rompasaurus/regardedPal/hardware-design/scad Parts/Rev 2 extended with joystick/04-26-design-alterations/solar-panel-bonding-adhesives.md

# Bonding a Solar Panel to a PETG Base Plate — Adhesive Options

Goal: glue a small solar panel (typically PET / ETFE / glass front, EVA + polymer backsheet, or epoxy-potted "rigid" panel) to a 3D-printed **PETG** base plate, outdoors, for years.

PETG itself is one of the most weather-tolerant common filaments — it survives years of sun without going brittle, so the bond joint is the limiting factor, not the plate. The two failure modes you're designing against are: (1) UV breaking down the adhesive, and (2) thermal cycling shearing it as PETG (CTE ~60 µm/m·°C) and the panel expand/contract at different rates. That's why **flexible** adhesives outperform rigid epoxies for this job.

## Quick recommendation

- **Best overall (long life, tolerant of thermal cycling, weather-sealed):** Sikaflex‑252 or Sikaflex‑295 UV bead around the perimeter.
- **Best for a clean, no-mess, fast install:** 3M VHB tape (5952 / 4941 / 4611 outdoor grades).
- **Best if you want it permanent and don't care about removability:** Sikaflex 252 + a few dots of CA glue to tack it while the urethane cures.
- **Avoid for outdoor, long-term:** hot glue, generic super glue, PVA/wood glue, plain 2‑part 5‑min epoxy.

---

## Option matrix

| Adhesive | Type | Bond to PETG | UV / outdoor | Flexible? | Expected outdoor life | Notes |
|---|---|---|---|---|---|---|
| **Sikaflex‑252** | 1‑part polyurethane | Excellent (lightly sand PETG first) | Excellent | Yes | **15–20+ years** (field reports of 20 yr installs still holding) | Industry standard for bonding solar panels to RVs/vans. Cures with humidity over ~24 h. |
| **Sikaflex‑295 UV** | 1‑part polyurethane | Excellent | Excellent (designed for marine glazing in UV) | Yes | **15–20+ years** | Specifically formulated for plastics that see direct sun. Often paired with Sika primer 209 on plastics. |
| **DOWSIL 795** | Neutral‑cure silicone | Very good (abrade + clean with IPA) | Excellent | Yes | **20+ years** (architectural rated) | Used to structurally bond glass curtain walls — overkill in the best way. |
| **3M VHB 5952 / 4941 / 4611** | Acrylic foam tape | Very good on PETG (clean, 21 °C+ install) | UV‑stable, weather‑resistant | Slightly (foam absorbs shear) | **10+ years** outdoor; 3M cites multi‑decade architectural use | Cleanest install. Press hard; full bond strength at ~72 h. Use a wide enough strip — bond area is everything. |
| **3M 4945 (UV‑resistant VHB)** | Acrylic foam tape | Good | Specifically UV‑rated | Slight | **10+ years** | Variant marketed for UV‑exposed joints. |
| **3D Gloop! (PETG version)** | Solvent‑weld | Excellent — chemically welds PETG to PETG | Moderate (joint is PETG, so good; but only welds PETG‑to‑PETG, not PETG‑to‑glass/EVA) | No | Depends on substrate | Great for joining PETG parts; **not** the right tool for bonding a glass/EVA panel face to PETG. |
| **Weld‑On 16** | Solvent cement | Excellent on PETG (PETG‑to‑acrylic/PETG) | Moderate | No | 5–10 yr | Same caveat as Gloop — designed for plastic‑to‑plastic, not panel‑to‑plastic. |
| **J‑B Weld Plastic Bonder** | 2‑part urethane epoxy | Good (sand PETG) | OK | Slightly | **5–10 yr** outdoor | Stronger than 5‑min epoxy, more flexible than rigid epoxy. Decent budget option. |
| **Loctite PL Premium / polyurethane construction adhesive** | 1‑part polyurethane | Good | Good | Yes | **10–15 yr** | Cheap, available everywhere, similar chemistry to Sikaflex but less refined. |
| **Gorilla Clear Silicone / GE II** | Neutral‑cure silicone | OK (abrade first) | Good | Yes | **5–10 yr** | The hardware‑store version of DOWSIL 795. Fine for hobby projects. |
| **Hot glue (EVA)** | Thermoplastic | Poor adhesion to PETG, softens in sun | Bad | Yes | **<1 season outdoors** | Don't. PETG + black plate + sun easily hits 60–80 °C. |
| **CA / super glue** | Cyanoacrylate | OK on PETG with primer | Bad — embrittles in UV/humidity | No | **<1 yr outdoors** | Fine as a *tack* while a real adhesive cures, not as the structural bond. |
| **5‑minute epoxy (generic)** | Rigid epoxy | OK on sanded PETG | Yellows and embrittles in UV | No | **1–3 yr outdoors** | Rigid joint cracks under thermal cycling. |

CTE = coefficient of thermal expansion.

---

## UHU products (Germany / EU availability)

UHU is the obvious shelf-pick in DE/AT/CH. Here's how their lineup maps onto this job:

| UHU product | Chemistry | Fit for solar‑on‑PETG outdoors | Expected outdoor life | Verdict |
|---|---|---|---|---|
| **UHU Max Repair Extreme** | MS polymer (modified silane, same family as Soudal Fix All / Bostik Evo‑Stik Serious Stuff) | **Yes — best UHU choice.** Flexible, waterproof, UV‑resistant, rated −40 to +120 °C, bonds plastic/glass/metal | **~10–15 yr** outdoors realistically (UHU markets it as long-life UV/weather rated) | **Pick this** if you want a UHU product. Functionally equivalent to a softer Sikaflex. Bead the perimeter, weight overnight, full strength in 24 h. |
| **UHU Plus Endfest 300** | 2‑part epoxy, 90 min open time | Strong but **rigid** → fails the thermal-cycling test on a sunlit panel | 2–5 yr outdoors before stress cracking | OK for indoor structural; not ideal for an outdoor solar bond. |
| **UHU Plus Schnellfest** (5‑min) | 2‑part rapid epoxy | Same problem as Endfest, plus weaker | 1–3 yr outdoors | Avoid for this use. |
| **UHU Plast Special / UHU Plast** | Solvent cement (THF/MEK based) | Designed for polystyrene, ABS, PVC, acrylic — **does not chemically weld PETG**, and only works plastic‑to‑plastic anyway | n/a for this job | Wrong tool. |
| **UHU Alleskleber Kraft / All Purpose Power Transparent** | Solvent‑based contact-style | Not weatherproof at the level you need | <2 yr outdoors | Indoor only. |
| **UHU Sekundenkleber (super glue)** | Cyanoacrylate | Embrittles in UV/humidity | <1 yr outdoors | Use only as a tack while MS polymer cures. |
| **UHU Kraftkleber Kontakt** | Polychloroprene contact adhesive | Softens in heat, not UV‑rated | 1–3 yr outdoors | Skip. |
| **Pattex Kleben statt Bohren Montagekleber Extreme** *(not UHU but same shelf in any Bauhaus / OBI)* | MS polymer | Equivalent to UHU Max Repair Extreme | ~10–15 yr | Solid alternative if Max Repair Extreme is sold out. |

**Bottom line for the German shelf:** grab **UHU Max Repair Extreme**. It's the UHU product that matches the chemistry the solar industry actually uses (MS polymer / polyurethane hybrids). If you can find Sikaflex‑252 or Pattex Montagekleber Extreme at a Bauhaus / OBI / Hornbach, those are a half-step better for very long service life, but Max Repair Extreme is more than good enough for a hobby solar plate and is everywhere — Müller, dm, Rossmann, hardware stores.

Same prep rules apply: scuff the PETG with 240 grit, wipe with isopropanol, clamp/weight for 24 h.

---

## Surface prep (matters more than the adhesive choice)

PETG is a low-ish surface energy plastic and 3D prints are often glossy, which kills adhesion. For any of the options above:

1. **Scuff** the PETG bond face with 220–400 grit sandpaper until uniformly matte. This is the single biggest win.
2. **Degrease** with 90 %+ isopropyl alcohol on a lint-free cloth. Let it flash off.
3. (Polyurethane / silicone) Optionally apply the manufacturer's primer — Sika Primer‑209 N for Sikaflex on plastics, DOWSIL 1200 OS Primer for DOWSIL 795. Adds years of service life.
4. **Clamp or weight** the panel during cure. For VHB, apply firm pressure (15+ psi) for ~10 seconds across the whole strip.
5. **Cure at room temp** before exposing to sun/rain — 24 h minimum for Sikaflex/silicone, 72 h for VHB to reach full strength.

## Application patterns

- **Perimeter bead + center dots** (Sikaflex/silicone): leaves a flexible joint that also weather-seals the panel edge. Best for outdoor.
- **Continuous VHB strip around the perimeter**: clean, mechanically strong, but doesn't seal as well unless you also run a thin silicone fillet around the outside edge afterward.
- **Avoid full‑face rigid bonding** (epoxy slathered everywhere). Differential thermal expansion will pop the bond or crack the panel substrate within a few summers.

## Solar‑specific note

Commercial solar modules are laminated with **EVA encapsulant** at ~150 °C, then bonded into frames with polyurethane or silicone. You're effectively recreating the frame‑bond step. Polyurethane (Sikaflex) and structural silicone (DOWSIL 795) are what the industry actually uses for this exact job at scale, which is why they top the list.

---

## Sources

- [3M VHB Tapes — outdoor durability overview](https://www.3m.com/3M/en_US/vhb-tapes-us/)
- [3M VHB Durability Technical Bulletin (PDF)](https://www.curbellplastics.com/wp-content/uploads/2022/11/3M-VHB-Tape-Durability.pdf)
- [3M 4945 UV‑resistant VHB datasheet](https://www.adezif.com/vhb-adhesive-3m-4945)
- [DOWSIL 795 product page](https://www.dow.com/en-us/pdp.dowsil-795-silicone-building-sealant.01595717z.html)
- [Sika Sikaflex‑715 / solar mounting context](https://www.solarpanelstore.com/products/sika-sikaflex-715-semi-self-leveling-roof-sealant)
- [Sikaflex for solar panels — long‑term field report (10 yr)](https://www.promasterforum.com/threads/ten-year-follow-up-on-direct-mount-of-pv-panel-to-pm-roof.105215/)
- [Best Sikaflex for solar panel mounting (2026 guide)](https://tyntrades.com/power-generation/best-sikaflex-for-mounting-solar-panel/)
- [DIY solar — silicone sealant discussion](https://diysolarforum.com/threads/silicone-sealant.36943/)
- [Hackaday — comparing adhesives for gluing PETG prints](https://hackaday.com/2025/01/30/comparing-adhesives-for-gluing-petg-prints/)
- [MakerBuildIt — best adhesives for PETG (3D Gloop, Weld‑On 16, J‑B Weld)](https://makerbuildit.com/blogs/news/the-best-adhesives-for-petg-3d-gloop-pvc-glue-weld-on-16-and-j-b-weld-for-plastics)
- [All3DP — best glue for PETG 3D prints](https://all3dp.com/2/best-petg-glue/)
- [PETG UV resistance overview](https://makershop.co/petg-uv-resistance/)
- [PVEducation — module materials & EVA encapsulation](https://www.pveducation.org/pvcdrom/modules-and-arrays/module-materials)
- [EVA encapsulant — adhesion study](https://vishakharenewables.com/blog/eva-encapsulant-a-detailed-study/)
- [UHU Max Repair Power — official product page](https://www.uhu.com/en-en/products/uhu-max-repair-power-blister-8-g-enplcsskhu)
- [UHU Max Repair Extreme — official product page](https://www.uhu.com/en/glueing-activities/diy-and-repair/repair/max-repair)
- [UHU Plus Endfest — 2‑part epoxy overview](https://buildglueinfo.com/features-of-two-component-epoxy-glue-of-the-uhu/)
- [UHU Plast Special — plastic-to-plastic solvent cement](https://sylcreate.com/product/uhu-plast-plastic-glue-30g/)
- [UHU adhesives product family](https://sylcreate.com/product-category/adhesives/uhu/)
