rompasaurus/regardedPal/PromptProgression.md

# Prompt Progression

A record of every prompt submitted during the development of Dilder.

Spelling and grammar are lightly cleaned for readability while preserving the original intent and voice.

## Fields tracked per entry

Every prompt entry below uses the following fields. Entries that don't yet list all fields should be treated as incomplete and backfilled when the context is recovered.

- **Date/Time** — absolute date (`YYYY-MM-DD`) of the prompt. Relative dates like "Thursday" get resolved when the entry is written.
- **Prompt** — the user's message, quoted. Spelling and grammar are lightly cleaned for readability while preserving the original intent and voice.
- **Input Tokens (est)** — approximate user-facing input token count.
- **Output Tokens (est)** — approximate assistant output token count across the full turn.
- **Commit** — the short SHA + subject line of the git commit that landed the changes from this prompt, in the form `` `abc1234` — commit subject ``. Uses `n/a — <reason>` if no files were changed (research / Q&A / explanation turns) or if the work was never committed.
- **Files Created/Modified** — bulleted list of files touched, with short notes on the change. If nothing changed, omit or write `none`. Multi-prompt sessions may share a single commit; each entry still lists the files the specific prompt touched.

---

## Prompt #1
- **Date/Time:** 2026-04-08
- **Prompt:** "Let's create a new git repo for this project and put it up on my rompasaurus GitHub account. Also create a prompt progression file to notate every prompt that I type out for this project in an MD file with date and time stamp and the token count for each, and the files created or modified, in a file called PromptProgression."
- **Input Tokens (est):** ~75
- **Output Tokens (est):** ~350
- **Commit:** `369880d` — Initial commit: add PromptProgression.md for tracking project prompts
- **Files Created/Modified:**
  - `PromptProgression.md` (created)
  - `.git/` (initialized)
  - GitHub repo `rompasaurus/dilder` (created)

---

## Prompt #2
- **Date/Time:** 2026-04-08
- **Prompt:** "Let's set up a README and plan for this project. The idea is to create a learning platform and blog along with a YouTube series that goes through the development process of creating a Tamagotchi clone using a Pi Zero, e-ink display, battery, and 3D-printed case. As part of this we are going to document the entire process, starting with the prompts and structure of the project and planning process. Flesh out a README that outlines this intent, marking each addition in phases so that it can be compiled into a proper step-by-step instruction."
- **Input Tokens (est):** ~110
- **Output Tokens (est):** ~2,500
- **Commit:** `cc9ea8f` — Add README with phased project roadmap and update prompt log
- **Files Created/Modified:**
  - `README.md` (created)
  - `PromptProgression.md` (modified)

---

## Prompt #3
- **Date/Time:** 2026-04-09
- **Prompt:** "Let's continue the planning process. Bear in mind each prompt I submit needs to be recorded in PromptProgression.md. I suppose Phase 0 planning is somewhat complete — there is a section to define the pet and personality but I believe that should be planned at a later date. I think the focus first will be piecing together the hardware for a prototype testable unit with a display and input, and perhaps we'll put a placeholder animal animation of sorts to get a scaffold in place code-wise and a process in place for deploying code and testing it. As for the hardware, what we are going to be working with is a Pi Zero and this e-ink display. Let's begin to research the materials list to include this and whatever else hardware-wise will be needed to get a test bench setup for developing on this hardware. Also, given this hardware, come up with prototype sketches that could potentially be a 3D-printed casing for these materials and allow for 4–5 buttons of input actions to be recorded on the hardware, and suggest and research the types of cheap off-the-shelf components that can be used to establish input actions."
- **Input Tokens (est):** ~220
- **Output Tokens (est):** ~4,500
- **Commit:** `733c582` — Add hardware research with materials list, component specs, and input options
- **Files Created/Modified:**
  - `PromptProgression.md` (modified)
  - `docs/hardware-research.md` (created)
  - `README.md` (modified)

---

## Prompt #4
- **Date/Time:** 2026-04-09
- **Prompt:** "I also need the output processing token estimate from the prompts as well in the prompt progression."
- **Input Tokens (est):** ~20
- **Output Tokens (est):** ~250
- **Commit:** `8b8b2e4` — Update README and prompt log for Phase 1 hardware planning
- **Files Created/Modified:**
  - `PromptProgression.md` (modified — added output token estimates to all entries)

---

## Prompt #5
- **Date/Time:** 2026-04-09
- **Prompt:** "Those concept ASCII images are neat, but I want something more like a long rectangular case with the buttons on the right of the display — somewhat like the second-to-last generation of iPod Nanos — with four buttons: up, down, left, right, and a center button. Try to mock this up and see if you can generate an actual example, full-resolution prototype concept of this, bearing in mind the hardware we are using."
- **Input Tokens (est):** ~90
- **Output Tokens (est):** ~3,800
- **Commit:** `e1b6891` — Add prototype enclosure concept renders (v1 and v2 SVGs)
- **Files Created/Modified:**
  - `docs/concepts/prototype-v1.svg` (created — full-resolution prototype concept render)
  - `docs/hardware-research.md` (modified — replaced ASCII concepts with SVG reference and updated form factor)
  - `PromptProgression.md` (modified)

---

## Prompt #6
- **Date/Time:** 2026-04-09
- **Prompt:** "That's a good start. Let's create another revision of the prototype and make a v2. This time let's make the dimensions make sense — the display is going to take up the largest area of the device with the buttons being a quarter or less of the device's face real estate. Let's also take into account the Waveshare's actual dimensions and account for these ratios."
- **Input Tokens (est):** ~75
- **Output Tokens (est):** ~6,500
- **Commit:** `e1b6891` — Add prototype enclosure concept renders (v1 and v2 SVGs)
- **Files Created/Modified:**
  - `docs/concepts/prototype-v2.svg` (created — dimension-accurate prototype concept at 4:1 scale)
  - `docs/hardware-research.md` (modified — updated enclosure section with v2 specs and real component dimensions)
  - `PromptProgression.md` (modified)

---

## Prompt #7
- **Date/Time:** 2026-04-09
- **Prompt:** "For the hardware research we will need a breadboard to wire everything together — add that in there. Then we can begin the hardware setup and configuration, assuming we bought all the materials listed and a Waveshare e-ink display 2.13 V3. Compose an in-depth, well-researched setup guide to begin displaying text on the display and compile and run embedded code on the Raspberry Pi. Make the guide as simple and exhaustive as possible. Include a table of contents and walk me through the documentation for the hardware and how to set up the development and debugging environment. Pull in and research every bit of documentation I will need to be successful in this project."
- **Input Tokens (est):** ~130
- **Output Tokens (est):** ~12,000
- **Commit:** `30bb8b7` — Add comprehensive hardware and dev environment setup guide
- **Files Created/Modified:**
  - `docs/setup-guide.md` (created — comprehensive hardware and dev environment setup guide with 13 sections)
  - `docs/hardware-research.md` (modified — updated display to V3, added breadboard detail)
  - `README.md` (modified — added setup guide link to docs table and Phase 1 checklist)
  - `PromptProgression.md` (modified)

---

## Prompt #8
- **Date/Time:** 2026-04-09
- **Prompt:** "I want to set up a documentation webpage/portfolio to provide an in-depth guide on how this project is progressing in real time, along with a page for documentation and research, contact information, and an introduction. Let's create a new folder to begin planning this. I would also like to use pwnagotchi.ai as something of an inspiration for how to set this up and organise the website. It doesn't need to be anything ridiculous — in fact, static pages may be the ideal format — along with a Discord group and Patreon page. Let's roll out this folder and christen it with a new MD file."
- **Input Tokens (est):** ~120
- **Output Tokens (est):** ~3,500
- **Commit:** `f44695c` — Add website planning folder with site structure and community plan
- **Files Created/Modified:**
  - `website/PLAN.md` (created — website plan with site structure, page descriptions, Discord/Patreon plans, SSG comparison, pwnagotchi analysis)
  - `PromptProgression.md` (modified)

---

## Prompt #9
- **Date/Time:** 2026-04-09
- **Prompt:** "Let's kick off the website implementation. Look through the plan and start fleshing this out. Make sure while implementing the site to notate every step taken in a website implementation process MD, which will have a nicely structured TOC and detailed step-by-step notes on the process of creating this static site — to act as instruction and documentation. I also need a detailed guide on how to add and update content and the structure of the site, and further steps to deploy on Digital Ocean for as cheap as possible, and the best way to secure a domain for a website. Come up with domain ideas as well. Add steps to create a Patreon and Discord account. Don't forget to update PromptProgression with any prompt I input — don't be afraid to clean spelling and grammar before putting it in there too."
- **Input Tokens (est):** ~180
- **Output Tokens (est):** ~35,000
- **Commit:** `0360ba9` — Build out full MkDocs website scaffold and dev tooling (Prompts 9–13)
- **Files Created/Modified:**
  - `website/mkdocs.yml` (created — full MkDocs Material config with blog plugin, nav, social links, extensions)
  - `website/docs/index.md` (created — landing page)
  - `website/docs/about/index.md` (created — about page)
  - `website/docs/about/contact.md` (created — contact page)
  - `website/docs/blog/index.md` (created — blog landing)
  - `website/docs/blog/posts/phase-0-planning.md` (created — Phase 0 blog post)
  - `website/docs/blog/posts/phase-1-hardware.md` (created — Phase 1 blog post)
  - `website/docs/docs/index.md` (created — docs overview)
  - `website/docs/docs/hardware/materials-list.md` (created — migrated from hardware-research.md)
  - `website/docs/docs/hardware/wiring-pinout.md` (created — GPIO assignments and breadboard layout)
  - `website/docs/docs/hardware/enclosure-design.md` (created — case dimensions and design constraints)
  - `website/docs/docs/setup/pi-zero-setup.md` (created — OS flash, SSH, SPI setup)
  - `website/docs/docs/setup/display-setup.md` (created — HAT attachment, Waveshare library, hello world)
  - `website/docs/docs/setup/dev-environment.md` (created — rsync workflow, VS Code Remote-SSH, systemd)
  - `website/docs/docs/software/project-structure.md` (created — planned firmware architecture)
  - `website/docs/community/index.md` (created — community overview)
  - `website/docs/community/discord.md` (created — Discord server structure)
  - `website/docs/community/support.md` (created — Patreon tiers)
  - `website/docs/prompts/index.md` (created — prompt log mirroring PromptProgression.md)
  - `website/docs/stylesheets/extra.css` (created — custom CSS overrides)
  - `website/IMPLEMENTATION.md` (created — 14-section build process doc covering MkDocs setup, GitHub Pages, Digital Ocean deployment, domain registration guide, domain ideas, Discord setup, Patreon setup)
  - `website/CONTENT-GUIDE.md` (created — 11-section content management guide covering blog posts, docs pages, nav, Markdown features, images, and publishing)
  - `PromptProgression.md` (modified)

---

## Prompt #10
- **Date/Time:** 2026-04-09
- **Prompt:** "Give me a Python setup CLI script I can run to deploy this locally, with nice logging and status output when it is running, and various helper options for this project."
- **Input Tokens (est):** ~40
- **Output Tokens (est):** ~4,500
- **Commit:** `0360ba9` — Build out full MkDocs website scaffold and dev tooling (Prompts 9–13)
- **Files Created/Modified:**
  - `website/dev.py` (created — CLI with subcommands: check, install, serve, build, deploy, clean, status; ANSI color output with spinner; argparse; no external dependencies)

---

## Prompt #11
- **Date/Time:** 2026-04-09
- **Prompt:** "Give me a nice selection menu interface instead of a list of commands."
- **Input Tokens (est):** ~15
- **Output Tokens (est):** ~3,800
- **Commit:** `0360ba9` — Build out full MkDocs website scaffold and dev tooling (Prompts 9–13)
- **Files Created/Modified:**
  - `website/dev.py` (modified — replaced no-args fallback with interactive arrow-key menu: ↑↓ navigation, live description footer, env status badges, returns to menu after each command)

---

## Prompt #12
- **Date/Time:** 2026-04-09
- **Prompt:** "There seems to be a build failure when I build via the CLI script."
- **Input Tokens (est):** ~180 (included full error output)
- **Output Tokens (est):** ~500
- **Commit:** `0360ba9` — Build out full MkDocs website scaffold and dev tooling (Prompts 9–13)
- **Files Created/Modified:**
  - `website/docs/blog/.authors.yml` (created — required by MkDocs blog plugin for named authors)
  - `website/docs/blog/index.md` (modified — removed dead RSS link that wasn't a source file)
  - `website/docs/docs/hardware/enclosure-design.md` (modified — changed SVG links from broken relative paths to GitHub URLs)

---

## Prompt #13
- **Date/Time:** 2026-04-09
- **Prompt:** "Let's update the prompts with the last ones I sent through — divide and describe them. Commit the changes, and also apply the git commit as another field in the prompt progression where the prompt's changes were applied. Don't be afraid to clean up the spelling and grammar a bit. Report this prompt as well."
- **Input Tokens (est):** ~65
- **Output Tokens (est):** ~2,500
- **Commit:** `78ea1a0` — Backfill commit hash in PromptProgression.md (Prompt 13)
- **Files Created/Modified:**
  - `PromptProgression.md` (modified — full grammar/spelling pass, added commit hash field to all entries, added Prompts #11–13)

---

## Prompt #14
- **Date/Time:** 2026-04-09
- **Prompt:** "Walk me through how I could deploy this on GitHub Pages and the pricing structure — hopefully free — and if a domain can be linked to a GitHub Pages account."
- **Input Tokens (est):** ~35
- **Output Tokens (est):** ~900
- **Commit:** `633b084` — Add GitHub Actions workflow for automatic Pages deployment
- **Files Created/Modified:**
  - `.github/workflows/deploy-site.yml` (created — workflow that triggers on pushes to `website/` on main, installs MkDocs Material, and runs `mkdocs gh-deploy`)

---

## Prompt #15
- **Date/Time:** 2026-04-09
- **Prompt:** "Can you embed the concept images instead of linking to the GitHub page on the website?"
- **Input Tokens (est):** ~30
- **Output Tokens (est):** ~300
- **Commit:** `e358a1f` — Embed prototype SVG renders directly in enclosure design page
- **Files Created/Modified:**
  - `website/docs/assets/images/prototype-v1.svg` (created — copied from docs/concepts/)
  - `website/docs/assets/images/prototype-v2.svg` (created — copied from docs/concepts/)
  - `website/docs/docs/hardware/enclosure-design.md` (modified — replaced GitHub links with inline `![img]()` embeds)

---

## Prompt #16
- **Date/Time:** 2026-04-09
- **Prompt:** "Should the site folder be in the gitignore or will that need to be included to render on the GitHub Pages?"
- **Input Tokens (est):** ~25
- **Output Tokens (est):** ~150
- **Commit:** n/a — explanation only, no files changed
- **Files Created/Modified:** none

---

## Prompt #17
- **Date/Time:** 2026-04-09
- **Prompt:** "Add the last prompts with code changes to the prompt history with a commit ref."
- **Input Tokens (est):** ~20
- **Output Tokens (est):** ~400
- **Commit:** `1c270fd` — Update PromptProgression with Prompts 14–17 and fix #13 commit ref
- **Files Created/Modified:**
  - `PromptProgression.md` (modified — fixed Prompt #13 commit hash, added Prompts #14–17)

---

## Prompt #18
- **Date/Time:** 2026-04-09
- **Prompt:** "I need a website deployment process guide for GitHub Pages. I have a registered domain on Squarespace and I would like to deploy this site on GitHub and link my domain to this page."
- **Input Tokens (est):** ~45
- **Output Tokens (est):** ~2,800
- **Commit:** `38baa75` — Add deployment guide and CNAME file for Squarespace domain setup
- **Files Created/Modified:**
  - `website/DEPLOY.md` (created — 13-section deployment guide: GitHub Pages setup, first deployment, CNAME file, Squarespace DNS configuration with step-by-step record setup, HTTPS, mkdocs.yml update, end-to-end verification checklist, troubleshooting)
  - `website/docs/CNAME` (created — placeholder CNAME file, update with real domain before deploying)

---

## Prompt #19
- **Date/Time:** 2026-04-09
- **Prompt:** "Add my Patreon page to the site."
- **Input Tokens (est):** ~15
- **Output Tokens (est):** ~100
- **Commit:** `3b36905` — Add real Patreon URL (MchenrysDevelopment) across site
- **Files Created/Modified:**
  - `website/mkdocs.yml` (modified — Patreon social link updated)
  - `website/docs/community/support.md` (modified — Patreon URL updated)
  - `website/docs/about/contact.md` (modified — Patreon URL updated)

---

## Prompt #20
- **Date/Time:** 2026-04-09
- **Prompt:** "There's a 404 error — it's not loading despite the domain pointing correctly and the GitHub hook deploying."
- **Input Tokens (est):** ~40
- **Output Tokens (est):** ~300
- **Commit:** `0af7962` — Clarify Pages source setting in workflow comment
- **Files Created/Modified:**
  - `.github/workflows/deploy-site.yml` (modified — added comment clarifying Pages must be set to "Deploy from a branch → gh-pages" not "GitHub Actions")

---

## Prompt #21
- **Date/Time:** 2026-04-09
- **Prompt:** "Make that branch for me so that it triggers the deploy."
- **Input Tokens (est):** ~20
- **Output Tokens (est):** ~150
- **Commit:** `1c7f210` — Trigger GitHub Pages deployment via website/ path change
- **Files Created/Modified:**
  - `website/requirements.txt` (modified — added comment to satisfy workflow paths filter and trigger first deployment)

---

## Prompt #22
- **Date/Time:** 2026-04-09
- **Prompt:** *(Shared GitHub Actions build log showing successful deploy to gh-pages branch with CNAME resolution to dilder.dev)*
- **Input Tokens (est):** ~200 (build log)
- **Output Tokens (est):** ~200
- **Commit:** `18c8876` — Lowercase CNAME domain
- **Files Created/Modified:**
  - `website/docs/CNAME` (modified — changed `Dilder.dev` to `dilder.dev` for consistency)

---

## Prompt #23
- **Date/Time:** 2026-04-09
- **Prompt:** "Now we need to pull in the documentation for the Pi Zero WH and the e-ink display. Reach out to the official documentation and put it in its own folder in the docs folder. We need to then extract the pinout and pertinent documentation and attach it to the Wiring & Pinout doc."
- **Input Tokens (est):** ~55
- **Output Tokens (est):** ~8,500
- **Commit:** `61525d6` — Add official hardware reference docs and expand wiring pinout
- **Files Created/Modified:**
  - `website/docs/docs/reference/pi-zero-wh.md` (created — full 40-pin GPIO table, electrical limits, SPI/I²C/UART/PWM protocol assignments, BCM vs physical numbering guide, official links)
  - `website/docs/docs/reference/waveshare-eink.md` (created — display specs, HAT pin mapping with signal behavior table, SPI protocol details, refresh rules, V3 vs V4 comparison, Python setup examples, safety notes, official links)
  - `website/docs/docs/hardware/wiring-pinout.md` (modified — expanded with full 40-pin header map, signal behavior table, wiring diagram, SPI config table, links to new reference docs, troubleshooting section)
  - `website/mkdocs.yml` (modified — Reference section added to nav)

---

## Prompt #24
- **Date/Time:** 2026-04-09
- **Prompt:** "Update the prompts file with this and the commit."
- **Input Tokens (est):** ~15
- **Output Tokens (est):** ~400
- **Commit:** `09519b5` — Update PromptProgression with Prompts 20–24
- **Files Created/Modified:**
  - `PromptProgression.md` (modified — added Prompts #20–24)

---

## Prompt #25
- **Date/Time:** 2026-04-10
- **Prompt:** "Let's update this plan and the hardware we are going to use. For now I have a set of Waveshare 2.13 V3 displays and Pico W boards on hand that I would like to use to start this project with instead of the Pi Zero. We'll put the Pi Zero in a later dev phase and start with what we have. Update the documentation to account for this hardware change and pull in the correct documentation for this hardware and setup in the project and on the site. Update everything and replace the Zero with the Pico, and then we need to create a setup document to wire up the Waveshare to the Pico W and begin debugging from VSCode on Linux."
- **Input Tokens (est):** ~130
- **Output Tokens (est):** ~45,000
- **Commit:** `604039f` — Migrate from Pi Zero to Pico W as Phase 1 development platform
- **Files Created/Modified:**
  - `README.md` (modified — Pico W as primary board, Pi Zero deferred to Phase 5, new phase roadmap)
  - `docs/hardware-research.md` (modified — Pico W specs, SPI1 pin mapping, updated materials list and GPIO budget)
  - `website/docs/docs/reference/pico-w.md` (created — full Pico W reference: RP2040 specs, pinout, electrical limits, MicroPython firmware, Pico W vs Pi Zero comparison)
  - `website/docs/docs/reference/waveshare-eink.md` (modified — added Pico W jumper wire mapping, MicroPython driver setup, kept Pi Zero mapping for future)
  - `website/docs/docs/reference/pi-zero-wh.md` (modified — added "future hardware" banner)
  - `website/docs/docs/hardware/materials-list.md` (modified — Pico W components, updated costs and specs)
  - `website/docs/docs/hardware/wiring-pinout.md` (modified — complete rewrite for Pico W GPIO, jumper wire diagrams, MicroPython button code, visual pin map)
  - `website/docs/docs/hardware/enclosure-design.md` (modified — Pico W dimensions, enclosure deferred note)
  - `website/docs/docs/setup/pi-zero-setup.md` (modified — rewritten as Pico W setup: MicroPython flash, BOOTSEL, serial REPL, Wi-Fi test)
  - `website/docs/docs/setup/display-setup.md` (modified — rewritten for Pico W jumper wire connection, Waveshare MicroPython driver, framebuf hello world)
  - `website/docs/docs/setup/dev-environment.md` (modified — rewritten for VSCode + MicroPico on Linux: serial permissions, project config, file upload, mpremote CLI, debugging)
  - `website/docs/docs/software/project-structure.md` (modified — updated for MicroPython: framebuf, machine.Pin, flash storage notes)
  - `website/docs/docs/index.md` (modified — updated section names and descriptions for Pico W)
  - `website/docs/index.md` (modified — landing page updated for Pico W)
  - `website/mkdocs.yml` (modified — site description, nav labels, added Pico W reference page)
  - `website/docs/blog/posts/phase-1-hardware.md` (modified — rewritten for Pico W test bench)
  - `website/docs/blog/posts/phase-0-planning.md` (modified — hardware decision section updated for Pico W first approach)

---

## Prompt #26
- **Date/Time:** 2026-04-10
- **Prompt:** "Update the prompts file and fix grammar a bit. Divide, describe, and commit."
- **Input Tokens (est):** ~20
- **Output Tokens (est):** ~1,500
- **Commit:** `604039f` — Migrate from Pi Zero to Pico W as Phase 1 development platform
- **Files Created/Modified:**
  - `PromptProgression.md` (modified — added Prompts #25–26)

---

## Prompt #27
- **Date/Time:** 2026-04-11
- **Prompt:** "Let's make a development setup folder with a Docker Compose file and a step-by-step guide with a table of contents on setting up the Pico W and Waveshare e-ink display — physically connecting the display to the Pico board via GPIO headers, then flashing and connecting the Pico to this computer and running a first Hello World program via VSCode using compiled C. I need all the instructions to set up the hardware, configure VSCode, connect, debug, and run this application. Make this guide as detailed and as simple as possible, step by step. Also update the PromptProgression every time I submit a prompt here — clean up the grammar and spelling though. Make this setup guide the Pico and display first-time setup, and update the dev website too."
- **Input Tokens (est):** ~150
- **Output Tokens (est):** ~45,000
- **Commit:** `8f0df95` — Add C SDK dev environment, setup CLI, and first-time hardware guide
- **Files Created/Modified:**
  - `dev-setup/pico-and-display-first-time-setup.md` (created — comprehensive 13-section first-time setup guide with TOC: hardware wiring, C SDK toolchain install, VSCode configuration, CMake cross-compilation, build/flash/debug workflow, troubleshooting)
  - `dev-setup/hello-world/CMakeLists.txt` (created — CMake build config for Pico W with Waveshare e-Paper library, USB serial output, Ninja generator)
  - `dev-setup/hello-world/main.c` (created — Hello World C program that initializes SPI, draws text on the e-ink display, and prints heartbeat to USB serial)
  - `dev-setup/Dockerfile` (created — Ubuntu 24.04 container with ARM cross-compiler toolchain and Pico SDK for reproducible builds)
  - `dev-setup/docker-compose.yml` (created — single-service compose file that mounts the project and runs CMake + Ninja build)
  - `website/docs/docs/setup/first-time-setup.md` (created — website version of the setup guide with MkDocs Material formatting, tabbed OS instructions, admonitions)
  - `website/mkdocs.yml` (modified — added "First-Time Setup (C SDK)" to the Setup nav section)
  - `PromptProgression.md` (modified — added Prompt #27)

---

## Prompt #28
- **Date/Time:** 2026-04-11
- **Prompt:** "Let's start planning the hardware enclosure design. Create a new folder labelled hardware-design and document the applicable dimensions of the e-ink display and Pico board, along with viable off-the-shelf button options that can be wired to the Pico easily. Research the web for the best button options and provide a cost breakdown. Then we need to start planning how to model out a 3D-printed prototype case based on the concept images — link the concept images, suggest the best CAD software and company to print the first prototype cases, and provide estimated costs. Put this in a new hardware planning document with a table of contents and step-by-step guide. Also update the PromptProgression with this entry, following the same pattern."
- **Input Tokens (est):** ~150
- **Output Tokens (est):** ~25,000
- **Commit:** `8f0df95` — Add C SDK dev environment, setup CLI, and first-time hardware guide
- **Files Created/Modified:**
  - `hardware-design/hardware-planning.md` (created — comprehensive enclosure planning document with TOC: component dimensions, button selection with cost breakdown, concept image links, enclosure constraints, CAD software comparison, step-by-step 3D modeling plan, printing service comparison with costs, prototype timeline)

---

## Prompt #29
- **Date/Time:** 2026-04-11
- **Prompt:** "I want another Hello World version of the code running in C as well. The intent with this project is to have it running on C code completely for speed and efficiency. Also, for the wiring section, I am using the soldered-on headers and pins to slot the Waveshare directly onto the Pico on its headers, so it just slides in. Update the guide accordingly — I will provide pictures later."
- **Input Tokens (est):** ~80
- **Output Tokens (est):** ~30,000
- **Commit:** `8f0df95` — Add C SDK dev environment, setup CLI, and first-time hardware guide
- **Files Created/Modified:**
  - `dev-setup/hello-world-serial/main.c` (created — bare-minimum serial-only Hello World in C: LED blink + heartbeat printf, no display wiring needed, verifies toolchain end-to-end)
  - `dev-setup/hello-world-serial/CMakeLists.txt` (created — minimal CMake config linking only pico_stdlib with USB serial output)
  - `dev-setup/pico-and-display-first-time-setup.md` (rewritten — restructured as two checkpoints: Checkpoint 1 serial-only, Checkpoint 2 display; added C vs MicroPython rationale; updated wiring section from jumper wires to direct header-on-header connection)
  - `website/docs/docs/setup/first-time-setup.md` (rewritten — website version updated to match: direct header connection, two-checkpoint flow, C-first rationale)
  - `PromptProgression.md` (modified — added Prompt #29)

---

## Prompt #30
- **Date/Time:** 2026-04-11
- **Prompt:** "Let's take this Pico W & Display First-Time Setup and implement a Python command-line step-by-step interface that sets everything up and explains the process in detail as well. Put the Python script in the root of this project."
- **Input Tokens (est):** ~40
- **Output Tokens (est):** ~35,000
- **Commit:** `8f0df95` — Add C SDK dev environment, setup CLI, and first-time hardware guide
- **Files Created/Modified:**
  - `setup.py` (created — interactive 14-step CLI walkthrough: prerequisite checks, ARM toolchain install with distro detection, Pico SDK clone, PICO_SDK_PATH configuration, serial port permissions, VSCode extension install, serial hello world build/flash/verify, display connection guidance, Waveshare library download, display hello world build/flash/verify; includes --status, --step N, and --list flags; matches dev.py visual style with ANSI colors, spinners, boxed explanations, and manual-step callouts)
  - `PromptProgression.md` (modified — added Prompt #30)

---

## Prompt #31
- **Date/Time:** 2026-04-11
- **Prompt:** "Failed at step 5 — `usermod: group 'dialout' does not exist`. Does the Pico need to be connected at step 5?"
- **Input Tokens (est):** ~30
- **Output Tokens (est):** ~5,000
- **Commit:** `8f0df95` — Add C SDK dev environment, setup CLI, and first-time hardware guide
- **Files Created/Modified:**
  - `setup.py` (modified — added `detect_serial_group()` and `user_in_serial_group()` helpers that check for `uucp` first then `dialout`; Arch/CachyOS uses `uucp`, Debian/Ubuntu uses `dialout`; all hardcoded `dialout` references replaced with dynamic detection)
  - `dev-setup/pico-and-display-first-time-setup.md` (modified — serial permissions section updated with distro-specific group names)
  - `website/docs/docs/setup/first-time-setup.md` (modified — same distro-specific serial group fix with tabbed instructions)
  - `PromptProgression.md` (modified — added Prompt #31)

---

## Prompt #32
- **Date/Time:** 2026-04-11
- **Prompt:** *(Pasted build failure output from setup.py Step 7 — `PICO_DEFAULT_LED_PIN` undeclared error)*
- **Input Tokens (est):** ~80
- **Output Tokens (est):** ~8,000
- **Commit:** `8f0df95` — Add C SDK dev environment, setup CLI, and first-time hardware guide
- **Files Created/Modified:**
  - `dev-setup/hello-world-serial/main.c` (modified — replaced `PICO_DEFAULT_LED_PIN` and `gpio_put` with `cyw43_arch_gpio_put(CYW43_WL_GPIO_LED_PIN)` since the Pico W's onboard LED is wired to the CYW43 Wi-Fi chip, not a regular GPIO pin; added `pico/cyw43_arch.h` include and `cyw43_arch_init()` call)
  - `dev-setup/hello-world-serial/CMakeLists.txt` (modified — added `pico_cyw43_arch_none` to link libraries for CYW43 LED control)
  - `setup.py` (modified — fixed build error output to show both stdout and stderr since Ninja reports compile errors on stdout)
  - `PromptProgression.md` (modified — added Prompt #32)

---

## Prompt #33
- **Date/Time:** 2026-04-11
- **Prompt:** "Could not find the RPI-RP2 mount despite it showing up in Dolphin file explorer."
- **Input Tokens (est):** ~40
- **Output Tokens (est):** ~5,000
- **Commit:** `8f0df95` — Add C SDK dev environment, setup CLI, and first-time hardware guide
- **Files Created/Modified:**
  - `setup.py` (modified — added `find_rpi_rp2_mount()` helper that checks static paths, falls back to `findmnt`/`lsblk` for the actual mount point, retries after 1-second delay for automount; both flash steps now loop with retry instead of failing on first miss)
  - `PromptProgression.md` (modified — added Prompt #33)

---

## Prompt #34
- **Date/Time:** 2026-04-11
- **Prompt:** *(Pasted Step 12 build failure — `Debug.h: No such file or directory` and missing `<stdlib.h>` warnings)*
- **Input Tokens (est):** ~100
- **Output Tokens (est):** ~5,000
- **Commit:** `8f0df95` — Add C SDK dev environment, setup CLI, and first-time hardware guide
- **Files Created/Modified:**
  - `dev-setup/hello-world/main.c` (modified — added missing `#include <stdlib.h>` for `malloc`/`free`)
  - `dev-setup/hello-world/lib/Config/Debug.h` (added — copied from Waveshare repo, was missing from the initial file list)
  - `setup.py` (modified — added `Debug.h` to the Waveshare library copy list in Step 11)
  - `dev-setup/pico-and-display-first-time-setup.md` (modified — added `Debug.h` to the manual copy commands)
  - `website/docs/docs/setup/first-time-setup.md` (modified — same `Debug.h` fix)
  - `PromptProgression.md` (modified — added Prompt #34)

---

## Prompt #35
- **Date/Time:** 2026-04-11
- **Prompt:** "That worked. Let's update the documentation and provide a step-by-step walkthrough of this script and setup process in the setup document. Also update the prompts doc with all the prompts we used here and the last session, then divide, describe, commit, and push this code."
- **Input Tokens (est):** ~50
- **Output Tokens (est):** ~12,000
- **Commit:** `8f0df95` — Add C SDK dev environment, setup CLI, and first-time hardware guide
- **Files Created/Modified:**
  - `dev-setup/pico-and-display-first-time-setup.md` (modified — added "Automated Setup Script" section at the top with full walkthrough: command reference, 14-step table with automated/manual flags, example `--status` output, resume instructions)
  - `website/docs/docs/setup/first-time-setup.md` (modified — added matching setup script walkthrough with MkDocs admonitions and step table)
  - `.gitignore` (modified — added build artifacts, Waveshare lib files, pico_sdk_import.cmake, `__pycache__/`, `.vscode/`)
  - `PromptProgression.md` (modified — added Prompts #27–35, updated all pending commit hashes)
  - All new and modified files committed and pushed to origin/main

---

## Prompt #36
- **Date/Time:** 2026-04-11
- **Prompt:** "Now that the dev environment is set up, let's make a Python GUI to interface with the Pico — view logs, debug, and create a simple utility to draw images and type text on an emulated e-ink display that can then be either saved locally or sent to the e-ink display live. When saved, add it to an assets folder in the root of this project directory. Also, if there are any other useful utilities that can be added to enhance the development and usage of the Pico W, add them to this Python UI. Let's make this in Tkinter and put it in the root of this project in a directory called DevTool. Also I need an in-depth walkthrough of this implementation in the folder as well — an MD with a TOC and step-by-step instructions."
- **Input Tokens (est):** ~150
- **Output Tokens (est):** ~55,000
- **Commit:** `cf5cd3a` — Add DevTool — Tkinter GUI for Pico W development
- **Files Created/Modified:**
  - `DevTool/devtool.py` (created — 950-line Tkinter GUI with five tabs: display emulator with pencil/eraser/line/rect/text tools and save/load/send; serial monitor with connect/disconnect/send/log; firmware flash utility with BOOTSEL detection and build buttons; asset manager with preview and delete; GPIO pin reference viewer; dark theme; threaded serial I/O)
  - `DevTool/requirements.txt` (created — pyserial, Pillow)
  - `DevTool/README.md` (created — 11-section walkthrough with TOC: requirements, installation, all five tabs documented with usage instructions, file formats, architecture overview, class structure, threading model, troubleshooting table)
  - `assets/` (created — empty directory for saved display images)
  - `PromptProgression.md` (modified — added Prompt #36)

---

## Prompt #37
- **Date/Time:** 2026-04-11
- **Prompt:** "Add a utility tab to walk through connecting the Pico via USB, and also add a Wi-Fi option as well in the GUI as a tab. Be descriptive and as simple as possible. And add a documentation tab to reference how to use the application."
- **Input Tokens (est):** ~50
- **Output Tokens (est):** ~25,000
- **Commit:** `cdae51f` — Add Connect and Docs tabs to DevTool
- **Files Created/Modified:**
  - `DevTool/devtool.py` (modified — added two new tabs: ConnectionUtility with USB serial walkthrough (4 steps with live Check buttons for device detection, serial port, permissions, plus link to Serial Monitor) and Wi-Fi walkthrough (C code examples, CMake config, network scanner, TCP connection tester with IP/port input); DocumentationTab with searchable TOC sidebar, styled headings/code blocks, Find/Clear search with highlight, covers all 7 tabs plus keyboard shortcuts, file formats, and troubleshooting)
  - `DevTool/README.md` (modified — updated TOC, launch table, and architecture table for 7 tabs; added Section 9 Connection Utility with USB and Wi-Fi step tables; added Section 10 Documentation tab description; renumbered remaining sections)
  - `PromptProgression.md` (modified — added Prompt #37)

---

## Prompt #38
- **Date/Time:** 2026-04-11
- **Prompt:** "Allow me to run the sudo for serial permissions in the DevTool."
- **Input Tokens (est):** ~15
- **Output Tokens (est):** ~5,000
- **Commit:** `b8985c7` — Add sudo serial permissions button to DevTool Connect tab
- **Files Created/Modified:**
  - `DevTool/devtool.py` (modified — added "Fix: Add me to serial group" button in the Connect tab USB walkthrough; `_fix_serial_perms()` method auto-detects the correct group, tries `pkexec` for a graphical sudo prompt first, falls back to opening a terminal emulator with the command, shows confirmation dialog before running, reports success with logout reminder)
  - `PromptProgression.md` (modified — added Prompt #38)

---

## Prompt #39
- **Date/Time:** 2026-04-11
- **Prompt:** "The DevTool was suspended but didn't close. Help me close this and prevent this in the future."
- **Input Tokens (est):** ~20
- **Output Tokens (est):** ~2,000
- **Commit:** `586dff9` — Ignore Ctrl+Z (SIGTSTP) in DevTool to prevent zombie suspends
- **Files Created/Modified:**
  - `DevTool/devtool.py` (modified — added `signal.signal(signal.SIGTSTP, signal.SIG_IGN)` at startup to ignore Ctrl+Z; killed the suspended process with `kill -9`)

---

## Prompt #40
- **Date/Time:** 2026-04-11
- **Prompt:** "Update the prompts and add the latest assets as well. Clean up spelling and grammar."
- **Input Tokens (est):** ~20
- **Output Tokens (est):** ~3,000
- **Commit:** `5025ec6` — Add test assets and update PromptProgression through Prompt #40
- **Files Created/Modified:**
  - `assets/garbage.pbm` (added — test image saved from DevTool display emulator)
  - `assets/garbage.bin` (added — raw display buffer of the test image)
  - `assets/garbage.png` (added — PNG export of the test image)
  - `PromptProgression.md` (modified — added Prompts #39–40, backfilled commit hashes for #37–38, grammar and spelling pass)

---

## Prompt #41
- **Date/Time:** 2026-04-11
- **Prompt:** "We need to update the website with all the new documentation and Python tools created. Follow the structure of the site and update this."
- **Input Tokens (est):** ~30
- **Output Tokens (est):** ~60,000
- **Commit:** `b408ab1` — Update website with Tools docs, blog post, prompt log, and DevTool Programs tab
- **Files Created/Modified:**
  - `website/docs/docs/tools/devtool.md` (created — DevTool documentation page with installation, tabs overview, file formats, and architecture)
  - `website/docs/docs/tools/setup-cli.md` (created — setup.py documentation page with step tables, features, and status dashboard)
  - `website/docs/docs/tools/website-dev.md` (created — website dev.py documentation page with commands and workflow)
  - `website/docs/blog/posts/phase-1-devtools.md` (created — blog post covering setup CLI, DevTool GUI, and C-first development decisions)
  - `website/mkdocs.yml` (modified — added Tools section to nav with DevTool, Setup CLI, Website Dev CLI)
  - `website/docs/docs/index.md` (modified — added Tools subsection with links to all three tool pages)
  - `website/docs/docs/software/project-structure.md` (modified — complete rewrite: updated repo layout to include DevTool, dev-setup, hardware-design, assets, website planning docs; rewrote planned modules from MicroPython to C SDK; updated comparison table)
  - `website/docs/index.md` (modified — updated current phase to reflect dev tooling progress, added Dev Tools quick link card, added tools link to "How This Project Works" section)
  - `website/docs/prompts/index.md` (modified — added Prompts #10–40, covering website deployment, GitHub Pages, hardware migration, C SDK setup, DevTool development)
  - `PromptProgression.md` (modified — added Prompt #41)

---

## Prompt #42
- **Date/Time:** 2026-04-11
- **Prompt:** "Divide, describe, and commit. Update the prompts, fix grammar. Check all the latest Claude sessions for prompts."
- **Input Tokens (est):** ~25
- **Output Tokens (est):** ~2,000
- **Commit:** `b408ab1` — Update website with Tools docs, blog post, prompt log, and DevTool Programs tab
- **Files Created/Modified:**
  - `PromptProgression.md` (modified — added Prompt #42)

---

## Prompt #43
- **Date/Time:** 2026-04-11
- **Prompt:** "Also the software on the site needs the READMEs for the GUI app and a guide on the CLI setup."
- **Input Tokens (est):** ~25
- **Output Tokens (est):** ~40,000
- **Commit:** `8401317` — Expand DevTool and Setup CLI pages with full README content
- **Files Created/Modified:**
  - `website/docs/docs/tools/devtool.md` (rewritten — expanded from summary to full documentation matching DevTool/README.md: all 7 tabs with detailed usage instructions, drawing tools, serial monitor, flash firmware, asset manager, GPIO reference, connection utility with USB/Wi-Fi walkthroughs, documentation tab, file format specifications with byte layouts, class architecture, threading model, troubleshooting table)
  - `website/docs/docs/tools/setup-cli.md` (rewritten — expanded from summary to comprehensive guide matching dev-setup/pico-and-display-first-time-setup.md: 14-step walkthrough table, hardware requirements, software installed, Pico W and Waveshare specs, C vs MicroPython rationale, display connection with side-view diagram and pin mapping, troubleshooting tables for build/flash/serial/display issues, quick reference card)
  - `PromptProgression.md` (modified — added Prompt #43)

---

## Prompt #44
- **Date/Time:** 2026-04-11
- **Prompt:** "OK, you made a dev tool where I can create assets via the display emulator. First of all, the pencil and line don't draw on the window at all — text and rectangle do. Also I want the ability to preview the asset on the Pico display if it's connected — add a button to deploy to Pico. Then we want to create another tab in the dev tool to deploy from a list of programs. For the first program I want you to create a sassy octopus that smiles and alternates between that expression and an open-mouth expression with a text chat bubble where it blurts out from a random list of unhinged hilarious conspiracies and jokes and meme statements, alternating between facial expressions. The octopus should be on the left side of the display and the chat bubble to the right of its mouth."
- **Input Tokens (est):** ~200
- **Output Tokens (est):** ~80,000
- **Commit:** `63e696b`
- **Files Created/Modified:**
  - `DevTool/devtool.py` (modified — fixed `_draw_brush` range bug that broke pencil/line tools; added Programs tab with preview/deploy; added Sassy Octopus program with pixel art, 3 mouth expressions, 30 quotes, tiny bitmap font, chat bubble rendering; made Send to Pico non-blocking with write timeout)

---

## Prompt #45
- **Date/Time:** 2026-04-11
- **Prompt:** "The octopus needs more legs and it should have less black and more curvaceous. The display emulator tab should have a preview deploy on the Pico as well."
- **Input Tokens (est):** ~40
- **Output Tokens (est):** ~30,000
- **Commit:** `151b575` — Make DevTool serial send non-blocking and backfill Prompt #40 commit hash
- **Files Created/Modified:**
  - `DevTool/devtool.py` (modified — redesigned octopus to outline style with 6 curvy tentacles, then reverted to original chunky style per user preference; added 6 tentacle legs; fixed deploy hang with write_timeout)

---

## Prompt #46
- **Date/Time:** 2026-04-11
- **Prompt:** "God the octopus looks awful, use the other octopus you made — it looked way better."
- **Input Tokens (est):** ~20
- **Output Tokens (est):** ~15,000
- **Commit:** `b408ab1` — Update website with Tools docs, blog post, prompt log, and DevTool Programs tab
- **Files Created/Modified:**
  - `DevTool/devtool.py` (modified — reverted to original chunky filled-style octopus with 6 tentacle legs, improved open-mouth with proper white interior and black border)

---

## Prompt #47
- **Date/Time:** 2026-04-11
- **Prompt:** "I don't want to see the logs — write the steps in the write-failed message. Also the logs at the bottom need to be resizable."
- **Input Tokens (est):** ~30
- **Output Tokens (est):** ~10,000
- **Commit:** `63e696b` — Add Programs tab, Sassy Octopus, IMG-receiver and standalone firmware, fix drawing tools
- **Files Created/Modified:**
  - `DevTool/devtool.py` (modified — moved deploy failure steps to status label; replaced fixed log bar with resizable PanedWindow + scrollbar + Clear button; improved port detection with Raspberry Pi VID 0x2E8A; fixed hardcoded /dev/ttyACM0 references)

---

## Prompt #48
- **Date/Time:** 2026-04-11
- **Prompt:** "Also no device found error — I changed USB ports, does that break this? If so check for the correct port in all the utils."
- **Input Tokens (est):** ~30
- **Output Tokens (est):** ~5,000
- **Commit:** `63e696b` — Add Programs tab, Sassy Octopus, IMG-receiver and standalone firmware, fix drawing tools
- **Files Created/Modified:**
  - `DevTool/devtool.py` (modified — `find_pico_serial()` now checks Raspberry Pi USB VID 0x2E8A first, then falls back to ttyACM/usbmodem name matching; connection utility uses dynamic detection instead of hardcoded paths)

---

## Prompt #49
- **Date/Time:** 2026-04-11
- **Prompt:** "It says to flash the firmware via the flash tab — where is the image, what am I flashing? Can't you do it in the Programs tab when I have the Pico in BOOTSEL mode?"
- **Input Tokens (est):** ~40
- **Output Tokens (est):** ~40,000
- **Commit:** `63e696b` — Add Programs tab, Sassy Octopus, IMG-receiver and standalone firmware, fix drawing tools
- **Files Created/Modified:**
  - `dev-setup/img-receiver/main.c` (created — Pico W firmware that receives IMG: protocol over USB serial and displays on e-ink, with landscape-to-portrait transpose and partial refresh)
  - `dev-setup/img-receiver/CMakeLists.txt` (created)
  - `dev-setup/img-receiver/lib/` (created — copied shared Waveshare/GUI libraries)
  - `dev-setup/docker-compose.yml` (modified — added build-img-receiver service)
  - `DevTool/devtool.py` (modified — added Build & Flash button to Programs tab with Docker build + BOOTSEL flash; added 3 mouth expressions: smirk, smile, open; added MOUTH_CYCLE animation; updated all error messages to reference Programs tab)

---

## Prompt #50
- **Date/Time:** 2026-04-11
- **Prompt:** "Also give the octopus more mouth expressions — I want a default smile which is a half-circle that's white and slightly off-angle from the normal mouth."
- **Input Tokens (est):** ~30
- **Output Tokens (est):** ~5,000
- **Commit:** `63e696b` — Add Programs tab, Sassy Octopus, IMG-receiver and standalone firmware, fix drawing tools
- **Files Created/Modified:**
  - `DevTool/devtool.py` (modified — added smirk expression as default: tilted half-circle with white interior; animation now cycles smirk → open → smile → open)

---

## Prompt #51
- **Date/Time:** 2026-04-12
- **Prompt:** "In the build give some more descriptive logs of what Docker is doing. Also can the logs and windows be resized on this GUI?"
- **Input Tokens (est):** ~25
- **Output Tokens (est):** ~15,000
- **Commit:** `63e696b` — Add Programs tab, Sassy Octopus, IMG-receiver and standalone firmware, fix drawing tools
- **Files Created/Modified:**
  - `DevTool/devtool.py` (modified — Docker image build step now streams output line-by-line with `[docker]` prefixed log entries; shows download/install/clone progress in real time; increased timeout to 600s; fixed sidebar panels to allow proper horizontal resizing)

---

## Prompt #52
- **Date/Time:** 2026-04-12
- **Prompt:** "I want the ability to deploy the sassy octopus fully to the Pico so I can run it without having the USB connected and it will just boot into this program standalone."
- **Input Tokens (est):** ~40
- **Output Tokens (est):** ~30,000
- **Commit:** `63e696b` — Add Programs tab, Sassy Octopus, IMG-receiver and standalone firmware, fix drawing tools
- **Files Created/Modified:**
  - `dev-setup/sassy-octopus/main.c` (created — standalone firmware that cycles pre-rendered frames on the e-ink display with partial refresh, no USB needed)
  - `dev-setup/sassy-octopus/CMakeLists.txt` (created)
  - `dev-setup/sassy-octopus/lib/` (created — copied shared Waveshare/GUI libraries)
  - `dev-setup/docker-compose.yml` (modified — added build-sassy-octopus service)
  - `DevTool/devtool.py` (modified — added Deploy Standalone button that pre-renders all 120 animation frames in Python, writes frames.h C header, Docker-builds the firmware, and flashes to Pico via BOOTSEL)

---

## Prompt #53
- **Date/Time:** 2026-04-12
- **Prompt:** "Divide, describe, and commit. Update the prompts, fix spelling, and add documentation on the new features of the tool. Update existing docs and the website and prompts file, and commit and push."
- **Input Tokens (est):** ~40
- **Output Tokens (est):** ~50,000
- **Commit:** `63e696b` — Add Programs tab, Sassy Octopus, IMG-receiver and standalone firmware, fix drawing tools
- **Files Created/Modified:**
  - `PromptProgression.md` (modified — added Prompts #44–53)
  - `README.md` (modified — updated Phase 1 checklist, added DevTool and firmware projects)
  - `DevTool/README.md` (modified — updated for 8 tabs, added Programs tab docs, updated architecture)
  - `website/docs/docs/tools/devtool.md` (modified — added Programs tab and standalone deploy documentation)
  - `website/docs/prompts/index.md` (modified — added Prompts #41–53)
  - `dev-setup/img-receiver/main.c`, `dev-setup/sassy-octopus/main.c` (spelling fixes)

---

## Prompt #54
- **Date/Time:** 2026-04-12
- **Prompt:** "Could the XIAO nRF52840, BT5.0 do the same thing as the Pi Pico in this project?"
- **Input Tokens (est):** ~25
- **Output Tokens (est):** ~4,000
- **Commit:** n/a — analysis only, no files changed
- **Files Created/Modified:** none

---

## Prompt #55
- **Date/Time:** 2026-04-12
- **Prompt:** "Give me a comparison chart for Raspberry Pi Pico, RP2040, Cortex-M0+, microUSB..." *(pasted full shopping cart with 9 boards: Pi Pico, Pi Pico H, Pi Pico 2 W, Pi Pico 2 WH, XIAO SAMD21, XIAO nRF52840+, XIAO MG24 Sense, XIAO ESP32S3+, XIAO RP2350)*
- **Input Tokens (est):** ~400
- **Output Tokens (est):** ~5,000
- **Commit:** n/a — analysis only, no files changed
- **Files Created/Modified:** none

---

## Prompt #56
- **Date/Time:** 2026-04-12
- **Prompt:** *(Pasted wrong shopping cart with microscopes, USB mouse, stool, and other non-display items — corrected in next prompt)*
- **Input Tokens (est):** ~350
- **Output Tokens (est):** ~1,500
- **Commit:** n/a — clarification, no files changed
- **Files Created/Modified:** none

---

## Prompt #57
- **Date/Time:** 2026-04-12
- **Prompt:** *(Pasted correct shopping cart with 18 items: boards, e-paper displays, LCD/TFT displays, and Pi Zeros — asked for display comparison with board compatibility, power consumption, refresh rates, and pros/cons)*
- **Input Tokens (est):** ~600
- **Output Tokens (est):** ~8,000
- **Commit:** n/a — analysis only, no files changed
- **Files Created/Modified:** none

---

## Prompt #58
- **Date/Time:** 2026-04-12
- **Prompt:** "Go in depth with the difference in the e-ink displays — what would be the improvements or detriments to each."
- **Input Tokens (est):** ~20
- **Output Tokens (est):** ~6,000
- **Commit:** n/a — analysis only, no files changed
- **Files Created/Modified:** none

---

## Prompt #59
- **Date/Time:** 2026-04-12
- **Prompt:** "OK, update the hardware research with all the details from this research and prompt session. Also update the prompts file and clean grammar and spelling. Commit and push."
- **Input Tokens (est):** ~30
- **Output Tokens (est):** ~8,000
- **Commit:** `ce2f22b` — Add board and display comparison research to hardware docs
- **Files Created/Modified:**
  - `docs/hardware-research.md` (modified — added Board Comparison table with 9 boards, Display Comparison section with 4 e-paper displays and 7 LCD/TFT alternatives, trade-off analysis, firmware impact assessments, and recommendations; updated firmware language from MicroPython to C/C++)
  - `PromptProgression.md` (modified — added Prompts #54–59, grammar and spelling cleanup)

---

## Prompt #60
- **Date/Time:** 2026-04-12
- **Prompt:** "OK, let's research LiPo batteries that I could wire up to these boards easily and run me through estimated cost and battery life on each board and wiring setup process as well."
- **Input Tokens (est):** ~40
- **Output Tokens (est):** ~10,000
- **Commit:** n/a — analysis only, no files changed
- **Files Created/Modified:** none

---

## Prompt #61
- **Date/Time:** 2026-04-12
- **Prompt:** "Could a rechargeable AAA battery work for this?"
- **Input Tokens (est):** ~15
- **Output Tokens (est):** ~3,000
- **Commit:** n/a — analysis only, no files changed
- **Files Created/Modified:** none

---

## Prompt #62
- **Date/Time:** 2026-04-12
- **Prompt:** "What about just 1 battery?"
- **Input Tokens (est):** ~10
- **Output Tokens (est):** ~2,000
- **Commit:** n/a — analysis only, no files changed
- **Files Created/Modified:** none

---

## Prompt #63
- **Date/Time:** 2026-04-12
- **Prompt:** "Update the hardware research — add a section for batteries and expected battery life. Include 2000mAh and 3000mAh options and viable options for that and expected price. Update prompts and website documentation with everything as well. Commit and push."
- **Input Tokens (est):** ~40
- **Output Tokens (est):** ~10,000
- **Commit:** `1e27cb4` — Add battery and power research to hardware docs and website
- **Files Created/Modified:**
  - `docs/hardware-research.md` (modified — added Battery & Power section with board power consumption, LiPo options up to 3000mAh, battery life estimates, charging solutions, wiring diagrams for Pico/XIAO/Pi Zero, AAA NiMH alternative, and recommendation)
  - `website/docs/docs/hardware/materials-list.md` (modified — updated battery section with specific recommendations, added no-boost-converter tip)
  - `website/docs/prompts/index.md` (modified — added Prompts #54–63)
  - `PromptProgression.md` (modified — added Prompts #60–63)

---

## Prompt #64
- **Date/Time:** 2026-04-12
- **Prompt:** "OK, the testing pulled screenshots for the website. I also need the devtool and the setup to have screenshot walkthroughs as well and detailed documentation. Also scan code changes and ensure the tests are up to date."
- **Input Tokens (est):** ~50
- **Output Tokens (est):** ~120,000
- **Commit:** *(included in multi-commit push)*
- **Files Created/Modified:**
  - `testing/devtool/test_dependency_gate.py` (created — tests for `_check_and_install_deps()` distro detection, `_check_docker_toolchain()` startup health check, and simplified output logging)
  - `testing/setup_cli/test_docker_step.py` (created — tests for Step 15 Docker install/daemon/compose detection and build file verification)
  - `testing/setup_cli/test_test_setup.py` (created — tests for `setup_testing()` function, `--test-setup` CLI flag, Docker/Testing status sections)
  - `testing/setup_cli/test_cli_screenshots.py` (created — ANSI-to-PNG rendering pipeline for CLI screenshots via Playwright)
  - `testing/setup_cli/test_prerequisites.py` (modified — added `TestTkinterPrereqCheck` and `TestPyserialPrereqCheck` classes with realistic mock run_cmd responses)
  - `testing/setup_cli/test_vscode_extensions.py` (modified — added `TestCodeOSSDetection` class covering pacman detection, codium path resolution, and proprietary VSCode fallback)
  - `testing/setup_cli/test_cli_navigation.py` (modified — updated step count from 14 to 15, added `TestTestSetupFlag` class and `--test-setup` help mention test)
  - `testing/utils/guide_generator.py` (modified — added setup_cli screenshot descriptions for help, list, status, and test-setup renders)
  - DevTool screenshots generated: 35 PNGs covering all 8 tabs (display emulator with all 6 tools, serial monitor states, flash firmware, asset manager, programs, GPIO pins, connection utility USB/WiFi modes, documentation with search)
  - Setup CLI screenshots generated: 4 PNGs for global flags (help, list, status, test-setup rendered as styled terminal HTML)
  - Test suite: 147 tests passing (90 devtool + 57 setup_cli), 0 failures
  - User guides generated: `testing/guides/devtool_guide.md` (35 screenshots), `testing/guides/setup_cli_guide.md` (4 screenshots), `testing/guides/website_guide.md` (23 screenshots)

---

## Prompt #65
- **Date/Time:** 2026-04-12
- **Prompt:** "Get a few more screenshots for the setup.py util. I want every step captured and put into documentation. Also we need to attach all the screenshots to the associated documentation and update the website to show it."
- **Input Tokens (est):** ~50
- **Output Tokens (est):** ~150,000
- **Commit:** *(included in multi-commit push)*
- **Files Created/Modified:**
  - `testing/setup_cli/test_cli_screenshots.py` (rewritten — added `TestStepScreenshots` class with parametrized tests for all 15 steps, `_capture_step_output()` helper that pipes Enter+quit to capture step headers/explanations, `TestCLIGlobalScreenshots` class for --help/--list/--status/--test-setup)
  - `testing/utils/guide_generator.py` (modified — added 15 step-by-step screenshot descriptions: `setup_cli_step_01` through `setup_cli_step_15`)
  - `website/docs/assets/images/setup-cli/` (created — 19 PNGs: 4 global flag renders + 15 individual step screenshots)
  - `website/docs/assets/images/devtool/` (created — 35 PNGs copied from testing screenshots)
  - `website/docs/docs/tools/setup-cli.md` (rewritten — added 19 embedded screenshots: help output, step list, full step-by-step walkthrough with a screenshot for each of all 15 steps, status dashboard, testing setup; updated step count to 15, added Checkpoint 3, added Code OSS detection and `--test-setup` documentation)
  - `website/docs/docs/tools/devtool.md` (rewritten — added 28 embedded screenshots: every tab overview, all 6 drawing tools individually, drawing demo, inverted canvas, save workflow, serial monitor 3 states, flash firmware with BOOTSEL detection, asset manager list and preview, programs list/preview/deploy, GPIO pin diagram, connection utility USB/WiFi modes, documentation with search; updated architecture for dependency gate, Docker health check, line count ~3400)
  - `website/docs/docs/setup/first-time-setup.md` (modified — added 7 embedded screenshots at toolchain install, Docker setup, checkpoint 1, display connection, and checkpoint 2 sections; updated step count from 14 to 15, added Step 15 Docker row, added status dashboard screenshot)
  - Test suite: 162 tests passing (90 devtool + 72 setup_cli), 0 failures
  - MkDocs site builds successfully with all 54 images resolving across 3 documentation pages

---

## Prompt #66
- **Date/Time:** 2026-04-12
- **Prompt:** "Looks good, let's update the prompts. Look through the entire list of relevant session history in Claude and ensure the entire prompts with error messages are put into the prompt history. Clean up grammar and spelling and account for any prompts that haven't been listed yet. Update while running the commits on all the staged code changes. Be descriptive and push it."
- **Input Tokens (est):** ~60
- **Output Tokens (est):** ~80,000
- **Commit:** *(see commits below)*
- **Files Created/Modified:**
  - `PromptProgression.md` (modified — added Prompts #64–66 covering testing framework creation, step screenshot capture, documentation updates with embedded images, and prompt history update)
  - `website/docs/prompts/index.md` (modified — added Prompts #64–66)

---

## Prompt #67
- **Date/Time:** 2026-04-12
- **Prompt:** "Let's continue the hardware design process. Let's make a 3D print prototyping pipeline MD analysis document and go through every viable off-the-shelf 3D printing option, technologies and price points, and use this to evaluate the most cost-effective and quickest way to CAD design and print a case and mounting system for this hardware. Give a pros and cons list between all the available 3D printing technologies and tech stacks and overhead behind it. Also deep-dive into third-party print options and the pros and cons and price options for this as well. Build a robust document for this with a TOC and pricing estimates. Give several viable options after research."
- **Input Tokens (est):** ~120
- **Output Tokens (est):** ~15,000
- **Commit:** `d61b2ff` — Add 3D printing prototyping pipeline analysis
- **Files Created/Modified:**
  - `hardware-design/3d-printing-pipeline.md` (created — comprehensive 15-section analysis covering FDM/SLA/SLS/MJF technologies, 9 third-party services deep-dived with pricing, material guide, CAD software comparison, cost estimates specific to Dilder enclosure, 5 ranked viable options, decision framework, and scaling path to injection molding)

---

## Prompt #68
- **Date/Time:** 2026-04-12
- **Prompt:** "OK, update the prompts with this and commit and push this doc and update the website as well."
- **Input Tokens (est):** ~25
- **Output Tokens (est):** ~8,000
- **Commit:** `d61b2ff` — Add 3D printing pipeline to website and update prompts
- **Files Created/Modified:**
  - `PromptProgression.md` (modified — added Prompts #67–68)
  - `website/docs/prompts/index.md` (modified — added Prompts #67–68)
  - `website/docs/docs/hardware/3d-printing-pipeline.md` (created — website copy of the pipeline analysis)
  - `website/docs/docs/hardware/enclosure-design.md` (modified — added 3D Printing Pipeline summary section with technology table, recommended approach, top services, and JLCPCB bundling tip)
  - `website/mkdocs.yml` (modified — added "3D Printing Pipeline" to Hardware nav section)

---

## Prompt #69
- **Date/Time:** 2026-04-12
- **Prompt:** "Alright we have a sassy octopus, let's make a sassy supportive octopus — same functionality but just the text should be more oriented to humorous but supportive statements, littered with unhinged but weirdly loving statements, sprinkle in some spicy language, and make a huge list of cycled text for this and add it to the programs to be deployable to the Pico."
- **Input Tokens (est):** ~80
- **Output Tokens (est):** ~12,000
- **Commit:** `da4d979`
- **Files Created/Modified:**
  - `DevTool/devtool.py` (modified — added `SUPPORTIVE_QUOTES` list with 80 quotes, added `supportive_octopus` program entry, parameterized `_draw_chat_bubble` and `_generate_octopus_frame` with tagline, refactored `_run_sassy_octopus` to generic `_run_octopus`, added `_OCTOPUS_CONFIGS` and `_FIRMWARE_DIRS` lookup dicts)
  - `dev-setup/supportive-octopus/main.c` (created — standalone Pico firmware for Supportive Octopus)
  - `dev-setup/supportive-octopus/CMakeLists.txt` (created — CMake build config)
  - `dev-setup/docker-compose.yml` (modified — added `build-supportive-octopus` service)
  - `.gitignore` (modified — added supportive-octopus build artifacts)

---

## Prompt #70
- **Date/Time:** 2026-04-12
- **Prompt:** "OK the sassy quotes are looking sparse compared to the supportive ones, let's expand on this — more unhinged, more weird, more conspiratorial, and more chaotic. Sprinkle in plenty of spicy language and swear words too. Get tin-foiled with some of them, get stupid with the others. Pull from modern memetic conspiracies. And if the quotes are especially weird, give the octopus a weird expression, and especially unhinged, make an unhinged expression."
- **Input Tokens (est):** ~100
- **Output Tokens (est):** ~15,000
- **Commit:** `da4d979`
- **Files Created/Modified:**
  - `DevTool/devtool.py` (modified — expanded `SASSY_QUOTES` from 30 to 124 entries with mood tags, added `MOUTH_WEIRD` and `MOUTH_UNHINGED` expressions with pixel art functions for wobbly sine-wave mouth and jagged scream-mouth, added `_octo_weird_eyes` with misaligned pupils and `_octo_unhinged_eyes` with tiny pinprick pupils, added `_parse_quote` and `_mood_cycle` helpers, updated all rendering and frame generation to use mood-based expression cycling)

---

## Prompt #71
- **Date/Time:** 2026-04-12
- **Prompt:** "OK the DevTool program tab is a bit wonky — when I select a display model it deselects the program. Also the display mode is hard to read once selected, the background lightness ruins the text."
- **Input Tokens (est):** ~40
- **Output Tokens (est):** ~3,000
- **Commit:** `da4d979`
- **Files Created/Modified:**
  - `DevTool/devtool.py` (modified — added `exportselection=False` to program Listbox to prevent deselection on focus loss, added `TCombobox` dark theme styling with proper `fieldbackground`/`foreground`/`selectbackground` for readonly state, added `option_add` for combobox popdown listbox dark theme)

---

## Prompt #72
- **Date/Time:** 2026-04-12
- **Prompt:** "Let's embed the sassy and supportive octopus on the website too, as a banner with all the quotes made. Have it cycle through them at the top."
- **Input Tokens (est):** ~30
- **Output Tokens (est):** ~10,000
- **Commit:** `b447aab`
- **Files Created/Modified:**
  - `website/docs/javascripts/octopus-banner.js` (created — canvas-rendered pixel art octopus with typewriter quote cycling across both sassy and supportive pools, responsive design)
  - `website/docs/stylesheets/extra.css` (modified — added octopus banner styles with dark background, blinking cursor, responsive breakpoints)
  - `website/docs/index.md` (modified — added banner div at top of homepage)
  - `website/mkdocs.yml` (modified — added `extra_javascript` for banner script)

---

## Prompt #73
- **Date/Time:** 2026-04-12
- **Prompt:** "Look at the SASSY_QUOTES and SUPPORTIVE_QUOTES blocks of strings. I want you to double the amount of quotes in each one and get weird with it — go off the rails, get unhinged, conspiratorial, and fun. Silly but match the theme for each block. Don't be afraid to swear or use spicy language."
- **Input Tokens (est):** ~80
- **Output Tokens (est):** ~18,000
- **Commit:** `23e7fd7`
- **Files Created/Modified:**
  - `DevTool/devtool.py` (modified — doubled `SASSY_QUOTES` from 124 to 252, doubled `SUPPORTIVE_QUOTES` from 80 to 160, each section expanded with theme-matched new entries)
  - `website/docs/javascripts/octopus-banner.js` (modified — updated JS quote arrays to match the expanded Python lists)

---

## Prompt #74
- **Date/Time:** 2026-04-12
- **Prompt:** "I want to ensure the programs on the Pi will also contain these quotes."
- **Input Tokens (est):** ~15
- **Output Tokens (est):** ~20,000
- **Commit:** `6b42bde`
- **Files Created/Modified:**
  - `dev-setup/sassy-octopus/main.c` (rewritten — runtime rendering engine replaces pre-baked frames; embeds body RLE, 5×7 bitmap font, all 5 mouth expressions, word-wrap text renderer, ADC-seeded PRNG; renders each frame on-the-fly)
  - `dev-setup/supportive-octopus/main.c` (rewritten — identical runtime renderer)
  - `dev-setup/sassy-octopus/CMakeLists.txt` (modified — removed GUI/Font deps, added hardware_adc and math lib)
  - `dev-setup/supportive-octopus/CMakeLists.txt` (modified — same changes)
  - `DevTool/devtool.py` (modified — replaced `_generate_frames_header` with `_generate_quotes_header` that outputs ~17KB string header instead of ~4MB bitmap data)
  - `.gitignore` (modified — `frames.h` → `quotes.h`)

---

## Prompt #75
- **Date/Time:** 2026-04-12
- **Prompt:** "OK let's look at the DevTool GUI documentation — the screenshots are nice but too damn big to really read. Can we run the test with the GUI again but with a smaller window and capture more readable screenshots?"
- **Input Tokens (est):** ~50
- **Output Tokens (est):** ~15,000
- **Commit:** `75fb79a` — Retake DevTool screenshots at compact 900x550 window size
- **Files Created/Modified:**
  - `DevTool/capture_screenshots.py` (created — automated screenshot capture script that launches the DevTool at 900x550, cycles through all 8 tabs, and saves PNGs via ImageMagick `import`)
  - `website/docs/assets/images/devtool/*.png` (35 files modified — all screenshots resized from 1908x2040 to 976x720, total image size reduced from ~2.5MB to ~1.3MB)

---

## Prompt #76
- **Date/Time:** 2026-04-12
- **Prompt:** "The website still shows the old small pics."
- **Input Tokens (est):** ~10
- **Output Tokens (est):** ~1,000
- **Commit:** n/a — confirmed GitHub Actions deployed successfully; issue was CDN cache (max-age 600s), resolved with hard refresh
- **Files Created/Modified:** none

---

## Prompt #77
- **Date/Time:** 2026-04-12
- **Prompt:** "The tool demo screenshots are all the same blank canvases — nothing shows on them in the screenshots."
- **Input Tokens (est):** ~20
- **Output Tokens (est):** ~20,000
- **Commit:** `7e06495` — Retake all DevTool screenshots with real drawn content
- **Files Created/Modified:**
  - `DevTool/capture_screenshots.py` (rewritten — draws real content for each tool: pencil sine wave, eraser with gap, crossing lines, nested rectangles, overlapping filled rects, multi-size text, house scene with roof/door/tree/sun, inverted version, simulated serial output with heartbeats, Sassy Octopus preview with quote)
  - `website/docs/assets/images/devtool/*.png` (16 detail screenshots replaced — each now shows actual tool output instead of blank canvas copies)

---

## Prompt #78
- **Date/Time:** 2026-04-12
- **Prompt:** "Perfect. Take all my prompts in this session not in the prompt progression and add them. Fix the grammar and spelling and commit."
- **Input Tokens (est):** ~25
- **Output Tokens (est):** ~8,000
- **Commit:** `608ab92` — Add Prompts #75–78 covering screenshot recapture and prompt log update
- **Files Created/Modified:**
  - `PromptProgression.md` (modified — added Prompts #75–78, grammar and spelling cleanup)

---

## Prompt #79
- **Date/Time:** 2026-04-12
- **Prompt:** "OK I have added pictures of the Pico and display setup. Compress into a smaller JPEG and delete the originals in the folders, then put them in the setup guide in the appropriate locations to give a picture of how the hardware looks and is set up."
- **Input Tokens (est):** ~50
- **Output Tokens (est):** ~10,000
- **Commit:** `a6f174c` — Add hardware photos to setup guide — compressed HEIC to JPG
- **Files Created/Modified:**
  - `website/docs/assets/images/hardware/*.jpg` (8 files created — converted from 4096x3072 HEIC to 800px-wide compressed JPG, ~985KB total down from ~21MB)
  - `docs/pictures/*.heic` (8 files deleted — originals removed after conversion)
  - `website/docs/docs/setup/first-time-setup.md` (modified — embedded photos at What You Need, Pico W at a Glance, Waveshare HAT, Seat the Display, Checkpoint 2 sections)

---

## Prompt #80
- **Date/Time:** 2026-04-12
- **Prompt:** "OK let's update the programs — the sassy and supportive octopuses. I want you to move the octopus and chat bubble down more, center vertically. Then let's add the day's date fully written out and the time without seconds, 12-hour format AM/PM, at the top middle."
- **Input Tokens (est):** ~60
- **Output Tokens (est):** ~15,000
- **Commit:** `2532778` — Add date/time header and vertically center octopus layout
- **Files Created/Modified:**
  - `DevTool/devtool.py` (modified — added date/time header rendering with `datetime.now().strftime`, centered at top; added Y_OFF=12 vertical offset to all octopus drawing; added y_offset parameter to `_draw_chat_bubble`)

---

## Prompt #81
- **Date/Time:** 2026-04-12
- **Prompt:** "The clock and height look good on the preview. I need it to also deploy via the C code as well to the Pico."
- **Input Tokens (est):** ~25
- **Output Tokens (est):** ~20,000
- **Commit:** `2864b14` — Add date/time header and vertical centering to standalone Pico firmware
- **Files Created/Modified:**
  - `dev-setup/sassy-octopus/main.c` (modified — added RTC initialization from compile-time `__DATE__`/`__TIME__`, `draw_clock_header()` with month name lookup and 12-hour format, Y_OFF=12 with `px_set_off`/`px_clr_off` helpers, offset applied to all body/eye/mouth/bubble drawing)
  - `dev-setup/sassy-octopus/CMakeLists.txt` (modified — added `hardware_rtc` to link libraries)
  - `dev-setup/supportive-octopus/main.c` (modified — same changes as sassy-octopus)
  - `dev-setup/supportive-octopus/CMakeLists.txt` (modified — added `hardware_rtc`)

---

## Prompt #82
- **Date/Time:** 2026-04-12
- **Prompt:** "Perfect. Update the prompts with this and commit."
- **Input Tokens (est):** ~10
- **Output Tokens (est):** ~5,000
- **Commit:** `17d0953` — Add Prompts #79–82 covering hardware photos, clock header, and Pico deploy
- **Files Created/Modified:**
  - `PromptProgression.md` (modified — added Prompts #79–82, backfilled commit hash for Prompt #78)

---

## Prompt #83
- **Date/Time:** 2026-04-12
- **Prompt:** "OK let's make an angry octopus program. We need to change its eyes to be two slanted half-circles angled in an angry way, then compile a list of nonsensical wacky kind-of-mean quotes but still cute. Then we also want to split out the sassy octopus and pull out the conspiratorial crazy statements into a conspiratorial octopus program. And if there are other emotional states we can map into a program, let's create those as well. Get fun and weird with the quotes and make sure they match the emotion state."
- **Input Tokens (est):** ~100
- **Output Tokens (est):** ~60,000
- **Commit:** `d0cc8fb` — Add Angry, Conspiratorial, Sad, and Chaotic octopus programs
- **Files Created/Modified:**
  - `DevTool/devtool.py` (modified — added MOUTH_ANGRY/SAD/CHAOTIC expressions with pixel art, angry slanted half-circle eyebrows, sad droopy brows, chaotic spiral eyes, angry frown mouth, sad frown, chaotic zigzag mouth, per-program default_mood, ANGRY_QUOTES 45 entries, CONSPIRATORIAL_QUOTES 47 entries split from sassy, SAD_QUOTES 35 entries, CHAOTIC_QUOTES 40 entries, 6 programs registered in PROGRAMS/_OCTOPUS_CONFIGS/_FIRMWARE_DIRS)
  - `dev-setup/angry-octopus/main.c`, `dev-setup/angry-octopus/CMakeLists.txt` (created)
  - `dev-setup/conspiratorial-octopus/main.c`, `dev-setup/conspiratorial-octopus/CMakeLists.txt` (created)
  - `dev-setup/sad-octopus/main.c`, `dev-setup/sad-octopus/CMakeLists.txt` (created)
  - `dev-setup/chaotic-octopus/main.c`, `dev-setup/chaotic-octopus/CMakeLists.txt` (created)
  - `dev-setup/docker-compose.yml` (modified — added 4 new build services)
  - `.gitignore` (modified — added new firmware build/lib/quote artifacts)

---

## Prompt #84
- **Date/Time:** 2026-04-12
- **Prompt:** "That's pretty great. Let's fix the angry one's eyes — they should look like slanted half-circles."
- **Input Tokens (est):** ~20
- **Output Tokens (est):** ~8,000
- **Commit:** `cba64b2` — Fix angry octopus eyebrows — thick slanted half-circle arcs
- **Files Created/Modified:**
  - `DevTool/devtool.py` (modified — rewrote `_octo_angry_eyes()` with proper thick curved arcs using sine-wave sweep across the eye socket width, 3px thick with extra fill, outer high / inner low for V-furrowed brow look)

---

## Prompt #85
- **Date/Time:** 2026-04-12
- **Prompt:** "The angry eyes look good on the preview but the C program eyes don't match — the pupils should be close to the nose and downward."
- **Input Tokens (est):** ~25
- **Output Tokens (est):** ~20,000
- **Commit:** `db5d6cd` — Add angry/sad/chaotic expressions to standalone Pico firmware
- **Files Created/Modified:**
  - `dev-setup/sassy-octopus/main.c` (modified — added MOOD_ANGRY/SAD/CHAOTIC constants, EXPR_ANGRY/SAD/CHAOTIC, `draw_pupils_angry()` with inward+down shifted pupils, `draw_brows_angry()` with matching half-circle arcs, `draw_pupils_sad()` with downward pupils, `draw_brows_sad()` with droopy arcs, `draw_pupils_chaotic()` with spiral ring eyes, `draw_mouth_angry/sad/chaotic()`, updated expression cycles and render_frame switch)
  - All 5 other octopus firmware main.c files updated with same changes

---

## Prompt #86
- **Date/Time:** 2026-04-12
- **Prompt:** "OK update the webpage implementation as well with the new quotes and emotion states."
- **Input Tokens (est):** ~15
- **Output Tokens (est):** ~15,000
- **Commit:** `038ba93` — Add all 6 octopus emotion states to website banner
- **Files Created/Modified:**
  - `website/docs/javascripts/octopus-banner.js` (modified — added ANGRY, CONSPIRATORIAL, SAD, CHAOTIC quote arrays with 25 entries each, updated `buildPool()` to include all 6 pools, updated `updateMode()` with labels and CSS classes for all 6 modes)
  - `website/docs/stylesheets/extra.css` (modified — added `.octo-mode-angry` red, `.octo-mode-conspiratorial` yellow, `.octo-mode-sad` blue, `.octo-mode-chaotic` orange accent colors)

---

## Prompt #87
- **Date/Time:** 2026-04-12
- **Prompt:** "Update the prompts with the latest ones not added and fix grammar and push."
- **Input Tokens (est):** ~15
- **Output Tokens (est):** ~8,000
- **Commit:** `59921bf` — Add Prompts #83–87 covering new octopus programs, expression fixes, and website banner
- **Files Created/Modified:**
  - `PromptProgression.md` (modified — added Prompts #83–87, backfilled commit hash for Prompt #82)

---

## Prompt #88
- **Date/Time:** 2026-04-12
- **Prompt:** "Let's add a hungry and tired and slap happy octopus as well. Implement this on the webpage, on the DevTool preview, and in the C program. Come up with a really good set of quotes for each state."
- **Input Tokens (est):** ~40
- **Output Tokens (est):** ~40,000
- **Commit:** `b8bdf54` — Add Hungry, Tired, and Slap Happy octopus programs
- **Files Created/Modified:**
  - `DevTool/devtool.py` (modified — added MOUTH_HUNGRY/TIRED/SLAPHAPPY expressions, hungry upward-staring eyes, tired half-closed eyelids, slap-happy one-squint-one-manic eyes, drooling mouth, yawn mouth, wobbly grin, HUNGRY_QUOTES 30, TIRED_QUOTES 30, SLAPHAPPY_QUOTES 30, 3 new programs registered)
  - `dev-setup/hungry-octopus/`, `dev-setup/tired-octopus/`, `dev-setup/slaphappy-octopus/` (created — main.c + CMakeLists.txt)
  - All 9 octopus firmware main.c files updated with new expressions
  - `dev-setup/docker-compose.yml` (modified — 3 new build services)
  - `.gitignore` (modified — new build/lib entries)
  - `website/docs/javascripts/octopus-banner.js` (modified — 3 new quote arrays, labels, sources)
  - `website/docs/stylesheets/extra.css` (modified — hungry pink, tired gray, slap-happy teal)

---

## Prompt #89
- **Date/Time:** 2026-04-12
- **Prompt:** "Let's add a lazy octopus and a fat octopus and chill octopus and creepy octopus."
- **Input Tokens (est):** ~20
- **Output Tokens (est):** ~80,000
- **Commit:** `d053296` — Add Lazy, Fat, Chill, Creepy, Excited, Nostalgic, and Homesick octopus programs
- **Files Created/Modified:**
  - `DevTool/devtool.py` (modified — added 7 new expression types: lazy nearly-shut eyes + flat mouth, fat wide pupils + cheek puffs, chill side-glancing + half-smile, creepy heart-shaped pupils + tongue, excited sparkle crosses + wide grin, nostalgic up-right looking + wistful smile, homesick teary eyes + wobbly line; 7 quote lists of 30 each; 7 programs registered)
  - 7 new firmware directories created (lazy/fat/chill/creepy/excited/nostalgic/homesick-octopus)
  - All 16 firmware main.c files updated
  - Docker, gitignore, website JS + CSS all updated

---

## Prompt #90
- **Date/Time:** 2026-04-12
- **Prompt:** "Excited as well and nostalgic."
- **Input Tokens (est):** ~5
- **Output Tokens (est):** ~500
- **Commit:** `ec59806` — Add Prompts #88-95, update website docs for 16 programs and body animations
- **Files Created/Modified:** (included in Prompt #89 commit — both were added in the same batch)

---

## Prompt #91
- **Date/Time:** 2026-04-12
- **Prompt:** "Homesick too."
- **Input Tokens (est):** ~5
- **Output Tokens (est):** ~500
- **Commit:** `ec59806` — Add Prompts #88-95, update website docs for 16 programs and body animations
- **Files Created/Modified:** (included in Prompt #89 commit)

---

## Prompt #92
- **Date/Time:** 2026-04-12
- **Prompt:** "The emotion state doc shouldn't have checkboxes. Also you didn't produce any images of the state or animation for me to view — you only explained it."
- **Input Tokens (est):** ~30
- **Output Tokens (est):** ~15,000
- **Commit:** `efcb22b` — Replace emotion states doc with rendered previews, remove checkboxes
- **Files Created/Modified:**
  - `assets/octopus-emotion-states.md` (rewritten — removed all checkboxes and tracker tables, replaced with clean visual gallery showing each octopus face)
  - `assets/emotion-previews/*.png` (17 files created — rendered at 2x scale from the DevTool engine, one per emotion state)

---

## Prompt #93
- **Date/Time:** 2026-04-12
- **Prompt:** "Let's make some body movement animations and head deformations to match with the emotional states in various ways as well."
- **Input Tokens (est):** ~25
- **Output Tokens (est):** ~50,000
- **Commit:** `b5a3b2f` — Add body movement animations and head deformations per emotional state
- **Files Created/Modified:**
  - `DevTool/devtool.py` (modified — added `_body_transform(mood, frame_count)` returning dx/dy/x_expand/row_wobble per mood, modified `_generate_octopus_frame` to accept `frame_count` and apply transforms to body spans and pixel offsets)
  - All 16 firmware main.c files updated with matching C `setup_body_transform()` function, `draw_body_transformed()`, per-row wobble globals, and `render_frame` now takes `frame_idx` parameter
  - `assets/emotion-previews/*-anim.png` (17 animation strip PNGs created — 4-frame strips showing body movement per mood)
  - `assets/octopus-emotion-states.md` (updated — added animation strips and body animation descriptions to every emotion state)

---

## Prompt #94
- **Date/Time:** 2026-04-12
- **Prompt:** "Also I want images of just the octopus in the MD document, focusing on the animations and clearly annotated and described in each picture. Make a robust set, then apply it."
- **Input Tokens (est):** ~30
- **Output Tokens (est):** ~5,000
- **Commit:** `ec59806` — Add Prompts #88-95, update website docs for 16 programs and body animations
- **Files Created/Modified:** (included in Prompt #93 commit — animation strips were generated in that batch)

---

## Prompt #95
- **Date/Time:** 2026-04-12
- **Prompt:** "OK let's look through the session prompts and add them to the prompt document, then update all the webpages with the new documents and documentation. Fix spelling and grammar too."
- **Input Tokens (est):** ~30
- **Output Tokens (est):** ~30,000
- **Commit:** *(see below)*
- **Files Created/Modified:**
  - `PromptProgression.md` (modified — added Prompts #88–95, backfilled commit hash for Prompt #87)
  - `website/docs/prompts/index.md` (modified — added Prompts #88–95)
  - `website/docs/docs/tools/devtool.md` (modified — updated Programs tab section for 16 programs, added body animation documentation)

---

## Prompt #96
- **Date/Time:** 2026-04-12
- **Prompt:** "OK let's export the octopus and its facial expressions and animations into the assets folder, label and map all the available combinations, and then plan for new implementation. For every emotional state of the octopus planned we need to start moving the body according to its state as well. Give me a nice exhaustive combination of assets that eventually can be put into the C program upon approval. Give me an MD document to outline each state and provide a check mark and notes option for each state for improvements later in Claude."
- **Input Tokens (est):** ~100
- **Output Tokens (est):** ~15,000
- **Commit:** `deb3291` — Add custom fat/lazy octopus bodies, C-faithful renderer, keyboard input plan, and Prompts #96-104
- **Files Created/Modified:**
  - `assets/octopus-emotion-states.md` (created — comprehensive tracker doc with all 13 emotional states, per-feature tables, body motion priority matrix, implementation approach for RLE body transforms, animation cycle reference, and source file reference)

---

## Prompt #97
- **Date/Time:** 2026-04-12
- **Prompt:** "What would it take to map the keyboard actions for the time being to the Pico so that I can play around with user actions on the octopus? Create an MD in the docs and dive into the options."
- **Input Tokens (est):** ~40
- **Output Tokens (est):** ~20,000
- **Commit:** `deb3291` — Add custom fat/lazy octopus bodies, C-faithful renderer, keyboard input plan, and Prompts #96-104
- **Files Created/Modified:**
  - `docs/keyboard-to-pico-input.md` (created — explores 3 options: Serial Command Mode over existing USB CDC, GPIO Button Array on free pins GP0-GP4, and Hybrid; includes full key mapping table for 30+ commands covering mood selection, expression override, animation control, body motion, quote control, and system commands; provides C code snippets for handle_command(), polling main loop, and state variables; GPIO pinout diagram; DevTool integration mockup; 10-step implementation plan)

---

## Prompt #98
- **Date/Time:** 2026-04-12
- **Prompt:** "The fat and lazy octopus legs are hard to differentiate between which leg is which. Perhaps for the fat one make the octopus fat up top with a bit thicker legs, and with the lazy one make it lounge on its side with a tentacle on its belly lying like a French woman."
- **Input Tokens (est):** ~50
- **Output Tokens (est):** ~40,000
- **Commit:** `deb3291` — Add custom fat/lazy octopus bodies, C-faithful renderer, keyboard input plan, and Prompts #96-104
- **Files Created/Modified:**
  - `dev-setup/fat-octopus/main.c` (modified — replaced `body_rle[]` with custom wider body: dome starts 2 rows higher, +5px per side at peak, no waist taper, tentacles widened +1px per side; updated `setup_body_transform` to remove `body_x_expand=3` since body is inherently fat)
  - `dev-setup/lazy-octopus/main.c` (modified — replaced `body_rle[]` with reclining pose: asymmetric body sloping rightward, belly tentacle overlay function, sprawling tentacles; updated `setup_body_transform`)
  - `DevTool/devtool.py` (modified — added `_octo_body_fat()`, `_octo_body_lazy()`, `_octo_belly_tentacle_lazy()`, updated `_body_transform()` and `_generate_octopus_frame()` to use mood-specific bodies)

---

## Prompt #99
- **Date/Time:** 2026-04-12
- **Prompt:** "Use the C implementation of the animations and produce accurately a set of images in the assets folder to compare against the Python."
- **Input Tokens (est):** ~25
- **Output Tokens (est):** ~50,000
- **Commit:** `deb3291` — Add custom fat/lazy octopus bodies, C-faithful renderer, keyboard input plan, and Prompts #96-104
- **Files Created/Modified:**
  - `assets/render_c_previews.py` (created — standalone Python script that is a 1:1 port of every C firmware drawing function: `fill_circle`, all `draw_pupils_*`, `draw_brows_*`, `draw_lids_*`, `draw_mouth_*`, body RLE decode, chat bubble, body transforms, and row wobble; renders all 16 moods to PNG at 4x scale plus a comparison grid)
  - `assets/c-render/*.png` (16 individual mood PNGs + `_grid_all_moods.png` generated)
  - `assets/py-render/*.png` (16 Python devtool renders regenerated for comparison)
  - `assets/c-vs-python-key-comparison.png` (created — side-by-side Normal/Fat/Lazy comparison)
  - `assets/c-vs-python-comparison.png` (created — side-by-side all 16 moods)

---

## Prompt #100
- **Date/Time:** 2026-04-12
- **Prompt:** "Lazy octopus looks weird. Just have him sit on his side with his legs draped to the right."
- **Input Tokens (est):** ~20
- **Output Tokens (est):** ~15,000
- **Commit:** `deb3291` — Add custom fat/lazy octopus bodies, C-faithful renderer, keyboard input plan, and Prompts #96-104
- **Files Created/Modified:**
  - `dev-setup/lazy-octopus/main.c` (modified — replaced reclining body_rle with simpler design: standard head dome + body, cheeks taper rightward, all 5 tentacles sweep diagonally to the right with organic sine wobble; removed `draw_belly_tentacle_lazy()` call from render_frame)
  - `DevTool/devtool.py` (modified — updated `_octo_body_lazy()` to match new tentacles-draped-right design, removed belly tentacle from frame builder)
  - `assets/render_c_previews.py` (modified — updated `BODY_RLE_LAZY` and removed belly tentacle from `MOOD_CONFIG`)
  - All preview PNGs regenerated

---

## Prompt #101
- **Date/Time:** 2026-04-12
- **Prompt:** "Compare the C renders with the Python images and make sure they line up. Also with the C render, split up each octopus into its own image file named like the emotion previews."
- **Input Tokens (est):** ~30
- **Output Tokens (est):** ~10,000
- **Commit:** `deb3291` — Add custom fat/lazy octopus bodies, C-faithful renderer, keyboard input plan, and Prompts #96-104
- **Files Created/Modified:**
  - `assets/render_c_previews.py` (modified — added full `setup_body_transform()` with body_dx/dy/x_expand/wobble matching C firmware, added `body_x_expand` to `draw_body()`, added `row_wobble()` to `px_set_off`/`px_clr_off`)
  - `assets/emotion-previews/*.png` (all 34 files regenerated — 17 statics + 17 anim strips from C-faithful renderer)
  - `assets/c-render/*.png` (regenerated with body transforms applied)
  - `assets/py-render/*.png` (regenerated for comparison)
  - Pixel comparison: 10/16 moods pixel-perfect match, remaining 6 within 256 pixels (sinf rounding)

---

## Prompt #102
- **Date/Time:** 2026-04-12
- **Prompt:** "C renders need to be generated now too."
- **Input Tokens (est):** ~10
- **Output Tokens (est):** ~500
- **Commit:** `deb3291` — Add custom fat/lazy octopus bodies, C-faithful renderer, keyboard input plan, and Prompts #96-104
- **Files Created/Modified:**
  - `assets/c-render/*.png` (regenerated — 16 individual PNGs + grid)

---
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
