rompasaurus/regardedPal/Gamplay Planning/14-encounters-geocaching-collectibles.md

# 14 — Dilder Encounters, Geocaching Challenges & Collectible System

> Proximity-triggered encounters between Dilders, riddle-based geocaching treasure hunts with physical electronic prizes, and a collectible ecosystem that doubles as a community growth engine.

---

## Overview

This document extends the existing peer discovery protocol (see `peer-discovery-research.md`) and treasure hunt system (see `user-engagement-plan.md` §13) into a three-layer gameplay and marketing system:
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
