rompasaurus/regardedPal/assets/images/hardware/hello-dilder-running.jpg

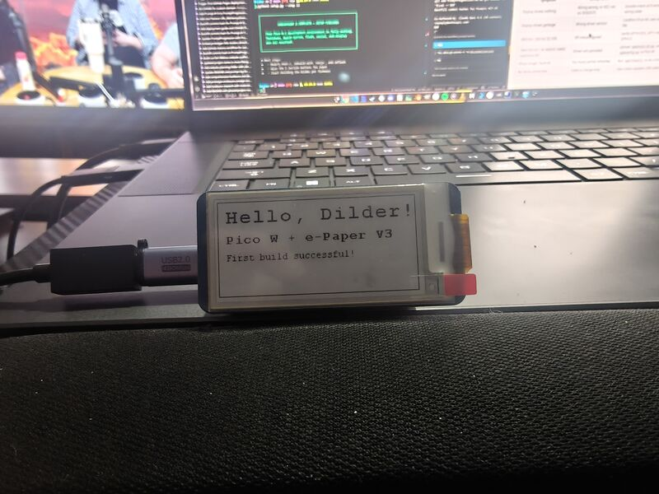
assets/images/hardware/hello-dilder-running.jpg
