rompasaurus/regardedPal/assets/images/hardware/pico-mounted-on-hat-side.jpg

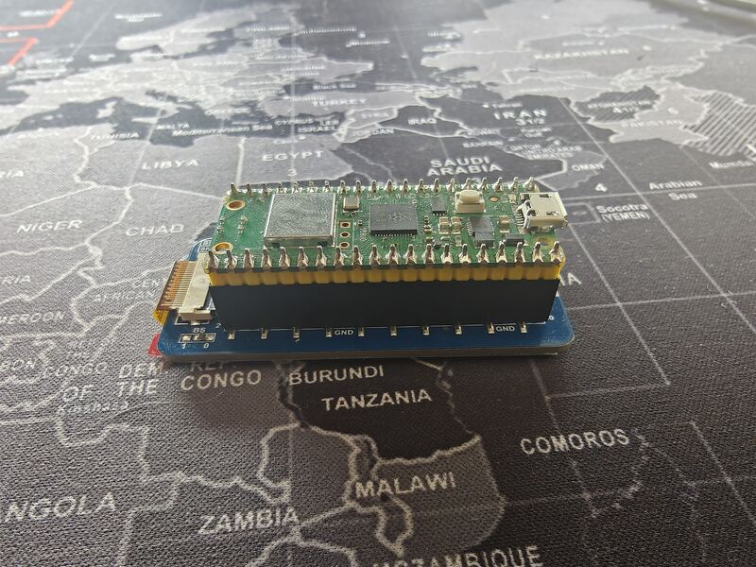
assets/images/hardware/pico-mounted-on-hat-side.jpg
