rompasaurus/regardedPal/assets/images/hardware/pico-mounted-on-hat-top.jpg

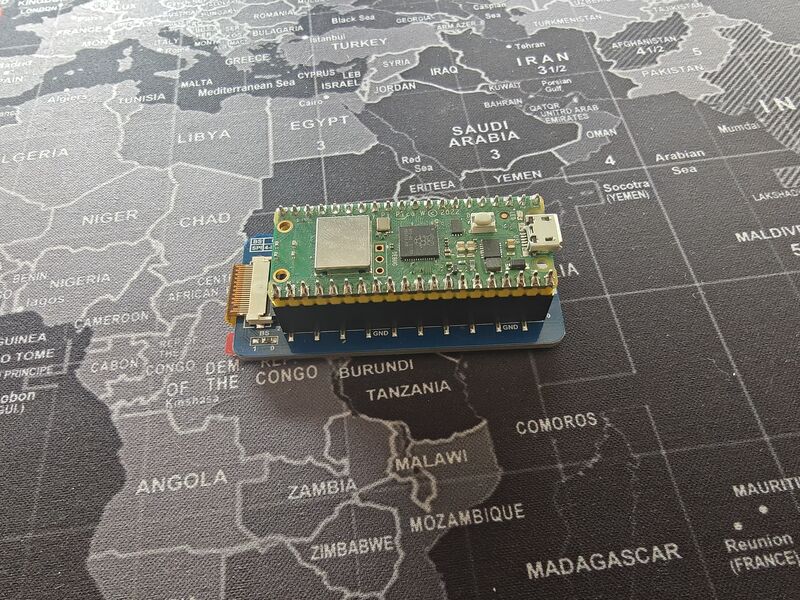
assets/images/hardware/pico-mounted-on-hat-top.jpg
