rompasaurus/regardedPal/assets/images/hardware/pico-w-and-display-separated.jpg

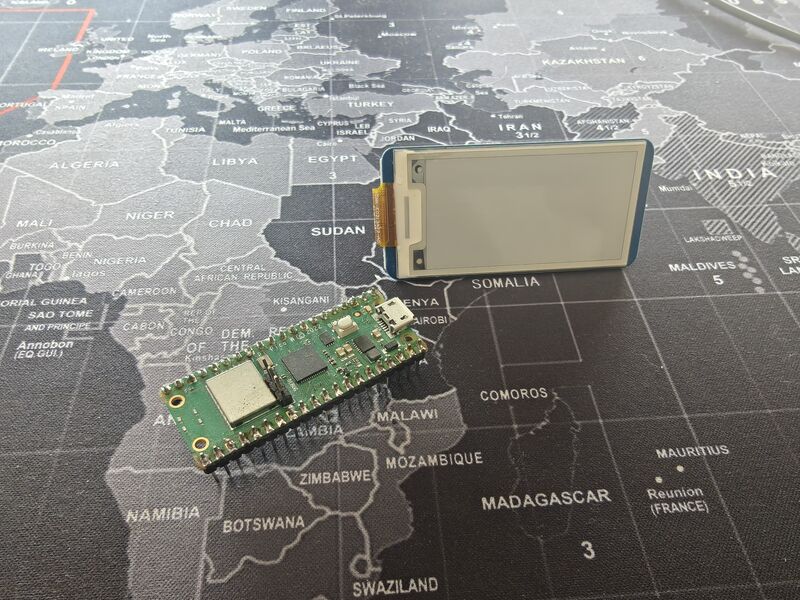
assets/images/hardware/pico-w-and-display-separated.jpg
