rompasaurus/regardedPal/assets/images/hardware/pico-w-board.jpg

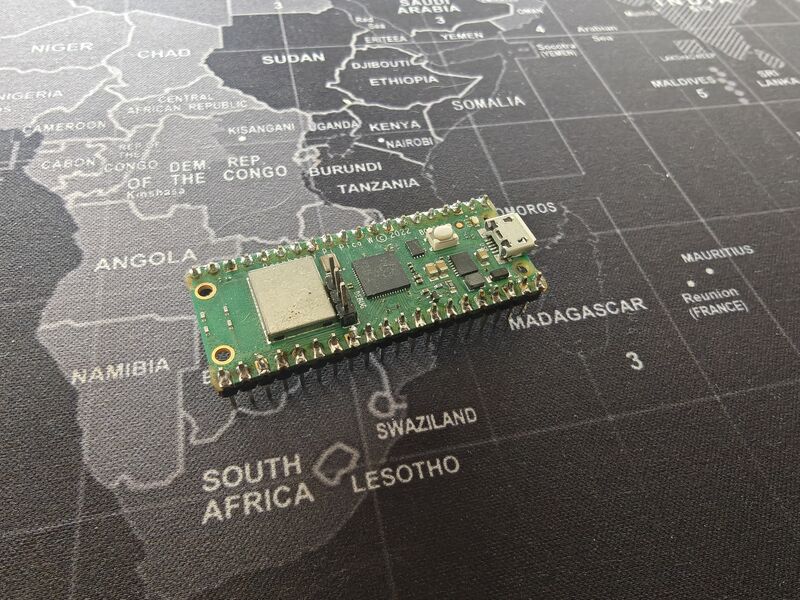
assets/images/hardware/pico-w-board.jpg
