rompasaurus/regardedPal/assets/images/hardware/waveshare-hat-back.jpg

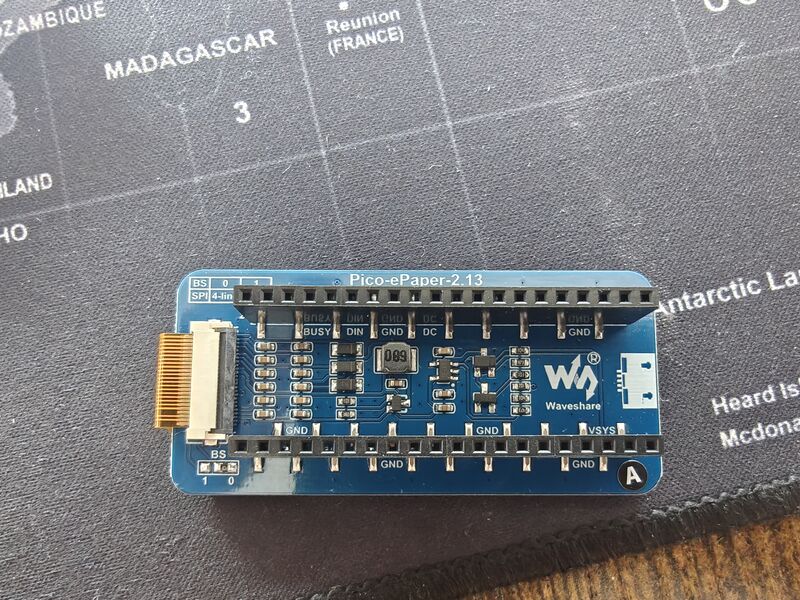
assets/images/hardware/waveshare-hat-back.jpg
