rompasaurus/regardedPal/hardware-design/examples/01-pocketmage-pda/Docs/Documents & Advanced/Assets/App Loader/Image200.bmp

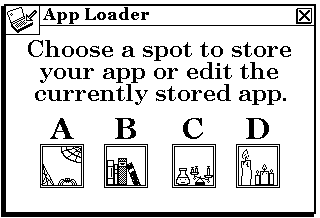
hardware-design/examples/01-pocketmage-pda/Docs/Documents & Advanced/Assets/App Loader/Image200.bmp
