rompasaurus/regardedPal/hardware-design/examples/01-pocketmage-pda/Docs/Documents & Advanced/Assets/Calendar/calendar00.bmp

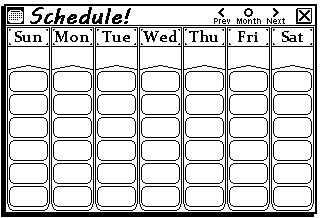
hardware-design/examples/01-pocketmage-pda/Docs/Documents & Advanced/Assets/Calendar/calendar00.bmp
