rompasaurus/regardedPal/hardware-design/examples/01-pocketmage-pda/Docs/Documents & Advanced/Assets/File Wizard/fileWiz1.bmp

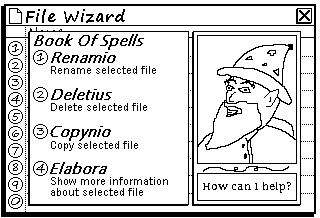
hardware-design/examples/01-pocketmage-pda/Docs/Documents & Advanced/Assets/File Wizard/fileWiz1.bmp
