rompasaurus/regardedPal/hardware-design/examples/01-pocketmage-pda/Docs/Documents & Advanced/Assets/File Wizard/fileWiz2.bmp

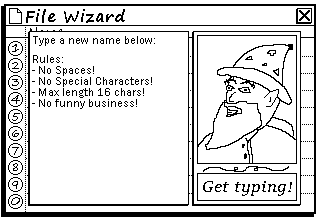
hardware-design/examples/01-pocketmage-pda/Docs/Documents & Advanced/Assets/File Wizard/fileWiz2.bmp
