rompasaurus/regardedPal/hardware-design/examples/01-pocketmage-pda/Docs/Documents & Advanced/Assets/Font Czar/font0.bmp

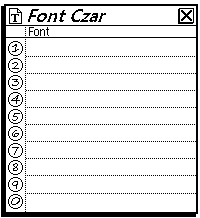
hardware-design/examples/01-pocketmage-pda/Docs/Documents & Advanced/Assets/Font Czar/font0.bmp
