rompasaurus/regardedPal/hardware-design/examples/01-pocketmage-pda/Docs/Documents & Advanced/Assets/Now and Later/nowAndLater3.bmp

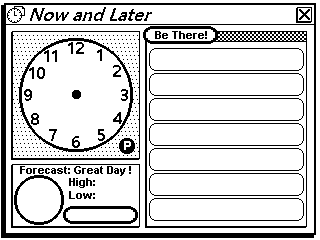
hardware-design/examples/01-pocketmage-pda/Docs/Documents & Advanced/Assets/Now and Later/nowAndLater3.bmp
