rompasaurus/regardedPal/hardware-design/examples/01-pocketmage-pda/Docs/Documents & Advanced/Assets/ScreenSaver/New folder/beautifulhair_b4by_dr1v3r.bmp

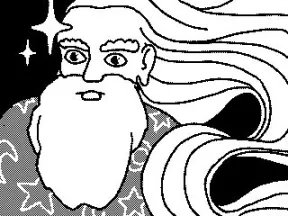
hardware-design/examples/01-pocketmage-pda/Docs/Documents & Advanced/Assets/ScreenSaver/New folder/beautifulhair_b4by_dr1v3r.bmp
