rompasaurus/regardedPal/hardware-design/examples/01-pocketmage-pda/Docs/Documents & Advanced/Assets/ScreenSaver/New folder/betterworld_JosieBB.bmp

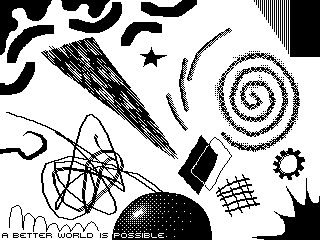
hardware-design/examples/01-pocketmage-pda/Docs/Documents & Advanced/Assets/ScreenSaver/New folder/betterworld_JosieBB.bmp
