rompasaurus/regardedPal/hardware-design/examples/01-pocketmage-pda/Docs/Documents & Advanced/Assets/ScreenSaver/New folder/chad_rein.bmp

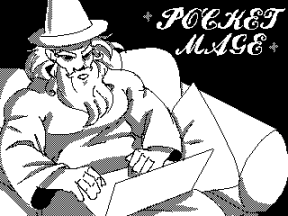
hardware-design/examples/01-pocketmage-pda/Docs/Documents & Advanced/Assets/ScreenSaver/New folder/chad_rein.bmp
