rompasaurus/regardedPal/hardware-design/examples/01-pocketmage-pda/Docs/Documents & Advanced/Assets/ScreenSaver/New folder/classic (1).bmp

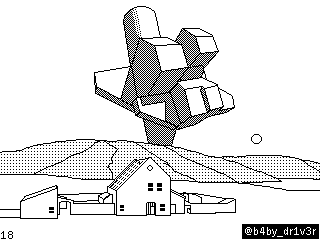
hardware-design/examples/01-pocketmage-pda/Docs/Documents & Advanced/Assets/ScreenSaver/New folder/classic (1).bmp
