rompasaurus/regardedPal/hardware-design/examples/01-pocketmage-pda/Docs/Documents & Advanced/Assets/ScreenSaver/New folder/classic (2).bmp

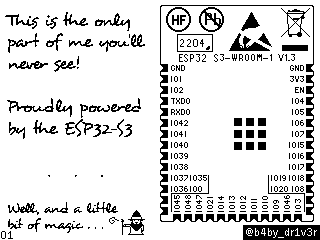
hardware-design/examples/01-pocketmage-pda/Docs/Documents & Advanced/Assets/ScreenSaver/New folder/classic (2).bmp
