rompasaurus/regardedPal/hardware-design/examples/01-pocketmage-pda/Docs/Documents & Advanced/Assets/screensavers/appzap_Omiopi.bmp

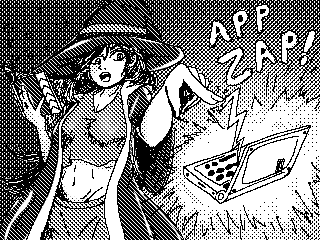
hardware-design/examples/01-pocketmage-pda/Docs/Documents & Advanced/Assets/screensavers/appzap_Omiopi.bmp
