rompasaurus/regardedPal/hardware-design/examples/01-pocketmage-pda/Docs/Documents & Advanced/Assets/screensavers/castle_Nora.bmp

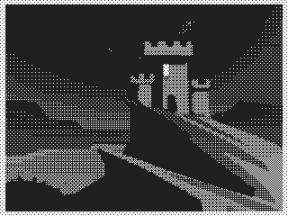
hardware-design/examples/01-pocketmage-pda/Docs/Documents & Advanced/Assets/screensavers/castle_Nora.bmp
