rompasaurus/regardedPal/hardware-design/examples/01-pocketmage-pda/Docs/Documents & Advanced/Assets/screensavers/powerbeam_forest927.bmp

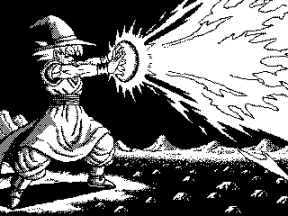
hardware-design/examples/01-pocketmage-pda/Docs/Documents & Advanced/Assets/screensavers/powerbeam_forest927.bmp
