rompasaurus/regardedPal/hardware-design/examples/01-pocketmage-pda/Docs/Documents & Advanced/Assets/screensavers/startrails_Fin.bmp

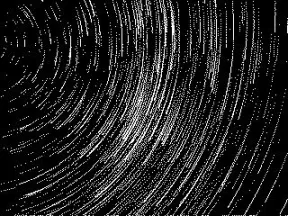
hardware-design/examples/01-pocketmage-pda/Docs/Documents & Advanced/Assets/screensavers/startrails_Fin.bmp
