rompasaurus/regardedPal/hardware-design/examples/01-pocketmage-pda/Docs/Documents & Advanced/Assets/Settings/settings0.bmp

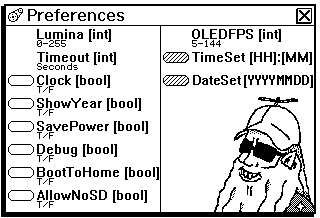
hardware-design/examples/01-pocketmage-pda/Docs/Documents & Advanced/Assets/Settings/settings0.bmp
