rompasaurus/regardedPal/hardware-design/examples/01-pocketmage-pda/Docs/Documents & Advanced/Assets/Tasks/1.bmp

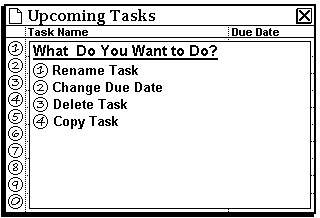
hardware-design/examples/01-pocketmage-pda/Docs/Documents & Advanced/Assets/Tasks/1.bmp
