rompasaurus/regardedPal/hardware-design/examples/01-pocketmage-pda/Docs/Documents & Advanced/Assets/usb/Image20.bmp

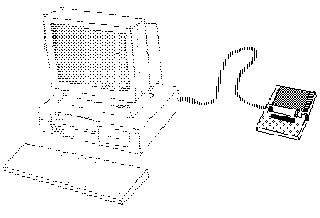
hardware-design/examples/01-pocketmage-pda/Docs/Documents & Advanced/Assets/usb/Image20.bmp
