rompasaurus/regardedPal/hardware-design/examples/09-bitwiseajeet-tp4056/PICTURES/75.png

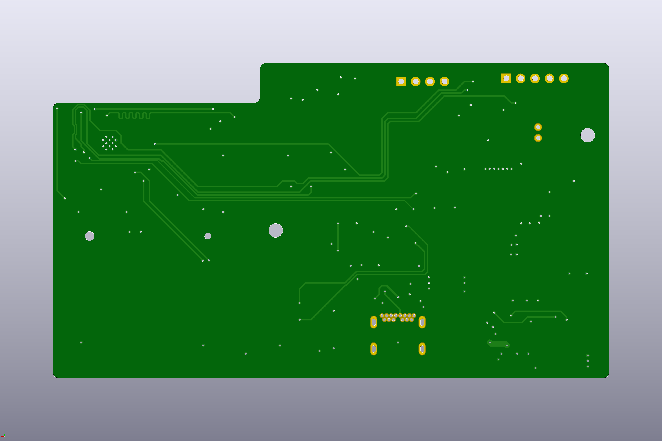
hardware-design/examples/09-bitwiseajeet-tp4056/PICTURES/75.png
