rompasaurus/regardedPal/hardware-design/examples/09-bitwiseajeet-tp4056/PICTURES/ESP32 PCB11.png

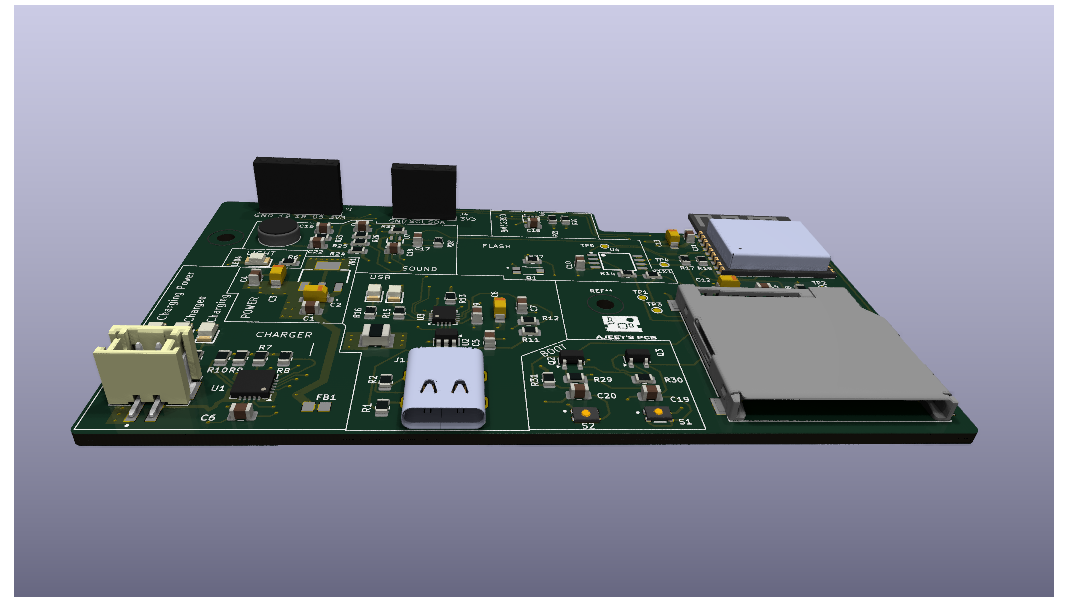
hardware-design/examples/09-bitwiseajeet-tp4056/PICTURES/ESP32 PCB11.png
