rompasaurus/regardedPal/hardware-design/examples/09-bitwiseajeet-tp4056/PICTURES/PCB HQQ.png

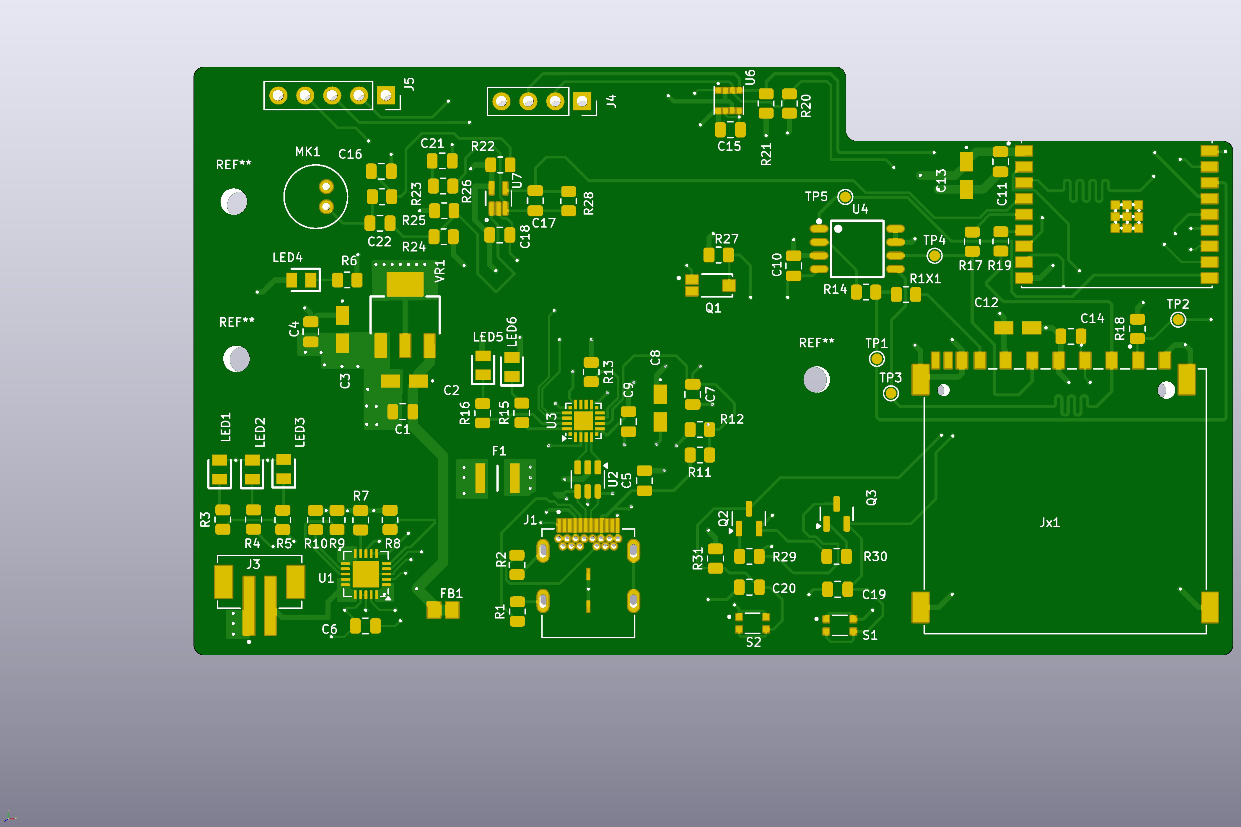
hardware-design/examples/09-bitwiseajeet-tp4056/PICTURES/PCB HQQ.png
