rompasaurus/regardedPal/hardware-design/examples/09-bitwiseajeet-tp4056/PICTURES/Screenshot 2025-06-28 162114.png

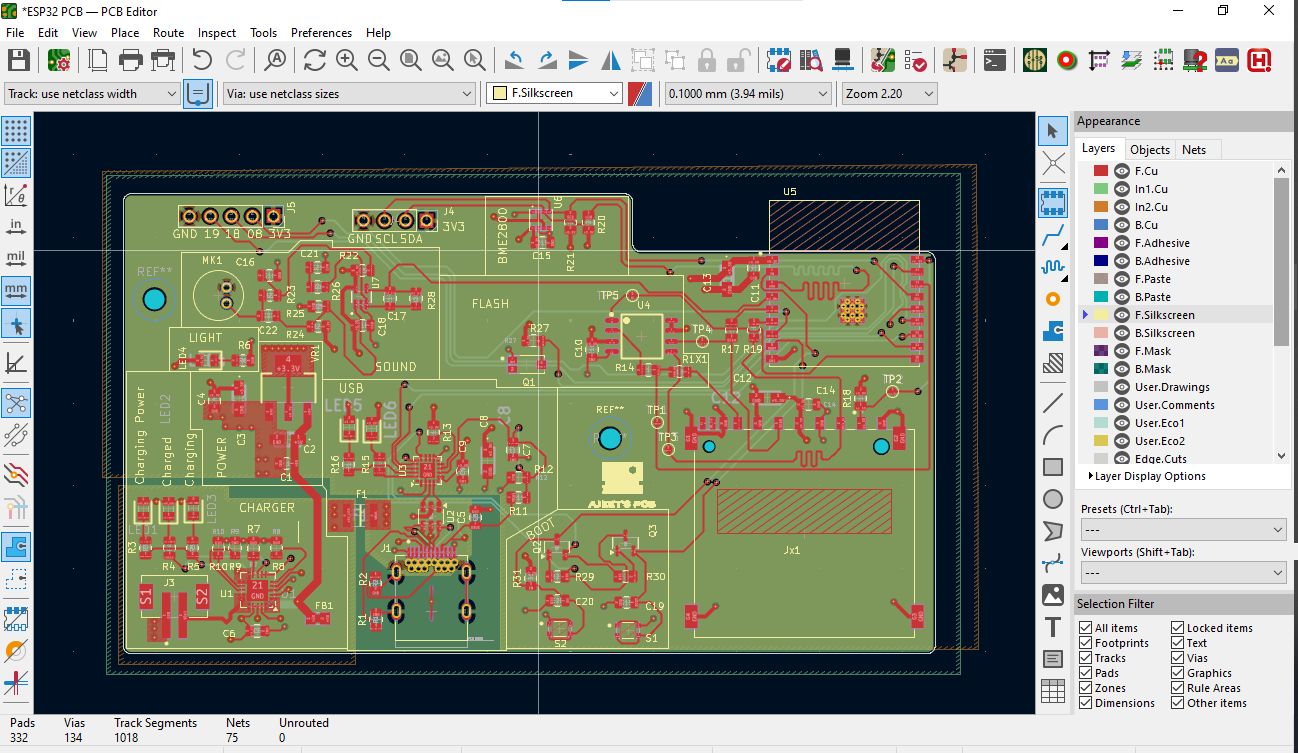
hardware-design/examples/09-bitwiseajeet-tp4056/PICTURES/Screenshot 2025-06-28 162114.png
