rompasaurus/regardedPal/hardware-design/renders/var-06a-angle-front-right.png

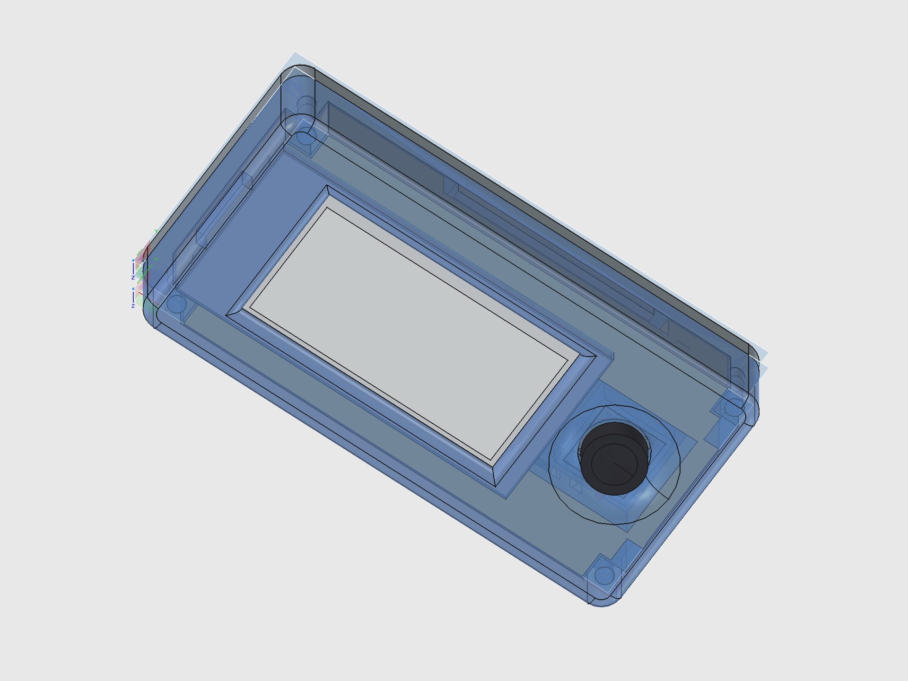
hardware-design/renders/var-06a-angle-front-right.png
