rompasaurus/regardedPal/hardware-design/renders/var-06b-angle-front-left.png

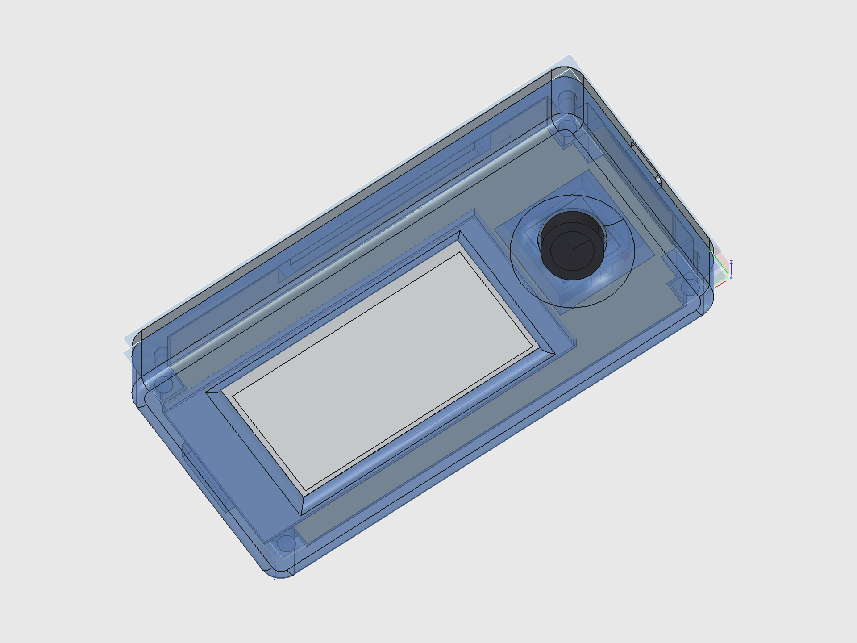
hardware-design/renders/var-06b-angle-front-left.png
