rompasaurus/regardedPal/hardware-design/renders/var-06d-angle-rear.png

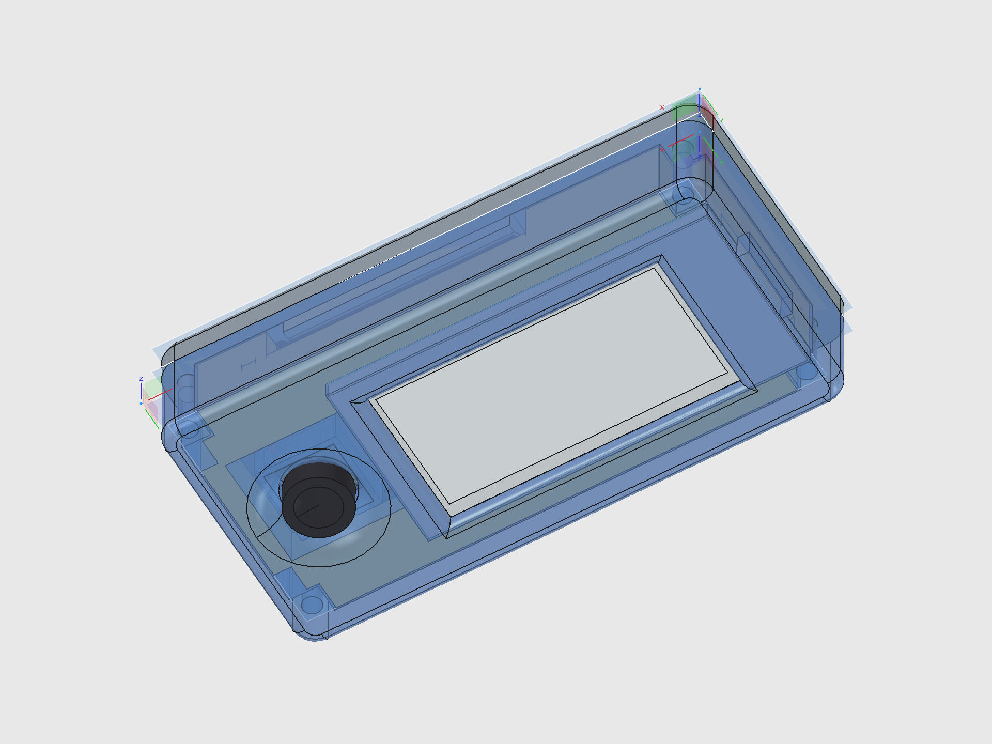
hardware-design/renders/var-06d-angle-rear.png
