rompasaurus/regardedPal/hardware-design/renders/var-16-exploded-iso.png

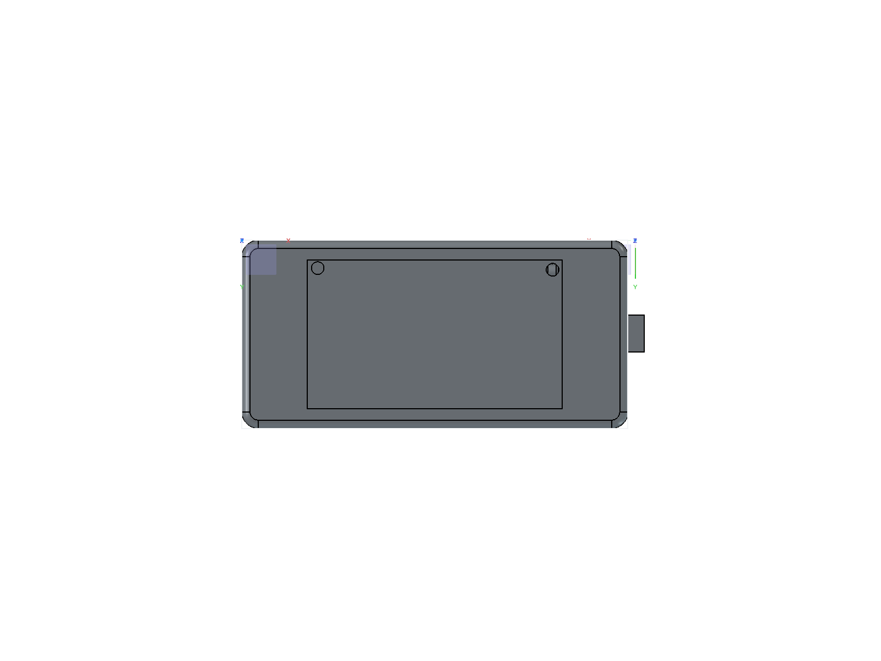
hardware-design/renders/var-16-exploded-iso.png
