rompasaurus/regardedPal/hardware-design/renders/var-17-exploded-front.png

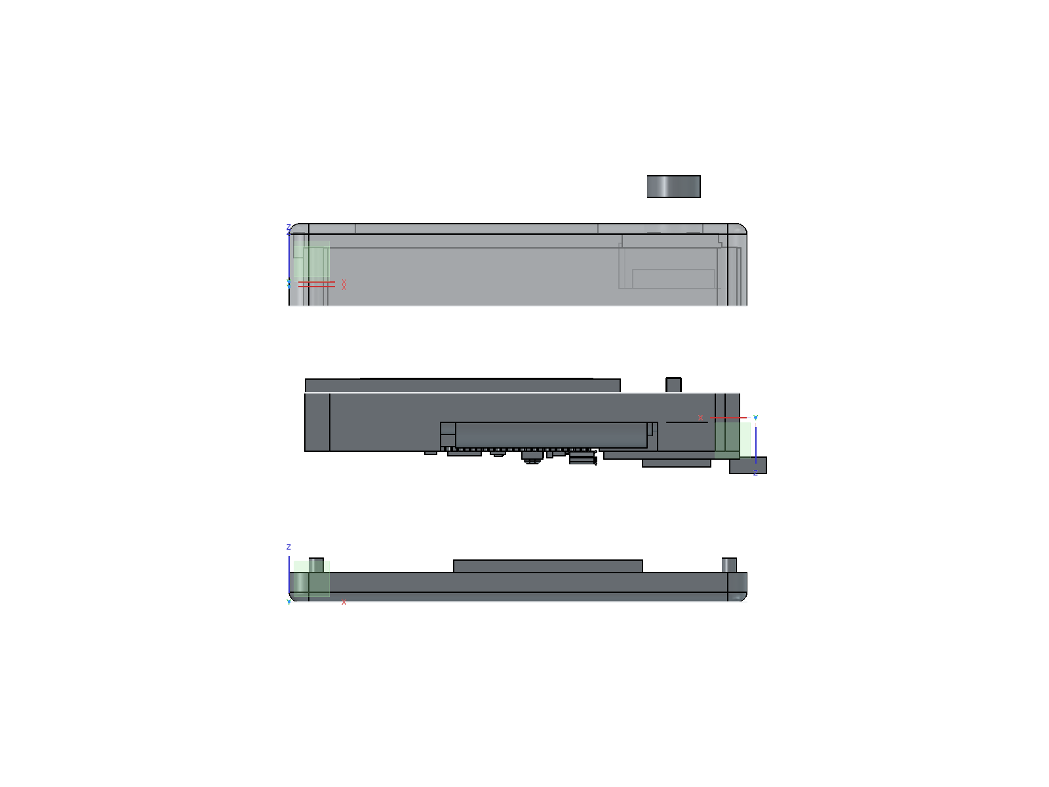
hardware-design/renders/var-17-exploded-front.png
