rompasaurus/regardedPal/hardware-design/renders/var-24-exploded-front.png

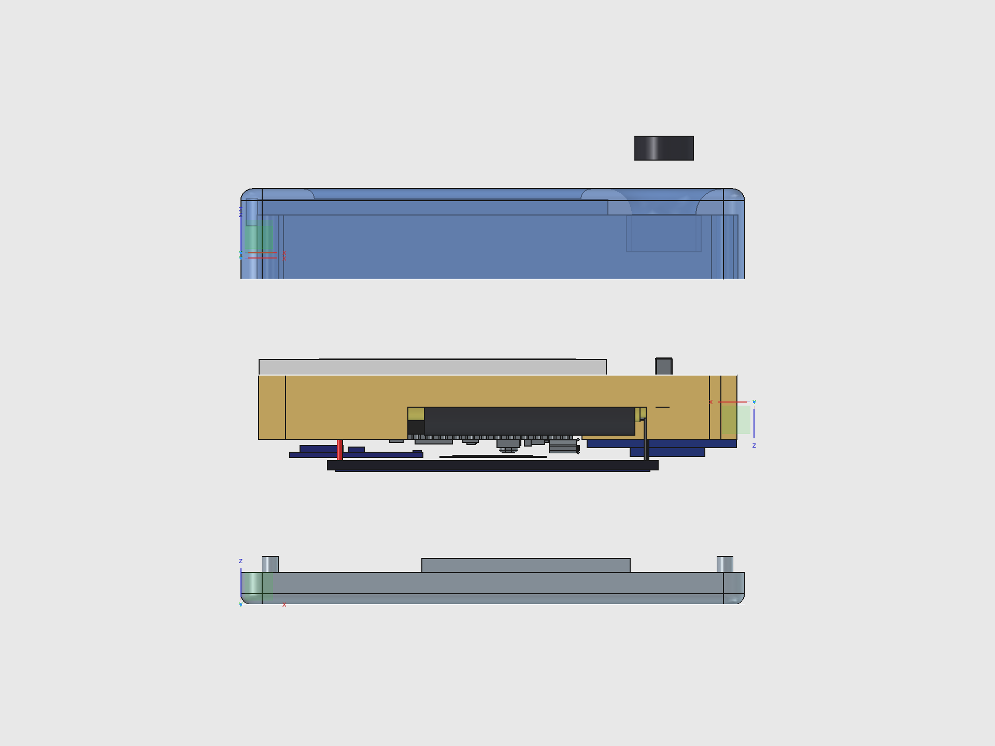
hardware-design/renders/var-24-exploded-front.png
