rompasaurus/regardedPal/website/docs/assets/images/tools/design-tracker/tracker-naming.png

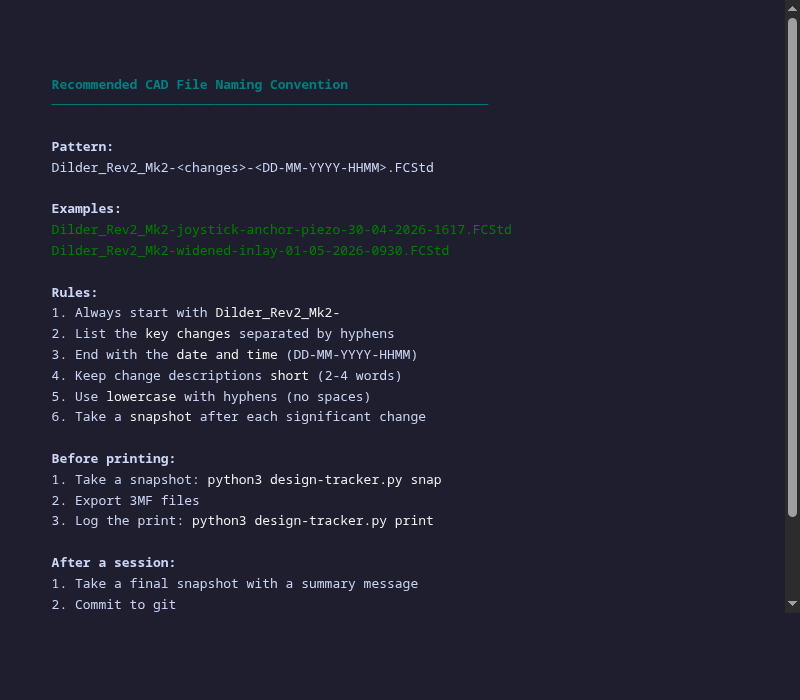
website/docs/assets/images/tools/design-tracker/tracker-naming.png
