rompasaurus/regardedPal/website/docs/assets/images/tools/designtool/designtool-tab-presets.png

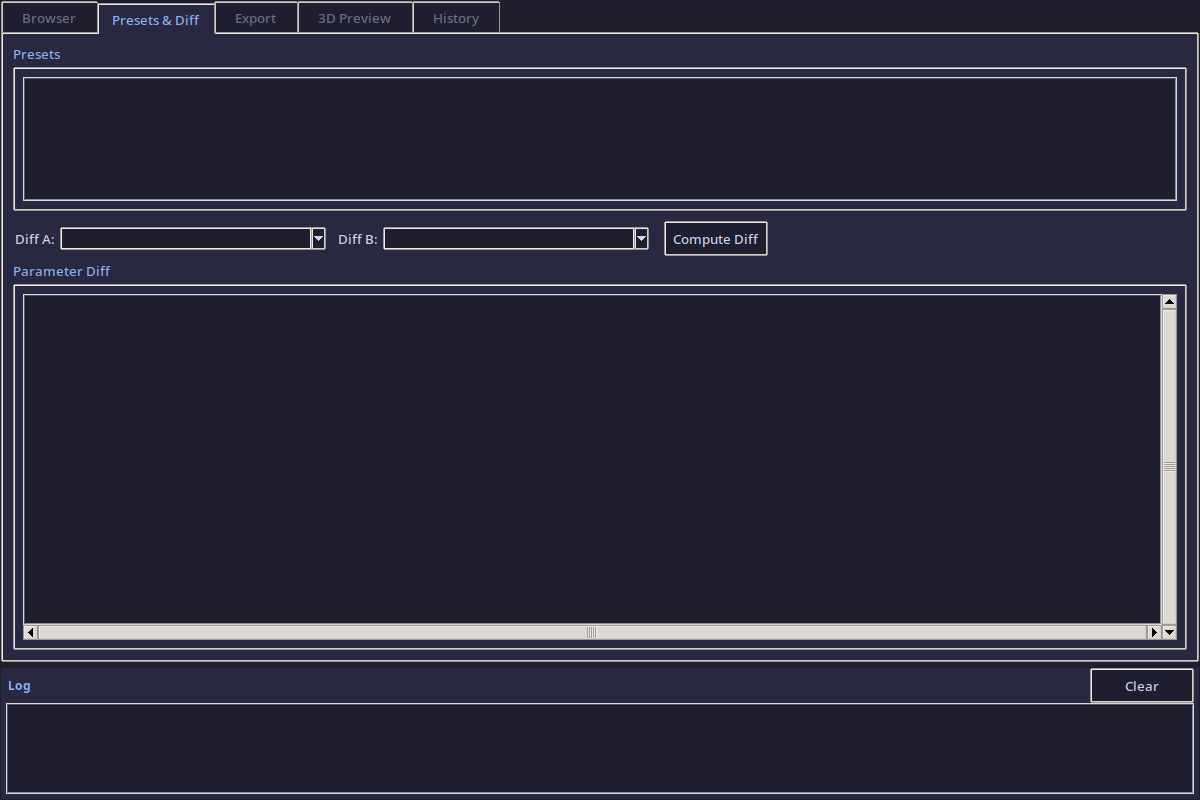
website/docs/assets/images/tools/designtool/designtool-tab-presets.png
