rompasaurus/regardedPal/website/docs/assets/images/tools/render-cli/design-doc-toc.png

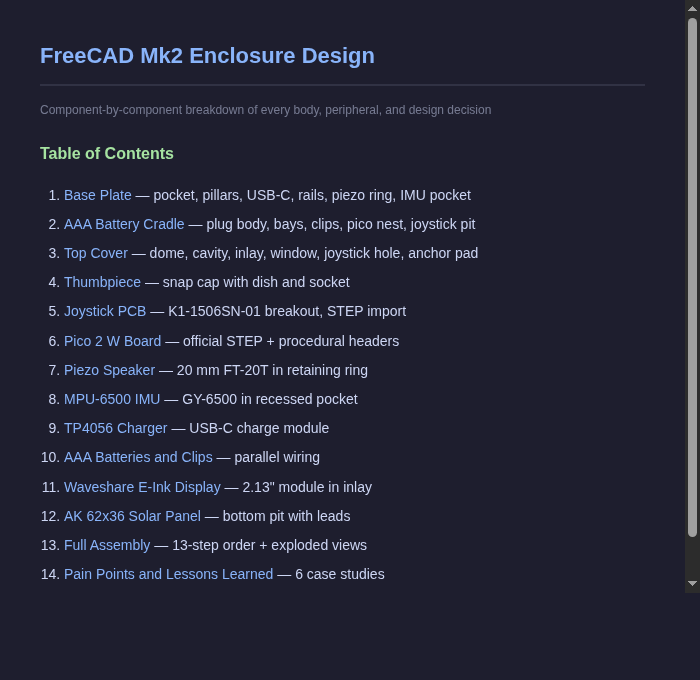
website/docs/assets/images/tools/render-cli/design-doc-toc.png
