rompasaurus/regardedPal/hardware-design/examples/10-klp5e-sensor-board/BOM.ods

DESIGNATOR | QTY | VALUE | MANUF. PART No | MANUFACTURER | PACKAGE | DESCRIPTION
C1, C2, C5, C8, C10, C13-C16, C18, C21, C23 | 12 | 0.1u | C0805C104K4RAC | KEMET | 0805 | Multilayer Ceramic Capacitors MLCC - SMD/SMT 16V 0.1uF X7R 0805 10%
C3, C4, C7, C12 | 4 | 10u | T491A106K010AT7280 | KEMET | 1206 | T491, Tantalum, MnO2 Tantalum, Commercial Grade, 10 uF, 10%, 10 VDC, 125C, -55C, 85C, SMD, MnO2, Molded, 6 % , 3.8 Ohms, 1000 nA, 58.6 mg, 3216, 1.6mm, Height Max = 1.8mm, 9000, 156 Weeks
C6, C11, C22 | 3 | 1u | C0805C105K4RACTU | KEMET | 0805 | Multilayer Ceramic Capacitors MLCC - SMD/SMT 16V 1uF X7R 0805 10%
C9 | 1 | 4.7u | T491A475K010AT7280 | KEMET | 1206 | T491, Tantalum, MnO2 Tantalum, Commercial Grade, 4.7 uF, 10%, 10 VDC, 125C, -55C, 85C, SMD, MnO2, Molded, 6 % , 4 Ohms, 500 nA, 58.6 mg, 3216, 1.6mm, Height Max = 1.8mm, 9000, 156 Weeks
C17, C24, C25 | 3 | 10n | C0603C103K4RACTU | KEMET | 0603 | Multilayer Ceramic Capacitors MLCC - SMD/SMT 16V 0.01uF X7R 0603 10%
C19 | 1 | 10uF | C1206C106K4RAC | KEMET | 1206 | Multilayer Ceramic Capacitors MLCC - SMD/SMT 16V 10uF X7R 1206 10%
C20 | 1 | 100pF | C0603C101K4RACTU | KEMET | 0603 | Multilayer Ceramic Capacitors MLCC - SMD/SMT 16V 100pF X7R 0603 10%
D1, D4, D6 | 3 | RED | LTST-C170KRKT | Lite-On | 0805 | Standard LEDs - SMD Red Clear 631nm
D2, D5 | 2 | GREEN | LTST-C170GKT | Lite-On | 0805 | LED,SMD,0805,Green,6mcd,130deg Lite-On LTST-C170GKT, CHIPLED 0805 Series Green LED, 569 nm 2012 (0805), Rectangle Lens SMD package
D3 | 1 | BLUE | LTST-C170TBKT | Lite-On | 0805 | LED,SMD,0805,Blue,28mcd,130deg
F1 | 1 | 0ZCH0110AF2E | 0ZCH0110AF2E | Belfuse | 1210 | 1210 SMT PPTC | 1.10 Ih | 16V
J1 | 1 | USB_C_Receptacle | SS-52400-002 | STEWART CONNECTOR | USB Type-C | USB 2.0-only Type-C Receptacle connector
J2 | 1 | JST_2mm_LiPo | PHR-2 | JST |  | 2 Pin 2mm JST Battery Connector
J3 | 1 | GSD090012SEU | GSD090012SEU | Amphenol |  | Memory Card Connectors SD CARD CONNECTOR 9 POS, SMT
J4, J5 | 2 | B4B-XH-AM | B4B-XH-AM | JST |  | Connector header vertical 4pos 2.5mm
J6 | 1 | Conn_01x05 |  |  |  | Header 1X5, 2.54mm
L1 | 1 |  | FBMJ2125HM330 | TAIYO YUDEN | 0805 | Ferrite Bead 0805 4A 33OHMS 25%
MK1 | 1 | CMC-5042PF-AC | CMC-5042PF-AC | CUI INC
Q1 | 1 | TEMT6000X01 | TEMT6000X01 | VISHAY | 4 mm x 2 mm x 1.05 mm | Ambient Light Sensors Ambient Light Sensor AEC-Q101 Qualified
Q2, Q3 | 2 | BC817 | BC817 |  | SOT-23 | 0.8A Ic, 45V Vce, NPN Transistor, SOT-23
R1, R2, R19, R23, R32-R34 | 7 | 10K |  |  | 805 | SMD resistor, 0805, 125mW, 1%
R3, R4 | 2 | 5k1 |  |  | 0805 | SMD resistor, 0805, 125mW, 1%
R5, R26, R28 | 3 | 2K |  |  | 0805 | SMD resistor, 0805, 125mW, 1%
R6 | 1 | 20K |  |  | 0805 | SMD resistor, 0805, 125mW, 1%
R7-R9 | 3 | 470 |  |  | 0805 | SMD resistor, 0805, 125mW, 1%
R10, R14, R18 | 3 | 330 |  |  | 0805 | SMD resistor, 0805, 125mW, 1%
R11, R30 | 2 | 1K |  |  | 0805 | SMD resistor, 0805, 125mW, 1%
R12 | 1 | 22K1 |  |  | 0805 | SMD resistor, 0805, 125mW, 1%
R13 | 1 | 47K5 |  |  | 0805 | SMD resistor, 0805, 125mW, 1%
R15-R17, R20-R22 | 6 | 50 |  |  | 0805 | SMD resistor, 0805, 125mW, 1%
R24, R25 | 2 | 4K7 |  |  | 0805 | SMD resistor, 0805, 125mW, 1%
R27, R29 | 2 | 1M |  |  | 0805 | SMD resistor, 0805, 125mW, 1%
R31 | 1 | 22K |  |  | 0805 | SMD resistor, 0805, 125mW, 1%
SW1, SW2 | 2 | TL3305AF260QG | TL3305AF260QG | E-Switch |  | Tactile Switches 50mA 12VDC SPST, NO 3.8mm Act 260gf
U1 | 1 | MCP73871 | MCP73871-4CCI/ML | Microchip | QFN-20 | Single cell, Li-Ion/Li-Po charge management controller
U2 | 1 | LM1117MPX-3.3_NOPB | LM1117MPX-3.3/NOPB | Texas Instruments | SOT-223-4 | Space saving 800-mA low-dropout linear regulator with internal current limit
U3 | 1 | ESP32-C3-WROOM-02-H4 | ESP32-C3-WROOM-02-H4 | Espressif |  | Multiprotocol Modules SMD module, ESP32-C3, 4MB SPI flash, PCB antenna
U4 | 1 | CP2102N-A02-GQFN20 | CP2102N-A02-GQFN20 | Silicon Laboratories | QFN20 | USB to UART Bridge
U5 | 1 | USBLC6-2SC6 | USBLC6-2SC6 | STMicroelectronics | SOT-23-6 | ESD Suppressors / TVS Diodes ESD Protection Low Cap
U6 | 1 | W25Q32JVSSIQ | W25Q32JVSSIQ | Winbond | SOIC-8 | NOR Flash spiFlash, 32M-bit, 4Kb Uniform Sector
U7 | 1 | BME280 | BME280 | Bosch | LGA-8 | Air Quality Sensor MEMS humidity, pressure and temperature sensor
U8 | 1 | MAX4466EXK+T | MAX4466EXK+T | Analog Devices Inc. | SC-70-5 | Microphone Preamplifier
VR1 | 1 | 35WR100KLFTR | 35WR100KLFTR | TT Electronics |  | Trimmer Resistor - SMD 3mm 100K Open Type
