rompasaurus/regardedPal/hardware-design/examples/07-whirlingbits-s3-platform/_Bom/ESP_S3-CP-24_Platform_BOM.xlsx

ESP-S3 Developer Platform R0.80 (12.3.2022)
Pos | Sourced | References | Value | Footprint | DigiKey | LCSC | Mouser | Quantity
1 |  | C2, C3, C5, C8, C15, C18, C21, C25 | 0.1uF, 50V | C_0805_2012Metric |  | C161260 |  | 8
2 |  | C7, C10, C14 | 1uF, 16V | C_0805_2012Metric |  | C16834 |  | 3
3 |  | C16, C17, C19 | 4.7uF, 25V | C_0805_2012Metric |  | C98192 |  | 3
4 |  | C4, C6 | 47uF, 22V | C_0805_2012Metric |  | C913559 |  | 2
5 |  | C22, C23 | 12pF, 50V | C_0805_2012Metric |  | C182488 |  | 2
6 |  | C24, C26 | 22uF, 10V | C_0805_2012Metric |  | C77074 |  | 2
7 |  | C1 | 0.1uF, 50V (DNP) | C_0805_2012Metric |  | C161260 |  | 1
8 |  | C9 | 22p | C_0805_2012Metric |  | C105623 |  | 1
9 |  | C11 | 1500p | C_0805_2012Metric |  | C114765 |  | 1
10 |  | C12 | 47p | C_0805_2012Metric |  | C113821 |  | 1
11 |  | C13 | 100uF, 6,3V | C_0805_2012Metric |  | C141660 |  | 1
12 |  | R49, R50, R51, R52, R53, R54, R55, R56, R57, R58, R59, R60, R61, R62, R63, R64, R65, R66, R67, R68, R69, R70, R71, R72, R73, R74, R75, R76, R77, R78, R79, R80, R81, R82, R83, R84, R85 | 22R | R_0402_1005Metric |  | C114765 |  | 37
13 |  | R2, R3, R6, R7, R8, R19, R37, R39, R40, R41, R42, R43, R91, R92, R99, R102, R103, R107, R108, R109, R110, R111, R112, R113 | 0R | R_0805_2012Metric |  | C100045 |  | 24
14 |  | R34, R35, R48, R106, R114, R115, R116, R117, R118, R119 | 10k | R_0805_2012Metric |  | C169253 |  | 10
15 |  | R14, R26, R27, R28, R29, R88, R101 | 5k1 | R_0805_2012Metric |  | C204548 |  | 7
16 |  | R11, R12, R13, R25, R30, R32 | 0R1 | R_1210_3225Metric |  | C473589 |  | 6
17 |  | R86, R87, R89, R100, R104, R105 | 5k1 (DNP) | R_0805_2012Metric |  | C204548 |  | 6
18 |  | R44, R45, R46, R47 | 22R | R_0805_2012Metric |  | C144531 |  | 4
19 |  | R4, R5, R16 | 1M (DNP) | R_0805_2012Metric |  | C230655 |  | 3
20 |  | R9, R10, R38 | 1k | R_0805_2012Metric |  | C95781, |  | 3
21 |  | R1 | 1k8 | R_0805_2012Metric |  | C137465 |  | 1
22 |  | R15 | 1M | R_0805_2012Metric |  | C230655 |  | 1
23 |  | R17 | 41,2k | R_0805_2012Metric |  | C204486 |  | 1
24 |  | R18 | 0R (DNP) | R_0805_2012Metric |  | C100045 |  | 1
25 |  | R20 | 11,5k | R_0805_2012Metric |  | C228269 |  | 1
26 |  | R21 | 49R9 | R_0805_2012Metric |  | C479104 |  | 1
27 |  | R22 | 845k | R_0805_2012Metric |  | C416871 |  | 1
28 |  | R23 | 270k | R_0805_2012Metric |  | C352236 |  | 1
29 |  | R24 | 1k5 | R_0805_2012Metric |  | C163951 |  | 1
30 |  | R31 | 2k2 | R_0805_2012Metric |  | C441982 |  | 1
31 |  | R33 | 47.5k | R_0805_2012Metric |  | C104355 |  | 1
32 |  | R36 | 10k (DNP) | R_0805_2012Metric |  |  |  | 1
33 |  | R90 | 5.6M | R_0805_2012Metric |  | C185285 |  | 1
34 |  | R93 | 22.1k | R_0805_2012Metric |  | C104113 |  | 1
35 |  | L1 | 10uH - SLF7032T-100M1R4-2PF | L_TDK_SLF7032 |  | C76852 |  | 1
36 |  | D5, D6, D7, D8, D9, D10, D14, D15, D16, D17, D18, D19 | PESD15VW1BCSFYL | D_SOD-523 |  |  | 771-PESD15VW1BCSFYL | 12
37 |  | D1, D3, D4, D13 | LTST-C191KRKT (Red) | LED_0603_1608Metric |  | C125099 |  | 4
38 |  | D2, D11, D12 | BAT760-7 | D_SOD-323 |  | C116158 |  | 3
39 |  | U1 | LTC3111EMSEPBF | MSOP-16 |  | C684080 | 584-LTC3111EMSETRPBF | 1
40 |  | U2 | CP2102N-A02-GQFN24 | QFN-24-1EP_4x4mm_P0.5mm_EP2.6x2.6mm |  | C80225 |  | 1
41 |  | U3 | ESP32-S3-WROOM-1 | ESP32-S3-WROOM-1 |  | C2913201 |  | 1
42 |  | Y1 | XTAL 32,678kHz (C20S-12.5PF20PPM) | SC20S125PF20PPM |  | C97603 |  | 1
43 |  | SW1, SW2 | SKRTLAE010 | SW_Push_1P1T-MP_NO_Horizontal_Alps_SKRTLAE010 |  | C110293 |  | 2
44 |  | Q1, Q2 | SS8050-G | SOT-23 |  | C164885 |  | 2
45 |  | J2, J3 | Conn_01x22 (DNP) | PinHeader_1x22_P2.54mm_Vertical |  | C725954 |  | 2
46 |  | J5, J6 | Conn_02x02_Top_Bottom (DNP) | PinHeader_2x02_P2.54mm_Vertical |  | C492419 |  | 2
47 |  | J7, J8 | USB_C_Receptacle (USB4110-GF-A) | GCT_USB4110-GF-A_REVB |  |  | 640-USB4110-GF-A | 2
48 |  | J1 | Conn_02x05_Odd_Even | PinHeader_2x05_P1.27mm_Vertical_SMD |  | C150517 |  | 1
49 |  | J4 | PJ-002AH-SMT-TR (Barrel Jack) | BarrelJack_CLIFF_FC681465S_SMT_Horizontal |  |  | 490-PJ-002AH-SMT-TR | 1
50 |  | J9 | DM3AT-SF-PEJM5 | HRS_DM3AT-SF-PEJM5 |  | C114218 |  | 1
