rompasaurus/regardedPal/hardware-design/PCB Designs/joystick-pcb-by-hand/JoystickBoardDilder/production/bom.csv

Comment | Designator | Footprint | LCSC
K1-1506SN-01 | SW1 | KEY-SMD_K1-1506SN-01 | C145910
