rompasaurus/regardedPal/hardware-design/examples/02-lilka-console/hardware/v2/bom_clean.ods

К-сть | Ідентифікатор | Значення | Ціна | +Батарея | +Звук | Посилання
1 | U4 | ESP32-S3-WROOM-1 | 249 |  |  | https://www.rcscomponents.kiev.ua/product/esp32-s3-wroom-1-n16r8_184448.html
1 | U2 | 280x240 1.69" TFT | 176 |  |  | https://arduino.ua/prod6568-tft-displei-1-7-spi-240x280-rgb
1 | J5 | uSD | 24 |  |  | https://diyshop.com.ua/en/modul-interfejsa-mini-sd-karty-kardrider
1 | U3 | TLV1117LV33DCYR | 7 |  |  | https://www.kosmodrom.ua/stabilizator-naprugi/tlv1117lv33dcyr-2.html
2 | C2, C3 | 10uF | 10 |  |  | https://prom.ua/ua/p436700921-kondensator-50v-keramika.html
1 | C1 | 1uF | 3 |  |  | https://m-teh.com.ua/kondensator-ct4-1uf-50v-x7r-10/
1 | R1 | 10K | 2 |  |  | https://justas-electronics.com.ua/rss0125w-10k/
8 | SW1-SW8 | Button Kit (12mm) | 27 |  |  | https://arduino.ua/prod2506-komplekt-knopok-12mm-s-kolpachkom-5-cvetov
3 | SW9, SW10, SW12 | Select/Start/Reset Tact Button | 10 |  |  | https://arduino.ua/prod6165-taktova-knopka-smd-4pin-6h6x9-5mm-shtok-6-0mm
1 | J1 | USB Type-C to DIP | 12 |  |  | https://arduino.ua/prod2783-plata-perehodnik-usb-type-c-na-dip-2-54
1 | R2 | 100K | 2 |  |  | https://justas-electronics.com.ua/rss0125w-100k/
1 | BZ1 | Buzzer | 5 |  |  | https://www.mini-tech.com.ua/ua/passivnyj-zummer
1 | SW11 | Power | 10 |  |  | https://arduino.ua/prod5124-perekluchatel-polzynkovii-ms-22d18g2-dip
1 | J3, | Ext, | 9 |  |  | https://arduino.ua/prod1077-konnektor-dvyhryadnii-2h40-pin-papa
1 | U2J1 | TFT_Socket | 7 |  |  | https://arduino.ua/prod315-konnektor-40-pin-mama
1 | J2 | Bat |  | 116 |  | https://m-teh.com.ua/li-pol-akumuliator-603048p-1000-ma-hod-3.7v-z-plato%D1%96u-zakhystu/?gad_source=1
1 | J8 | TP4056 |  | 16 |  | https://arduino.ua/prod1486-zaryadnii-modyl-tp4056-micro-usb-s-fynkciei-zashhiti-akkymylyatora
1 | Q1 | IRLML6401 |  | 4 |  | https://www.rcscomponents.kiev.ua/product/irlml6401trpbf_34344.html
1 | D1 | 1N4001 |  | 1 |  | https://voron.ua/uk/catalog/029199--diod_1n4001_v_lente_mic_master_instrument_corporation_do41_do41
1 | R3 | 100K |  | 2 |  | https://justas-electronics.com.ua/rss025w-200r/
1 | R4 | 33K |  | 2 |  | https://justas-electronics.com.ua/rss0125w-33kOm/
1 | J7 | MAX98357 |  |  | 92 | https://arduino.ua/prod4112-modyl-aydioysilitelya-mono-3vt-klassa-d-na-max98357
1 | J6 | Audio Jack 3.5 (mono) |  |  | 8 | https://imrad.com.ua/ua/pj3013d-144736
Разом |  |  | 553 | 141 | 100
