rompasaurus/regardedPal/hardware-design/freecad-mk2/Dilder_Rev2_Mk2Full parts so far with joystick model with battery assembly even closer-AAACradle.3mf

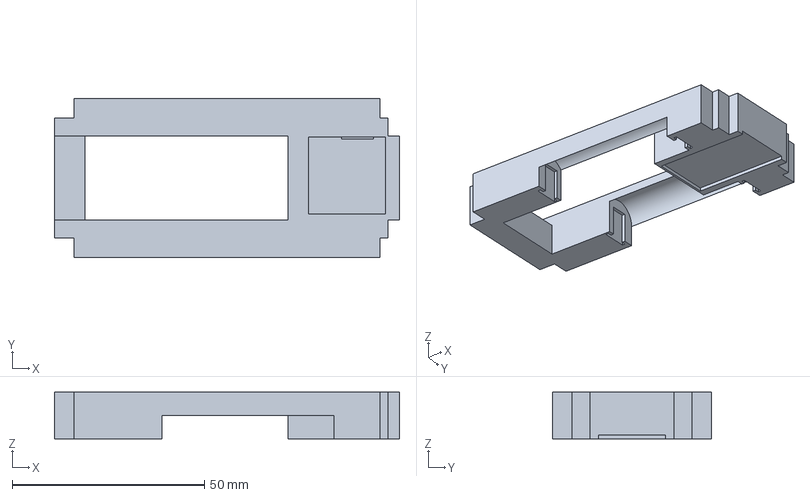
[picture p262: CAD file, 2026-04-30]
hardware-design/freecad-mk2/Dilder_Rev2_Mk2Full parts so far with joystick model with battery assembly even closer-AAACradle.3mf
89.7 x 41.4 x 12.1 mm
