rompasaurus/regardedPal/hardware-design/freecad-mk2/Dilder_Rev2_Mk2Full parts so far with joystick needs work.FCStd

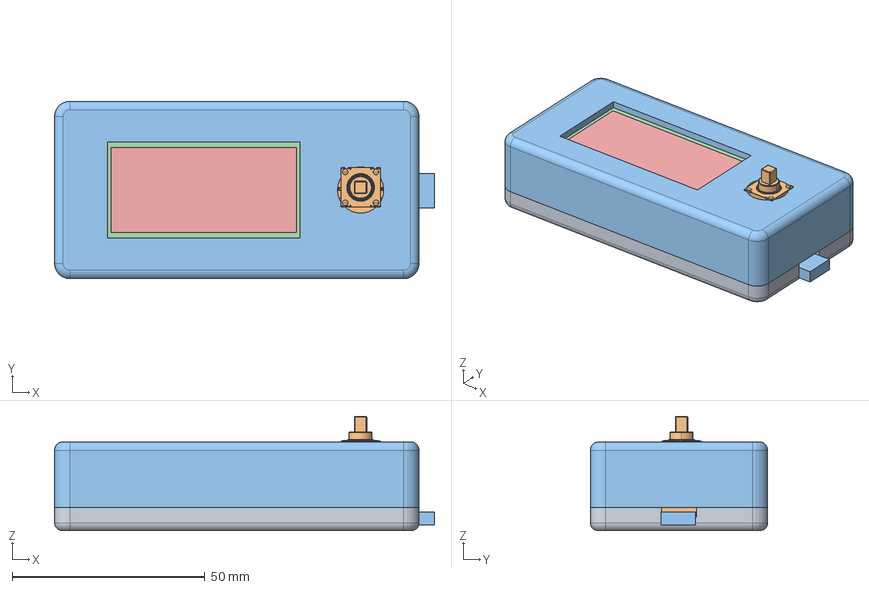
[picture p263: CAD file, 2026-04-29]
hardware-design/freecad-mk2/Dilder_Rev2_Mk2Full parts so far with joystick needs work.FCStd
98.5 x 46.0 x 29.6 mm
BasePlate
AAACradle
TopCover
Pico2W_Board
Pico2W_Headers
AAA_Battery_1
AAA_Battery_1_PosTerm
AAA_Battery_2
AAA_Battery_2_PosTerm
TP4056_Module
TP4056_USBC
EInkDisplay_Module
EInkDisplay_Panel
BatteryClips_Positive
BatteryClips_Negative
BatteryWiring_Positive
BatteryWiring_Negative
JoystickPCB
