rompasaurus/regardedPal/hardware-design/freecad-mk2/Dilder_Rev2_Mk2ProperwithPicoandHeaderAssemblies.FCStd

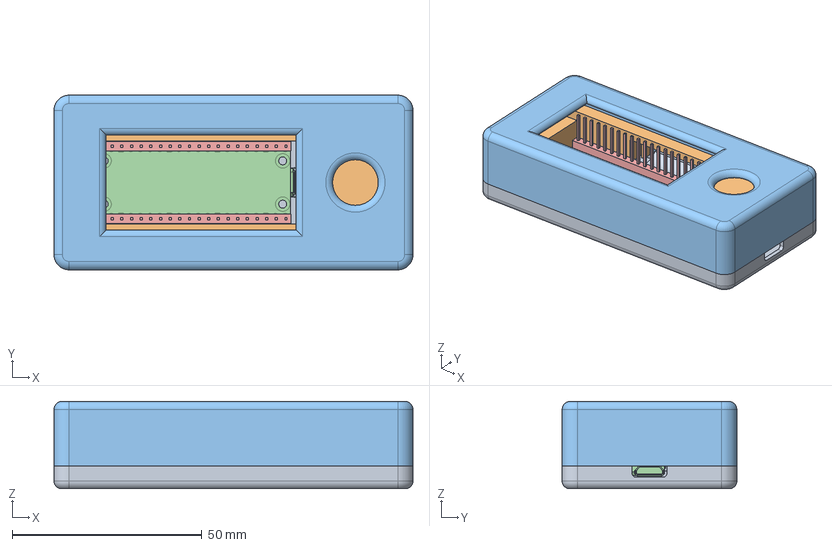
[picture p265: CAD file, 2026-04-29]
hardware-design/freecad-mk2/Dilder_Rev2_Mk2ProperwithPicoandHeaderAssemblies.FCStd
94.5 x 46.0 x 23.0 mm
BasePlate
AAACradle
TopCover
Pico2W_Board
Pico2W_Headers
