rompasaurus/regardedPal/hardware-design/freecad-mk2/Dilder_Rev2_Mk2ProperwithPicoandHeaderAssemblies-TopCover.3mf

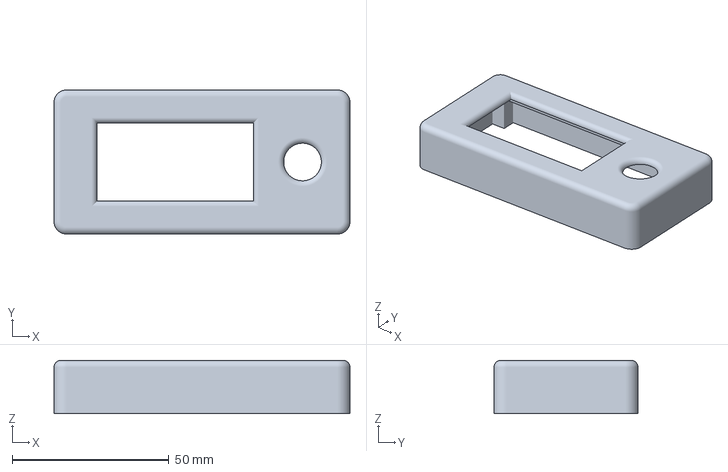
[picture p266: CAD file, 2026-04-29]
hardware-design/freecad-mk2/Dilder_Rev2_Mk2ProperwithPicoandHeaderAssemblies-TopCover.3mf
94.5 x 46.0 x 17.0 mm
