rompasaurus/regardedPal/hardware-design/examples/01-pocketmage-pda/Docs/Documents & Advanced/PCB/V3.3/einkPDA_keyboard/JLC_Parts/YTS-C017-2B.step

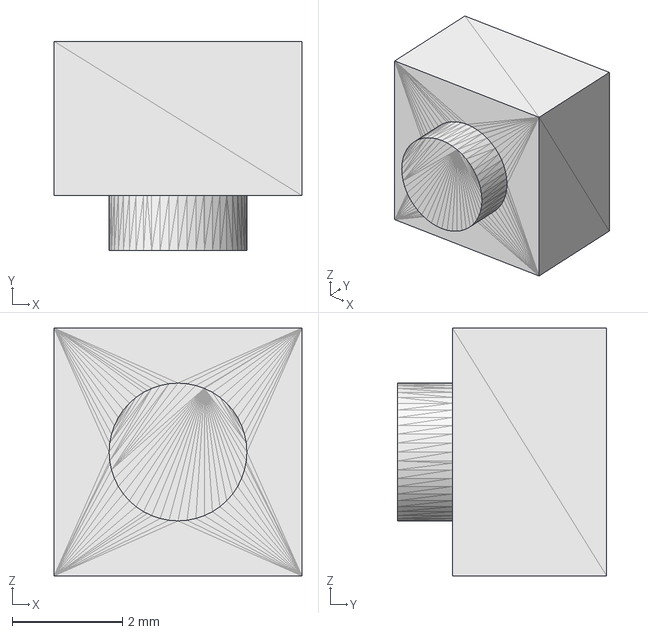
[picture p267: CAD file, 2026-04-15]
hardware-design/examples/01-pocketmage-pda/Docs/Documents & Advanced/PCB/V3.3/einkPDA_keyboard/JLC_Parts/YTS-C017-2B.step
4.50 x 3.80 x 4.50 mm
