rompasaurus/regardedPal/hardware-design/examples/02-lilka-console/hardware/v2/3dmodels/Display 1.69 ST7789V2.stp

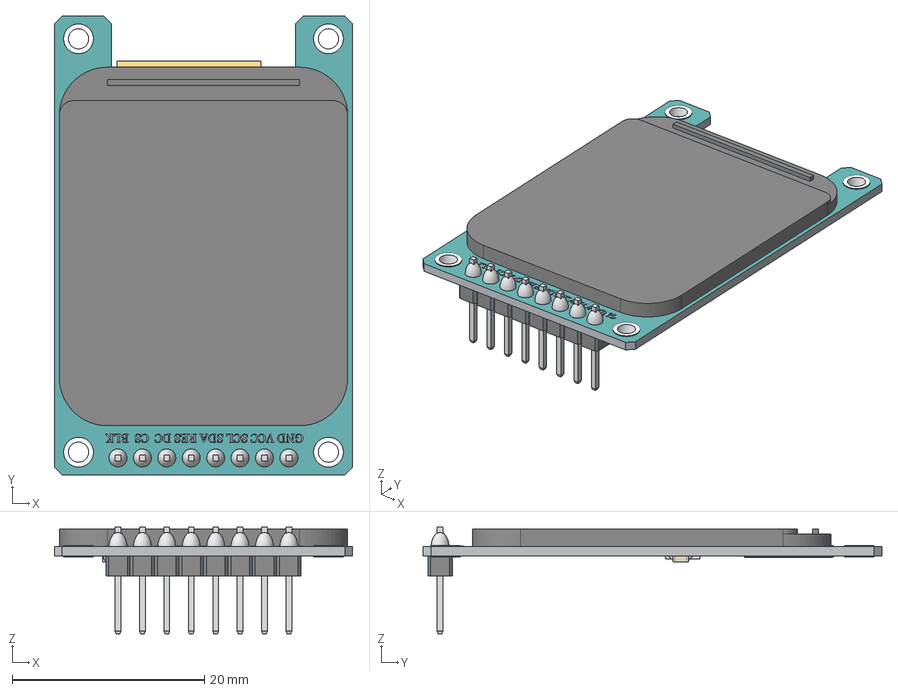
[picture p268: CAD file, 2026-04-15]
hardware-design/examples/02-lilka-console/hardware/v2/3dmodels/Display 1.69 ST7789V2.stp
31.0 x 47.7 x 11.1 mm
PCB
Display
Pin x 8
R-0603 x 3
C-0603 x 2
U-0603
