rompasaurus/regardedPal/hardware-design/examples/05-olimex-devkit-lipo/HARDWARE/ESP32-DevKit-LiPo-Rev.D/3d/BAT54.step

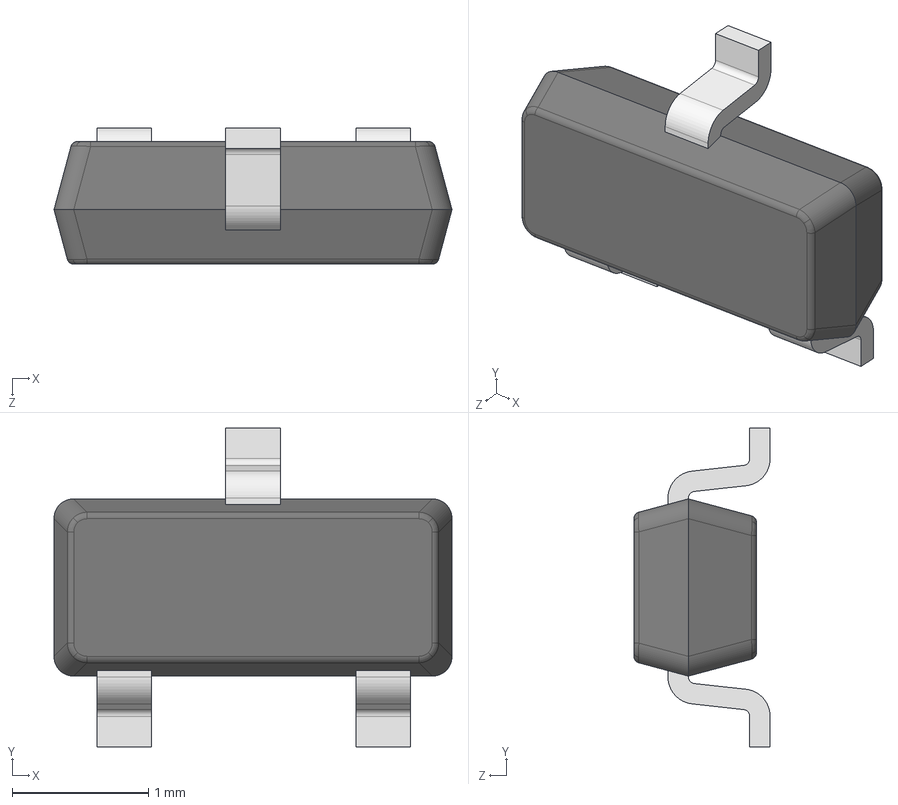
[picture p270: CAD file, 2026-04-15]
hardware-design/examples/05-olimex-devkit-lipo/HARDWARE/ESP32-DevKit-LiPo-Rev.D/3d/BAT54.step
2.92 x 2.34 x 1.00 mm
