rompasaurus/regardedPal/hardware-design/examples/06-unexpected-maker-s3/3d models/FeatherS3Neo/FeatherS3Neo.step

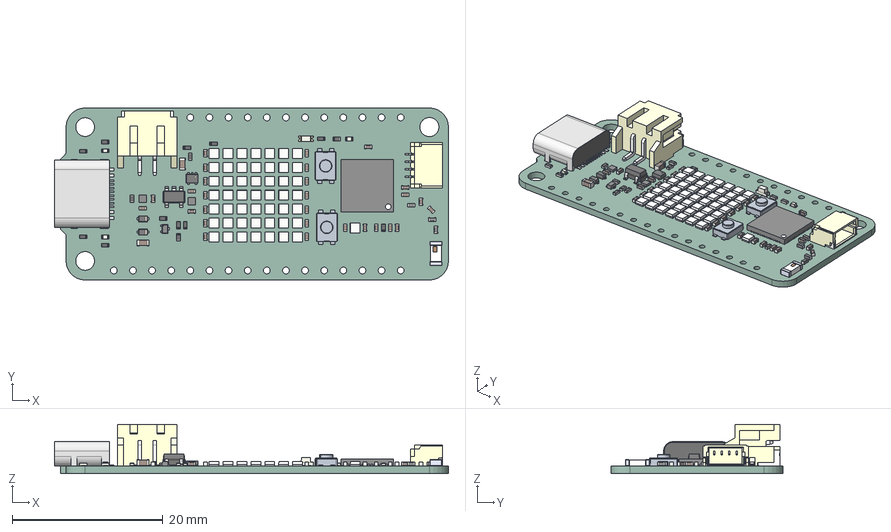
[picture p271: CAD file, 2026-04-15]
hardware-design/examples/06-unexpected-maker-s3/3d models/FeatherS3Neo/FeatherS3Neo.step
52.3 x 22.9 x 6.55 mm
2450AT18B100E
D_SOD_523 x 2
LED_0402_1005Metric x 3
R_0402_1005Metric x 15
C_0402_1005Metric x 28
SOT_23_5
ESD7C5.0DT5G
APA102 2020 LED v2 x 50
BTN_KMR2_4.6X2.8_HAND v1 x 2
HRO USB-C col 3 v9
LED_0805_2012Metric_Castellated
ESP32-S2
L_0402_1005Metric x 3
C_0603_1608Metric x 2
SM04B-SRSS-TB(LF)(SN)
NCP160AMX280TBG x 2
S2B-PH-SM4-TB(LF)(SN)
SOT_553
FeatherS3 Neo_PCB
