rompasaurus/regardedPal/hardware-design/examples/06-unexpected-maker-s3/3d models/NanoS3/NanoS3 Castellated.step

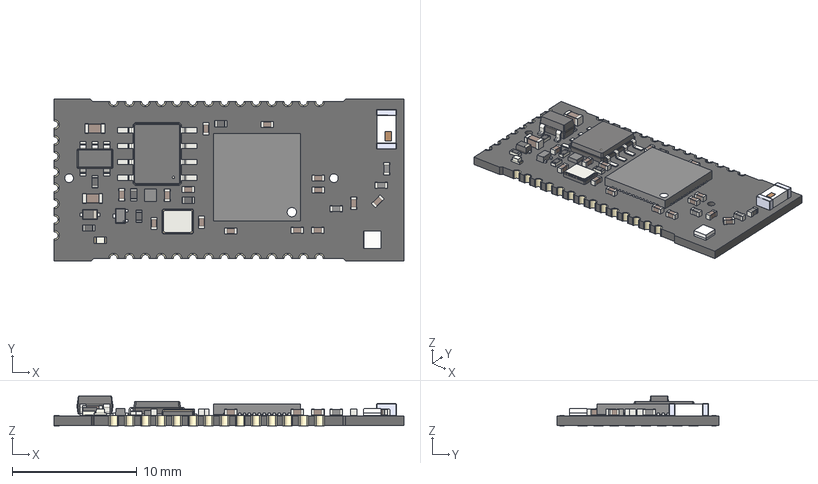
[picture p272: CAD file, 2026-04-15]
hardware-design/examples/06-unexpected-maker-s3/3d models/NanoS3/NanoS3 Castellated.step
28.1 x 13.0 x 2.40 mm
NanoS3_2450AT18B PCB
