rompasaurus/regardedPal/hardware-design/examples/06-unexpected-maker-s3/3d models/NanoS3_Carrier/NanoS3_Carrier_Empty.STEP

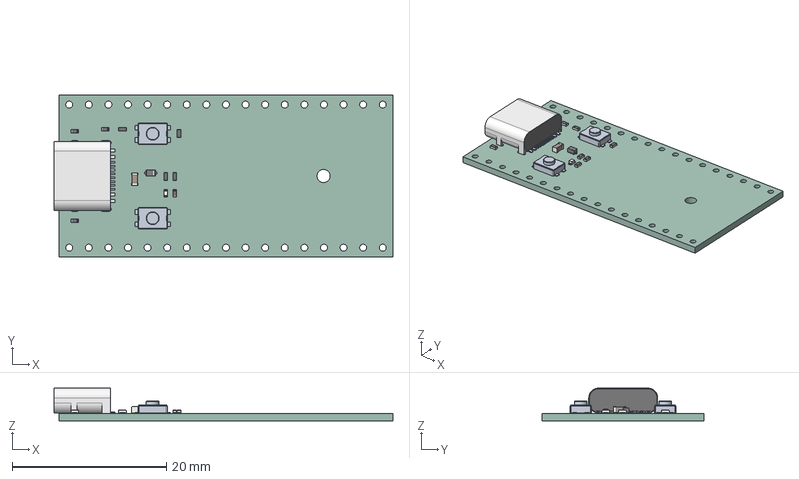
[picture p273: CAD file, 2026-04-15]
hardware-design/examples/06-unexpected-maker-s3/3d models/NanoS3_Carrier/NanoS3_Carrier_Empty.STEP
43.9 x 21.0 x 4.24 mm
_autosave-NanoS3_Carrier PCB
