rompasaurus/regardedPal/hardware-design/examples/06-unexpected-maker-s3/3d models/OMGS3/OMGS3.step

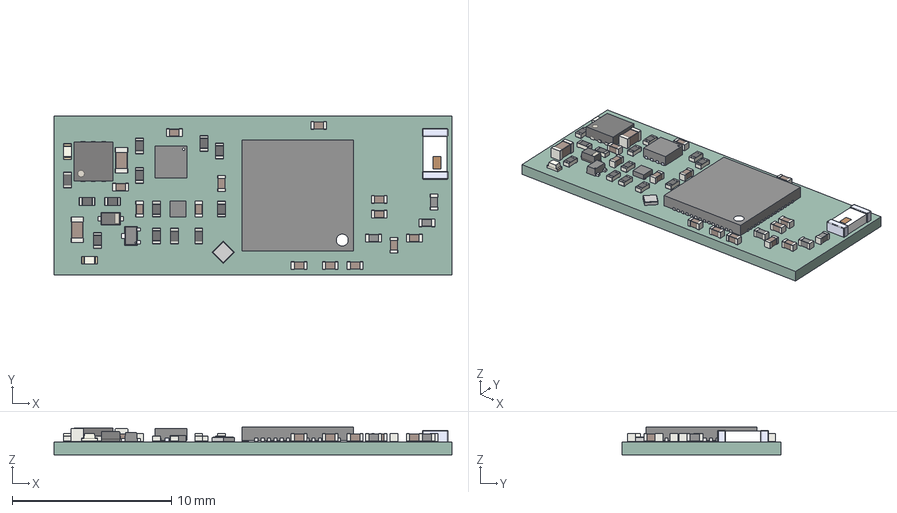
[picture p274: CAD file, 2026-04-15]
hardware-design/examples/06-unexpected-maker-s3/3d models/OMGS3/OMGS3.step
25.0 x 10.0 x 1.75 mm
C_0402_1005Metric x 13
L_0402_1005Metric x 3
R_0402_1005Metric x 13
(Unsaved)
TDFN_6_1EP_25x25mm_P065mm_EP13x2mm
2450AT18B100E
LED_0402_1005Metric x 2
MAX17048G+T10
ESD7C5.0DT5G
NCP160AMX280TBG
D_SOD_523
C_0603_1608Metric x 2
ESP32-S2
_autosave-OMGS3_P1_1.27_PCB
