rompasaurus/regardedPal/hardware-design/examples/06-unexpected-maker-s3/series_d/3d models/EdgeS3D.step

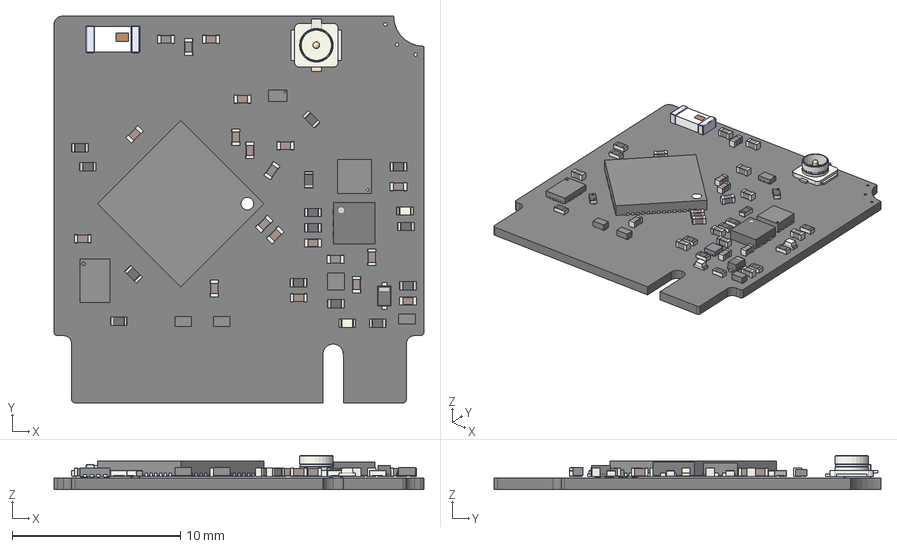
[picture p275: CAD file, 2026-04-15]
hardware-design/examples/06-unexpected-maker-s3/series_d/3d models/EdgeS3D.step
22.0 x 23.0 x 2.05 mm
C_0402_1005Metric x 17
U.FL_Hirose_U.FL-R-SMT-1_Vertical
BGS12WN6E6327XTSA1
L_0402_1005Metric x 3
R_0402_1005Metric x 14
TVS_DFN1006 x 3
LED_0402_1005Metric x 2
NCP170AMX170TCG
FXL6408UMX
D_SOD-523
2450AT18B100E--3DModel-STEP-269445
TDFN-6-1EP_2.5x2.5mm_P0.65mm_EP1.3x2mm
MAX17048G-T10
ESP32_S2--3DModel-STEP-1
EdgeS3_Dual_R1_PCB
