rompasaurus/regardedPal/hardware-design/examples/07-whirlingbits-s3-platform/_libraries/CP2102N-A01-GQFN28/CP2102N-A01-GQFN28.step

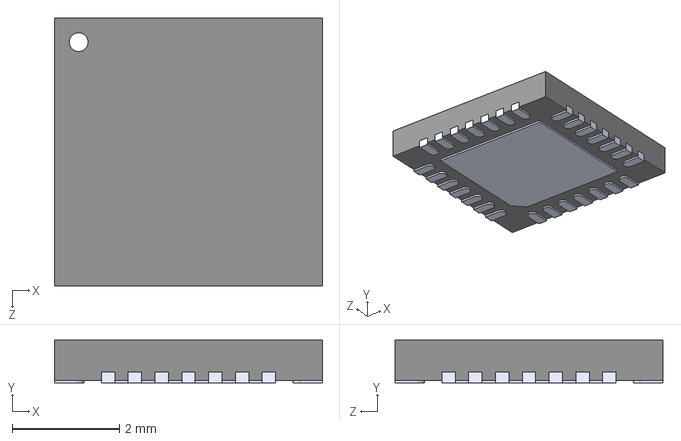
[picture p276: CAD file, 2026-04-15]
hardware-design/examples/07-whirlingbits-s3-platform/_libraries/CP2102N-A01-GQFN28/CP2102N-A01-GQFN28.step
5.00 x 0.8 x 5.00 mm
