rompasaurus/regardedPal/hardware-design/examples/07-whirlingbits-s3-platform/_libraries/CP2102N-A02-GQFN20R/CP2102N-A02-GQFN20R.step

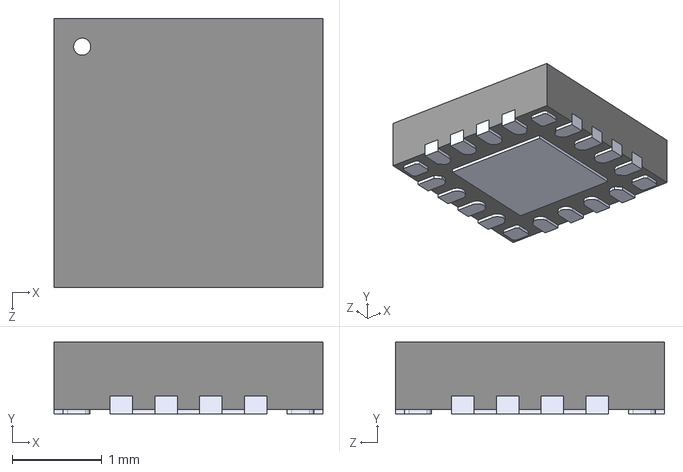
[picture p277: CAD file, 2026-04-15]
hardware-design/examples/07-whirlingbits-s3-platform/_libraries/CP2102N-A02-GQFN20R/CP2102N-A02-GQFN20R.step
3.00 x 0.8 x 3.00 mm
