rompasaurus/regardedPal/hardware-design/examples/07-whirlingbits-s3-platform/_libraries/DM3AT-SF-PEJM5/DM3AT-SF-PEJM5.step

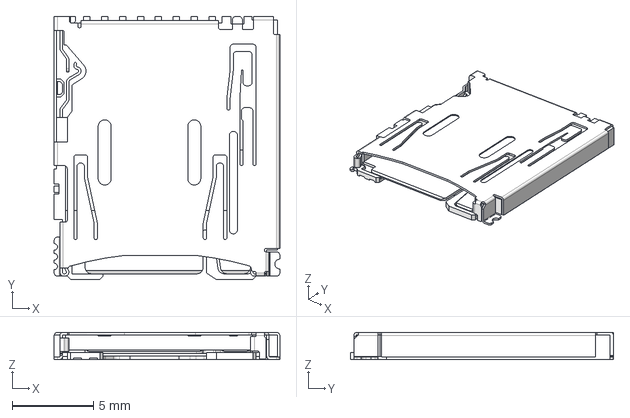
[picture p278: CAD file, 2026-04-15]
hardware-design/examples/07-whirlingbits-s3-platform/_libraries/DM3AT-SF-PEJM5/DM3AT-SF-PEJM5.step
13.8 x 16.2 x 1.68 mm
