rompasaurus/regardedPal/hardware-design/examples/07-whirlingbits-s3-platform/_libraries/ESP32-S3-WROOM/ESP32-S3-WROOM-1-N8R2.step

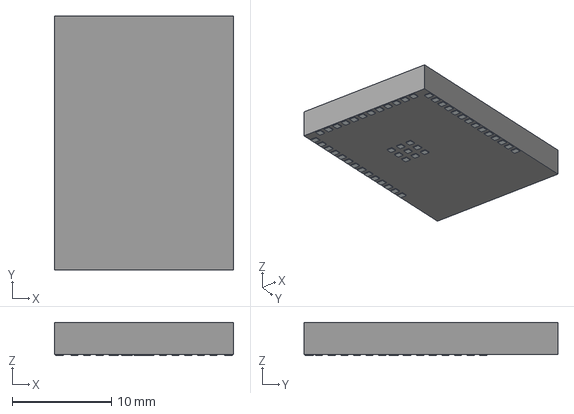
[picture p279: CAD file, 2026-04-15]
hardware-design/examples/07-whirlingbits-s3-platform/_libraries/ESP32-S3-WROOM/ESP32-S3-WROOM-1-N8R2.step
18.0 x 25.5 x 3.35 mm
Pins
