rompasaurus/regardedPal/hardware-design/examples/07-whirlingbits-s3-platform/_libraries/LM3671MF-3.3/LM3671MF-3.3.step

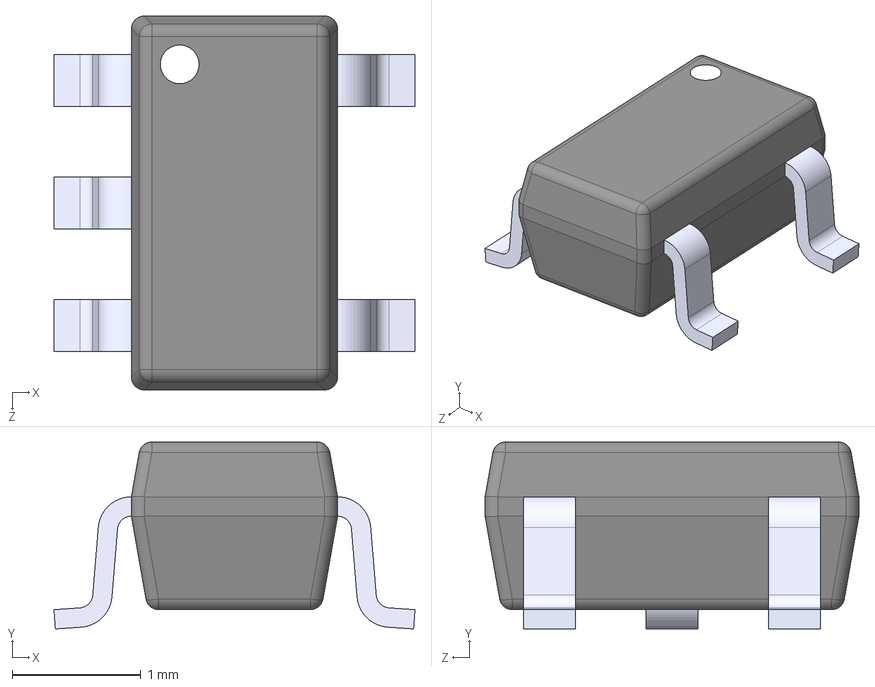
[picture p280: CAD file, 2026-04-15]
hardware-design/examples/07-whirlingbits-s3-platform/_libraries/LM3671MF-3.3/LM3671MF-3.3.step
2.80 x 1.45 x 2.90 mm
