rompasaurus/regardedPal/hardware-design/examples/07-whirlingbits-s3-platform/_libraries/LTC3111EMSEPBF/LTC3111EMSEPBF.step

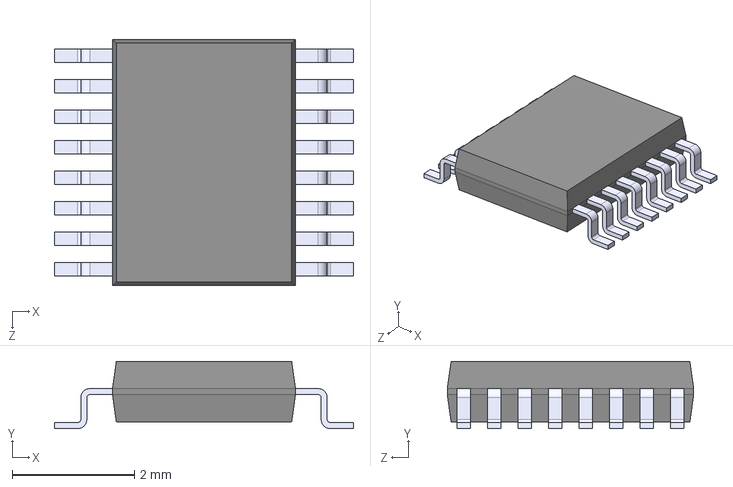
[picture p281: CAD file, 2026-04-15]
hardware-design/examples/07-whirlingbits-s3-platform/_libraries/LTC3111EMSEPBF/LTC3111EMSEPBF.step
4.90 x 1.10 x 4.04 mm
