rompasaurus/regardedPal/hardware-design/examples/07-whirlingbits-s3-platform/_libraries/LTST-C191KGKT/LTST-C191KGKT--3DModel-STEP-56544.STEP

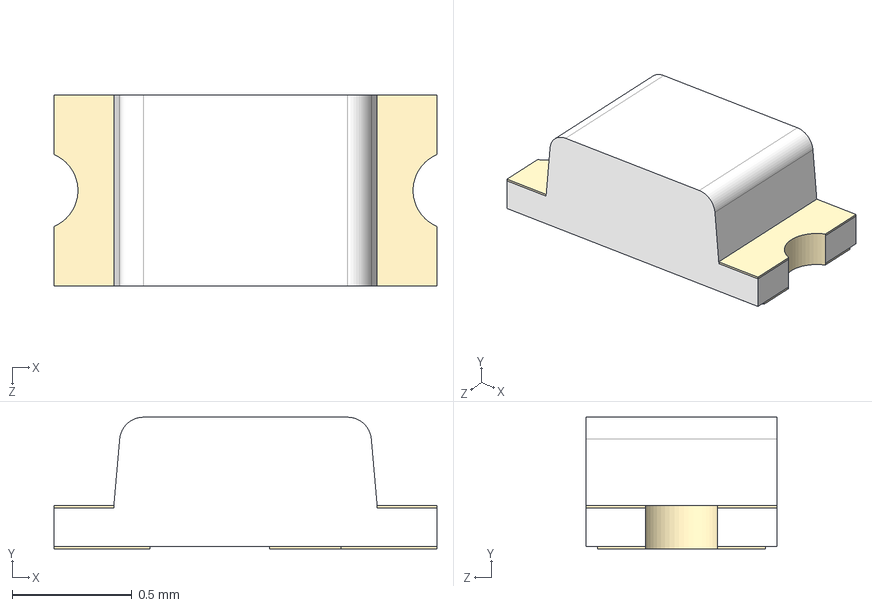
[picture p282: CAD file, 2026-04-15]
hardware-design/examples/07-whirlingbits-s3-platform/_libraries/LTST-C191KGKT/LTST-C191KGKT--3DModel-STEP-56544.STEP
1.60 x 0.55 x 0.8 mm
