rompasaurus/regardedPal/hardware-design/examples/07-whirlingbits-s3-platform/_libraries/MIC2026A-1YM-TR/MIC2026A-1YM-TR.step

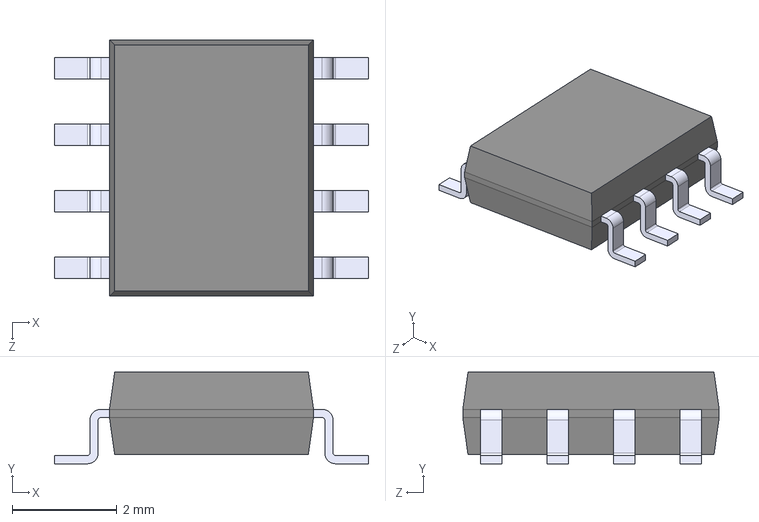
[picture p283: CAD file, 2026-04-15]
hardware-design/examples/07-whirlingbits-s3-platform/_libraries/MIC2026A-1YM-TR/MIC2026A-1YM-TR.step
6.00 x 1.75 x 4.90 mm
