rompasaurus/regardedPal/hardware-design/examples/07-whirlingbits-s3-platform/_libraries/PJ-036AH-SMT-TR/CUI_DEVICES_PJ-036AH-SMT-TR.step

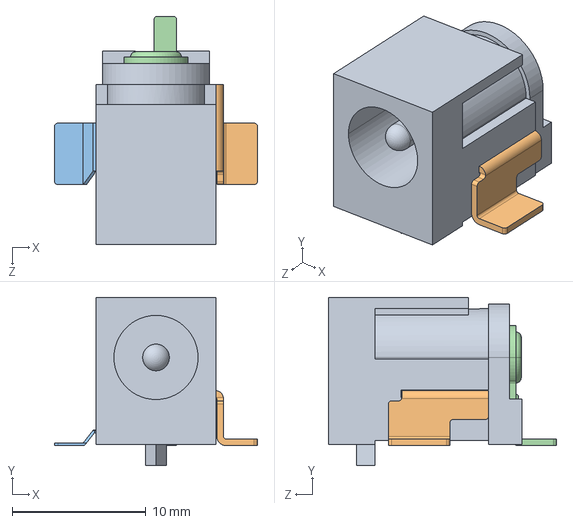
[picture p284: CAD file, 2026-04-15]
hardware-design/examples/07-whirlingbits-s3-platform/_libraries/PJ-036AH-SMT-TR/CUI_DEVICES_PJ-036AH-SMT-TR.step
15.2 x 12.6 x 17.1 mm
