rompasaurus/regardedPal/hardware-design/examples/07-whirlingbits-s3-platform/_libraries/SKRTLAE010/SKRTLA.STEP

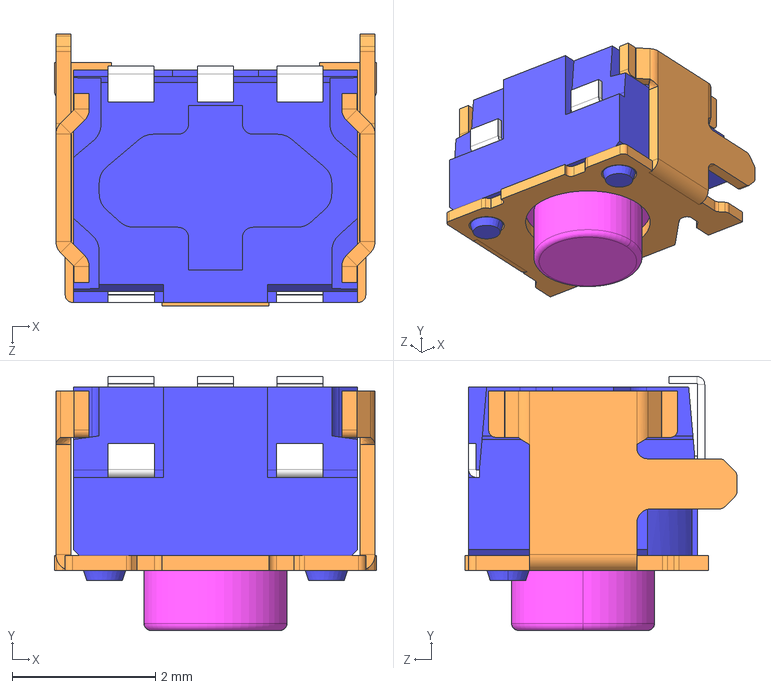
[picture p285: CAD file, 2026-04-15]
hardware-design/examples/07-whirlingbits-s3-platform/_libraries/SKRTLAE010/SKRTLA.STEP
4.50 x 3.55 x 3.80 mm
