rompasaurus/regardedPal/hardware-design/examples/07-whirlingbits-s3-platform/_libraries/USB4110-GF-A_REVB/USB4110-GF-A_REVB.step

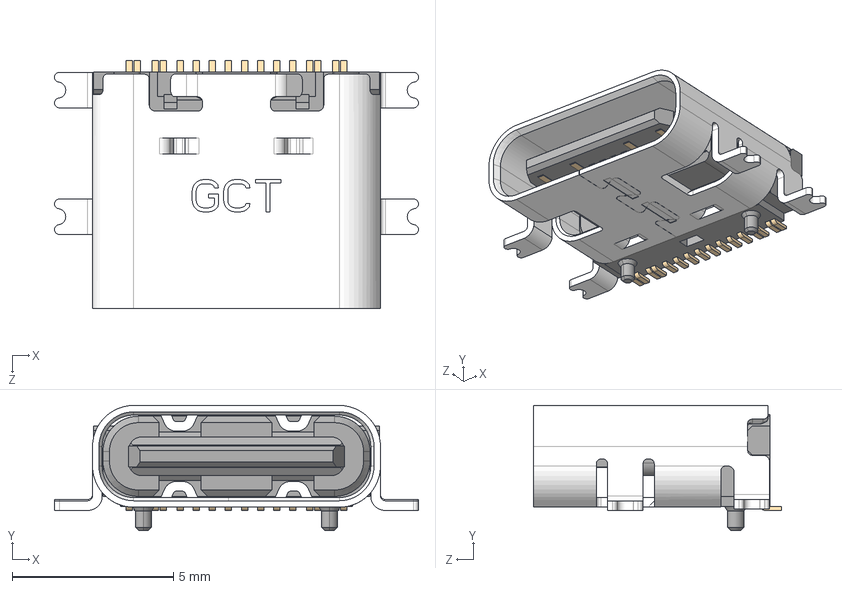
[picture p286: CAD file, 2026-04-15]
hardware-design/examples/07-whirlingbits-s3-platform/_libraries/USB4110-GF-A_REVB/USB4110-GF-A_REVB.step
11.3 x 3.89 x 7.70 mm
