rompasaurus/regardedPal/hardware-design/examples/08-esp-rust-board/kicad_libs/3d/SHTC3.step

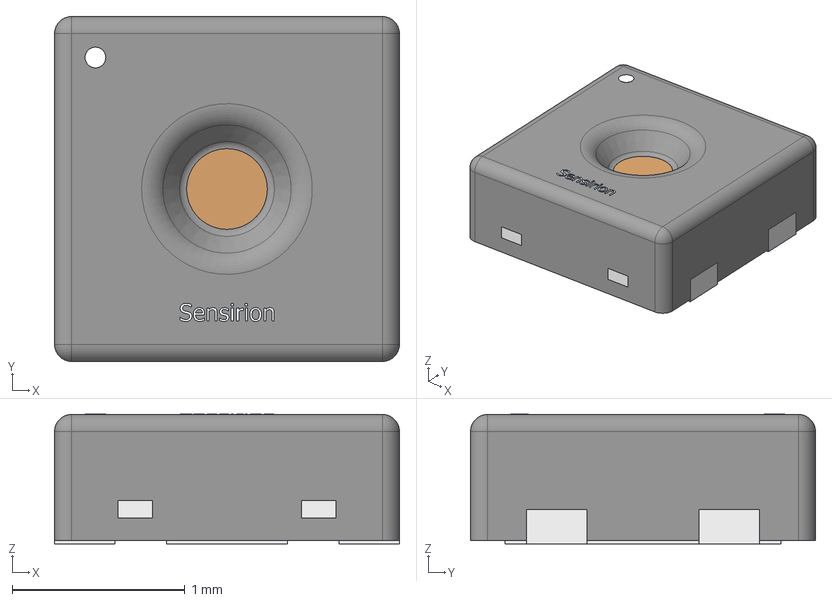
[picture p287: CAD file, 2026-04-15]
hardware-design/examples/08-esp-rust-board/kicad_libs/3d/SHTC3.step
2.00 x 2.00 x 0.751 mm
