rompasaurus/regardedPal/hardware-design/freecad-mk2/Dilder_Rev2_Mk2_NoSolar-Thumbpiece.3mf

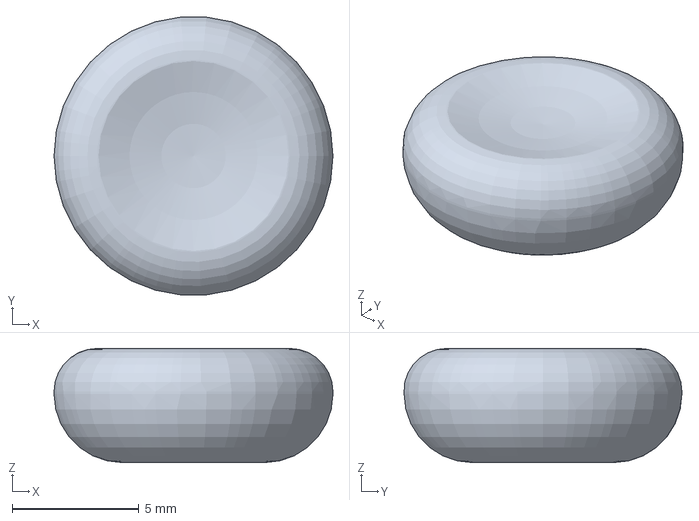
[picture p288: CAD file, 2026-05-06]
hardware-design/freecad-mk2/Dilder_Rev2_Mk2_NoSolar-Thumbpiece.3mf
11.0 x 11.0 x 4.50 mm
