rompasaurus/regardedPal/hardware-design/PCB Designs/joystick-pcb-by-hand/JoystickBoardDilder/JoystickBoardDilder.step

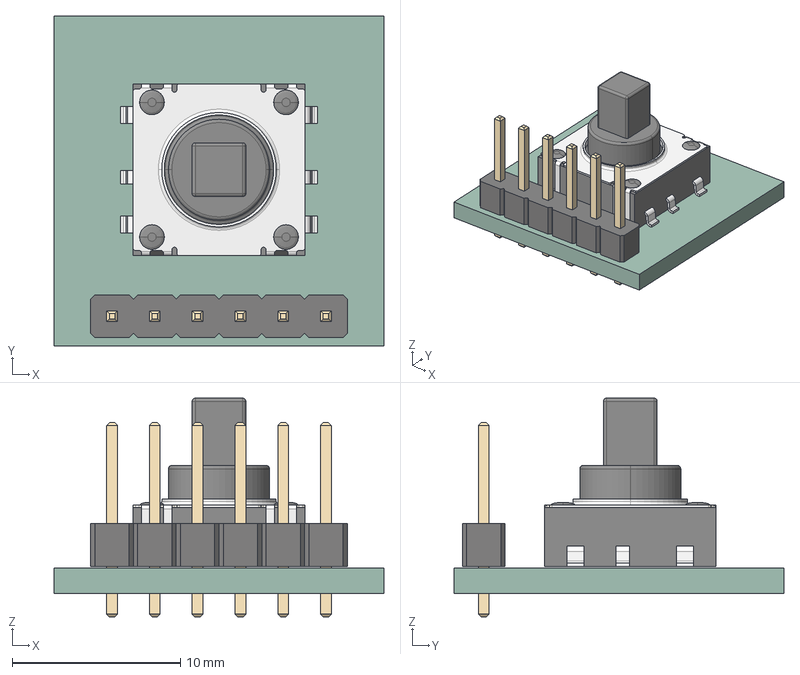
[picture p289: CAD file, 2026-04-29]
hardware-design/PCB Designs/joystick-pcb-by-hand/JoystickBoardDilder/JoystickBoardDilder.step
19.6 x 19.6 x 13.0 mm
KEY-SMD_6P-L10.2-W10.2-H10.0-LS11.7-P6.5
PinHeader_1x06_P2.54mm_Vertical
JoystickBoardDilder_PCB
