rompasaurus/regardedPal/hardware-design/reference-boards/esp32s3-basic-devboard/3d-models/TYPE-C-31-M-12.step

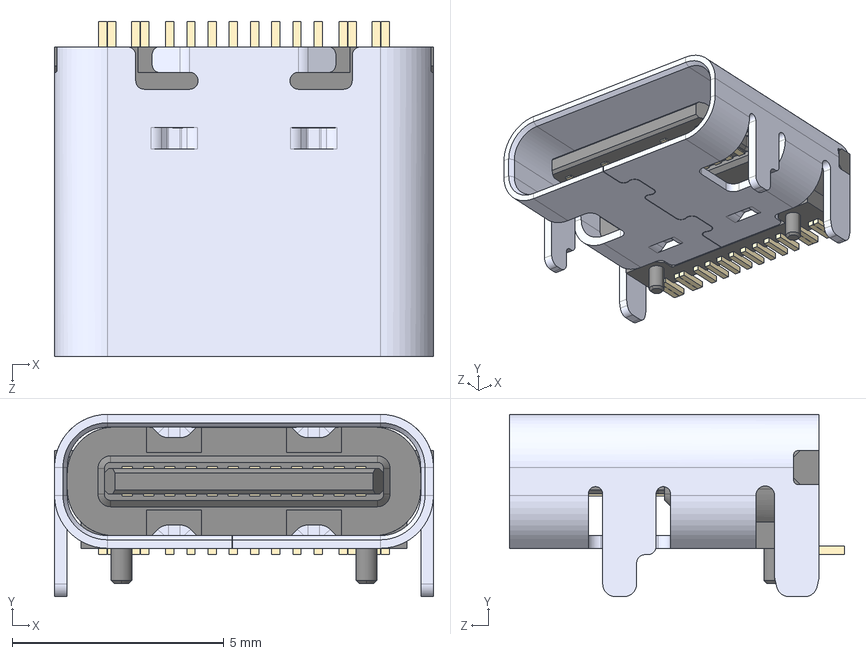
[picture p290: CAD file, 2026-04-15]
hardware-design/reference-boards/esp32s3-basic-devboard/3d-models/TYPE-C-31-M-12.step
8.94 x 4.30 x 7.90 mm
