rompasaurus/regardedPal/hardware-design/reference-boards/raspberry-pi-pico-2/RaspberryPi-Pico-2.step

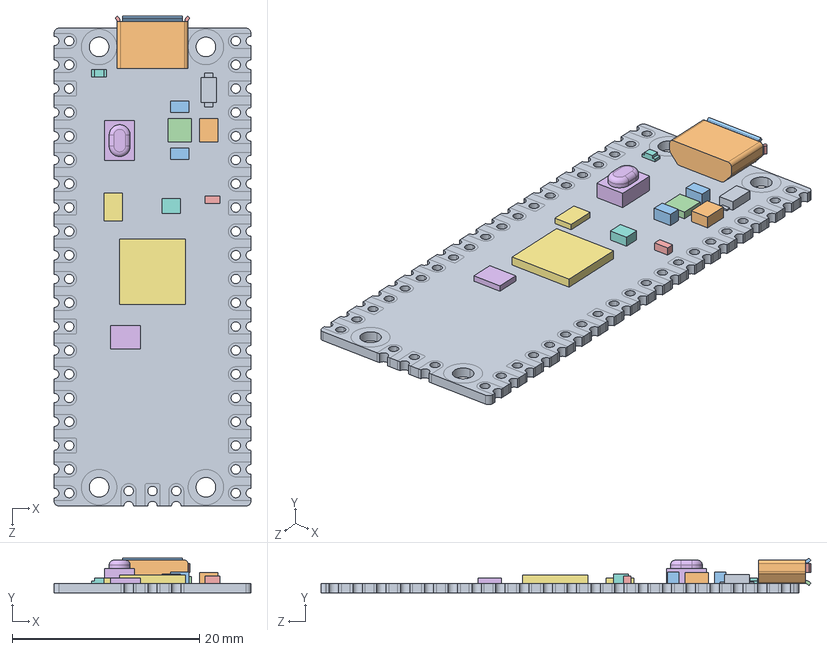
[picture p291: CAD file, 2026-04-29]
hardware-design/reference-boards/raspberry-pi-pico-2/RaspberryPi-Pico-2.step
21.0 x 3.73 x 52.3 mm
PICO_REF_BOARD
PICO_REF_USB
PICO_REF_SWITCH
PICO_REF_MICROCONTROLLER
PICO_REF_LED
PICO_REF_COMP_1
PICO_REF_COMP_2
PICO_REF_COMP_3 x 2
PICO_REF_COMP_4
PICO_REF_COMP_5
PICO_REF_COMP_6
PICO_REF_COMP_7
PICO_REF_INDUCTOR
