rompasaurus/regardedPal/hardware-design/reference-boards/rp2040-pico-usbc/KiCad Projects/Pico 2 C/STEP files/W25Q16JVUXIQ.step

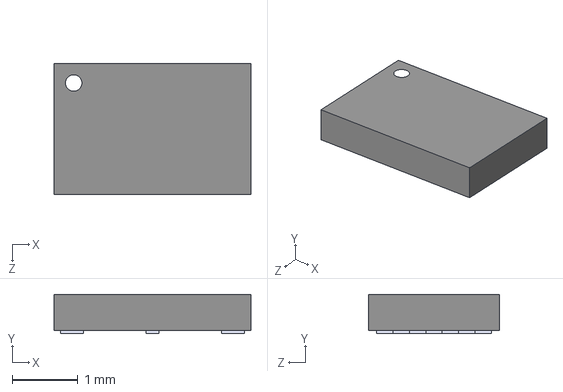
[picture p292: CAD file, 2026-04-15]
hardware-design/reference-boards/rp2040-pico-usbc/KiCad Projects/Pico 2 C/STEP files/W25Q16JVUXIQ.step
3.00 x 0.6 x 2.00 mm
