rompasaurus/regardedPal/hardware-design/reference-boards/rp2040-pico-usbc/KiCad Projects/Pico C/STEP files/RT6150B-33GQW.step

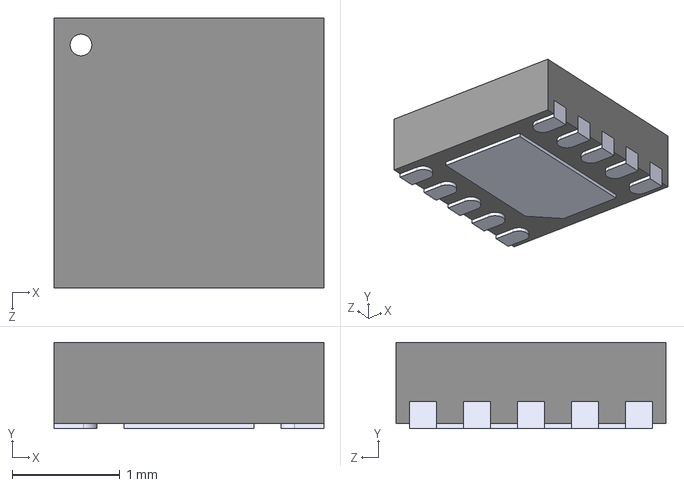
[picture p293: CAD file, 2026-04-15]
hardware-design/reference-boards/rp2040-pico-usbc/KiCad Projects/Pico C/STEP files/RT6150B-33GQW.step
2.50 x 0.8 x 2.50 mm
