rompasaurus/regardedPal/hardware-design/reference-boards/rp2040-pico-usbc/KiCad Projects/Pico WH - No License/STEP files/DMG1012T-7.step

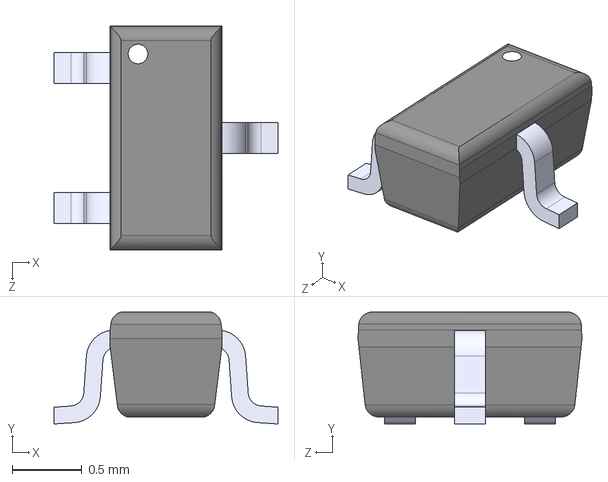
[picture p294: CAD file, 2026-04-15]
hardware-design/reference-boards/rp2040-pico-usbc/KiCad Projects/Pico WH - No License/STEP files/DMG1012T-7.step
1.60 x 0.8 x 1.60 mm
