rompasaurus/regardedPal/hardware-design/scad Parts/Rev 2 extended with joystick/04-24-designs-alterations/aaa-cradle-insert-v1__design_default_values.3mf

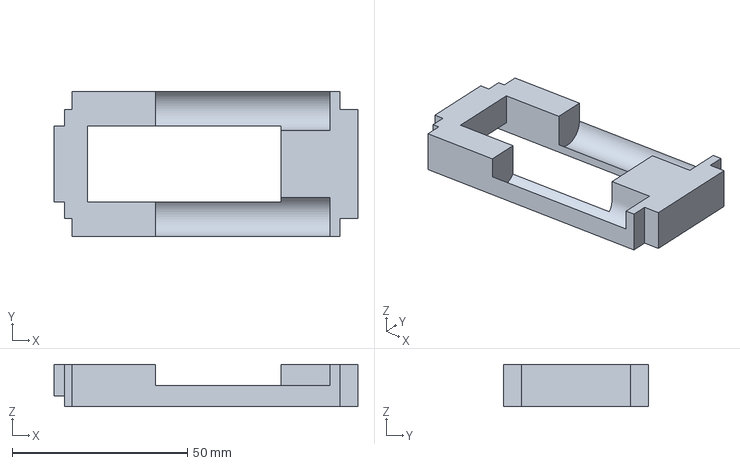
[picture p295: CAD file, 2026-04-26]
hardware-design/scad Parts/Rev 2 extended with joystick/04-24-designs-alterations/aaa-cradle-insert-v1__design_default_values.3mf
86.7 x 41.4 x 12.1 mm
