rompasaurus/regardedPal/hardware-design/scad Parts/Rev 2 extended with joystick/04-26-design-alterations/aaa-cradle-with-batt-clips__battery_clips_forst_print_04-27_Shortened_holesby_5mm_and_opened_batt_clip_window_at_top.3mf

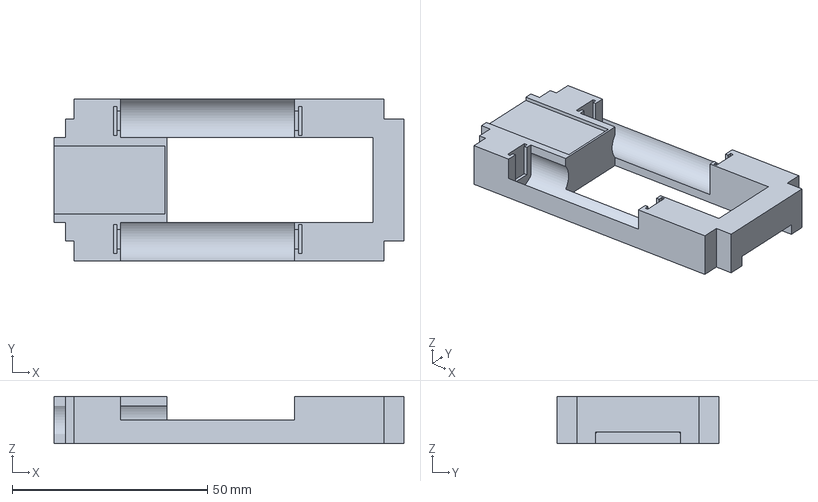
[picture p297: CAD file, 2026-04-27]
hardware-design/scad Parts/Rev 2 extended with joystick/04-26-design-alterations/aaa-cradle-with-batt-clips__battery_clips_forst_print_04-27_Shortened_holesby_5mm_and_opened_batt_clip_window_at_top.3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
89.7 x 41.4 x 12.1 mm
