rompasaurus/regardedPal/hardware-design/scad Parts/Rev 2 extended with joystick/base-v1.3mf

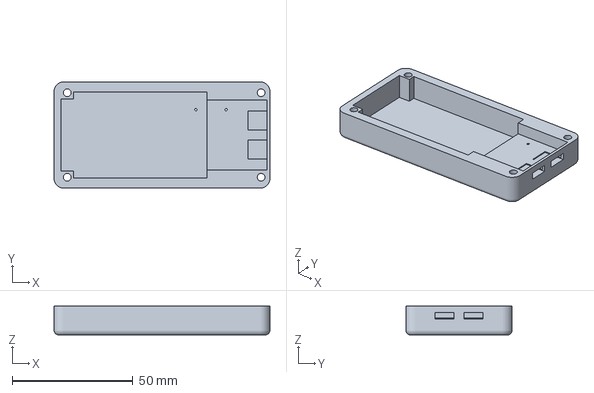
[picture p298: CAD file, 2026-04-23]
hardware-design/scad Parts/Rev 2 extended with joystick/base-v1.3mf
89.5 x 44.0 x 12.0 mm
