rompasaurus/regardedPal/hardware-design/scad Parts/Rev 2 extended with joystick/freecad-export/top-cover-windowed-v1.step

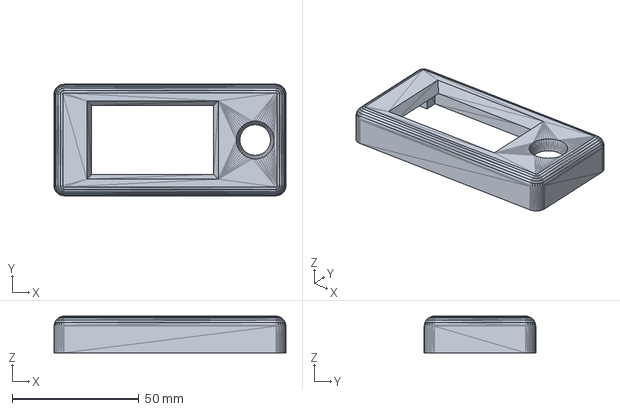
[picture p299: CAD file, 2026-04-25]
hardware-design/scad Parts/Rev 2 extended with joystick/freecad-export/top-cover-windowed-v1.step
91.5 x 44.0 x 14.5 mm
