rompasaurus/regardedPal/tools/design-tracker/.design-tracker/snapshots/snap-0002/Dilder_Rev2_Mk2 .4mm extension fixed lip and curved the thumbstick.FCStd

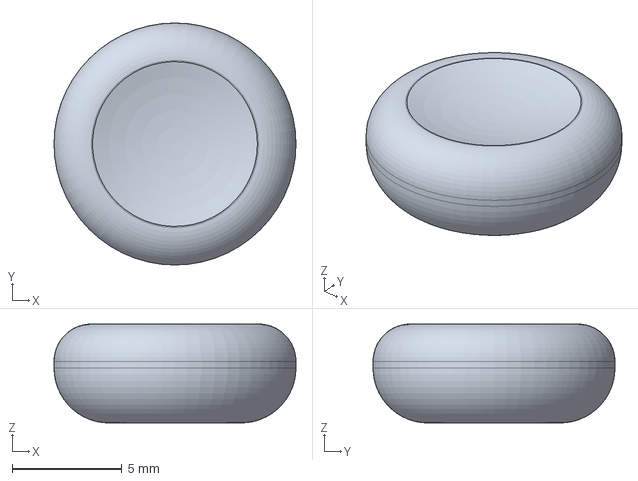
[picture p301: CAD file, 2026-05-01]
tools/design-tracker/.design-tracker/snapshots/snap-0002/Dilder_Rev2_Mk2 .4mm extension fixed lip and curved the thumbstick.FCStd
11.0 x 11.0 x 4.50 mm
