rompasaurus/regardedPal/hardware-design/examples/02-lilka-console/hardware/v2/3dmodels/12mm Push Button with Black Cap.STEP

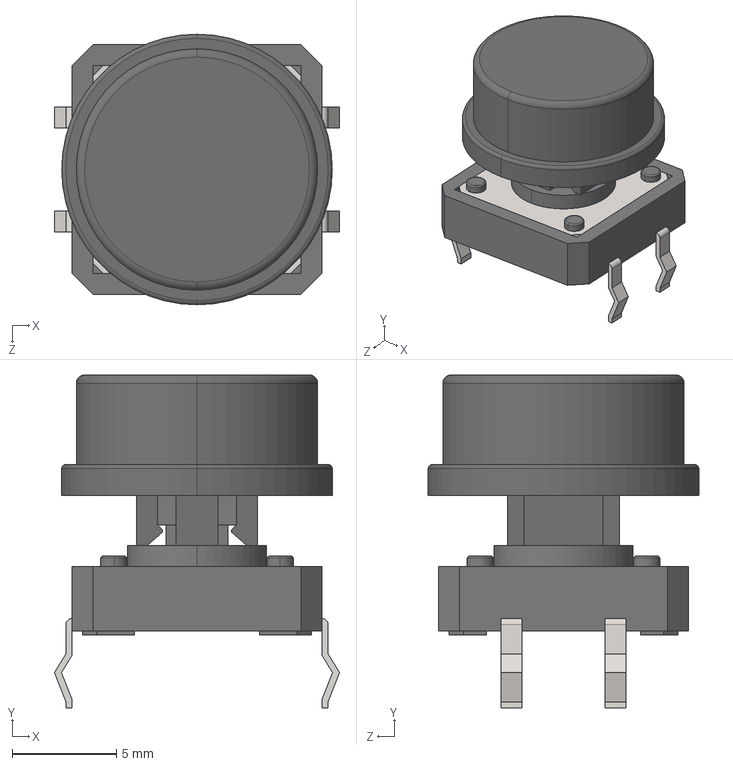
[picture p302: CAD file, 2026-04-15]
hardware-design/examples/02-lilka-console/hardware/v2/3dmodels/12mm Push Button with Black Cap.STEP
13.7 x 16.0 x 13.0 mm
12mm Push Button
12mm Push Button Cap
