rompasaurus/regardedPal/hardware-design/examples/04-olimex-s3-devkit-lipo/HARDWARE/ESP32-S3-DevKit-LiPo_Rev_B/3d/SOT-23-5.step

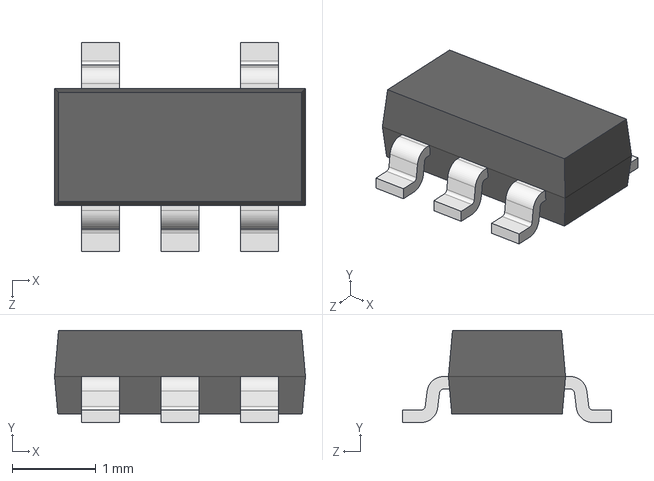
[picture p303: CAD file, 2026-04-15]
hardware-design/examples/04-olimex-s3-devkit-lipo/HARDWARE/ESP32-S3-DevKit-LiPo_Rev_B/3d/SOT-23-5.step
3.00 x 1.10 x 2.50 mm
