rompasaurus/regardedPal/hardware-design/examples/05-olimex-devkit-lipo/HARDWARE/ESP32-DevKit-LiPo-Rev.D/3d/usb_micro_4p.stp

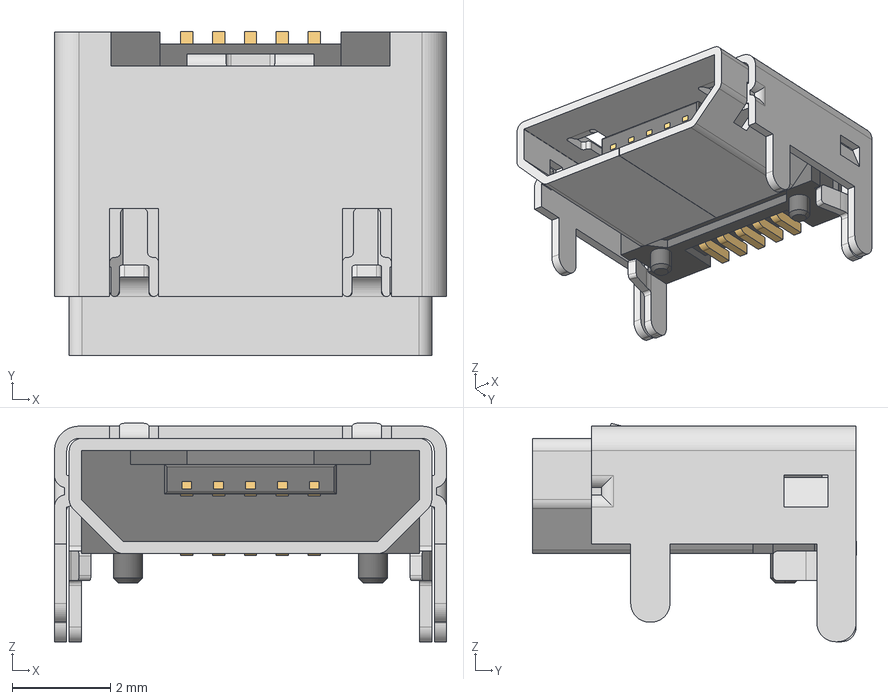
[picture p304: CAD file, 2026-04-15]
hardware-design/examples/05-olimex-devkit-lipo/HARDWARE/ESP32-DevKit-LiPo-Rev.D/3d/usb_micro_4p.stp
8.00 x 6.60 x 4.46 mm
