rompasaurus/regardedPal/hardware-design/examples/06-unexpected-maker-s3/3d models/OMGS3/OMGUSB.step

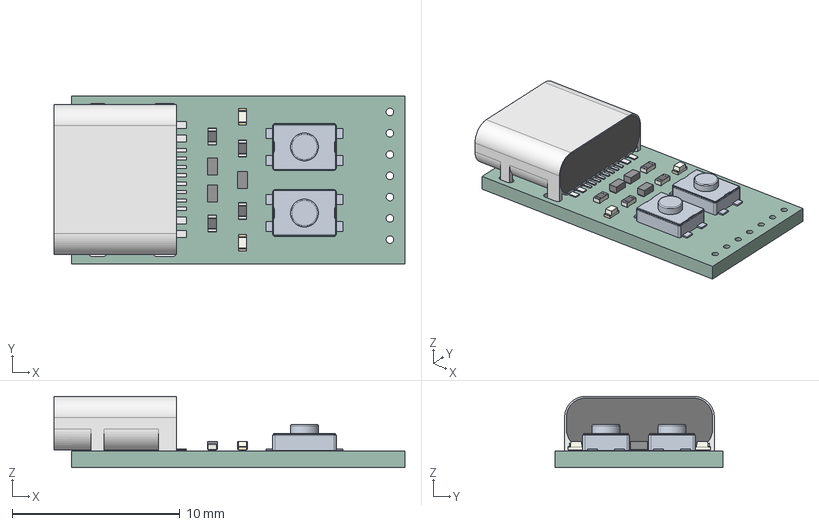
[picture p305: CAD file, 2026-04-15]
hardware-design/examples/06-unexpected-maker-s3/3d models/OMGS3/OMGUSB.step
21.0 x 10.0 x 4.26 mm
R_0402_1005Metric x 4
BTN_KMR2_4.6X2.8_HAND v1 x 2
HRO USB-C col 3 v9
TESD5V0L1UC RJG x 3
LED_0402_1005Metric x 2
OMGUSB_P3_PCB
