rompasaurus/regardedPal/hardware-design/examples/06-unexpected-maker-s3/series_d/3d models/TinyS3D.step

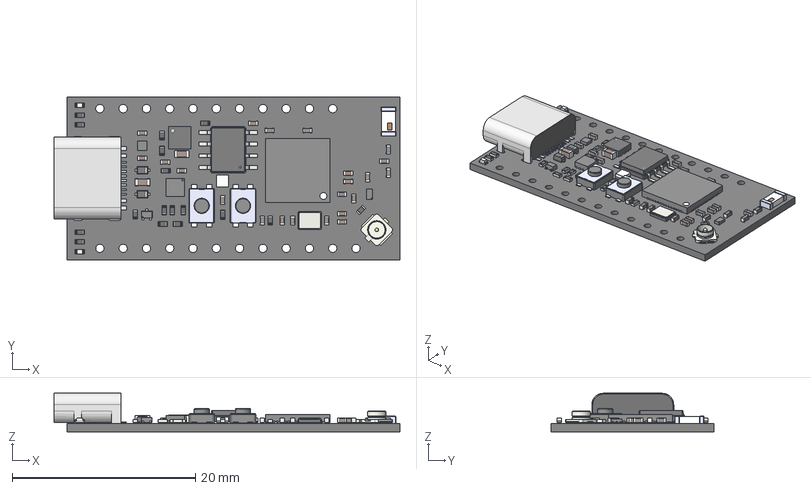
[picture p306: CAD file, 2026-04-15]
hardware-design/examples/06-unexpected-maker-s3/series_d/3d models/TinyS3D.step
37.7 x 17.8 x 4.21 mm
R_0402_1005Metric x 17
C_0402_1005Metric x 19
TDFN-6-1EP_2.5x2.5mm_P0.65mm_EP1.3x2mm
L_0402_1005Metric x 3
KMR221GLFS--3DModel-STEP-56544 v3 x 2
U.FL_Hirose_U.FL-R-SMT-1_Vertical
BGS12WN6E6327XTSA1
LED_0402_1005Metric x 2
MAX17048G-T10
SOT-723
NCP170AMX170TCG
D_SOD-523 x 2
SSOP-8_3.9x5.05mm_P1.27mm
2450AT18B100E--3DModel-STEP-269445
Crystal_SMD_3225-4Pin_3.2x2.5mm_HandSoldering
C_0603_1608Metric x 2
ESP32_S2--3DModel-STEP-1
HIRO-USB-C Fixed Position
TinyS3D_P1_PCB
