rompasaurus/regardedPal/hardware-design/examples/08-esp-rust-board/kicad_libs/3d/ICM-42670-P.step

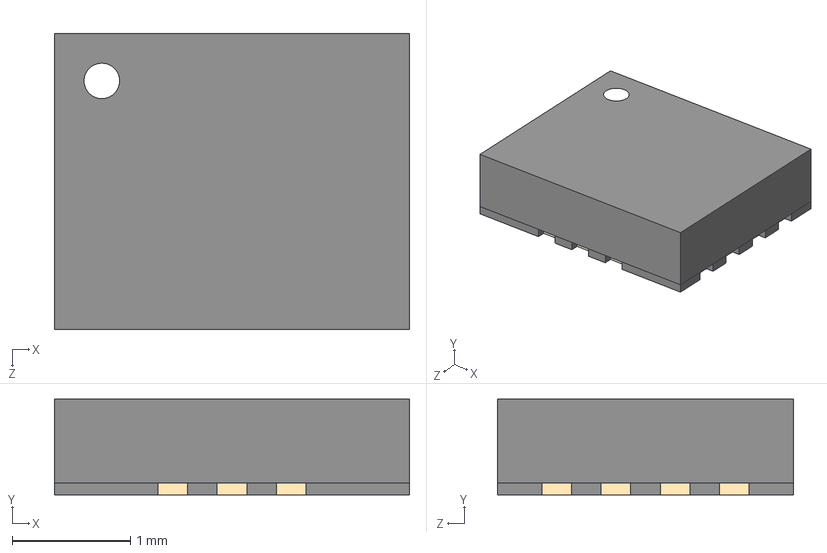
[picture p307: CAD file, 2026-04-15]
hardware-design/examples/08-esp-rust-board/kicad_libs/3d/ICM-42670-P.step
3.00 x 0.81 x 2.50 mm
