rompasaurus/regardedPal/hardware-design/freecad-mk2/loerclearer batter top and bottom.3mf

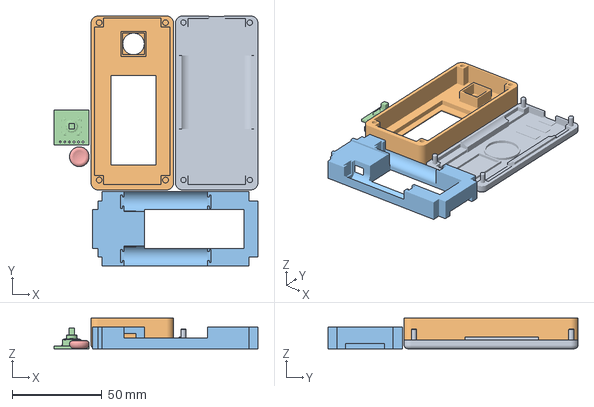
[picture p308: CAD file, 2026-05-04]
hardware-design/freecad-mk2/loerclearer batter top and bottom.3mf
113.6 x 139.3 x 17.0 mm
