rompasaurus/regardedPal/hardware-design/reference-boards/esp32s3-basic-devboard/3d-models/SW-SMD_L3.9-W2.9-H2.0-LS4.8.step

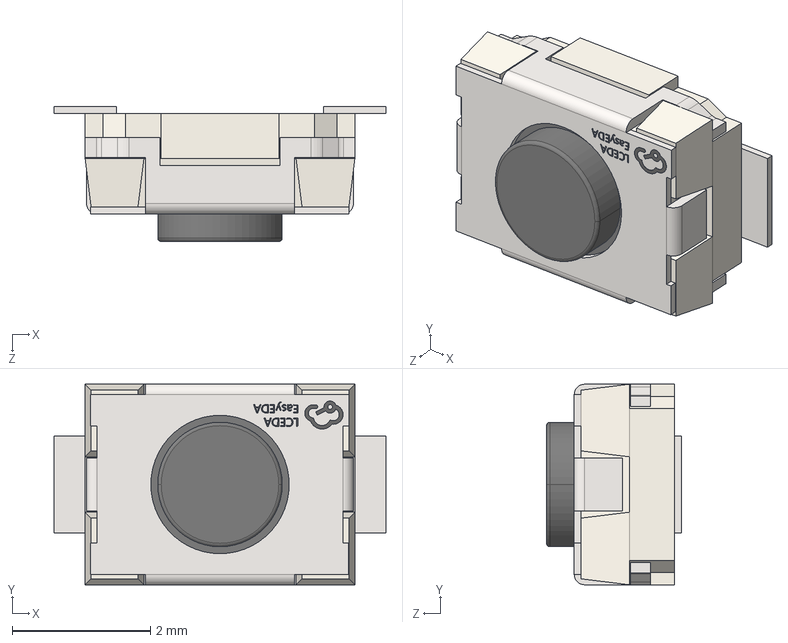
[picture p309: CAD file, 2026-04-15]
hardware-design/reference-boards/esp32s3-basic-devboard/3d-models/SW-SMD_L3.9-W2.9-H2.0-LS4.8.step
4.80 x 2.90 x 1.95 mm
