rompasaurus/regardedPal/hardware-design/reference-boards/rp2040-pico-usbc/KiCad Projects/Pico C/STEP files/SM03B-SRSS-TB_LF__SN_.step

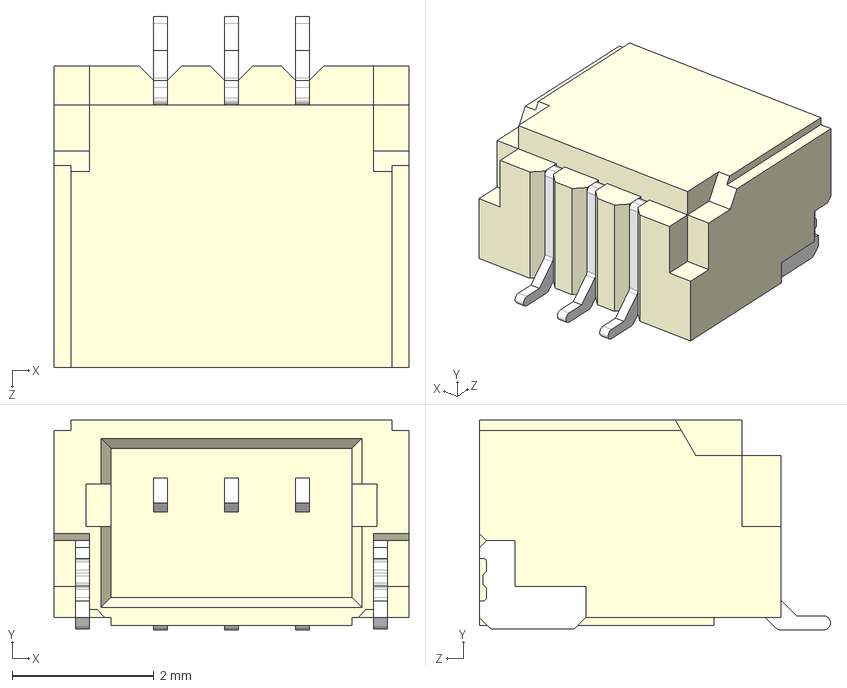
[picture p310: CAD file, 2026-04-15]
hardware-design/reference-boards/rp2040-pico-usbc/KiCad Projects/Pico C/STEP files/SM03B-SRSS-TB_LF__SN_.step
5.00 x 2.96 x 4.95 mm
