rompasaurus/regardedPal/hardware-design/reference-boards/rp2040-pico-usbc/KiCad Projects/Pico WH - No License/STEP files/8Q-37.400MEEE-T.step

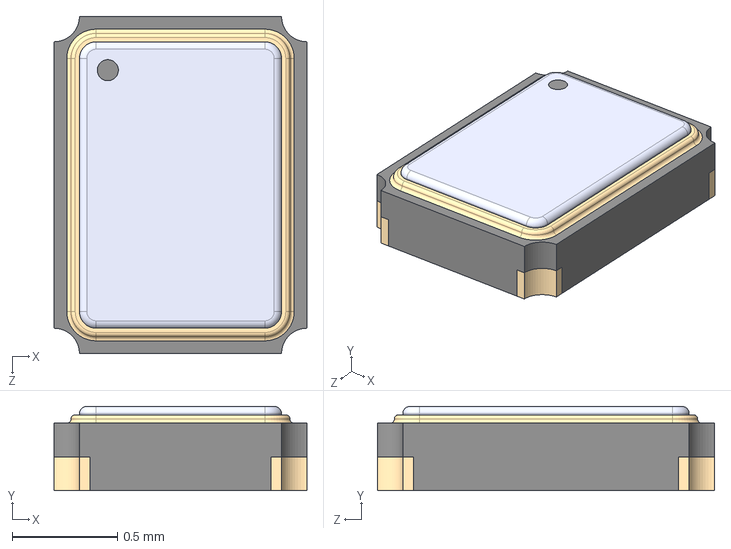
[picture p311: CAD file, 2026-04-15]
hardware-design/reference-boards/rp2040-pico-usbc/KiCad Projects/Pico WH - No License/STEP files/8Q-37.400MEEE-T.step
1.20 x 0.4 x 1.60 mm
