rompasaurus/regardedPal/hardware-design/scad Parts/Rev 2 extended with joystick/04-25-design-alterations/top-cover-windowed-screen-inlay-v3-2piece__working_face_flace_lowered_radius_curvature_1mm_face_plate_thickness.3mf

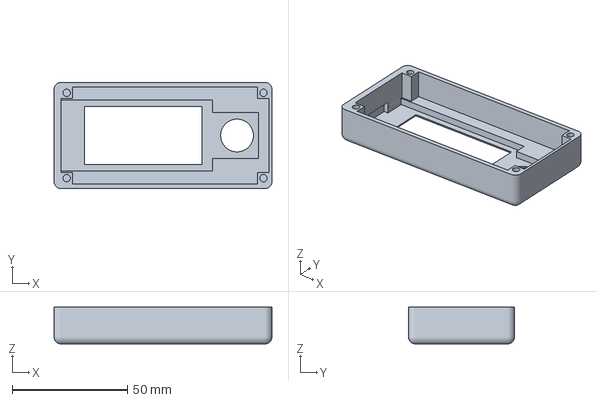
[picture p312: CAD file, 2026-04-26]
hardware-design/scad Parts/Rev 2 extended with joystick/04-25-design-alterations/top-cover-windowed-screen-inlay-v3-2piece__working_face_flace_lowered_radius_curvature_1mm_face_plate_thickness.3mf
94.5 x 46.0 x 16.0 mm
