rompasaurus/regardedPal/hardware-design/scad Parts/Rev 2 extended with joystick/freecad-export/top-cover-windowed-screen-inlay-v1-2mm.step

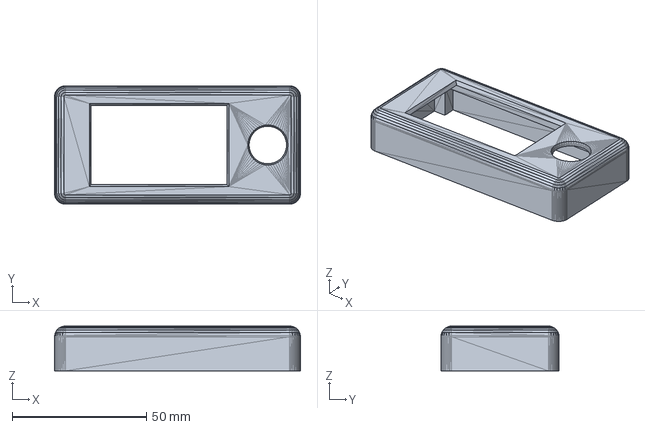
[picture p313: CAD file, 2026-04-25]
hardware-design/scad Parts/Rev 2 extended with joystick/freecad-export/top-cover-windowed-screen-inlay-v1-2mm.step
91.5 x 44.0 x 16.7 mm
