rompasaurus/regardedPal/hardware-design/examples/04-olimex-s3-devkit-lipo/HARDWARE/ESP32-S3-DevKit-LiPo_Rev_B/3d/MSOP10-1.step

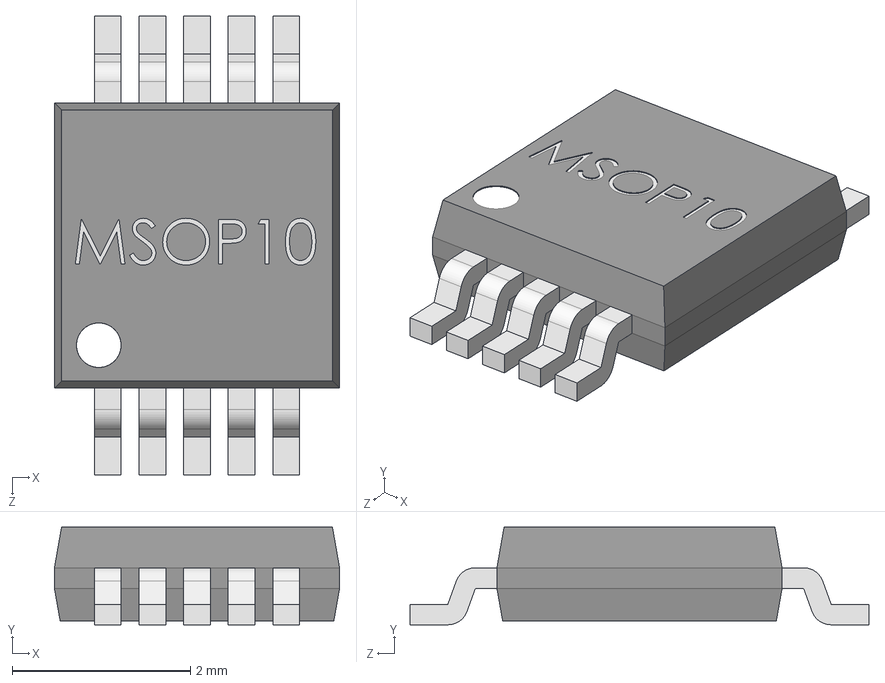
[picture p314: CAD file, 2026-04-15]
hardware-design/examples/04-olimex-s3-devkit-lipo/HARDWARE/ESP32-S3-DevKit-LiPo_Rev_B/3d/MSOP10-1.step
3.20 x 1.10 x 5.15 mm
