rompasaurus/regardedPal/hardware-design/examples/06-unexpected-maker-s3/3d models/OMGS3/OMGS3_Carrier.step

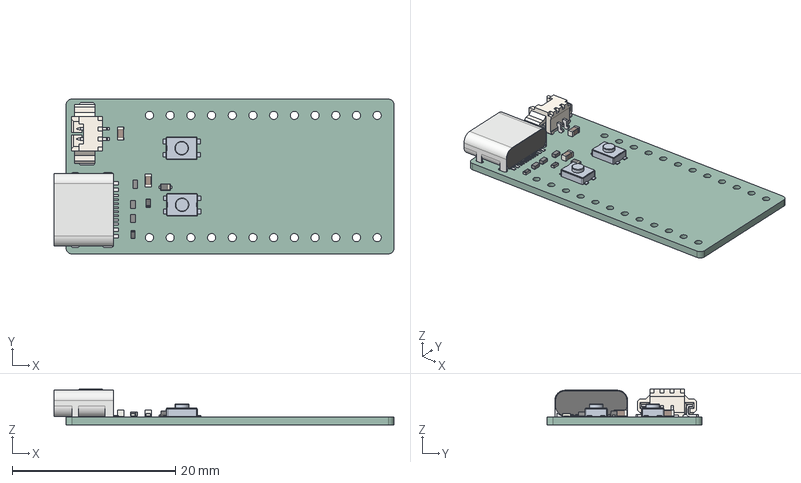
[picture p315: CAD file, 2026-04-15]
hardware-design/examples/06-unexpected-maker-s3/3d models/OMGS3/OMGS3_Carrier.step
41.7 x 19.0 x 4.40 mm
C_0603_1608Metric x 2
PICOBLADE v1
BTN_KMR2_4.6X2.8_HAND v1 x 2
R_0402_1005Metric x 2
TESD5V0L1UC RJG x 3
HRO USB-C col 3 v9
D_SOD_523
OMGS3_Carrier_R1_PCB
