rompasaurus/regardedPal/hardware-design/examples/08-esp-rust-board/kicad_libs/3d/PTS810SJK250SMTRLFS.step

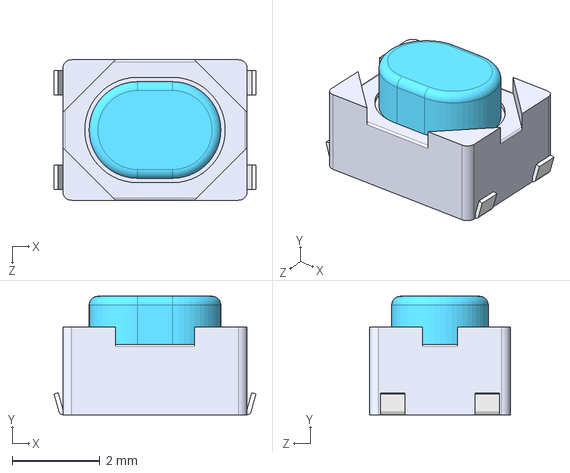
[picture p316: CAD file, 2026-04-15]
hardware-design/examples/08-esp-rust-board/kicad_libs/3d/PTS810SJK250SMTRLFS.step
4.60 x 2.70 x 3.20 mm
