rompasaurus/regardedPal/hardware-design/freecad-mk2/Dilder_Rev2_Mk2_NoSolar Thicker Base longer peg shorter pillars(ext_z).FCStd

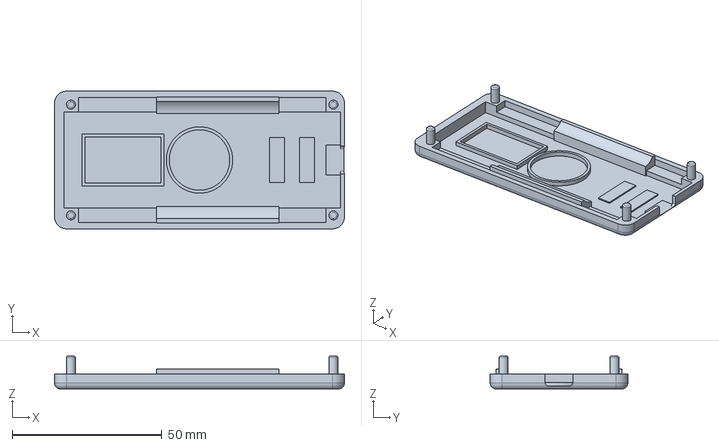
[picture p317: CAD file, 2026-05-04]
hardware-design/freecad-mk2/Dilder_Rev2_Mk2_NoSolar Thicker Base longer peg shorter pillars(ext_z).FCStd
96.9 x 46.0 x 11.0 mm
