rompasaurus/regardedPal/hardware-design/reference-boards/rp2040-pico-usbc/KiCad Projects/Pico 2 C/STEP files/SW_SPST_PTS810.step

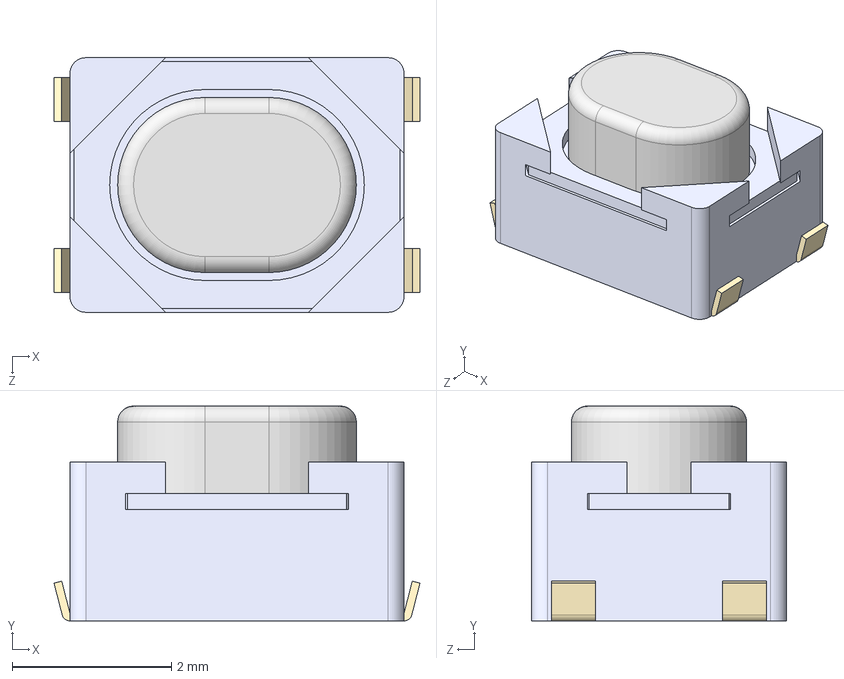
[picture p318: CAD file, 2026-04-15]
hardware-design/reference-boards/rp2040-pico-usbc/KiCad Projects/Pico 2 C/STEP files/SW_SPST_PTS810.step
4.60 x 2.70 x 3.20 mm
