rompasaurus/regardedPal/hardware-design/reference-boards/rp2040-pico-usbc/KiCad Projects/Pico WH - No License/STEP files/LFB212G45CG7D227.stp

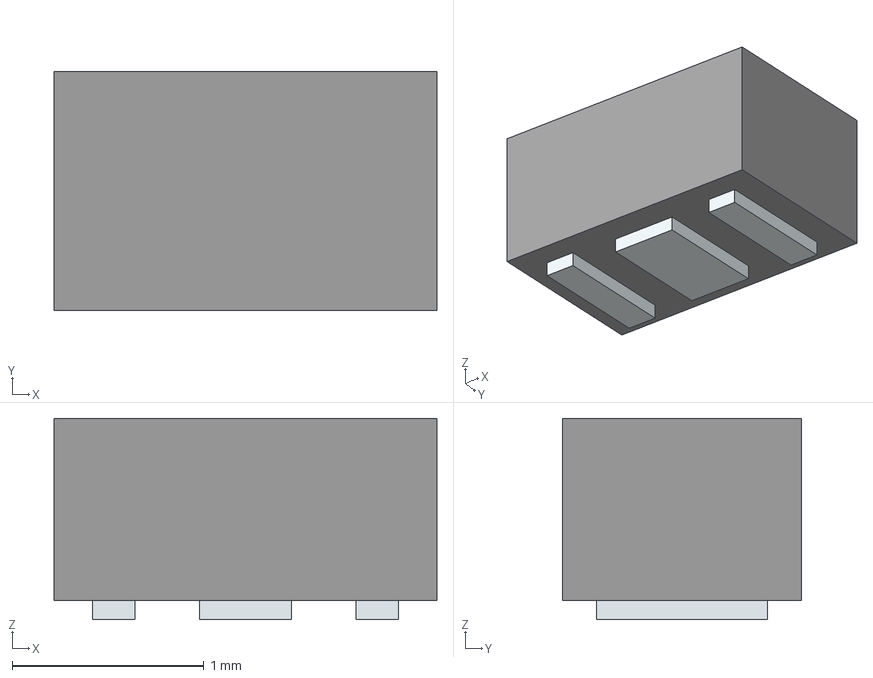
[picture p319: CAD file, 2026-04-15]
hardware-design/reference-boards/rp2040-pico-usbc/KiCad Projects/Pico WH - No License/STEP files/LFB212G45CG7D227.stp
2.00 x 1.25 x 1.05 mm
Pins
