rompasaurus/regardedPal/hardware-design/examples/02-lilka-console/hardware/v2/3dmodels/USB-C board JRC-B023.step

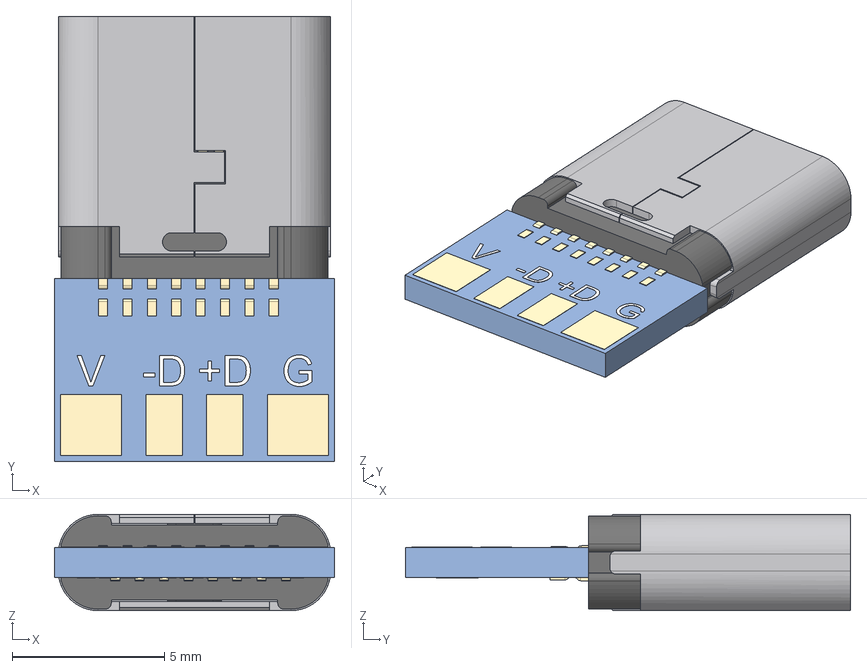
[picture p320: CAD file, 2026-04-15]
hardware-design/examples/02-lilka-console/hardware/v2/3dmodels/USB-C board JRC-B023.step
9.20 x 14.6 x 3.16 mm
USB_C_SHELL
USB_C_Body
USB_C_PIN x 16
PCB board
text
Contacts
