rompasaurus/regardedPal/hardware-design/examples/04-olimex-s3-devkit-lipo/HARDWARE/ESP32-S3-DevKit-LiPo_Rev_B/3d/L-CD32_shielded.step

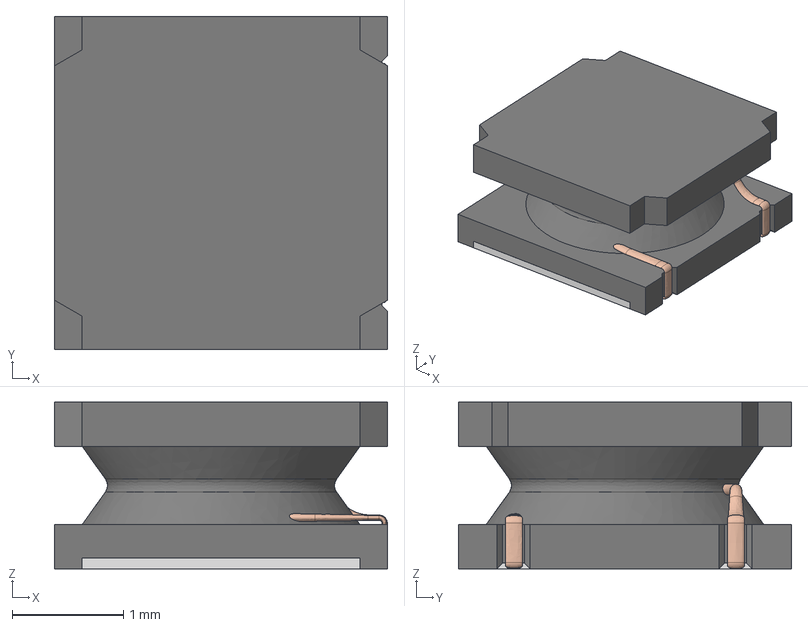
[picture p321: CAD file, 2026-04-15]
hardware-design/examples/04-olimex-s3-devkit-lipo/HARDWARE/ESP32-S3-DevKit-LiPo_Rev_B/3d/L-CD32_shielded.step
3.00 x 3.00 x 1.50 mm
