rompasaurus/regardedPal/hardware-design/examples/05-olimex-devkit-lipo/HARDWARE/ESP32-DevKit-LiPo-Rev.D/3d/ESP32-WROOM-32D-56544.STEP

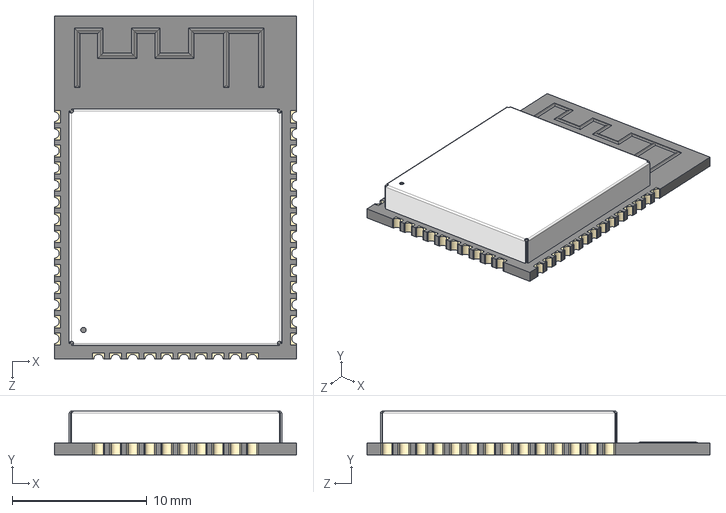
[picture p322: CAD file, 2026-04-15]
hardware-design/examples/05-olimex-devkit-lipo/HARDWARE/ESP32-DevKit-LiPo-Rev.D/3d/ESP32-WROOM-32D-56544.STEP
18.0 x 3.25 x 25.5 mm
