rompasaurus/regardedPal/hardware-design/examples/08-esp-rust-board/kicad_libs/3d/USB4105-GF-A.step

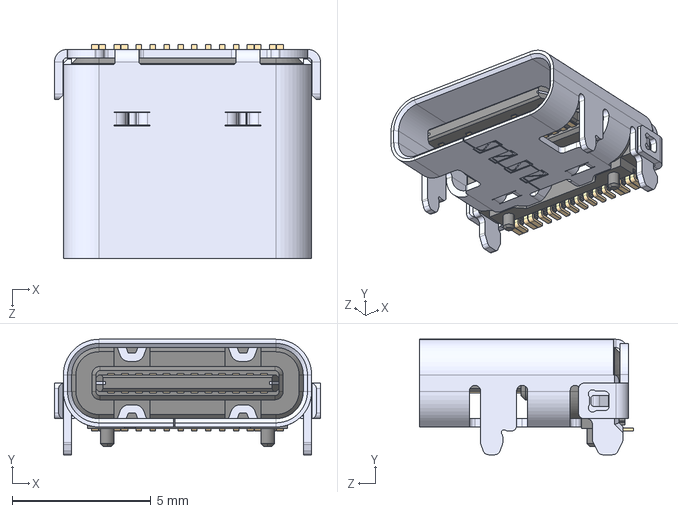
[picture p323: CAD file, 2026-04-15]
hardware-design/examples/08-esp-rust-board/kicad_libs/3d/USB4105-GF-A.step
9.58 x 4.16 x 7.71 mm
