rompasaurus/regardedPal/hardware-design/scad Parts/Rev 2 extended with joystick/04-25-design-alterations/base-plate-v1-2mm-thinner__pillar_instert_thinner_4mm.3mf

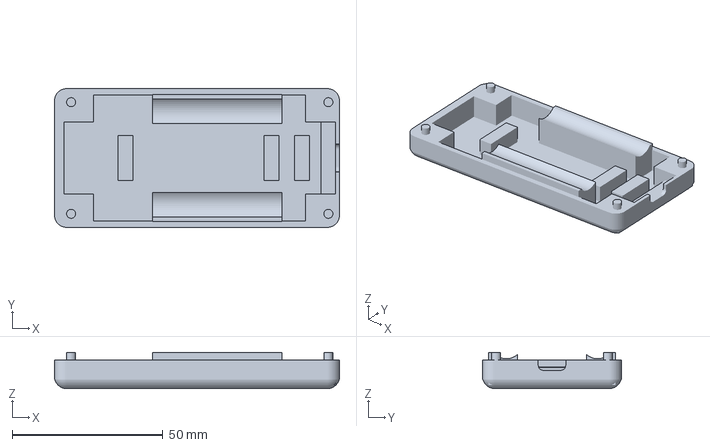
[picture p324: CAD file, 2026-04-26]
hardware-design/scad Parts/Rev 2 extended with joystick/04-25-design-alterations/base-plate-v1-2mm-thinner__pillar_instert_thinner_4mm.3mf
94.5 x 46.0 x 12.0 mm
