rompasaurus/regardedPal/hardware-design/examples/04-olimex-s3-devkit-lipo/HARDWARE/ESP32-S3-DevKit-LiPo_Rev_B/3d/YTS-A016-X(SKRPABE010).stp

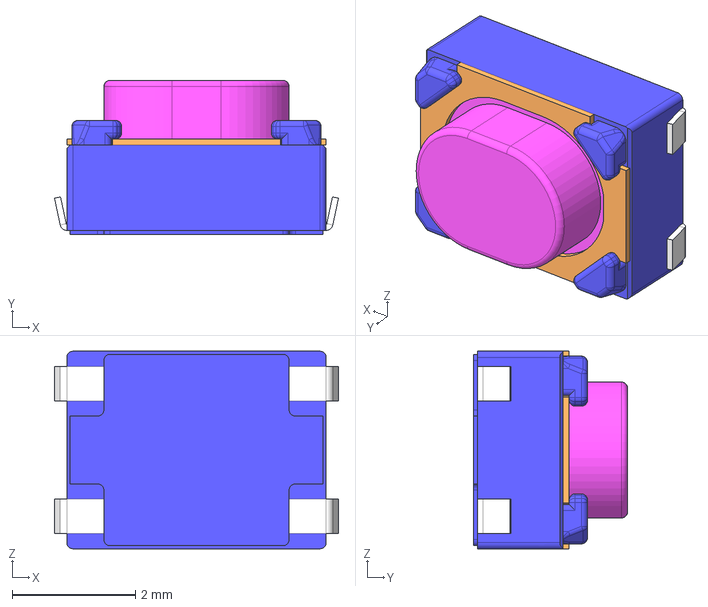
[picture p325: CAD file, 2026-04-15]
hardware-design/examples/04-olimex-s3-devkit-lipo/HARDWARE/ESP32-S3-DevKit-LiPo_Rev_B/3d/YTS-A016-X(SKRPABE010).stp
4.60 x 2.50 x 3.20 mm
