rompasaurus/regardedPal/hardware-design/examples/08-esp-rust-board/kicad_libs/3d/WS2812B-MINI.step

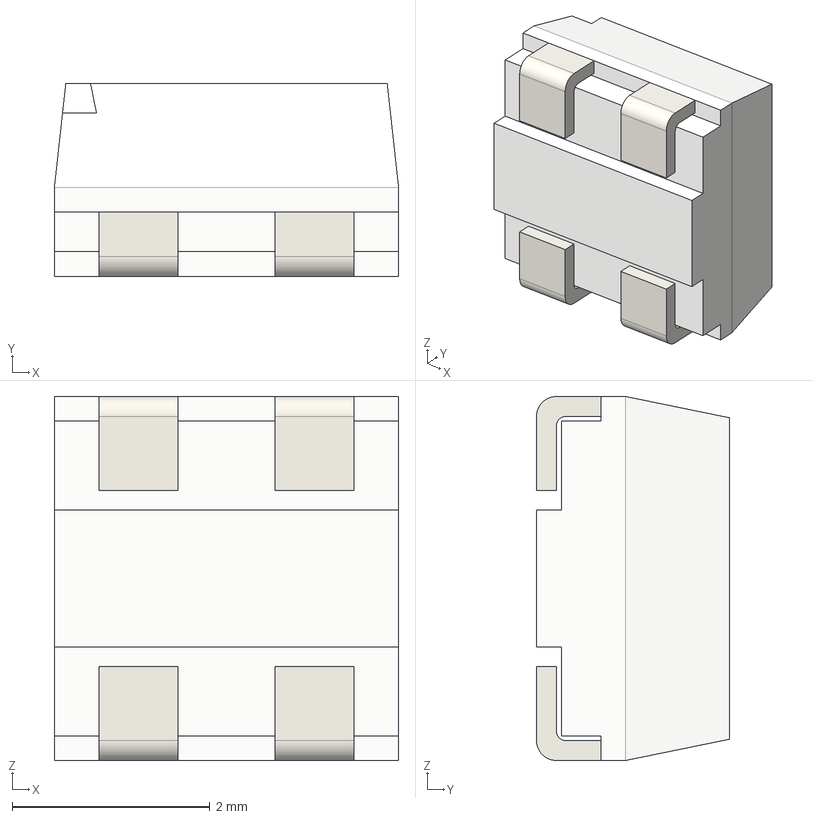
[picture p326: CAD file, 2026-04-15]
hardware-design/examples/08-esp-rust-board/kicad_libs/3d/WS2812B-MINI.step
3.48 x 1.95 x 3.68 mm
