rompasaurus/regardedPal/hardware-design/freecad-mk2/Dilder_Rev2_Mk2_NoSolar-AAACradle.3mf

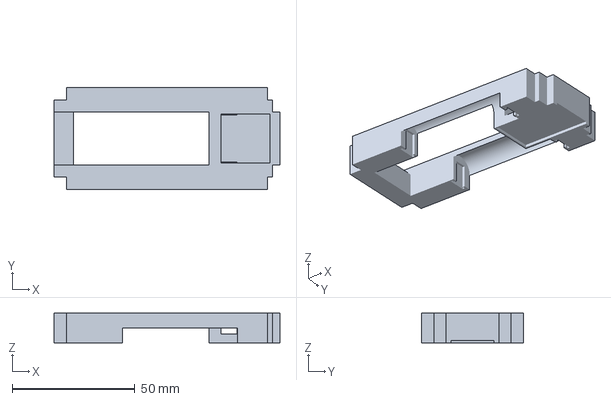
[picture p327: CAD file, 2026-05-02]
hardware-design/freecad-mk2/Dilder_Rev2_Mk2_NoSolar-AAACradle.3mf
92.1 x 41.4 x 12.1 mm
