rompasaurus/regardedPal/hardware-design/reference-boards/rp2040-pico-usbc/KiCad Projects/Pico WH - No License/STEP files/BGA-63.step

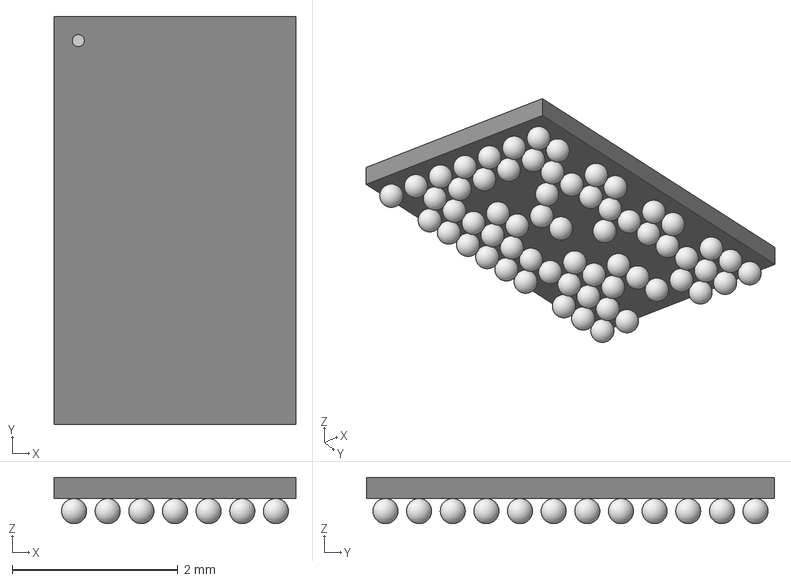
[picture p328: CAD file, 2026-04-15]
hardware-design/reference-boards/rp2040-pico-usbc/KiCad Projects/Pico WH - No License/STEP files/BGA-63.step
2.92 x 4.93 x 0.561 mm
