rompasaurus/regardedPal/hardware-design/examples/02-lilka-console/hardware/v2/3dmodels/ALPHA-RD901F-40.step

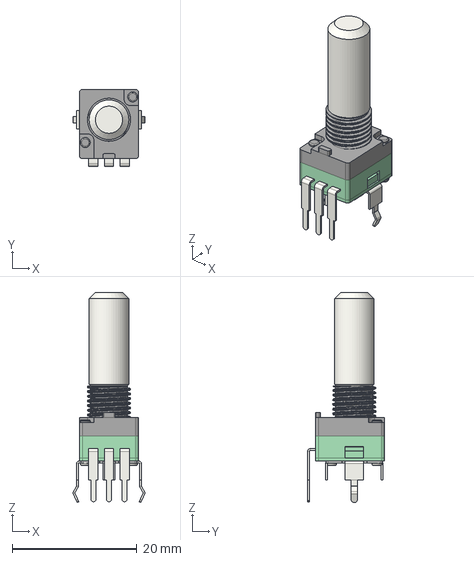
[picture p329: CAD file, 2026-04-15]
hardware-design/examples/02-lilka-console/hardware/v2/3dmodels/ALPHA-RD901F-40.step
11.5 x 12.4 x 33.6 mm
