rompasaurus/regardedPal/hardware-design/examples/04-olimex-s3-devkit-lipo/HARDWARE/ESP32-S3-DevKit-LiPo_Rev_B/3d/HN1x22-PinHeader_1x22_P2.54mm_Vertical.step

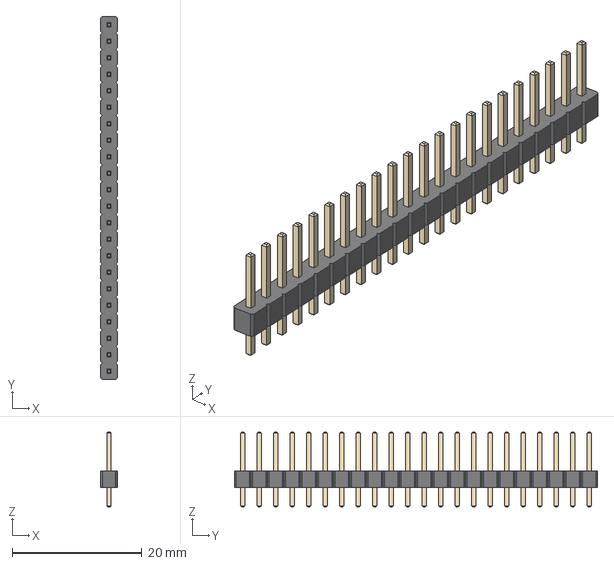
[picture p330: CAD file, 2026-04-15]
hardware-design/examples/04-olimex-s3-devkit-lipo/HARDWARE/ESP32-S3-DevKit-LiPo_Rev_B/3d/HN1x22-PinHeader_1x22_P2.54mm_Vertical.step
2.54 x 55.9 x 11.5 mm
