rompasaurus/regardedPal/hardware-design/examples/05-olimex-devkit-lipo/HARDWARE/ESP32-DevKit-LiPo-Rev.D/3d/SOD123.step

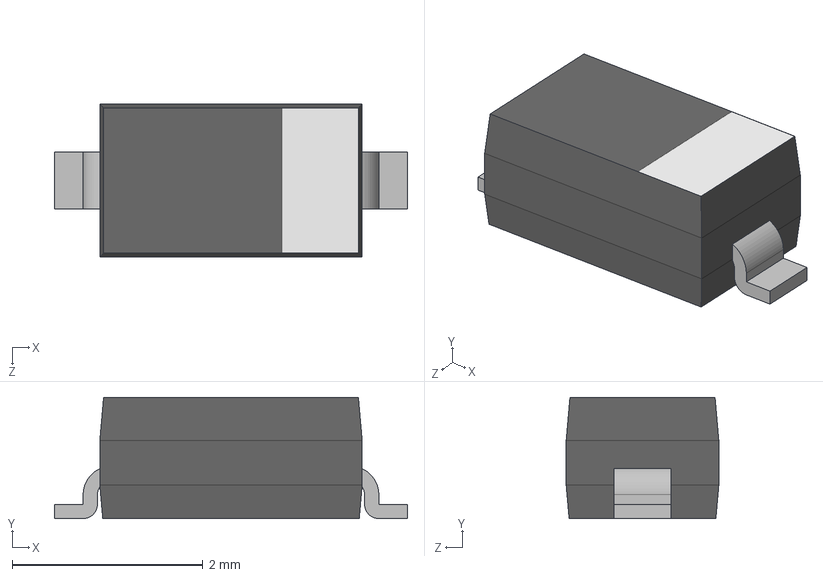
[picture p331: CAD file, 2026-04-15]
hardware-design/examples/05-olimex-devkit-lipo/HARDWARE/ESP32-DevKit-LiPo-Rev.D/3d/SOD123.step
3.70 x 1.27 x 1.60 mm
