rompasaurus/regardedPal/hardware-design/reference-boards/rp2040-pico-usbc/KiCad Projects/Pico WH - No License/STEP files/BM03B-SRSS-TB-LF--SN---3DModel-STEP-56544.STEP

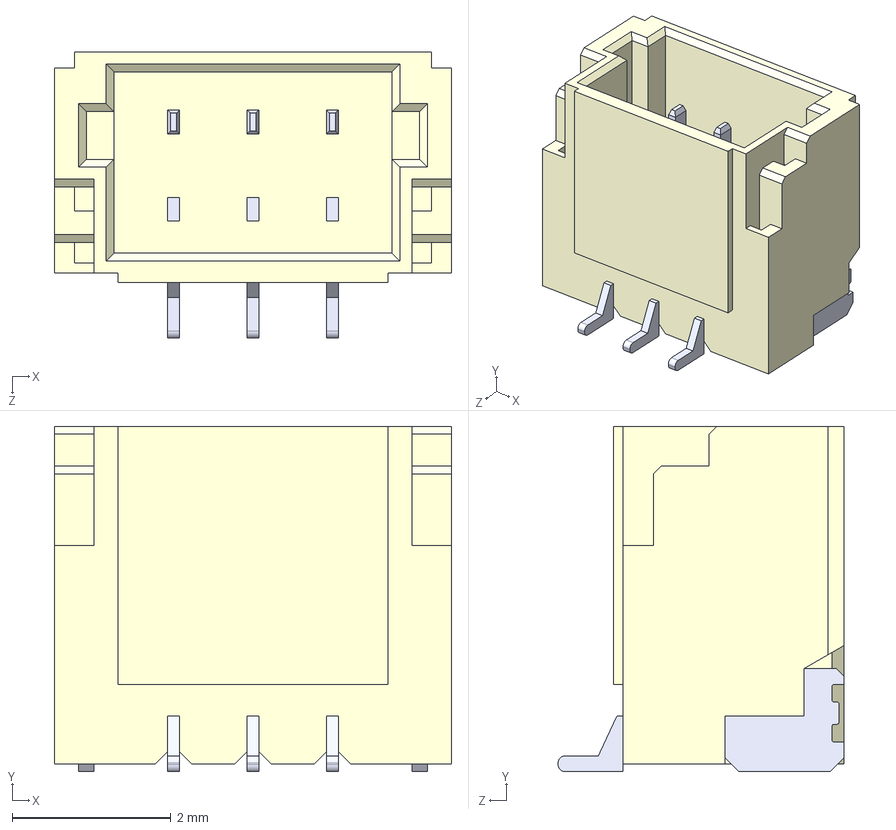
[picture p332: CAD file, 2026-04-15]
hardware-design/reference-boards/rp2040-pico-usbc/KiCad Projects/Pico WH - No License/STEP files/BM03B-SRSS-TB-LF--SN---3DModel-STEP-56544.STEP
5.00 x 4.35 x 3.60 mm
