rompasaurus/regardedPal/hardware-design/examples/04-olimex-s3-devkit-lipo/HARDWARE/ESP32-S3-DevKit-LiPo_Rev_B/3d/BM10B-SRSS-TB(JST_GH_BM10B-GHS-TBT_1x10-1MP_P1.25mm_Vertical).step

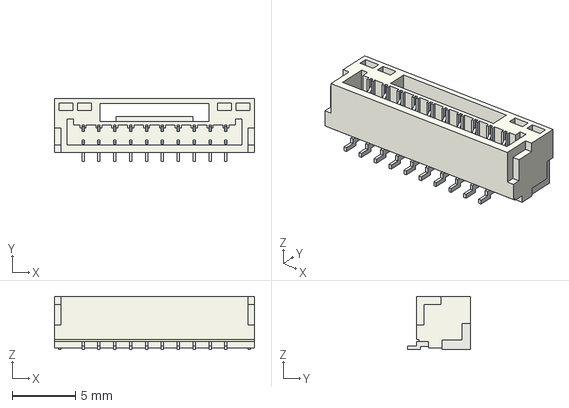
[picture p333: CAD file, 2026-04-15]
hardware-design/examples/04-olimex-s3-devkit-lipo/HARDWARE/ESP32-S3-DevKit-LiPo_Rev_B/3d/BM10B-SRSS-TB(JST_GH_BM10B-GHS-TBT_1x10-1MP_P1.25mm_Vertical).step
15.8 x 4.95 x 4.20 mm
