rompasaurus/regardedPal/hardware-design/examples/05-olimex-devkit-lipo/HARDWARE/ESP32-DevKit-LiPo-Rev.D/3d/HN1x19-PinHeader_1x19_P2.54mm_Vertical.step

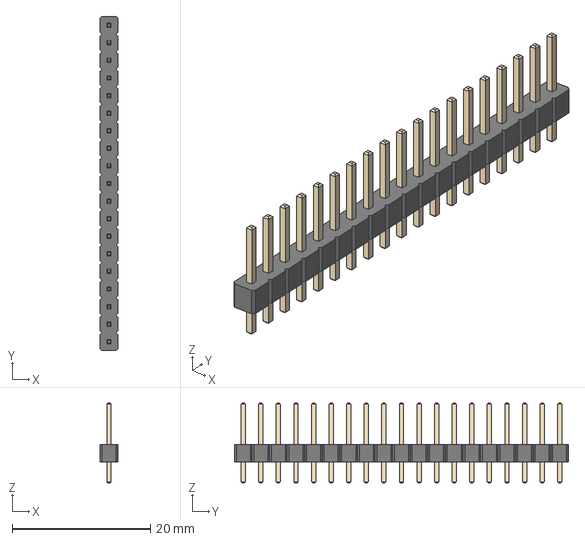
[picture p334: CAD file, 2026-04-15]
hardware-design/examples/05-olimex-devkit-lipo/HARDWARE/ESP32-DevKit-LiPo-Rev.D/3d/HN1x19-PinHeader_1x19_P2.54mm_Vertical.step
2.54 x 48.3 x 11.5 mm
