rompasaurus/regardedPal/hardware-design/freecad-mk2/Dilder_Rev2_Mk2_NoSolar-BasePlate.3mf

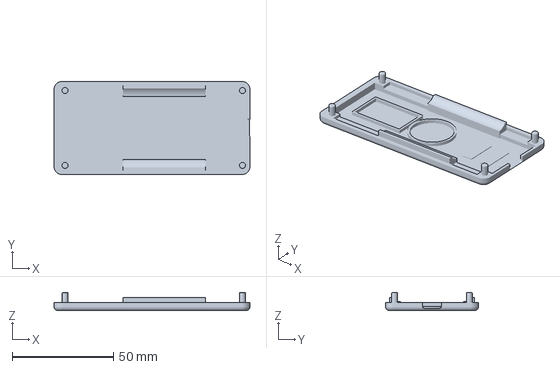
[picture p335: CAD file, 2026-05-02]
hardware-design/freecad-mk2/Dilder_Rev2_Mk2_NoSolar-BasePlate.3mf
96.9 x 46.0 x 9.00 mm
