rompasaurus/regardedPal/hardware-design/freecad-mk2/Dilder_Rev2_Mk2_NoSolar-TopCover.3mf

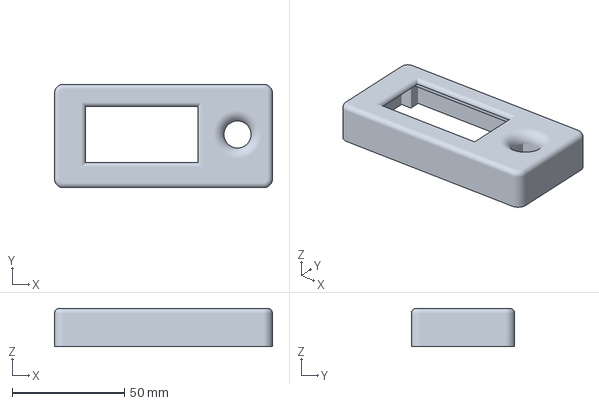
[picture p338: CAD file, 2026-05-02]
hardware-design/freecad-mk2/Dilder_Rev2_Mk2_NoSolar-TopCover.3mf
96.9 x 46.0 x 17.0 mm
