rompasaurus/regardedPal/hardware-design/scad Parts/Rev 2 extended with joystick/04-25-design-alterations/base-plate-v1__shortened_batt_rail_1_mm_height.3mf

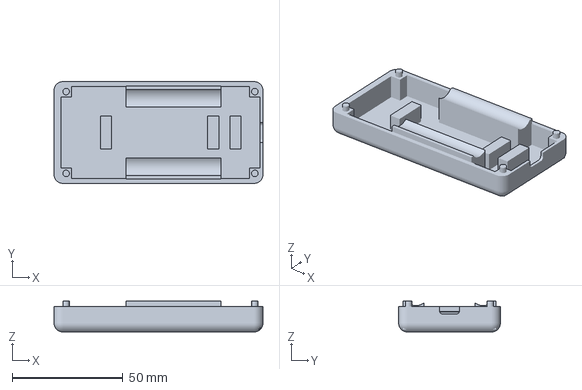
[picture p339: CAD file, 2026-04-25]
hardware-design/scad Parts/Rev 2 extended with joystick/04-25-design-alterations/base-plate-v1__shortened_batt_rail_1_mm_height.3mf
94.5 x 46.0 x 14.0 mm
