rompasaurus/regardedPal/hardware-design/freecad-mk2/Dilder_Rev2_Mk2 2mm longer line base plate rails for wiring 01-05-2026-Thumbpiece.3mf

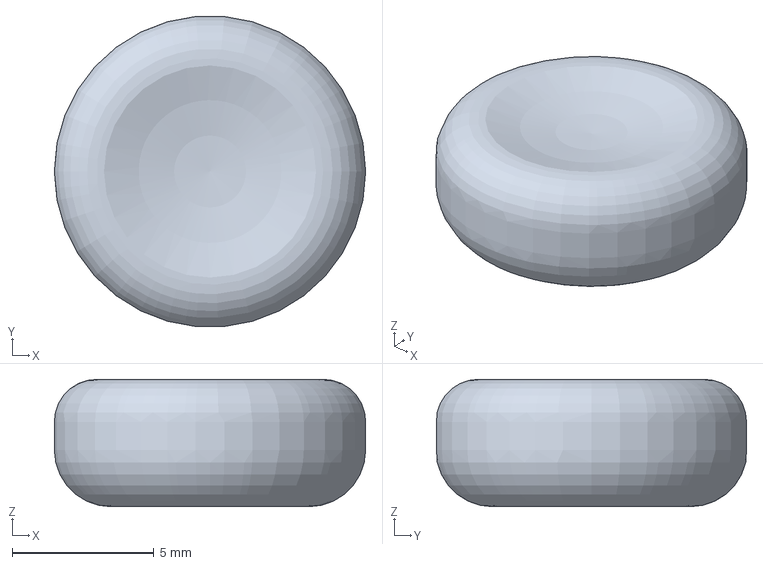
[picture p341: CAD file, 2026-05-01]
hardware-design/freecad-mk2/Dilder_Rev2_Mk2 2mm longer line base plate rails for wiring 01-05-2026-Thumbpiece.3mf
11.0 x 11.0 x 4.50 mm
