rompasaurus/regardedPal/hardware-design/freecad-mk2/Dilder_Rev2_Mk2 2mm longer line base plate rails for wiring 01-05-2026.FCStd

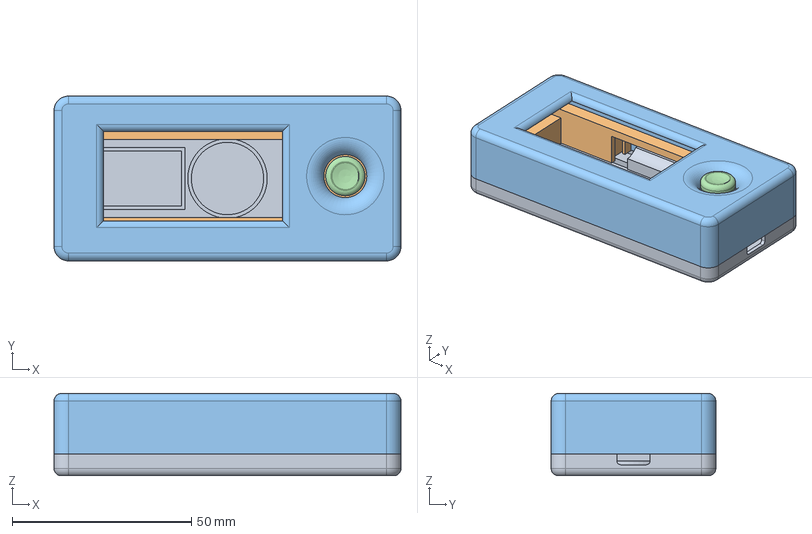
[picture p342: CAD file, 2026-05-01]
hardware-design/freecad-mk2/Dilder_Rev2_Mk2 2mm longer line base plate rails for wiring 01-05-2026.FCStd
96.9 x 46.0 x 23.0 mm
BasePlate
AAACradle
TopCover
Thumbpiece
