rompasaurus/regardedPal/hardware-design/freecad-mk2/Dilder_Rev2_Mk2 2mm longer line base plate rails for wiring 01-05-2026-BasePlate.3mf

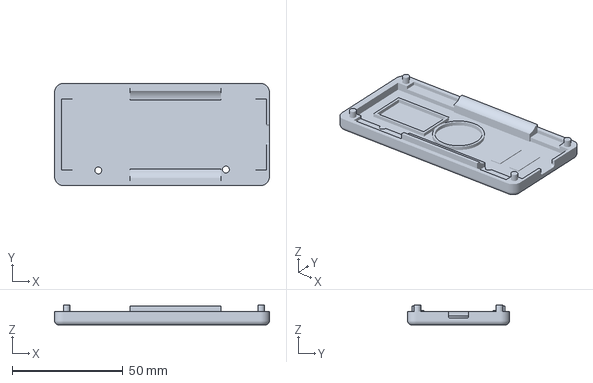
[picture p343: CAD file, 2026-05-01]
hardware-design/freecad-mk2/Dilder_Rev2_Mk2 2mm longer line base plate rails for wiring 01-05-2026-BasePlate.3mf
96.9 x 46.0 x 9.00 mm
