rompasaurus/regardedPal/hardware-design/freecad-mk2/Dilder_Rev2_Mk2.FCStd

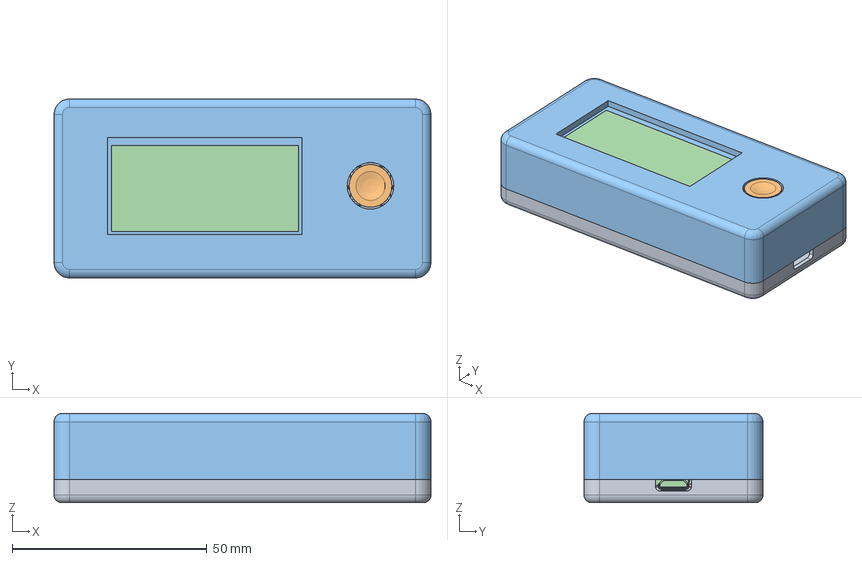
[picture p344: CAD file, 2026-05-01]
hardware-design/freecad-mk2/Dilder_Rev2_Mk2.FCStd
96.9 x 46.0 x 23.0 mm
BasePlate
AAACradle
TopCover
Pico2W_Board
Pico2W_Headers
AAA_Battery_1
AAA_Battery_1_PosTerm
AAA_Battery_2
AAA_Battery_2_PosTerm
TP4056_Module
EInkDisplay_Module
EInkDisplay_Panel
BatteryClips_Positive
BatteryClips_Negative
BatteryWiring_Positive
BatteryWiring_Negative
JoystickPCB
Thumbpiece
Piezo_Brass
Piezo_Ceramic
IMU_Module
Solar_Frame
Solar_Cells
Solar_Wire_Plus
Solar_Wire_Minus
