rompasaurus/regardedPal/hardware-design/freecad-mk2/Dilder_Rev2_Mk2 .4mm extension fixed lip and curved the thumbstickbambuprint.3mf

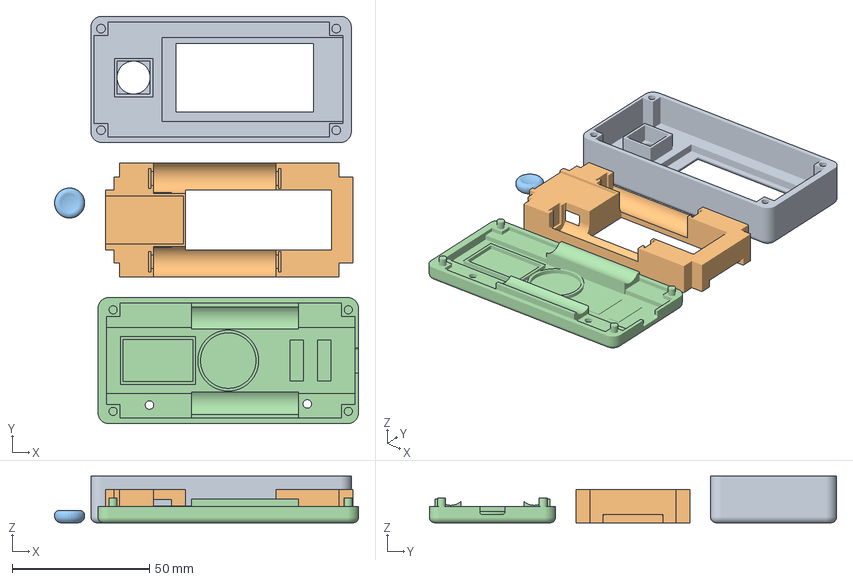
[picture p345: CAD file, 2026-05-01]
hardware-design/freecad-mk2/Dilder_Rev2_Mk2 .4mm extension fixed lip and curved the thumbstickbambuprint.3mf
110.8 x 148.5 x 17.0 mm
