rompasaurus/regardedPal/hardware-design/freecad-mk2/Dilder_Rev2_Mk2 .4mm extension fixed lip and curved the thumbstick-Thumbpiece.3mf

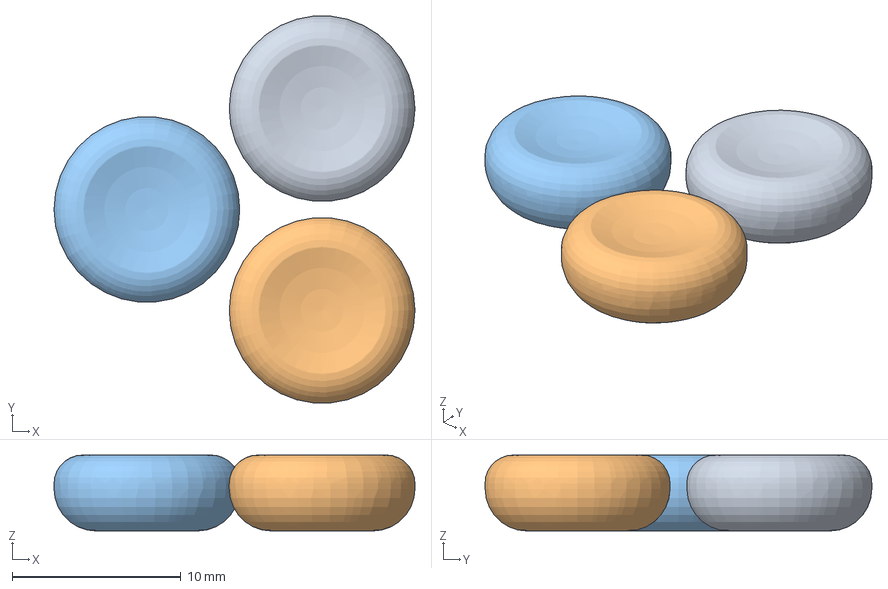
[picture p346: CAD file, 2026-05-01]
hardware-design/freecad-mk2/Dilder_Rev2_Mk2 .4mm extension fixed lip and curved the thumbstick-Thumbpiece.3mf
21.4 x 22.9 x 4.50 mm
