rompasaurus/regardedPal/hardware-design/freecad-mk2/Dilder_Rev2_Mk2 .4mm extension fixed lip and curved the thumbstick.FCStd

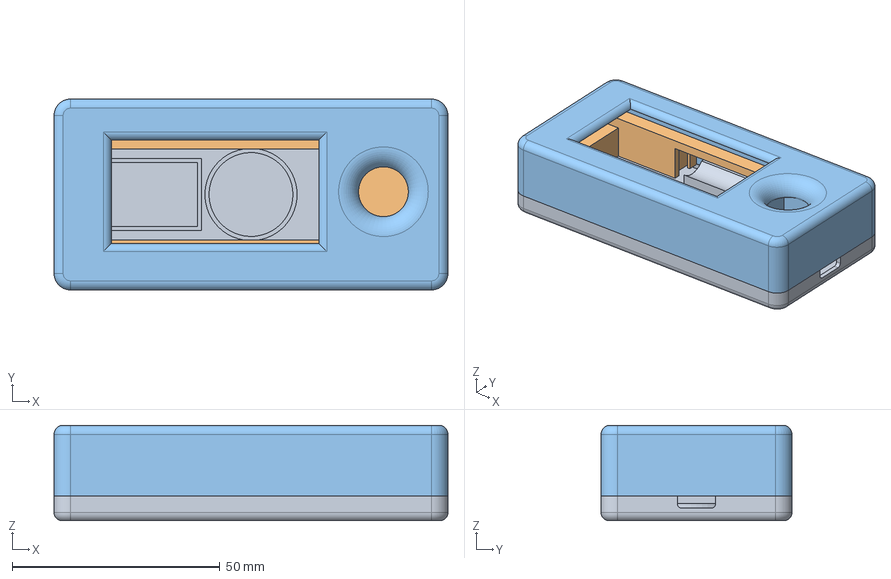
[picture p347: CAD file, 2026-05-01]
hardware-design/freecad-mk2/Dilder_Rev2_Mk2 .4mm extension fixed lip and curved the thumbstick.FCStd
94.9 x 46.0 x 23.0 mm
BasePlate
AAACradle
TopCover
