rompasaurus/regardedPal/hardware-design/examples/06-unexpected-maker-s3/3d models/README.md

# 3D models - Unexpected Maker - ESP32-S3 Boards 
3D STEP models and reference images of my ESP32-S3 boards  

You can find out more about my ESP32-S3 boards at https://esp32s3.com 

Artwork and content in this folder is (c)2022,2023 Unexpected Maker, all rights reserved.

### NanoS3
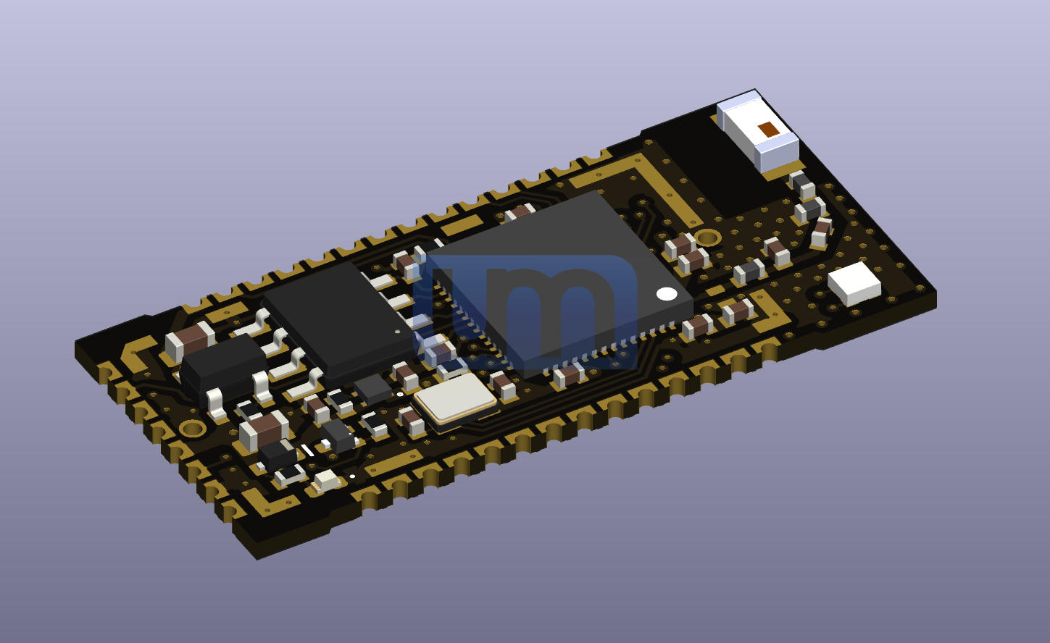
[picture p349: hardware-design/examples/06-unexpected-maker-s3/3d models/NanoS3/NanoS3.jpg]
NanoS3


### TinyS3 & TinyS3 uFL
<div>
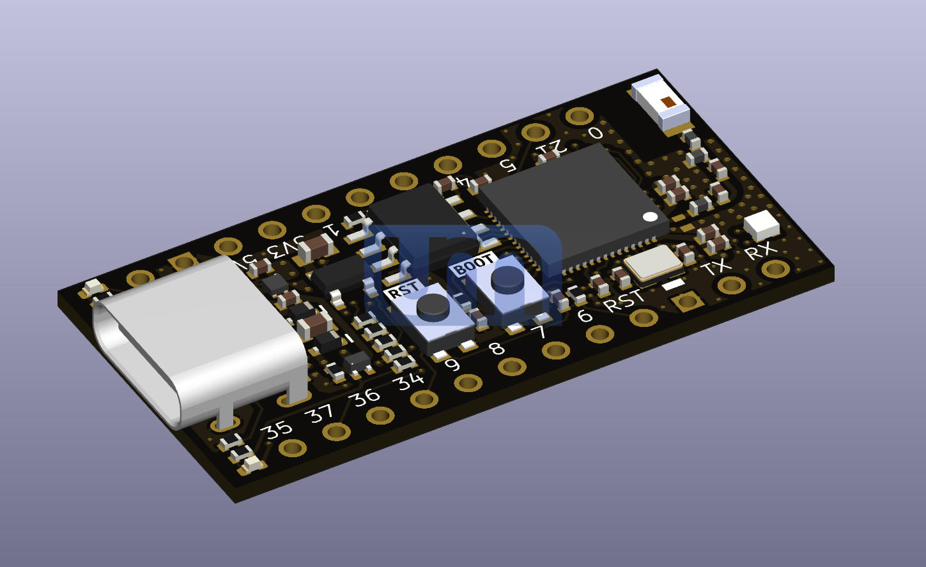
[picture p350: hardware-design/examples/06-unexpected-maker-s3/3d models/TinyS3/TinyS3.jpg]
TinyS3
    
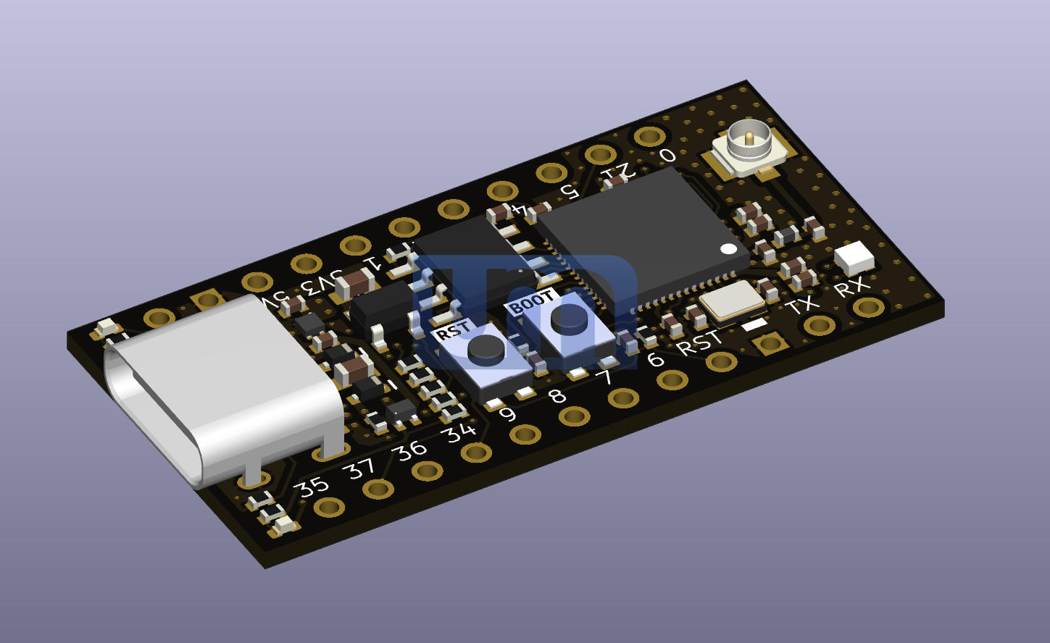
[picture p351: hardware-design/examples/06-unexpected-maker-s3/3d models/TinyS3/TinyS3_uFL.jpg]
TinyS3 uFL
    
</div>

### ProS3 & ProS3 uFL
<div>
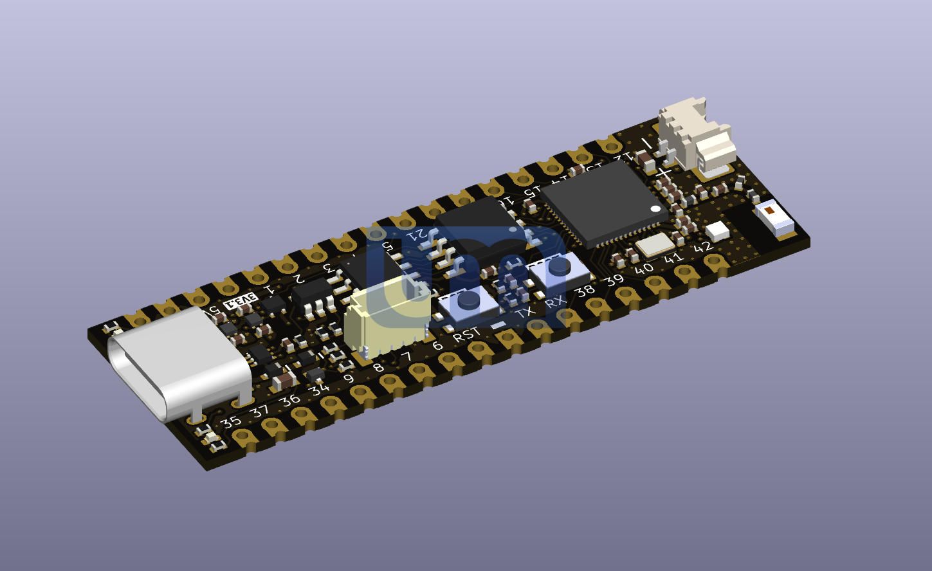
[picture p352: hardware-design/examples/06-unexpected-maker-s3/3d models/ProS3/ProS3.jpg]
ProS3
    
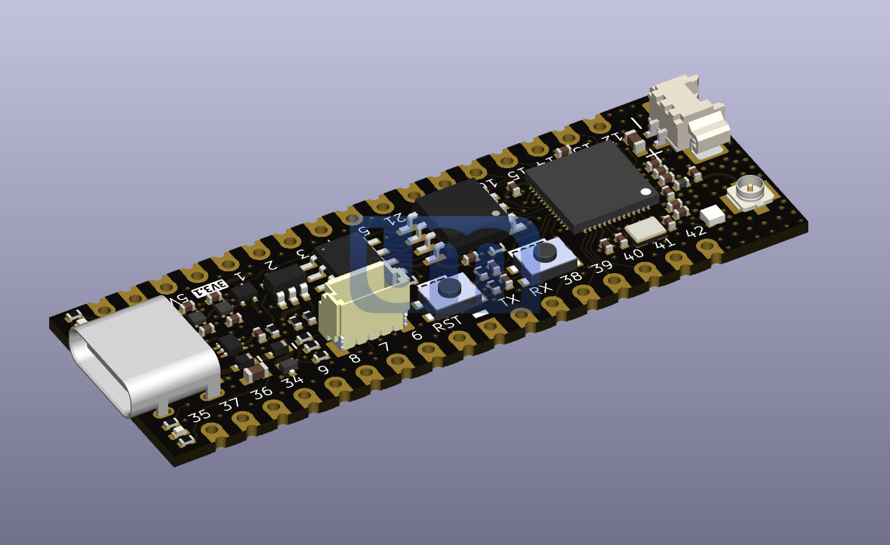
[picture p353: hardware-design/examples/06-unexpected-maker-s3/3d models/ProS3/ProS3_uFL.jpg]
ProS3 uFL
    
</div>

### FeatherS3 & FeatherS3 uFL
<div>
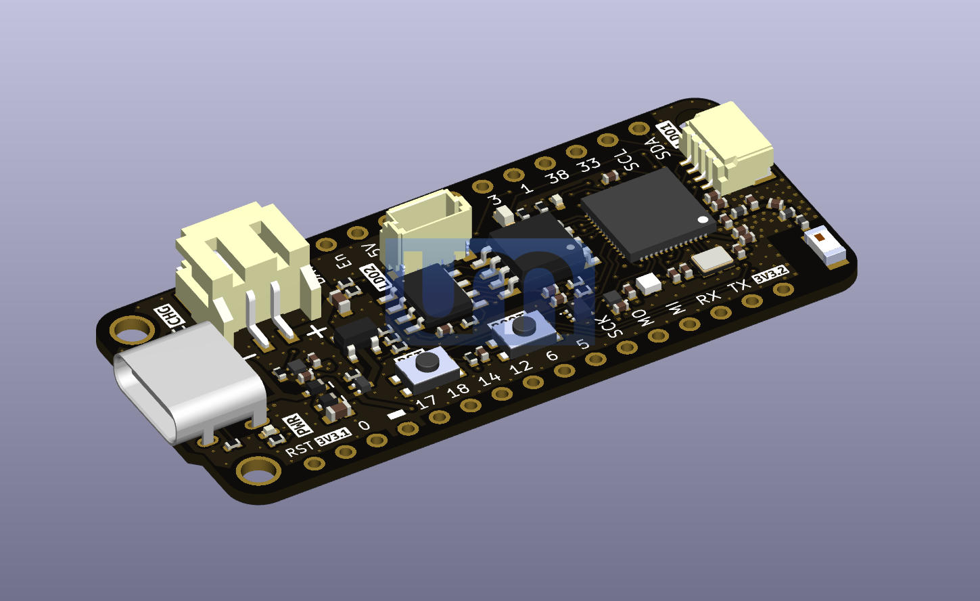
[picture p354: hardware-design/examples/06-unexpected-maker-s3/3d models/FeatherS3/FeatherS3.jpg]
FeatherS3
    
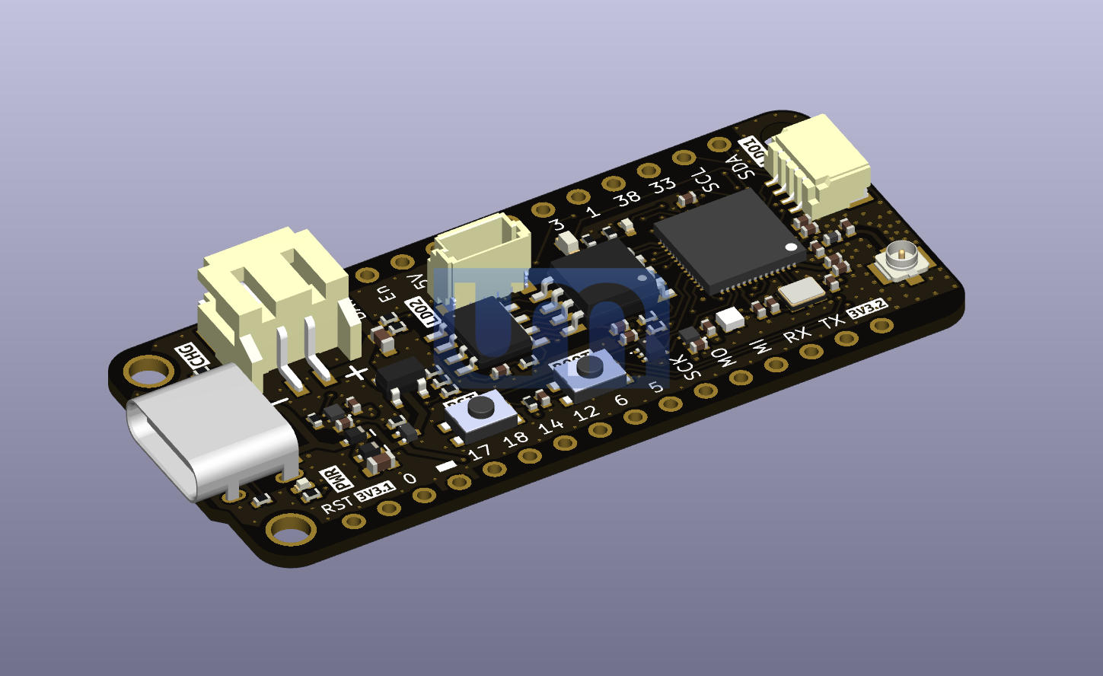
[picture p355: hardware-design/examples/06-unexpected-maker-s3/3d models/FeatherS3/FeatherS3_uFL.jpg]
FeatherS3 uFL
    
</div>

### NanoS3 Carrier
<div>
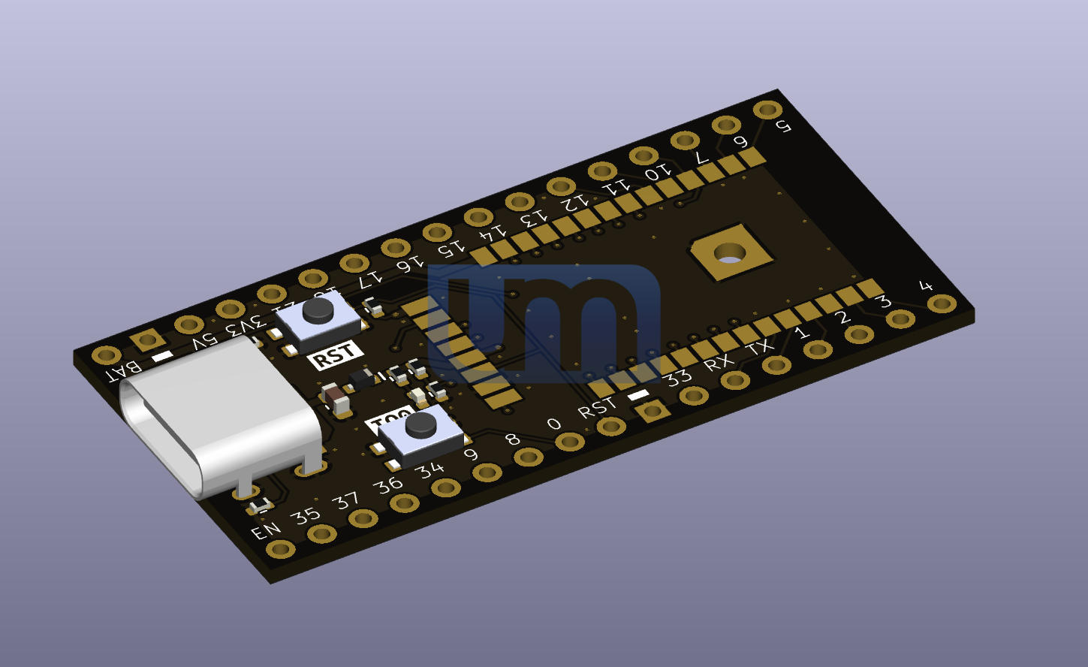
[picture p356: hardware-design/examples/06-unexpected-maker-s3/3d models/NanoS3_Carrier/NanoS3_Carrier_Empty.jpg]
NanoS3 Carrier Empty
    
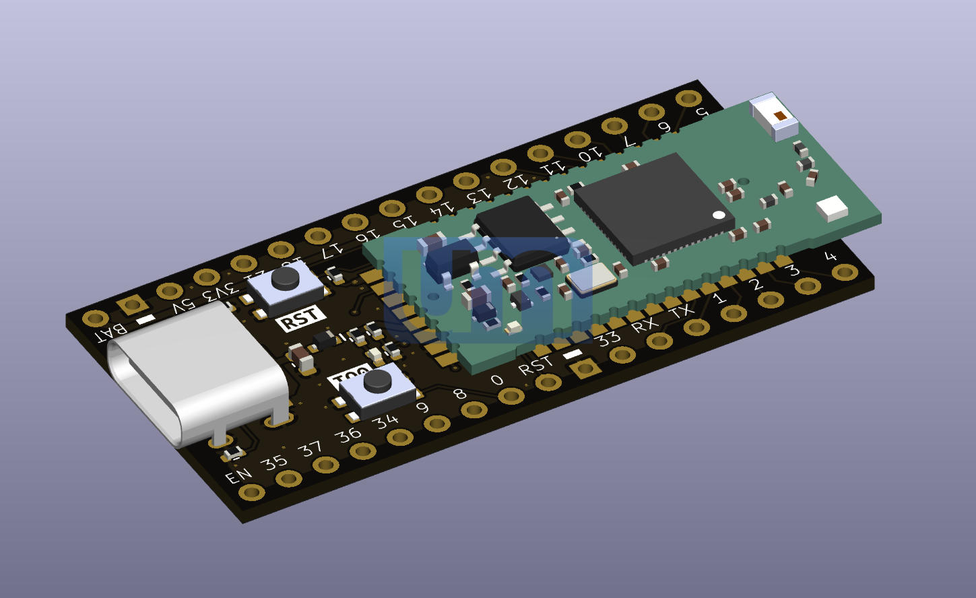
[picture p357: hardware-design/examples/06-unexpected-maker-s3/3d models/NanoS3_Carrier/NanoS3_Carrier_with_NanoS3.jpg]
NanoS3 Carrier with NanoS3
    
</div>
