rompasaurus/regardedPal/hardware-design/examples/06-unexpected-maker-s3/kicad/README.md

# KiCAD Footprints - Unexpected Maker - ESP32-S3 Boards 
KiCAD Footprints for my ESP32-S3 boards  

You can find out more about my ESP32-S3 boards at https://esp32s3.com 

Please refer to the included license.
