rompasaurus/regardedPal/hardware-design/examples/06-unexpected-maker-s3/series_d/README.md

# Unexpected Maker - Series[D]



Assorted files for my new ESP32-S3 Series[D] development boards 









You can find out more about my ESP32-S3 boards at https://esp32s3.com

# Contents
In this repo you'll find the following items:

## 3D Models
3D STEP files for each of the TinyS3[D], ProS3[D], FeatherS3[D] and EdgeS3[D] boards

You'll also find a STEP file for the EdgeS3[D] Reference Carrier board and a STEP for the M.2 connector footprint with the EdgeS3[D] inserted to help line things up.

## Schematics
PDF Schematics for each of the TinyS3[D], ProS3[D], FeatherS3[D] and EdgeS3[D] boards.

## KiCAD (v9)
Symbol and Footprint for EdgeS3[D] and a project folder for the EdgeS3[D] Reference Carrier PCB.

## Pin Reference Cards
Hires pinout reference cards for each of the TinyS3[D], ProS3[D], FeatherS3[D] and EdgeS3[D] boards

# Support Unexpected Maker
I love designing, making, and releasing projects and products that empower others to learn and build amazing things! I do it because I believe it’s important to share knowledge and give back to the community as many have done before me. It helps us all learn and grow.

Please consider supporting me by buying some of my products from:

https://unexpectedmaker.com/shop

Or by buying one of my products on tindie or Lectronz:

https://www.tindie.com/stores/seonr/
https://lectronz.com/stores/unexpectedmaker

Or by becoming a Patron:

https://www.patreon.com/unexpectedmaker

## Unexpected Maker
http://youtube.com/c/unexpectedmaker

http://twitter.com/unexpectedmaker

https://discord.gg/xAHpApP

https://www.facebook.com/unexpectedmaker/
