rompasaurus/regardedPal/hardware-design/examples/06-unexpected-maker-s3/code/arduino/README.md

# Unexpected Maker ESP32-S3 Arduino Helper Library

This is the [helper library](https://github.com/UnexpectedMaker/esp32s3-arduino-helper) for all the Unexpected Maker [ESP32-S3 boards](https://esp32s3.com).

Examples can be found in the [examples directory](https://github.com/UnexpectedMaker/esp32s3-arduino-helper/tree/main/examples), these can also be loaded from the examples menu in the Arduino IDE.

## Installation

Please download the library called `UMS3 Helper` via the Arduino Library Manager.

## List of functions

```c++

// Initializes all UM board peripherals
void begin();

// Set LDO2 on or off (ProS3 and FeatherS3 only)
void setLDO2Power(bool on);

// Set neopixel power on or off (On ProS3 and Feather it sets LDO2 on)
void setPixelPower(bool on);

// Set neopixel color
void setPixelColor(uint8_t r, uint8_t g, uint8_t b);
void setPixelColor(uint32_t rgb);

// Set neopixel brightness
void setPixelBrightness(uint8_t brightness);

// Pack r,g,b (0-255) into a 32bit rgb color
static uint32_t color(uint8_t r, uint8_t g, uint8_t b);

// Convert a color wheel angle (0-255) to a 32bit rgb color
static uint32_t colorWheel(uint8_t pos);

// Set the blue LED on or off (FeatherS3 only)
void setBlueLED(bool on);

// Toggle the blue LED (FeatherS3 only)
void toggleBlueLED();

// Get the battery voltage in volts
float getBatteryVoltage();

// Get the light sensor in volts (0-3.3)
float getLightSensorVoltage();

// Detect if VBUS (USB power) is present
bool getVbusPresent();
```
