rompasaurus/regardedPal/testing/guides/setup_cli_guide.md

# Setup CLI User Guide

> Auto-generated from 19 test screenshots.
> Re-run the test suite to update: `pytest setup_cli/ -m screenshot`

---

## Cli

### Setup Cli Help Rendered

The setup.py help output showing all available flags and usage examples.

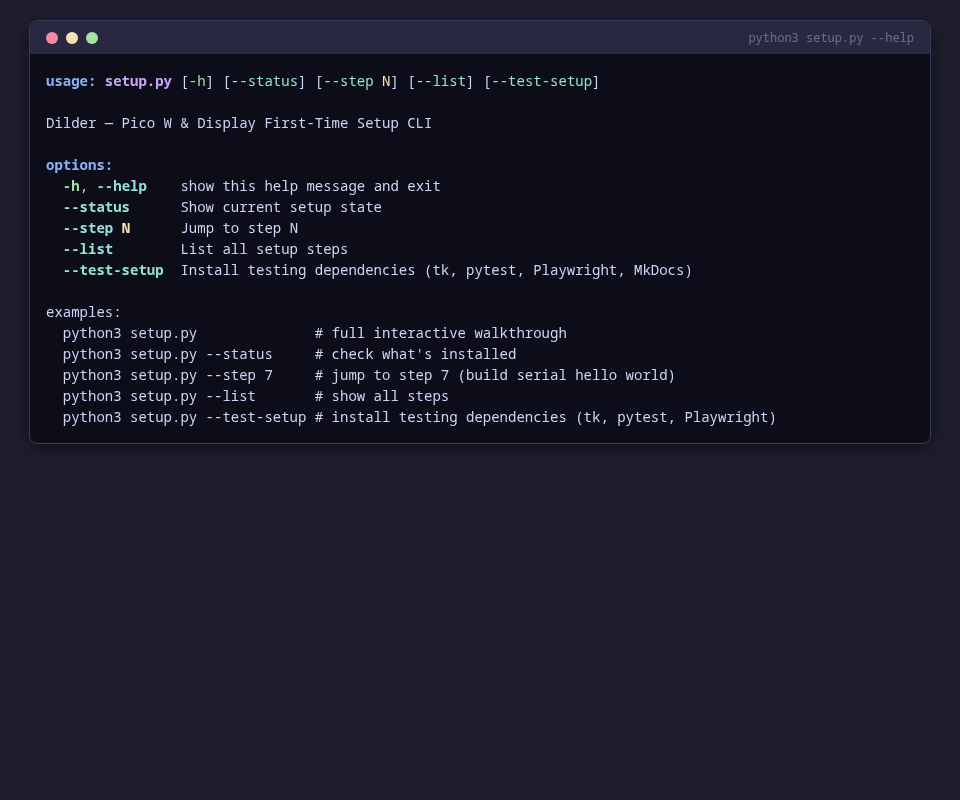
[picture p371: testing/setup_cli/screenshots/setup_cli_help_rendered.png]
setup_cli_help_rendered


### Setup Cli List Rendered

The step list output showing all 15 setup steps with their status.

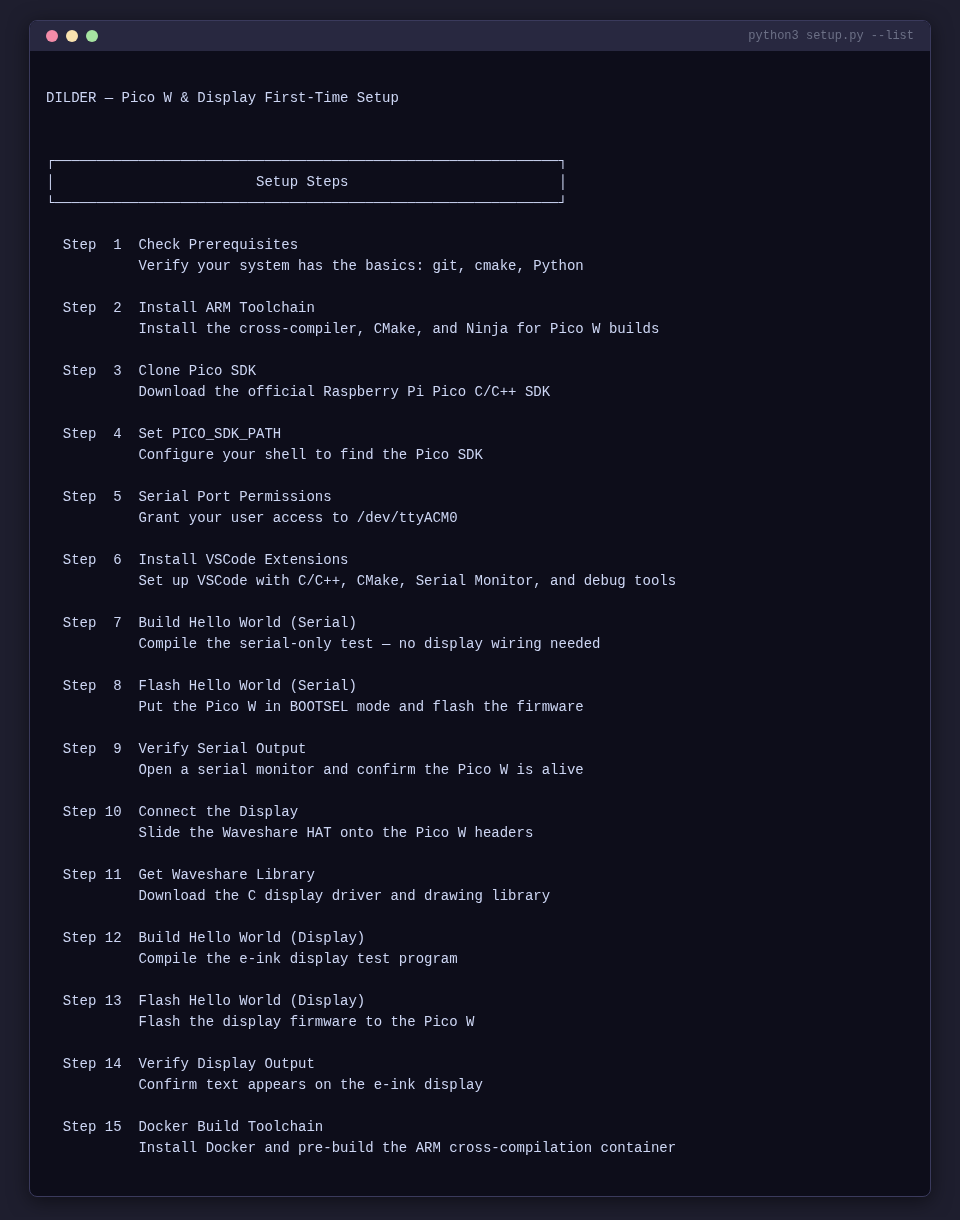
[picture p372: testing/setup_cli/screenshots/setup_cli_list_rendered.png]
setup_cli_list_rendered


### Setup Cli Status Rendered

The environment status output showing installed tools, SDK paths, Docker, and testing framework.

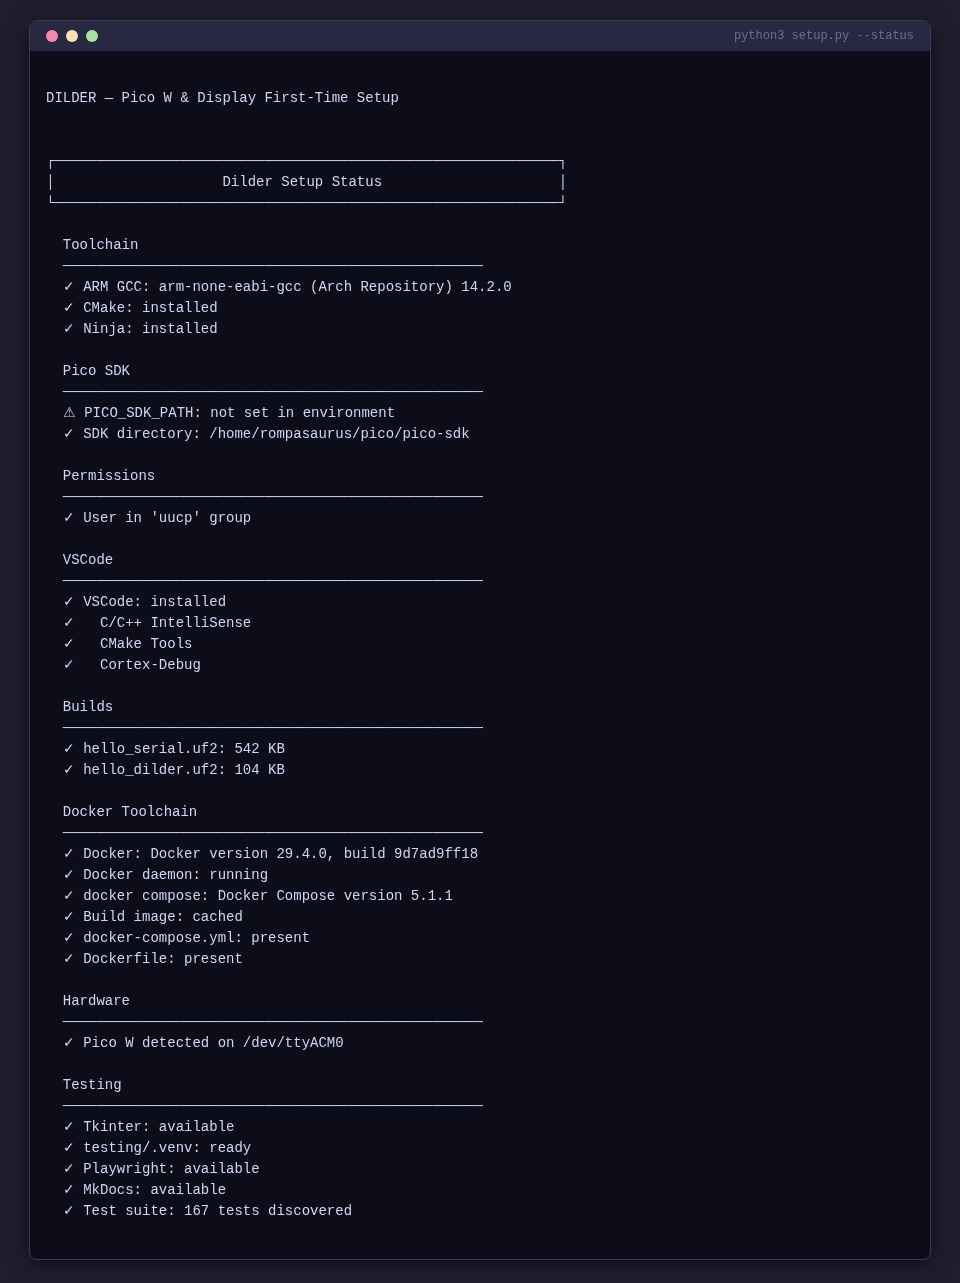
[picture p373: testing/setup_cli/screenshots/setup_cli_status_rendered.png]
setup_cli_status_rendered


### Setup Cli Step 01

Step 1 — Check Prerequisites: verifies git, cmake, Python, Tkinter, and pyserial are installed.

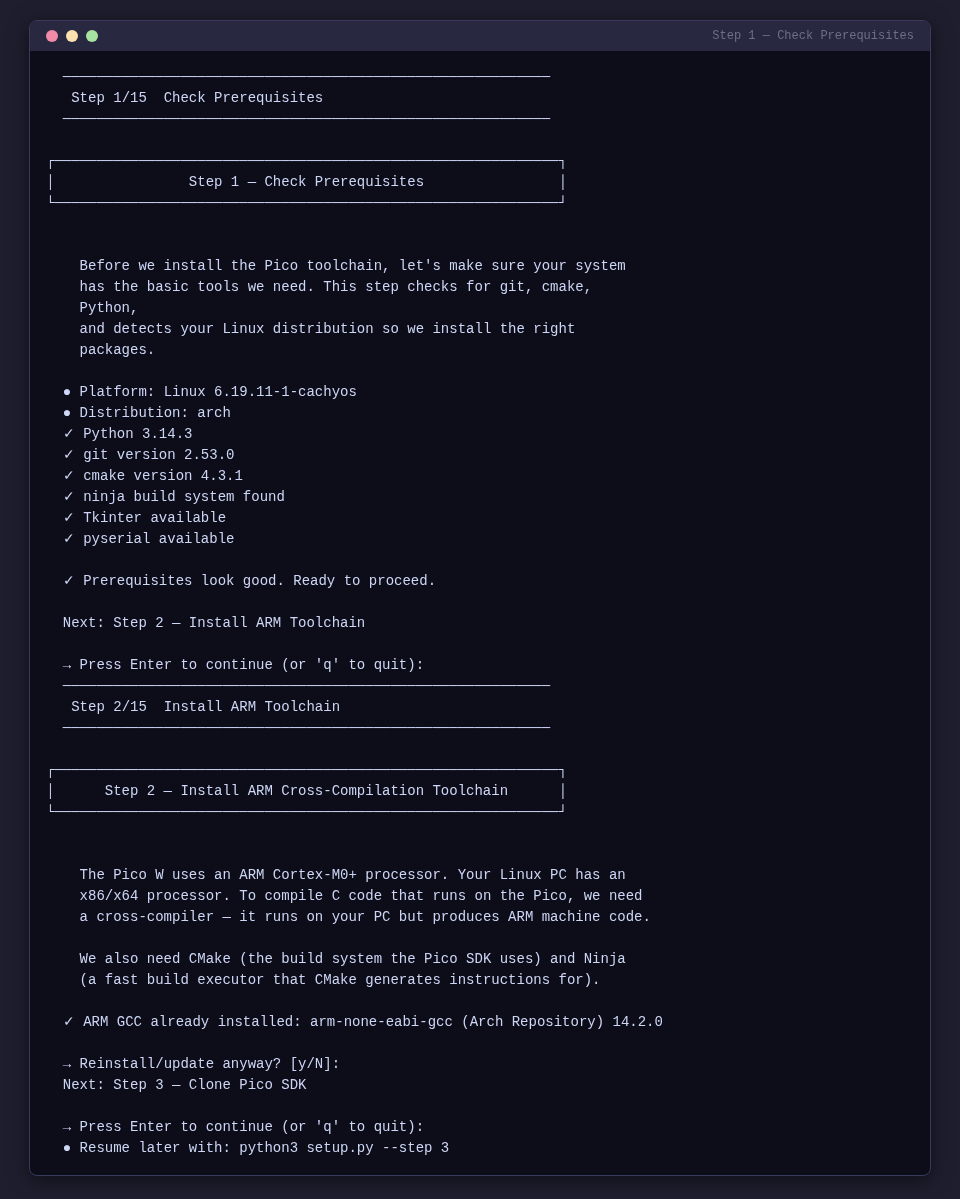
[picture p374: testing/setup_cli/screenshots/setup_cli_step_01.png]
setup_cli_step_01


### Setup Cli Step 02

Step 2 — Install ARM Toolchain: installs arm-none-eabi-gcc, cmake, and ninja via the distro package manager.

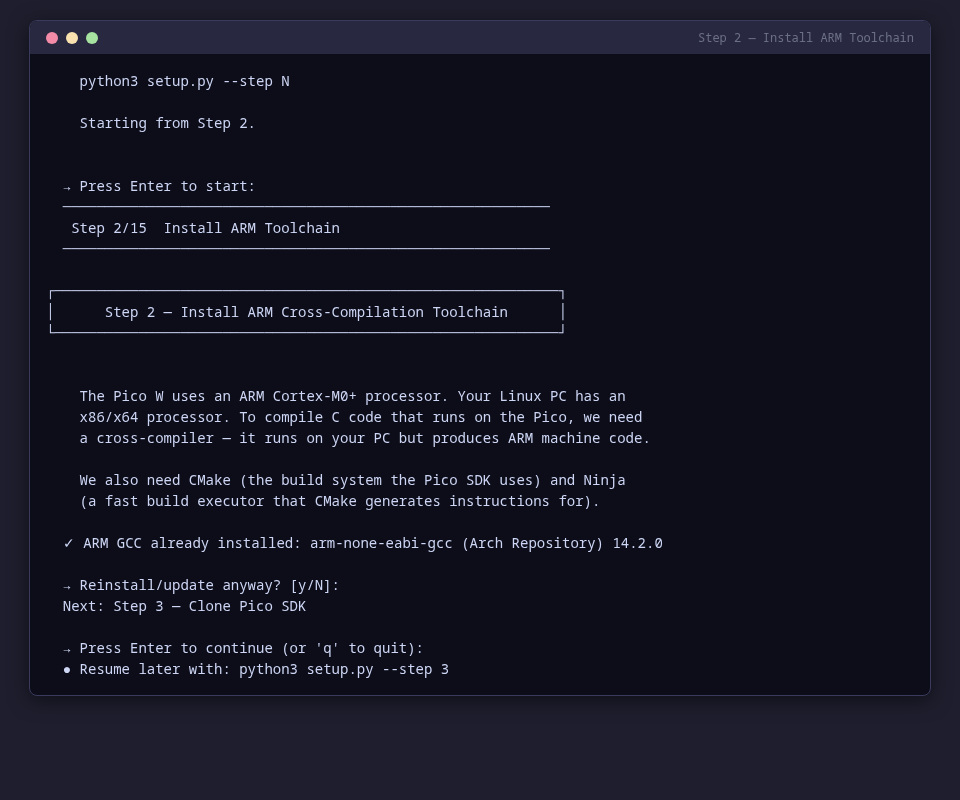
[picture p375: testing/setup_cli/screenshots/setup_cli_step_02.png]
setup_cli_step_02


### Setup Cli Step 03

Step 3 — Clone Pico SDK: downloads the official pico-sdk with all submodules.

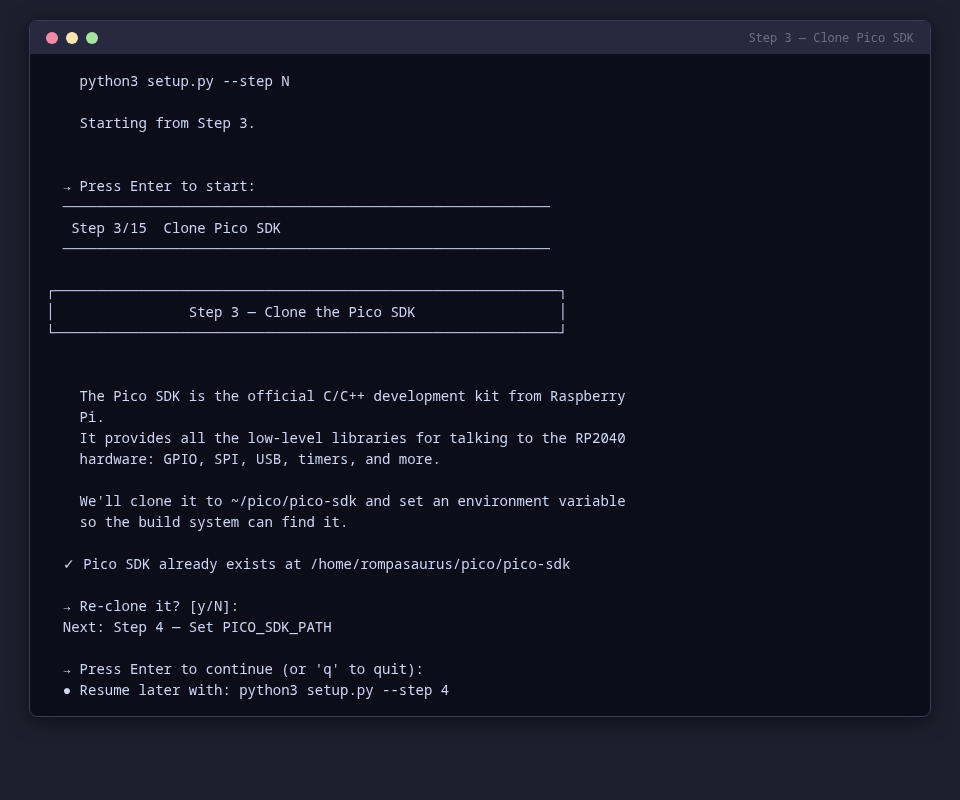
[picture p376: testing/setup_cli/screenshots/setup_cli_step_03.png]
setup_cli_step_03


### Setup Cli Step 04

Step 4 — Set PICO_SDK_PATH: appends the SDK path export to your shell rc file.

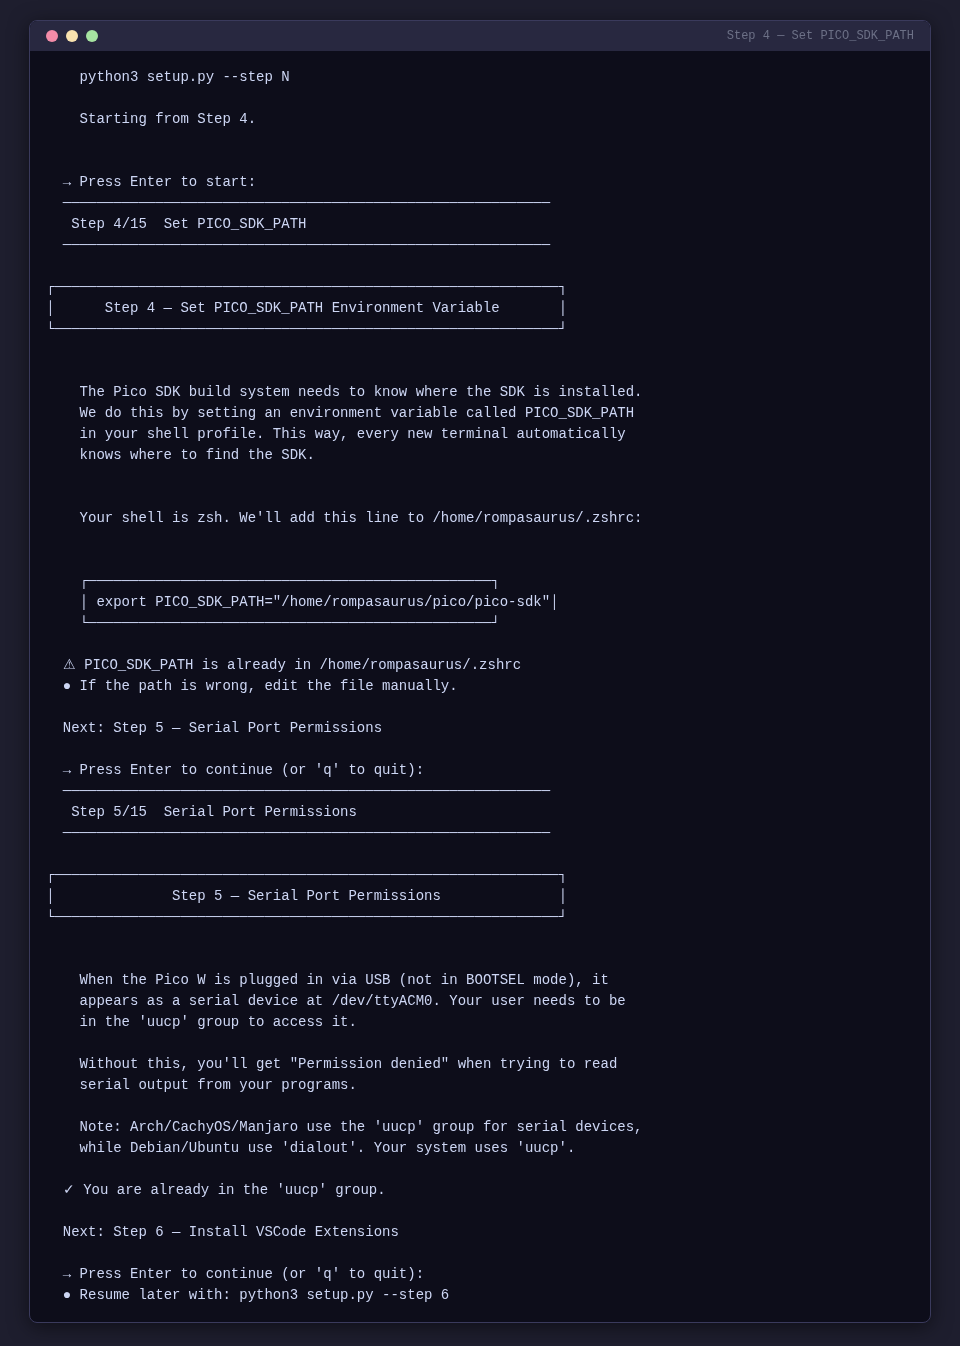
[picture p377: testing/setup_cli/screenshots/setup_cli_step_04.png]
setup_cli_step_04


### Setup Cli Step 05

Step 5 — Serial Port Permissions: adds user to the uucp/dialout serial group.

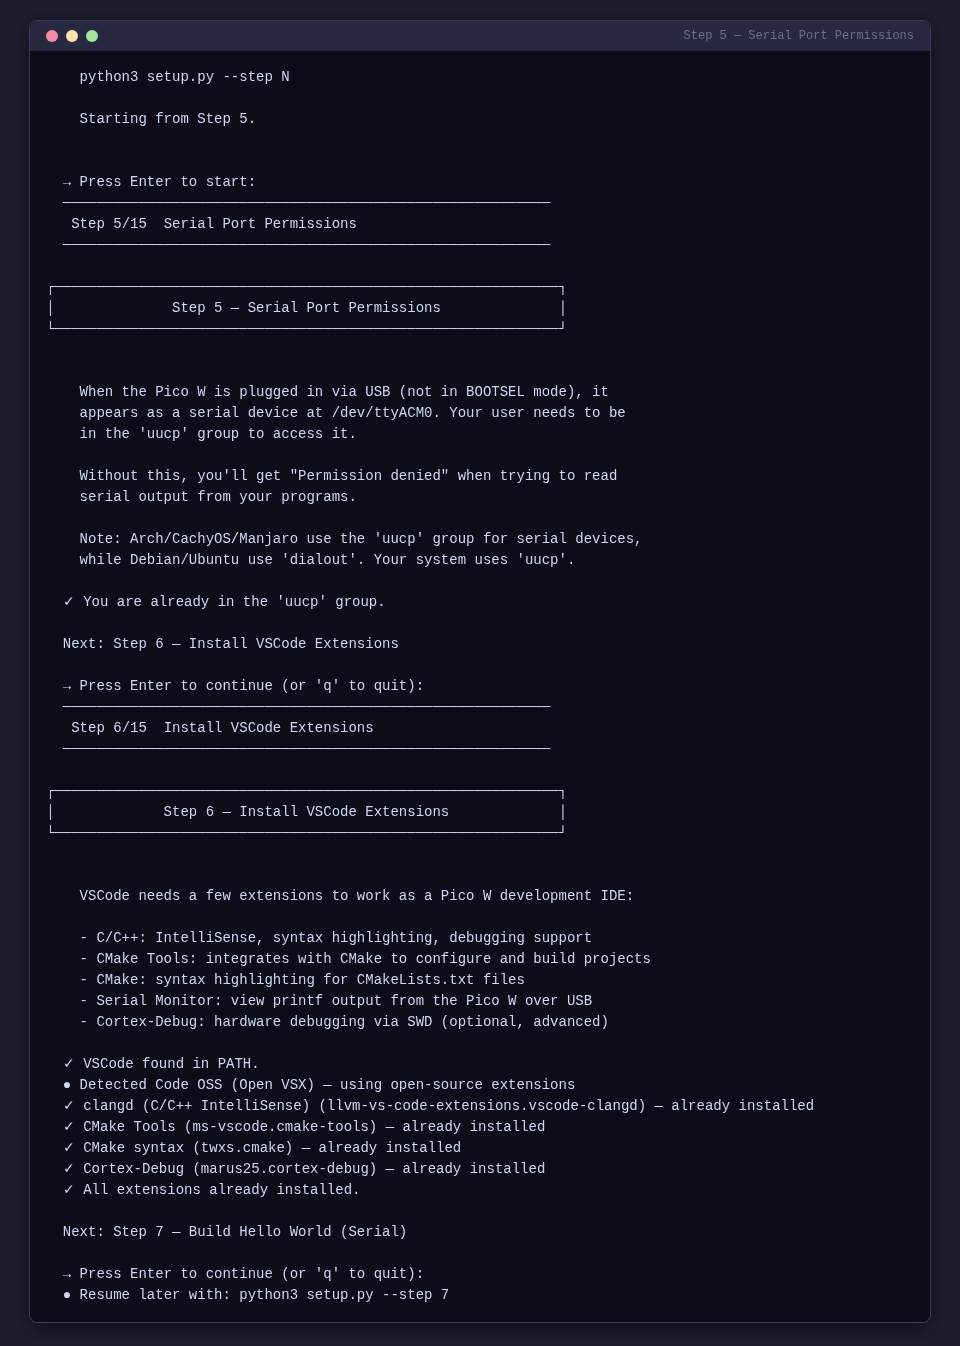
[picture p378: testing/setup_cli/screenshots/setup_cli_step_05.png]
setup_cli_step_05


### Setup Cli Step 06

Step 6 — Install VSCode Extensions: installs C/C++, CMake Tools, and Cortex-Debug extensions.

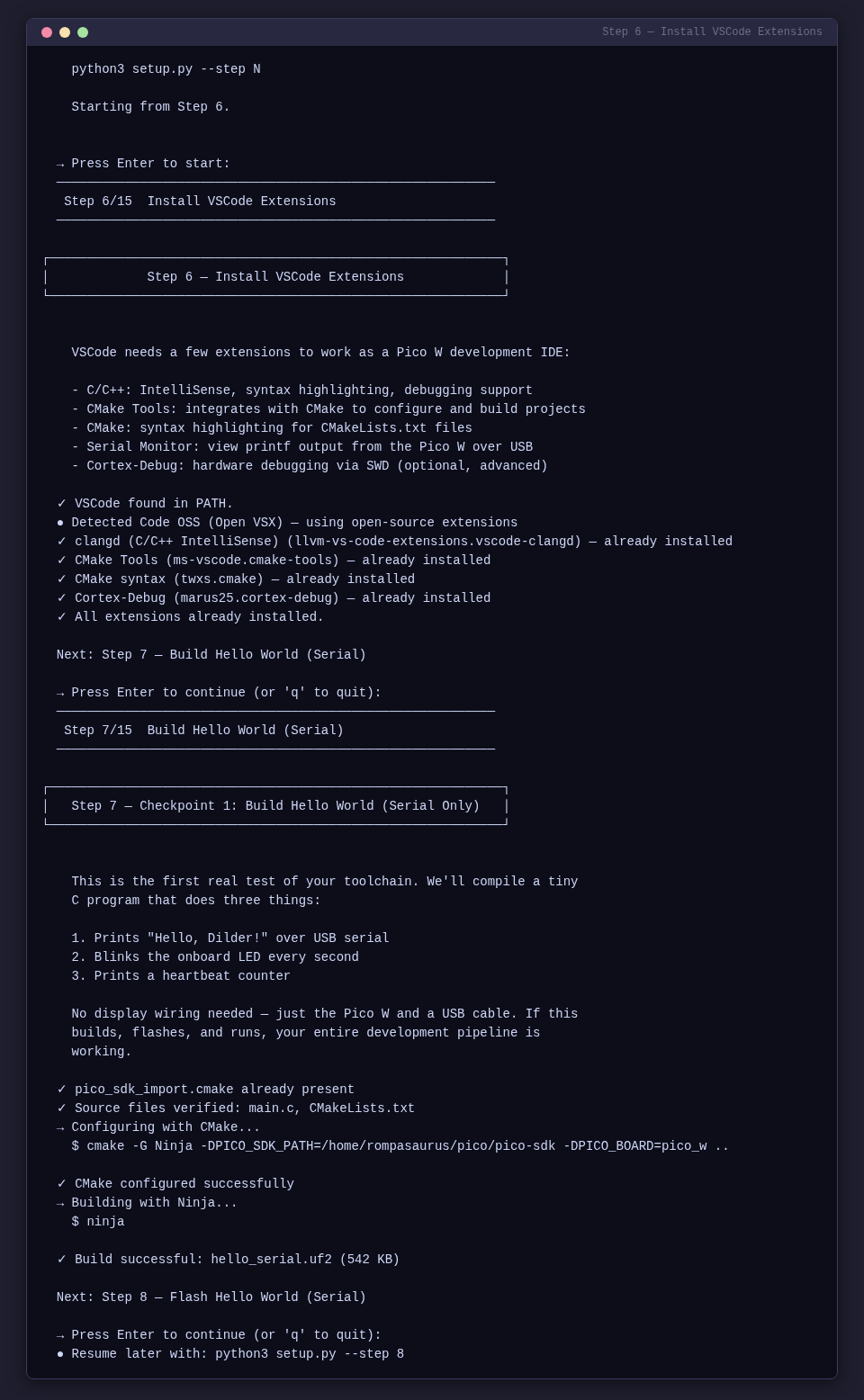
[picture p379: testing/setup_cli/screenshots/setup_cli_step_06.png]
setup_cli_step_06


### Setup Cli Step 07

Step 7 — Build Hello World (Serial): CMake configure and Ninja build for the serial test firmware.

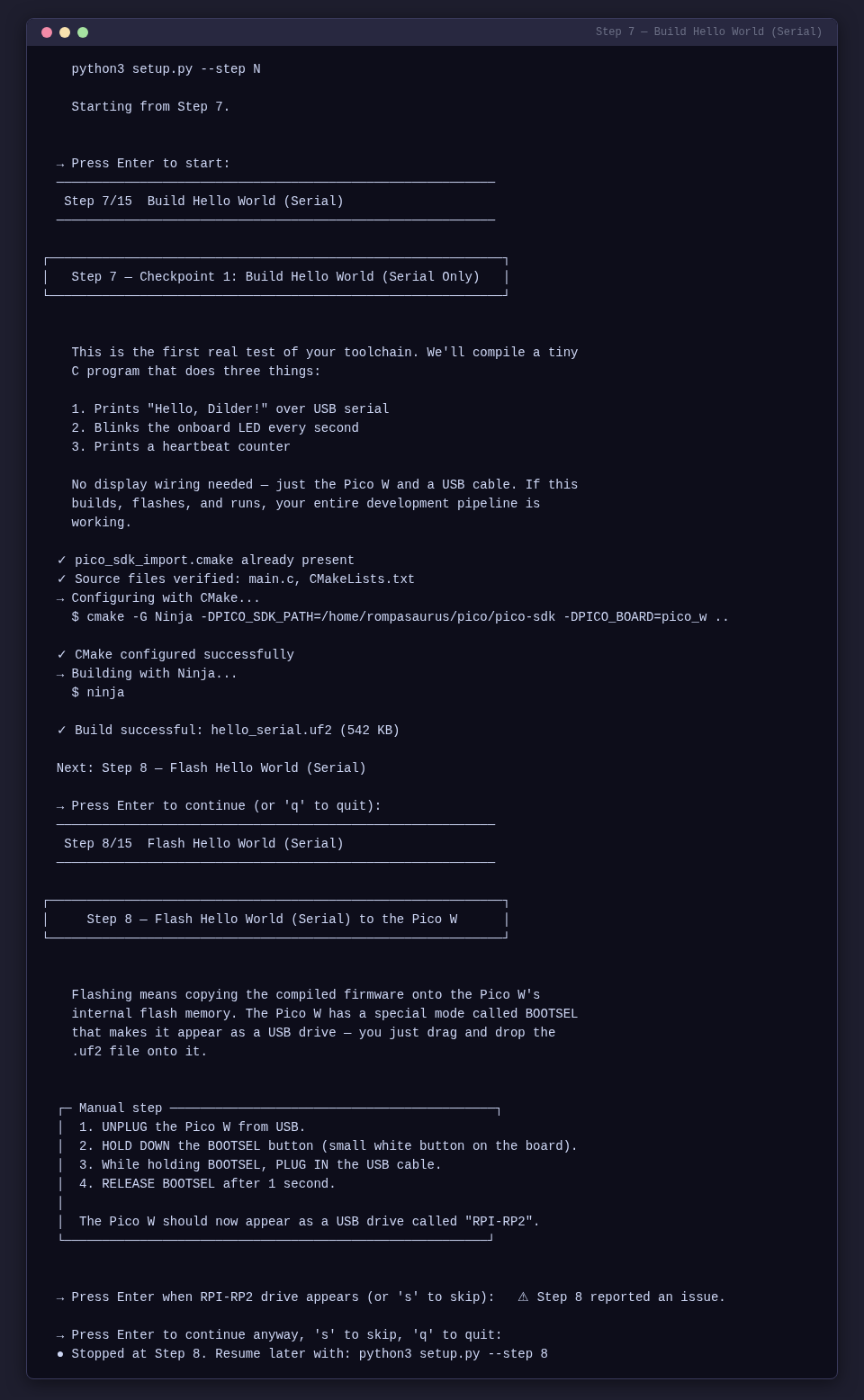
[picture p380: testing/setup_cli/screenshots/setup_cli_step_07.png]
setup_cli_step_07


### Setup Cli Step 08

Step 8 — Flash Hello World (Serial): BOOTSEL detection and UF2 firmware flash.

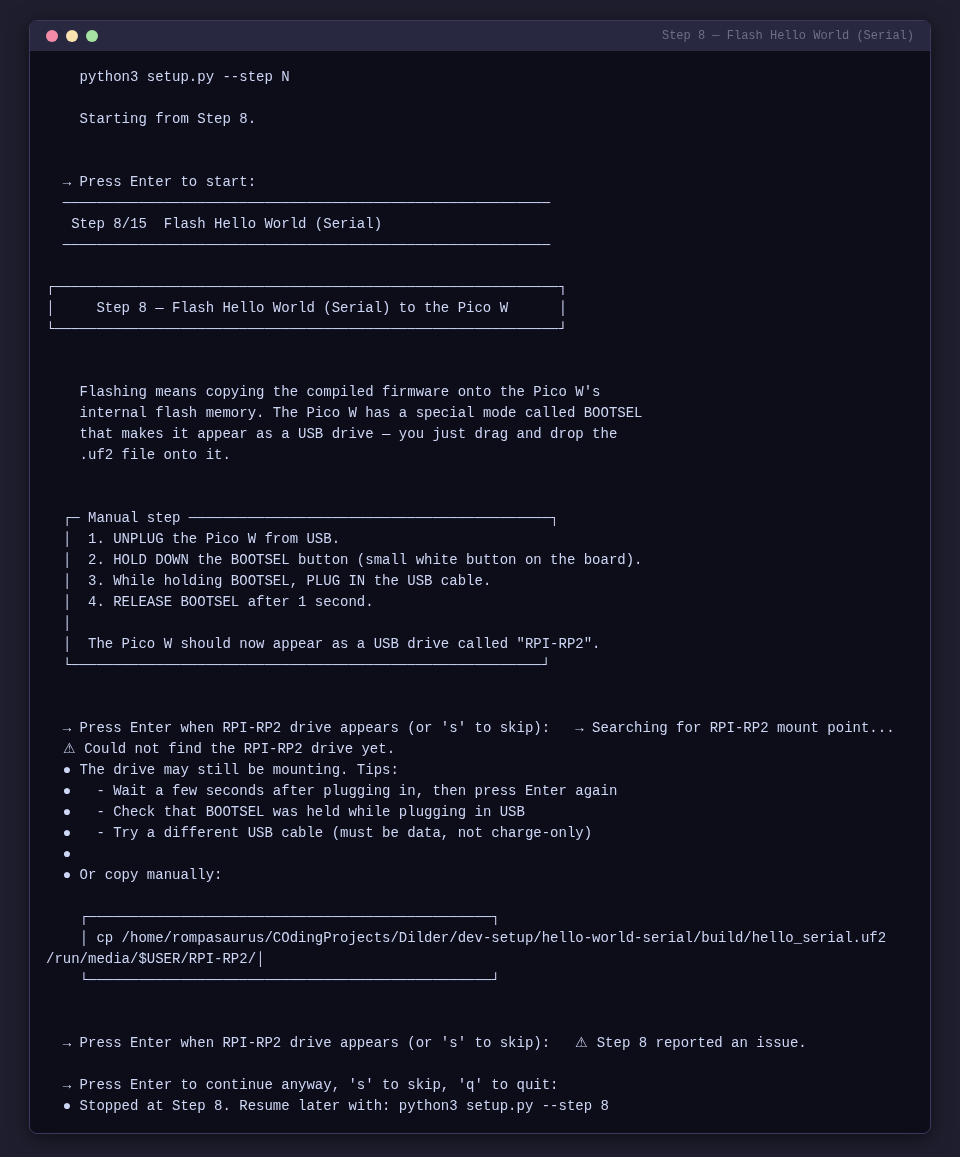
[picture p381: testing/setup_cli/screenshots/setup_cli_step_08.png]
setup_cli_step_08


### Setup Cli Step 09

Step 9 — Verify Serial Output: confirms the Pico W is alive via serial monitor.

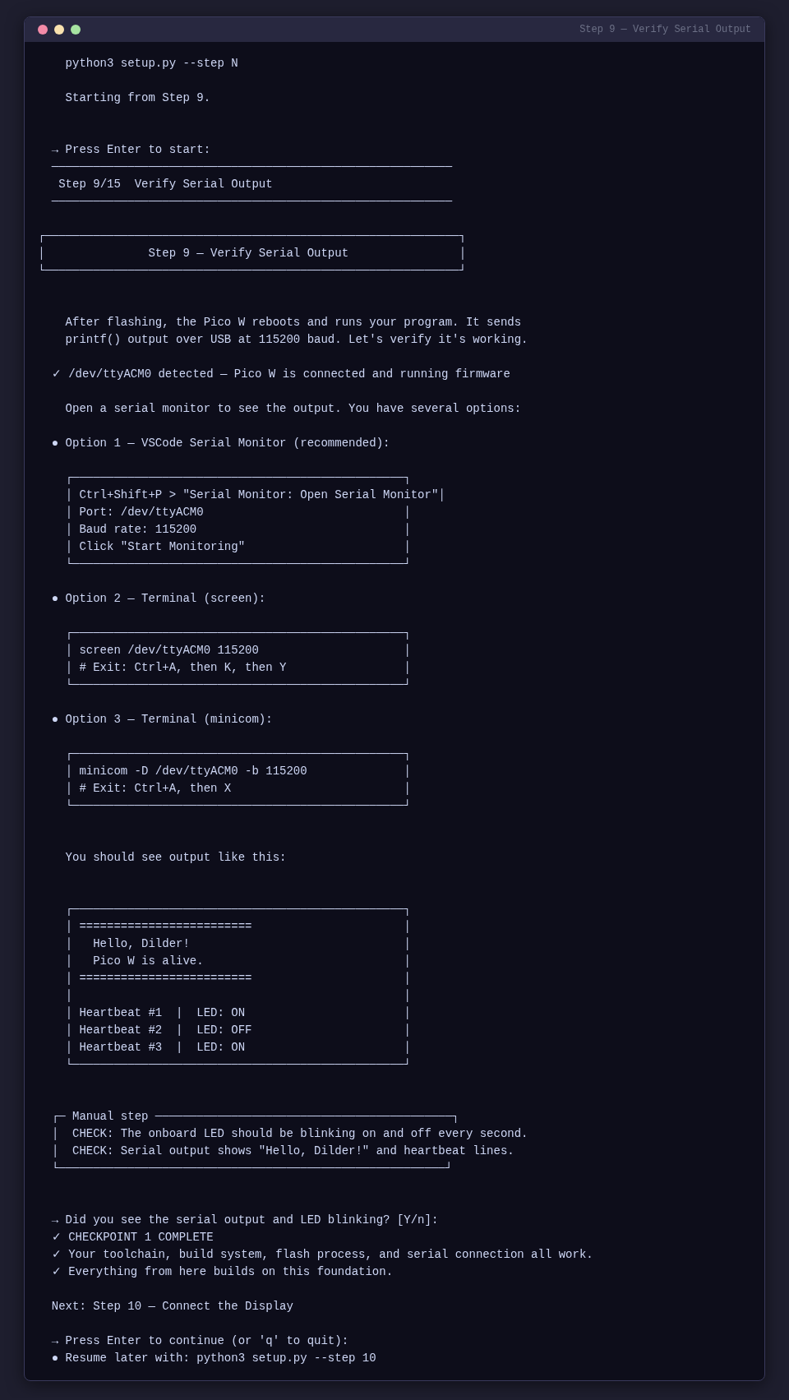
[picture p382: testing/setup_cli/screenshots/setup_cli_step_09.png]
setup_cli_step_09


### Setup Cli Step 10

Step 10 — Connect the Display: step-by-step HAT attachment instructions with ASCII diagrams.

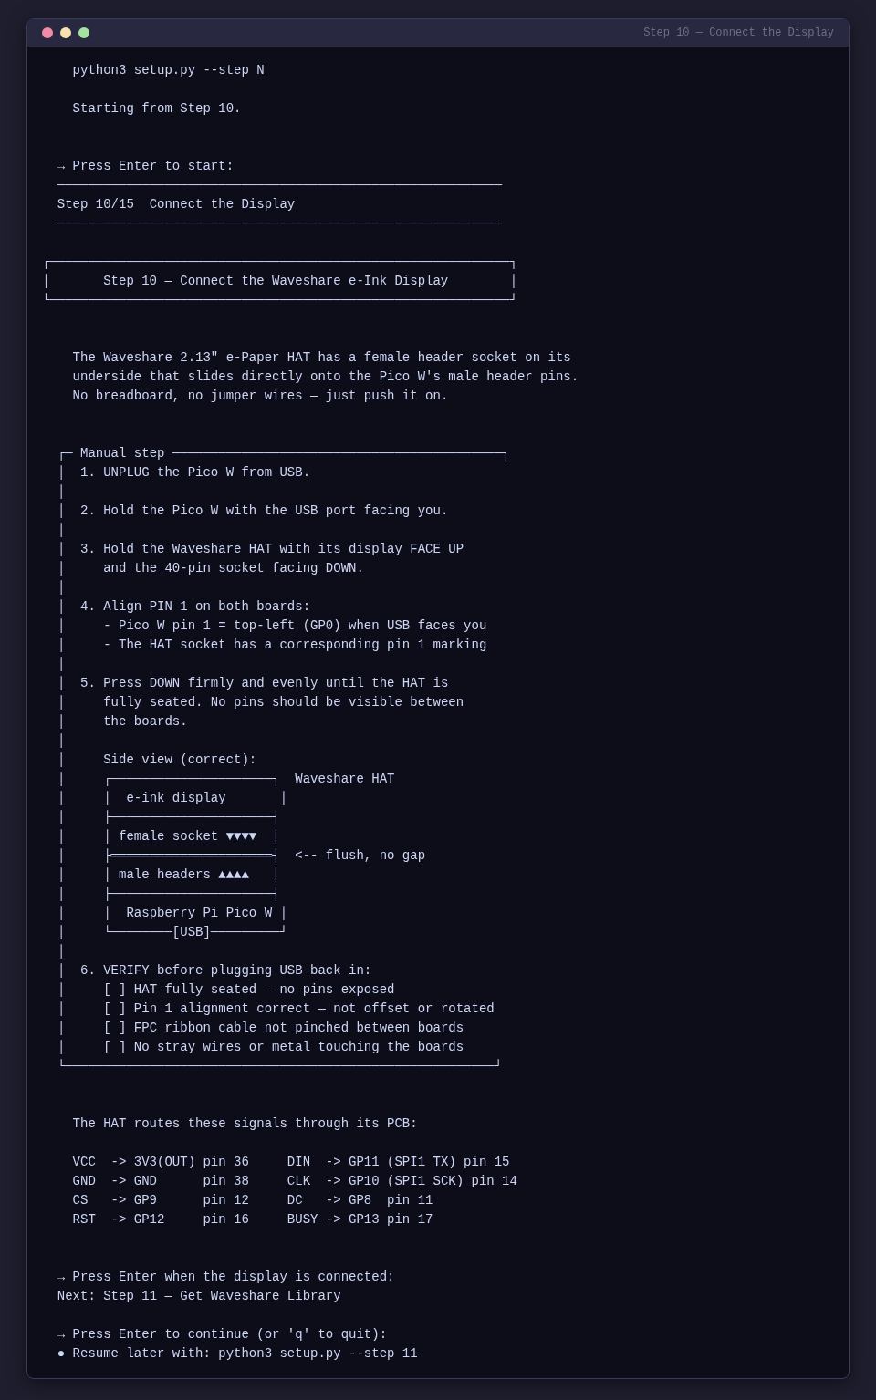
[picture p383: testing/setup_cli/screenshots/setup_cli_step_10.png]
setup_cli_step_10


### Setup Cli Step 11

Step 11 — Get Waveshare Library: downloads the C display driver and font files.

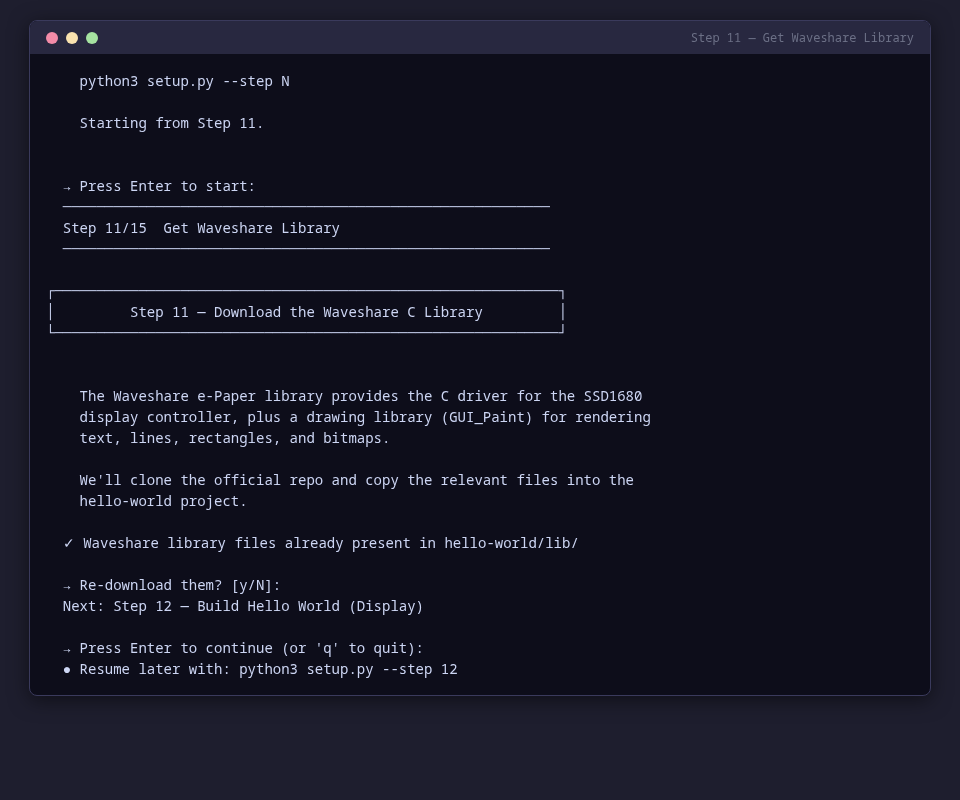
[picture p384: testing/setup_cli/screenshots/setup_cli_step_11.png]
setup_cli_step_11


### Setup Cli Step 12

Step 12 — Build Hello World (Display): CMake + Ninja build for the display firmware.

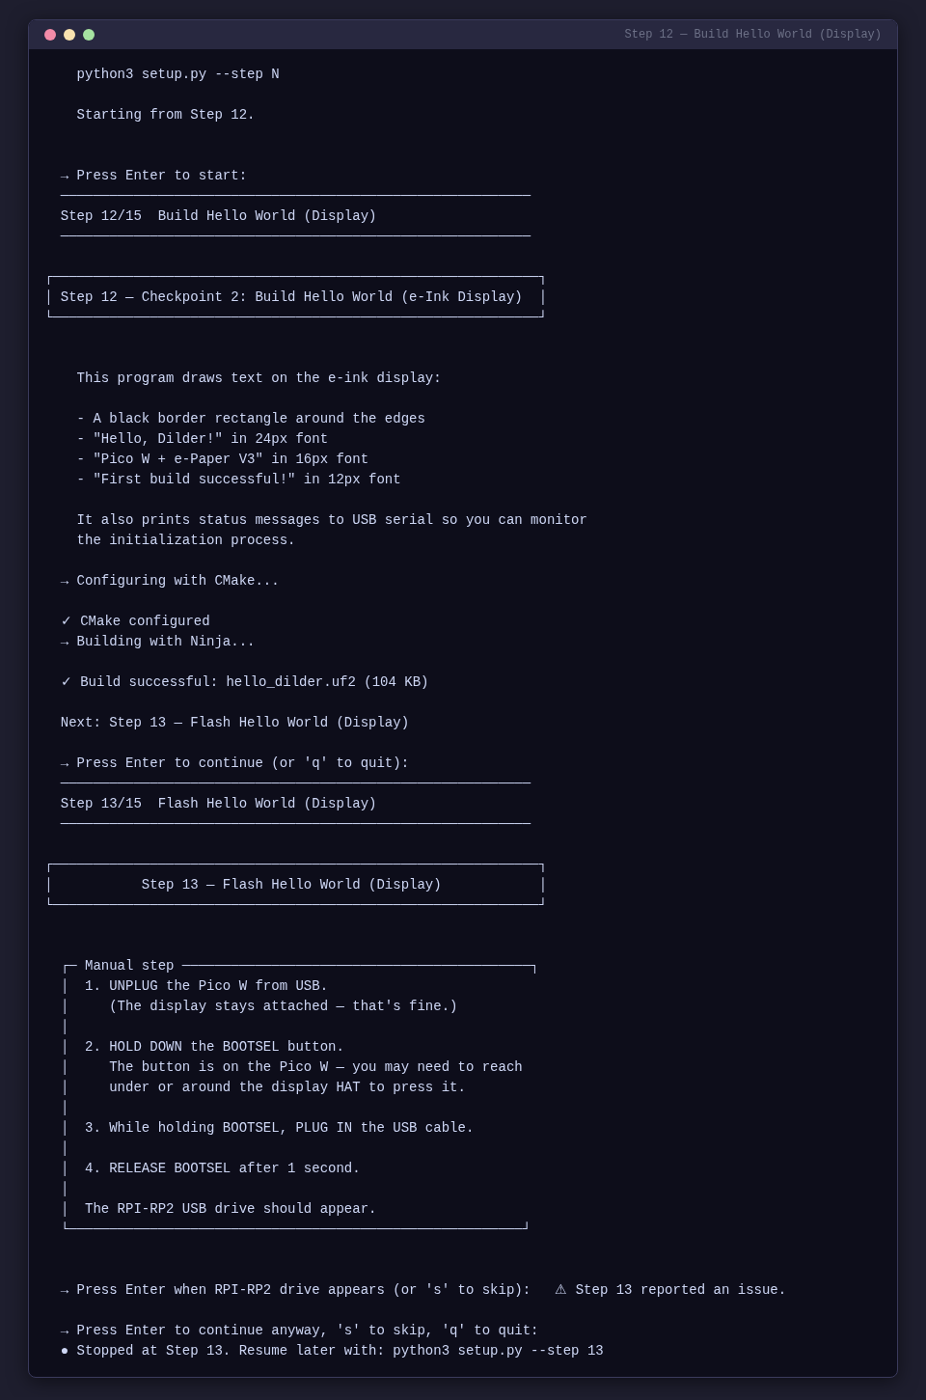
[picture p385: testing/setup_cli/screenshots/setup_cli_step_12.png]
setup_cli_step_12


### Setup Cli Step 13

Step 13 — Flash Hello World (Display): BOOTSEL detection and display firmware flash.

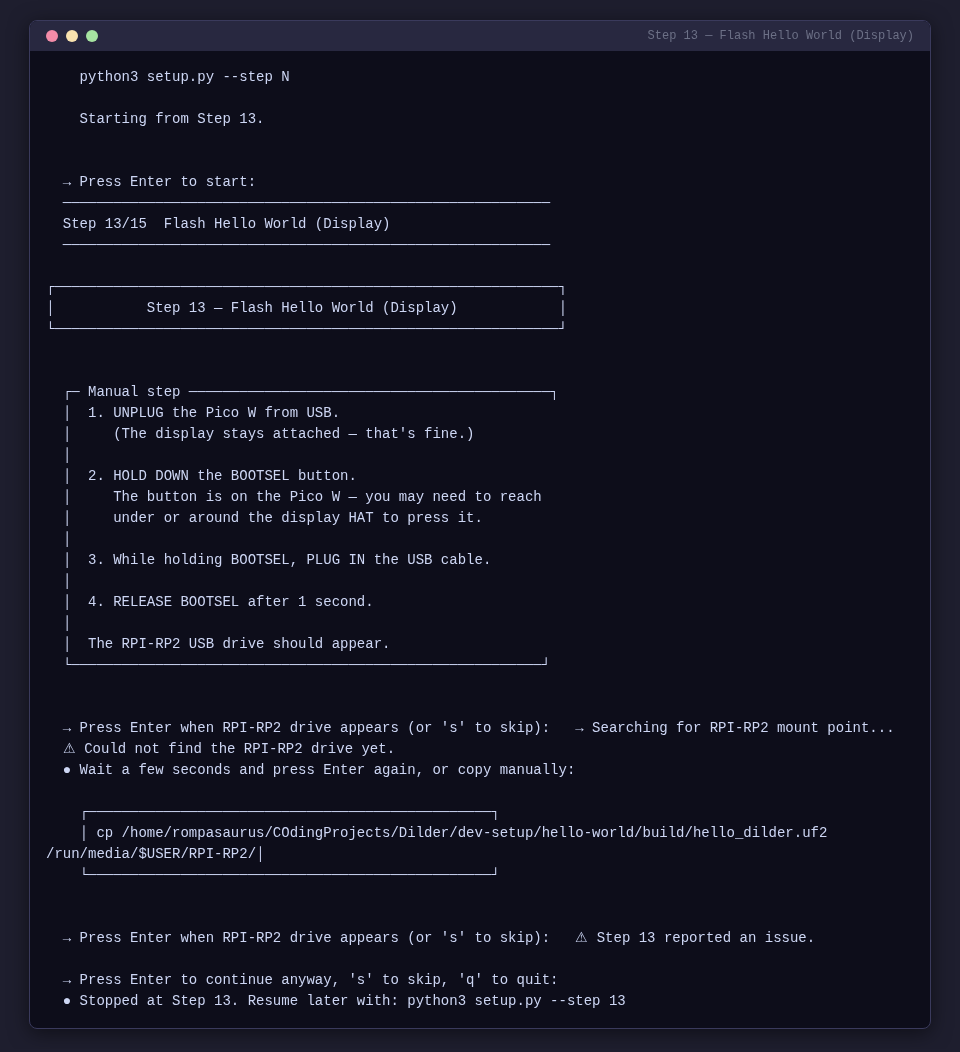
[picture p386: testing/setup_cli/screenshots/setup_cli_step_13.png]
setup_cli_step_13


### Setup Cli Step 14

Step 14 — Verify Display Output: confirms text appears on the e-ink display.

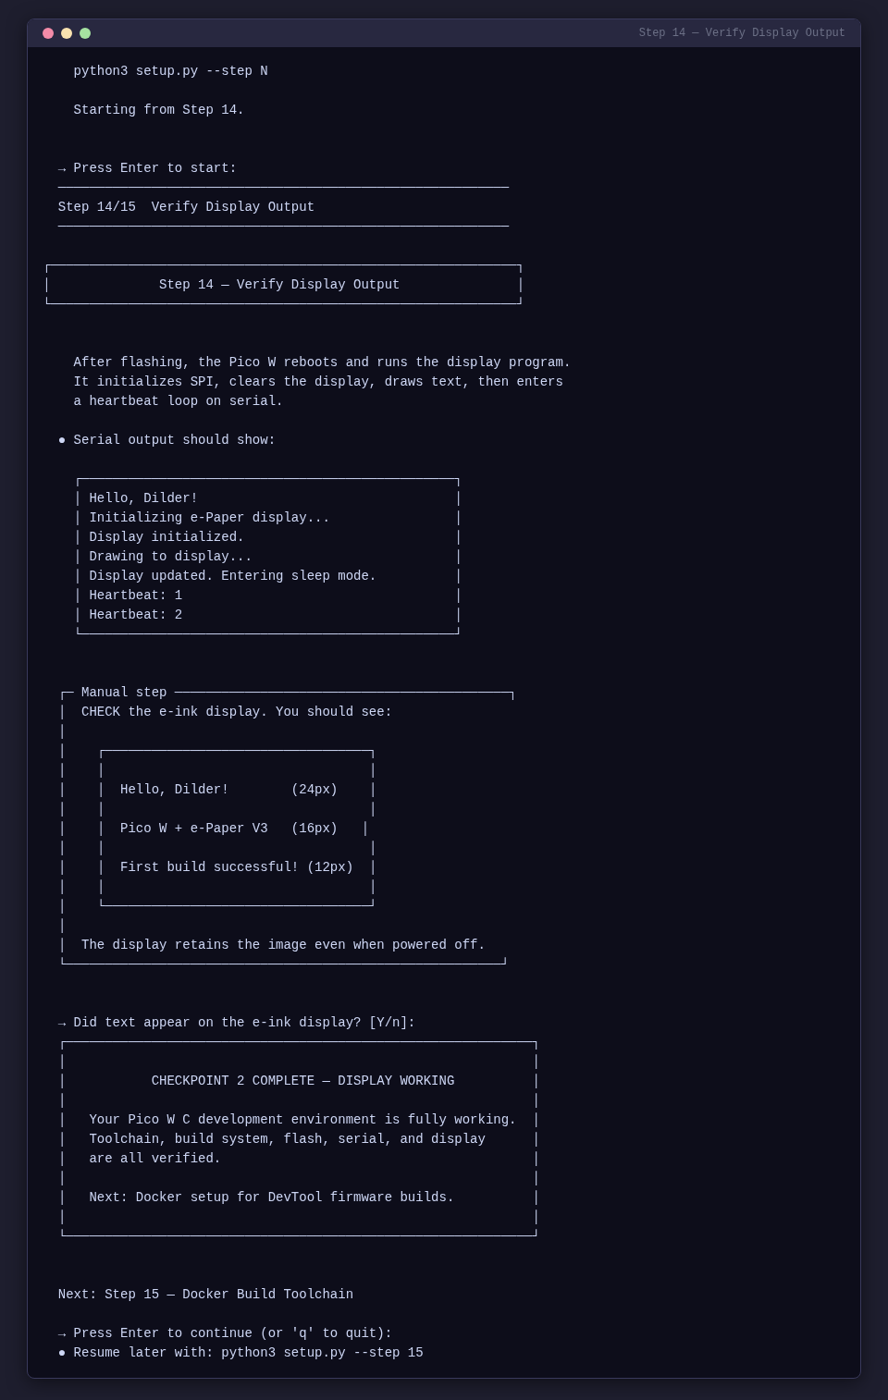
[picture p387: testing/setup_cli/screenshots/setup_cli_step_14.png]
setup_cli_step_14


### Setup Cli Step 15

Step 15 — Docker Build Toolchain: installs Docker and pre-builds the ARM cross-compilation container.

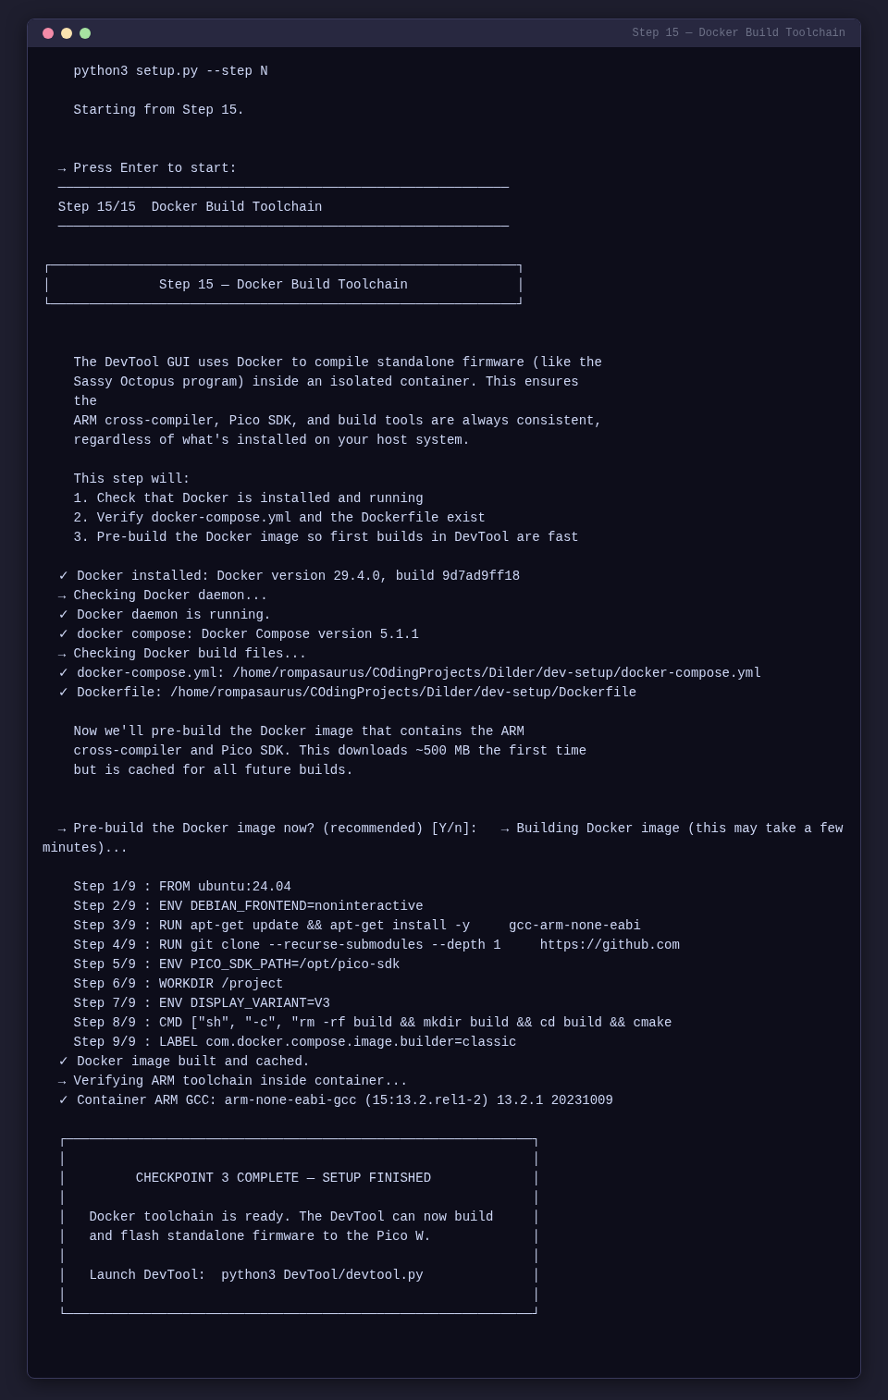
[picture p388: testing/setup_cli/screenshots/setup_cli_step_15.png]
setup_cli_step_15


### Setup Cli Test Setup Rendered

The --test-setup output showing testing framework installation progress.

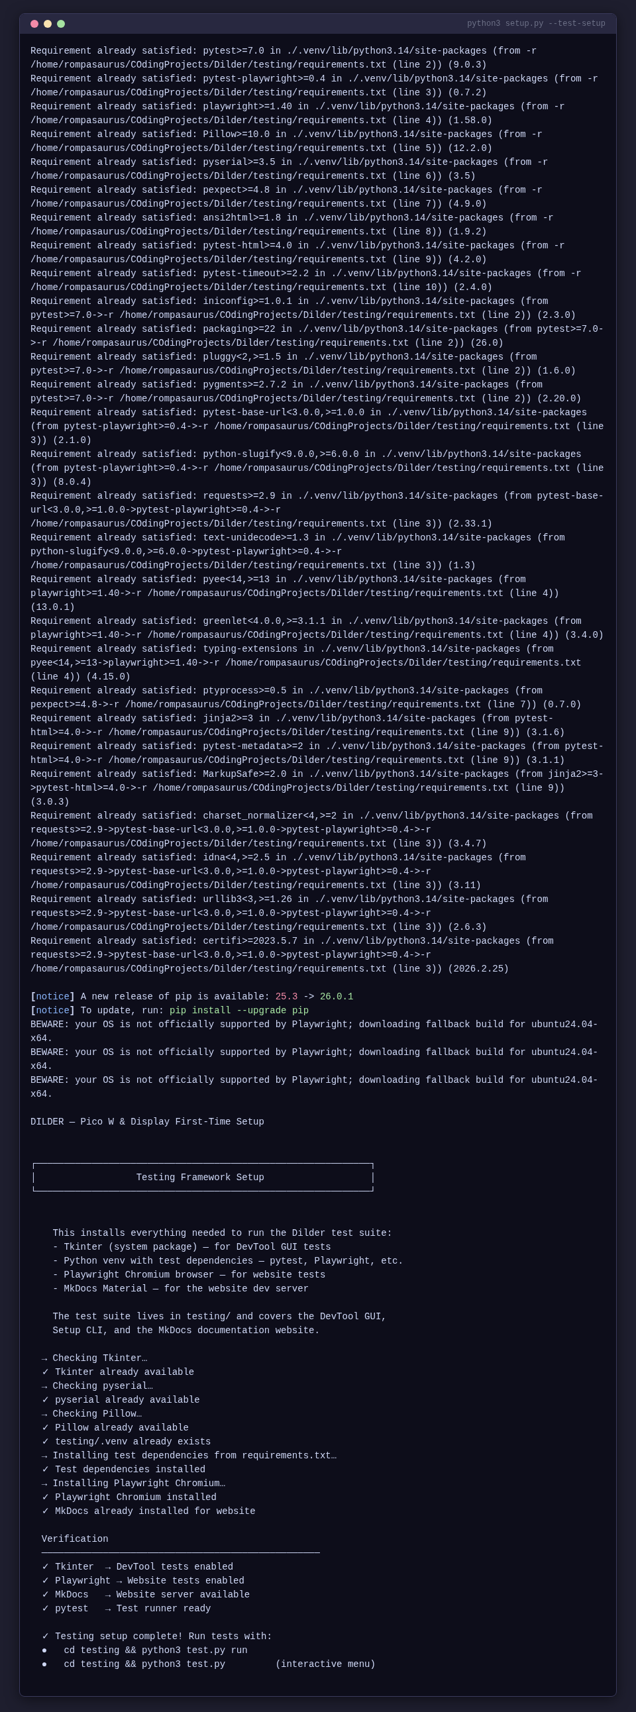
[picture p389: testing/setup_cli/screenshots/setup_cli_test_setup_rendered.png]
setup_cli_test_setup_rendered
