rompasaurus/regardedPal/tools/designtool/exports/2026-04-27_1352_aaa-cradle-with-batt-clips__battery_clips_forst_print_04-27_Shortened_holesby_5mm_and_opened_batt_clip_window_at_top/description.md

# Export: aaa-cradle-with-batt-clips / battery clips forst print 04-27 Shortened holesby 5mm and opened batt clip window at top

- **Date:** 2026-04-27 13:52:37
- **SCAD:** `aaa-cradle-with-batt-clips.scad`
- **Preset:** `battery clips forst print 04-27 Shortened holesby 5mm and opened batt clip window at top`
- **Formats:** stl, 3mf

## Parameters

| Parameter | Value | Default | Changed |
|---|---|---|---|
| `$fn` | 48 |  | **yes** |
| `aaa_bay_gap_from_pillar_cutout_mm` | 3 | 3.0 | **yes** |
| `aaa_bay_shift_toward_minus_x_mm` | 20 | 20 |  |
| `aaa_bay_wall_above_and_below_mm` | 0.5 | 0.5 |  |
| `aaa_cell_axial_slop_mm` | 1 | 1.0 | **yes** |
| `aaa_cell_contact_space_per_end_mm` | 2 | 2.0 | **yes** |
| `aaa_cell_diameter_mm` | 10.5 | 10.5 |  |
| `aaa_cell_length_mm` | 39.5 | 44.5 | **yes** |
| `aaa_cell_radial_slop_mm` | 0.3 | 0.3 |  |
| `batt_clip_plate_size_y_mm` | 7 | 7.0 | **yes** |
| `batt_clip_plate_size_z_mm` | 7 | 7.0 | **yes** |
| `batt_clip_plate_thickness_x_mm` | 0.5 | 0.5 |  |
| `batt_clip_retainer_enabled` | true | true |  |
| `batt_clip_retainer_thickness_x_mm` | 1 | 1.0 | **yes** |
| `batt_clip_retainer_window_size_y_mm` | 5 | 5.0 | **yes** |
| `batt_clip_retainer_window_size_z_mm` | 5 | 5.0 | **yes** |
| `batt_clip_retainer_window_z_extend_up_mm` | 4 | 0.0 | **yes** |
| `batt_clip_slot_slop_per_edge_mm` | 0.2 | 0.2 |  |
| `connecting_block_height_reduction_from_plug_mm` | 0 | 0 |  |
| `connecting_block_length_along_x_mm` | 29 | 29 |  |
| `corner_pillar_cutout_slop_mm` | 0.4 | 0.4 |  |
| `corner_pillar_square_side_length_mm` | 5 | 5 |  |
| `enclosure_outer_depth_along_y_axis_mm` | 46 | 46 |  |
| `enclosure_outer_width_along_x_axis_mm` | 94.5 | 94.5 |  |
| `face_plate_bottom_z_in_cover_local_mm` | 7 | 7 |  |
| `fpc_gap_width_along_x_mm` | 3 | 3 |  |
| `minus_x_end_wall_thickness_mm` | 3 | 3.0 | **yes** |
| `minus_x_inset_height_reduction_from_plug_mm` | 0 | 0 |  |
| `minus_x_inset_length_along_x_mm` | 29 | 29 |  |
| `perimeter_long_side_wall_thickness_y_mm_base` | 2 | 2 |  |
| `pico_w_board_length_along_x_mm` | 78 | 78 |  |
| `pico_w_board_width_along_y_mm` | 21 | 21.0 | **yes** |
| `plug_wall_slop_mm` | 0.3 | 0.3 |  |
| `plus_x_cutout_depth_z_mm` | 3 | 3 |  |
| `plus_x_end_wall_thickness_mm` | 1.2 | 1.2 |  |
| `print_fit_tolerance_slop_mm` | 0.4 | 0.4 |  |
| `tp4056_board_length_along_x_mm` | 28 | 28 |  |
| `tp4056_board_width_along_y_mm` | 17 | 17 |  |
| `tp4056_indent_depth_z_mm` | 1 | 1.0 | **yes** |
| `tp4056_indent_slop_per_edge_mm` | 0.2 | 0.2 |  |
