rompasaurus/regardedPal/hardware-design/examples/08-esp-rust-board/hardware/esp-rust-board/schematic/esp-rust-board-Assembly.pdf

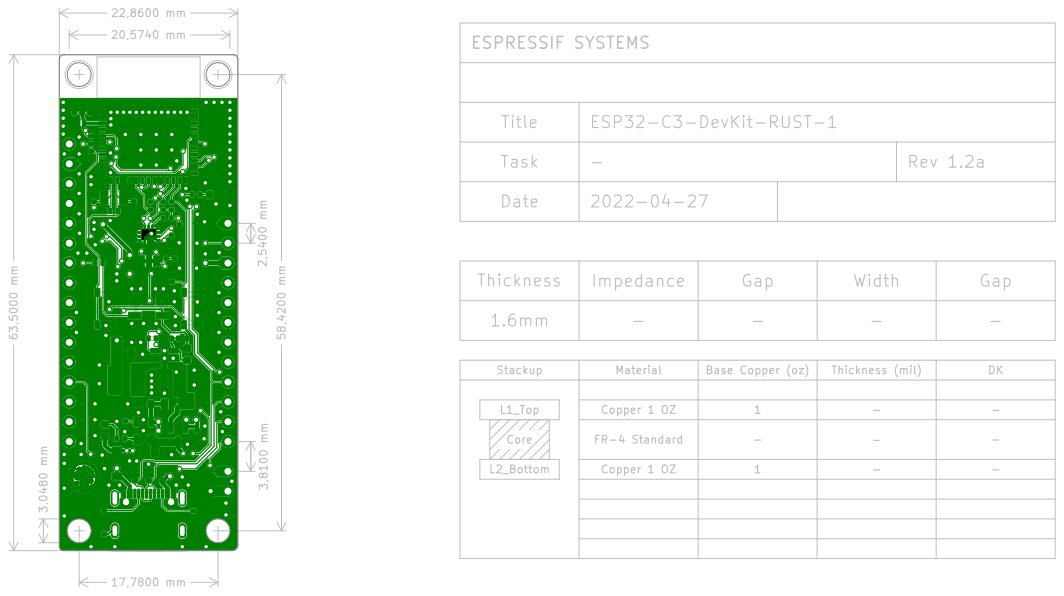
[picture p397: page 1]
D Date: 2022-04-27 KiCad E.D.A. kicad 6.0.1-79c1e3a40b~116~ubuntu21.04.1 Size: A4; Rev: 1.2a; - Stackup; Thickness (mil) L1_Top 1.6mm; Width; - Gap Date Thickness; Rev 1.2a ESPRESSIF SYSTEMS; Core; Gap; L2_Bottom; 1 Title; REF**; PCB-EDGE

ESP32-C3-DevKit-RUST-1 Task

2022-04-27
- Copper 1 OZ | | | DK

- Copper 1 OZ Material Impedance

- Base Copper (oz)

1 | - FR-4 Standard

Espressif Systems
Sheet: Assembly
File: esp-rust-board.kicad_pcb
Id: 1/1 Title: ESP32-C3-DevKit-RUST-1

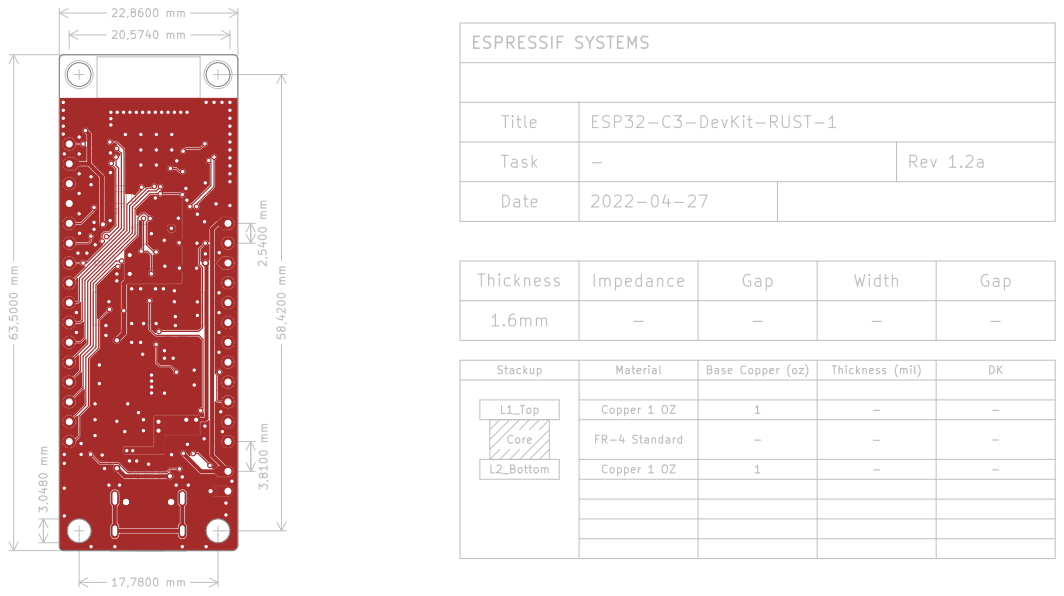
[picture p398: page 2]
D Date: 2022-04-27 KiCad E.D.A. kicad 6.0.1-79c1e3a40b~116~ubuntu21.04.1 Size: A4; Rev: 1.2a; - Stackup; Thickness (mil) L1_Top 1.6mm; Width; - Gap Date Thickness; Rev 1.2a ESPRESSIF SYSTEMS; Core; Gap; L2_Bottom; 1 Title; REF**; PCB-EDGE

ESP32-C3-DevKit-RUST-1 Task

- Copper 1 OZ Material Impedance

- Copper 1 OZ | | | DK

- Base Copper (oz)

1 | - FR-4 Standard

Espressif Systems
Sheet: Assembly
File: esp-rust-board.kicad_pcb
Id: 1/1 Title: ESP32-C3-DevKit-RUST-1

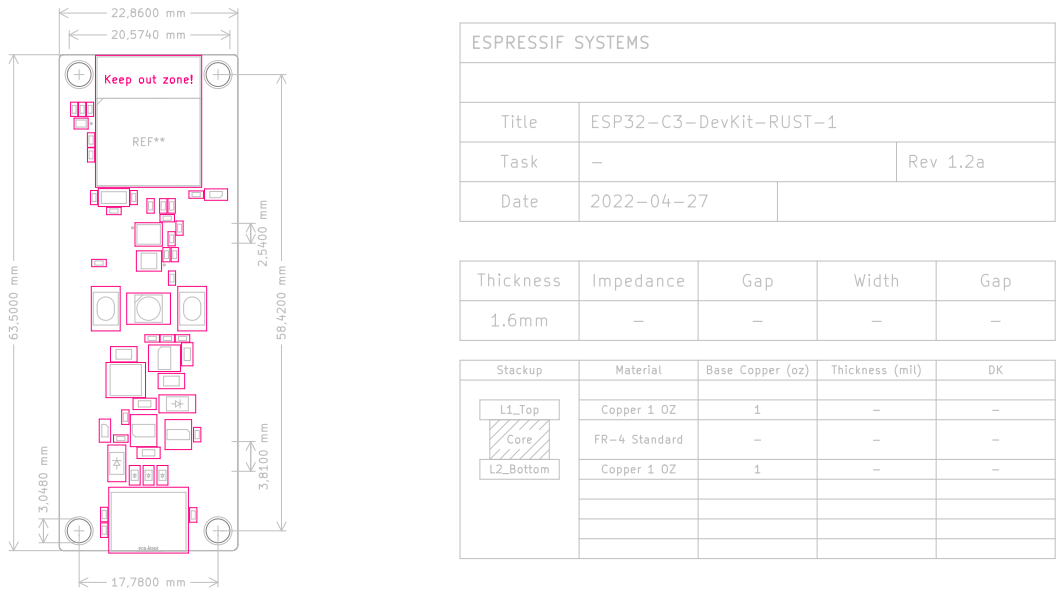
[picture p399: page 3]
D Date: 2022-04-27 KiCad E.D.A. kicad 6.0.1-79c1e3a40b~116~ubuntu21.04.1 Size: A4; Rev: 1.2a; - Stackup; Thickness (mil) L1_Top 1.6mm; Width; - Gap Date Thickness; Rev 1.2a ESPRESSIF SYSTEMS; Core; Gap; L2_Bottom; 1 Title; REF**

PCB-EDGE Keep out zone!

ESP32-C3-DevKit-RUST-1 Task

- Copper 1 OZ Material Impedance

- Copper 1 OZ | | | DK

- Base Copper (oz)

1 | - FR-4 Standard

Espressif Systems
Sheet: Assembly
File: esp-rust-board.kicad_pcb
Id: 1/1 Title: ESP32-C3-DevKit-RUST-1

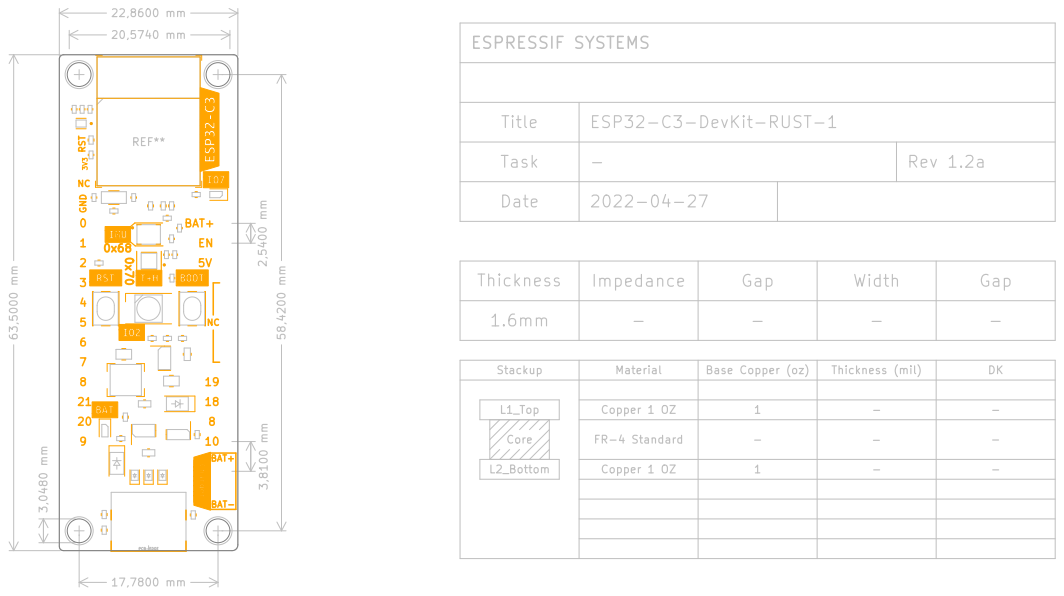
[picture p400: page 4]
D Date: 2022-04-27 KiCad E.D.A. kicad 6.0.1-79c1e3a40b~116~ubuntu21.04.1 Size: A4; Rev: 1.2a; - Stackup; Thickness (mil) L1_Top 1.6mm; Width; - Gap Date Thickness; Rev 1.2a ESPRESSIF SYSTEMS; Core; Gap; L2_Bottom; 1 Title; REF**; PCB-EDGE; BAT+ ³V³; 20GND; 0RST 9; BAT+ 1; 2 BAT- 10

ESP32-C3-DevKit-RUST-1 Task

- Copper 1 OZ Material Impedance

- Copper 1 OZ | | | DK

- Base Copper (oz)

1 | - FR-4 Standard

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

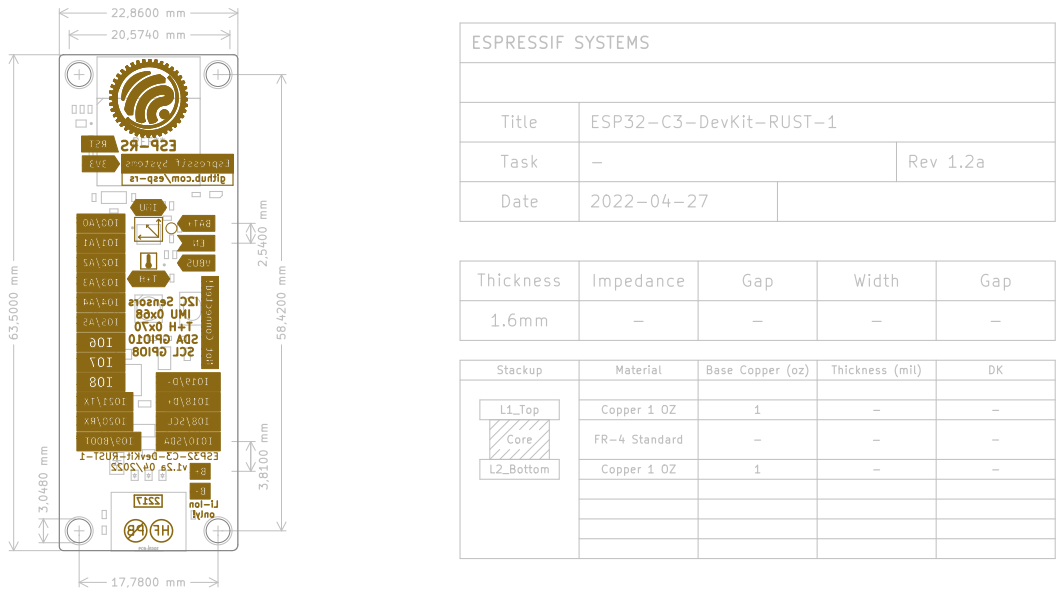
[picture p401: page 5]
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

ESP32-C3-DevKit-RUST-1 Task

- Copper 1 OZ Material Impedance

- Copper 1 OZ | | | DK

- Base Copper (oz)

1 | - FR-4 Standard

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

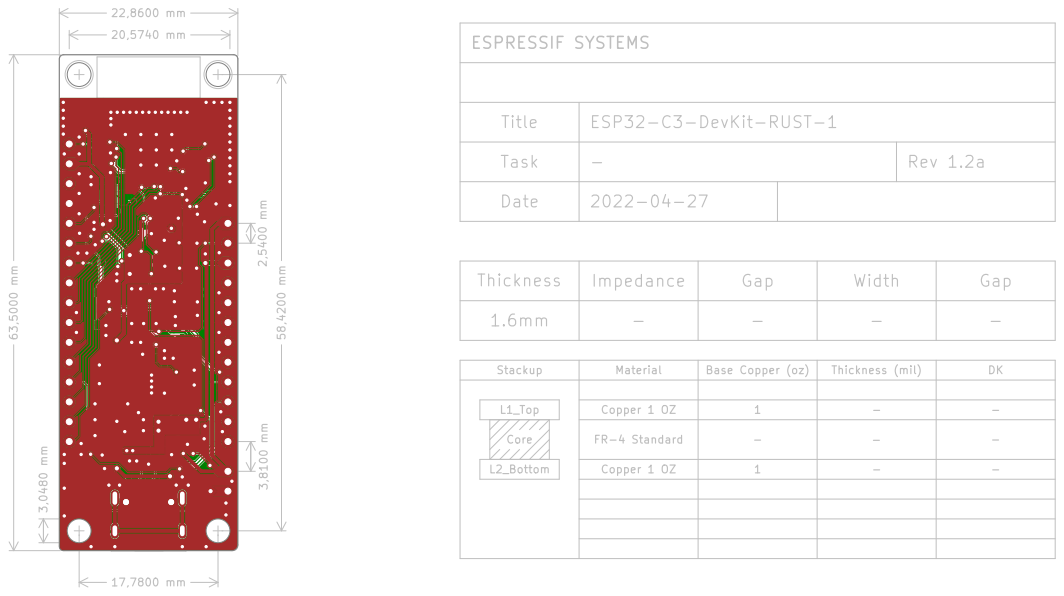
[picture p402: page 6]
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

ESP32-C3-DevKit-RUST-1 Task

2022-04-27
- Copper 1 OZ | | | DK

- Copper 1 OZ Material Impedance

- Base Copper (oz)

1 | - FR-4 Standard

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
