rompasaurus/regardedPal/testing/guides/devtool_guide.md

# Dilder DevTool User Guide

> Auto-generated from 35 test screenshots.
> Re-run the test suite to update: `pytest devtool/ -m screenshot`

---

## Asset

### Devtool Asset Manager List

The Asset Manager showing saved display images (PBM, BIN, PNG files).

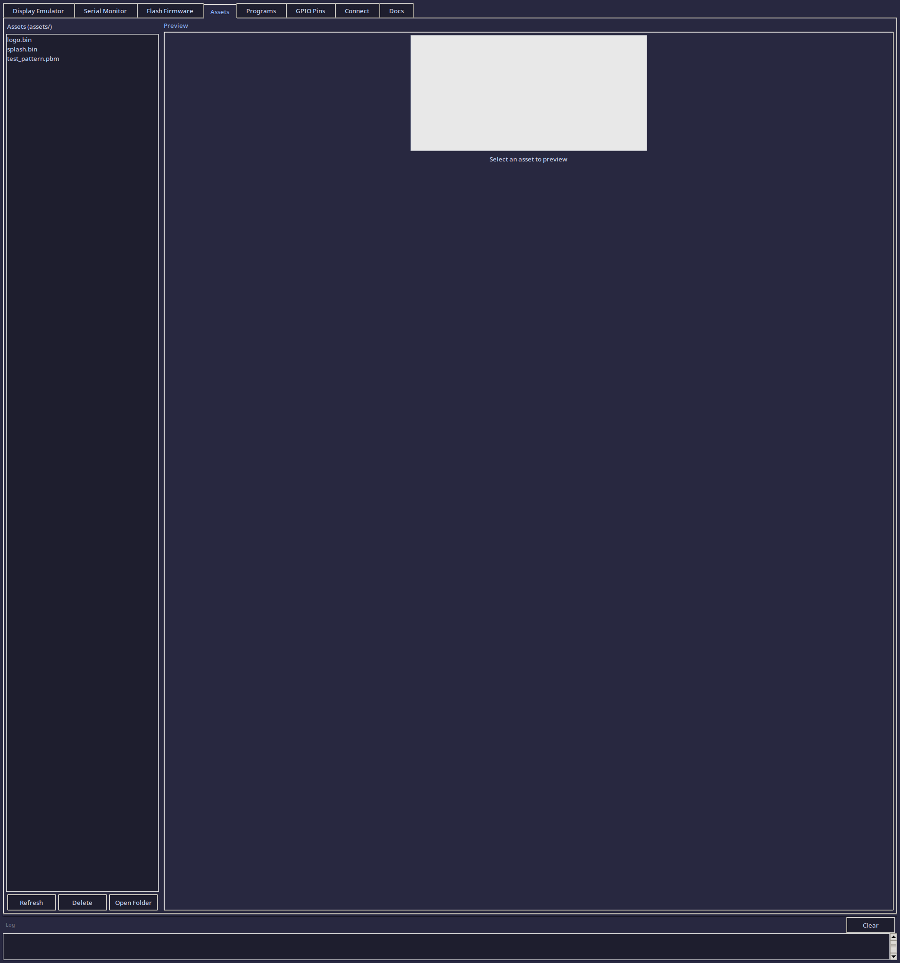
[picture p403: testing/devtool/screenshots/devtool_asset_manager_list.png]
devtool_asset_manager_list


### Devtool Asset Manager Preview

A checkerboard test pattern previewed at 2x zoom in the Asset Manager.

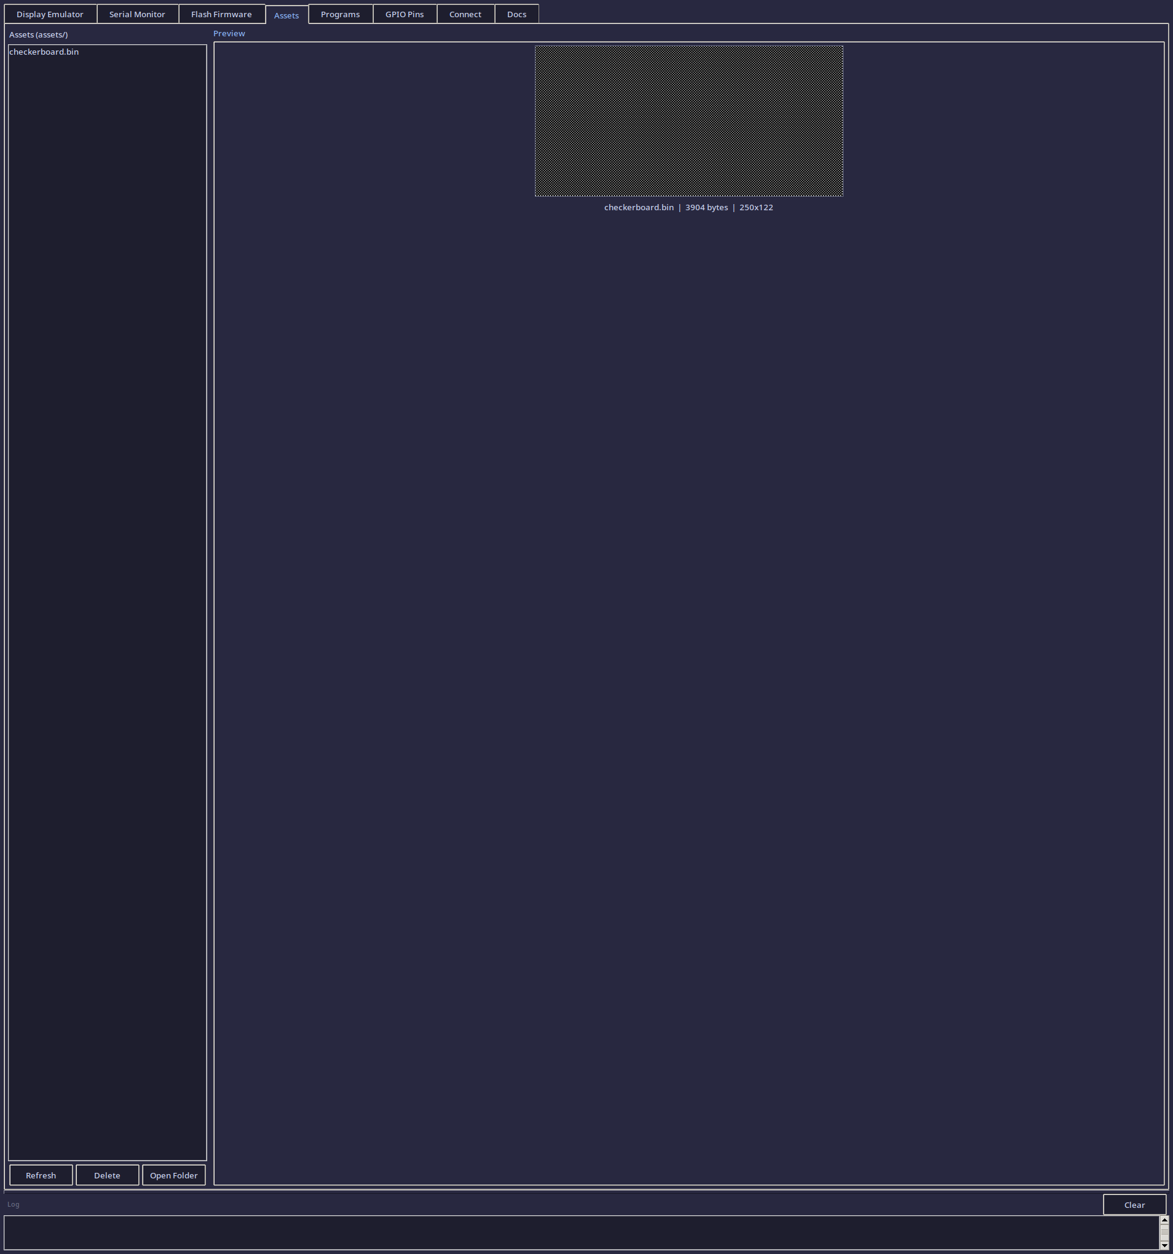
[picture p404: testing/devtool/screenshots/devtool_asset_manager_preview.png]
devtool_asset_manager_preview


## Connection

### Devtool Connection Usb Mode

USB Serial Connection walkthrough with step-by-step diagnostic checks.

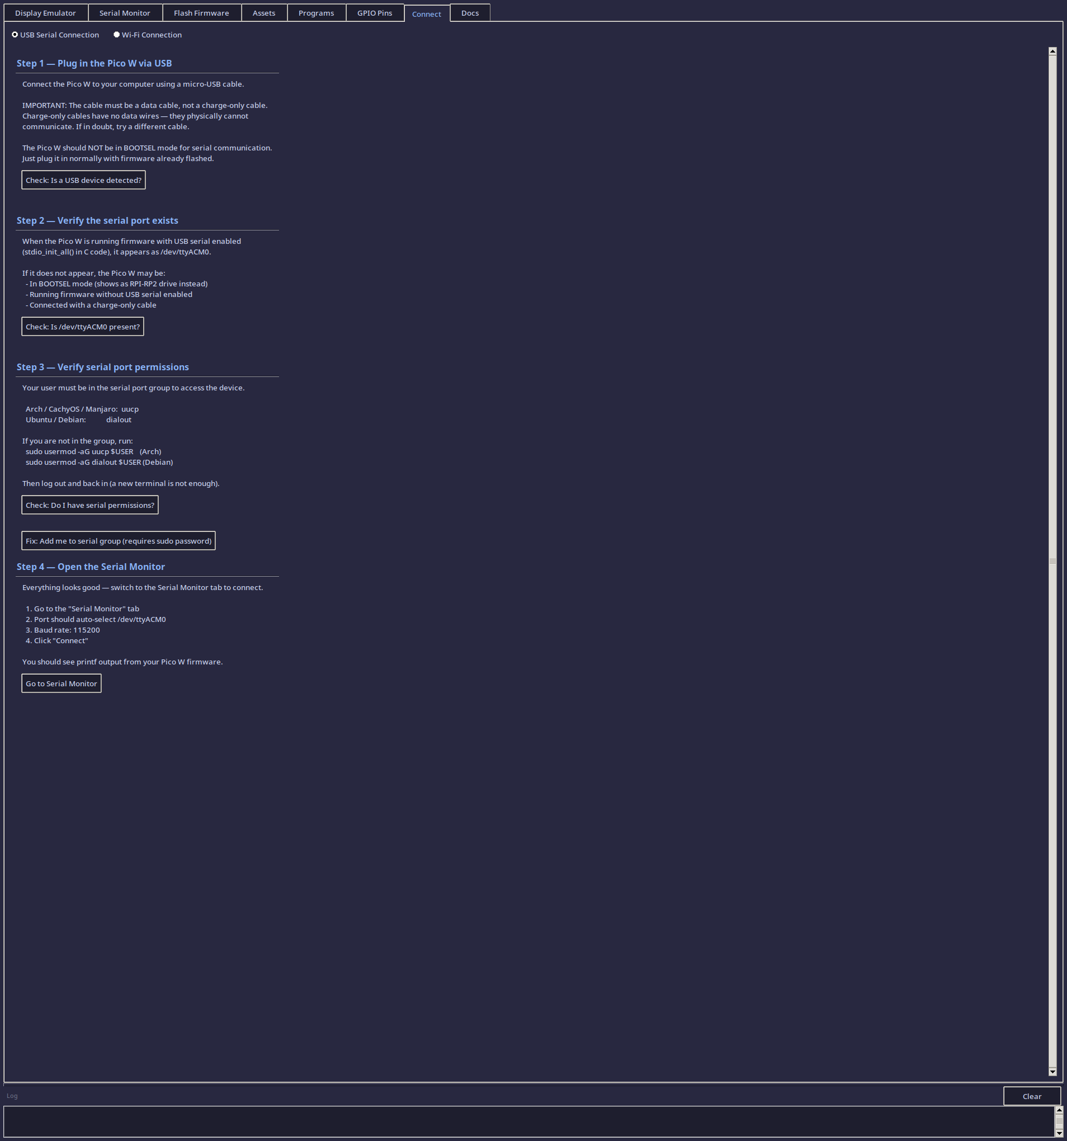
[picture p405: testing/devtool/screenshots/devtool_connection_usb_mode.png]
devtool_connection_usb_mode


### Devtool Connection Usb Walkthrough

The full USB connection walkthrough showing all 4 diagnostic steps.

devtool_connection_usb_walkthrough

### Devtool Connection Wifi Mode

Wi-Fi Connection setup guide with code samples and CMakeLists configuration.

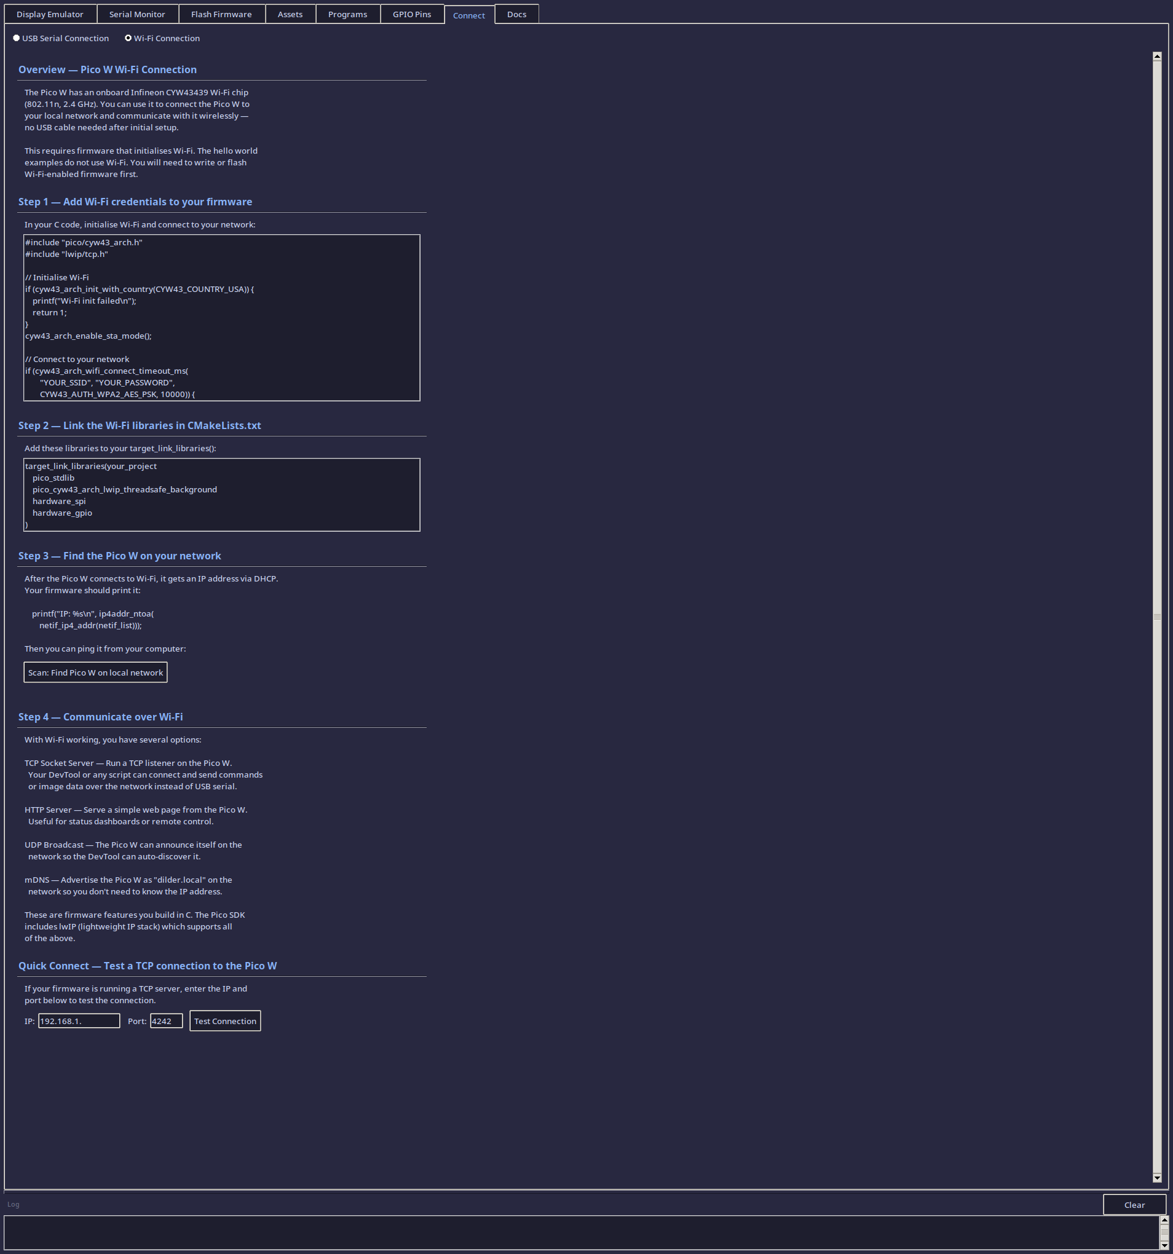
[picture p406: testing/devtool/screenshots/devtool_connection_wifi_mode.png]
devtool_connection_wifi_mode


## Display

### Devtool Display Blank Canvas

The Display Emulator tab with a fresh blank canvas (250x122 pixels, matching the Waveshare 2.13" e-ink display).

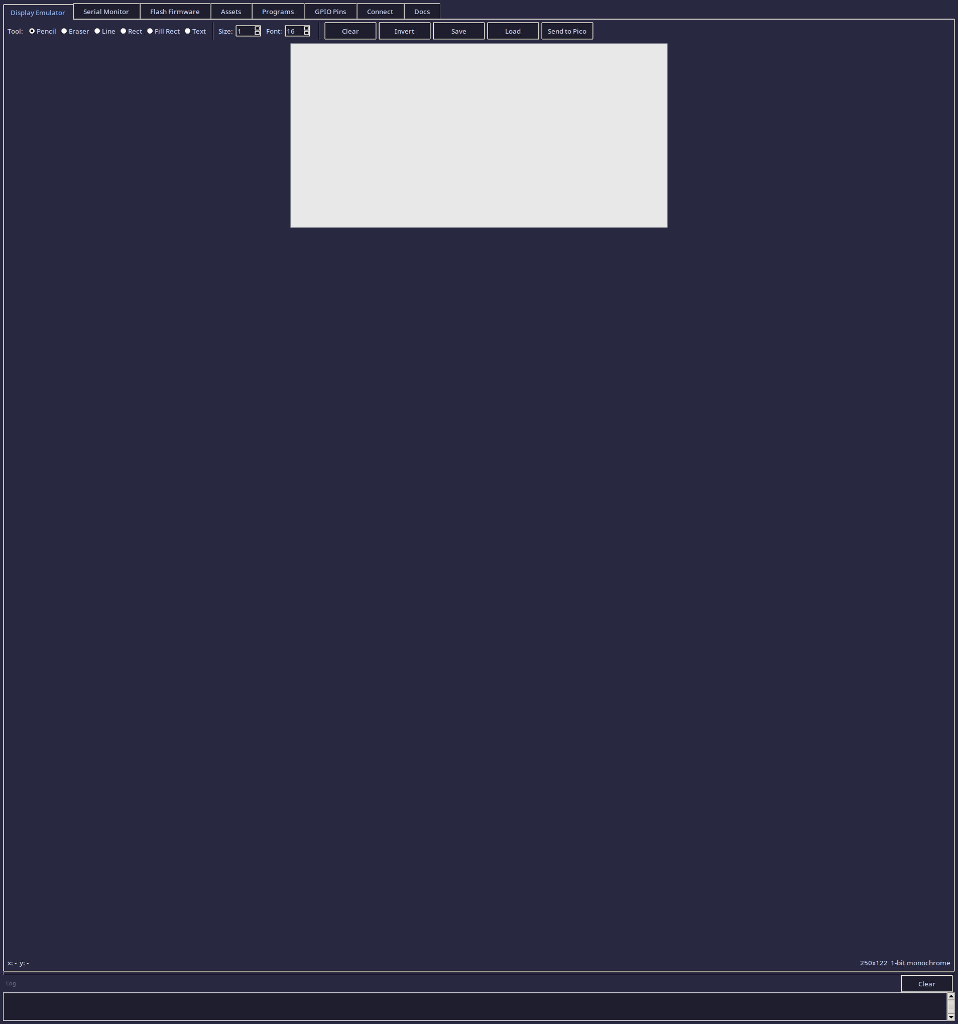
[picture p407: testing/devtool/screenshots/devtool_display_blank_canvas.png]
devtool_display_blank_canvas


### Devtool Display Drawing Tools

Drawing tools in action: line, rectangle, and filled rectangle demonstrated on the emulator canvas.

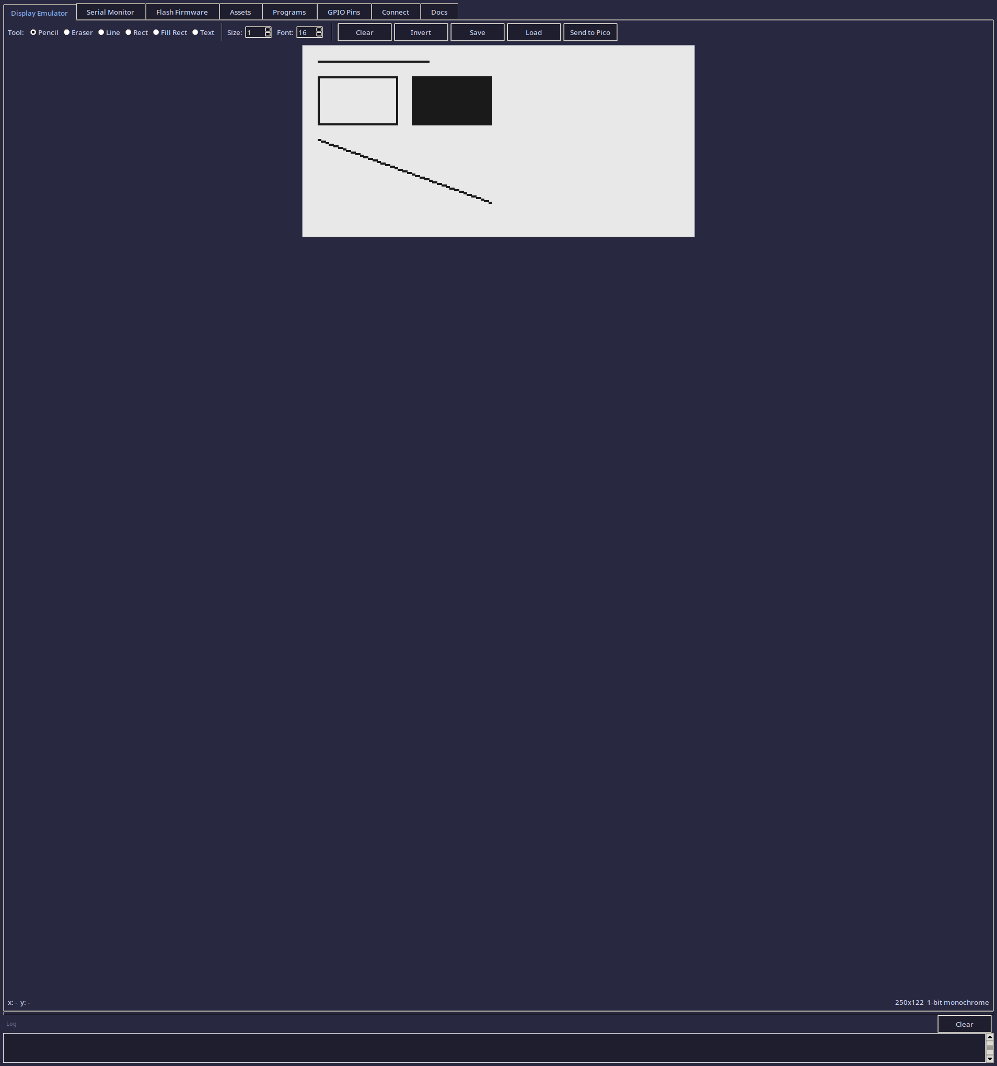
[picture p408: testing/devtool/screenshots/devtool_display_drawing_tools.png]
devtool_display_drawing_tools


### Devtool Display Inverted

The display after using the Invert function, which flips all black pixels to white and vice versa.

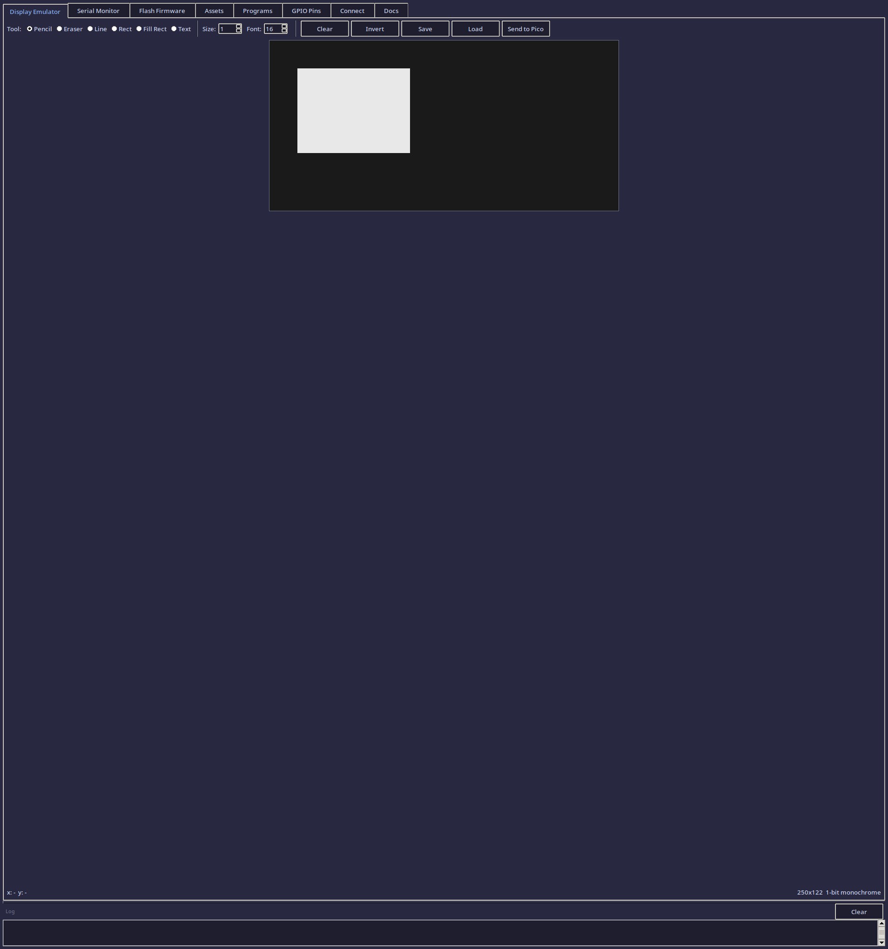
[picture p409: testing/devtool/screenshots/devtool_display_inverted.png]
devtool_display_inverted


### Devtool Display Save Workflow

A sample image ready to be saved in PBM, BIN, and PNG formats for use on the Pico W.

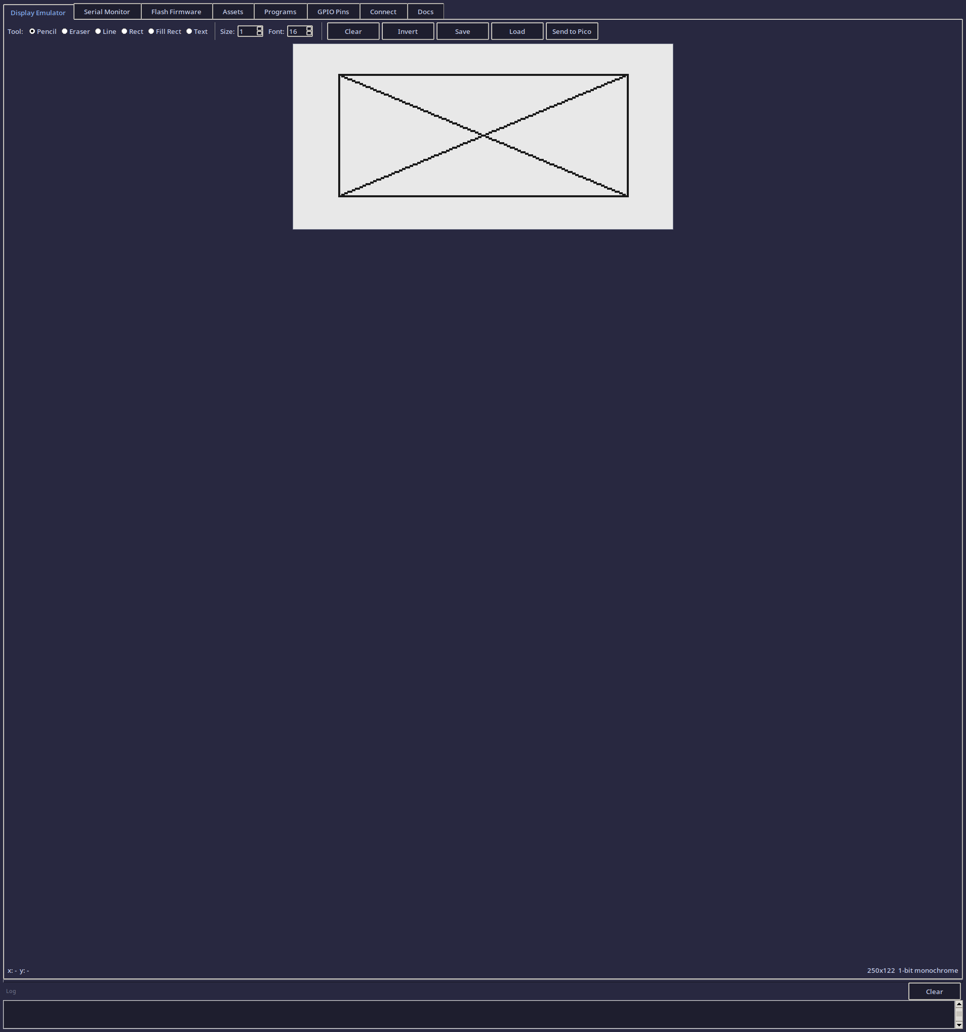
[picture p410: testing/devtool/screenshots/devtool_display_save_workflow.png]
devtool_display_save_workflow


### Devtool Display Tool Eraser

The Eraser tool selected — erase pixels back to white with configurable brush size.

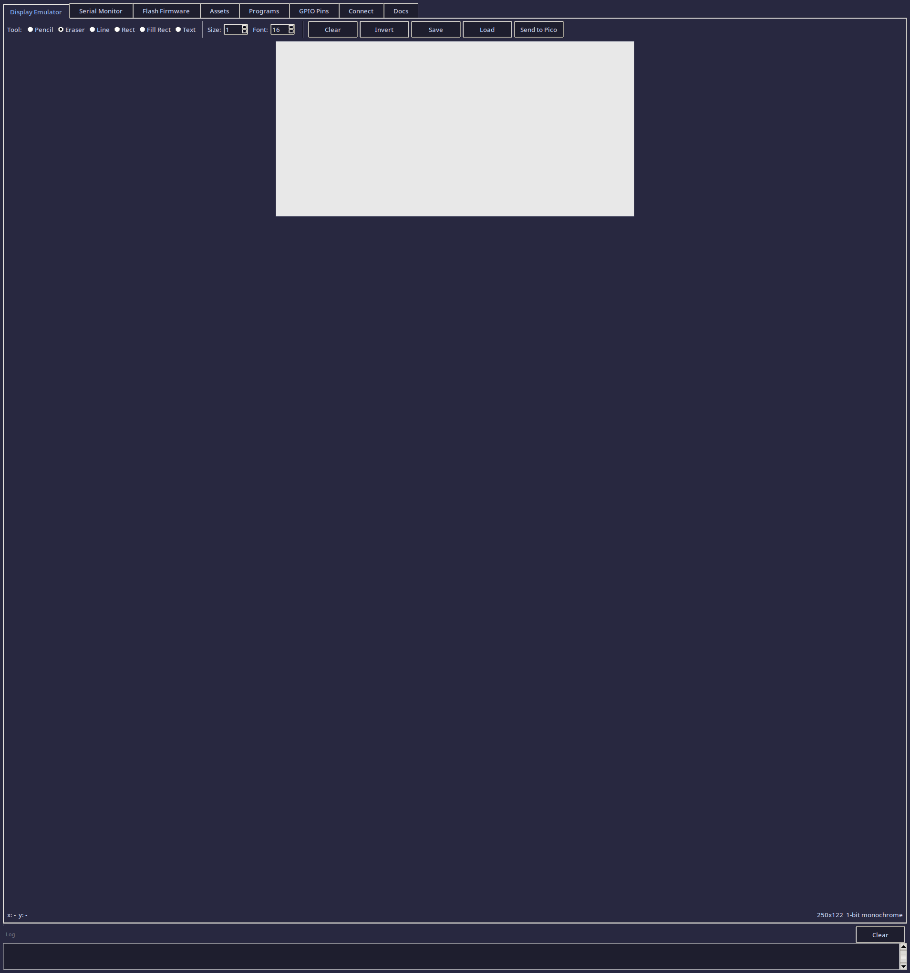
[picture p411: testing/devtool/screenshots/devtool_display_tool_eraser.png]
devtool_display_tool_eraser


### Devtool Display Tool Filled Rect

The Filled Rectangle tool selected — click and drag to draw filled rectangles.

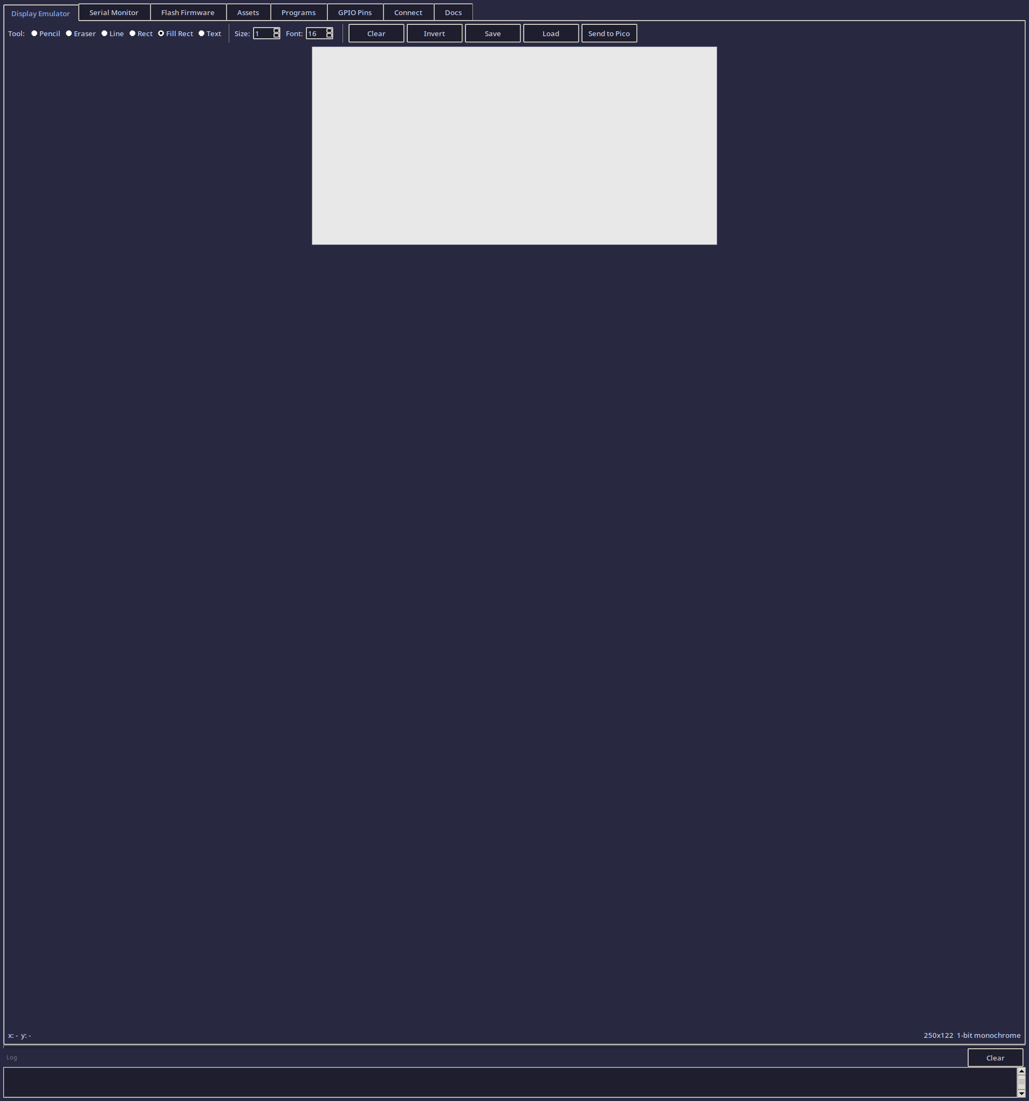
[picture p412: testing/devtool/screenshots/devtool_display_tool_filled_rect.png]
devtool_display_tool_filled_rect


### Devtool Display Tool Line

The Line tool selected — click and drag to draw straight lines using Bresenham's algorithm.

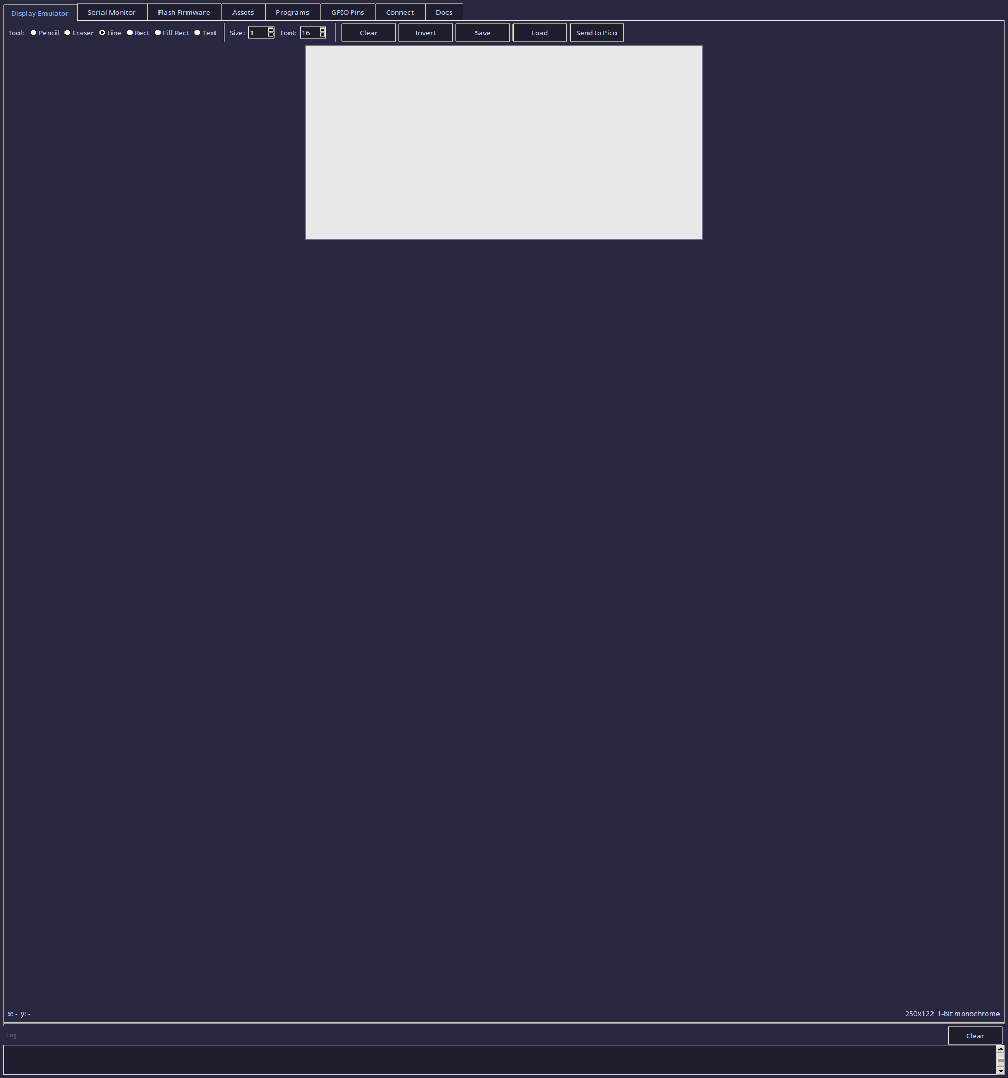
[picture p413: testing/devtool/screenshots/devtool_display_tool_line.png]
devtool_display_tool_line


### Devtool Display Tool Pencil

The Pencil tool selected — draw freehand with configurable brush size (1-10px).

devtool_display_tool_pencil

### Devtool Display Tool Rectangle

The Rectangle tool selected — click and drag to draw rectangle outlines.

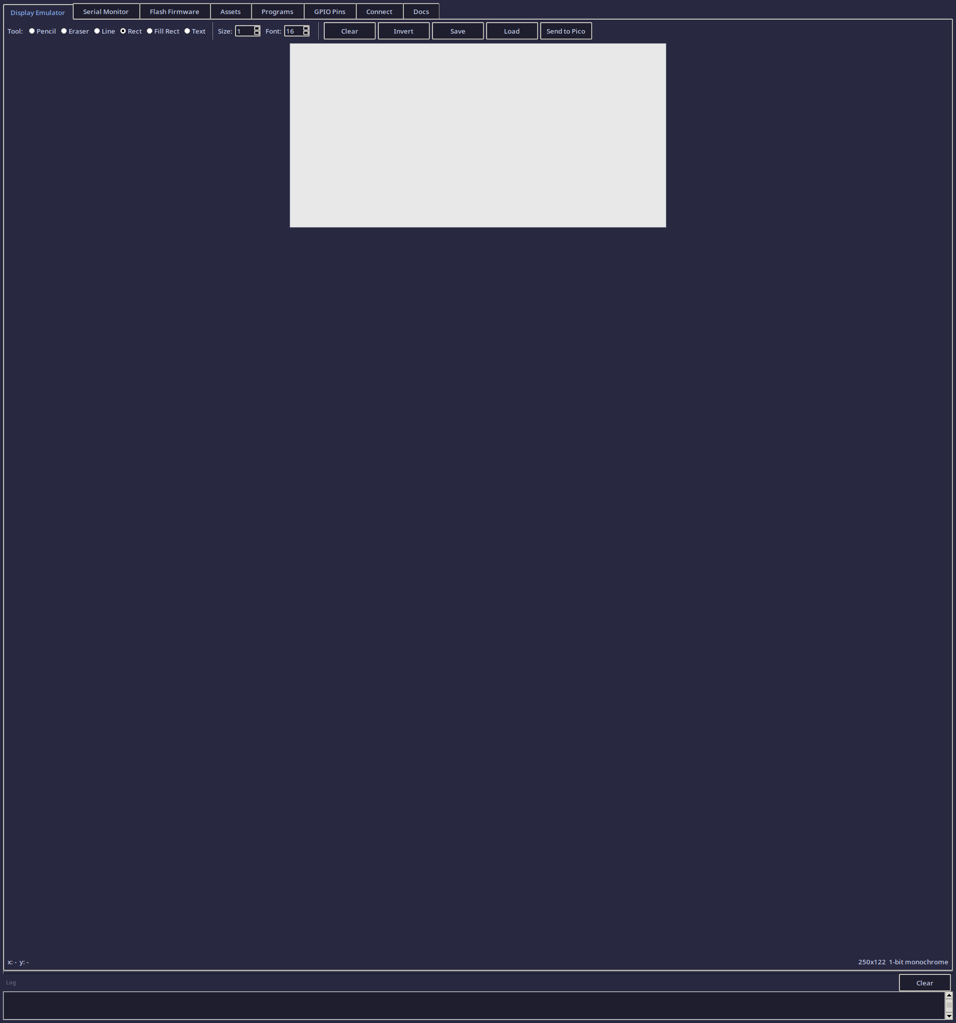
[picture p414: testing/devtool/screenshots/devtool_display_tool_rectangle.png]
devtool_display_tool_rectangle


### Devtool Display Tool Text

The Text tool selected — click to place rasterised text at any position.

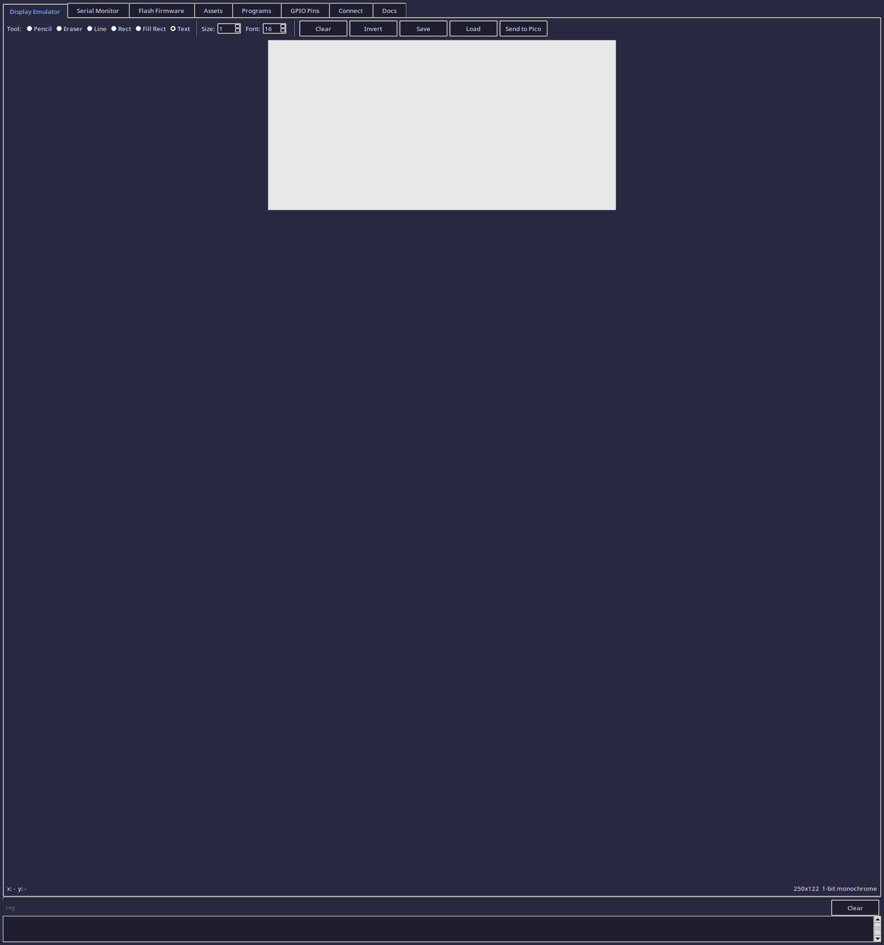
[picture p415: testing/devtool/screenshots/devtool_display_tool_text.png]
devtool_display_tool_text


## Documentation

### Devtool Documentation Search

Documentation search in action, filtering content by keyword.

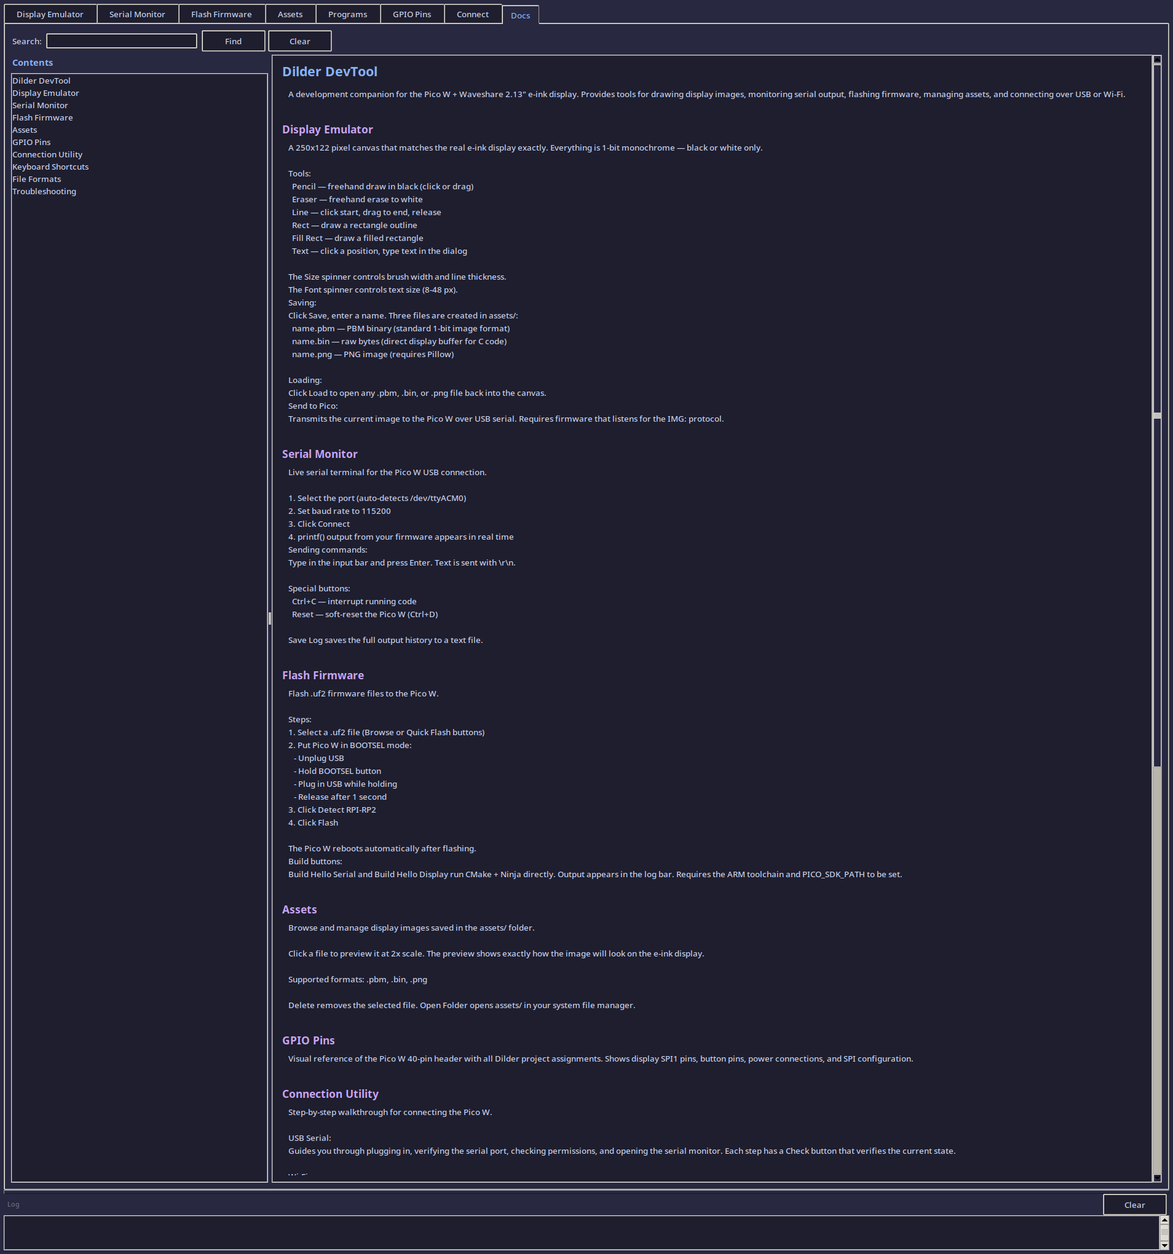
[picture p416: testing/devtool/screenshots/devtool_documentation_search.png]
devtool_documentation_search


### Devtool Documentation Tab

The built-in Documentation tab with searchable table of contents.

devtool_documentation_tab

## Flash

### Devtool Flash Firmware Tab

The Flash Firmware tab with UF2 file selection, BOOTSEL detection, and quick-flash presets.

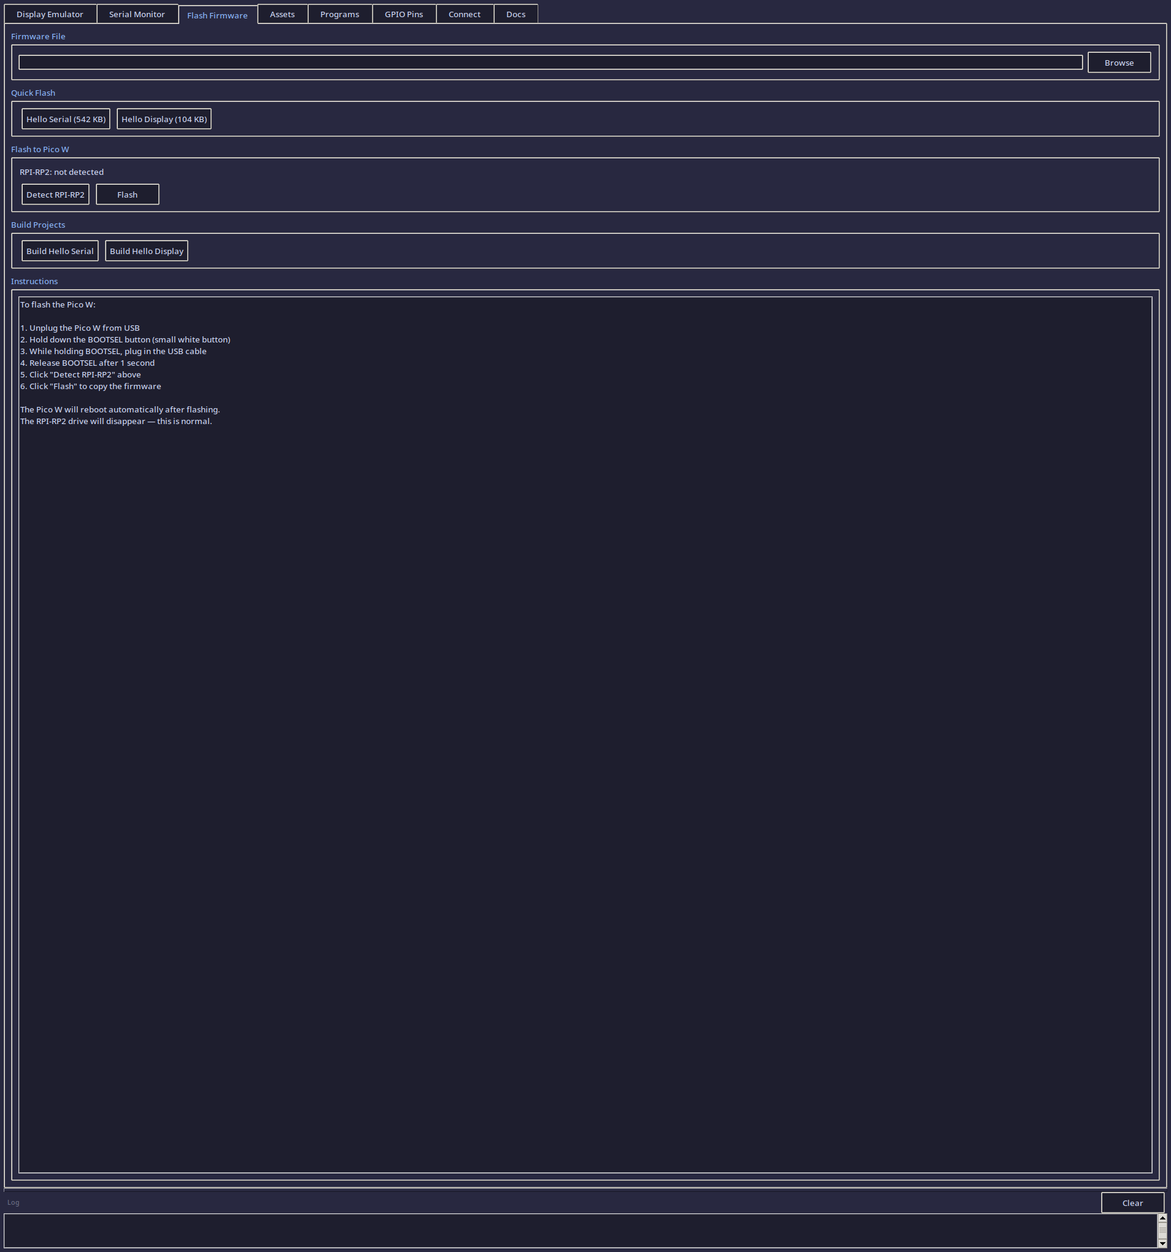
[picture p417: testing/devtool/screenshots/devtool_flash_firmware_tab.png]
devtool_flash_firmware_tab


### Devtool Flash Instructions

Step-by-step flashing instructions displayed in the Flash Firmware tab.

devtool_flash_instructions

### Devtool Flash Mount Detected

BOOTSEL mode detected — RPI-RP2 drive found and ready for firmware flashing.

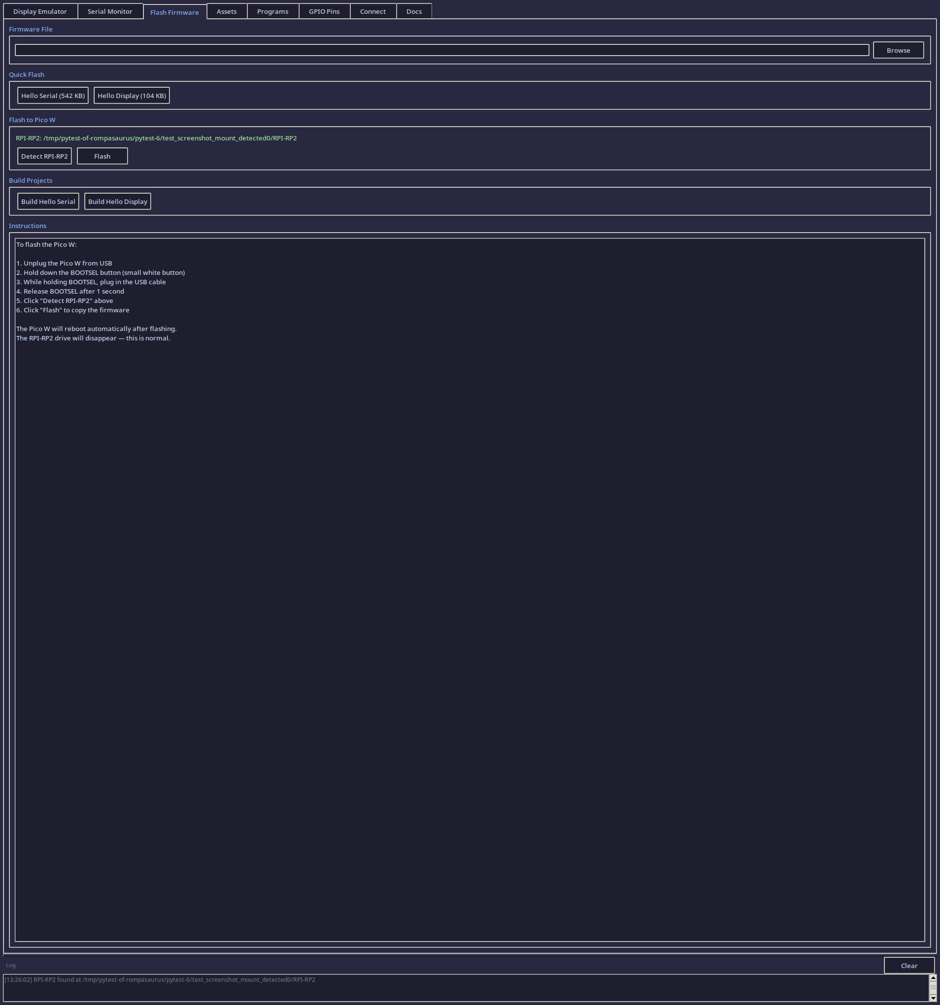
[picture p418: testing/devtool/screenshots/devtool_flash_mount_detected.png]
devtool_flash_mount_detected


## Gpio

### Devtool Gpio Pin Diagram

The GPIO Pin Viewer showing the complete Pico W pinout with Dilder-specific pin assignments highlighted.

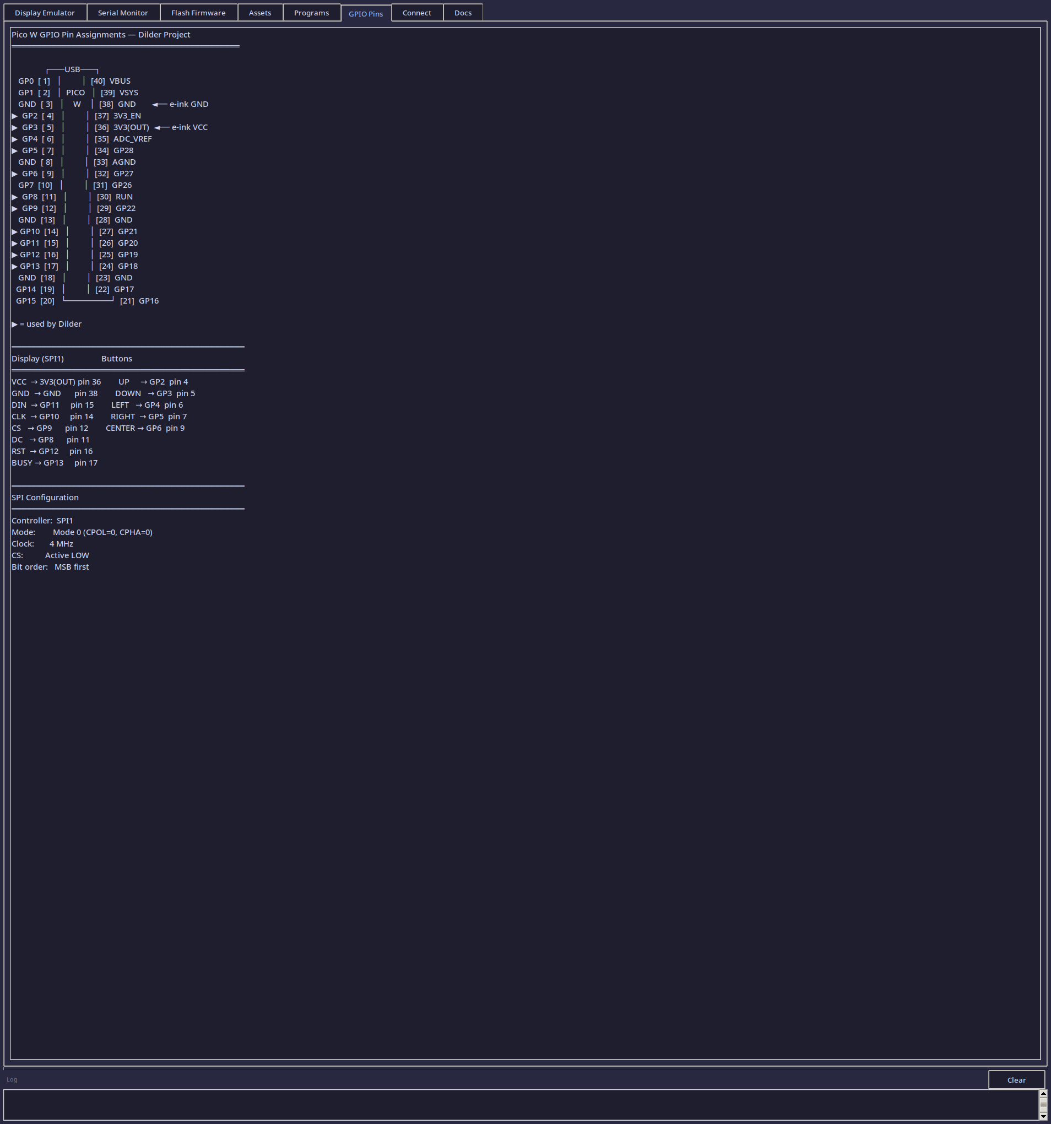
[picture p419: testing/devtool/screenshots/devtool_gpio_pin_diagram.png]
devtool_gpio_pin_diagram


## Programs

### Devtool Programs Deploy Buttons

Deploy buttons: Preview, Deploy to Pico (streaming), Flash IMG Receiver, and Deploy Standalone.

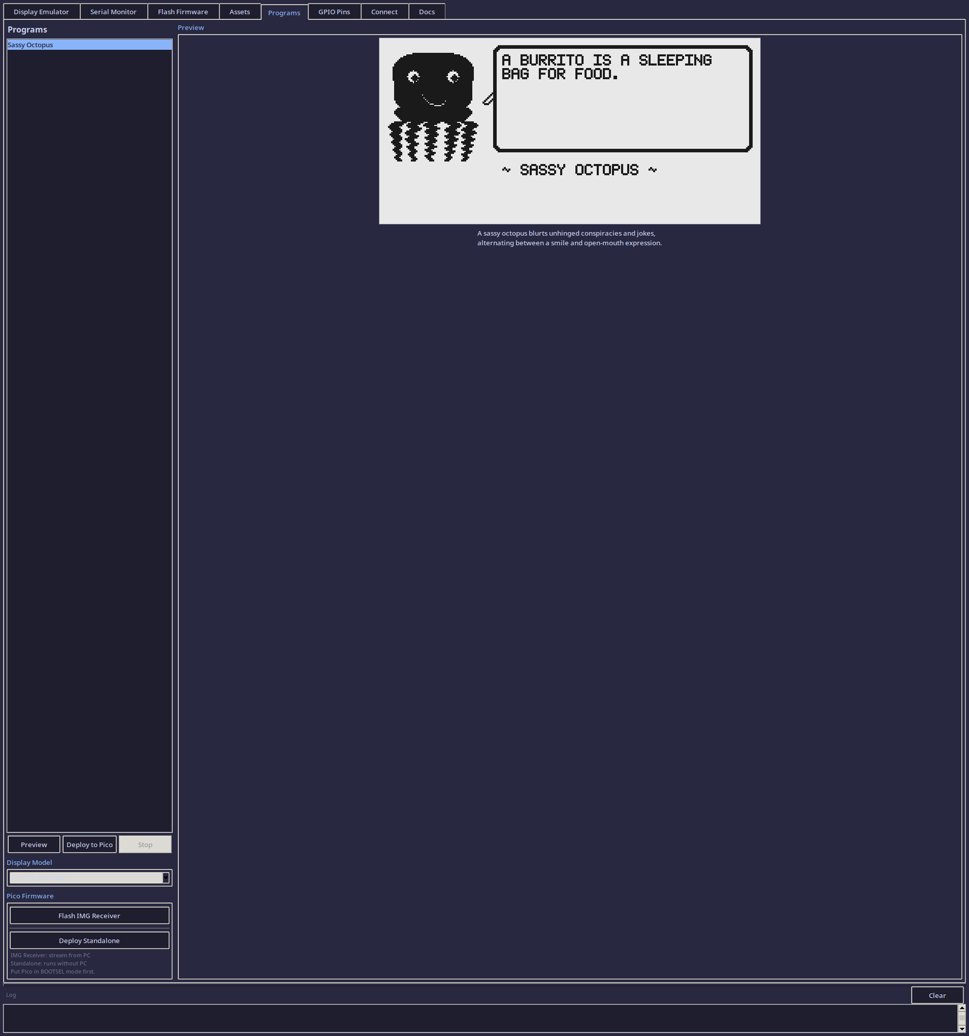
[picture p420: testing/devtool/screenshots/devtool_programs_deploy_buttons.png]
devtool_programs_deploy_buttons


### Devtool Programs List

The Programs tab with Sassy Octopus selected, showing program description and deploy options.

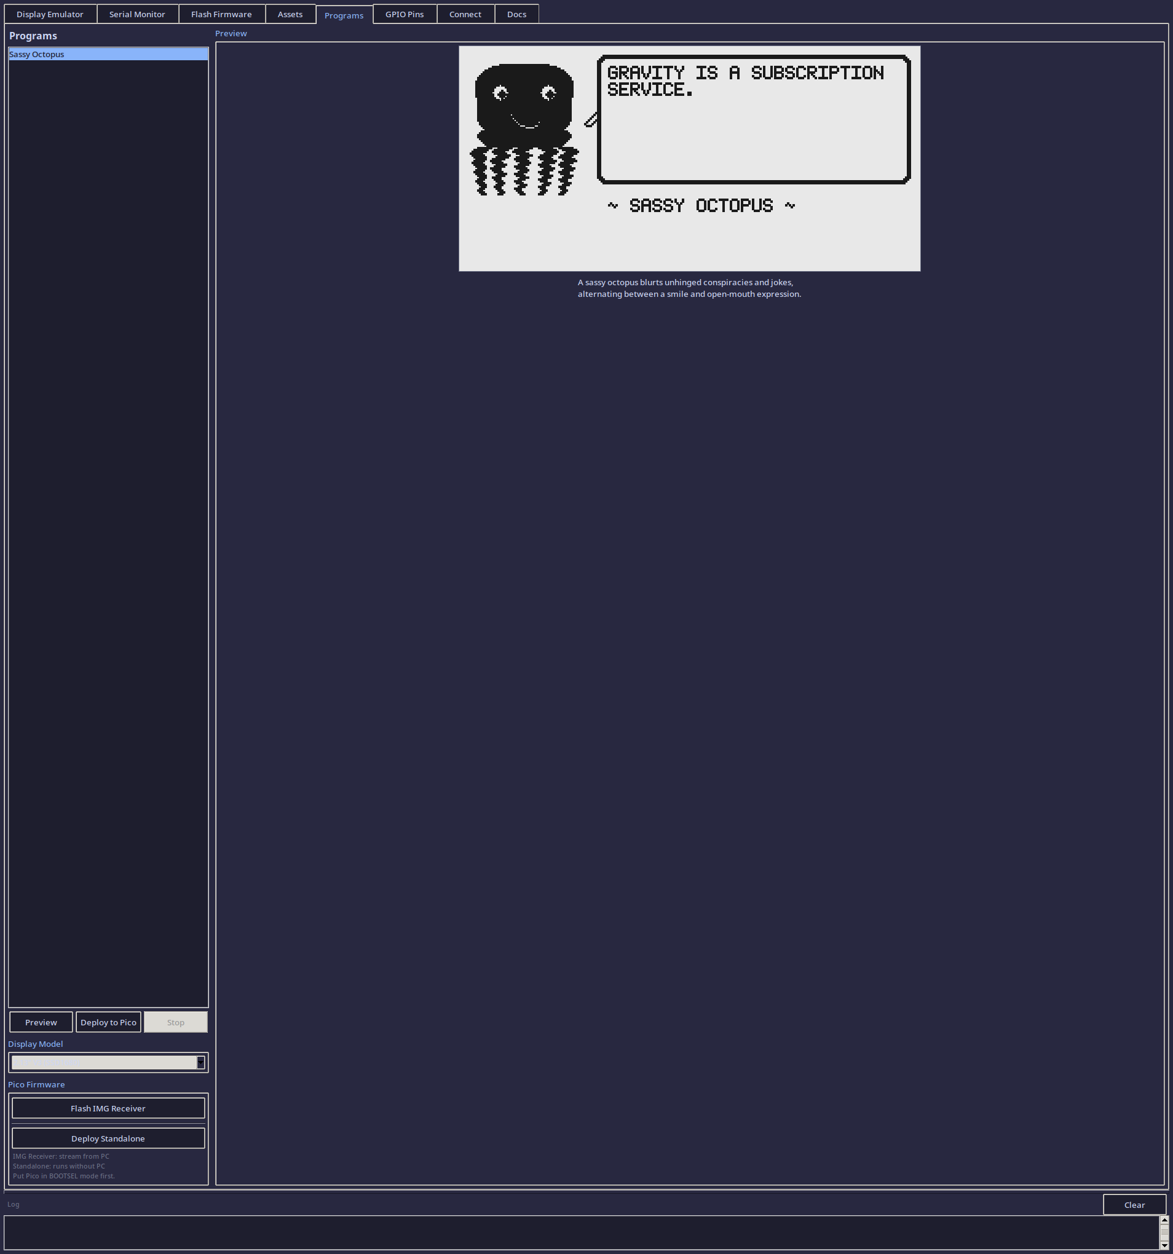
[picture p421: testing/devtool/screenshots/devtool_programs_list.png]
devtool_programs_list


### Devtool Programs Preview Area

The preview canvas area where programs are animated before deployment.

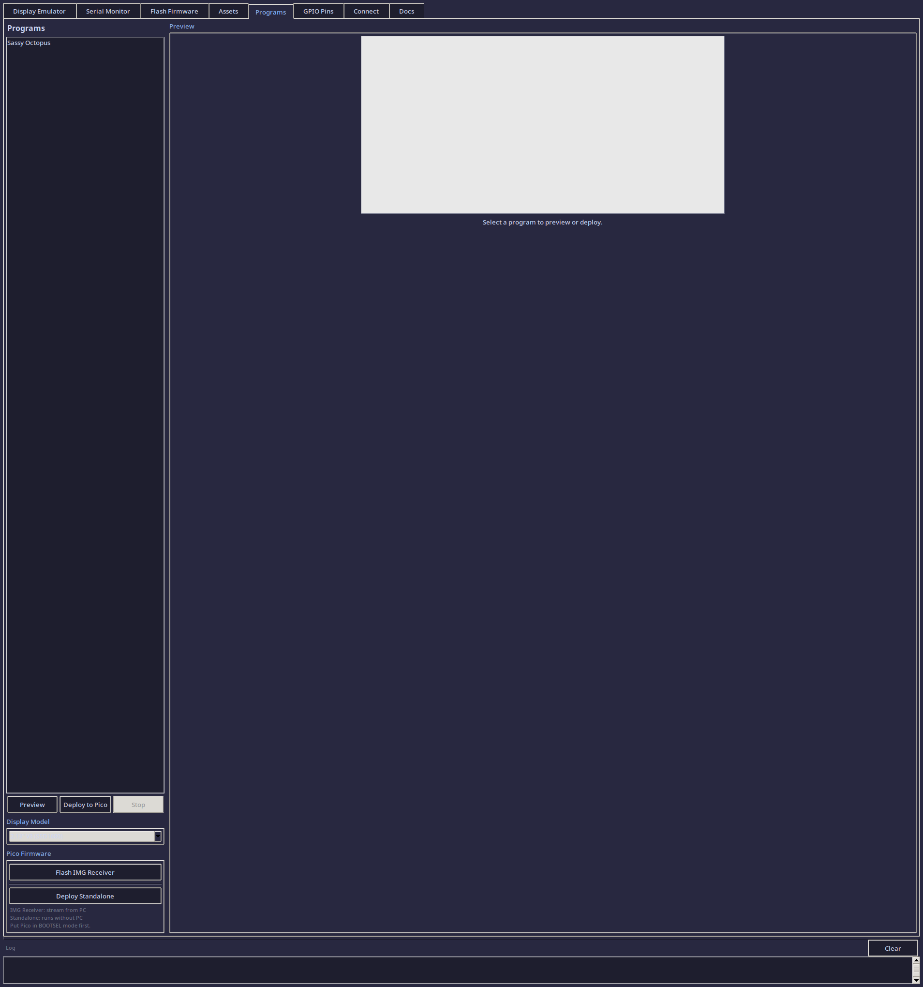
[picture p422: testing/devtool/screenshots/devtool_programs_preview_area.png]
devtool_programs_preview_area


## Serial

### Devtool Serial Connected

The Serial Monitor connected to the Pico W, ready to receive output.

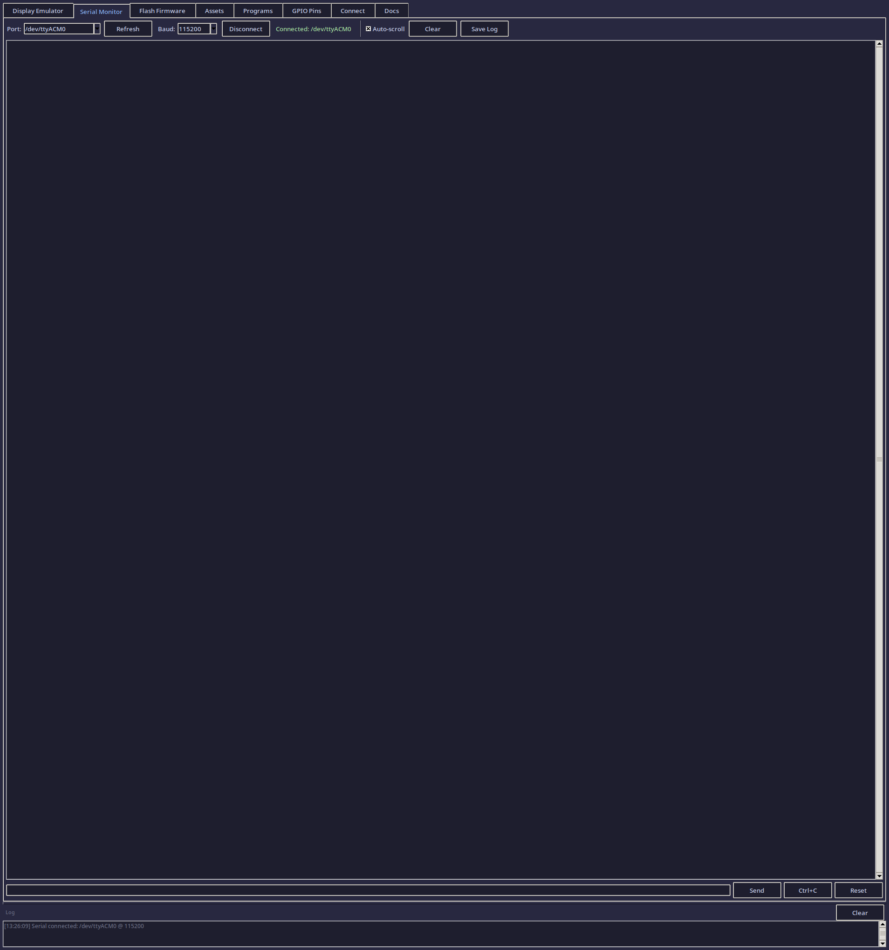
[picture p423: testing/devtool/screenshots/devtool_serial_connected.png]
devtool_serial_connected


### Devtool Serial Disconnected

The Serial Monitor tab in its disconnected state, showing port selection and baud rate configuration.

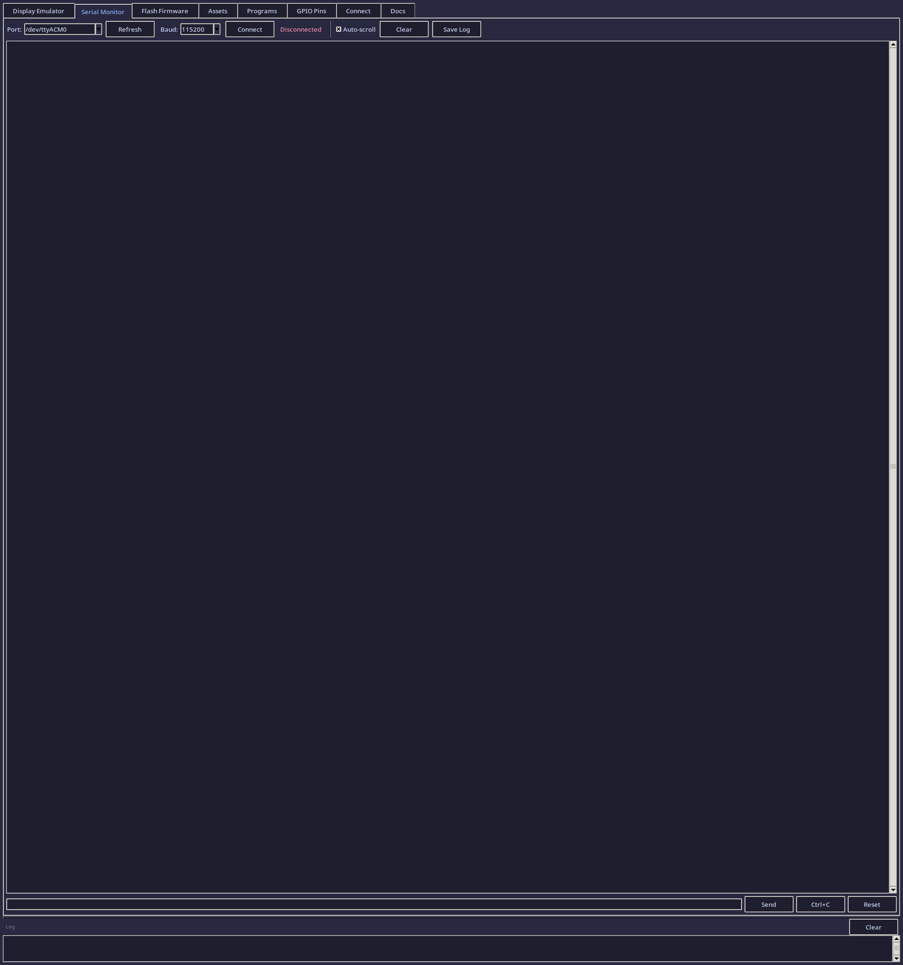
[picture p424: testing/devtool/screenshots/devtool_serial_disconnected.png]
devtool_serial_disconnected


### Devtool Serial With Output

Live serial output from the Pico W showing sensor readings and button events.

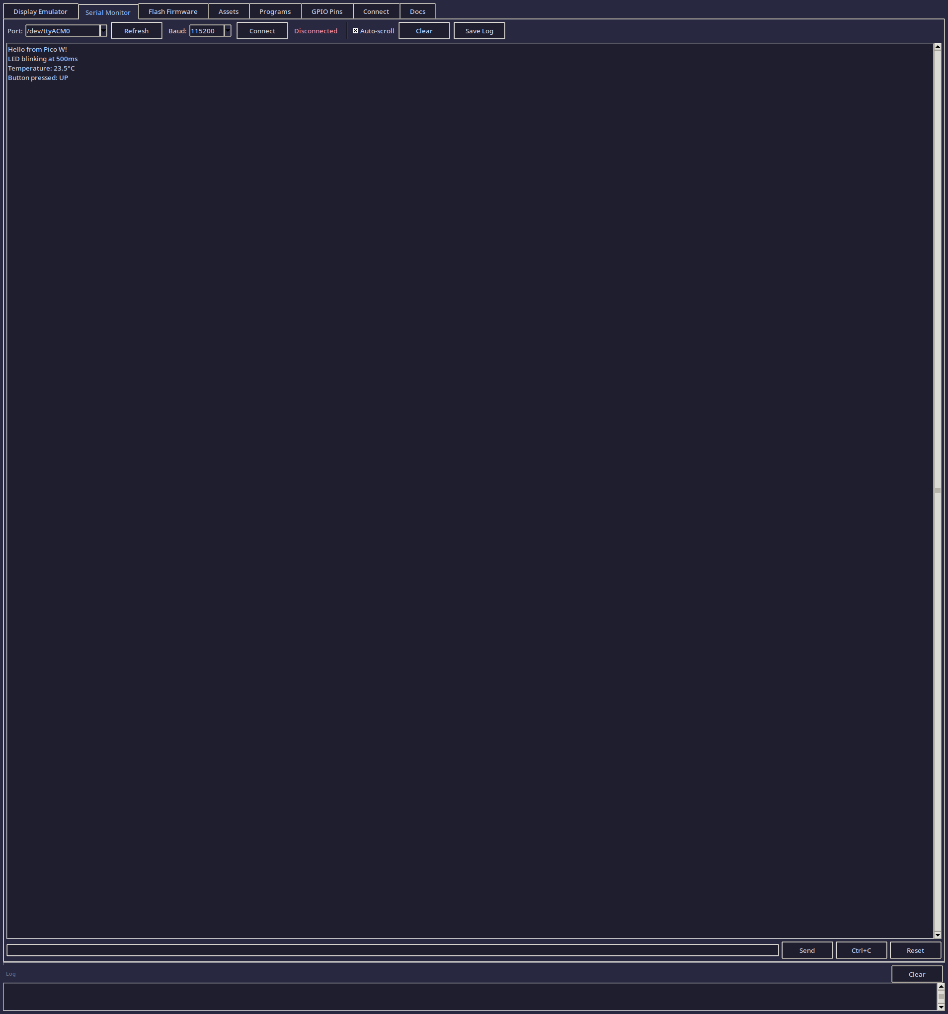
[picture p425: testing/devtool/screenshots/devtool_serial_with_output.png]
devtool_serial_with_output


## Tab

### Devtool Tab Asset Manager

Overview of the Asset Manager tab.

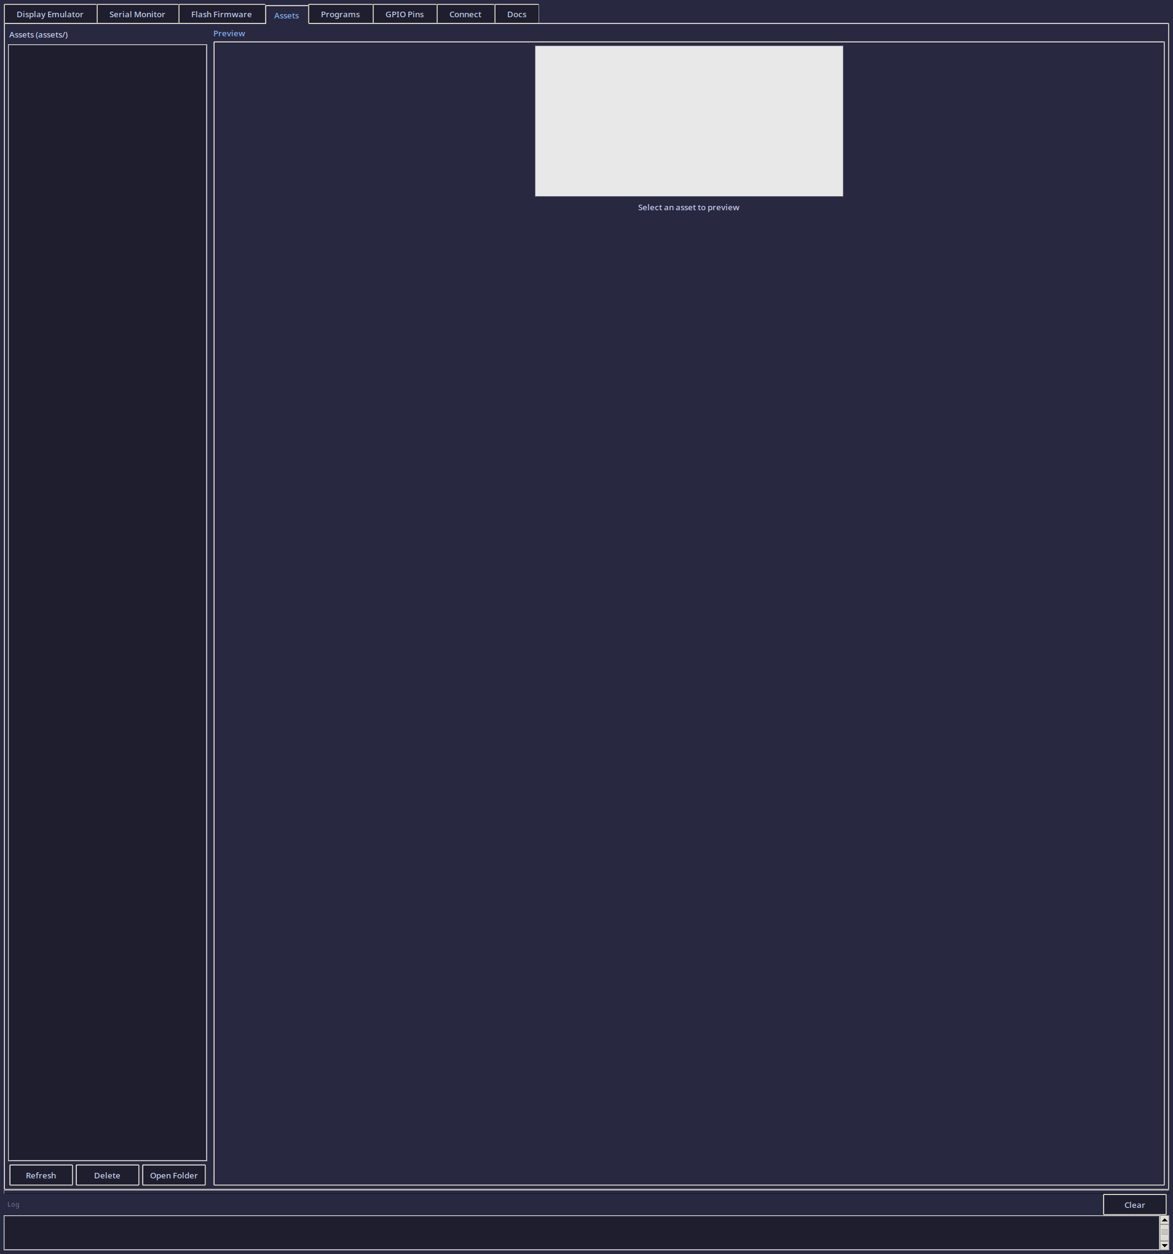
[picture p426: testing/devtool/screenshots/devtool_tab_asset_manager.png]
devtool_tab_asset_manager


### Devtool Tab Connection Utility

Overview of the Connection Utility tab.

devtool_tab_connection_utility

### Devtool Tab Display Emulator

Overview of the Display Emulator tab.

devtool_tab_display_emulator

### Devtool Tab Documentation

Overview of the Documentation tab.

devtool_tab_documentation

### Devtool Tab Flash Firmware

Overview of the Flash Firmware tab.

devtool_tab_flash_firmware

### Devtool Tab Gpio Pins

Overview of the GPIO Pins tab.

devtool_tab_gpio_pins

### Devtool Tab Programs

Overview of the Programs tab.

devtool_tab_programs

### Devtool Tab Serial Monitor

Overview of the Serial Monitor tab.

devtool_tab_serial_monitor
