rompasaurus/regardedPal/testing/guides/website_guide.md

# Dilder Website User Guide

> Auto-generated from 23 test screenshots.
> Re-run the test suite to update: `pytest website/ -m screenshot`

---

## Blog

### Website Blog Desktop

Screenshot: Website Blog Desktop

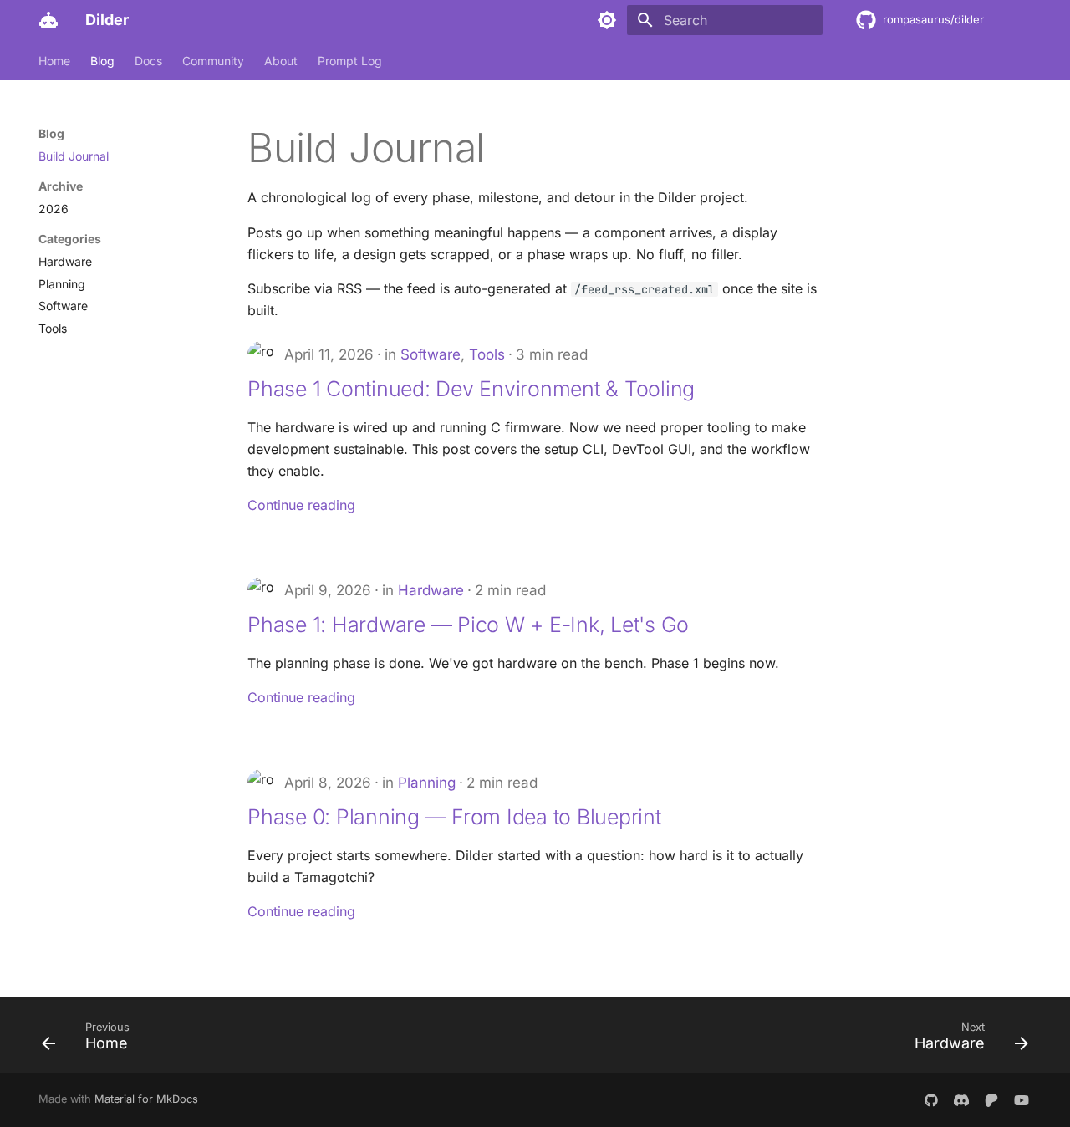
[picture p427: testing/website/screenshots/website_blog_desktop.png]
website_blog_desktop


### Website Blog Index

The blog index showing build series posts.

website_blog_index

### Website Blog Mobile

Screenshot: Website Blog Mobile

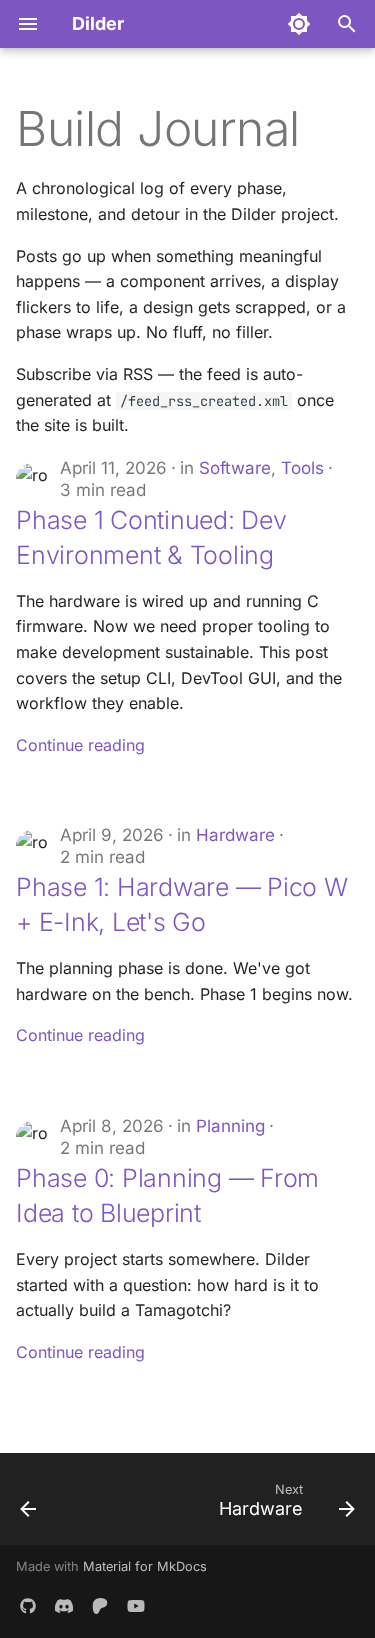
[picture p428: testing/website/screenshots/website_blog_mobile.png]
website_blog_mobile


### Website Blog Post

Screenshot: Website Blog Post

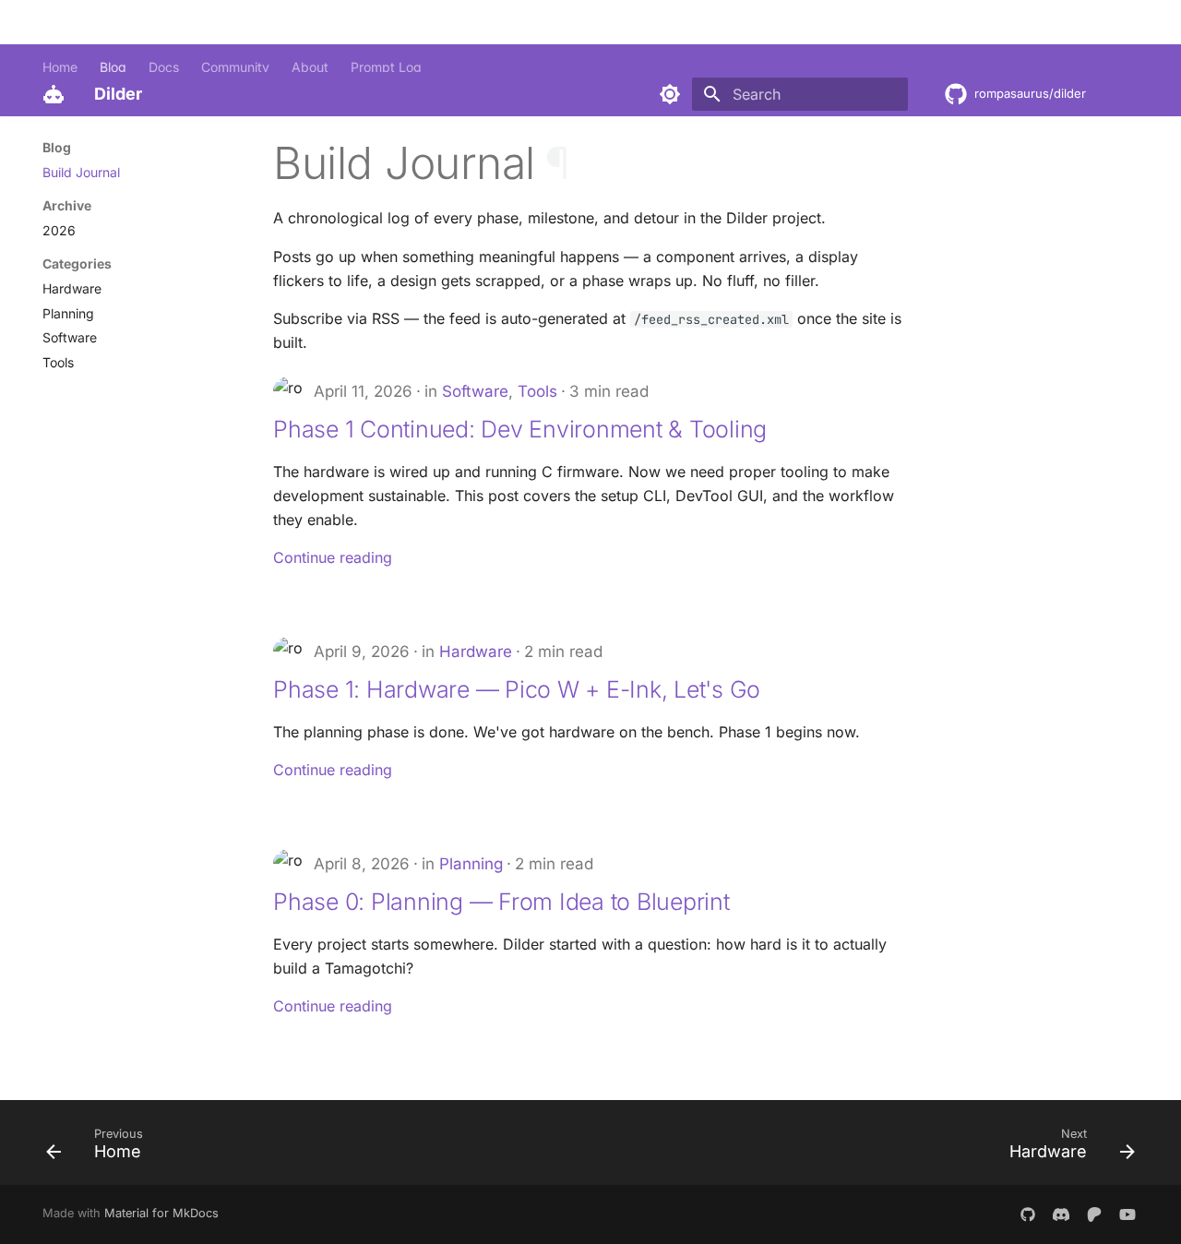
[picture p429: testing/website/screenshots/website_blog_post.png]
website_blog_post


### Website Blog Tablet

Screenshot: Website Blog Tablet

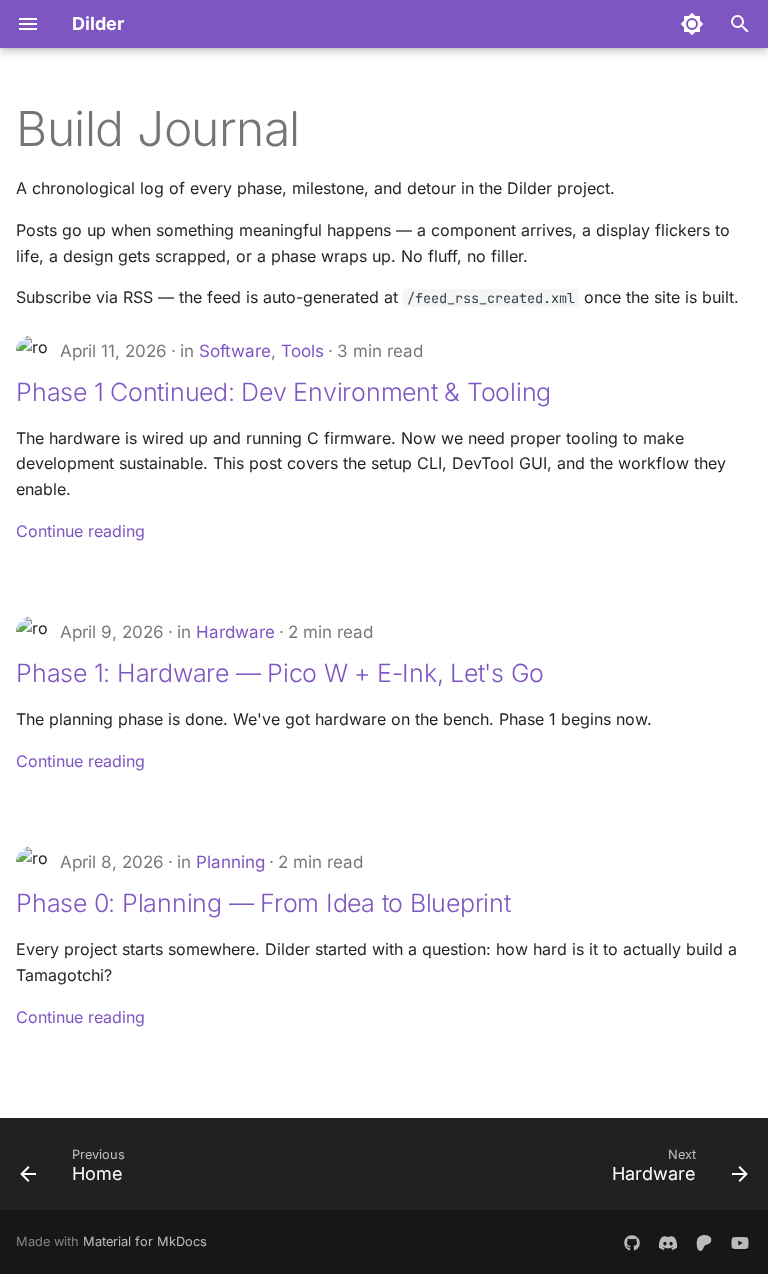
[picture p430: testing/website/screenshots/website_blog_tablet.png]
website_blog_tablet


## Doc

### Website Doc Docs Hardware Materials-List

Screenshot: Website Doc Docs Hardware Materials-List

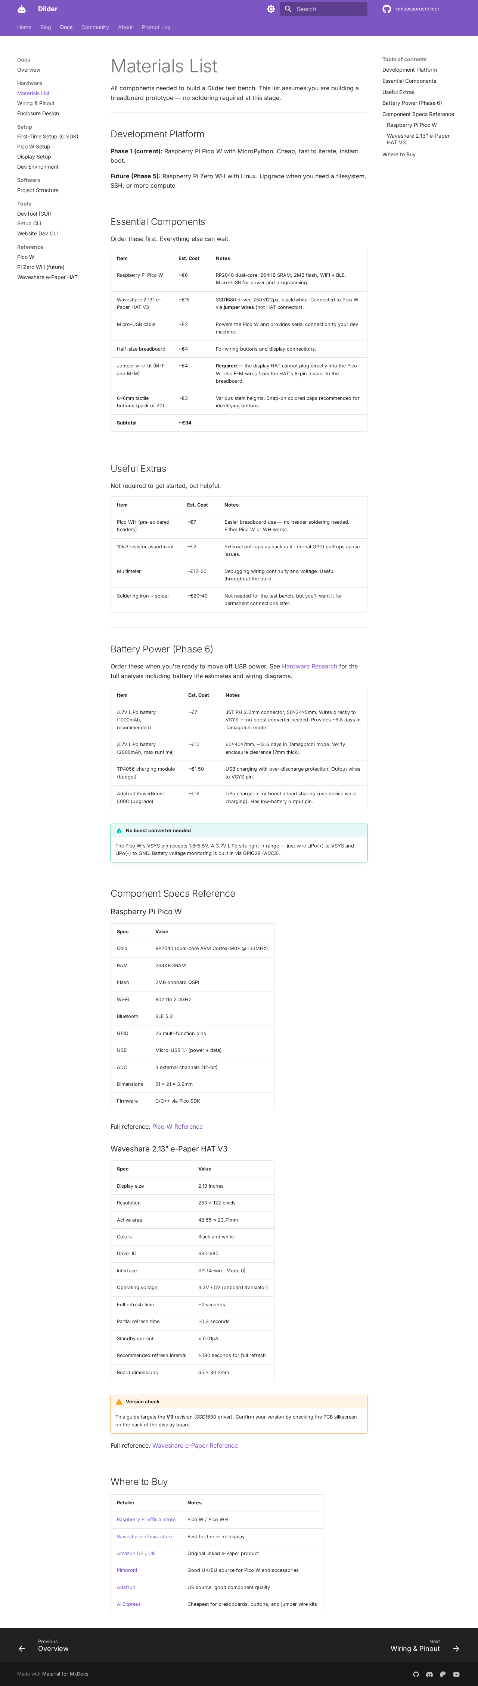
[picture p431: testing/website/screenshots/website_doc_docs_hardware_materials-list.png]
website_doc_docs_hardware_materials-list


### Website Doc Docs Hardware Wiring-Pinout

Screenshot: Website Doc Docs Hardware Wiring-Pinout

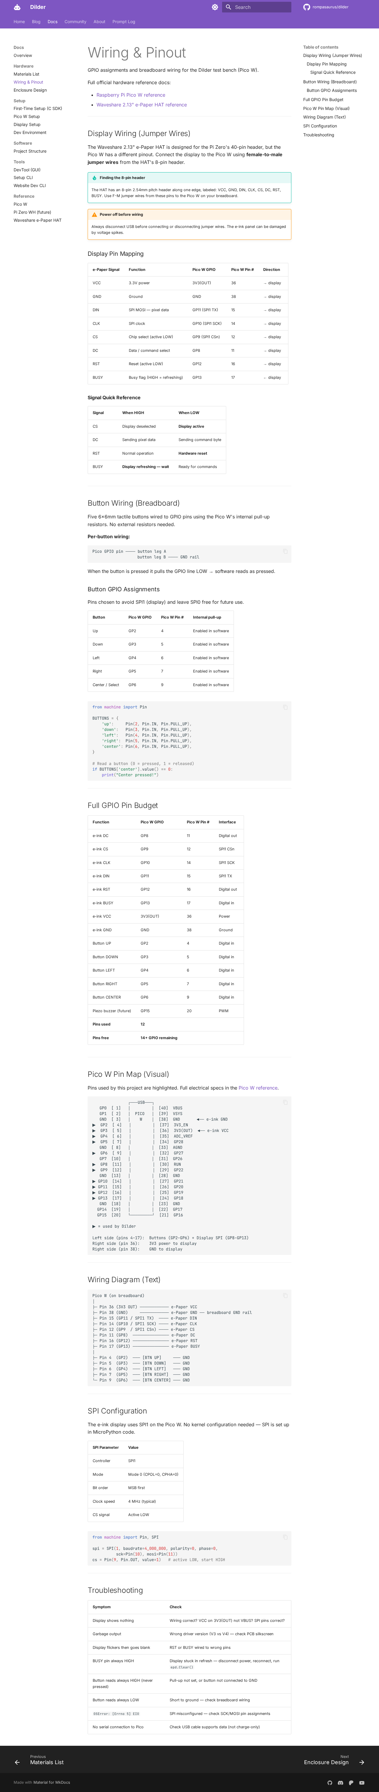
[picture p432: testing/website/screenshots/website_doc_docs_hardware_wiring-pinout.png]
website_doc_docs_hardware_wiring-pinout


### Website Doc Docs Setup First-Time-Setup

Screenshot: Website Doc Docs Setup First-Time-Setup

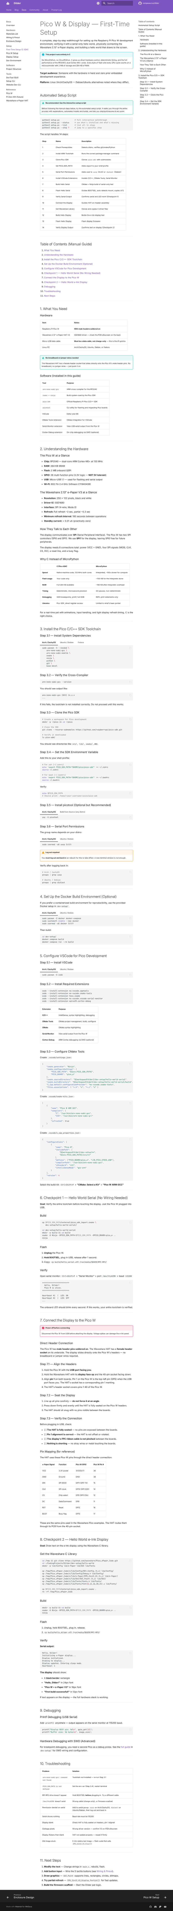
[picture p433: testing/website/screenshots/website_doc_docs_setup_first-time-setup.png]
website_doc_docs_setup_first-time-setup


### Website Doc Docs Software Project-Structure

Screenshot: Website Doc Docs Software Project-Structure

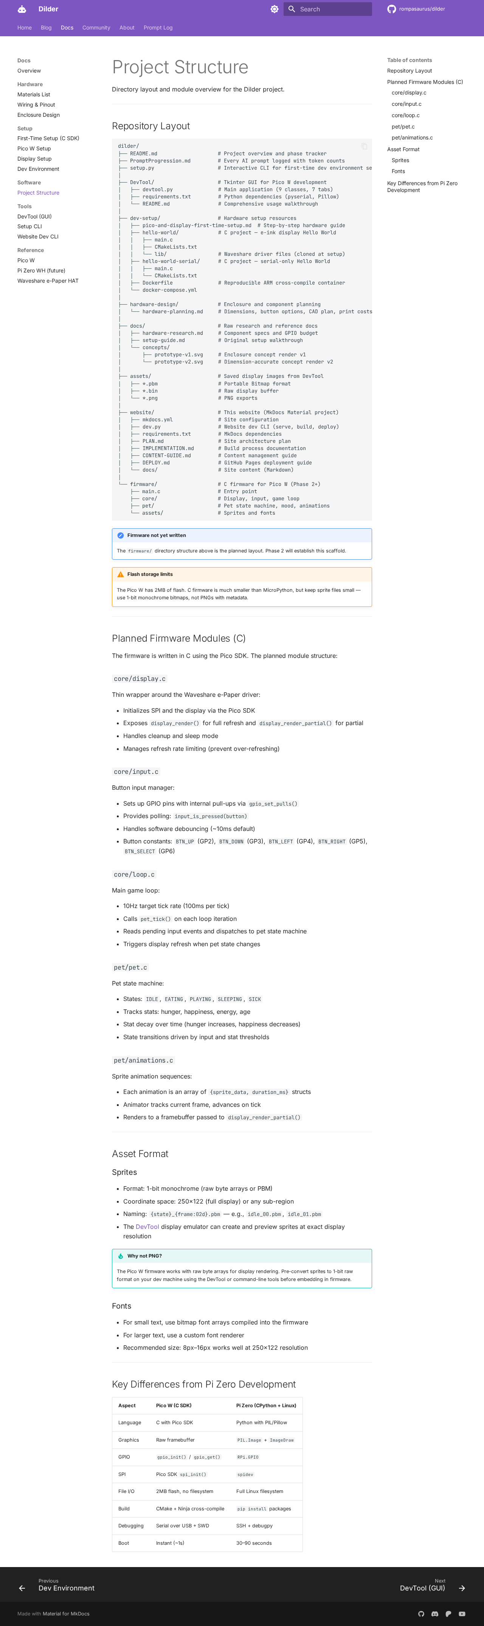
[picture p434: testing/website/screenshots/website_doc_docs_software_project-structure.png]
website_doc_docs_software_project-structure


### Website Doc Docs Tools Devtool

Screenshot: Website Doc Docs Tools Devtool

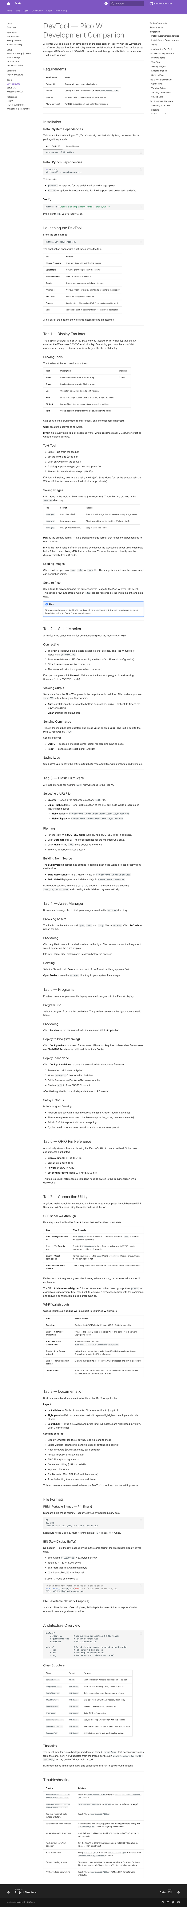
[picture p435: testing/website/screenshots/website_doc_docs_tools_devtool.png]
website_doc_docs_tools_devtool


### Website Doc Docs Tools Setup-Cli

Screenshot: Website Doc Docs Tools Setup-Cli

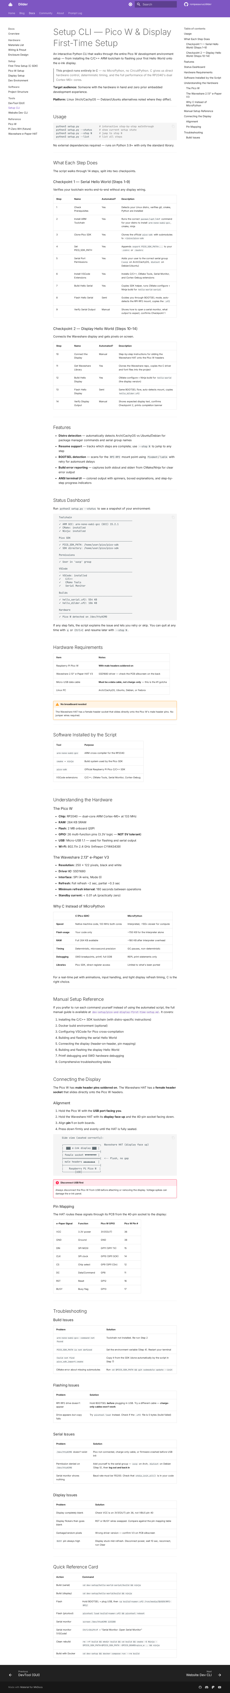
[picture p436: testing/website/screenshots/website_doc_docs_tools_setup-cli.png]
website_doc_docs_tools_setup-cli


## Docs

### Website Docs Desktop

Documentation at desktop resolution.

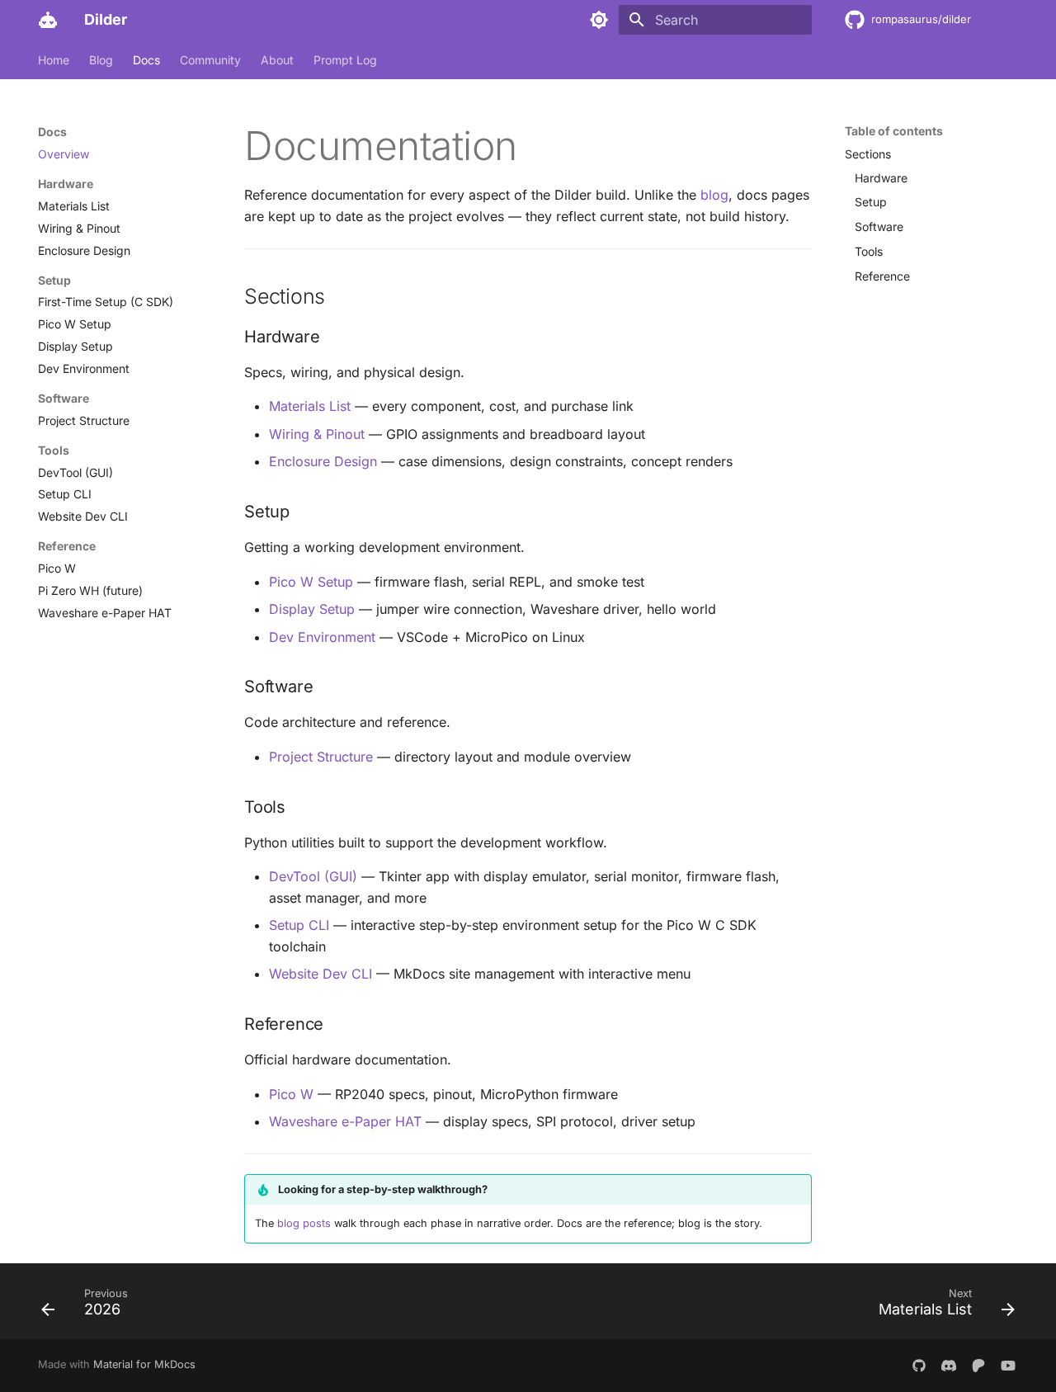
[picture p437: testing/website/screenshots/website_docs_desktop.png]
website_docs_desktop


### Website Docs Devtool

The DevTool documentation page on the website.

website_docs_devtool

### Website Docs Mobile

Documentation at mobile resolution.

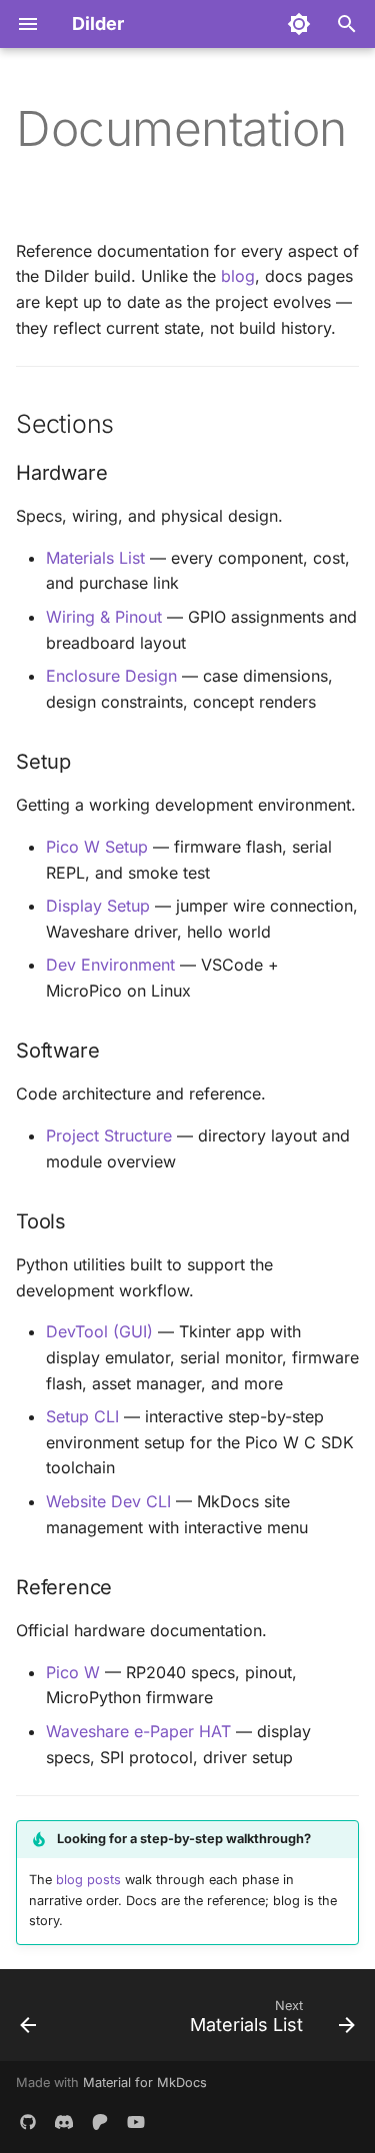
[picture p438: testing/website/screenshots/website_docs_mobile.png]
website_docs_mobile


### Website Docs Overview

The documentation overview page.

website_docs_overview

### Website Docs Setup Cli

The Setup CLI documentation page on the website.

website_docs_setup_cli

### Website Docs Tablet

Documentation at tablet resolution.

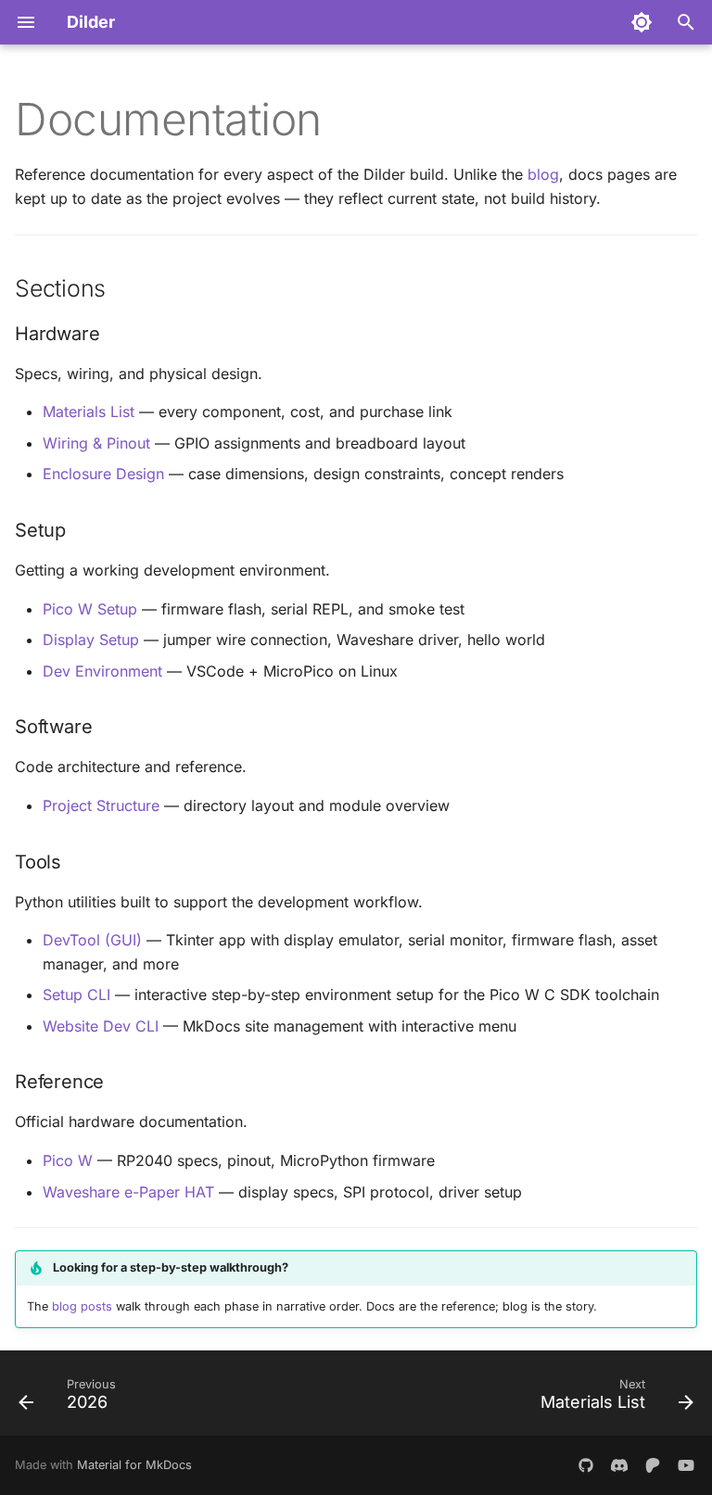
[picture p439: testing/website/screenshots/website_docs_tablet.png]
website_docs_tablet


## Home

### Website Home Desktop

Home page at desktop resolution (1280x800).

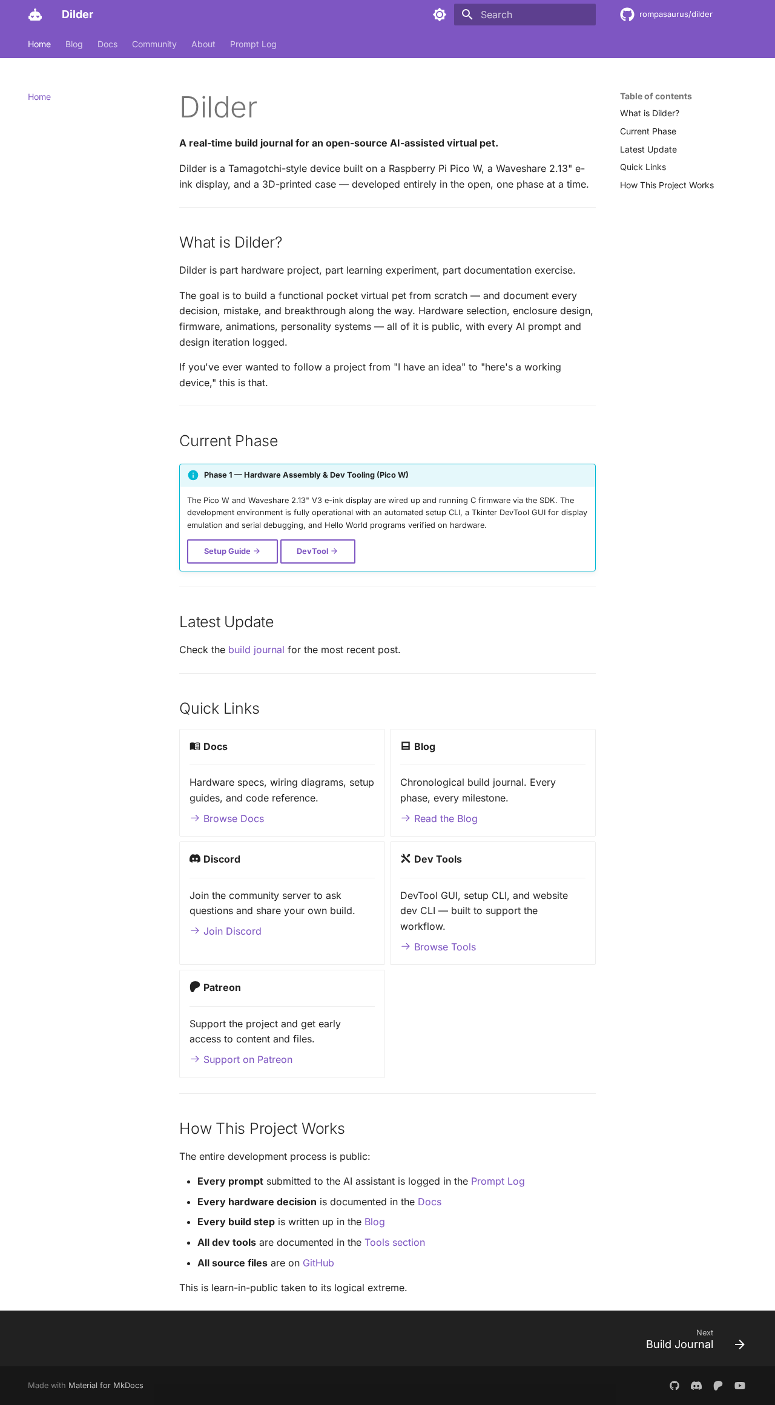
[picture p440: testing/website/screenshots/website_home_desktop.png]
website_home_desktop


### Website Home Mobile

Home page at mobile resolution (375x812).

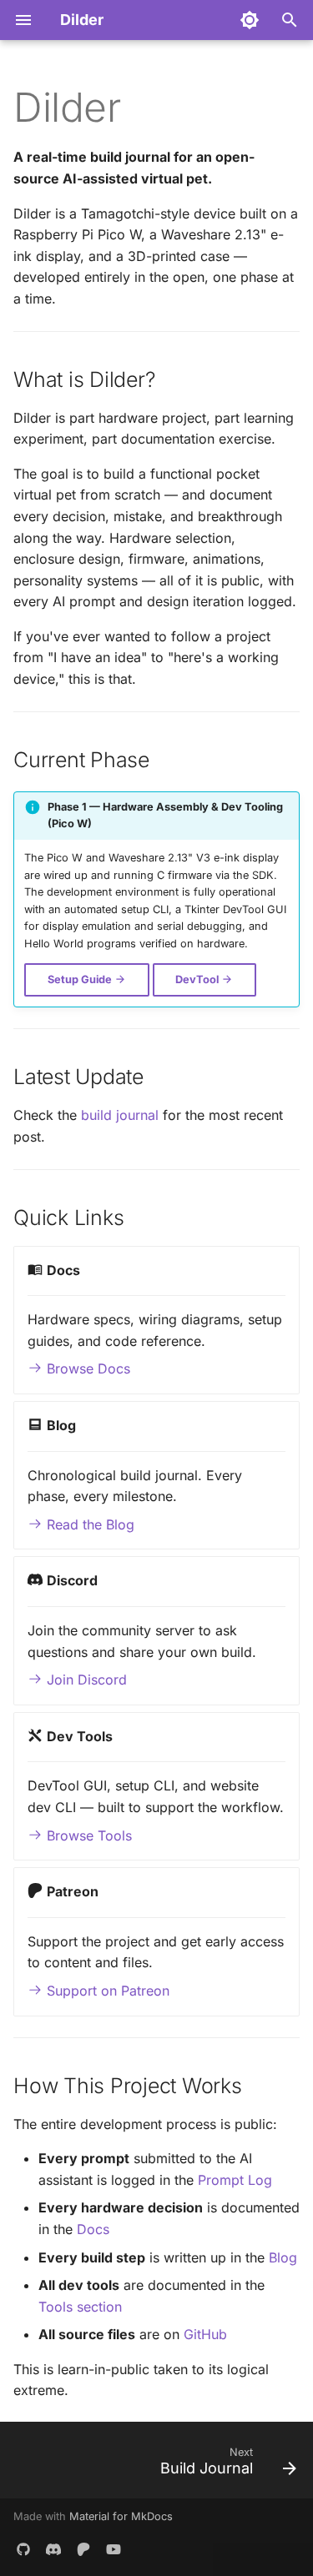
[picture p441: testing/website/screenshots/website_home_mobile.png]
website_home_mobile


### Website Home Page

The Dilder project home page.

website_home_page

### Website Home Tablet

Home page at tablet resolution (768x1024).

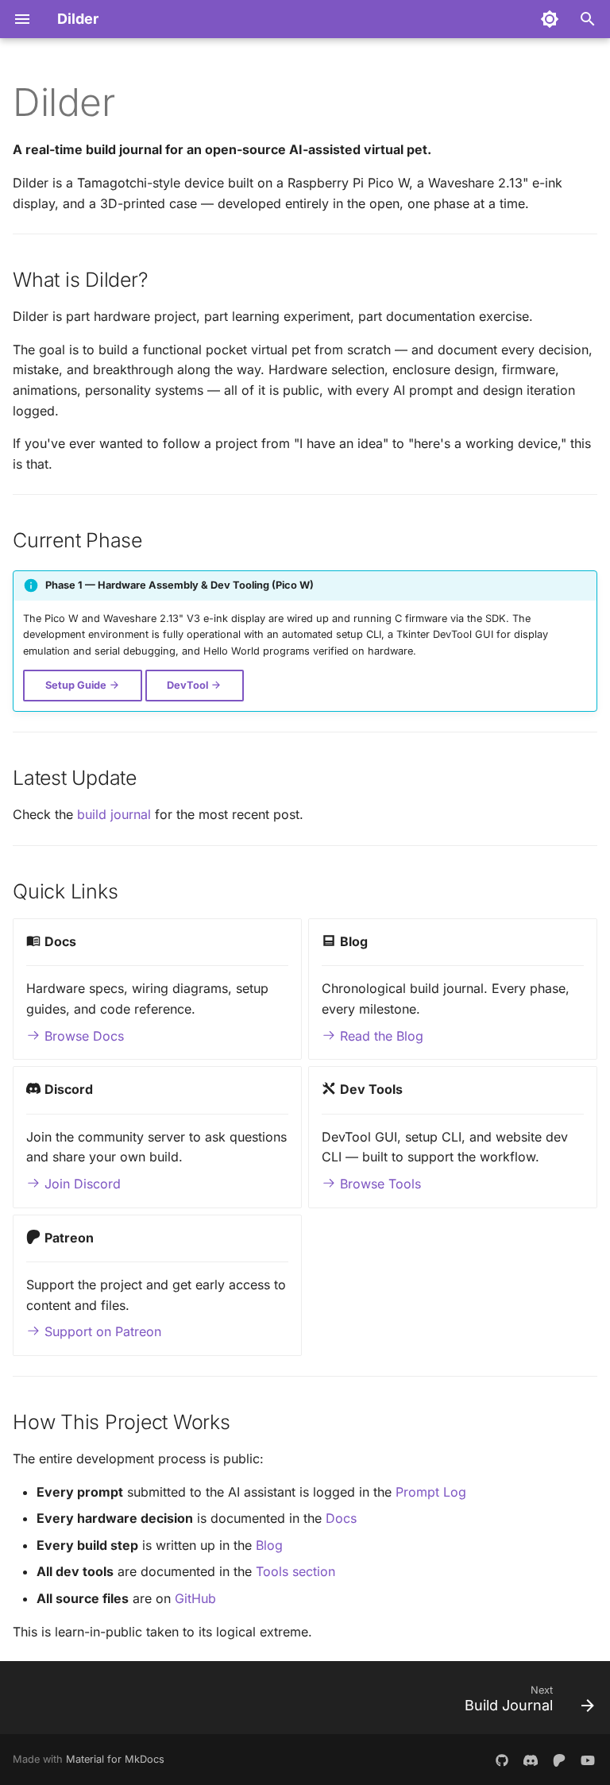
[picture p442: testing/website/screenshots/website_home_tablet.png]
website_home_tablet


## Reference

### Website Reference Pico W

The Pico W hardware reference page.

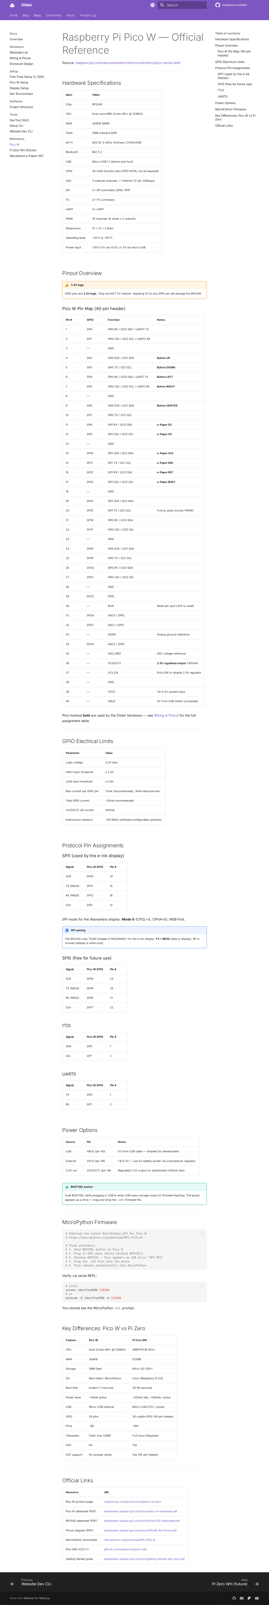
[picture p443: testing/website/screenshots/website_reference_pico_w.png]
website_reference_pico_w


## Search

### Website Search Results

Search results for 'Pico W' demonstrating the built-in search.

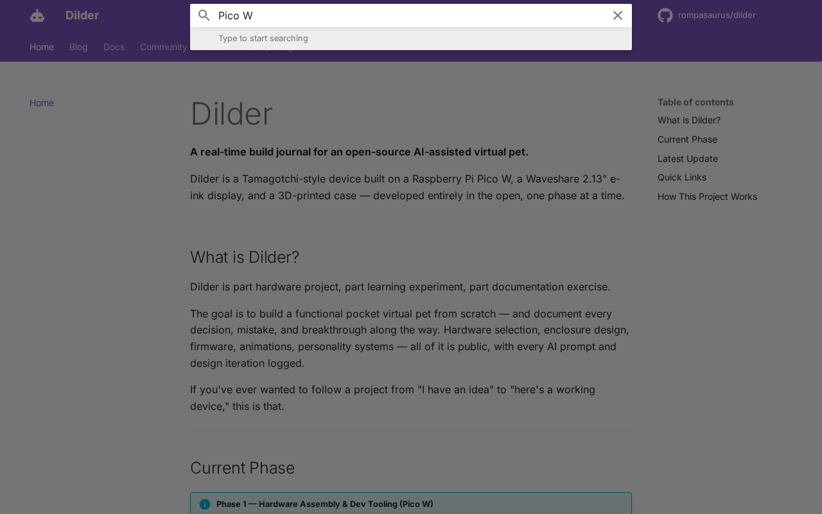
[picture p444: testing/website/screenshots/website_search_results.png]
website_search_results
