rompasaurus/regardedPal/website/docs/docs/design/user-guide.md

# Dilder User Guide

> The complete guide to raising, nurturing, and adventuring with your digital octopus companion.

---

## Table of Contents

### I. Introduction

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

### II. Getting to Know Your Octopus

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

### III. Caring for Dilder

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

### IV. The Physical World

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

### V. Growing Up

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

### VI. Progression & Collection

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

### VII. Achievements

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

### VIII. Environments & Scenes

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

### IX. Controls & Navigation

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

### X. Tips & Secrets

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

---

# I. Introduction

## 1. What Is Dilder?

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

The device runs on a custom PCB with an ESP32-S3 microcontroller, a 2.13" e-ink display (250x122 pixels, black and white), a 1000mAh battery, and sensors for touch, light, sound, temperature, humidity, and motion. Everything renders in real-time — no pre-baked sprites, no stored frames. The octopus is drawn mathematically, line by line, 60 times a minute.

All 16 emotions with aura effects

---

## 2. The Origin Story — Meet Jamal

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

We named him **Jamal**.

Jamal, the original octopus

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

Dilder is that answer. Named after... well, that's between us and Jamal.

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

---

## 3. Your First Hatch

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

**To hatch your octopus:**
- **Touch the device** — Hold the top of the case (head zone). Each touch adds progress.
- **Keep it warm** — A comfortable room temperature (18-24C) adds passive hatch progress.
- **Talk to it** — The microphone detects your voice. Talking to the egg helps it along.

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

Your tiny octopus blinks at the screen. It says its first word:

> "mama?"

Congratulations. You're a parent now.

---

# II. Getting to Know Your Octopus

## 4. The 16 Emotional States

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

### 4.1 Normal / Sassy

Normal emotion

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

> "MATTRESSES ARE BODY SHELVES."

**Triggered by:** All stats balanced, no extreme sensor inputs.

### 4.2 Hungry

Hungry emotion

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

> "hungwy..." (Hatchling)
> "I can't... eat... another... *burp*" (when overfed)

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

### 4.3 Tired

Tired emotion

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

> "Five more minutes? The dark is so... dark."

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

### 4.4 Sad

Sad emotion

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

> "I was starting to think you forgot about me..."

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

### 4.5 Angry

Angry emotion

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

> "...that was loud. Are you okay?"

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

### 4.6 Excited

Excited emotion

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

> "We did it! 5,000 steps! My tentacles are BURNING."

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

### 4.7 Chill

Chill emotion

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

> "You know what? Life is good. Really good."

**Triggered by:** All stats > 60 in a calm environment (low noise, comfortable temperature).

### 4.8 Lazy

Lazy emotion

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

> "Whatever."

**Triggered by:** Energy 15-30 with no interaction for 2+ hours, or overweight.

### 4.9 Fat

Fat emotion

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

> "I can't... eat... another... *burp*"

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

### 4.10 Chaotic

Chaotic emotion

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

> (No coherent quotes — just chaos)

**Triggered by:** 5+ events in 30 seconds, or simultaneous shaking + loud noise + touch. Very short dwell (10 seconds).

### 4.11 Weird

Weird emotion

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

> "Do fish know they're wet?"

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

### 4.12 Unhinged

Unhinged emotion

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

> (Distressed vocalizations only)

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

### 4.13 Slap Happy

Slap Happy emotion

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

> "HAHAHAHA I'M FINE I'M TOTALLY FINE"

**Triggered by:** Happiness > 90 after recently being < 30. The relief of recovery expressed as manic joy.

### 4.14 Horny

Horny emotion

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

> (Context-appropriate flirtatious quotes)

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

### 4.15 Nostalgic

Nostalgic emotion

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

> "Remember when I was just a hatchling? You were so attentive back then..."

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

### 4.16 Homesick

Homesick emotion

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

> "I miss the armchair..."

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

---

## 5. Reading the Display

The e-ink screen is divided into three zones:

```
┌──────────────────────────────────────────────────┐  
│ 12:34 PM          [HUN][HAP][ENE][HYG][HEA]     │  Header (16px)
├──────────────────────────────────────────────────┤  
│                                                  │
│              YOUR OCTOPUS                        │  Pet Area (80px)
│              + equipped decor                    │
│                                                  │
├──────────────────────────────────────────────────┤  
│ "Good morning! I had the strangest dream..."     │  Dialogue (26px)
└──────────────────────────────────────────────────┘  
```

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

---

# III. Caring for Dilder

## 6. The Stat System

### 6.1 Primary Stats

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

### 6.2 Secondary Stats

These accumulate over your octopus's lifetime and determine its evolution:

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

### 6.3 Hidden Stats

You can't see these directly, but they shape everything:

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

### 6.4 Stat Decay & Modifiers

Stat decay isn't constant — it's modified by context:

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

---

## 7. Care Actions

### 7.1 Feeding

Open the menu → **Feed**:

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

### 7.2 Cleaning

Open the menu → **Care** → **Clean**:
- +40 Hygiene
- 60-second cooldown
- +5 Bond XP

### 7.3 Playing

Open the menu → **Play**:

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

Mini-games are the primary way to manage weight and boost happiness simultaneously.

### 7.4 Medicine

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

### 7.5 Scolding & Discipline

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

### 7.6 Sleep

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

**Wake triggers:** Bright light, touch, loud noise, significant motion (picked up), or energy reaching 95.

---

## 8. The Daily Rhythm

```
  MORNING (6am-10am)
  ┌──────────────────────────────────────┐
  │ Dilder wakes with the light          │
  │ Morning greeting based on mood       │
  │ Feed (hunger decayed overnight)      │
  │ Pet/interact for happiness boost     │
  └──────────────────────────────────────┘
              │
              ▼
  DAYTIME (10am-6pm)
  ┌──────────────────────────────────────┐
  │ Carry Dilder — steps tracked         │
  │ Locations detected (WiFi)            │
  │ Environmental sensing (light, temp)  │
  │ Periodic dialogue check-ins          │
  │ Random events (10% daily chance)     │
  └──────────────────────────────────────┘
              │
              ▼
  EVENING (6pm-10pm)
  ┌──────────────────────────────────────┐
  │ Feed again (hunger decayed)          │
  │ Review daily activity summary        │
  │ Play / interact for happiness        │
  │ Unlock rewards from step targets     │
  └──────────────────────────────────────┘
              │
              ▼
  BEDTIME (10pm-6am)
  ┌──────────────────────────────────────┐
  │ Lights dim → Dilder gets tired       │
  │ Place in dark → auto-sleep           │
  │ Low power mode                       │
  │ Stats decay slowly overnight         │
  │ Energy regenerates                   │
  └──────────────────────────────────────┘
```

---

# IV. The Physical World

## 9. Sensor Interactions

Dilder doesn't just live on a screen — it senses the real world around it.

### 9.1 Voice & Sound

The microphone (MAX9814) detects volume and patterns — not words (no speech recognition on the microcontroller):

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

### 9.2 Light & Darkness

The BH1750 light sensor reads ambient light:

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

### 9.3 Temperature & Humidity

The AHT20 sensor reads the environment:

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

### 9.4 Motion & Movement

The LIS2DH12TR accelerometer tracks:

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

---

## 10. Step Tracking & Activity

### 10.1 Daily Step Targets

Every step you take with Dilder counts. Progressive daily goals unlock escalating rewards:

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

The step screen shows your progress:
```
┌──────────────────────────────────────┐
│  Today's Steps: 6,247                │
│  ██████████████░░░░░ 8,000 Gold      │
│                                      │
│  [check] Bronze  (2,000)             │
│  [check] Silver  (5,000)             │
│  [    ] Gold    (8,000) — 1,753 to go│
│  [    ] Platinum (12,000)            │
│  [    ] Diamond  (20,000)            │
└──────────────────────────────────────┘
```

### 10.2 Weekly Targets

Accumulate across the week (Monday–Sunday):

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

### 10.3 Monthly Targets

The "big goals" that drive long-term engagement:

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

### 10.4 The Streak System

Meet the Bronze daily target (2,000 steps) to keep your streak alive:

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

---

## 11. Location & Exploration

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

---

# V. Growing Up

## 12. Life Stages

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

### 12.1 Egg
**Duration:** Day 0-1

A wobbling egg on screen. No stats, no emotions. Just warmth, touch, and patience. Cracks appear at 25%, 50%, 75% progress. Hatches at 100%.

### 12.2 Hatchling
**Duration:** Day 1-3

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

4 misbehavior windows open during this stage for discipline.

### 12.3 Juvenile
**Duration:** Day 3-7

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

> "What's out there?" / "Are you my person?"

### 12.4 Adolescent
**Duration:** Day 7-14

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

> "Whatever." / "You don't understand me." / "Leave me alone... wait, don't."

### 12.5 Adult
**Duration:** Day 14-30

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

### 12.6 Elder
**Duration:** Day 30+

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

> "My tentacles may be slower, but my hearts are fuller."

---

## 13. Evolution — The Six Adult Forms

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

All outfits grid

### 13.1 Deep-Sea Scholar
**Requirements:** High intelligence + high bond + moderate discipline

Glasses, a book, a contemplative pose. Philosophical, verbose quotes. The intellectual octopus.

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

### 13.2 Reef Guardian
**Requirements:** High fitness + high exploration + balanced stats

Muscular tentacles, a coral crown. Adventurous and encouraging.

> "Let's see what's over the next hill. And the one after that."

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

### 13.3 Tidal Trickster
**Requirements:** Low discipline + high happiness + chaotic care pattern

Jester hat, mischievous grin. Chaotic, unpredictable, hilarious.

> "Rules are just suggestions written by people with no imagination."

**How to evolve:** Keep happiness high, ignore discipline windows, care unpredictably (sometimes neglect, sometimes smother).

### 13.4 Abyssal Hermit
**Requirements:** High discipline + low social interaction + self-sufficient

A cloak, dim eyes, stoic presence. Rare but profound dialogue.

> "..."
> (Abyssal Hermit speaks only when it matters.)

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

### 13.5 Coral Dancer
**Requirements:** High happiness + lots of music/singing exposure + creative

Flowing ribbons, graceful animations. Artistic and poetic.

> "Every ripple in the water is a note in a song only the ocean knows."

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

### 13.6 Storm Kraken
**Requirements:** Lots of scolding + high anger exposure + survived

Larger body, intimidating visual, powerful presence. Tough but loyal.

> "You think that's a storm? I've BEEN a storm."

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

---

## 14. Rebirth & Legacy

After day 30 (Elder stage), you can choose:

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

This creates generational lineage: "My 3rd-generation Deep-Sea Scholar, descended from a Storm Kraken."

---

# VI. Progression & Collection

## 15. Bond Levels

Every interaction earns Bond XP. Your bond level determines which features are available:

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

---

## 16. The Dialogue System

Dilder's vocabulary grows with intelligence and life stage:

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

---

## 17. Decor & Cosmetics

4 equip slots for customizing your octopus:

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

All environments

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

All decor props

---

## 18. Treasure Hunts

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

**Treasure types:**

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

Treasures expire after 24 hours if uncollected.

---

# VII. Achievements

## 19. Achievement System Overview

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

The achievement screen shows unlocked badges with descriptions. Locked achievements show "???" until you uncover them.

---

## 20. Care Achievements

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

---

## 21. Exploration Achievements

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

---

## 22. Social Achievements

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

---

## 23. Environmental Achievements

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

---

## 24. Mastery Achievements

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

---

## 25. Step Achievements

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

---

## 26. Secret Achievements

These are hidden — they only appear after you discover them.

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

*There are more secrets. Keep exploring.*

---

# VIII. Environments & Scenes

## 27. The 22 Environments

Dilder's world extends beyond the octopus itself. Unlockable environments change the background behind your pet:

All environments grid

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

**Land-Inspired:** City skyline, cozy room, park, library, mountain peak.

**Atmospheric:** Starry night, sunset, aurora, thunderstorm, fog, moonlit tide.

**Special:** The Armchair (Jamal's home — unlocked at Bond level 8).

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

---

## 28. Outfits & Decor Props

All outfits grid

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

All decor props

---

## 29. Aura & Particle Effects

Each emotion has a unique aura — particle effects that emanate from the octopus:

Emotions with auras

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

---

# IX. Controls & Navigation

## 30. Button Layout

```
    [UP]

[BACK]  [SELECT]  [ACTION]

    [DOWN]
```

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

---

## 31. Menu System

Long-press SELECT to open:

```
Main Menu
├── Feed
│   ├── Meal (+30 hunger, +1 weight)
│   ├── Snack (+10 hunger, +15 happiness, +2 weight)
│   └── Treat (+5 hunger, +25 happiness, +3 weight) [Bond 4+]
├── Play
│   ├── Mini-game (+20 happiness, -10 energy, -1 weight)
│   └── Tickle (+5 happiness, quick)
├── Care
│   ├── Clean (+40 hygiene)
│   ├── Medicine (+20 health) [Only when sick]
│   └── Light (sleep toggle)
├── Stats
│   ├── Health meters (all 5 bars)
│   ├── Bond level & XP progress
│   ├── Today's activity (steps, distance)
│   ├── Achievements
│   └── Memorial (rebirth history)
├── Decor [Bond 3+]
│   ├── Hats
│   ├── Backgrounds
│   ├── Accessories
│   └── Animation Styles
└── Settings
    ├── Sound (beeper on/off)
    ├── Time display
    └── Brightness
```

---

## 32. Quick Actions

Without opening the menu:
- **Short press ACTION:** Context-sensitive care — feeds if hungry, pets otherwise
- **Double press ACTION:** Quick stats overlay (disappears after 5 seconds)
- **Touch any zone:** Pet response (no button needed)
- **Talk to Dilder:** Automatic — mic always listening

---

# X. Tips & Secrets

## 33. Beginner Tips

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

## 34. Advanced Strategies

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

## 35. Easter Eggs & Hidden Features

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

---

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
