rompasaurus/regardedPal/hardware-design/renders/assembly-with-pico-front.png

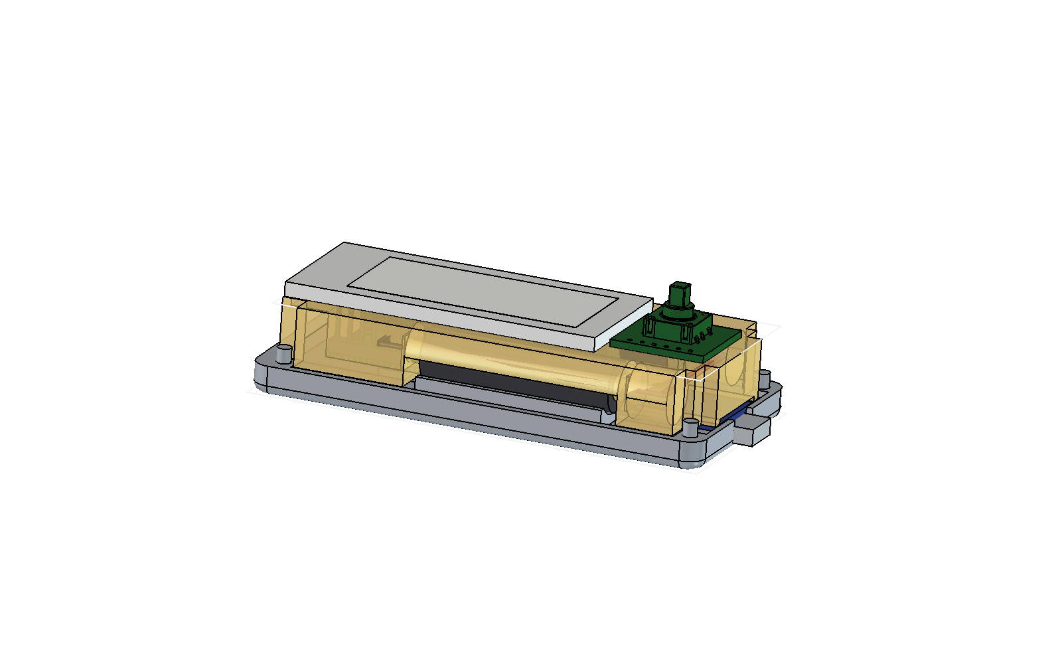
hardware-design/renders/assembly-with-pico-front.png
