rompasaurus/regardedPal/website/docs/assets/images/enclosure/assembly-with-pico-iso.png

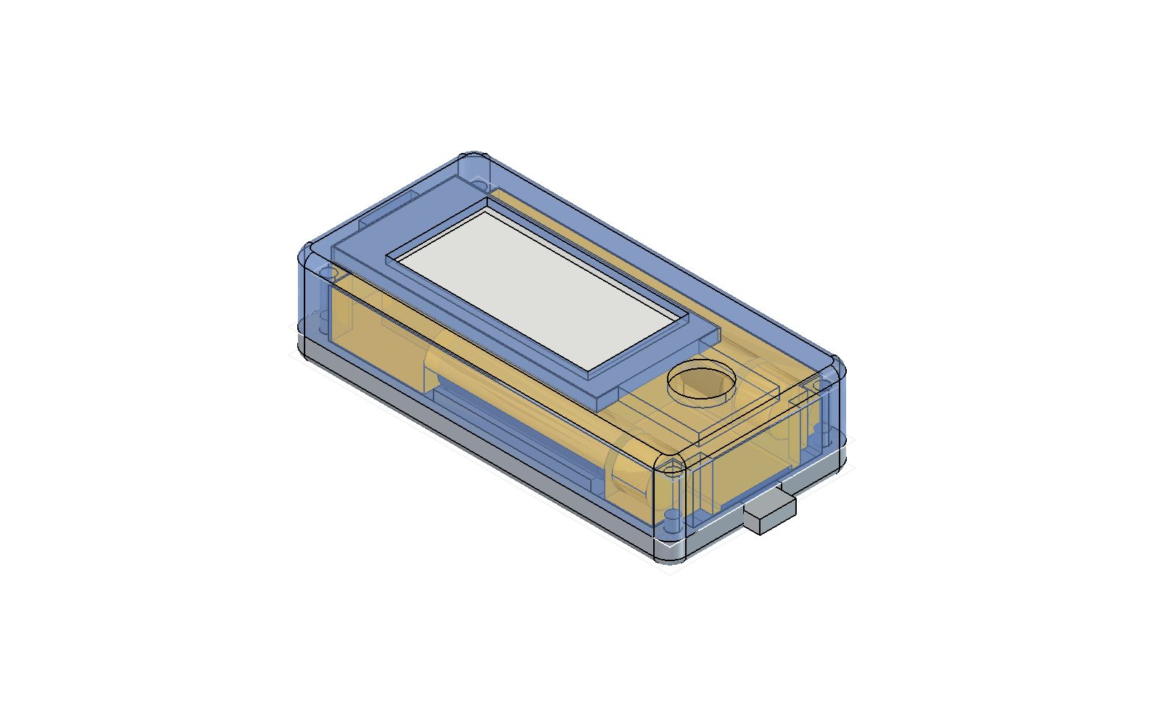
website/docs/assets/images/enclosure/assembly-with-pico-iso.png
