rompasaurus/regardedPal/website/docs/assets/images/hardware/handwritten-todo-list-week3-20260504.jpg

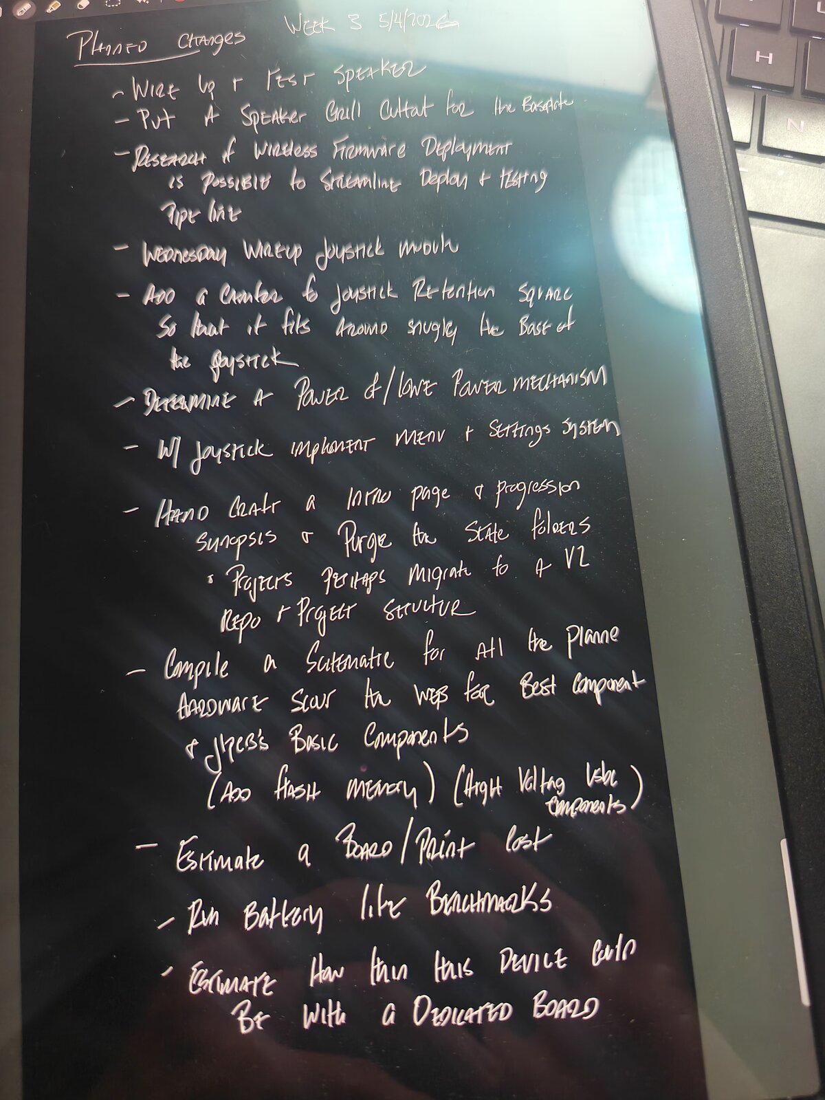
website/docs/assets/images/hardware/handwritten-todo-list-week3-20260504.jpg
