rompasaurus/regardedPal/website/docs/assets/images/tools/designtool/designtool-tab-history.png

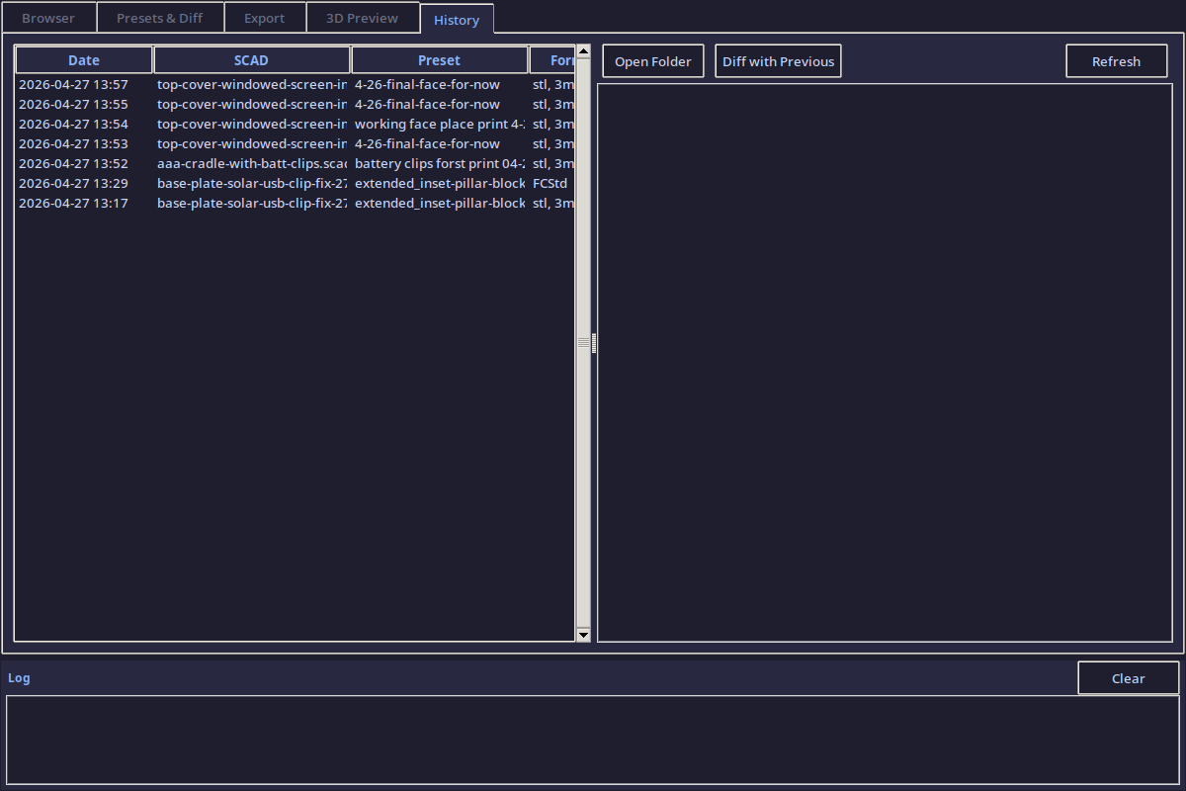
website/docs/assets/images/tools/designtool/designtool-tab-history.png
