rompasaurus/regardedPal/hardware-design/reference-boards/rp2040-designguide/PCB/RP2040-Guide.pdf

1 GPIO8 11 GPIO9 12 GPIO10 13 GPIO11 14 GPIO12 15 GPIO13 16 GPIO14 17 GPIO15 18 TESTEN 19 GPIO0 2 XTAL_IN 20 XTAL_OUT 21 SWCLK 24 SWDIO 25 ~{RUN} 26 GPIO16 27 GPIO17 28 GPIO18 29 GPIO1 3 GPIO19 30 GPIO20 31 GPIO21 32 GPIO22 34 GPIO23 35 GPIO24 36 GPIO25 37 GPIO26/ADC0 38 GPIO27/ADC1 39 GPIO2 4 GPIO28/ADC2 40 GPIO29/ADC3 41 ADC_AVDD 43 VREG_VIN 44 VREG_VOUT 45 D- 46 D+ 47 USB_VDD 48 GPIO3 5 DVDD 50 QSPI_SD3 51 QSPI_SCLK 52 QSPI_SD0 53 QSPI_SD2 54 QSPI_SD1 55 QSPI_SS_N 56 GND 57 GPIO4 6 GPIO5 7 GPIO6 8 GPIO7 9 U3 GND RP2040 +3.3V C6

File: RP2040-Guide.kicad_sch Sheet: / Sleepdealer

Id: 1/1 Title: RP2040 - Design Guide
