rompasaurus/regardedPal/hardware-design/examples/02-lilka-console/docs/_gen/v2_pcb.pdf

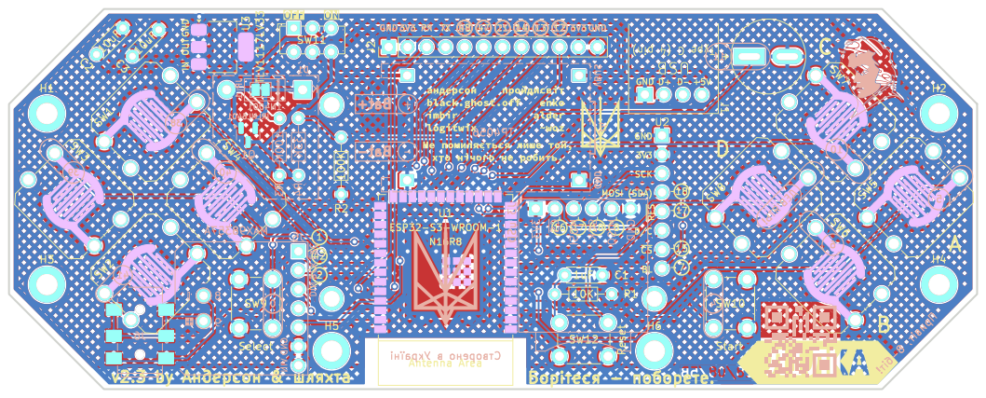
[picture p451: page 1]

Id: 1/1 Title: File: main.kicad_pcb Sheet:
