rompasaurus/regardedPal/hardware-design/examples/02-lilka-console/docs/_gen/v2_schematic.pdf

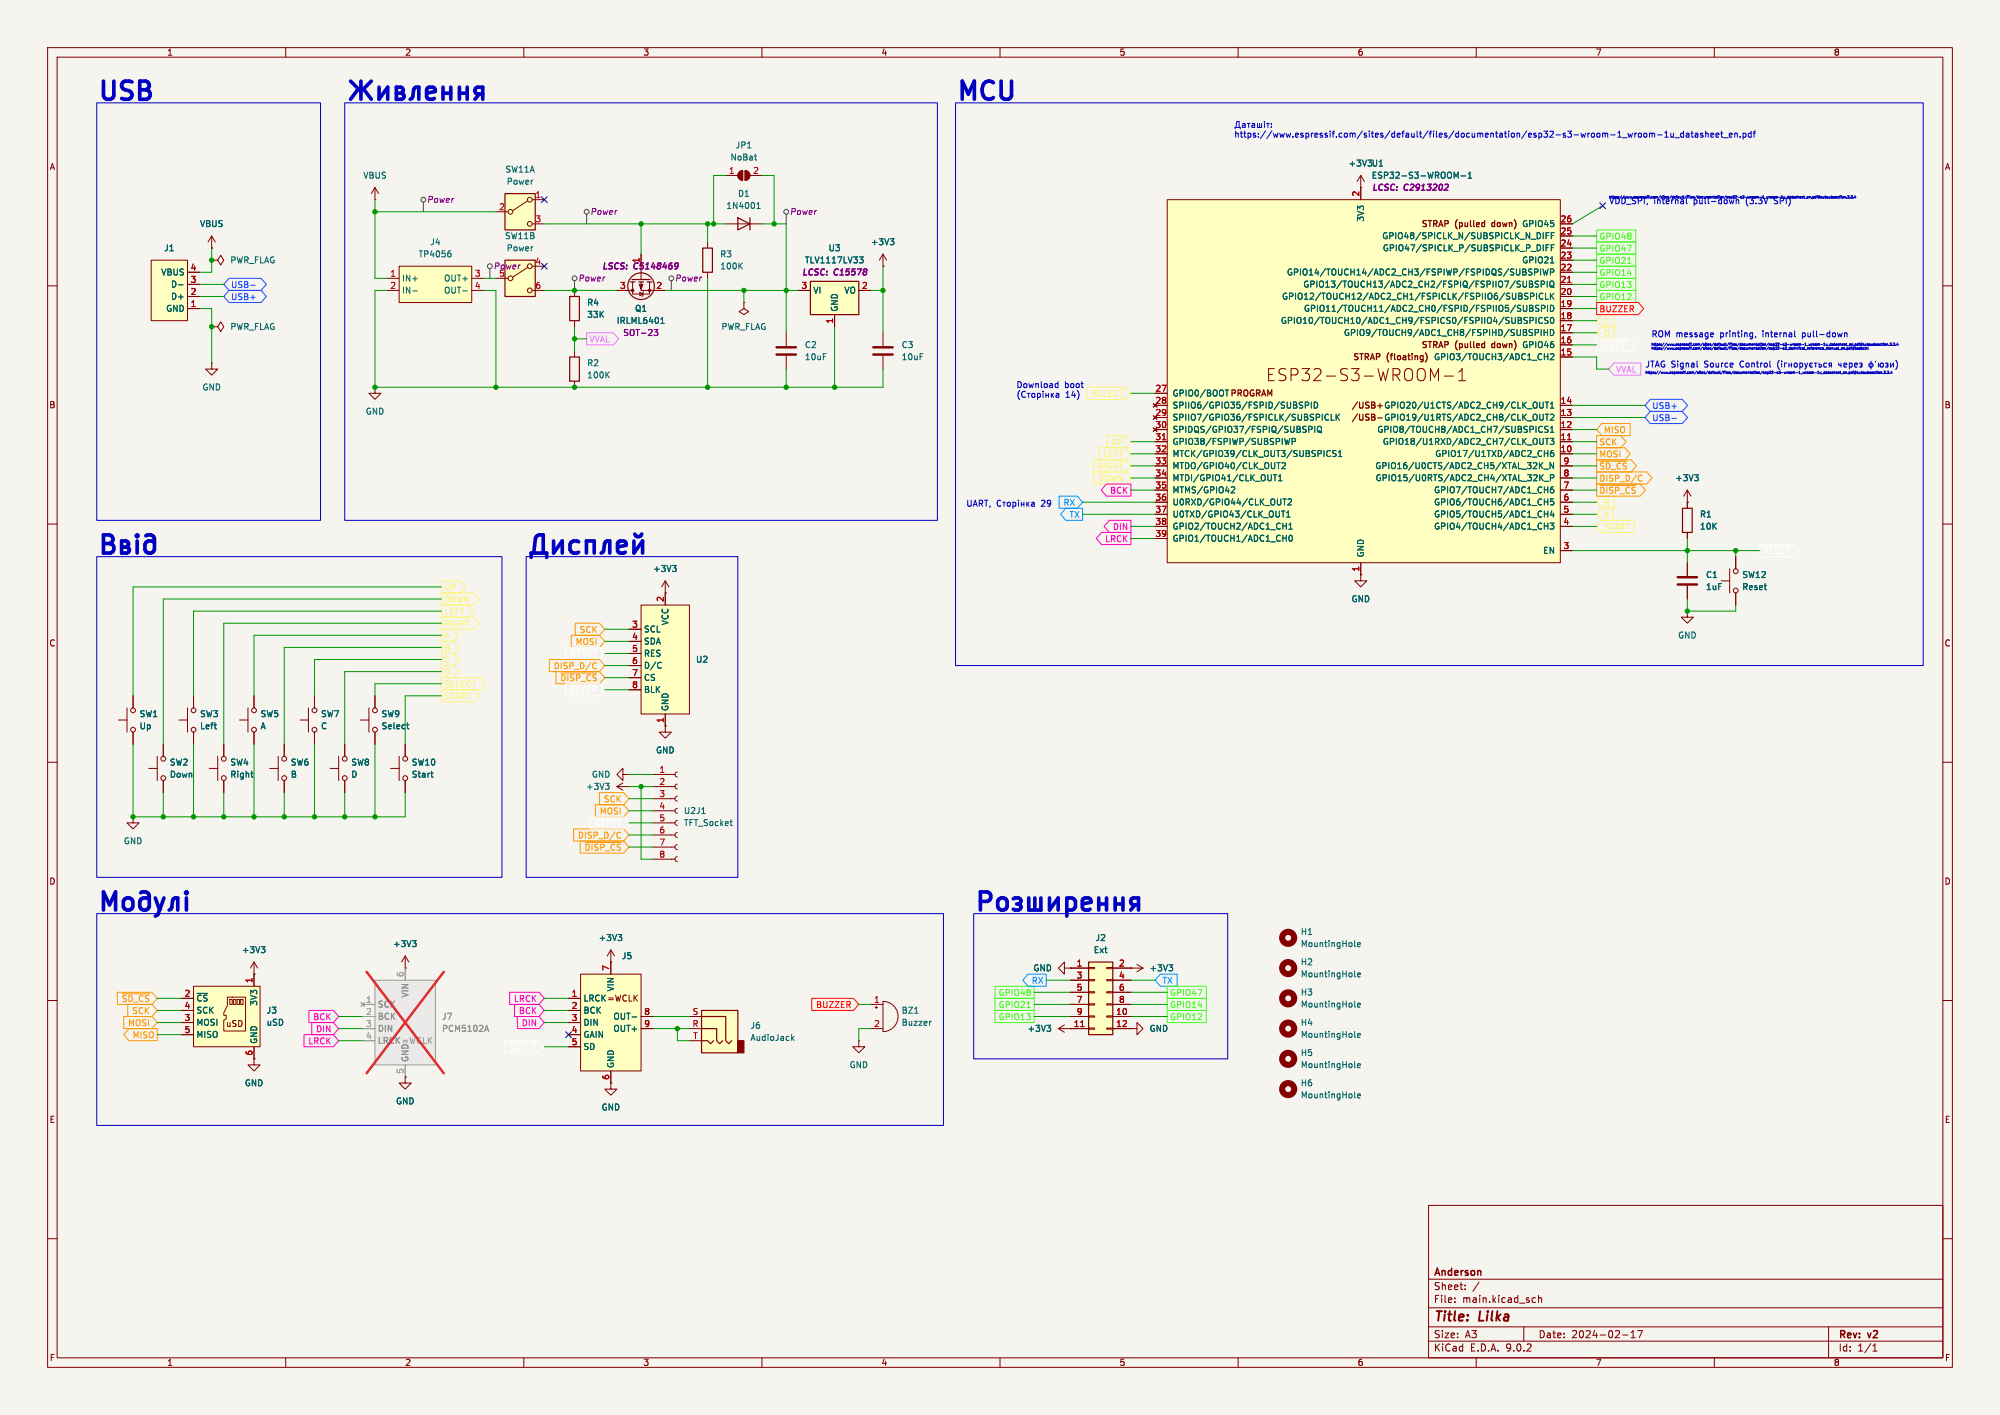
[picture p452: page 1]

Download boot þÿ(!B>@V=:0 14) UART, þÿ!B>@V=:0 29 MCU

https://www.espressif.com/sites/default/files/documentation/esp32-s3-wroom-1_wroom-1u_datasheet_en.pdf

1 GPIO45 26 GPIO48/SPICLK_N/SUBSPICLK_N_DIFF 25 GPIO47/SPICLK_P/SUBSPICLK_P_DIFF 24 GPIO21 23 GPIO14/TOUCH14/ADC2_CH3/FSPIWP/FSPIDQS/SUBSPIWP 22 GPIO13/TOUCH13/ADC2_CH2/FSPIQ/FSPIIO7/SUBSPIQ 21 GPIO12/TOUCH12/ADC2_CH1/FSPICLK/FSPIIO6/SUBSPICLK 20 GPIO11/TOUCH11/ADC2_CH0/FSPID/FSPIIO5/SUBSPID 19 GPIO10/TOUCH10/ADC1_CH9/FSPICS0/FSPIIO4/SUBSPICS0 18 GPIO9/TOUCH9/ADC1_CH8/FSPIHD/SUBSPIHD 17 GPIO46 16 GPIO3/TOUCH3/ADC1_CH2 15 GPIO8/TOUCH8/ADC1_CH7/SUBSPICS1 12 GPIO18/U1RXD/ADC2_CH7/CLK_OUT3 11 GPIO17/U1TXD/ADC2_CH6 10 GPIO16/U0CTS/ADC2_CH5/XTAL_32K_N 9 GPIO15/U0RTS/ADC2_CH4/XTAL_32K_P 8 GPIO7/TOUCH7/ADC1_CH6 7 GPIO6/TOUCH6/ADC1_CH5 6 GPIO5/TOUCH5/ADC1_CH4 5 GPIO4/TOUCH4/ADC1_CH3 4 EN 3 SPIIO6/GPIO35/FSPID/SUBSPID 28 SPIIO7/GPIO36/FSPICLK/SUBSPICLK 29 SPIDQS/GPIO37/FSPIQ/SUBSPIQ 30 GPIO20/U1CTS/ADC2_CH9/CLK_OUT1 14 GPIO19/U1RTS/ADC2_CH8/CLK_OUT2 13 U1ESP32-S3-WROOM-1 LCSC: C2913202 GND

1 GPIO45 26 GPIO48/SPICLK_N/SUBSPICLK_N_DIFF 25 GPIO47/SPICLK_P/SUBSPICLK_P_DIFF 24 GPIO21 23 GPIO14/TOUCH14/ADC2_CH3/FSPIWP/FSPIDQS/SUBSPIWP 22 GPIO13/TOUCH13/ADC2_CH2/FSPIQ/FSPIIO7/SUBSPIQ 21 GPIO12/TOUCH12/ADC2_CH1/FSPICLK/FSPIIO6/SUBSPICLK 20 GPIO11/TOUCH11/ADC2_CH0/FSPID/FSPIIO5/SUBSPID 19 GPIO10/TOUCH10/ADC1_CH9/FSPICS0/FSPIIO4/SUBSPICS0 18 GPIO9/TOUCH9/ADC1_CH8/FSPIHD/SUBSPIHD 17 GPIO46 16 GPIO3/TOUCH3/ADC1_CH2 15 GPIO8/TOUCH8/ADC1_CH7/SUBSPICS1 12 GPIO18/U1RXD/ADC2_CH7/CLK_OUT3 11 GPIO17/U1TXD/ADC2_CH6 10 GPIO16/U0CTS/ADC2_CH5/XTAL_32K_N 9 GPIO15/U0RTS/ADC2_CH4/XTAL_32K_P 8 GPIO7/TOUCH7/ADC1_CH6 7 GPIO6/TOUCH6/ADC1_CH5 6 GPIO5/TOUCH5/ADC1_CH4 5 GPIO4/TOUCH4/ADC1_CH3 4 EN 3 SPIIO6/GPIO35/FSPID/SUBSPID 28 SPIIO7/GPIO36/FSPICLK/SUBSPICLK 29 SPIDQS/GPIO37/FSPIQ/SUBSPIQ 30 GPIO20/U1CTS/ADC2_CH9/CLK_OUT1 14 GPIO19/U1RTS/ADC2_CH8/CLK_OUT2 13 GND

https://www.espressif.com/sites/default/files/documentation/esp32-s3-wroom-1_wroom-1u_datasheet_en.pdf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
JTAG Signal Source Control þÿ(V3=>@CTBLAO þÿG5@57 þÿD'N78)
VVAL

File: main.kicad_sch Sheet: / Anderson
