rompasaurus/regardedPal/hardware-design/examples/05-olimex-devkit-lipo/HARDWARE/ESP32-DevKit-LiPo-Rev.A1/ESP32-DevKit-Lipo_Rev_A1.pdf

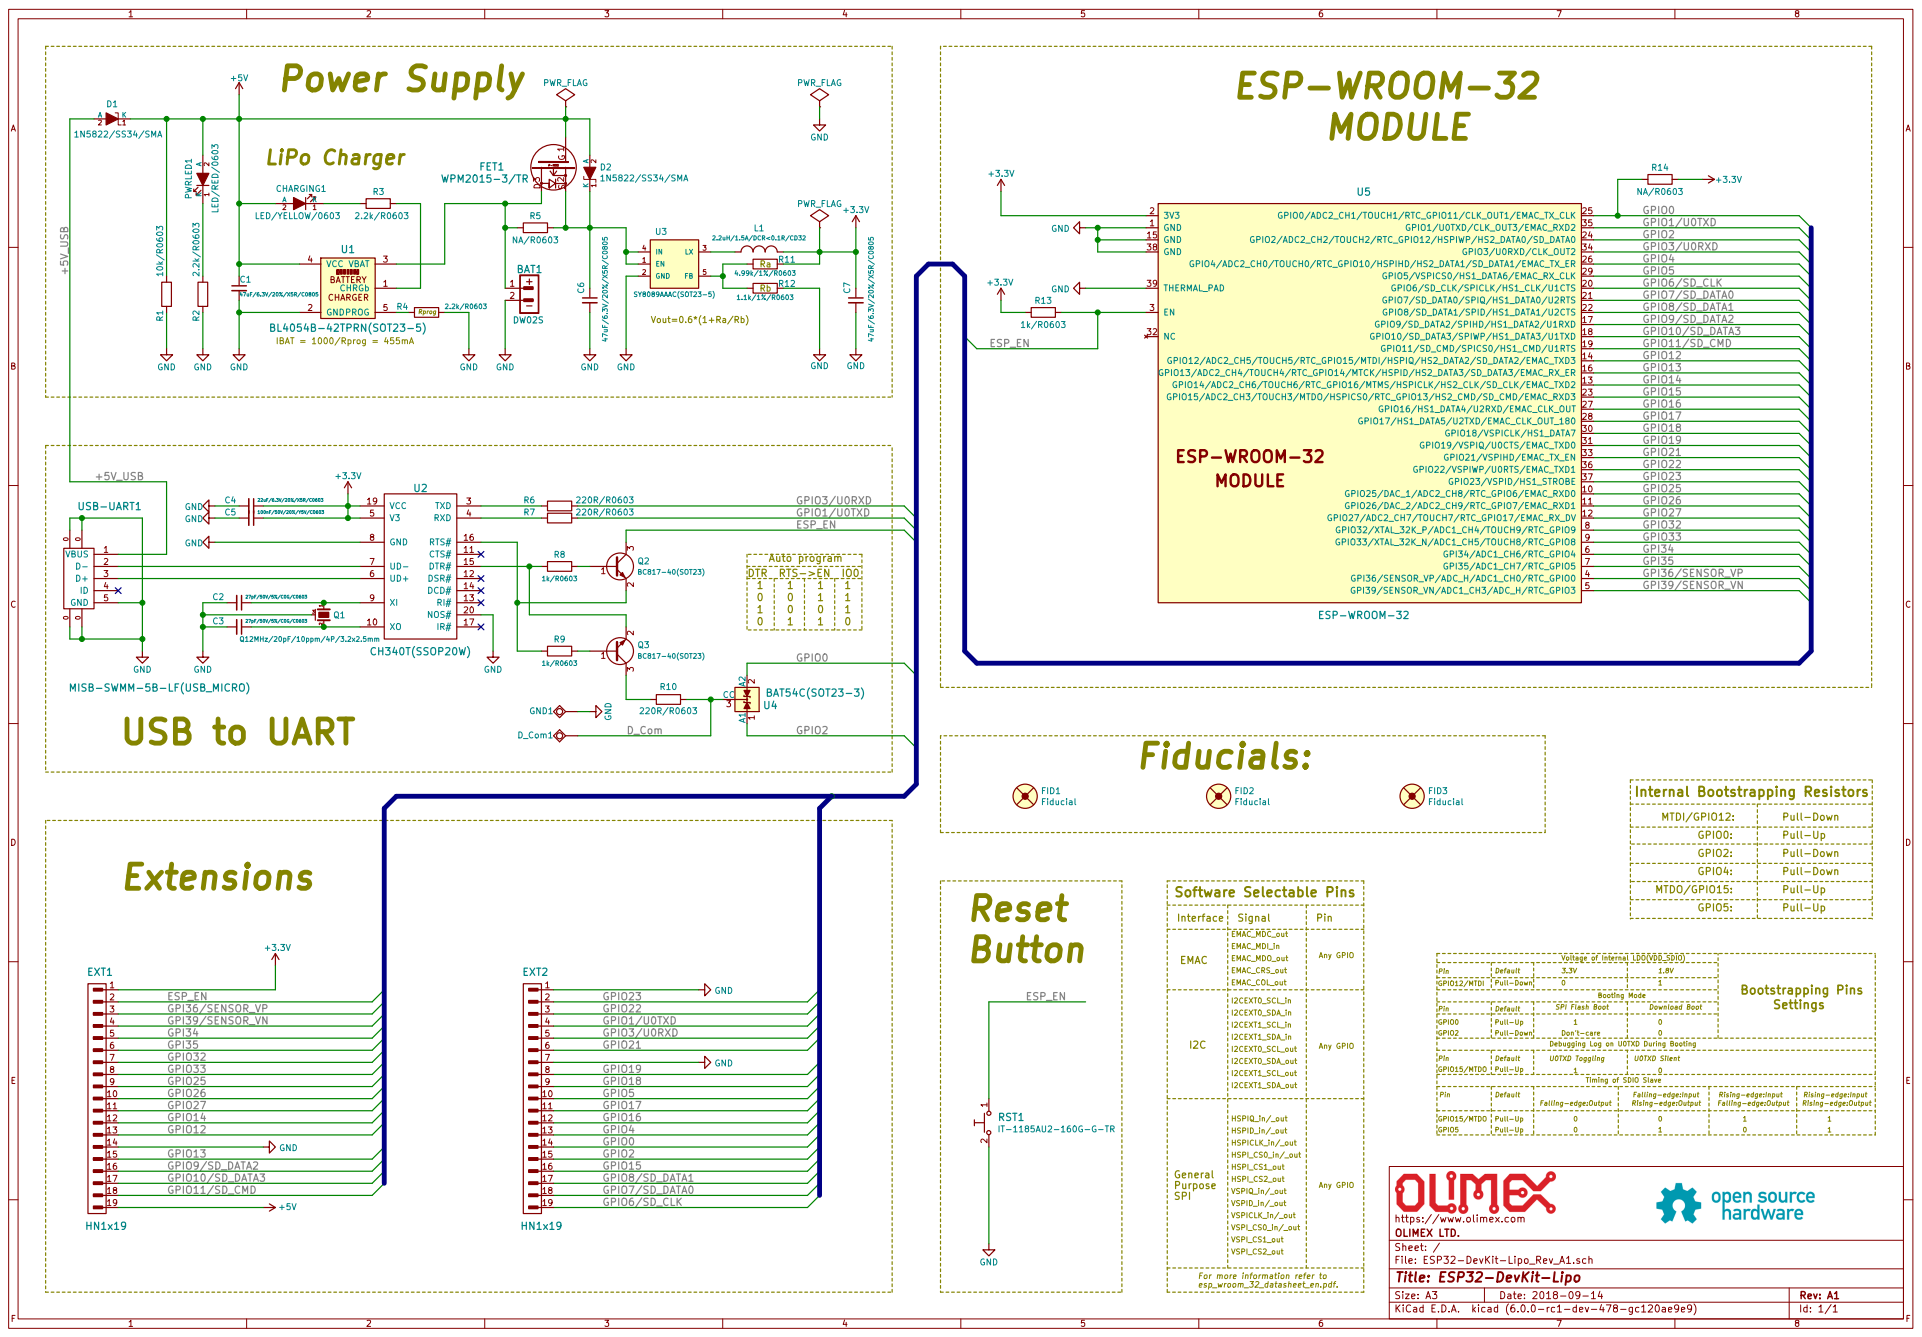
[picture p454: page 1]

2 PWRLED1 LED/RED/0603 GND GND GND

Reset Button GND | ESP_EN | File: ESP32-DevKit-Lipo_Rev_A1.sch Sheet: / OLIMEX LTD. https://www.olimex.com GNDGND1

Internal Bootstrapping Resistors MTDI/GPIO12: | Pull-Down GPIO0: Pull-Up GPIO2: Pull-Down GPIO4: Pull-Down MTDO/GPIO15: Pull-Up GPIO5: Pull-Up

EMAC_COL_out Interface EMAC EMAC_MDC_out EMAC_MDI_in EMAC_MDO_out EMAC_CRS_out | Any GPIO

Signal | Pin

Id: 1/1 Title: ESP32-DevKit-Lipo

Rev: A1 | F Date: 2018-09-14 KiCad E.D.A. kicad (6.0.0-rc1-dev-478-gc120ae9e9) Size: A3
