rompasaurus/regardedPal/hardware-design/reference-boards/rp2040-pico-usbc/KiCad Projects/Pico WH - No License/Pico WH.pdf

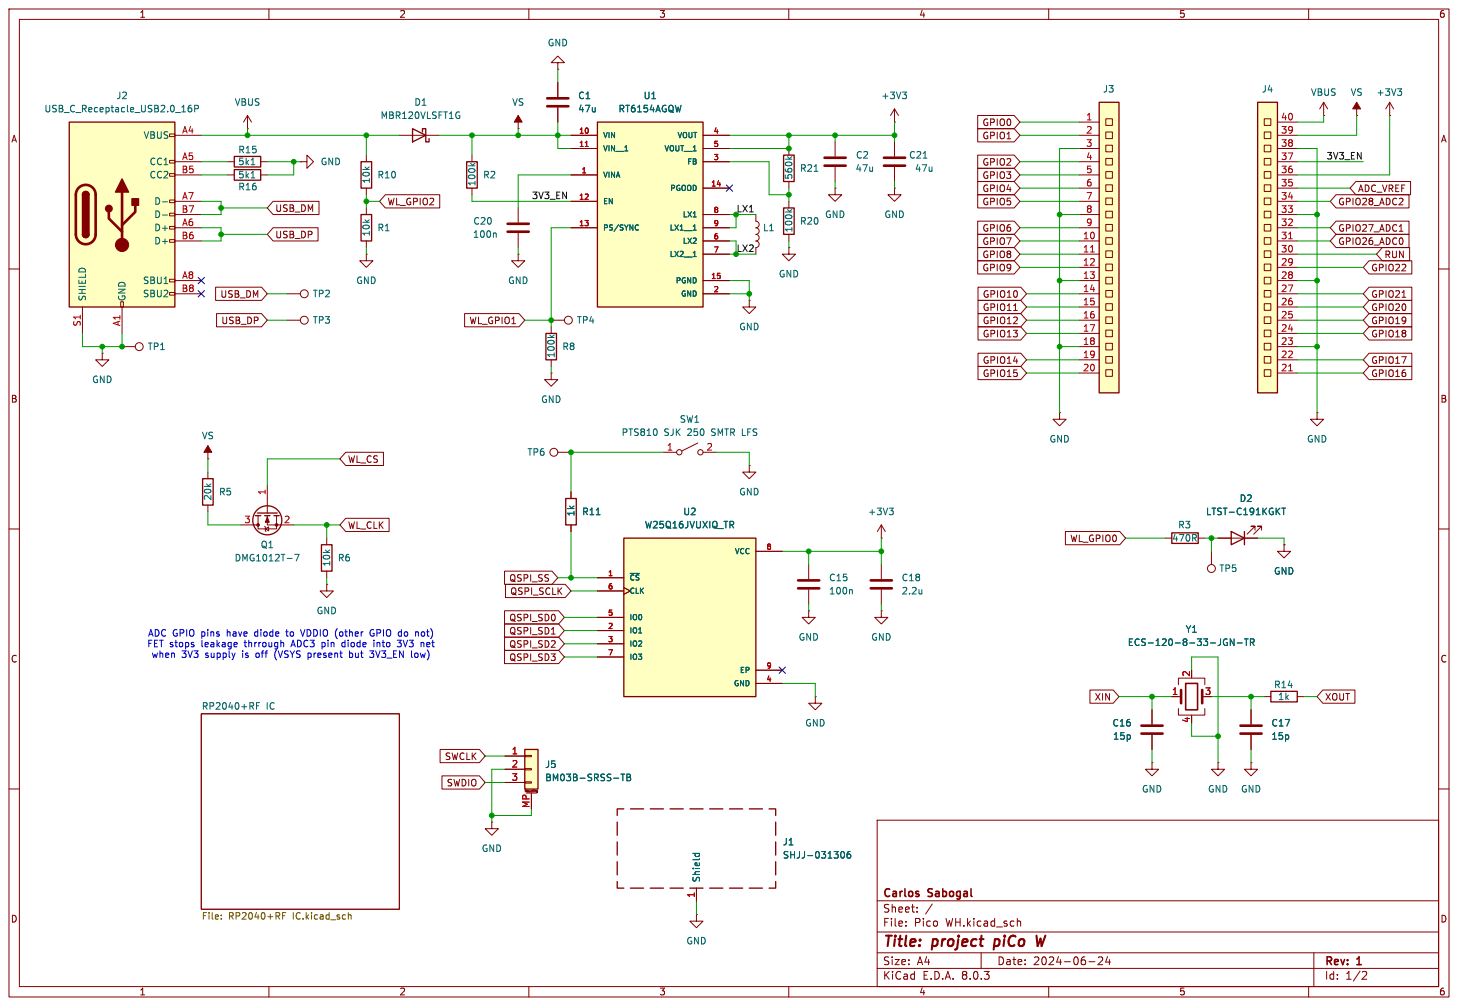
[picture p455: page 1]

4 Y1 ECS-120-8-33-JGN-TR GND GND

Id: 1/2 Title: project piCo W

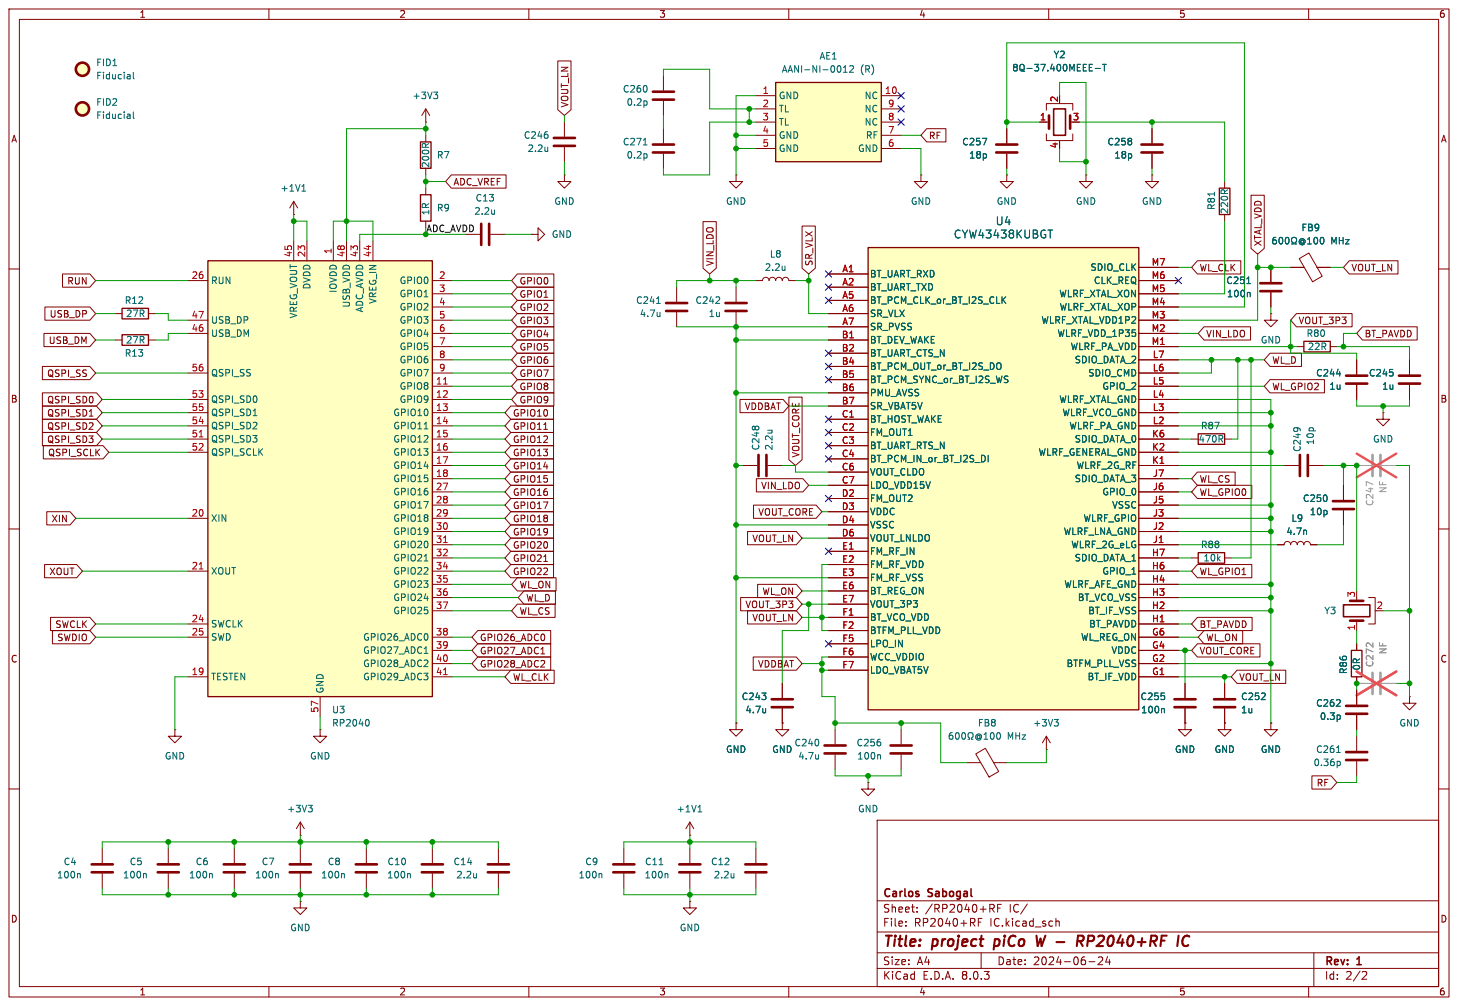
[picture p456: page 2]

1 GPIO8 11 GPIO9 12 GPIO10 13 GPIO11 14 GPIO12 15 GPIO13 16 GPIO14 17 GPIO15 18 TESTEN 19 GPIO0 2 XIN 20 XOUT 21 DVDD 23 SWCLK 24 SWD 25 RUN 26 GPIO16 27 GPIO17 28 GPIO18 29 GPIO1 3 GPIO19 30 GPIO20 31 GPIO21 32 GPIO22 34 GPIO23 35 GPIO24 36 GPIO25 37 GPIO26_ADC0 38 GPIO27_ADC1 39 GPIO2 4 GPIO28_ADC2 40 GPIO29_ADC3 41 ADC_AVDD 43 VREG_IN 44 VREG_VOUT 45 USB_DM 46 USB_DP 47 USB_VDD 48 GPIO3 5 QSPI_SD3 51 QSPI_SCLK 52 QSPI_SD0 53 QSPI_SD2 54 QSPI_SD1 55 QSPI_SS 56 GND 57 GPIO4 6 GPIO5 7 GPIO6 8 GPIO7 9 U3 RP2040 GND
