rompasaurus/regardedPal/hardware-design/reference-boards/esp32s3-basic-devboard/docs/schematic.pdf

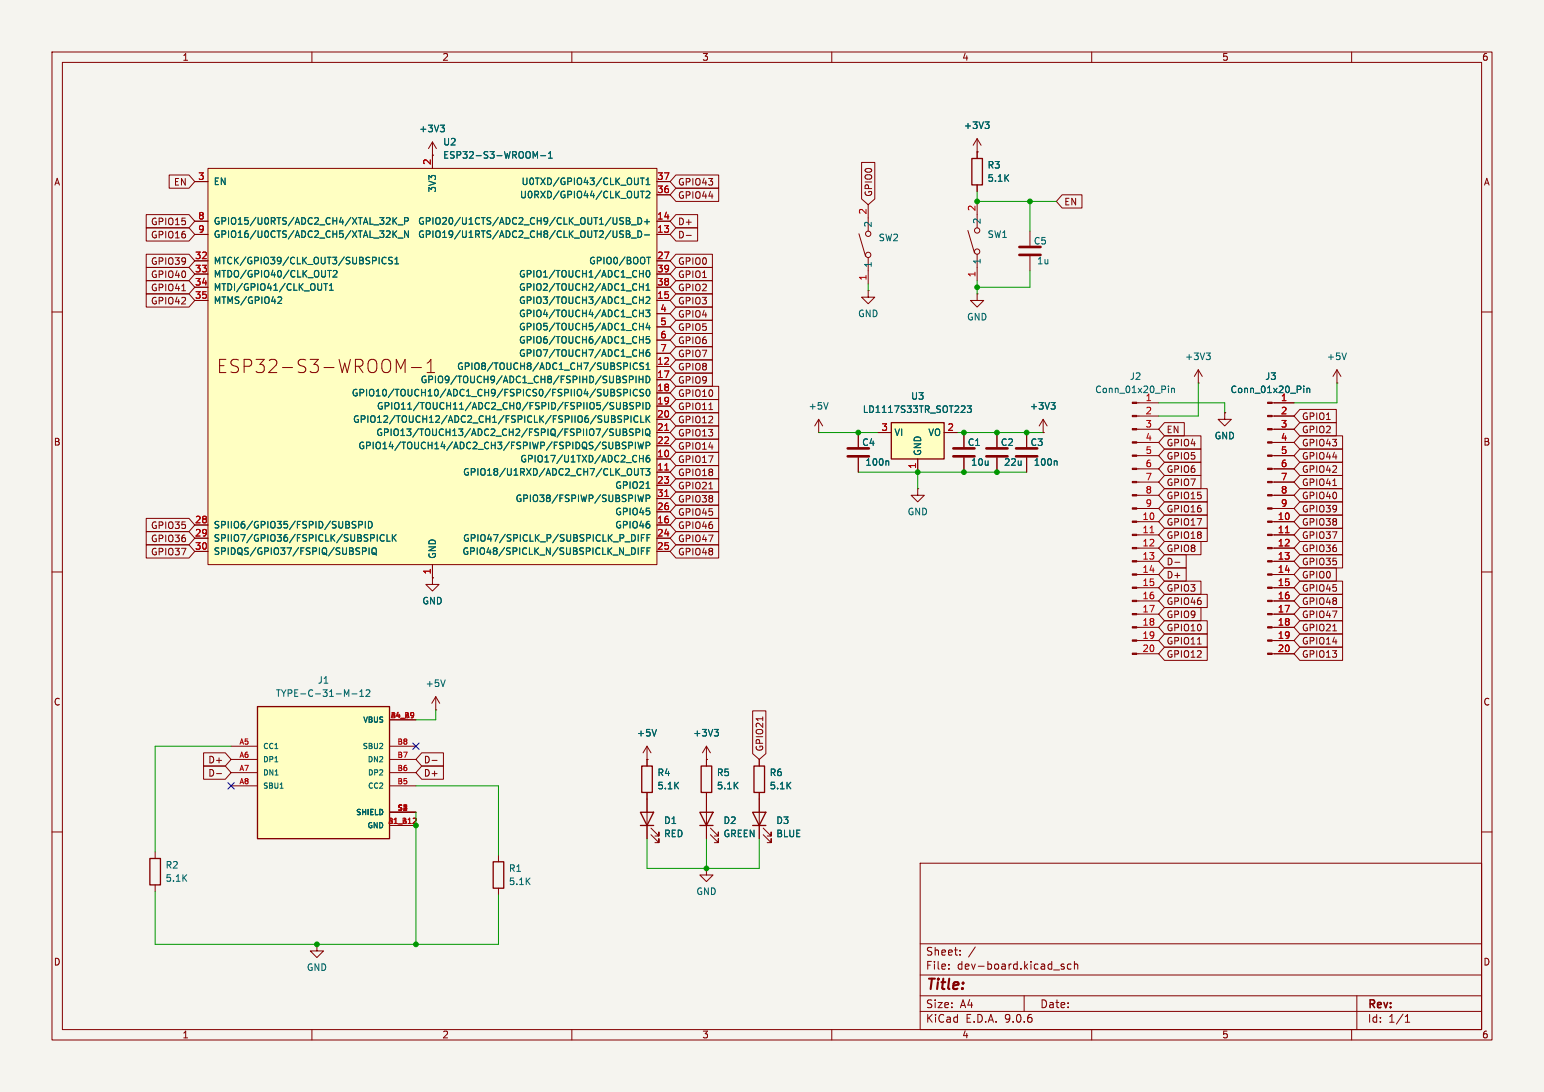
[picture p457: page 1]

1 U0TXD/GPIO43/CLK_OUT1 37 U0RXD/GPIO44/CLK_OUT2 36 GPIO20/U1CTS/ADC2_CH9/CLK_OUT1/USB_D+ 14 GPIO19/U1RTS/ADC2_CH8/CLK_OUT2/USB_D- 13 GPIO0/BOOT 27 GPIO1/TOUCH1/ADC1_CH0 39 GPIO2/TOUCH2/ADC1_CH1 38 GPIO3/TOUCH3/ADC1_CH2 15 GPIO4/TOUCH4/ADC1_CH3 4 GPIO5/TOUCH5/ADC1_CH4 5 GPIO6/TOUCH6/ADC1_CH5 6 GPIO7/TOUCH7/ADC1_CH6 7 GPIO8/TOUCH8/ADC1_CH7/SUBSPICS1 12 GPIO9/TOUCH9/ADC1_CH8/FSPIHD/SUBSPIHD 17 GPIO10/TOUCH10/ADC1_CH9/FSPICS0/FSPIIO4/SUBSPICS0 18 GPIO11/TOUCH11/ADC2_CH0/FSPID/FSPIIO5/SUBSPID 19 GPIO12/TOUCH12/ADC2_CH1/FSPICLK/FSPIIO6/SUBSPICLK 20 GPIO13/TOUCH13/ADC2_CH2/FSPIQ/FSPIIO7/SUBSPIQ 21 GPIO14/TOUCH14/ADC2_CH3/FSPIWP/FSPIDQS/SUBSPIWP 22 GPIO17/U1TXD/ADC2_CH6 10 GPIO18/U1RXD/ADC2_CH7/CLK_OUT3 11 GPIO21 23 GPIO38/FSPIWP/SUBSPIWP 31 GPIO45 26 GPIO46 16 GPIO47/SPICLK_P/SUBSPICLK_P_DIFF 24 GPIO48/SPICLK_N/SUBSPICLK_N_DIFF 25 U2ESP32-S3-WROOM-1 R6

1 U0TXD/GPIO43/CLK_OUT1 37 U0RXD/GPIO44/CLK_OUT2 36 GPIO20/U1CTS/ADC2_CH9/CLK_OUT1/USB_D+ 14 GPIO19/U1RTS/ADC2_CH8/CLK_OUT2/USB_D- 13 GPIO0/BOOT 27 GPIO1/TOUCH1/ADC1_CH0 39 GPIO2/TOUCH2/ADC1_CH1 38 GPIO3/TOUCH3/ADC1_CH2 15 GPIO4/TOUCH4/ADC1_CH3 4 GPIO5/TOUCH5/ADC1_CH4 5 GPIO6/TOUCH6/ADC1_CH5 6 GPIO7/TOUCH7/ADC1_CH6 7 GPIO8/TOUCH8/ADC1_CH7/SUBSPICS1 12 GPIO9/TOUCH9/ADC1_CH8/FSPIHD/SUBSPIHD 17 GPIO10/TOUCH10/ADC1_CH9/FSPICS0/FSPIIO4/SUBSPICS0 18 GPIO11/TOUCH11/ADC2_CH0/FSPID/FSPIIO5/SUBSPID 19 GPIO12/TOUCH12/ADC2_CH1/FSPICLK/FSPIIO6/SUBSPICLK 20 GPIO13/TOUCH13/ADC2_CH2/FSPIQ/FSPIIO7/SUBSPIQ 21 GPIO14/TOUCH14/ADC2_CH3/FSPIWP/FSPIDQS/SUBSPIWP 22 GPIO17/U1TXD/ADC2_CH6 10 GPIO18/U1RXD/ADC2_CH7/CLK_OUT3 11 GPIO21 23 GPIO38/FSPIWP/SUBSPIWP 31 GPIO45 26 GPIO46 16 GPIO47/SPICLK_P/SUBSPICLK_P_DIFF 24 GPIO48/SPICLK_N/SUBSPICLK_N_DIFF 25 C3

Id: 1/1 Title: File: dev-board.kicad_sch Sheet: /
