rompasaurus/regardedPal/hardware-design/examples/03-ducky-board-epaper/PCB.pdf

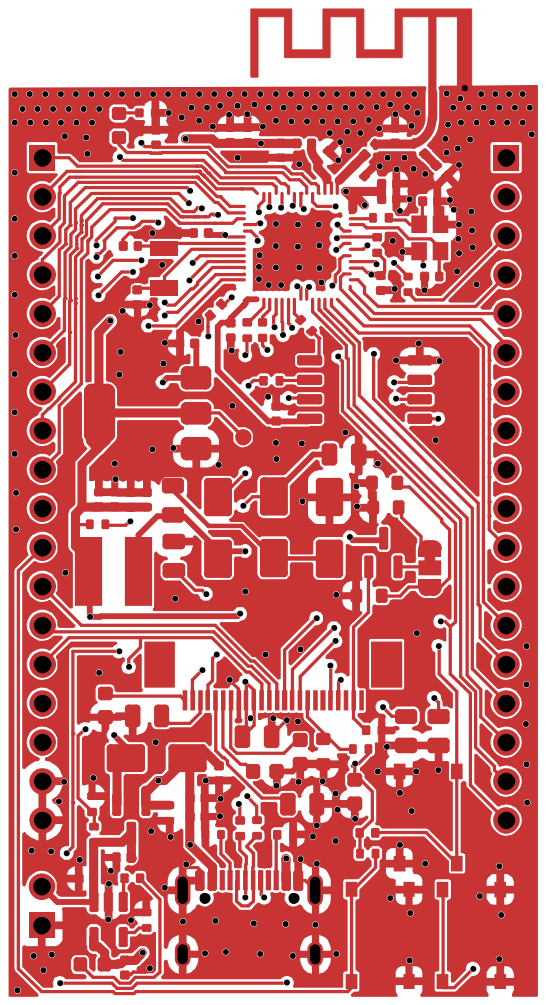
[picture p458: page 1]

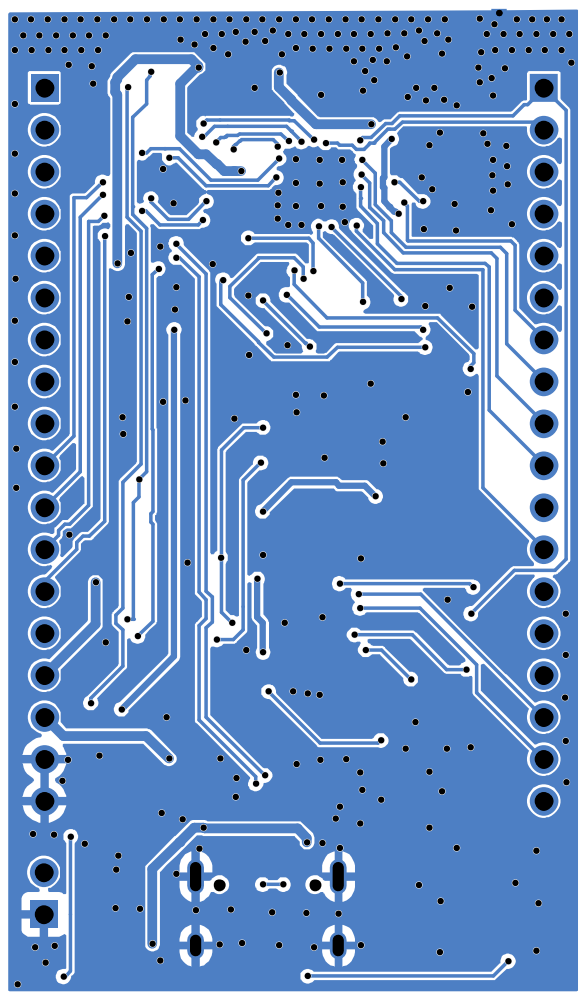
[picture p459: page 2]

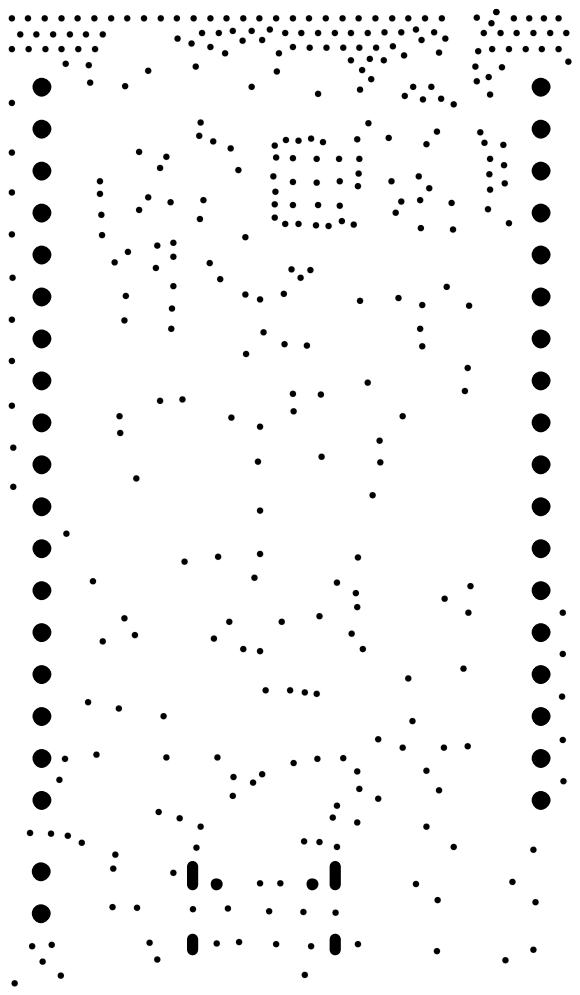
[picture p460: page 3]

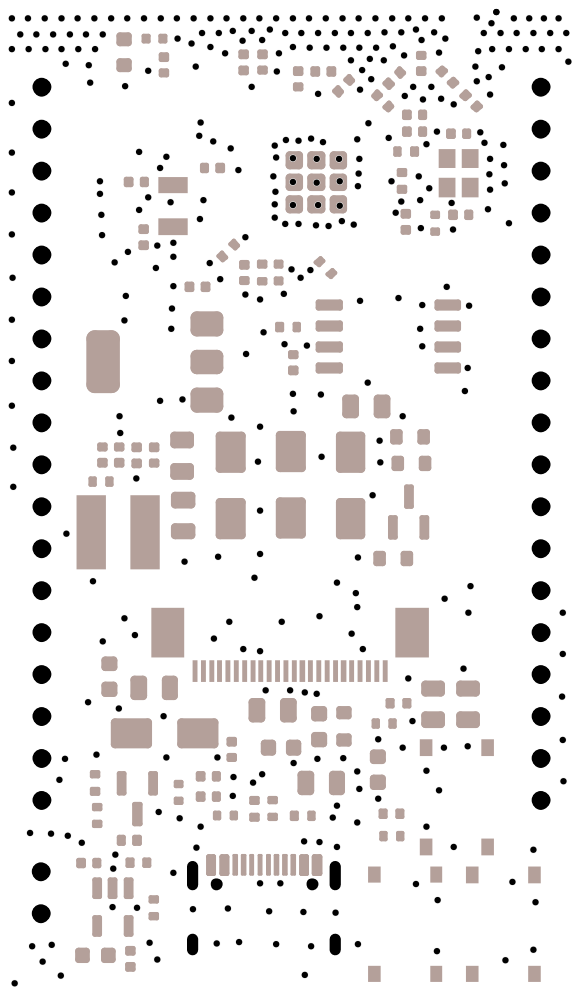
[picture p461: page 5]

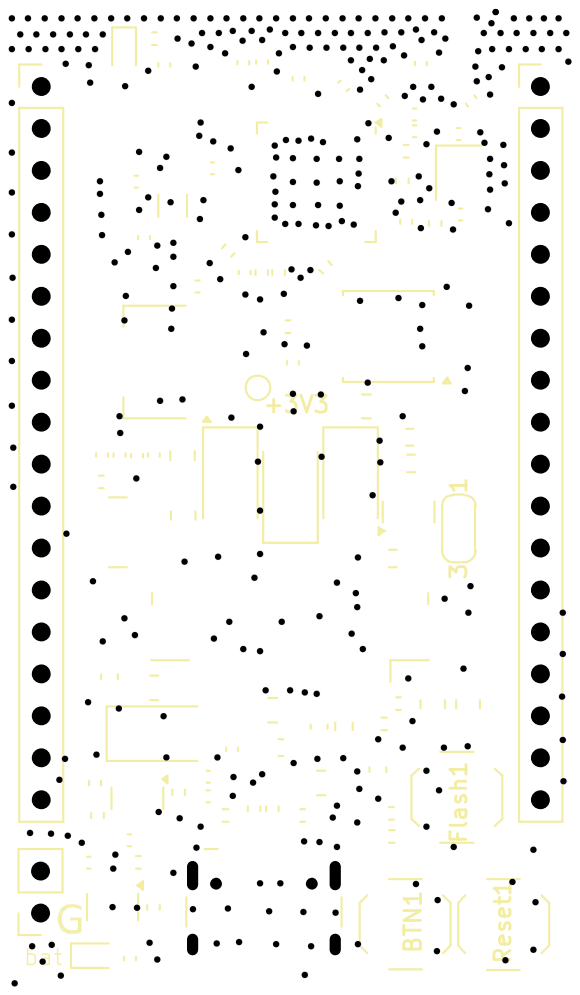
[picture p462: page 7]

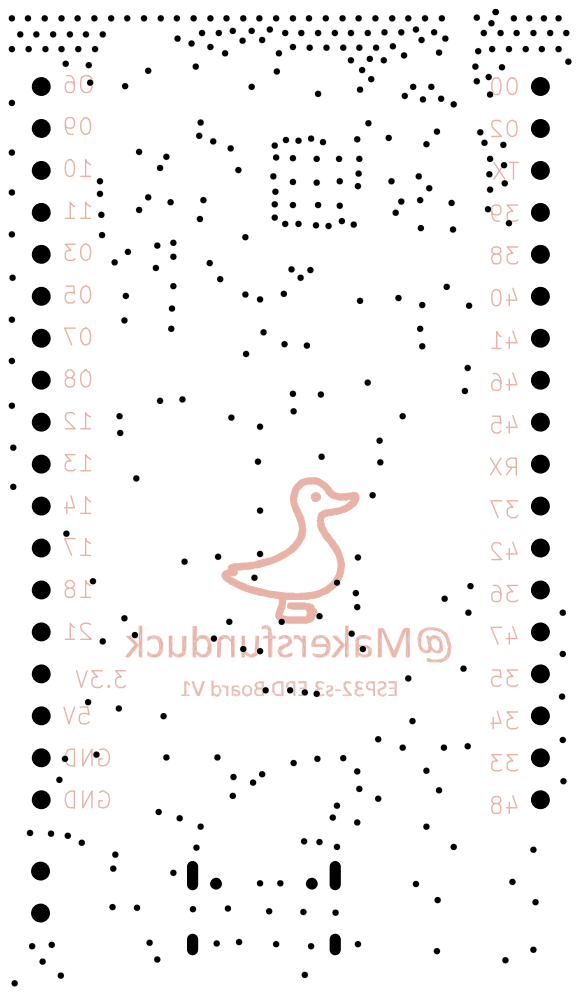
[picture p463: page 8]

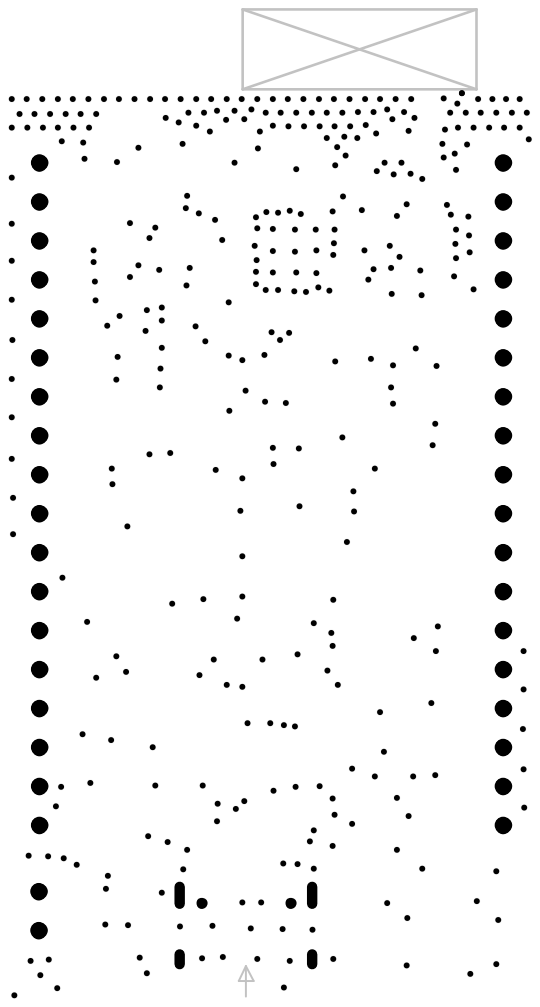
[picture p464: page 9]
