rompasaurus/regardedPal/hardware-design/examples/03-ducky-board-epaper/Schematic.pdf

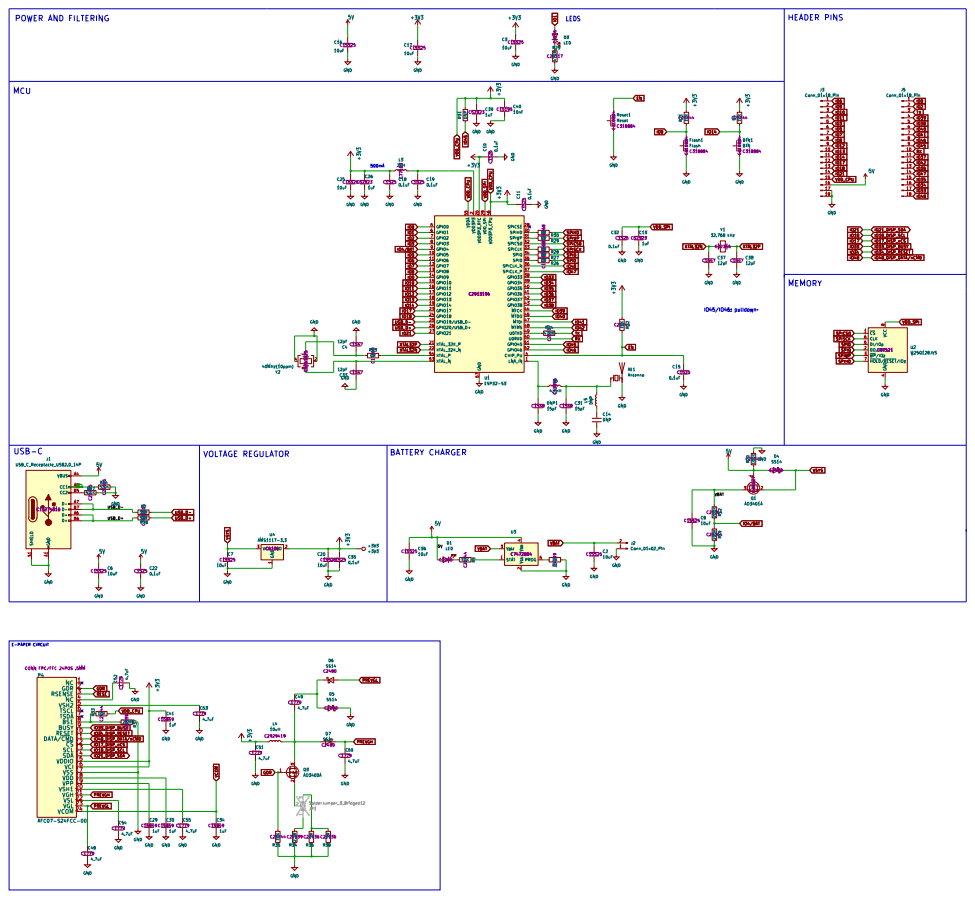
[picture p465: page 1]
