rompasaurus/regardedPal/hardware-design/examples/05-olimex-devkit-lipo/HARDWARE/ESP32-DevKit-LiPo-Rev.B/ESP32-DevKit-Lipo_Rev_B.pdf

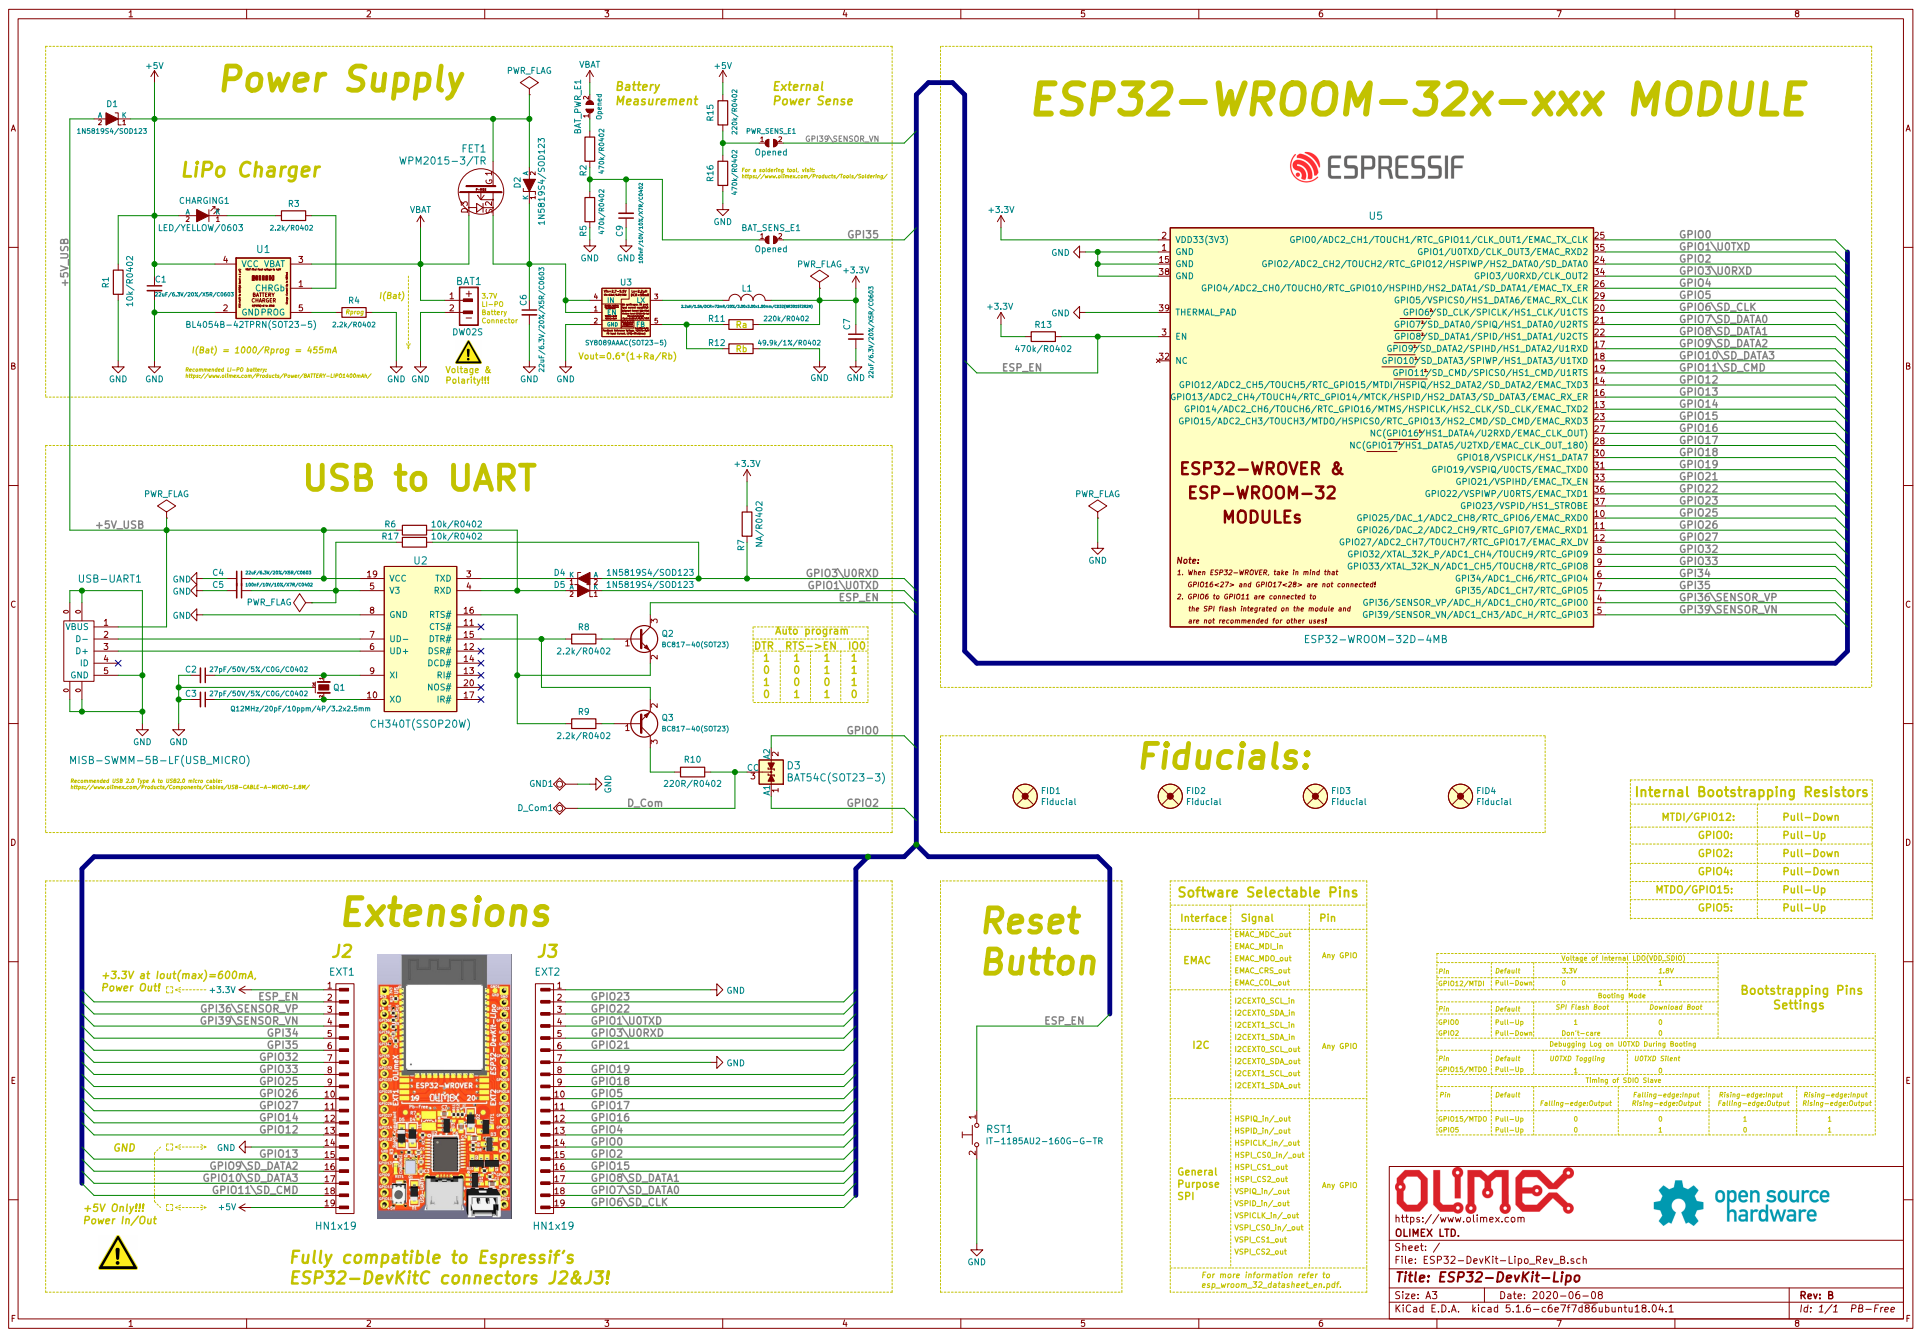
[picture p466: page 1]

load current capability! Lx=2.2H

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

2.2. 2. 2.2. 2. 2. GPIO6 to GPIO11 are connected to are not recommended for other uses! ESP-WROOM-32

Recommended LI-PO battery: https://www.olimex.com/Products/Power/BATTERY-LIPO1400mAh/

1. 1. 1. When ESP32-WROVER, take in mind that
ESP32-WROVER &

GPIO16<27> and GPIO17<28> are not connected! MODULEs

Recommended USB 2.0 Type A to USB2.0 micro cable: https://www.olimex.com/Products/Components/Cables/USB-CABLE-A-MICRO-1.8M/

EMAC | Pull-Down Reset

Interface

Debugging Log on U0TXD During Booting

File: ESP32-DevKit-Lipo_Rev_B.sch Sheet: / OLIMEX LTD. https://www.olimex.com

Fully compatible to Espressif's
ESP32-DevKitC connectors J2&J3!

Id: 1/1 PB-Free Title: ESP32-DevKit-Lipo
