rompasaurus/regardedPal/hardware-design/examples/01-pocketmage-pda/Docs/Documents & Advanced/PCB/V3.3/einkPDA_screen/einkPDA_screen.kicad_pcb

## KiCad design hardware-design/examples/01-pocketmage-pda/Docs/Documents & Advanced/PCB/V3.3/einkPDA_screen/einkPDA_screen.kicad_pcb (2026-04-15)

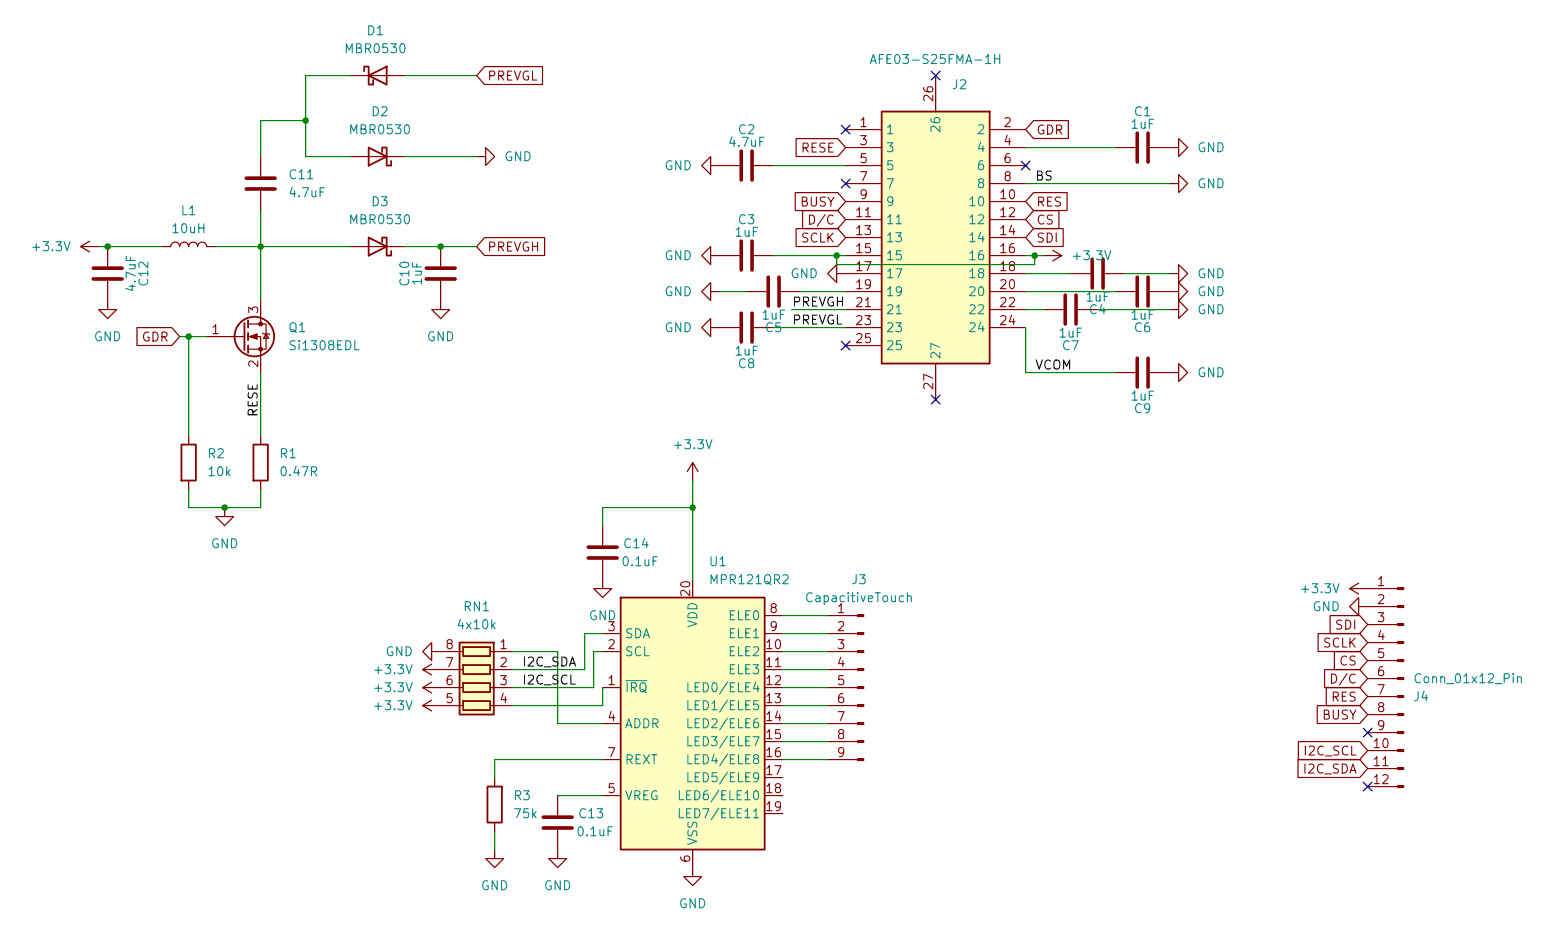
[picture p467: schematic einkPDA_screen.kicad_sch]

Parts:
C1, C3, C4, C5, C6, C7, C8, C9, C10: 1uF; C_0402_1005Metric; MPN C52923
C2, C12: 4.7uF; C_0402_1005Metric; MPN C23733
C11: 4.7uF; C_0805_2012Metric; MPN C1779
C13, C14: 0.1uF; C_0402_1005Metric; MPN C1525
D1, D2, D3: MBR0530; D_SOD-123; MPN C77336
J2: AFE03-S25FMA-1H; MPN C262544
J3: CapacitiveTouch; TouchSlider-9_50x10mm
J4: Conn_01x12_Pin; AFC01-S12FCA-00; MPN C262661
L1: 10uH; L_Cenker_CKCS5020; MPN C52281
Q1: Si1308EDL; SOT-323_SC-70; MPN C7603347
R1: 0.47R; R_0603_1608Metric; MPN C3013349
R2: 10k; R_0805_2012Metric; MPN C17414
R3: 75k; R_0603_1608Metric; MPN C23242
RN1: 4x10k; R_Array_Concave_4x0603; MPN C29718
U1: MPR121QR2; UQFN-20_3x3mm_P0.4mm; MPN C91322

Connections:
+3.3V: C3.2, C12.1, C14.1, J2.15, J2.16, J4.1, L1.1, RN1.5 (R4.2), RN1.6 (R3.2), RN1.7 (R2.2), U1.20 (VDD)
/VCOM: C9.2, J2.24
BUSY: J2.9, J4.8
CS: J2.12, J4.5
D/C: J2.11, J4.6
GDR: J2.2, Q1.1 (G), R2.1
GND: C1.2, C2.1, C3.1, C4.1, C5.2, C6.1, C7.1, C8.2, C9.1, C10.1, C12.2, C13.2, C14.2, D2.1 (K), J2.8, J2.17, J4.2, R1.2, R2.2, R3.1, RN1.8 (R1.2), U1.6 (VSS)
I2C_SCL: J4.10, RN1.3 (R3.1), U1.2 (SCL)
I2C_SDA: J4.11, RN1.2 (R2.1), U1.3 (SDA)
unnamed: C1.1, J2.4
unnamed: C2.2, J2.5
unnamed: C4.2, J2.18
unnamed: C5.1, J2.19
unnamed: C6.2, J2.20
unnamed: C7.2, J2.22
unnamed: C11.1, D1.1 (K), D2.2 (A)
unnamed: C11.2, D3.2 (A), L1.2, Q1.3 (D)
unnamed: J3.1, U1.8 (ELE0)
unnamed: J3.2, U1.9 (ELE1)
unnamed: J3.3, U1.10 (ELE2)
unnamed: J3.4, U1.11 (ELE3)
unnamed: J3.5, U1.12 (LED0/ELE4)
unnamed: J3.6, U1.13 (LED1/ELE5)
unnamed: J3.7, U1.14 (LED2/ELE6)
unnamed: J3.8, U1.15 (LED3/ELE7)
unnamed: J3.9, U1.16 (LED4/ELE8)
unnamed: RN1.1 (R1.1), U1.4 (ADDR)
unnamed: RN1.4 (R4.1), U1.1 (~IRQ)
unnamed: R3.2, U1.7 (REXT)
unnamed: C13.1, U1.5 (VREG)
PREVGH: C10.2, D3.1 (K), J2.21
PREVGL: C8.1, D1.2 (A), J2.23
RES: J2.10, J4.7
RESE: J2.3, Q1.2 (S), R1.1
SCLK: J2.13, J4.4
SDI: J2.14, J4.3

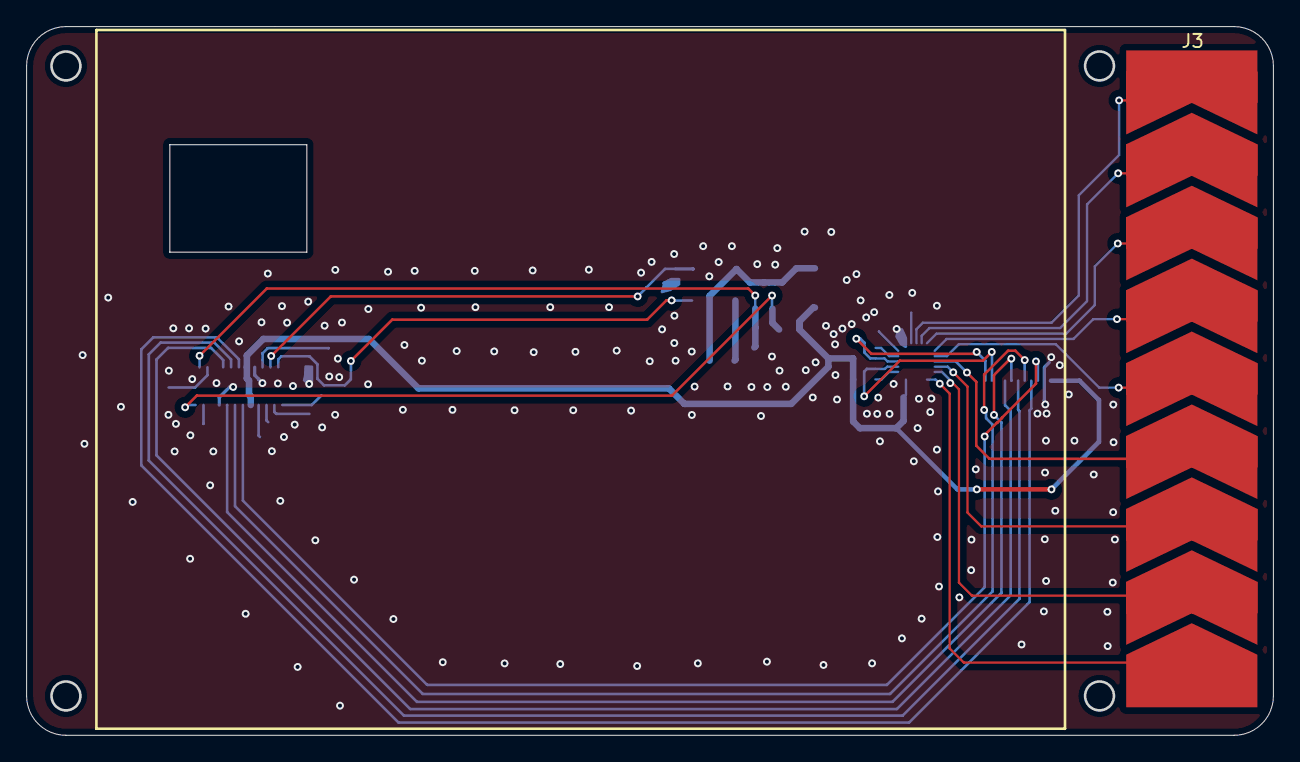
[picture p468: board einkPDA_screen.kicad_pcb from above]

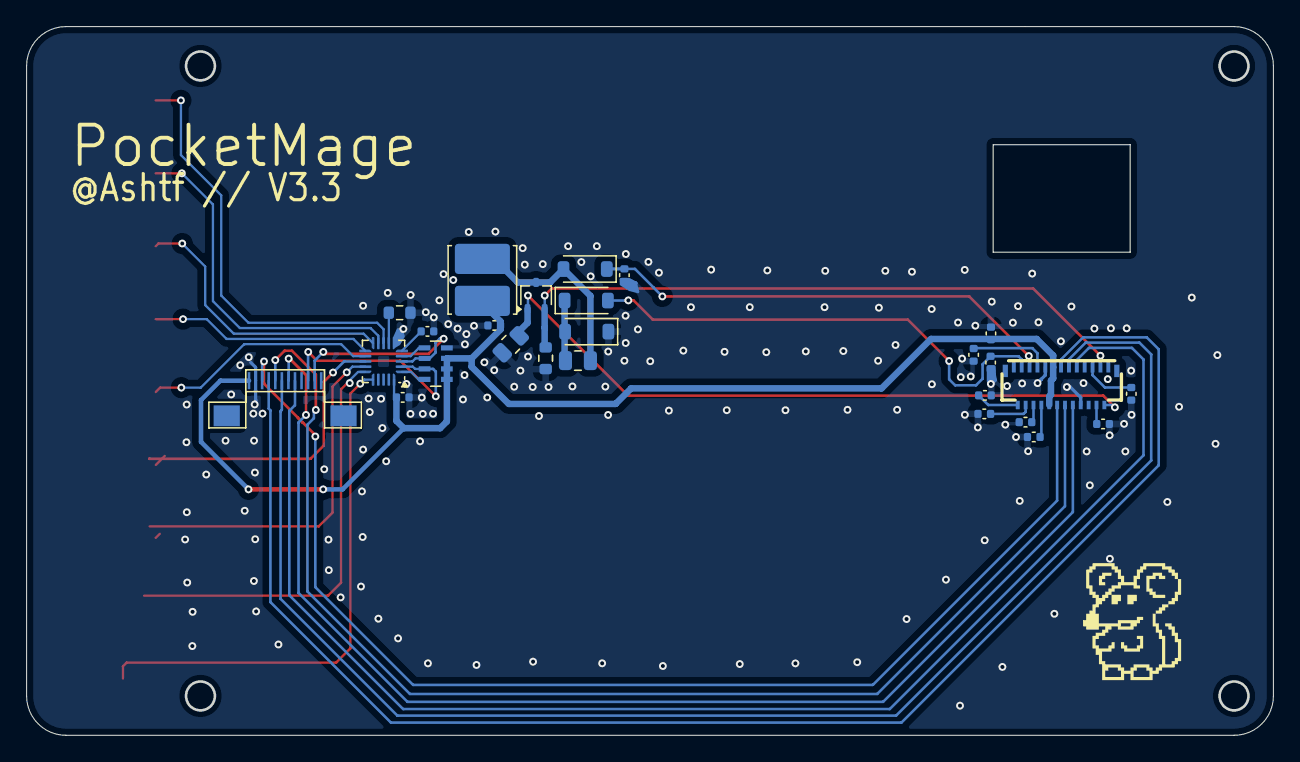
[picture p469: board einkPDA_screen.kicad_pcb from below]

Board: 2 copper layers, 95.0 x 54.0 mm, 27 parts (26 on the bottom side), 36 nets.
