rompasaurus/regardedPal/hardware-design/examples/03-ducky-board-epaper/hardware.kicad_pcb

## KiCad design hardware-design/examples/03-ducky-board-epaper/hardware.kicad_pcb (2026-04-15)

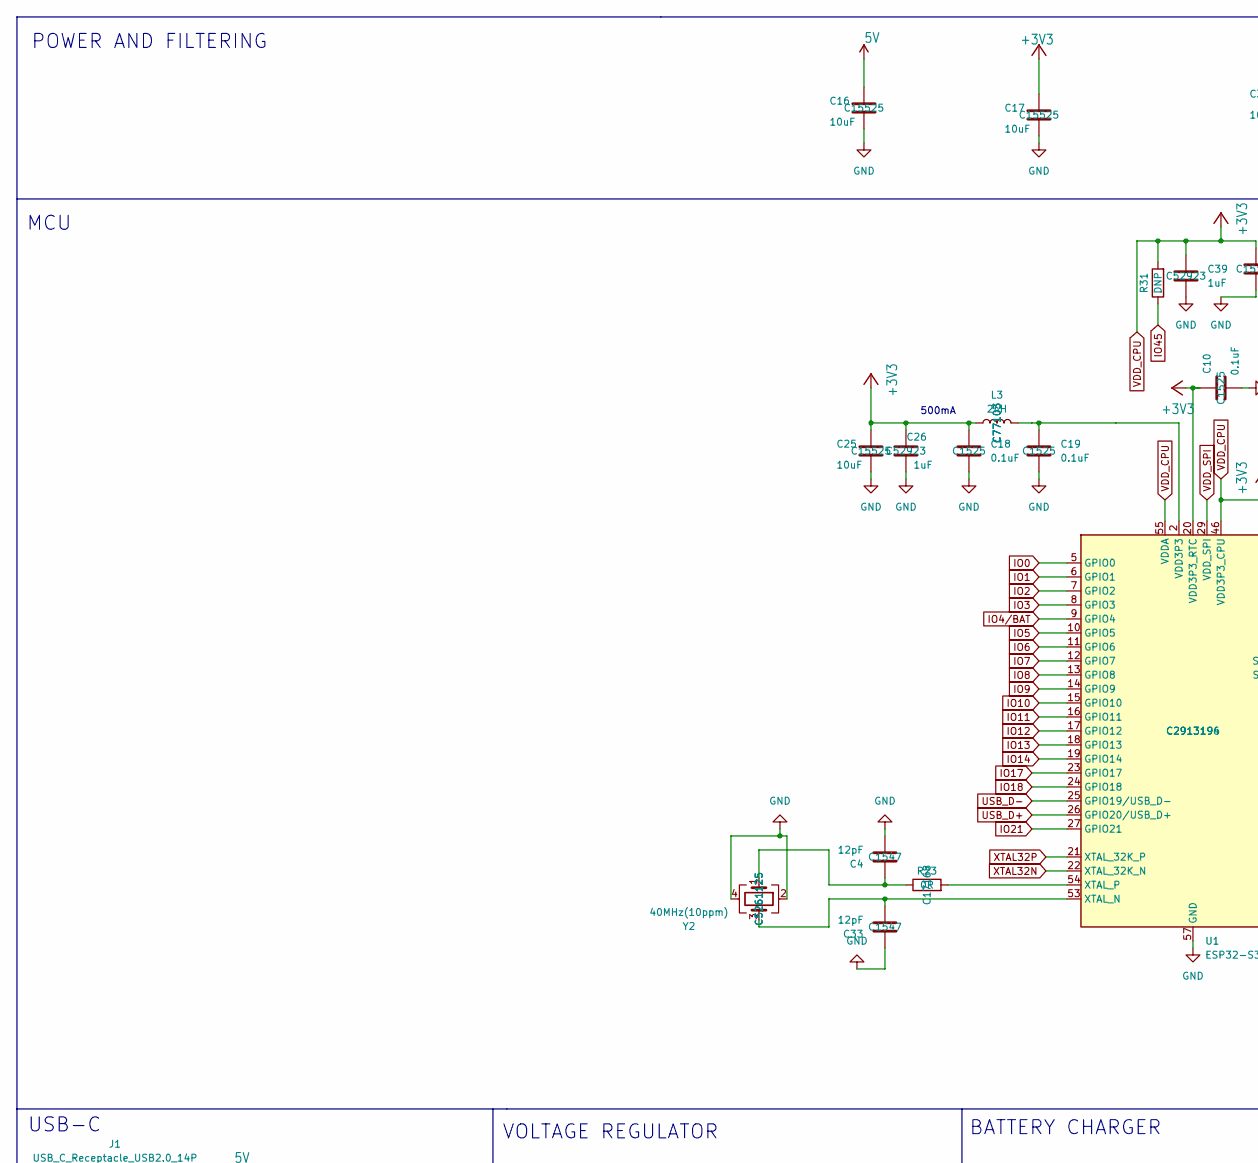
[picture p470: schematic hardware.kicad_sch, part in row 1, column 1]

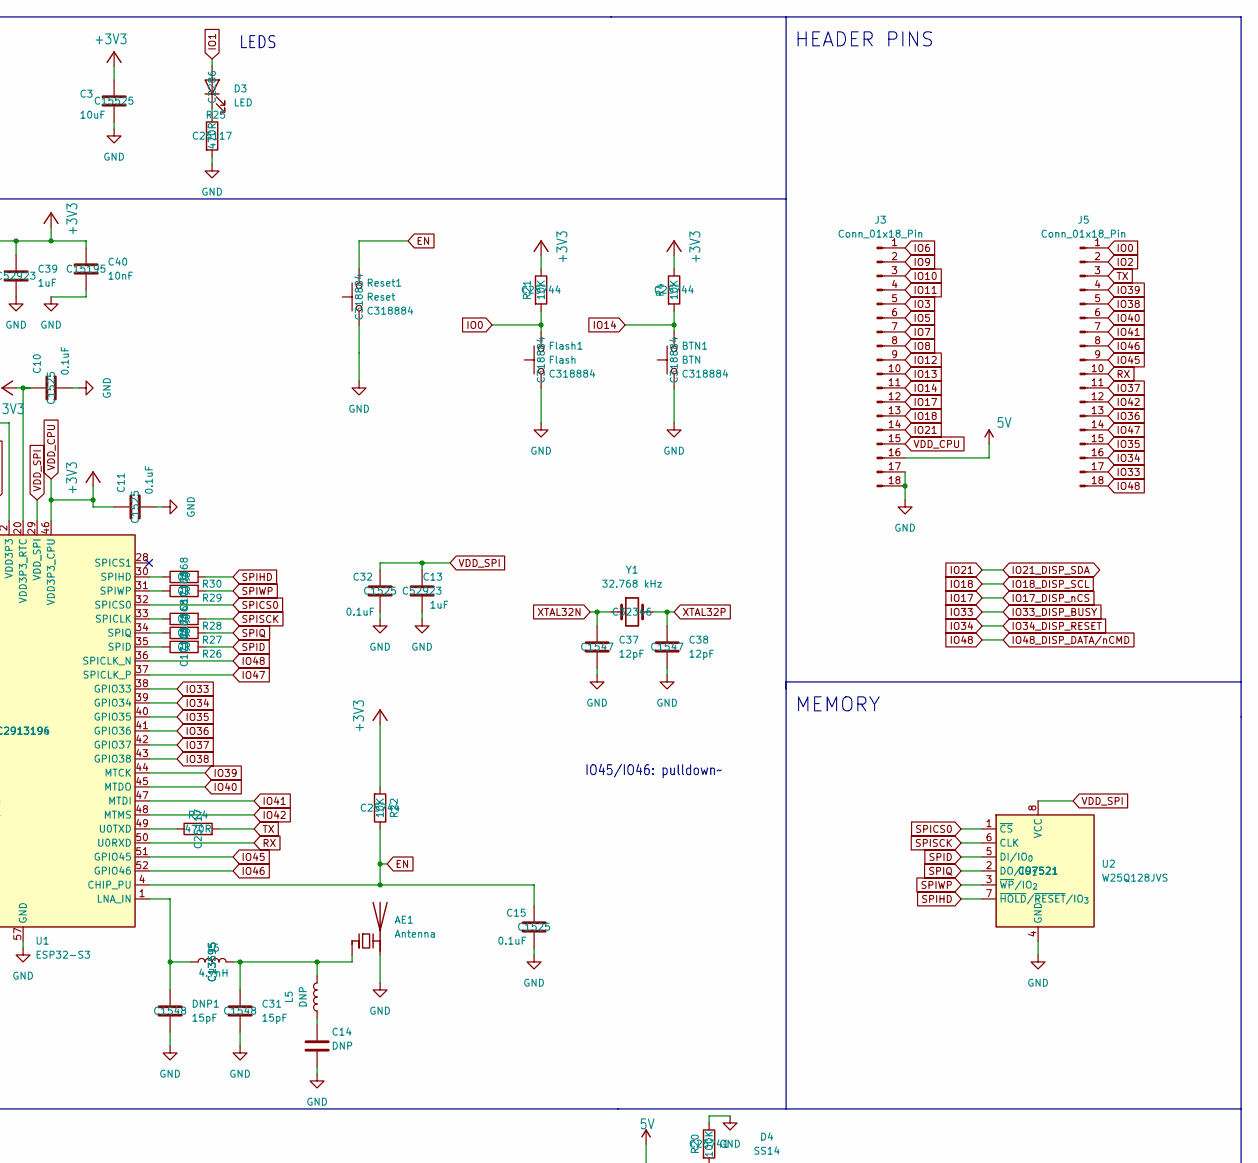
[picture p471: schematic hardware.kicad_sch, part in row 1, column 2]

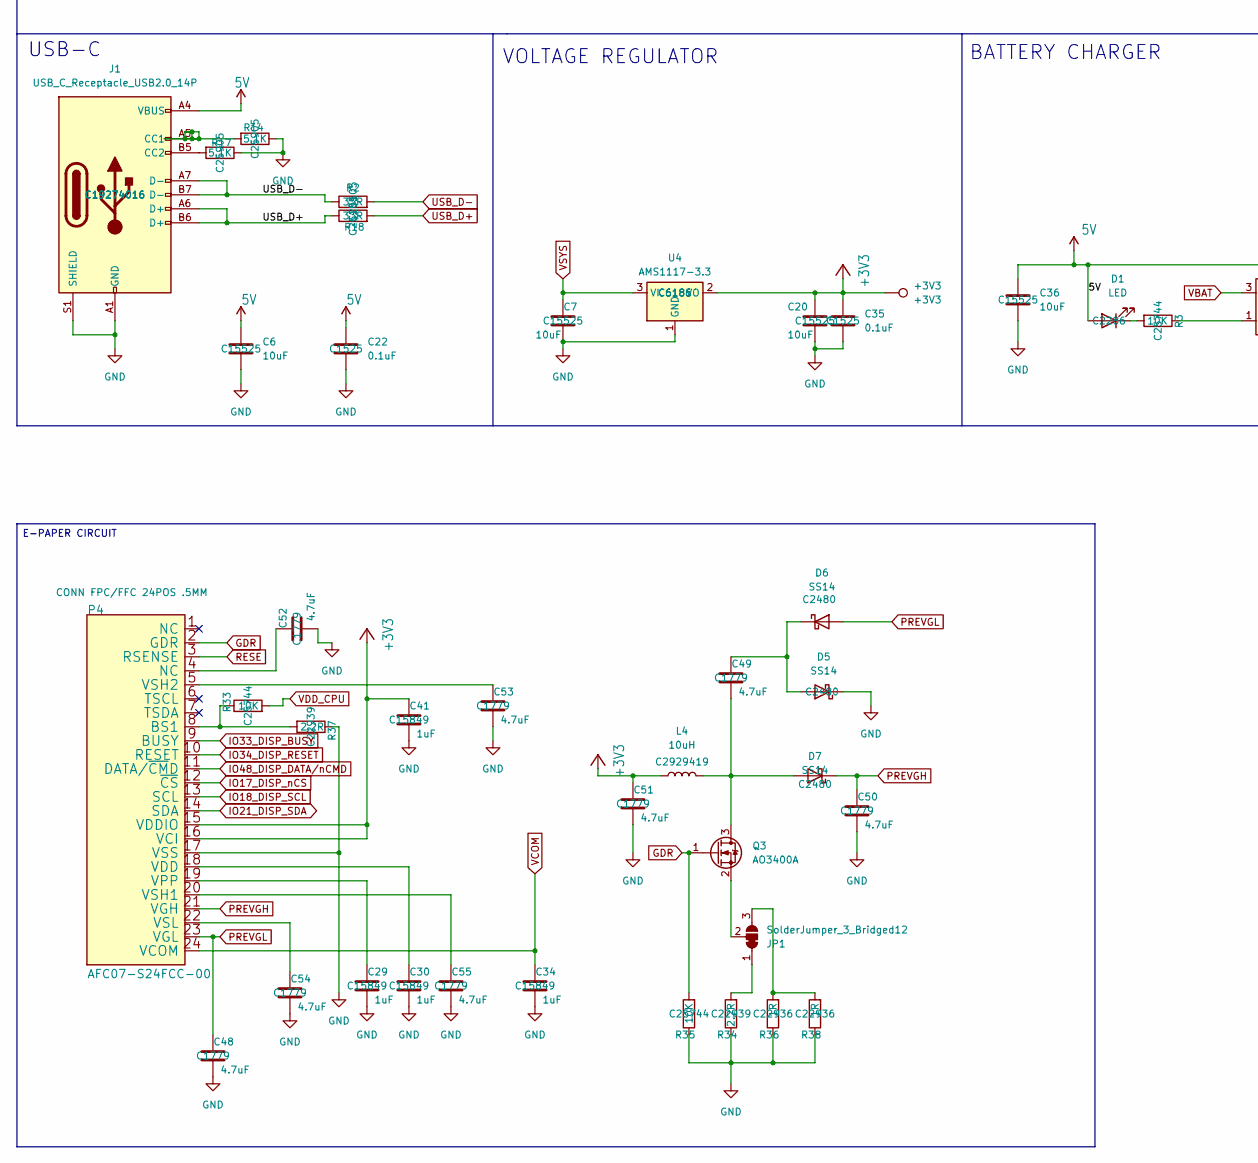
[picture p472: schematic hardware.kicad_sch, part in row 2, column 1]

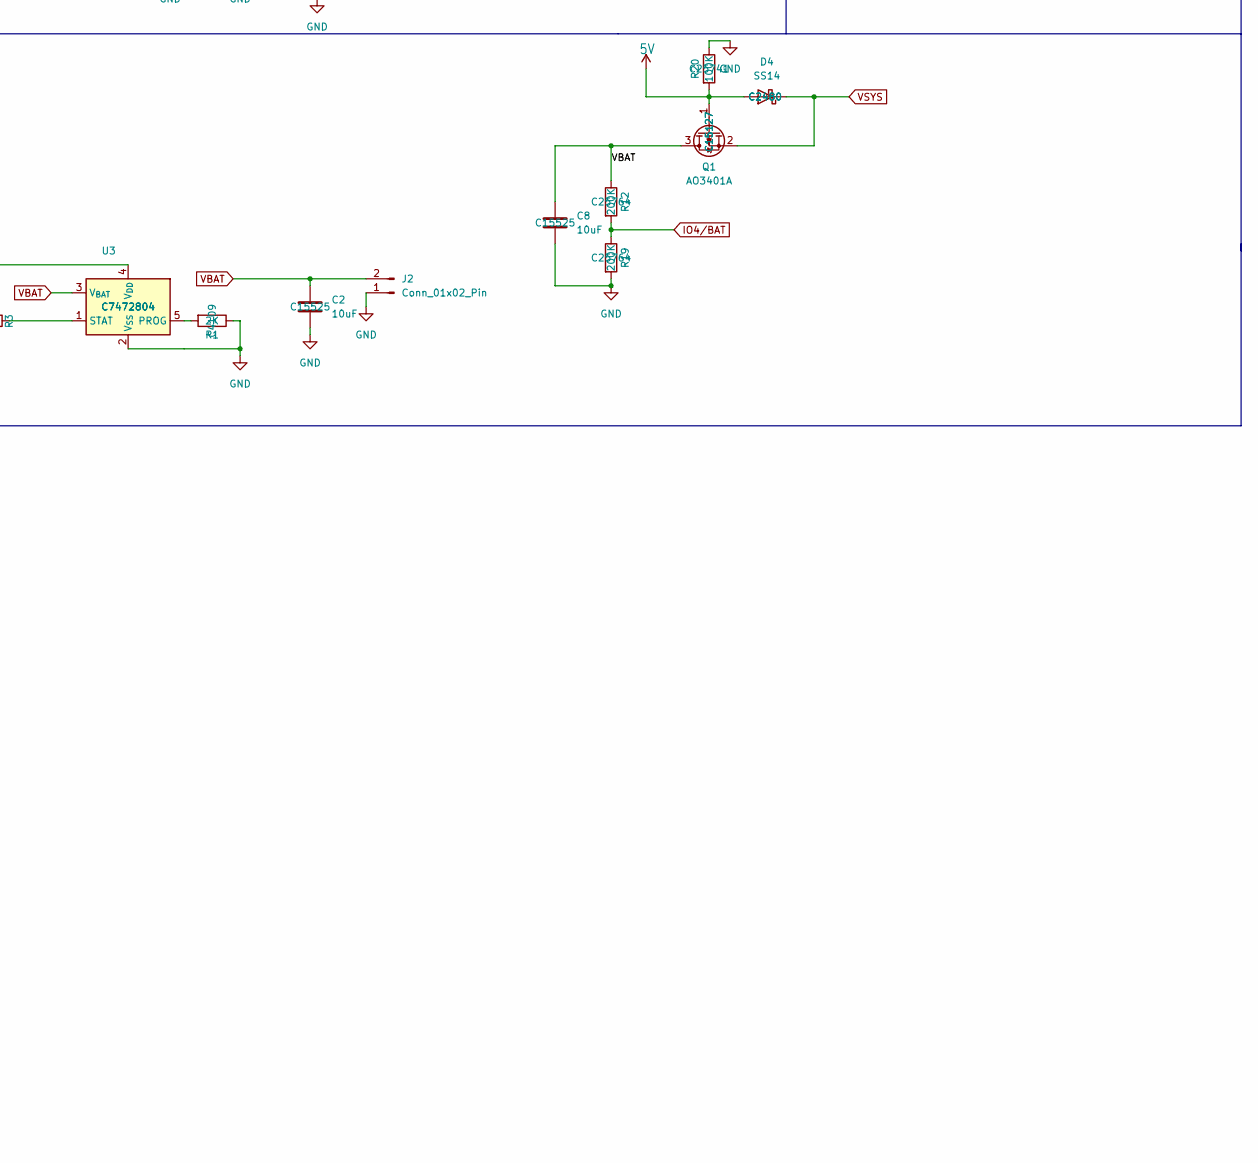
[picture p473: schematic hardware.kicad_sch, part in row 2, column 2]

Parts:
+3V3: +3V3; TestPoint_Pad_D1.0mm
AE1: Antenna; Texas_SWRA117D_2.4GHz_Left
BTN1: BTN; SW_Push_1P1T_XKB_TS-1187A; MNF PART NUMBER C318884; LCSC C318884
C2, C3, C6, C7, C8, C16, C17, C20, C25, C36: 10uF; C_0402_1005Metric; MNF PART NUMBER C15525; LCSC C15525
C4, C33, C37, C38: 12pF; C_0402_1005Metric; MNF PART NUMBER C1547; LCSC C1547
C10, C11, C15, C18, C19, C22, C32, C35: 0.1uF; C_0402_1005Metric; MNF PART NUMBER C1525; LCSC C1525
C13, C26, C39: 1uF; C_0402_1005Metric; MNF PART NUMBER C52923; LCSC C52923
C14: DNP; C_0402_1005Metric
C29, C30, C34, C41: 1uF; C_0603_1608Metric; MNF PART NUMBER C15849; LCSC C15849
C31: 15pF; C_0402_1005Metric; MNF PART NUMBER C1548; LCSC C1548
C40: 10nF; C_0402_1005Metric; MNF PART NUMBER C15195; LCSC C15195
C48, C49, C50, C51, C52, C53, C54, C55: 4.7uF; C_0805_2012Metric; MNF PART NUMBER C1779; LCSC C1779
D1, D3: LED; LED_0603_1608Metric; MNF PART NUMBER C2286; LCSC C2286
D4, D5, D6, D7: SS14; D_SMA; MNF PART NUMBER C2480; LCSC C2480
DNP1: 15pF; C_0402_1005Metric; MNF PART NUMBER C1548; LCSC C1548
Flash1: Flash; SW_Push_1P1T_XKB_TS-1187A; MNF PART NUMBER C318884; LCSC C318884
J1: USB_C_Receptacle_USB2.0_14P; USB_C_Receptacle_HCTL_HC-TYPE-C-16P-01A; MNF PART NUMBER C19274016; LCSC C19274016
J2: Conn_01x02_Pin; PinSocket_1x02_P2.54mm_Vertical
J3, J5: Conn_01x18_Pin; PinHeader_1x18_P2.54mm_Vertical
JP1: SolderJumper_3_Bridged12; SolderJumper-3_P1.3mm_Bridged12_RoundedPad1.0x1.5mm_NumberL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
L3: 2nH; L_0402_1005Metric; MNF PART NUMBER C77103; LCSC C77103
L4: 10uH; L_Ferrocore_DLG-0403; MNF PART NUMBER C2929419; LCSC C2929419
L5: DNP; L_0402_1005Metric
L6: 4.7nH; L_0402_1005Metric; MNF PART NUMBER C13595; LCSC C13595
P4: AFC07-S24FCC-00; Jushuo_AFC07-S24FCA-00_1x24-1MP_P0.50_Horizontal; MNF PART NUMBER C11057; LCSC C11057
Q1: AO3401A; SOT-23; MNF PART NUMBER C15127; LCSC C15127
Q3: AO3400A; SOT-23; MNF PART NUMBER C20917; LCSC C20917
R1: 2K; R_0402_1005Metric; MNF PART NUMBER C4109; LCSC C4109
R2, R18: 33R; R_0402_1005Metric; MNF PART NUMBER C25105; LCSC C25105
R3, R4, R21, R22, R33, R35: 10K; R_0402_1005Metric; MNF PART NUMBER C25744; LCSC C25744
R12, R19: 200K; R_0402_1005Metric; MNF PART NUMBER C25764; LCSC C25764
R14, R17: 5.1K; R_0402_1005Metric; MNF PART NUMBER C25905; LCSC C25905
R20: 100K; R_0402_1005Metric; MNF PART NUMBER C25741; LCSC C25741
R23, R26, R27, R28, R29, R30: 0R; R_0402_1005Metric; MNF PART NUMBER C17168; LCSC C17168
R24, R25: 470R; R_0402_1005Metric; MNF PART NUMBER C25117; LCSC C25117
R31: DNP; R_0402_1005Metric
R34, R37: 2.2R; R_0603_1608Metric; MNF PART NUMBER C22939; LCSC C22939
R36, R38: 1R; R_0603_1608Metric; MNF PART NUMBER C22936; LCSC C22936
Reset1: Reset; SW_Push_1P1T_XKB_TS-1187A; MNF PART NUMBER C318884; LCSC C318884
U1: ESP32-S3; QFN-56-1EP_7x7mm_P0.4mm_EP4x4mm; MNF PART NUMBER C2913196; LCSC C2913194
U2: W25Q128JVS; SOIC-8_5.3x5.3mm_P1.27mm; MNF PART NUMBER C97521; LCSC C97521
U3: MCP73831-2-OT; SOT-23-5; MNF PART NUMBER C7472804; LCSC C7472804
U4: AMS1117-3.3; SOT-223-3_TabPin2; MNF PART NUMBER C6186; LCSC C6186
Y1: 32.768 kHz; Crystal_SMD_3215-2Pin_3.2x1.5mm; MNF PART NUMBER C32346; LCSC C32346
Y2: 40MHz(10ppm); Crystal_SMD_2520-4Pin_2.5x2.0mm; MNF PART NUMBER C5261125; LCSC C5261125

Connections:
5V: C6.1, C16.1, C22.1, C36.1, D1.2 (A), D4.2 (A), J1.A4 (VBUS), J1.A9 (VBUS), J1.B4 (VBUS), J1.B9 (VBUS), J3.16, Q1.1 (G), R20.2, U3.4 (V_{DD})
EN: C15.1, R22.1, Reset1.2, U1.4 (CHIP_PU)
GDR: P4.2 (GDR), Q3.1 (G), R35.2
GND: AE1.2 (PCB_Trace), BTN1.1, C2.2, C3.2, C4.2, C6.2, C7.2, C8.2, C10.2, C11.2, C13.2, C14.2, C15.2, C16.2, C17.2, C18.2, C19.2, C20.2, C22.2, C25.2, C26.2, C29.2, C30.2, C31.2, C32.2, C33.1, C34.2, C35.2, C36.2, C37.2, C38.2, C39.2, C40.2, C41.2, C48.2, C50.2, C51.2, C52.2, C53.2, C54.2, C55.2, D5.1 (K), DNP1.2, Flash1.1, J1.A1 (GND), J1.A12 (GND), J1.B1 (GND), J1.B12 (GND), J1.S1 (SHIELD), J2.1, J3.17, J3.18, P4.17 (VSS), R1.1, R14.1, R17.1, R19.2, R20.1, R25.2, R34.1, R35.1, R36.1, R37.1, R38.1, Reset1.1, U1.57 (GND), U2.4 (GND), U3.2 (V_{SS}), U4.1 (GND), Y2.2, Y2.4
IO0: Flash1.2, J5.1, R21.2, U1.5 (GPIO0)
IO1: D3.2 (A), U1.6 (GPIO1)
IO2: J5.2, U1.7 (GPIO2)
IO3: J3.5, U1.8 (GPIO3)
IO4/BAT: R12.2, R19.1, U1.9 (GPIO4)
IO5: J3.6, U1.10 (GPIO5)
IO6: J3.1, U1.11 (GPIO6)
IO7: J3.7, U1.12 (GPIO7)
IO8: J3.8, U1.13 (GPIO8)
IO9: J3.2, U1.14 (GPIO9)
IO10: J3.3, U1.15 (GPIO10)
IO11: J3.4, U1.16 (GPIO11)
IO12: J3.9, U1.17 (GPIO12)
IO13: J3.10, U1.18 (GPIO13)
IO14: BTN1.2, J3.11, R4.2, U1.19 (GPIO14)
IO17: J3.12, P4.12 (~CS), U1.23 (GPIO17)
IO18: J3.13, P4.13 (SCL), U1.24 (GPIO18)
IO21: J3.14, P4.14 (SDA), U1.27 (GPIO21)
IO33: J5.17, P4.9 (BUSY), U1.38 (GPIO33)
IO34: J5.16, P4.10 (RESET), U1.39 (GPIO34)
IO35: J5.15, U1.40 (GPIO35)
IO36: J5.13, U1.41 (GPIO36)
IO37: J5.11, U1.42 (GPIO37)
IO38: J5.5, U1.43 (GPIO38)
IO39: J5.4, U1.44 (MTCK)
IO40: J5.6, U1.45 (MTDO)
IO41: J5.7, U1.47 (MTDI)
IO42: J5.12, U1.48 (MTMS)
IO45: J5.9, R31.1, U1.51 (GPIO45)
IO46: J5.8, U1.52 (GPIO46)
IO47: J5.14, U1.37 (SPICLK_P)
IO48: J5.18, P4.11 (DATA/~CMD), U1.36 (SPICLK_N)
unnamed: AE1.1 (FEED), C31.1, L5.2, L6.2
unnamed: C4.1, R23.1, Y2.1
unnamed: C14.1, L5.1
unnamed: C19.1, L3.2, U1.2 (VDD3P3), U1.3 (VDD3P3)
unnamed: C52.1, P4.4 (NC)
unnamed: D1.1 (K), R3.2
unnamed: D3.1 (K), R25.1
unnamed: C49.1, D5.2 (A), D6.1 (K)
unnamed: C49.2, D7.2 (A), L4.2, Q3.3 (D)
unnamed: J1.A5 (CC1), R14.2
unnamed: J1.B5 (CC2), R17.2
unnamed: JP1.1 (A), R34.2
unnamed: JP1.3 (B), R36.2, R38.2
unnamed: JP1.2 (C), Q3.2 (S)
unnamed: P4.8 (BS1), R33.1, R37.2
unnamed: C30.1, P4.18 (VDD)
unnamed: C29.1, P4.19 (VPP)
unnamed: C55.1, P4.20 (VSH1)
unnamed: C53.1, P4.5 (VSH2)
unnamed: C54.1, P4.22 (VSL)
unnamed: DNP1.1, L6.1, U1.1 (LNA_IN)
unnamed: R28.1, U1.33 (SPICLK)
unnamed: R26.1, U1.35 (SPID)
unnamed: R30.1, U1.30 (SPIHD)
unnamed: R27.1, U1.34 (SPIQ)
unnamed: R29.1, U1.31 (SPIWP)
unnamed: R24.1, U1.49 (U0TXD)
unnamed: C33.2, U1.53 (XTAL_N), Y2.3
unnamed: R23.2, U1.54 (XTAL_P)
unnamed: R1.2, U3.5 (PROG)
unnamed: R3.1, U3.1 (STAT)
PREVGH: C50.1, D7.1 (K), P4.21 (VGH)
PREVGL: C48.1, D6.2 (A), P4.23 (VGL)
RESE: P4.3 (RSENSE)
RX: J5.10, U1.50 (U0RXD)
SPICS0: U1.32 (SPICS0), U2.1 (~CS)
SPID: R26.2, U2.5 (DI/IO_{0})
SPIHD: R30.2, U2.7 (~HOLD/~RESET/IO_{3})
SPIQ: R27.2, U2.2 (DO/IO_{1})
SPISCK: R28.2, U2.6 (CLK)
SPIWP: R29.2, U2.3 (~WP/IO_{2})
TX: J5.3, R24.2
USB_D+: J1.A6 (D+), J1.B6 (D+), R18.1, R18.2, U1.26 (GPIO20/USB_D+)
USB_D-: J1.A7 (D-), J1.B7 (D-), R2.1, R2.2, U1.25 (GPIO19/USB_D-)
VBAT: C2.1, C8.1, J2.2, Q1.3 (D), R12.1, U3.3 (V_{BAT})
VCOM: C34.1, P4.24 (VCOM)
VDD_CPU: +3V3.1, C3.1, C10.1, C11.1, C17.1, C18.1, C20.1, C25.1, C26.1, C35.1, C39.1, C40.1, C41.1, C51.1, J3.15, L3.1, L4.1, P4.15 (VDDIO), P4.16 (VCI), R4.1, R21.1, R22.2, R31.2, R33.2, U1.20 (VDD3P3_RTC), U1.46 (VDD3P3_CPU), U1.55 (VDDA), U1.56 (VDDA), U4.2 (VO)
VDD_SPI: C13.1, C32.1, U1.29 (VDD_SPI), U2.8 (VCC)
VSYS: C7.1, D4.1 (K), Q1.2 (S), U4.3 (VI)
XTAL32N: C37.1, U1.22 (XTAL_32K_N), Y1.1
XTAL32P: C38.1, U1.21 (XTAL_32K_P), Y1.2

Notes on the sheet:
BATTERY CHARGER
VOLTAGE REGULATOR
500mA
LEDS
MCU
HEADER PINS
MEMORY
POWER AND FILTERING
IO45/IO46: pulldown~~{}
USB-C
E-PAPER CIRCUIT

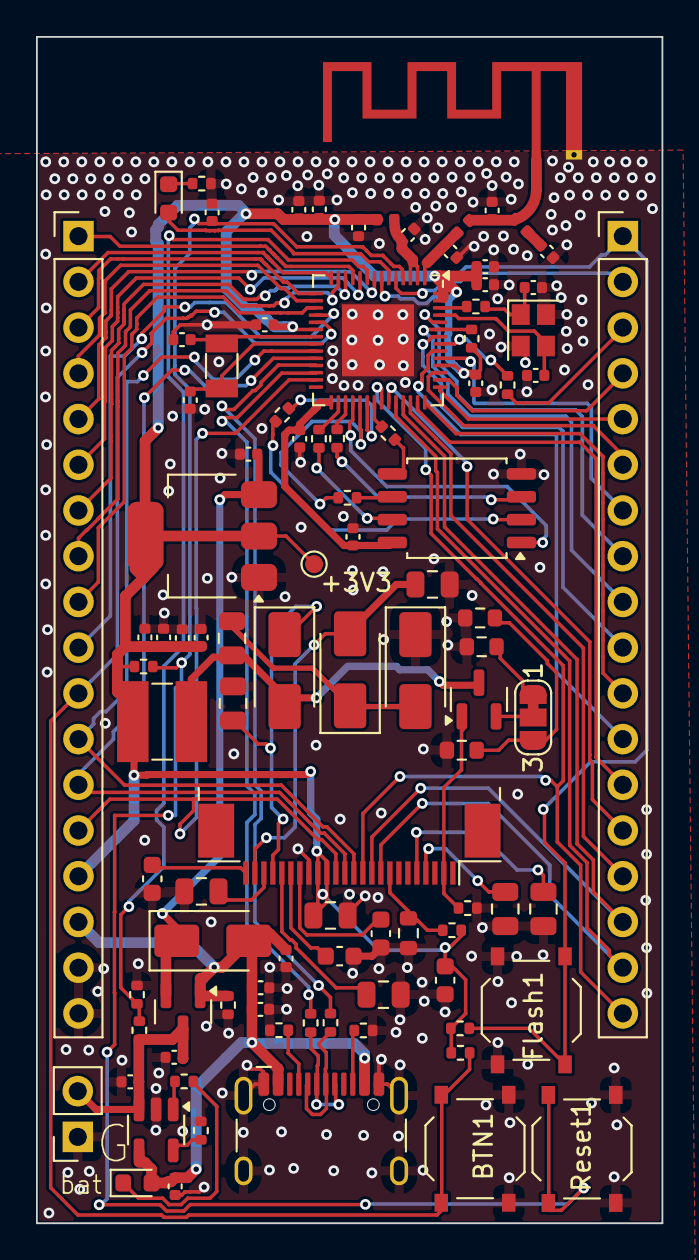
[picture p474: board hardware.kicad_pcb from above]

Board: 2 copper layers, 34.8 x 65.9 mm, 97 parts (0 on the bottom side), 86 nets.
