rompasaurus/regardedPal/hardware-design/examples/06-unexpected-maker-s3/series_d/KiCAD/EdgeS3D_Carrier_P1/EdgeS3D_Carrier_P1.kicad_pcb

## KiCad design hardware-design/examples/06-unexpected-maker-s3/series_d/KiCAD/EdgeS3D_Carrier_P1/EdgeS3D_Carrier_P1.kicad_pcb (2026-04-15)

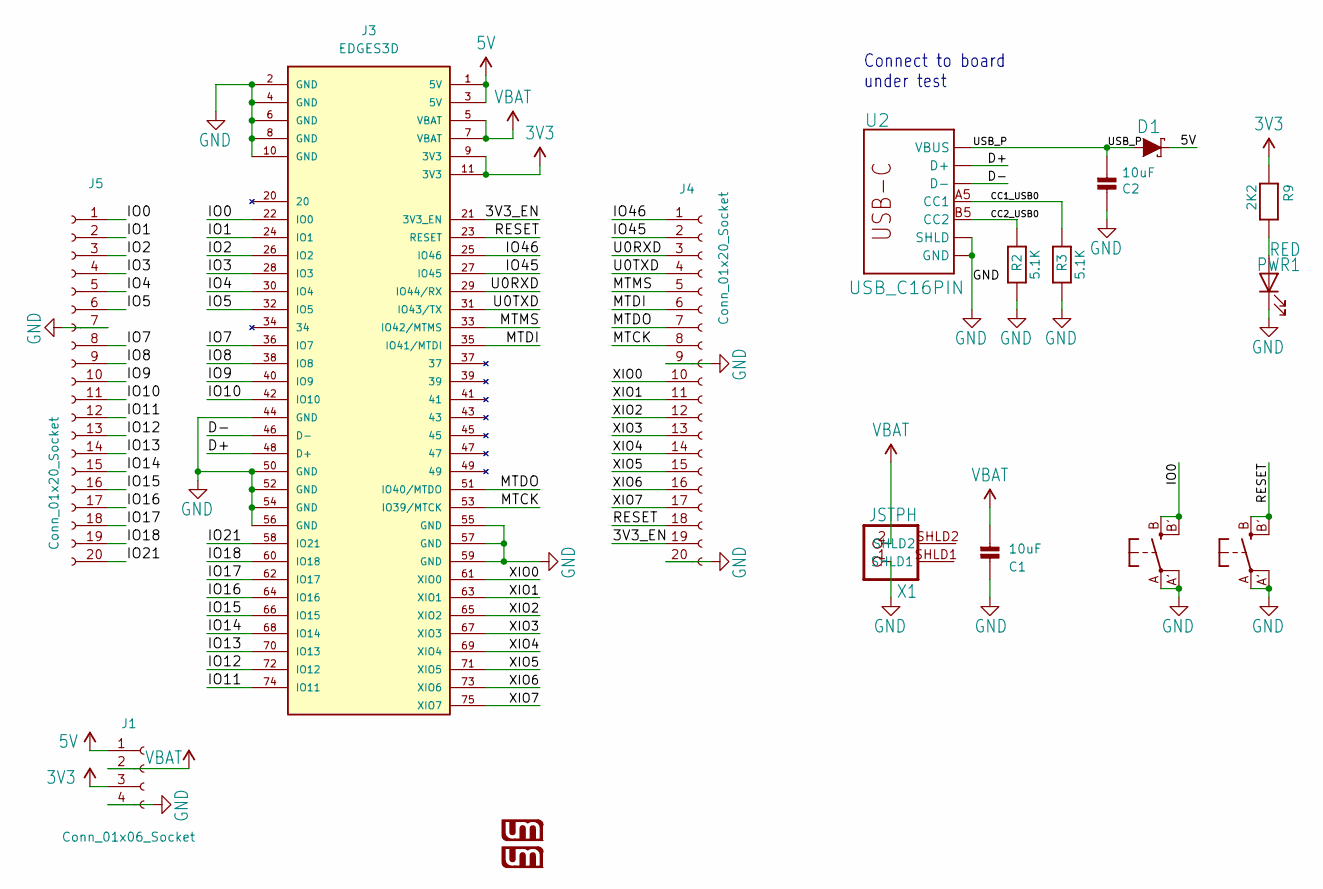
[picture p475: schematic EdgeS3D_Carrier_P1.kicad_sch, EdgeS3D Carrier Reference]

Parts:
C1, C2: 10uF; C_0603_1608Metric
D1: DIODE-SCHOTTKYWIDE; SOD-523-MSK4010
J1: Conn_01x06_Socket; PinHeader_1x04_P2.54mm_Vertical
J3: EDGES3D; AMPHENOL_MDT275B03001; PARTREV 7
J4, J5: Conn_01x20_Socket; PinHeader_1x20_P2.54mm_Vertical
PWR1: RED; LED_0805_2012Metric
R2, R3: 5.1K; R_0402_1005Metric
R9: 2K2; _0805MP
SW1, SW2: KMR2; BTN_KMR2_4.6X2.8
U2: USB_C16PIN; USB-C-16P-LESSPASTE-2-FIxed
U$1, U$2: UM_LOGONEW_SMALL; UM_LOGO_NEW_SMALL
X1: JSTPH; JST-PICOBLADE

Connections:
3V3: J1.3, J3.9 (3V3), J3.11 (3V3), R9.1
5V: D1.C, J1.1, J3.1 (5V), J3.3 (5V)
/3V3_EN: J3.21 (3V3_EN), J4.19
/CC1_USB0: R3.2, U2.A5 (CC1)
/CC2_USB0: R2.2, U2.B5 (CC2)
/D+: J3.48 (D+), U2.A6 (D+), U2.B6 (D+)
/D-: J3.46 (D-), U2.A7 (D-), U2.B7 (D-)
/IO0: J3.22 (IO0), J5.1, SW1.B (S), SW1.B' (S1)
/IO1: J3.24 (IO1), J5.2
/IO2: J3.26 (IO2), J5.3
/IO3: J3.28 (IO3), J5.4
/IO4: J3.30 (IO4), J5.5
/IO5: J3.32 (IO5), J5.6
/IO7: J3.36 (IO7), J5.8
/IO8: J3.38 (IO8), J5.9
/IO9: J3.40 (IO9), J5.10
/IO10: J3.42 (IO10), J5.11
/IO11: J3.74 (IO11), J5.12
/IO12: J3.72 (IO12), J5.13
/IO13: J3.70 (IO13), J5.14
/IO14: J3.68 (IO14), J5.15
/IO15: J3.66 (IO15), J5.16
/IO16: J3.64 (IO16), J5.17
/IO17: J3.62 (IO17), J5.18
/IO18: J3.60 (IO18), J5.19
/IO21: J3.58 (IO21), J5.20
/IO45: J3.27 (IO45), J4.2
/IO46: J3.25 (IO46), J4.1
/MTCK: J3.53 (IO39/MTCK), J4.8
/MTDI: J3.35 (IO41/MTDI), J4.6
/MTDO: J3.51 (IO40/MTDO), J4.7
/MTMS: J3.33 (IO42/MTMS), J4.5
/RESET: J3.23 (RESET), J4.18, SW2.B (S), SW2.B' (S1)
/U0RXD: J3.29 (IO44/RX), J4.3
/U0TXD: J3.31 (IO43/TX), J4.4
/USB_P: C2.2, D1.A, U2.VBUS1 (VBUS), U2.VBUS2 (VBUS)
/XIO0: J3.61 (XIO0), J4.10
/XIO1: J3.63 (XIO1), J4.11
/XIO2: J3.65 (XIO2), J4.12
/XIO3: J3.67 (XIO3), J4.13
/XIO4: J3.69 (XIO4), J4.14
/XIO5: J3.71 (XIO5), J4.15
/XIO6: J3.73 (XIO6), J4.16
/XIO7: J3.75 (XIO7), J4.17
GND: C1.1, C2.1, J1.4, J3.2 (GND), J3.4 (GND), J3.6 (GND), J3.8 (GND), J3.10 (GND), J3.44 (GND), J3.50 (GND), J3.52 (GND), J3.54 (GND), J3.55 (GND), J3.56 (GND), J3.57 (GND), J3.59 (GND), J4.9, J4.20, J5.7, PWR1.1 (K), R2.1, R3.1, SW1.A, SW1.A' (P1), SW2.A, SW2.A' (P1), U2.GND, U2.GND2 (GND), U2.SHLD, U2.SHLD2 (SHLD), U2.SHLD3 (SHLD), U2.SHLD4 (SHLD), U2.SHLD5 (SHLD), U2.SHLD6 (SHLD), U2.SHLD7 (SHLD), U2.SHLD8 (SHLD), X1.1
unnamed: PWR1.2 (A), R9.2
VBAT: C1.2, J1.2, J3.5 (VBAT), J3.7 (VBAT), X1.2

Notes on the sheet:
Connect to board under test

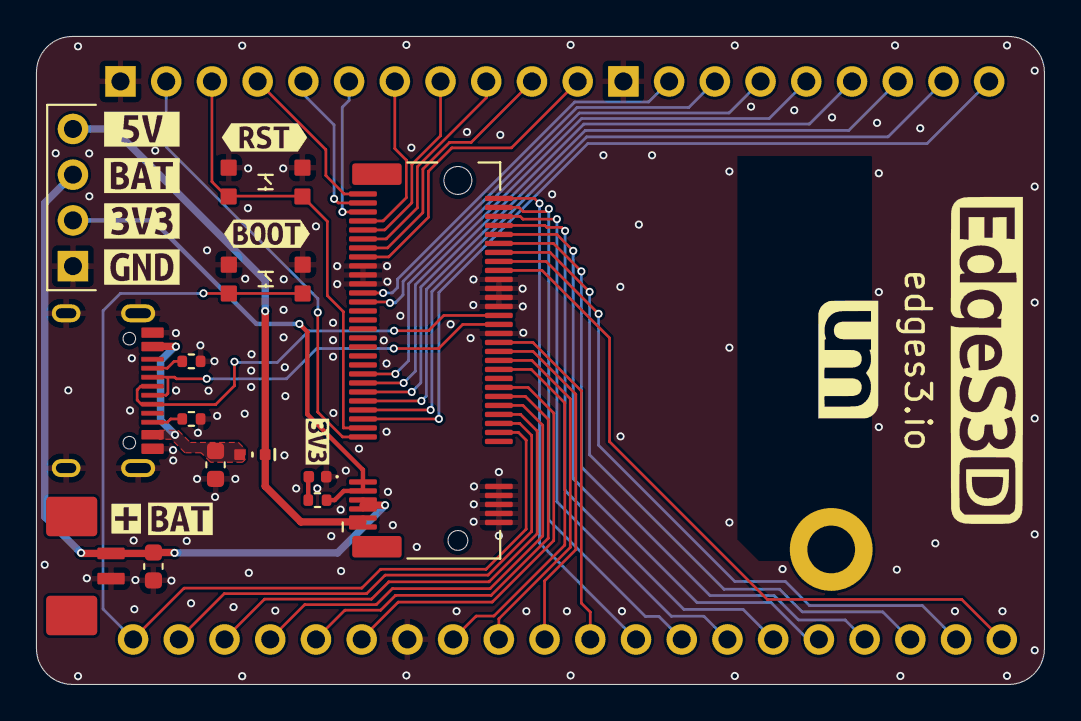
[picture p476: board EdgeS3D_Carrier_P1.kicad_pcb from above]

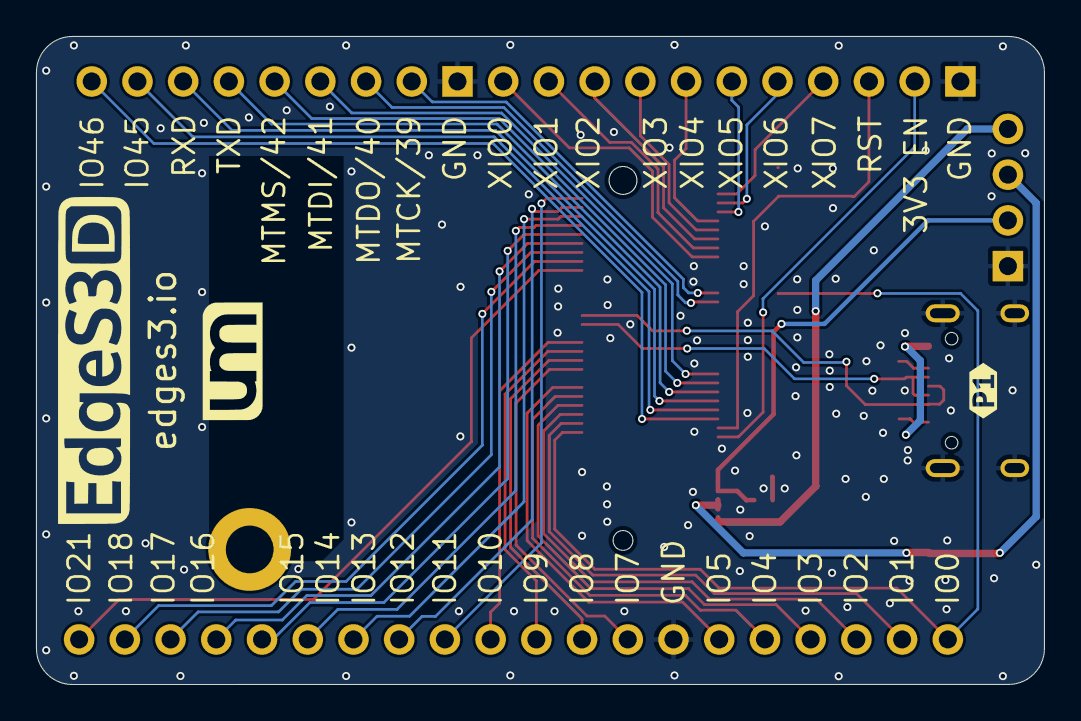
[picture p477: board EdgeS3D_Carrier_P1.kicad_pcb from below]

Board: 2 copper layers, 56.0 x 36.0 mm, 27 parts (2 on the bottom side), 47 nets.

Other parts of the board:
kibuzzard-66BFF55A: G***; kibuzzard-66BFF55A
kibuzzard-66BFF56B: G***; kibuzzard-66BFF56B
kibuzzard-66C05786: G***; kibuzzard-66C05786
kibuzzard-6857AC6A: G***; kibuzzard-6857AC6A
kibuzzard-6857AC7B: G***; kibuzzard-6857AC7B
kibuzzard-6857AC8E: G***; kibuzzard-6857AC8E
kibuzzard-6857AC89: G***; kibuzzard-6857AC89
kibuzzard-6857AD16: G***; kibuzzard-6857AD16
kibuzzard-6857ADA7: G***; kibuzzard-6857ADA7
kibuzzard-664315DB: G***; kibuzzard-664315DB
