rompasaurus/regardedPal/hardware-design/examples/05-olimex-devkit-lipo/HARDWARE/ESP32-DevKit-LiPo-Rev.B/ESP32-DevKit-Lipo_Rev_B.kicad_pcb

## KiCad design hardware-design/examples/05-olimex-devkit-lipo/HARDWARE/ESP32-DevKit-LiPo-Rev.B/ESP32-DevKit-Lipo_Rev_B.kicad_pcb (2026-04-15, an earlier design)

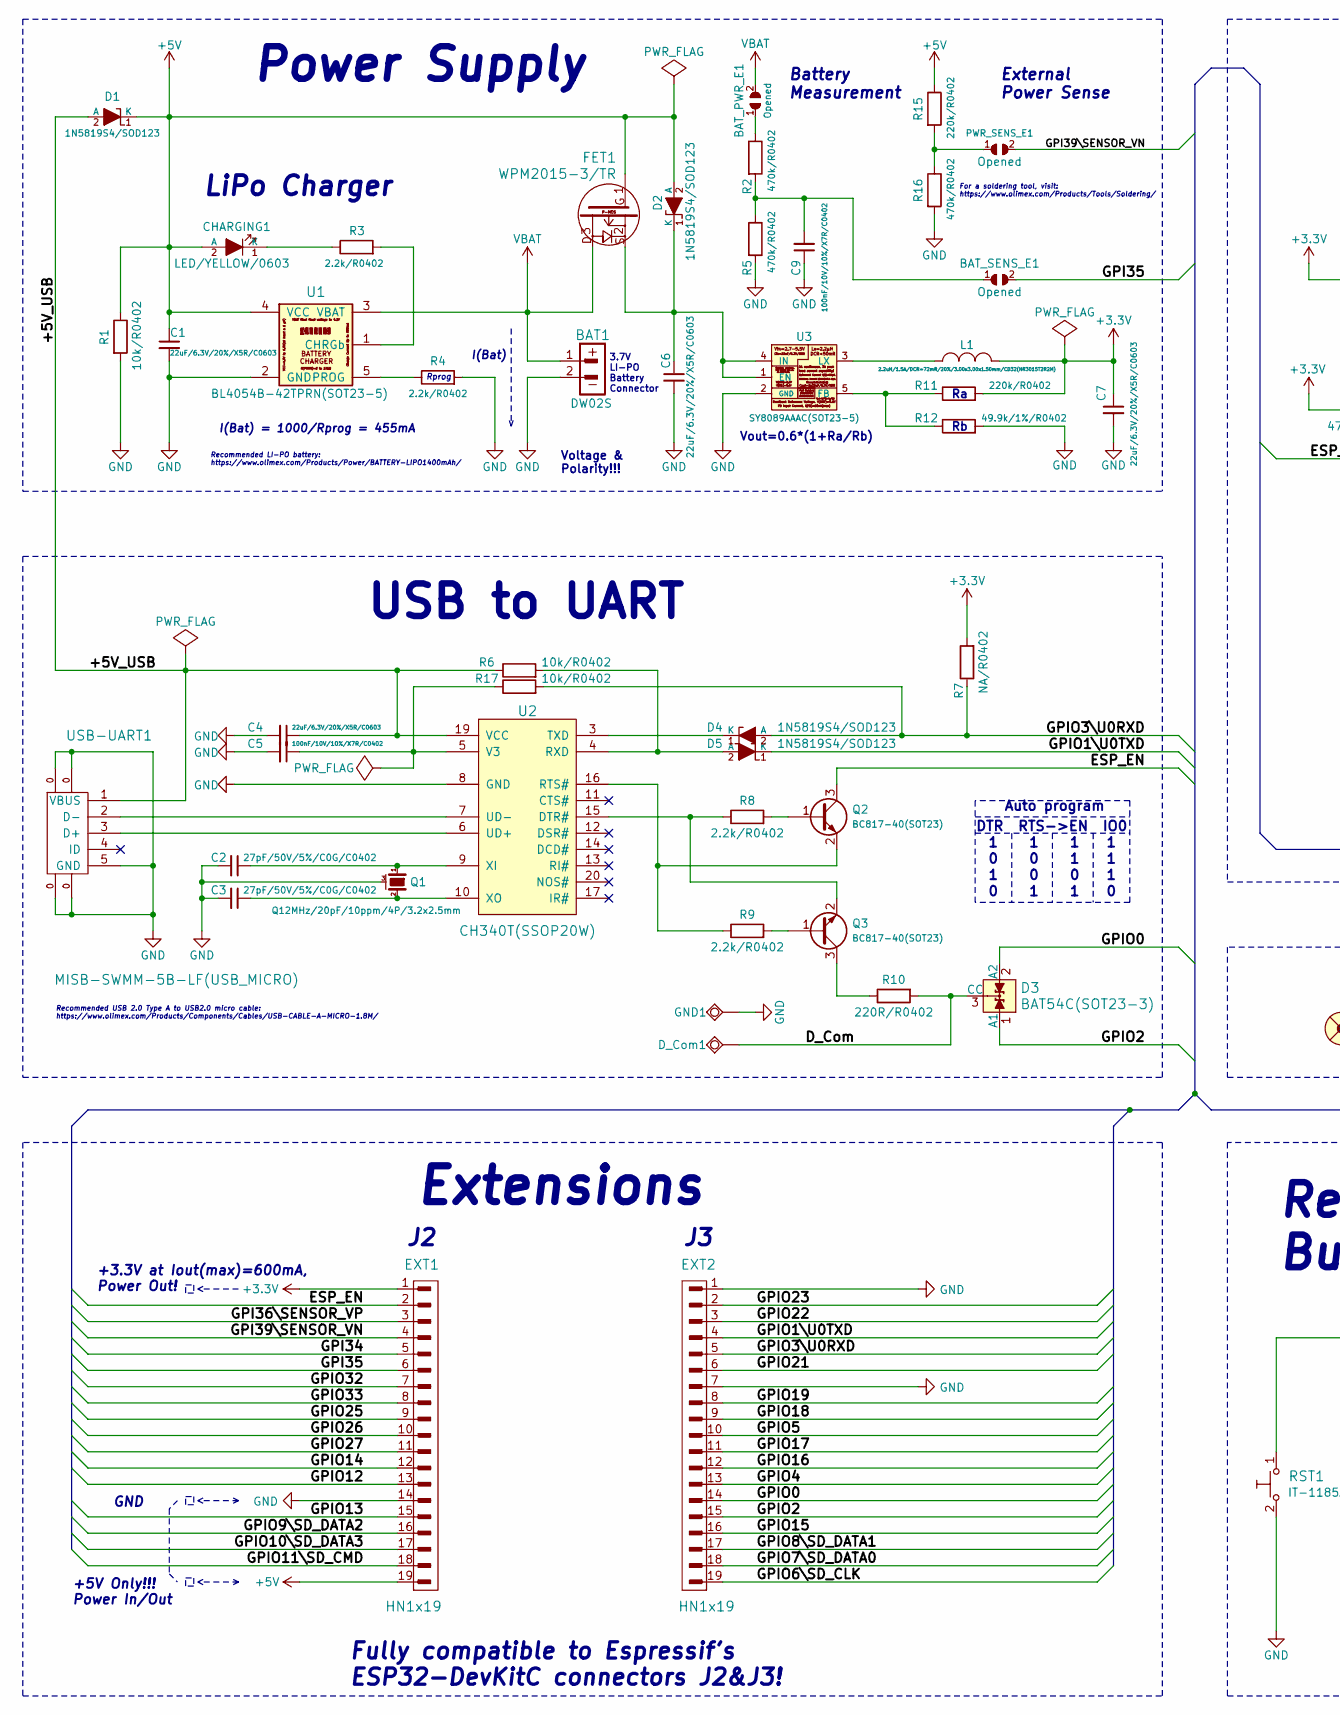
[picture p478: schematic ESP32-DevKit-Lipo_Rev_B.sch, ESP32-DevKit-Lipo, part in row 1, column 1]

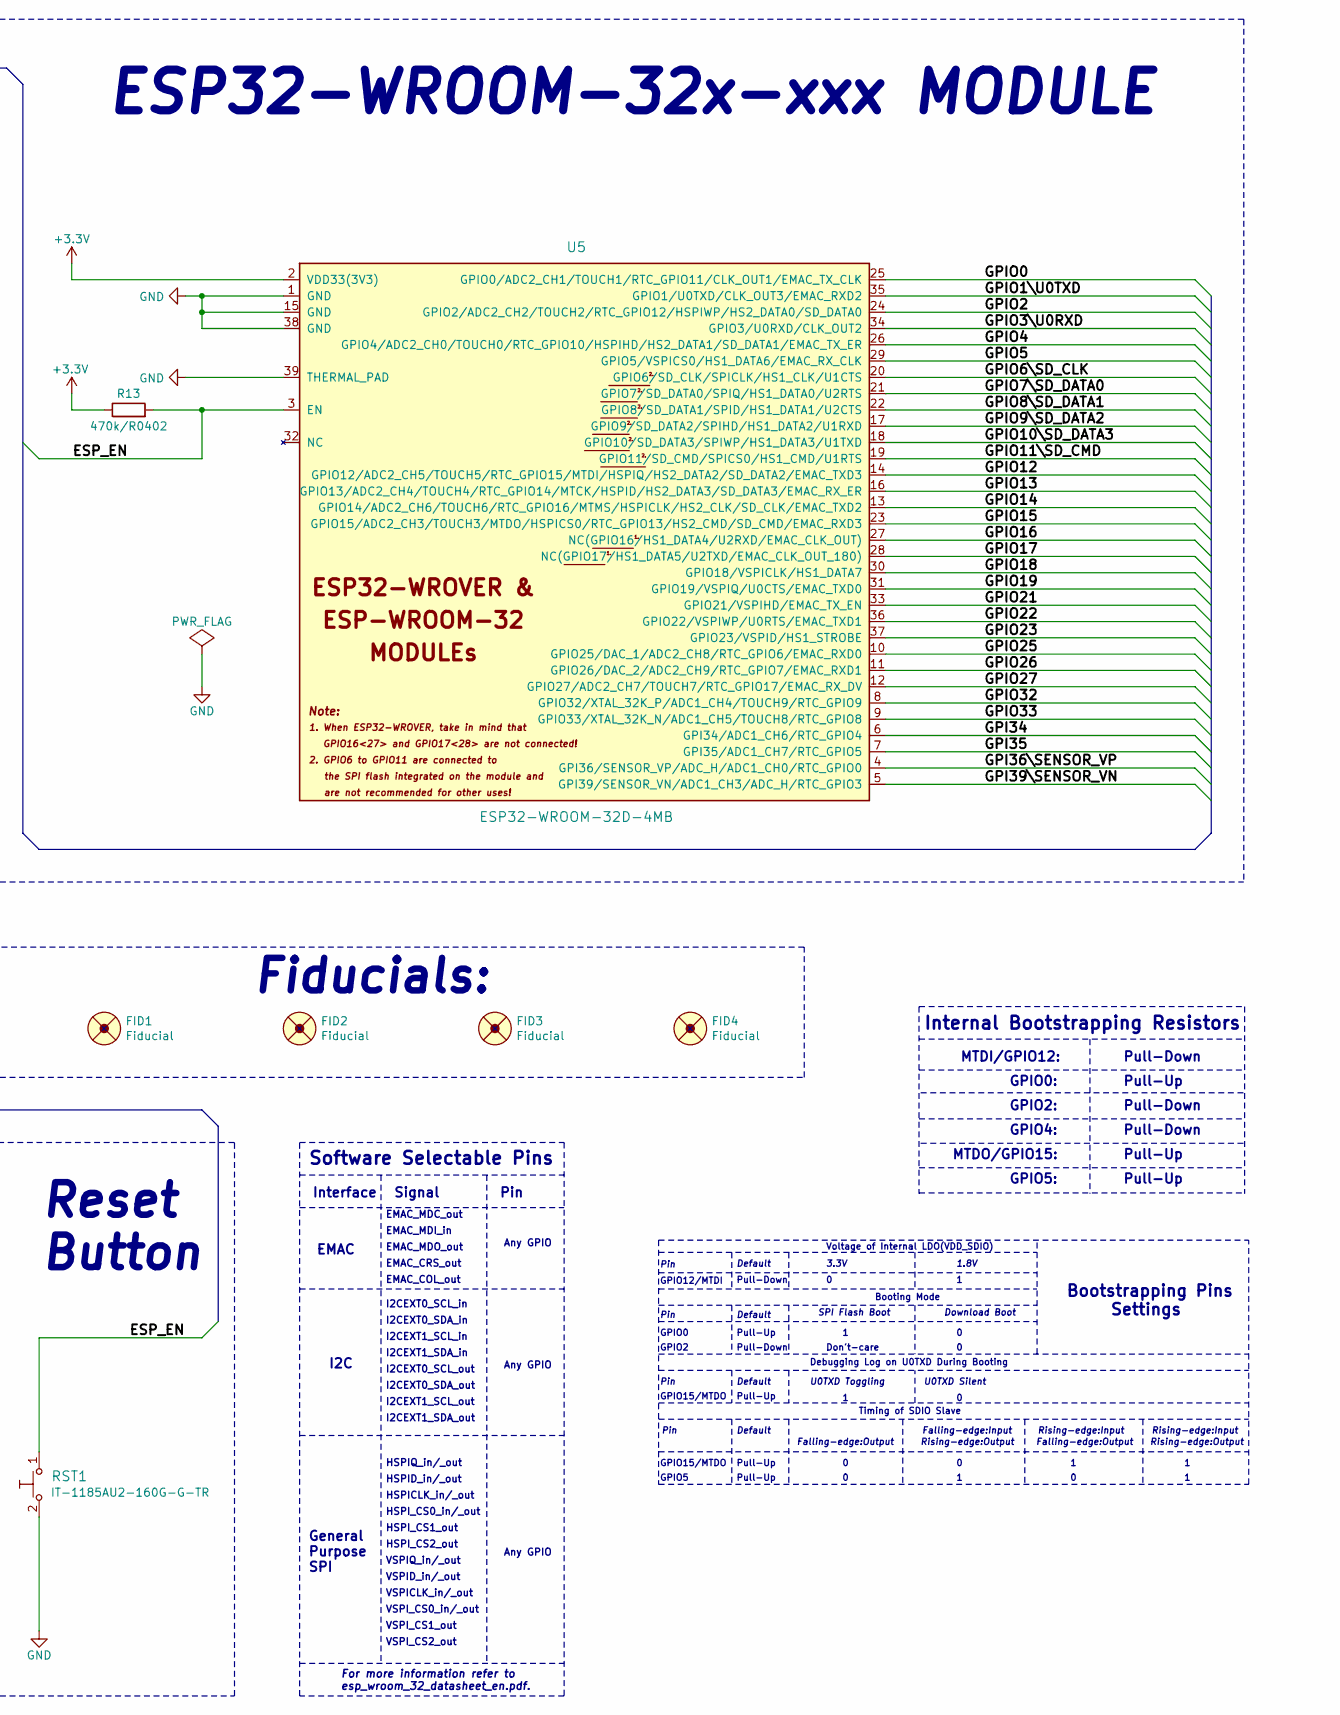
[picture p479: schematic ESP32-DevKit-Lipo_Rev_B.sch, ESP32-DevKit-Lipo, part in row 1, column 2]

Parts:
BAT1: DW02S; LIPO_BAT_VERTICAL_DW02S
BAT_PWR_E1: Opened; SJ_1_SMALLER
BAT_SENS_E1: Opened; SJ_1_SMALLER
C1, C4, C6, C7: 22uF/6.3V/20%/X5R/C0603; C_0603_5MIL_DWS
C2, C3: 27pF/50V/5%/C0G/C0402; C_0402_5MIL_DWS
C5, C9: 100nF/10V/10%/X7R/C0402; C_0402_5MIL_DWS
CHARGING1: LED/YELLOW/0603; LED_0603_KA
D1, D2, D4, D5: 1N5819S4/SOD123; SOD-123_1C-2A_KA
D3: BAT54C(SOT23-3); SOT23-3
D_Com1: TESTPAD; TESTPAD_40-ROUND
EXT1, EXT2: HN1x19
FET1: WPM2015-3/TR; SOT23
FID1, FID2, FID3, FID4: Fiducial; Fiducial1x3
GND1: TESTPAD; TESTPAD_40-ROUND
L1: 2.2uH/1.5A/DCR=72mR/20%/3.00x3.00x1.50mm/CD32(NR3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; CD32
PWR_SENS_E1: Opened; SJ_1_SMALLER
Q1: Q12MHz/20pF/10ppm/4P/3.2x2.5mm; TSX-3.2x2.5mm_GND(3)
Q2, Q3: BC817-40(SOT23); SOT23
R1, R6, R17: 10k/R0402; R_0402_5MIL_DWS
R2, R5, R13, R16: 470k/R0402; R_0402_5MIL_DWS
R3, R4, R8, R9: 2.2k/R0402; R_0402_5MIL_DWS
R7: NA/R0402; R_0402_5MIL_DWS
R10: 220R/R0402; R_0402_5MIL_DWS
R11, R15: 220k/R0402; R_0402_5MIL_DWS
R12: 49.9k/1%/R0402; R_0402_5MIL_DWS
RST1: IT-1185AU2-160G-G-TR; IT1185AU2_V2
U1: BL4054B-42TPRN(SOT23-5); SOT-23-5
U2: CH340T(SSOP20W); SSOP-20W
U3: SY8089AAAC(SOT23-5); SOT-23-5
U5: ESP32-WROOM-32D-4MB; ESP32-WROVER_MODULE
USB-UART1: MISB-SWMM-5B-LF(USB_MICRO); USB-MICRO_MISB-SWMM-5B_LF

Connections:
+3V3: C7.1, EXT1.1, L1.2, R7.2, R11.2, R13.1, U5.2 (VDD33(3V3))
+5V: C1.1, CHARGING1.2 (A), D1.1 (K), D2.2 (A), EXT1.19, FET1.1, R1.1, R15.1, U1.4 (VCC)
/+5V_USB: C4.1, D1.2 (A), R6.1, U2.19 (VCC), USB-UART1.1 (VBUS)
/D_Com: D3.3 (CC), D_Com1.1, R10.2
/ESP_EN: EXT1.2, Q2.3 (C), R13.2, RST1.1, U5.3 (EN)
/GPI34: EXT1.5, U5.6 (GPI34/ADC1_CH6/RTC_GPIO4)
/GPI35: BAT_SENS_E1.2, EXT1.6, U5.7 (GPI35/ADC1_CH7/RTC_GPIO5)
/GPI36\SENSOR_VP: EXT1.3, U5.4 (GPI36/SENSOR_VP/ADC_H/ADC1_CH0/RTC_GPIO0)
/GPI39\SENSOR_VN: EXT1.4, PWR_SENS_E1.2, U5.5 (GPI39/SENSOR_VN/ADC1_CH3/ADC_H/RTC_GPIO3)
/GPIO0: D3.2 (A2), EXT2.14, U5.25 (GPIO0/ADC2_CH1/TOUCH1/RTC_GPIO11/CLK_OU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)
/GPIO1\U0TXD: D5.1 (K), EXT2.4, U5.35 (GPIO1/U0TXD/CLK_OUT3/EMAC_RXD2)
/GPIO2: D3.1 (A1), EXT2.15, U5.24 (GPIO2/ADC2_CH2/TOUCH2/RTC_GPIO12/HSPIWP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)
/GPIO3\U0RXD: D4.2 (A), EXT2.5, R7.1, R17.2, U5.34 (GPIO3/U0RXD/CLK_OUT2)
/GPIO4: EXT2.13, U5.26 (GPIO4/ADC2_CH0/TOUCH0/RTC_GPIO10/HSPIHD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)
/GPIO5: EXT2.10, U5.29 (GPIO5/VSPICS0/HS1_DATA6/EMAC_RX_CLK)
/GPIO6\SD_CLK: EXT2.19, U5.20 (GPIO6/SD_CLK/SPICLK/HS1_CLK/U1CTS)
/GPIO7\SD_DATA0: EXT2.18, U5.21 (GPIO7/SD_DATA0/SPIQ/HS1_DATA0/U2RTS)
/GPIO8\SD_DATA1: EXT2.17, U5.22 (GPIO8/SD_DATA1/SPID/HS1_DATA1/U2CTS)
/GPIO9\SD_DATA2: EXT1.16, U5.17 (GPIO9/SD_DATA2/SPIHD/HS1_DATA2/U1RXD)
/GPIO10\SD_DATA3: EXT1.17, U5.18 (GPIO10/SD_DATA3/SPIWP/HS1_DATA3/U1TXD)
/GPIO11\SD_CMD: EXT1.18, U5.19 (GPIO11/SD_CMD/SPICS0/HS1_CMD/U1RTS)
/GPIO12: EXT1.13, U5.14 (GPIO12/ADC2_CH5/TOUCH5/RTC_GPIO15/MTDI/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)
/GPIO13: EXT1.15, U5.16 (GPIO13/ADC2_CH4/TOUCH4/RTC_GPIO14/MTCK/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)
/GPIO14: EXT1.12, U5.13 (GPIO14/ADC2_CH6/TOUCH6/RTC_GPIO16/MTMS/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)
/GPIO15: EXT2.16, U5.23 (GPIO15/ADC2_CH3/TOUCH3/MTDO/HSPICS0/RTC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)
/GPIO16: EXT2.12, U5.27 (NC(GPIO16/HS1_DATA4/U2RXD/EMAC_CLK_OUT))
/GPIO17: EXT2.11, U5.28 (NC(GPIO17/HS1_DATA5/U2TXD/EMAC_CLK_OUT_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)
/GPIO18: EXT2.9, U5.30 (GPIO18/VSPICLK/HS1_DATA7)
/GPIO19: EXT2.8, U5.31 (GPIO19/VSPIQ/U0CTS/EMAC_TXD0)
/GPIO21: EXT2.6, U5.33 (GPIO21/VSPIHD/EMAC_TX_EN)
/GPIO22: EXT2.3, U5.36 (GPIO22/VSPIWP/U0RTS/EMAC_TXD1)
/GPIO23: EXT2.2, U5.37 (GPIO23/VSPID/HS1_STROBE)
/GPIO25: EXT1.9, U5.10 (GPIO25/DAC_1/ADC2_CH8/RTC_GPIO6/EMAC_RX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)
/GPIO26: EXT1.10, U5.11 (GPIO26/DAC_2/ADC2_CH9/RTC_GPIO7/EMAC_RX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)
/GPIO27: EXT1.11, U5.12 (GPIO27/ADC2_CH7/TOUCH7/RTC_GPIO17/EMAC_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)
/GPIO32: EXT1.7, U5.8 (GPIO32/XTAL_32K_P/ADC1_CH4/TOUCH9/RTC_G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)
/GPIO33: EXT1.8, U5.9 (GPIO33/XTAL_32K_N/ADC1_CH5/TOUCH8/RTC_G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)
GND: BAT1.2, C1.2, C2.2, C3.2, C4.2, C5.2, C6.2, C7.2, C9.1, EXT1.14, EXT2.1, EXT2.7, GND1.1, Q1.3 (case), R1.2, R4.2, R5.2, R12.2, R16.2, RST1.2, U1.2 (GND), U2.8 (GND), U3.2 (GND), U5.1 (GND), U5.15 (GND), U5.38 (GND), U5.39 (THERMAL_PAD), USB-UART1.0, USB-UART1.5 (GND)
unnamed: BAT_PWR_E1.1, R2.1
unnamed: BAT_SENS_E1.1, C9.2, R2.2, R5.1
unnamed: C2.1, Q1.1, U2.9 (XI)
unnamed: C3.1, Q1.2, U2.10 (XO)
unnamed: C5.1, R17.1, U2.5 (V3)
unnamed: C6.1, D2.1 (K), FET1.2, U3.1 (EN), U3.4 (IN)
unnamed: CHARGING1.1 (K), R3.1
unnamed: D4.1 (K), U2.3 (TXD)
unnamed: D5.2 (A), R6.2, U2.4 (RXD)
unnamed: L1.1, U3.3 (LX)
unnamed: PWR_SENS_E1.1, R15.2, R16.1
unnamed: Q2.1 (B), R8.2
unnamed: Q2.2 (E), R9.1, U2.16 (RTS#)
unnamed: Q3.1 (B), R9.2
unnamed: Q3.2 (E), R8.1, U2.15 (DTR#)
unnamed: Q3.3 (C), R10.1
unnamed: R3.2, U1.1 (CHRGb)
unnamed: R4.1, U1.5 (PROG)
unnamed: R11.1, R12.1, U3.5 (FB)
unnamed: U2.6 (UD+), USB-UART1.3 (D+)
unnamed: U2.7 (UD-), USB-UART1.2 (D-)
VBAT: BAT1.1, BAT_PWR_E1.2, FET1.3, U1.3 (VBAT)

Notes on the sheet:
Vout=0.6*(1+Ra/Rb)
Power Supply
Reset Button
ESP32-WROOM-32x-xxx MODULE
Bootstrapping Pins Settings
Internal Bootstrapping Resistors
MTDI/GPIO12:
Pull-Down
GPIO0:
Pull-Up
GPIO2:
GPIO4:
MTDO/GPIO15:
GPIO5:
Voltage of Internal LDO(VDD_SDIO)
Pin
Default
3.3V
1.8V
Booting Mode
GPIO12/MTDI
GPIO0
GPIO2
SPI Flash Boot
Download Boot
Don't-care
Debugging Log on U0TXD During Booting
U0TXD Toggling
U0TXD Silent
GPIO15/MTDO
Timing of SDIO Slave
For more information refer to esp_wroom_32_datasheet_en.pdf.
Falling-edge:Output
Falling-edge:Input
Rising-edge:Output
Rising-edge:Input
GPIO5
Extensions
LiPo Charger
Software Selectable Pins
Signal
EMAC_MDC_out
EMAC_MDI_in
EMAC_MDO_out
EMAC_CRS_out
Any GPIO
EMAC_COL_out
Interface
EMAC
I2C
I2CEXT0_SCL_in
I2CEXT0_SDA_in
I2CEXT1_SCL_in
I2CEXT1_SDA_in
I2CEXT0_SCL_out
I2CEXT0_SDA_out
I2CEXT1_SCL_out
I2CEXT1_SDA_out
General Purpose SPI
HSPIQ_in/_out
HSPID_in/_out
HSPICLK_in/_out
HSPI_CS0_in/_out
HSPI_CS1_out
HSPI_CS2_out
VSPIQ_in/_out
VSPID_in/_out
VSPI_CS0_in/_out
VSPICLK_in/_out
VSPI_CS1_out
VSPI_CS2_out
I(Bat) = 1000/Rprog = 455mA
Rprog
Fiducials:
External Power Sense
Auto program
DTR RTS->EN IO0
Battery Measurement
USB to UART
For a soldering tool, visit: https://www.olimex.com/Products/Tools/Soldering/
Recommended LI-PO battery: https://www.olimex.com/Products/Power/BATTERY-LIPO1400mAh/
I(Bat)
Voltage & Polarity!!!
3.7V LI-PO Battery Connector
Recommended USB 2.0 Type A to USB2.0 micro cable: https://www.olimex.com/Products/Components/Cables/USB-CABLE-A-MICRO-1.8M/
Fully compatible to Espressif's ESP32-DevKitC connectors J2&J3!
+3.3V at Iout(max)=600mA, Power Out!
+5V Only!!! Power In/Out
GND

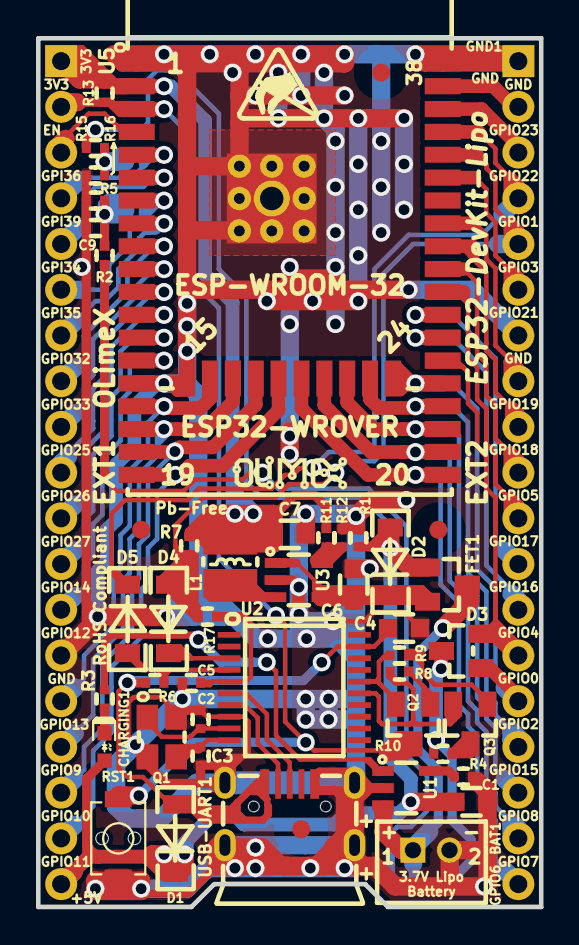
[picture p480: board ESP32-DevKit-Lipo_Rev_B.kicad_pcb from above]

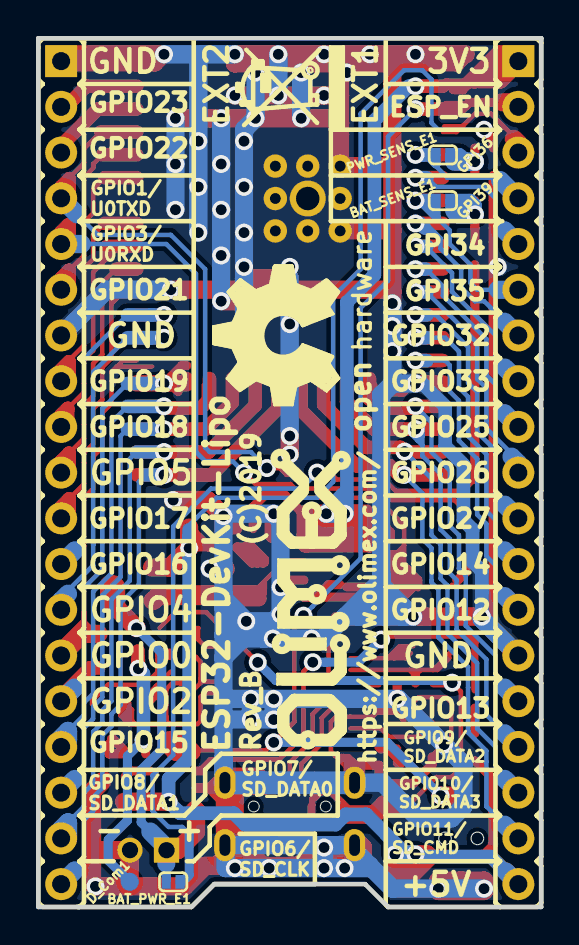
[picture p481: board ESP32-DevKit-Lipo_Rev_B.kicad_pcb from below]

Board: 2 copper layers, 27.9 x 48.3 mm, 58 parts (9 on the bottom side), 60 nets.

Other parts of the board:
Logo_OSHW: LOGO_OPENHARDWARE_8x8
Olimex_Logo_Big: OLIMEX_LOGO_TB
Olimex_Logo_Small: LOGO_OLIMEX_80
Sign_Antistatic: Val**; LOGO_ANTISTATIC_SMALL_4.5mmX2.8mm
Sign_RecycleBin: LOGO_RECYCLEBIN_1
