rompasaurus/regardedPal/hardware-design/examples/09-bitwiseajeet-tp4056/ESP32 PCB.kicad_pcb

## KiCad design hardware-design/examples/09-bitwiseajeet-tp4056/ESP32 PCB.kicad_pcb (2026-04-15)

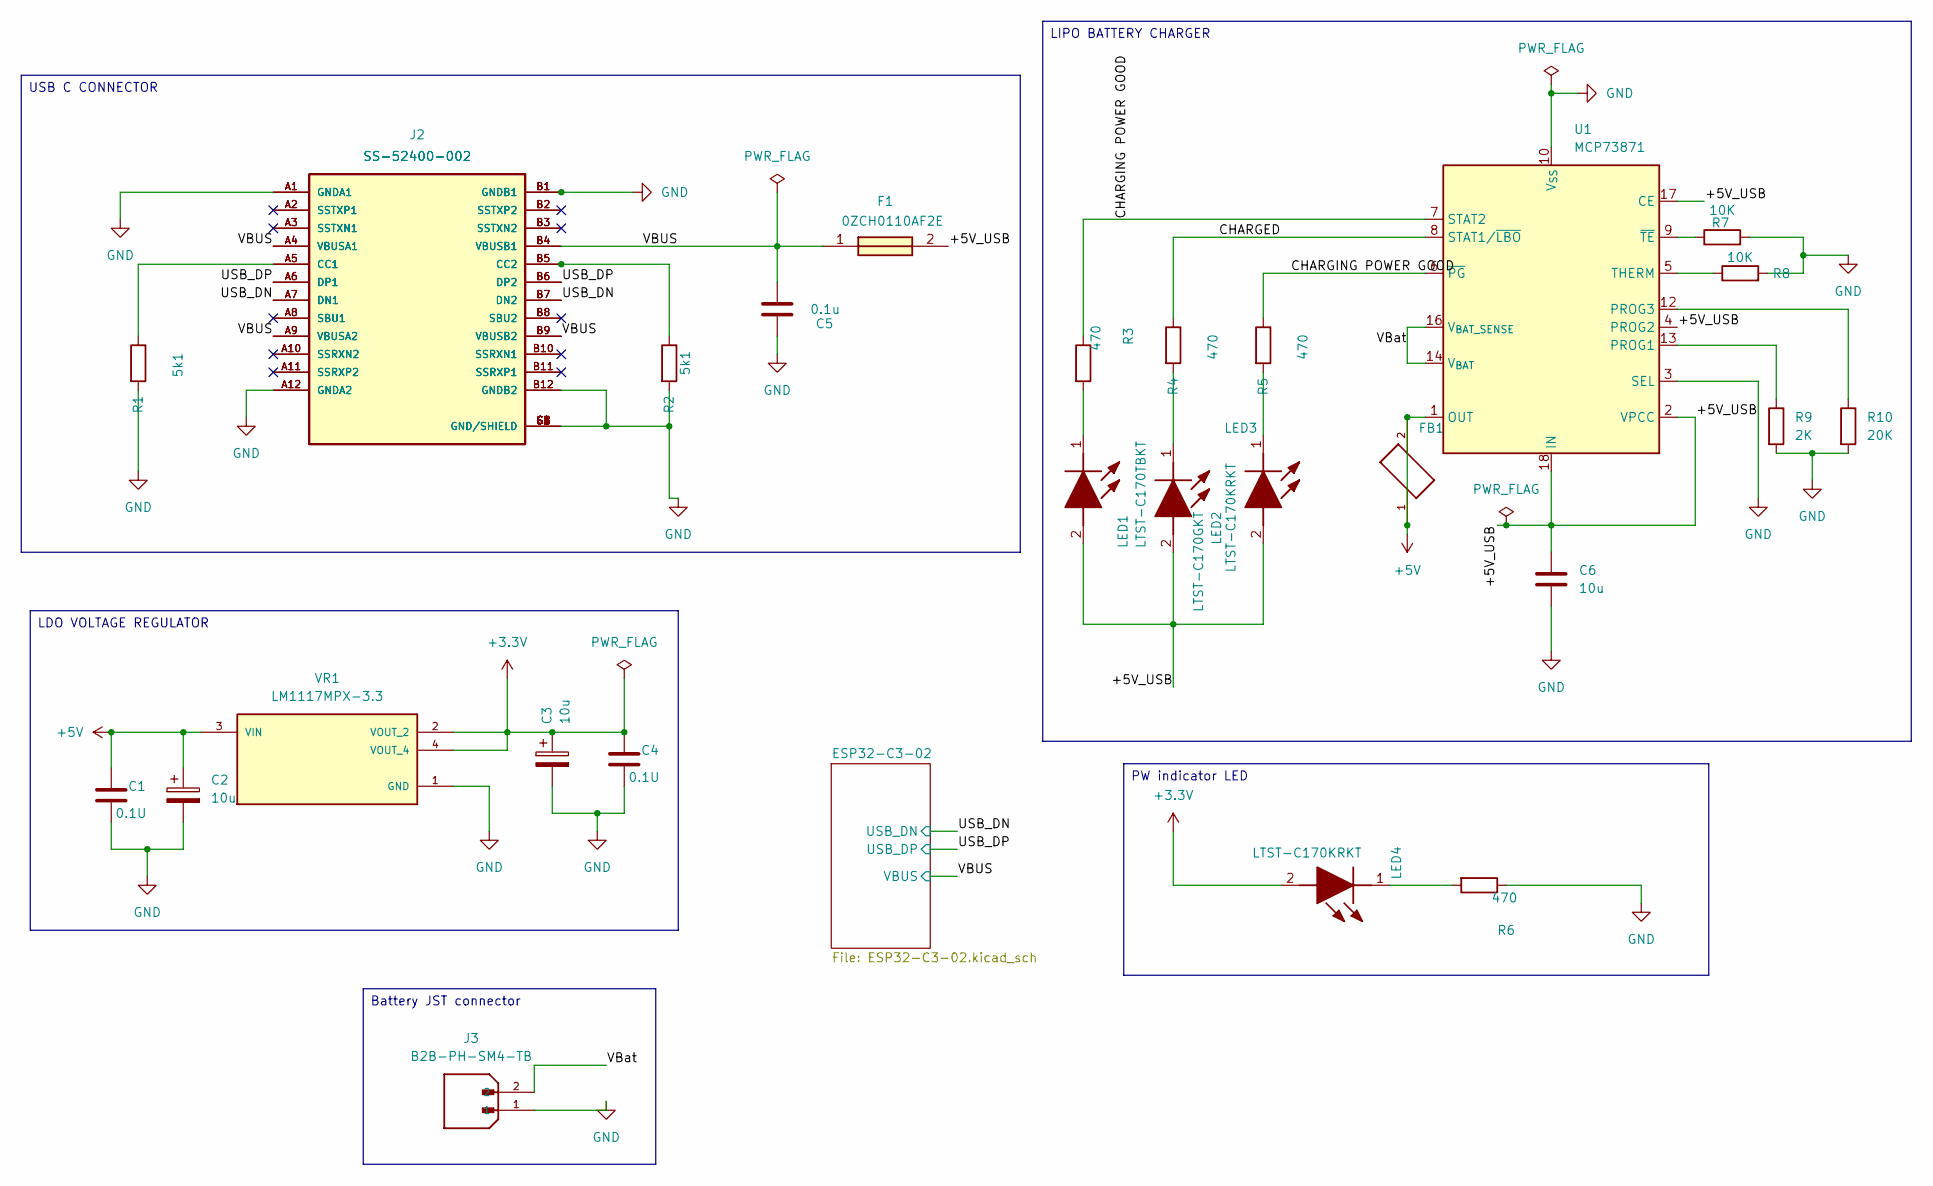
[picture p482: schematic ESP32 PCB.kicad_sch, ESP32 SENSOR BOARD_ROOT]

Parts:
C1, C4: 0.1U; C_0805_2012Metric
C2, C3: 10u; T491A
C5: 0.1u; C_0805_2012Metric
C6: 10u; C_0805_2012Metric
F1: 0ZCH0110AF2E; FUSC3226X100N; Manufacturer_Part_Number 0ZCH0110AF2E
FB1: FBMJ2125HM330-T; BEADC2012X105N
J1, J2: SS-52400-002; BELFUSE_SS-52400-002; PARTREV A0
J3: B2B-PH-SM4-TB; JST_B2B-PH-SM4-TB; PARTREV N/A
LED1: LTST-C170TBKT; LEDC2012X120N; Manufacturer_Part_Number LTST-C170TBKT; Mouser Part Number 859-LTST-C170TBKT
LED2: LTST-C170GKT; LEDC2012X120N; Manufacturer_Part_Number LTST-C170GKT; Mouser Part Number 859-LTST-C170GKT
LED3, LED4: LTST-C170KRKT; LEDC2012X120N; Manufacturer_Part_Number LTST-C170KRKT; Mouser Part Number 859-LTST-C170KRKT
R1, R2: 5k1; R_0805_2012Metric
R3, R4, R5, R6: 470; R_0805_2012Metric
R7, R8: 10K; R_0805_2012Metric
R9: 2K; R_0805_2012Metric
R10: 20K; R_0805_2012Metric
U1: MCP73871; QFN-20-1EP_4x4mm_P0.5mm_EP2.5x2.5mm
VR1: LM1117MPX-3.3; VREG_LM1117MPX-3.3

Connections:
+3.3V: C3.1, C4.1, LED4.2 (A), VR1.2 (VOUT_2), VR1.4 (VOUT_4); also elsewhere on the board
+5V: C1.1, C2.1, FB1.1, FB1.2, U1.1 (OUT), U1.20 (OUT), VR1.3 (VIN)
/+5V_USB: C6.1, F1.2, LED1.2 (A), LED2.2 (A), LED3.2 (A), U1.2 (VPCC), U1.4 (PROG2), U1.17 (CE), U1.18 (IN), U1.19 (IN)
/CHARGED: R4.1, U1.8 (STAT1/~LBO)
/CHARGING POWER GOOD: R3.1, R5.1, U1.6 (~PG), U1.7 (STAT2)
/USB_DN: J1.A7 (DN1), J1.B7 (DN2), J2.A7 (DN1), J2.B7 (DN2); also elsewhere on the board
/USB_DP: J1.A6 (DP1), J1.B6 (DP2), J2.A6 (DP1), J2.B6 (DP2); also elsewhere on the board
/VBUS: C5.1, F1.1, J1.A4 (VBUSA1), J1.A9 (VBUSA2), J1.B4 (VBUSB1), J1.B9 (VBUSB2), J2.A4 (VBUSA1), J2.A9 (VBUSA2), J2.B4 (VBUSB1), J2.B9 (VBUSB2); also elsewhere on the board
/VBat: J3.2, U1.14 (V_{BAT}), U1.15 (V_{BAT}), U1.16 (V_{BAT_SENSE})
GND: C1.2, C2.2, C3.2, C4.2, C5.2, C6.2, J1.A1 (GNDA1), J1.A12 (GNDA2), J1.B1 (GNDB1), J1.B12 (GNDB2), J1.G1 (GND/SHIELD), J1.G2 (GND/SHIELD), J1.G3 (GND/SHIELD), J1.G4 (GND/SHIELD), J1.S1 (GND/SHIELD), J1.S2 (GND/SHIELD), J1.S3 (GND/SHIELD), J1.S4 (GND/SHIELD), J2.A1 (GNDA1), J2.A12 (GNDA2), J2.B1 (GNDB1), J2.B12 (GNDB2), J2.G1 (GND/SHIELD), J2.G2 (GND/SHIELD), J2.G3 (GND/SHIELD), J2.G4 (GND/SHIELD), J2.S1 (GND/SHIELD), J2.S2 (GND/SHIELD), J2.S3 (GND/SHIELD), J2.S4 (GND/SHIELD), J3.1, R1.2, R2.2, R6.1, R7.2, R8.2, R9.2, R10.2, U1.3 (SEL), U1.10 (V_{SS}), U1.11 (V_{SS}), U1.21 (V_{SS}), VR1.1 (GND); also elsewhere on the board
unnamed: J1.A5 (CC1), J2.A5 (CC1), R1.1
unnamed: J1.B5 (CC2), J2.B5 (CC2), R2.1
unnamed: J1.A2 (SSTXP1), J2.A2 (SSTXP1)
unnamed: J1.A3 (SSTXN1), J2.A3 (SSTXN1)
unnamed: J1.A8 (SBU1), J2.A8 (SBU1)
unnamed: J1.A10 (SSRXN2), J2.A10 (SSRXN2)
unnamed: J1.A11 (SSRXP2), J2.A11 (SSRXP2)
unnamed: J1.B2 (SSTXP2), J2.B2 (SSTXP2)
unnamed: J1.B3 (SSTXN2), J2.B3 (SSTXN2)
unnamed: J1.B8 (SBU2), J2.B8 (SBU2)
unnamed: J1.B10 (SSRXN1), J2.B10 (SSRXN1)
unnamed: J1.B11 (SSRXP1), J2.B11 (SSRXP1)
unnamed: LED1.1 (K), R3.2
unnamed: LED2.1 (K), R4.2
unnamed: LED3.1 (K), R5.2
unnamed: LED4.1 (K), R6.2
unnamed: R9.1, U1.13 (PROG1)
unnamed: R10.1, U1.12 (PROG3)
unnamed: R8.1, U1.5 (THERM)
unnamed: R7.1, U1.9 (~TE)

Notes on the sheet:
LIPO BATTERY CHARGER
USB C CONNECTOR
PW indicator LED
LDO VOLTAGE REGULATOR
Battery JST connector

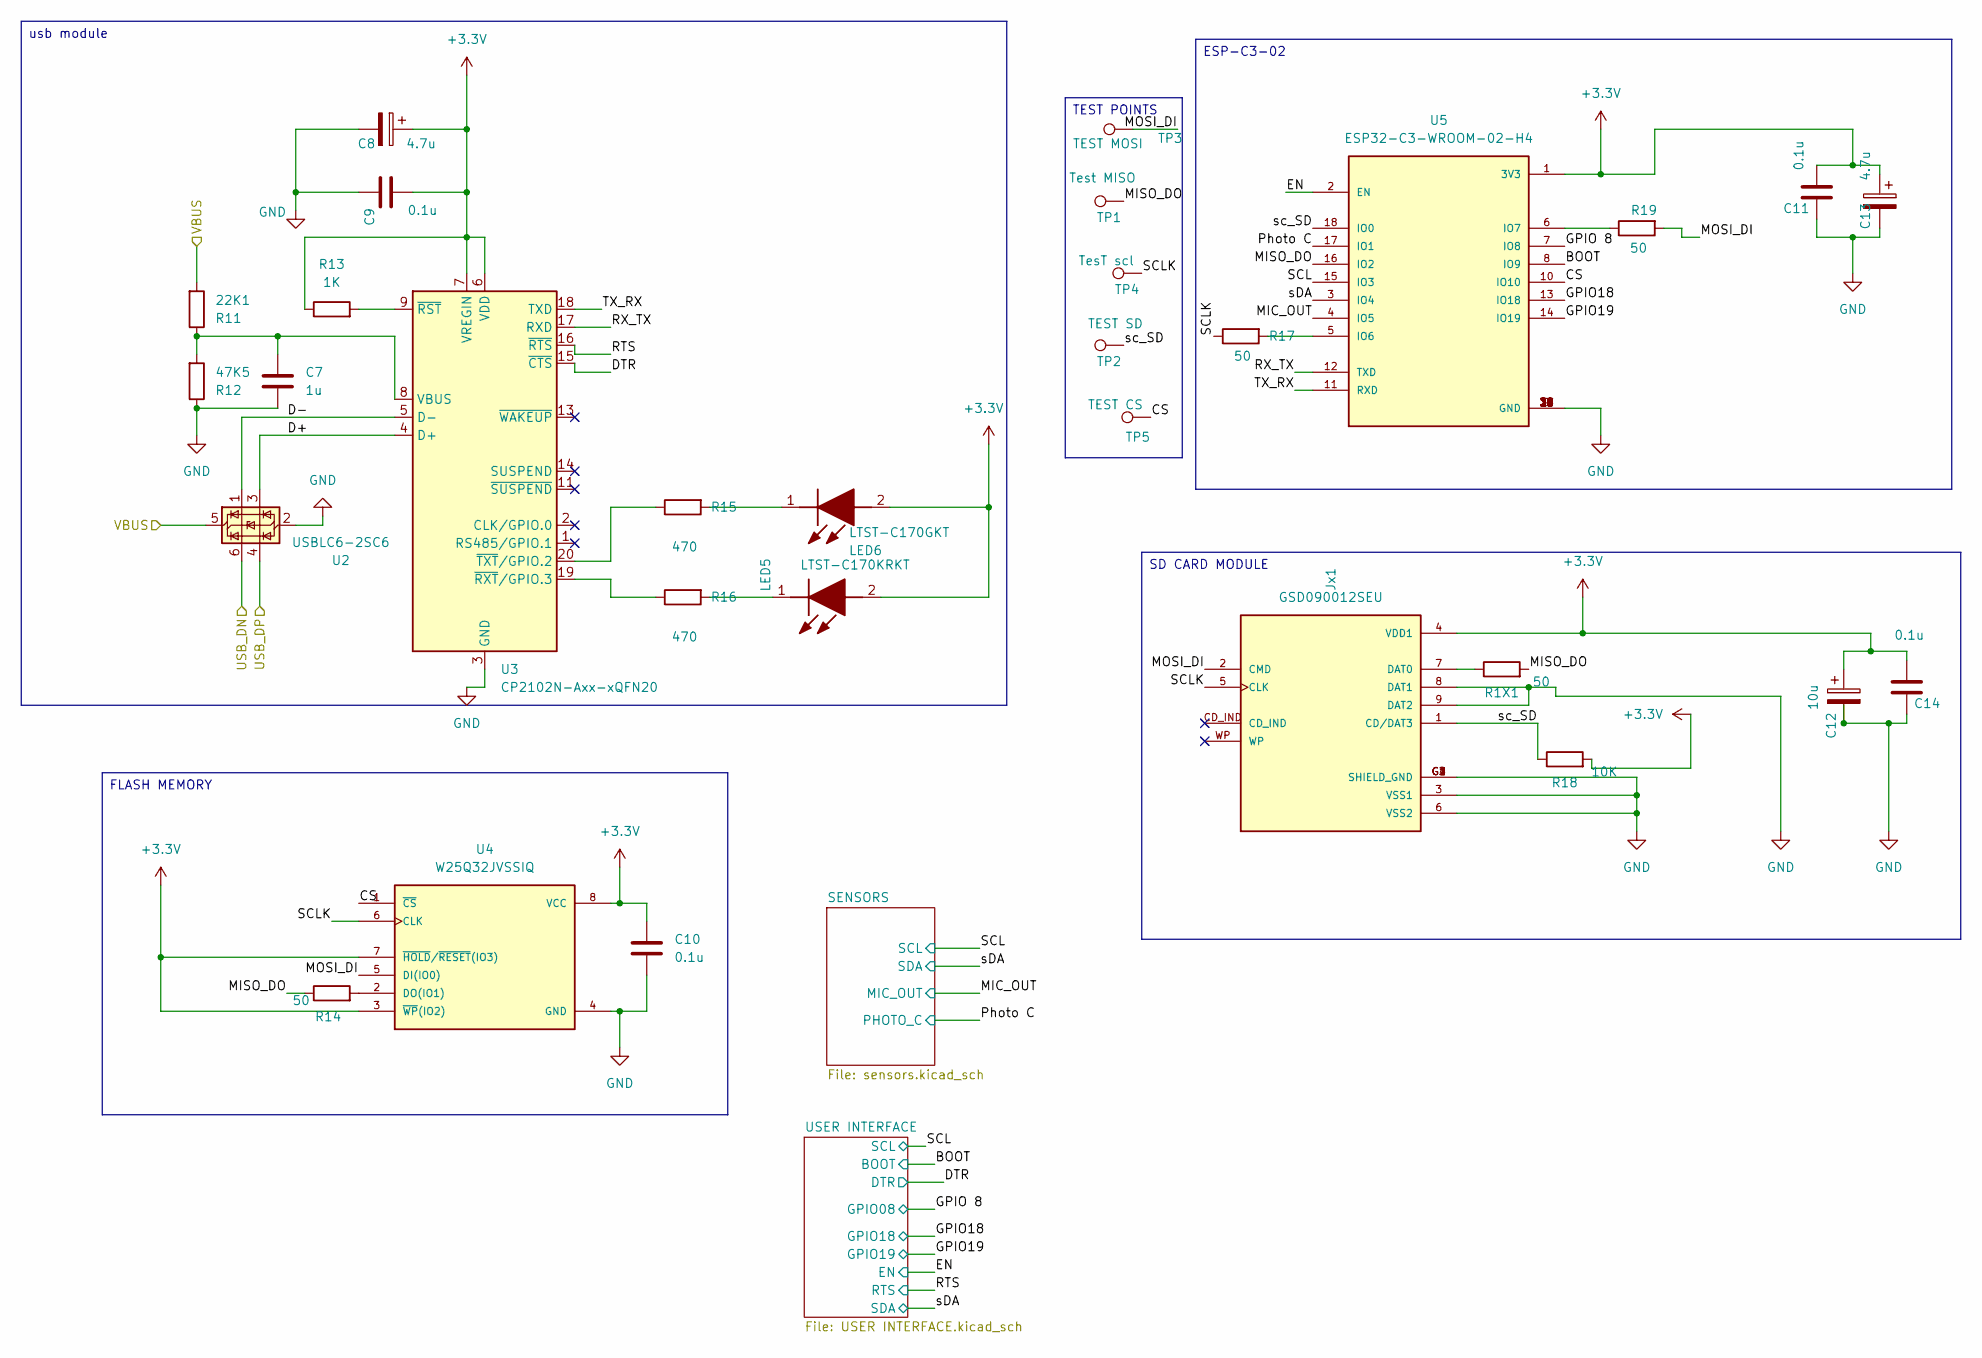
[picture p483: schematic ESP32-C3-02.kicad_sch, esp32-C3-FLASH_MEMORY]

Parts:
C7: 1u; C_0805_2012Metric
C8, C13: 4.7u; T491A
C9, C10, C11, C14: 0.1u; C_0805_2012Metric
C12: 10u; T491A
Jx1: GSD090012SEU; AMPHENOL_GSD090012SEU; PARTREV E
LED5: LTST-C170KRKT; LEDC2012X120N; Manufacturer_Part_Number LTST-C170KRKT; Mouser Part Number 859-LTST-C170KRKT
LED6: LTST-C170GKT; LEDC2012X120N; Manufacturer_Part_Number LTST-C170GKT; Mouser Part Number 859-LTST-C170GKT
R1X1, R14, R17, R19: 50; R_0805_2012Metric
R11: 22K1; R_0805_2012Metric
R12: 47K5; R_0805_2012Metric
R13: 1K; R_0805_2012Metric
R15, R16: 470; R_0805_2012Metric
R18: 10K; R_0805_2012Metric
TP1: Test MISO; TestPoint_Pad_D1.0mm
TP2: TEST SD; TestPoint_Pad_D1.0mm
TP3: TEST MOSI; TestPoint_Pad_D1.0mm
TP4: TesT scl; TestPoint_Pad_D1.0mm
TP5: TEST CS; TestPoint_Pad_D1.0mm
U2: USBLC6-2SC6; SOT-23-6
U3: CP2102N-Axx-xQFN20; SiliconLabs_QFN-20-1EP_3x3mm_P0.5mm_EP1.8x1.8mm
U4: W25Q32JVSSIQ; SOIC127P790X216-8N; M_PART_NUMBER W25QXX
U5: ESP32-C3-WROOM-02-H4; MODULE_ESP32-C3-WROOM-02-H4

Connections:
+3.3V: C8.1, C9.2, C10.1, C11.2, C12.1, C13.1, C14.2, Jx1.4 (VDD1), LED5.2 (A), LED6.2 (A), R13.1, R18.2, U3.6 (VDD), U3.7 (VREGIN), U4.3 (~WP(IO2)), U4.7 (~HOLD/~RESET(IO3)), U4.8 (VCC), U5.1 (3V3); also elsewhere on the board
/ESP32-C3-02/BOOT: U5.8 (IO9); also elsewhere on the board
/ESP32-C3-02/CS: TP5.1, U4.1 (~CS), U5.10 (IO10)
/ESP32-C3-02/D+: U2.3 (I/O2), U3.4 (D+)
/ESP32-C3-02/D-: U2.1 (I/O1), U3.5 (D-)
/ESP32-C3-02/DTR: U3.15 (~CTS); also elsewhere on the board
/ESP32-C3-02/EN: U5.2 (EN); also elsewhere on the board
/ESP32-C3-02/GPIO18: U5.13 (IO18); also elsewhere on the board
/ESP32-C3-02/GPIO19: U5.14 (IO19); also elsewhere on the board
/ESP32-C3-02/GPIO 8: U5.7 (IO8); also elsewhere on the board
/ESP32-C3-02/MIC_OUT: U5.4 (IO5); also elsewhere on the board
/ESP32-C3-02/MISO_DO: R1X1.2, R14.1, TP1.1, U5.16 (IO2)
/ESP32-C3-02/MOSI_DI: Jx1.2 (CMD), R19.2, TP3.1, U4.5 (DI(IO0))
/ESP32-C3-02/Photo C: U5.17 (IO1); also elsewhere on the board
/ESP32-C3-02/RTS: U3.16 (~RTS); also elsewhere on the board
/ESP32-C3-02/RX_TX: U3.17 (RXD), U5.12 (TXD)
/ESP32-C3-02/SCL: U5.15 (IO3); also elsewhere on the board
/ESP32-C3-02/SCLK: Jx1.5 (CLK), R17.1, TP4.1, U4.6 (CLK)
/ESP32-C3-02/TX_RX: U3.18 (TXD), U5.11 (RXD)
/ESP32-C3-02/sDA: U5.3 (IO4); also elsewhere on the board
/ESP32-C3-02/sc_SD: Jx1.1 (CD/DAT3), R18.1, TP2.1, U5.18 (IO0)
/USB_DN: U2.6 (I/O1); also elsewhere on the board
/USB_DP: U2.4 (I/O2); also elsewhere on the board
/VBUS: R11.2, U2.5 (VBUS); also elsewhere on the board
GND: C7.2, C8.2, C9.1, C10.2, C11.1, C12.2, C13.2, C14.1, Jx1.3 (VSS1), Jx1.6 (VSS2), Jx1.8 (DAT1), Jx1.9 (DAT2), Jx1.G1 (SHIELD_GND), Jx1.G2 (SHIELD_GND), Jx1.G3 (SHIELD_GND), Jx1.G4 (SHIELD_GND), R12.1, U2.2 (GND), U3.3 (GND), U3.12 (GND), U3.21 (GND), U4.4 (GND), U5.9 (GND), U5.19 (GND), U5.20 (GND), U5.21 (GND), U5.22 (GND), U5.23 (GND), U5.24 (GND), U5.25 (GND), U5.26 (GND), U5.27 (GND), U5.28 (GND), U5.29 (GND), U5.30 (GND), U5.31 (GND), U5.32 (GND), U5.33 (GND), U5.34 (GND), U5.35 (GND), U5.36 (GND), U5.37 (GND), U5.38 (GND), U5.39 (GND); also elsewhere on the board
unnamed: Jx1.7 (DAT0), R1X1.1
unnamed: LED5.1 (K), R16.2
unnamed: LED6.1 (K), R15.2
unnamed: C7.1, R11.1, R12.2, U3.8 (VBUS)
unnamed: R13.2, U3.9 (~RST)
unnamed: R16.1, U3.19 (~RXT/GPIO.3)
unnamed: R15.1, U3.20 (~TXT/GPIO.2)
unnamed: R14.2, U4.2 (DO(IO1))
unnamed: R17.2, U5.5 (IO6)
unnamed: R19.1, U5.6 (IO7)

Notes on the sheet:
FLASH MEMORY
SD CARD MODULE
TEST POINTS
ESP-C3-02
usb module

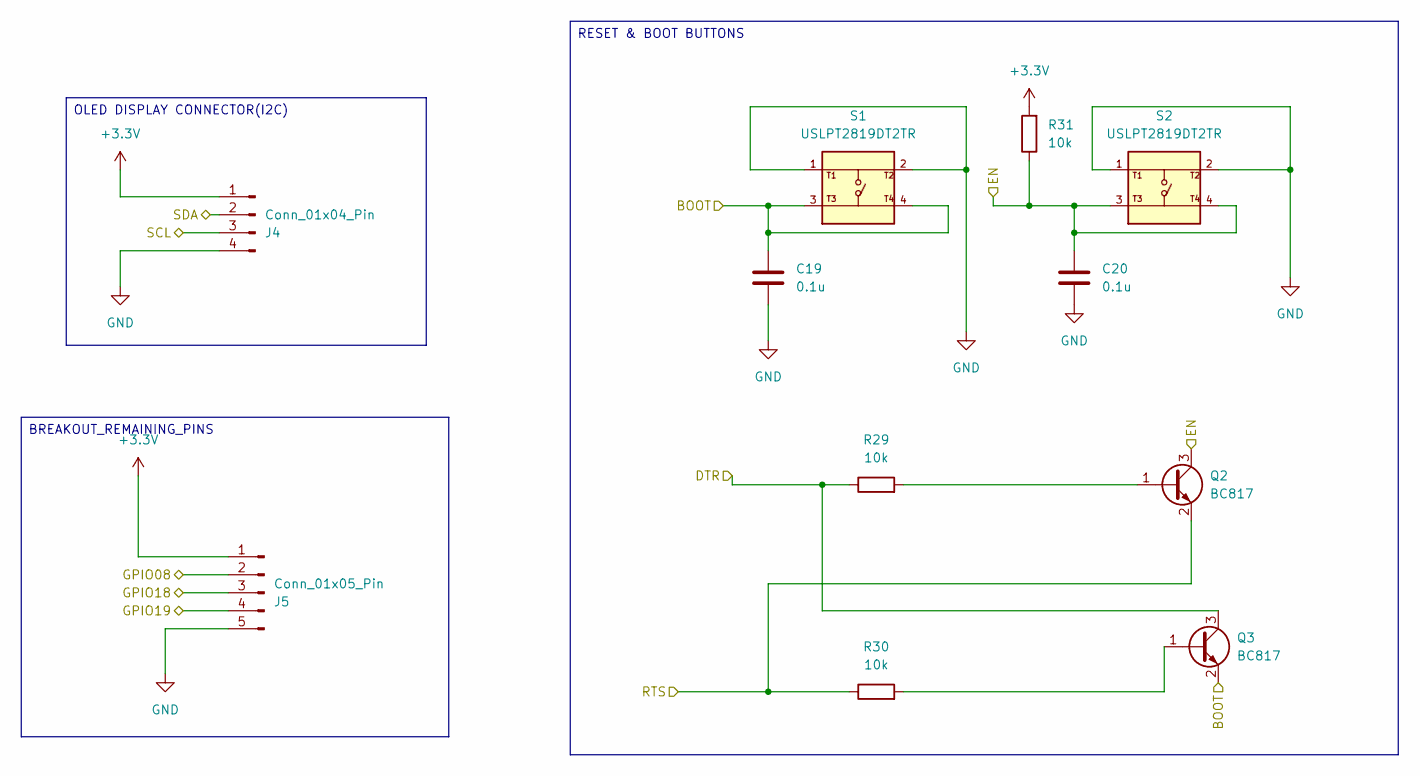
[picture p484: schematic USER INTERFACE.kicad_sch]

Parts:
C19, C20: 0.1u; C_0805_2012Metric
J4: Conn_01x04_Pin; PinSocket_1x04_P2.54mm_Vertical
J5: Conn_01x05_Pin; PinSocket_1x05_P2.54mm_Vertical
Q2, Q3: BC817; SOT-23
R29, R30, R31: 10k; R_0805_2012Metric
S1, S2: USLPT2819DT2TR; SW_USLPT2819DT2TR; PARTREV P

Connections:
+3.3V: J4.1, J5.1, R31.2; also elsewhere on the board
/ESP32-C3-02/BOOT: C19.1, Q3.2 (E), S1.3, S1.4; also elsewhere on the board
/ESP32-C3-02/DTR: Q3.3 (C), R29.1; also elsewhere on the board
/ESP32-C3-02/EN: C20.1, Q2.3 (C), R31.1, S2.3, S2.4; also elsewhere on the board
/ESP32-C3-02/GPIO18: J5.3; also elsewhere on the board
/ESP32-C3-02/GPIO19: J5.4; also elsewhere on the board
/ESP32-C3-02/GPIO 8: J5.2; also elsewhere on the board
/ESP32-C3-02/RTS: Q2.2 (E), R30.1; also elsewhere on the board
/ESP32-C3-02/SCL: J4.3; also elsewhere on the board
/ESP32-C3-02/sDA: J4.2; also elsewhere on the board
GND: C19.2, C20.2, J4.4, J5.5, S1.1, S1.2, S2.1, S2.2; also elsewhere on the board
unnamed: Q2.1 (B), R29.2
unnamed: Q3.1 (B), R30.2

Notes on the sheet:
BREAKOUT_REMAINING_PINS
RESET & BOOT BUTTONS
OLED DISPLAY CONNECTOR(I2C)

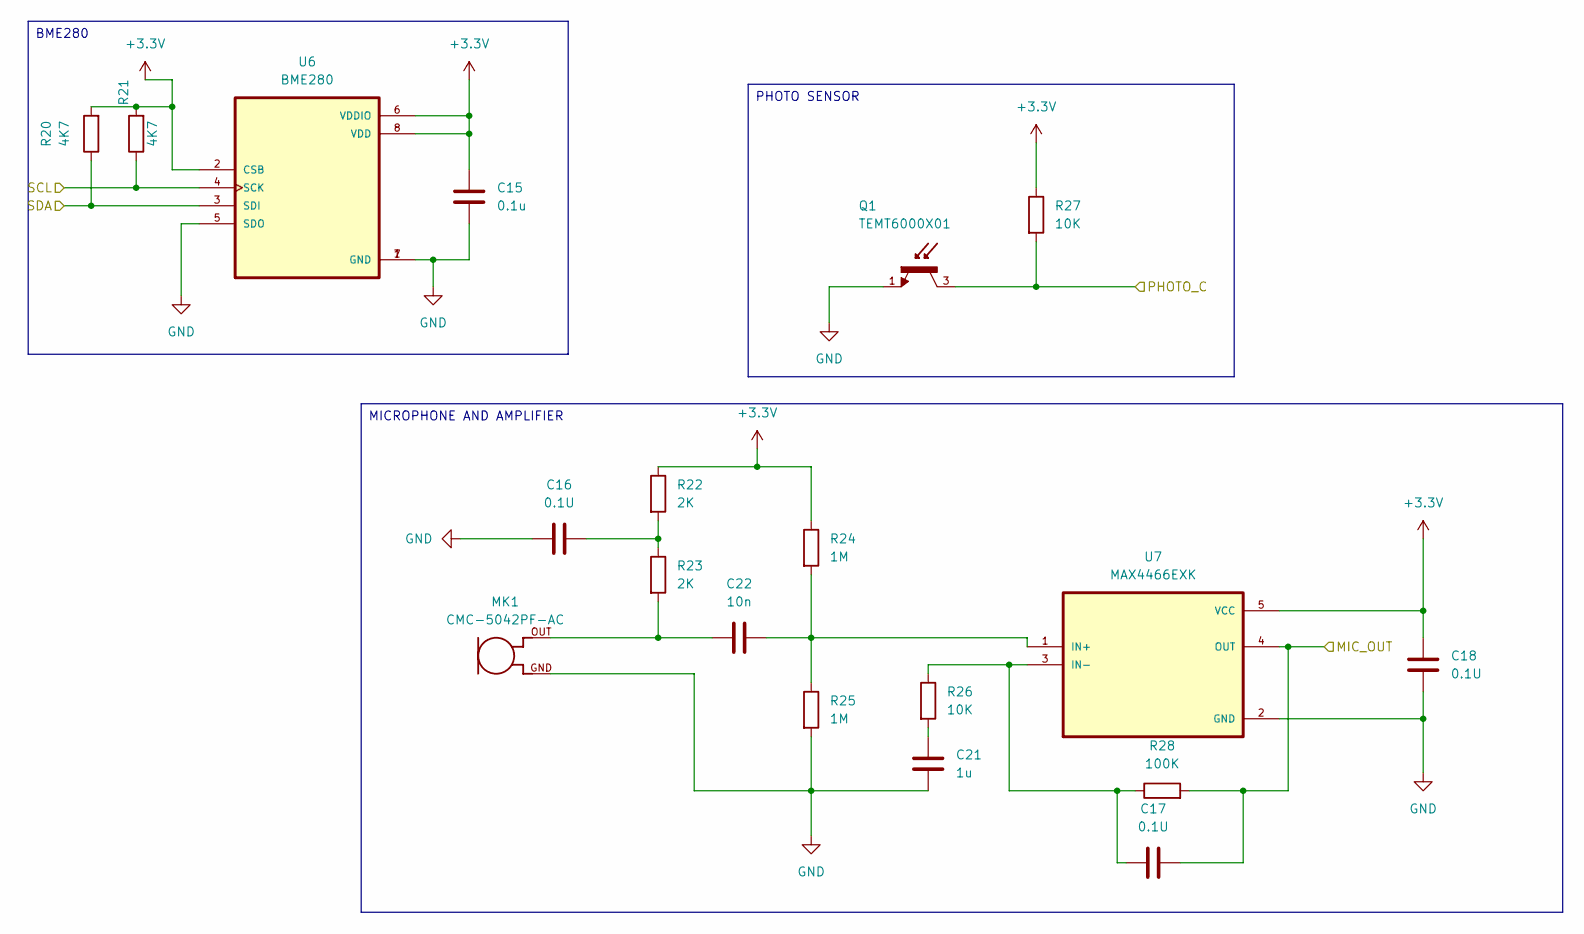
[picture p485: schematic sensors.kicad_sch]

Parts:
C15: 0.1u; C_0805_2012Metric
C16, C17, C18: 0.1U; C_0805_2012Metric
C21: 1u; C_0805_2012Metric
C22: 10n; C_0805_2012Metric
MK1: CMC-5042PF-AC; CUI_CMC-5042PF-AC
Q1: TEMT6000X01; TRANS_TEMT6000X01; PARTREV 1.9
R20, R21: 4K7; R_0805_2012Metric
R22, R23: 2K; R_0805_2012Metric
R24, R25: 1M; R_0805_2012Metric
R26, R27: 10K; R_0805_2012Metric
R28: 100K; R_0805_2012Metric
U6: BME280; PSON65P250X250X100-8N
U7: MAX4466EXK; SOT65P210X110-5N

Connections:
+3.3V: C15.1, C18.1, R20.2, R21.2, R22.1, R24.1, R27.1, U6.2 (CSB), U6.6 (VDDIO), U6.8 (VDD), U7.5 (VCC); also elsewhere on the board
/ESP32-C3-02/MIC_OUT: C17.2, R28.2, U7.4 (OUT); also elsewhere on the board
/ESP32-C3-02/Photo C: Q1.3, R27.2; also elsewhere on the board
/ESP32-C3-02/SCL: R21.1, U6.4 (SCK); also elsewhere on the board
/ESP32-C3-02/sDA: R20.1, U6.3 (SDI); also elsewhere on the board
GND: C15.2, C16.1, C18.2, C21.1, MK1.GND, Q1.1, R25.2, U6.1 (GND), U6.5 (SDO), U6.7 (GND), U7.2 (GND); also elsewhere on the board
unnamed: C16.2, R22.2, R23.1
unnamed: C21.2, R26.2
unnamed: C22.1, MK1.OUT, R23.2
unnamed: C22.2, R24.2, R25.1, U7.1 (IN+)
unnamed: C17.1, R26.1, R28.1, U7.3 (IN-)

Notes on the sheet:
MICROPHONE AND AMPLIFIER
BME280
PHOTO SENSOR
