rompasaurus/regardedPal/hardware-design/examples/09-bitwiseajeet-tp4056/ESP32 PCB.kicad_pcb

## KiCad design hardware-design/examples/09-bitwiseajeet-tp4056/ESP32 PCB.kicad_pcb (continued)

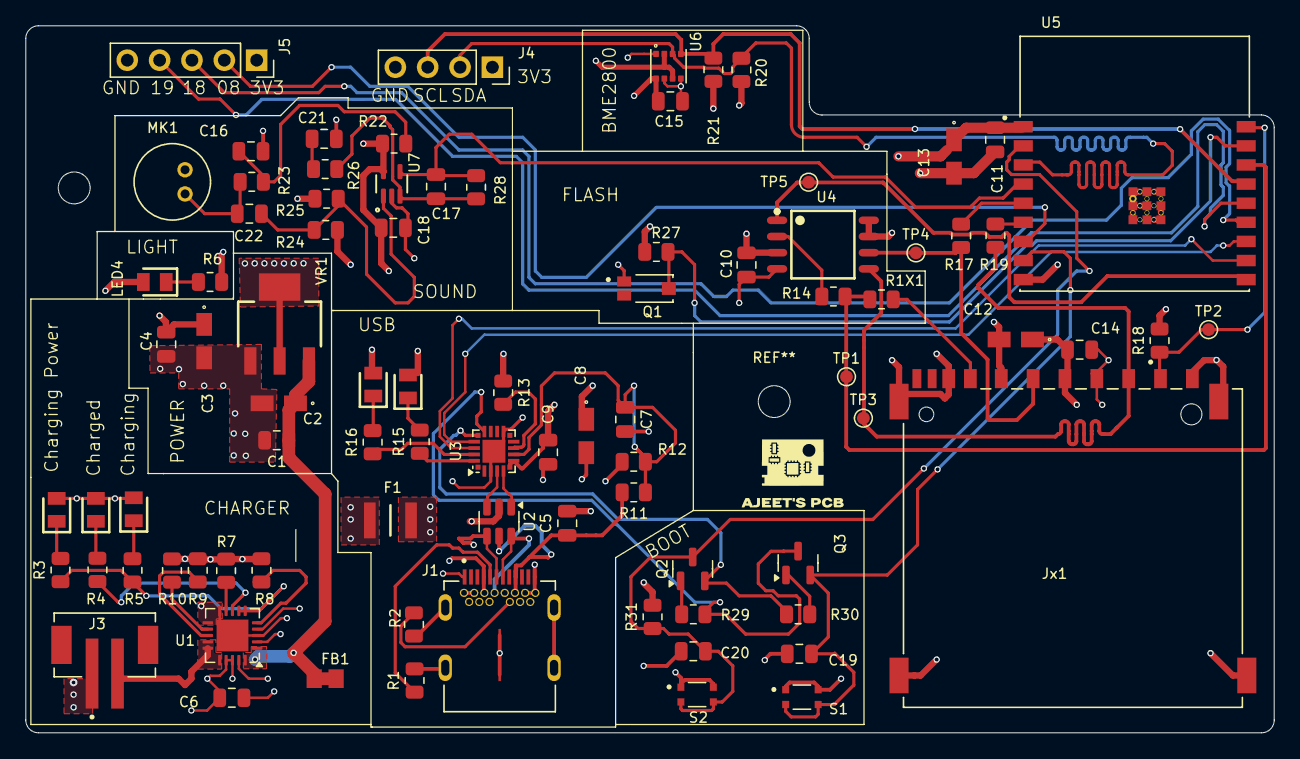
[picture p486: board ESP32 PCB.kicad_pcb from above]

Board: 4 copper layers, 98.0 x 55.5 mm, 86 parts (0 on the bottom side), 57 nets.
