rompasaurus/regardedPal/hardware-design/examples/11-aeonlabs-s3-template/KiCad/ESP32_S3_PCB_TEMPLATE.kicad_pcb

## KiCad design hardware-design/examples/11-aeonlabs-s3-template/KiCad/ESP32_S3_PCB_TEMPLATE.kicad_pcb (2026-04-15)

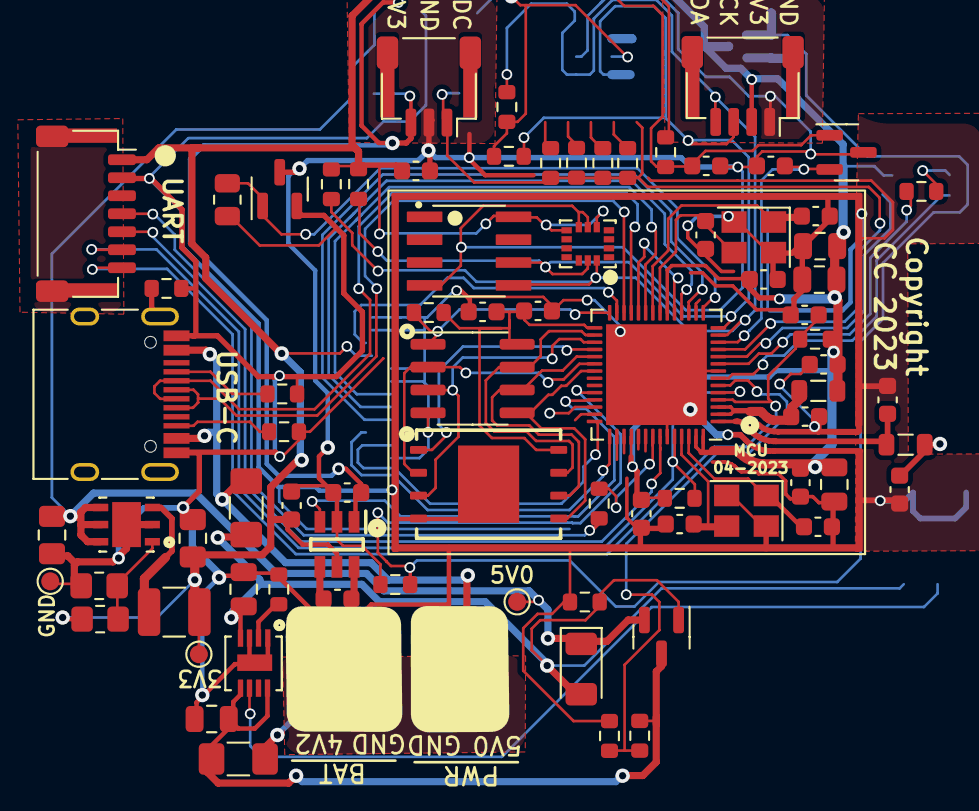
[picture p487: board ESP32_S3_PCB_TEMPLATE.kicad_pcb from above]

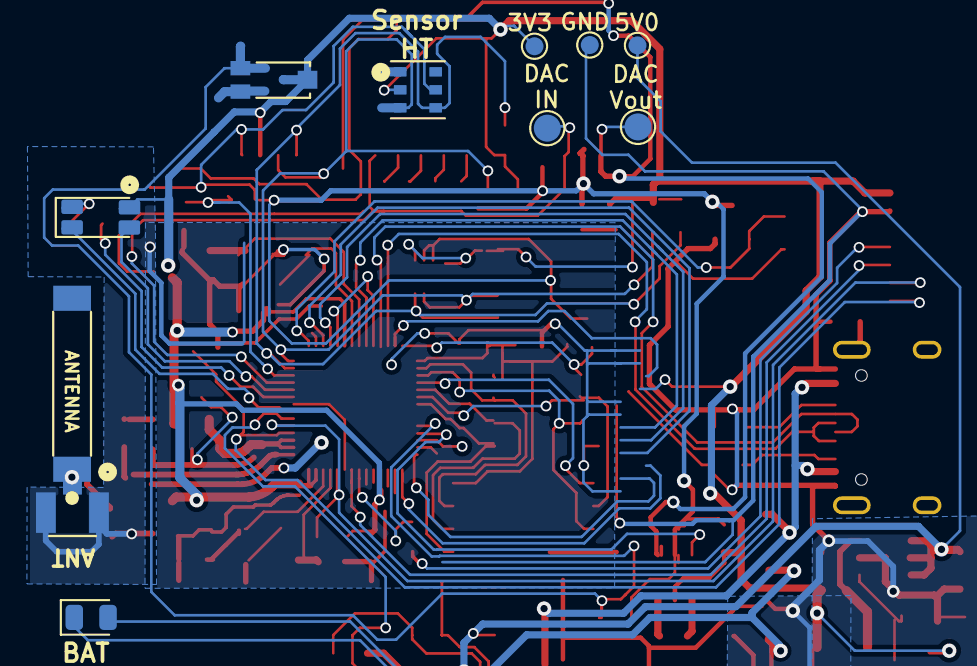
[picture p488: board ESP32_S3_PCB_TEMPLATE.kicad_pcb from below]

Board: 2 copper layers, 93 parts (12 on the bottom side), 53 nets.

Parts:
ATSHA_C1: 100nF; C_0603_1608Metric
AUR1: AUR9718x_DFN_3x3mm_6_pin; AUR9718 ST1S09 SON95P300X300X100-7N
AUR_C1: 22uF; C_0805_2012Metric_Pad1.18x1.45mm_HandSolder
AUR_C2: 4.7uF; C_0805_2012Metric_Pad1.18x1.45mm_HandSolder
AUR_R1: 75k; R_0805_2012Metric_Pad1.20x1.40mm_HandSolder
AUR_R2: 24k; R_0805_2012Metric_Pad1.20x1.40mm_HandSolder
AUR_l1: 3.3uF; L_1210_3225Metric
BAT_FUSE1: Polyfuse; Fuse_1206_3216Metric_Pad1.42x1.75mm_HandSolder
BAT_SENSE_R1, BAT_SENSE_R2: 100k; R_0603_1608Metric
CN3065_C2: 4.7uF; C_0805_2012Metric
CN3065_R1: 1K8; R_0603_1608Metric
CN3065_STDBY_LED1: LED; LED_0805_2012Metric
CN3965_C1: 22uF; C_0805_2012Metric
DIP_R1: 4k7; R_0603_1608Metric
DIP_R2: 1k; R_0603_1608Metric
DIP_R3: 20k; R_0603_1608Metric
DIP_R4: 200k; R_0603_1608Metric
DIP_R5: 2M; R_0603_1608Metric
DMP1045U_1: DMP1045U; SOT-23
DMP1045_R1: 10K; R_0603_1608Metric
DMP1045_SCHOT1: D_Schottky; D_1206_3216Metric
EPS1: ESP32-PSRAM_LY68L6400S; SOIC-8_3.9x4.9mm_P1.27mm
ESP32S1: ESP32-S3; QFN-56-1EP_7x7mm_P0.4mm_EP5.6x5.6mm
ESP32_SHIELD1: RFShield_OnePiece; ESP32-S3 GND Shield
ESP_FLASH1: W25Q128JVS; WSON8 FLASH SPI SON127P800X600X80-9N
E_DTR_R1: 10k; R_0603_1608Metric
E_LNA_ANT1: AN9520; 2.4ghZ WIFI ANTENNA AN9520_ANT2-SMD-9.5X2.1X1.0MM
E_LNA_ANT2: U.FL-R-SMT(01); RF Antenna IPEX SMD PCB HRS_U.FL-R-SMT(01)
E_LNA_C1, E_LNA_C2: 2.7pF; C_0603_1608Metric
E_LNA_l1: 1.8nH 5%; L_0805_2012Metric
E_RTS_C1: 100nF; C_0603_1608Metric
E_RTS_R1: 10k; R_0603_1608Metric
E_SPI_C1: 1uF 10% 50V; C_0603_1608Metric
E_SPI_C2: 100nF 10% 16V; C_0603_1608Metric
E_UART_TX_1: 499R; R_0603_1608Metric
E_VDDA_C1: 100nF; C_0603_1608Metric
E_VDDA_C2: 1uF 10% 50V; C_0805_2012Metric
E_VDD_3_C1, E_VDD_3_C2: 10uF 20% 6.3V; C_0805_2012Metric
E_VDD_3_C3, E_VDD_3_C4: 100nF 10% 16V; C_0603_1608Metric
E_VDD_CPU_C1: 100nF 10% 16V; C_0603_1608Metric
E_VDD_L1: 12nH 5%; L_0805_2012Metric
E_VDD_RTC_C1: 100nF 10% 16V; C_0603_1608Metric
E_XTAL32_1: 32.768Mhz 22pF+-10PPM; Crystal_SMD_3225-4Pin_3.2x2.5mm
E_XTAL32_C1, E_XTAL32_C2, E_XTAL40_C1, E_XTAL40_C2: 22pF 5% 50V; C_0603_1608Metric
E_XTAL40_1: 40Mhz 22pF+-10PPM; Crystal_SMD_3225-4Pin_3.2x2.5mm
ExtSW1: Conn_01x03_Female; JST_SH_SM03B-SRSS-TB_1x03-1MP_P1.00mm_Horizontal
ExtSWBAT_PLUG2: Conn_01x03_Female; JST_SH_SM03B-SRSS-TB_1x03-1MP_P1.00mm_Horizontal
HX1: HX4002; HX4002 SOT95 P280X125-6N
HX_C1, HX_C2, HX_C3: 2.2uF; C_0603_1608Metric
I2C_PLUG1: I2C6; JST_SH_SM04B-SRSS-TB_1x04-1MP_P1.00mm_Horizontal
I2C_SCL_R1, I2C_SDA_R1: 10k; R_0603_1608Metric
IMR1, IMR2: 10K; R_0603_1608Metric
IMU1: LSM6DS3; LSM6DS3 Motion Sensor PQFN50P300X250X86-14N
J1: TYPE-C-31-M-12; USB_C_Receptacle_HRO_TYPE-C-31-M-12
JICSP1: Conn_01x07_Socket; JST_SH_SM07B-SRSS-TB_1x07-1MP_P1.00mm_Horizontal
LED1: LED_GBRC; LED_1206_3210_RGB_Metric
LR1: 330R; R_0603_1608Metric
MTRR1: 10k; R_0805_2012Metric
MTRT1: NPN; SOT-23
PSRAM_R1: 100K; R_0603_1608Metric
PWR_FUSE1: Polyfuse; Fuse_1206_3216Metric_Pad1.42x1.75mm_HandSolder
PWR_PLUG1: Screw_Terminal_01x02; JST_SH_SM02B-SRSS-TB_1x02-1MP_P1.00mm_Horizontal
Sign-PbFree: LOGO_PBFREE
Sign-RecycleBin: LOGO_RECYCLEBIN_1
Sign-RoHS: LOGO_ROHS_1
TMPR1: 10K; R_0603_1608Metric
TP1, TP1#2: VIN; TestPoint_Pad_D1.0mm
TP2, TP2#2: VOut; TestPoint_Pad_D1.0mm
TP3, TP3#2: GND; TestPoint_Pad_D1.0mm
U1: MCP1525-TT; SOT-23
U2: ATSHA204A-MAHDA-T; ATSHA204A Auth SOIC8
U3: Battery_charger_CN3065_QFN8; QFN8 3.1x2.9mm QFNn-8 3x3 SON80P400X400X100-9N
U4: AHT20; AHT20 HT Sensor PSON100P300X300X110-6N
U6: TEMT6000; TEMT6000-SEN
USB_PLUG_R1, USB_PLUG_R3: 5k1; R_0603_1608Metric
USB_PLYG_R2: 150K; R_0603_1608Metric
VOLTAGE_REF_C1, VOLTAGE_REF_C2: 100nF; C_0603_1608Metric

Connections:
3V3: ATSHA_C1.2, AUR_C1.1, AUR_R1.1, AUR_l1.1, ESP32S1.20 (VDD3P3_RTC), ESP32S1.46 (VDD3P3_CPU), ESP32S1.55 (VDDA), ESP32S1.56 (VDDA), E_DTR_R1.1, E_RTS_R1.1, E_VDDA_C1.2, E_VDDA_C2.2, E_VDD_3_C1.1, E_VDD_3_C2.1, E_VDD_3_C3.1, E_VDD_CPU_C1.1, E_VDD_L1.1, E_VDD_RTC_C1.1, HX1.5 (VIN), HX_C3.2, I2C_PLUG1.2, I2C_SCL_R1.1, I2C_SDA_R1.2, IMR1.1, IMR2.1, IMU1.5 (VDDIO), IMU1.8 (VDD), JICSP1.1, LED1.4 (K), TP2.1, TP2#2.1, U2.8 (VCC), U4.2 (VDD), U6.COLLECTOR
3V3_PLUG: DIP_R1.2, ExtSW1.3, HX1.1 (VOUT), HX_C1.1, U1.1 (Vin), VOLTAGE_REF_C1.2
ADC_IN_IO04: DIP_R2.1, DIP_R3.1, DIP_R4.1, DIP_R5.1, ESP32S1.11 (GPIO6/ADC1_CH5), ExtSW1.1
BAT_SENSE_IO21: BAT_SENSE_R1.1, BAT_SENSE_R2.2, ESP32S1.6 (GPIO1/ADC1_CH0)
CHIP_EN: ESP32S1.4 (CHIP_PU/RESET), E_RTS_C1.2, E_RTS_R1.2, JICSP1.7
DAC_CALIBRATION: ESP32S1.19 (GPIO14/ADC2_CH3), ESP32S1.24 (GPIO18/ADC2_CH7/DAC_1)
ESP_GPIO0_BOOT-DTR: ESP32S1.5 (GPIO0/BOOT), ESP32S1.52 (GPIO46), E_DTR_R1.2, JICSP1.6
GND: AUR1.2 (GND), AUR1.7 (GND), AUR_C1.2, AUR_C2.2, AUR_R2.2, BAT_SENSE_R1.2, CN3065_C2.1, CN3065_R1.1, CN3965_C1.1, DMP1045_R1.2, EPS1.4 (VSS), ESP32S1.8 (GPIO3/ADC1_CH2), ESP32S1.51 (GPIO45), ESP32S1.57 (GND), ESP32_SHIELD1.1 (Shield), ESP_FLASH1.4 (GND), ESP_FLASH1.9 (GND), E_LNA_ANT2.1 (GND), E_LNA_ANT2.2 (GND), E_LNA_C1.2, E_LNA_C2.2, E_RTS_C1.1, E_SPI_C1.2, E_SPI_C2.2, E_VDDA_C1.1, E_VDDA_C2.1, E_VDD_3_C1.2, E_VDD_3_C2.2, E_VDD_3_C3.2, E_VDD_3_C4.2, E_VDD_CPU_C1.2, E_VDD_RTC_C1.2, E_XTAL32_1.2, E_XTAL32_1.4, E_XTAL32_C1.2, E_XTAL32_C2.2, E_XTAL40_1.2, E_XTAL40_1.4, E_XTAL40_C1.2, E_XTAL40_C2.2, ExtSWBAT_PLUG2.3, J1.B1, J1.B12, JICSP1.2, MTRR1.1, MTRT1.2, PWR_PLUG1.1, TP3.1, TP3#2.1, U3.1 (V_Temp), U3.3 (GND), U3.9 (GND), USB_PLUG_R1.2, USB_PLUG_R3.2, USB_PLYG_R2.2
GNDD: ATSHA_C1.1, ExtSW1.2, ExtSW1.MP, ExtSWBAT_PLUG2.MP, HX1.2 (GND), HX_C1.2, HX_C3.1, I2C_PLUG1.1, I2C_PLUG1.MP, IMU1.6 (GND), IMU1.7 (GND), JICSP1.MP, MTRT1.3, PWR_PLUG1.MP, TMPR1.1, U1.3 (Vss), U2.4 (GND), U4.5 (GND), VOLTAGE_REF_C1.1, VOLTAGE_REF_C2.1
GPIO8_I2C_SDA: ESP32S1.13 (GPIO8/ADC1_CH7), I2C_PLUG1.4, I2C_SDA_R1.1, IMR1.2, IMU1.14 (SDA), U2.5 (SDA), U4.4 (SDA)
GPIO9_I2C_SCL: ESP32S1.14 (GPIO9/ADC1_CH8), I2C_PLUG1.3, I2C_SCL_R1.2, IMR2.2, IMU1.13 (SCL), U2.6 (SCL), U4.3 (SCL)
LED_B_IO05: ESP32S1.10 (GPIO5/ADC1_CH4), LED1.2 (BA)
LED_G_IO02: ESP32S1.7 (GPIO2/ADC1_CH1), LED1.1 (GA)
LED_R_IO04: ESP32S1.9 (GPIO4/ADC1_CH3), LR1.1
unnamed: AUR1.1 (FB), AUR_R1.2, AUR_R2.1
unnamed: AUR1.3 (SW), AUR_l1.2
unnamed: ESP32S1.21 (GPIO15/ADC2_CH4/XTAL_32K_P), E_XTAL32_1.3, E_XTAL32_C1.1
unnamed: ESP32S1.22 (GPIO16/ADC2_CH5/XTAL_32K_N), E_XTAL32_1.1, E_XTAL32_C2.1
unnamed: ESP32S1.1 (LNA_IN/RF), E_LNA_C2.1, E_LNA_l1.2
unnamed: ESP32S1.49 (U0TXD/PROG/GPIO43), E_UART_TX_1.2
unnamed: ESP32S1.2 (VDD3P3), ESP32S1.3 (VDD3P3), E_VDD_3_C4.1, E_VDD_L1.2
unnamed: ESP32S1.53 (XTAL_N), E_XTAL40_1.3, E_XTAL40_C2.1
unnamed: ESP32S1.54 (XTAL_P), E_XTAL40_1.1, E_XTAL40_C1.1
unnamed: E_LNA_ANT1.1, E_LNA_ANT2.3 (SIG), E_LNA_C1.1, E_LNA_l1.1
unnamed: HX1.6 (C+), HX_C2.1
unnamed: HX1.4 (C-), HX_C2.2
unnamed: J1.A5 (CC1), USB_PLUG_R3.1
unnamed: J1.B5 (CC2), USB_PLUG_R1.1
unnamed: J1.S1 (SHIELD), USB_PLYG_R2.1
unnamed: LED1.3 (RA), LR1.2
unnamed: CN3065_R1.2, U3.2 (I_SET)
PERIPHERALS_PWR_EN_IO10: ESP32S1.15 (GPIO10/ADC1_CH9), MTRR1.2, MTRT1.1
PLUG_PWR_3V3_EN_IO38: ESP32S1.39 (GPIO34), HX1.3 (EN)
RXD0: ESP32S1.50 (U0RXD/PROG/GPIO44), JICSP1.5
SPICLK: EPS1.6 (SCLK), ESP32S1.33 (SPICLK/GPIO30), ESP_FLASH1.6 (CLK)
SPICS0: ESP32S1.32 (SPICS0/GPIO29), ESP_FLASH1.1 (~CS)
SPICS1: EPS1.1 (~CE), ESP32S1.28 (SPI_CS1/GPIO26), PSRAM_R1.1
SPID: EPS1.5 (SiO0), ESP32S1.35 (SPID/GPIO32), ESP_FLASH1.5 (DI(IO0))
SPIHD: EPS1.7 (SIO3), ESP32S1.30 (SPIHD/GPIO27), ESP_FLASH1.7 (IO3)
SPIQ: EPS1.2 (SIO1), ESP32S1.34 (SPIQ/GPIO31), ESP_FLASH1.2 (DO(IO1))
SPIWP: EPS1.3 (SIO2), ESP32S1.31 (SPIWP/GPIO28), ESP_FLASH1.3 (IO2)
STDBY_LED_G: CN3065_STDBY_LED1.1 (K), U3.6 (LED_DONE)
TEMT6000_IO33: ESP32S1.38 (GPIO33), TMPR1.2, U6.EMITTER
TXD0: E_UART_TX_1.1, JICSP1.4
USB_5V0: CN3065_STDBY_LED1.2 (A), CN3965_C1.2, DMP1045U_1.1, DMP1045_R1.1, DMP1045_SCHOT1.2 (A), PWR_FUSE1.1, U3.4 (VIN)
USB_5V0F: J1.A4, J1.A9, PWR_FUSE1.2, PWR_PLUG1.2
USB_D+: ESP32S1.26 (GPIO20/USB_D+/ADC2_CH9), J1.A6 (DP1), J1.B6 (DP2)
USB_D-: ESP32S1.25 (GPIO19/USB_D-/ADC2_CH8), J1.A7 (DN1), J1.B7 (DN2)
VDD_SPI: EPS1.8 (VCC), ESP32S1.29 (VDD_SPI), ESP_FLASH1.8 (VCC), E_SPI_C1.1, E_SPI_C2.1, PSRAM_R1.2
VIN: AUR1.4 (VIN_SW), AUR1.5 (VIN_A), AUR1.6 (EN), AUR_C2.1, DMP1045U_1.2, DMP1045_SCHOT1.1 (K), TP1.1, TP1#2.1
VIN_BAT: BAT_FUSE1.1, BAT_SENSE_R2.1, CN3065_C2.2, DMP1045U_1.3, U3.5 (BAT+), U3.8 (FB)
VIN_BATF: BAT_FUSE1.2, ExtSWBAT_PLUG2.1
VOLTAGE_REF_IO07: ESP32S1.12 (GPIO7/ADC1_CH6), U1.2 (Vout), VOLTAGE_REF_C2.2
