rompasaurus/regardedPal/hardware-design/examples/08-esp-rust-board/hardware/esp-rust-board/esp-rust-board.kicad_pcb

## KiCad design hardware-design/examples/08-esp-rust-board/hardware/esp-rust-board/esp-rust-board.kicad_pcb (2026-04-15)

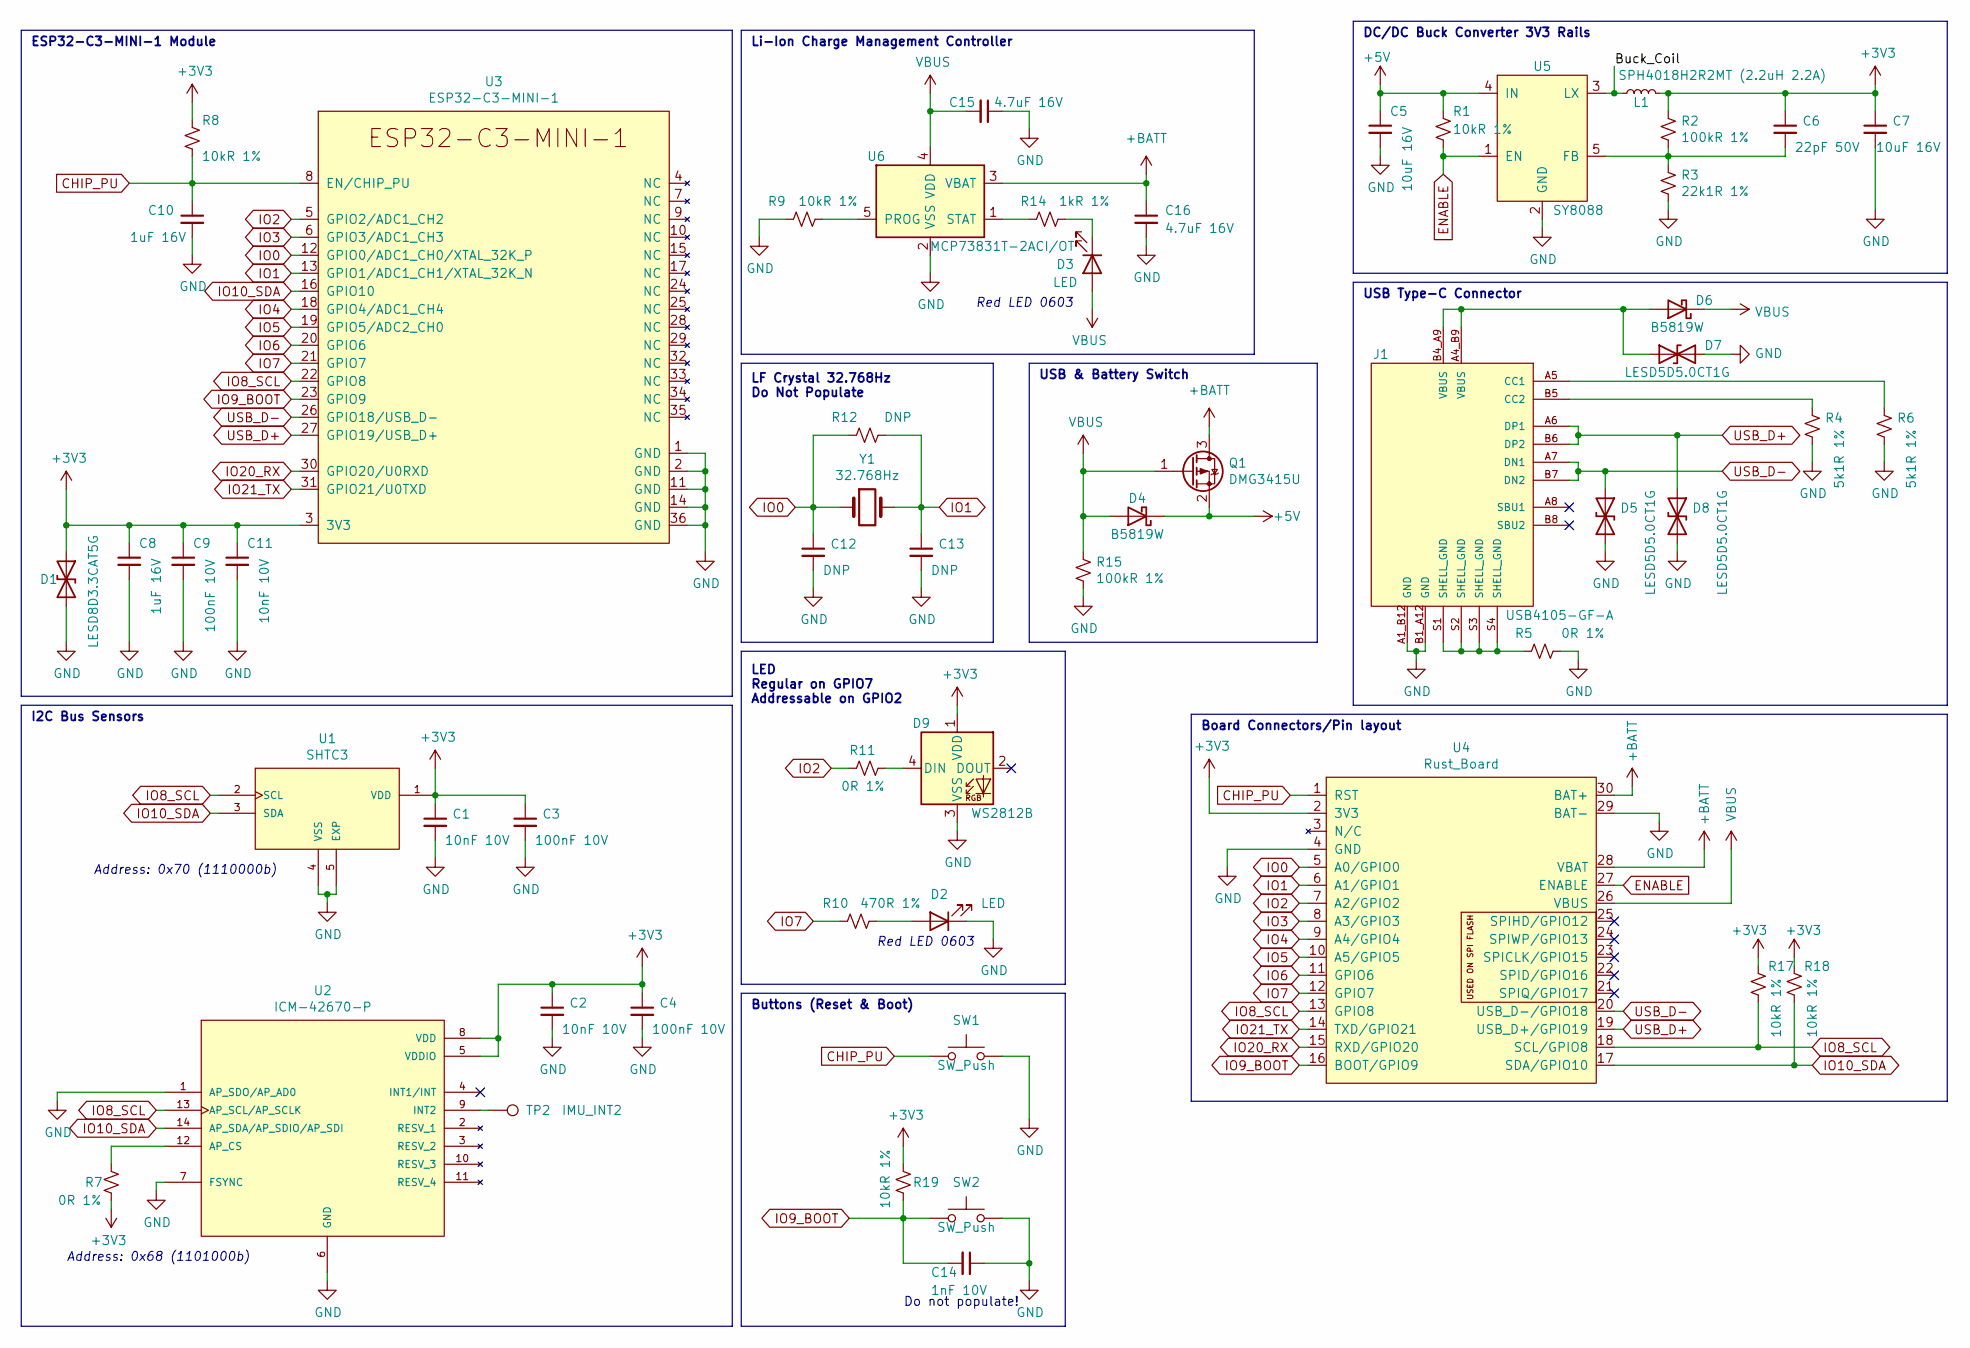
[picture p489: schematic esp-rust-board.kicad_sch, ESP32-C3-DevKit-RUST-1]

Parts:
C1, C2, C11: 10nF 10V; C_0402_1005Metric; LCSC C15195
C3, C4, C9: 100nF 10V; C_0402_1005Metric; LCSC C1525
C5, C7: 10uF 16V; C_0805_2012Metric; LCSC C15850
C6: 22pF 50V; C_0603_1608Metric; LCSC C1653
C8, C10: 1uF 16V; C_0402_1005Metric; LCSC C52923
C12, C13: DNP; C_0402_1005Metric
C14: 1nF 10V; C_0402_1005Metric; LCSC C1523
C15, C16: 4.7uF 16V; C_0603_1608Metric; LCSC C19666
D1: LESD8D3.3CAT5G; SOD-882; LCSC C172409
D2, D3: LED; LED_0603_1608Metric; LCSC C2286
D4, D6: B5819W; D_SOD-123; LCSC C8598
D5, D7, D8: LESD5D5.0CT1G; D_SOD-523; LCSC C383211
D9: WS2812B; LED_SK6812MINI_PLCC4_3.5x3.5mm_P1.75mm; LCSC C527089
J1: USB4105-GF-A; GCT_USB4105-GF-A; PARTREV A3; LCSC C165948
L1: SPH4018H2R2MT (2.2uH 2.2A); L_Bourns-SRN4018; LCSC C370436
Q1: DMG3415U; SOT-23; LCSC C96616
R1, R8, R9, R17, R18, R19: 10kR 1%; R_0402_1005Metric; LCSC C25744
R2, R15: 100kR 1%; R_0402_1005Metric; LCSC C25741
R3: 22k1R 1%; R_0402_1005Metric; LCSC C43473
R4, R6: 5k1R 1%; R_0402_1005Metric; LCSC C25905
R5, R7, R11: 0R 1%; R_0402_1005Metric; LCSC C17168
R10: 470R 1%; R_0402_1005Metric; LCSC C25117
R12: DNP; R_0402_1005Metric
R14: 1kR 1%; R_0402_1005Metric; LCSC C11702
SW1, SW2: SW_Push; SW_SPST_PTS810; LCSC C116501
TP2: IMU_INT2; TestPoint_Pad_D1.0mm
U1: SHTC3; SON100P200X200X80-5N; PARTREV 3; LCSC C194656
U2: ICM-42670-P; IC_ICM-42670-P; PARTREV 1.0
U3: ESP32-C3-MINI-1; LCSC C2838502
U4: Rust_Board
U5: SY8088; SOT-23-5; LCSC C479072
U6: MCP73831T-2ACI/OT; SOT-23-5; LCSC C424093
Y1: 32.768Hz; Crystal_SMD_3215-2Pin_3.2x1.5mm

Connections:
+3V3: C1.1, C2.1, C3.1, C4.1, C6.1, C7.1, C8.1, C9.1, C11.1, D1.1 (A1), D9.1 (VDD), L1.2, R2.1, R7.2, R8.1, R17.1, R18.1, R19.1, U1.1 (VDD), U2.5 (VDDIO), U2.8 (VDD), U3.3 (3V3), U4.2 (3V3)
+5V: C5.1, D4.1 (K), Q1.2 (S), R1.1, U5.4 (IN)
+BATT: C16.1, Q1.3 (D), U4.28 (VBAT), U4.30 (BAT+), U6.3 (VBAT)
/Buck_Coil: L1.1, U5.3 (LX)
CHIP_PU: C10.1, R8.2, SW1.1, U3.8 (EN/CHIP_PU), U4.1 (RST)
ENABLE: R1.2, U4.27 (ENABLE), U5.1 (EN)
GND: C1.2, C2.2, C3.2, C4.2, C5.2, C7.2, C8.2, C9.2, C10.2, C11.2, C12.2, C13.2, C14.1, C15.1, C16.2, D1.2 (A2), D2.1 (K), D5.2 (A2), D7.2 (A2), D8.2 (A2), D9.3 (VSS), J1.A1_B12 (GND), J1.B1_A12 (GND), R3.2, R4.2, R5.2, R6.2, R9.1, R15.2, SW1.2, SW2.2, U1.4 (VSS), U1.5 (EXP), U2.1 (AP_SDO/AP_AD0), U2.6 (GND), U2.7 (FSYNC), U3.1 (GND), U3.2 (GND), U3.11 (GND), U3.14 (GND), U3.36 (GND), U4.4 (GND), U4.29 (BAT-), U5.2 (GND), U6.2 (VSS)
IO0: C12.1, R12.1, U3.12 (GPIO0/ADC1_CH0/XTAL_32K_P), U4.5 (A0/GPIO0), Y1.1
IO1: C13.1, R12.2, U3.13 (GPIO1/ADC1_CH1/XTAL_32K_N), U4.6 (A1/GPIO1), Y1.2
IO2: R11.1, U3.5 (GPIO2/ADC1_CH2), U4.7 (A2/GPIO2)
IO3: U3.6 (GPIO3/ADC1_CH3), U4.8 (A3/GPIO3)
IO4: U3.18 (GPIO4/ADC1_CH4), U4.9 (A4/GPIO4)
IO5: U3.19 (GPIO5/ADC2_CH0), U4.10 (A5/GPIO5)
IO6: U3.20 (GPIO6), U4.11 (GPIO6)
IO7: R10.1, U3.21 (GPIO7), U4.12 (GPIO7)
IO8_SCL: R17.2, U1.2 (SCL), U2.13 (AP_SCL/AP_SCLK), U3.22 (GPIO8), U4.13 (GPIO8), U4.18 (SCL/GPIO8)
IO9_BOOT: C14.2, R19.2, SW2.1, U3.23 (GPIO9), U4.16 (BOOT/GPIO9)
IO10_SDA: R18.2, U1.3 (SDA), U2.14 (AP_SDA/AP_SDIO/AP_SDI), U3.16 (GPIO10), U4.17 (SDA/GPIO10)
IO20_RX: U3.30 (GPIO20/U0RXD), U4.15 (RXD/GPIO20)
IO21_TX: U3.31 (GPIO21/U0TXD), U4.14 (TXD/GPIO21)
unnamed: C6.2, R2.2, R3.1, U5.5 (FB)
unnamed: D2.2 (A), R10.2
unnamed: D3.1 (K), R14.2
unnamed: D6.2 (A), D7.1 (A1), J1.A4_B9 (VBUS), J1.B4_A9 (VBUS)
unnamed: D9.4 (DIN), R11.2
unnamed: J1.A5 (CC1), R6.1
unnamed: J1.B5 (CC2), R4.1
unnamed: J1.S1 (SHELL_GND), J1.S2 (SHELL_GND), J1.S3 (SHELL_GND), J1.S4 (SHELL_GND), R5.1
unnamed: R7.1, U2.12 (AP_CS)
unnamed: R9.2, U6.5 (PROG)
unnamed: R14.1, U6.1 (STAT)
unnamed: TP2.1, U2.9 (INT2)
USB_D+: D8.1 (A1), J1.A6 (DP1), J1.B6 (DP2), U3.27 (GPIO19/USB_D+), U4.19 (USB_D+/GPIO19)
USB_D-: D5.1 (A1), J1.A7 (DN1), J1.B7 (DN2), U3.26 (GPIO18/USB_D-), U4.20 (USB_D-/GPIO18)
VBUS: C15.2, D3.2 (A), D4.2 (A), D6.1 (K), Q1.1 (G), R15.1, U4.26 (VBUS), U6.4 (VDD)

Notes on the sheet:
USB Type-C Connector
Do not populate!
Buttons (Reset & Boot)
Address: 0x70 (1110000b)
Red LED 0603
LF Crystal 32.768Hz Do Not Populate
DC/DC Buck Converter 3V3 Rails
USB & Battery Switch
Board Connectors/Pin layout
LED Regular on GPIO7 Addressable on GPIO2
Address: 0x68 (1101000b)
ESP32-C3-MINI-1 Module
Li-Ion Charge Management Controller
I2C Bus Sensors

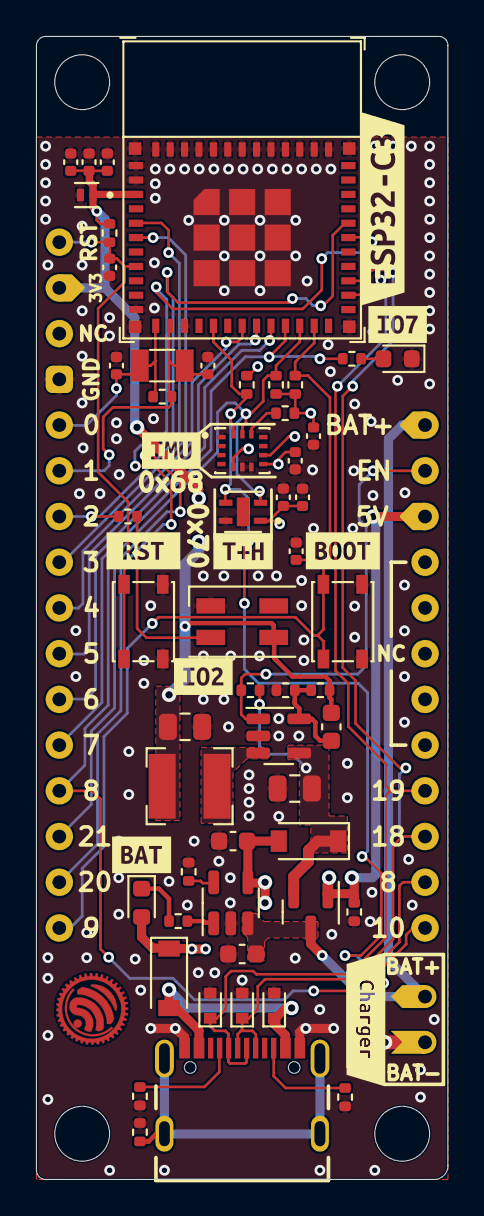
[picture p490: board esp-rust-board.kicad_pcb from above]

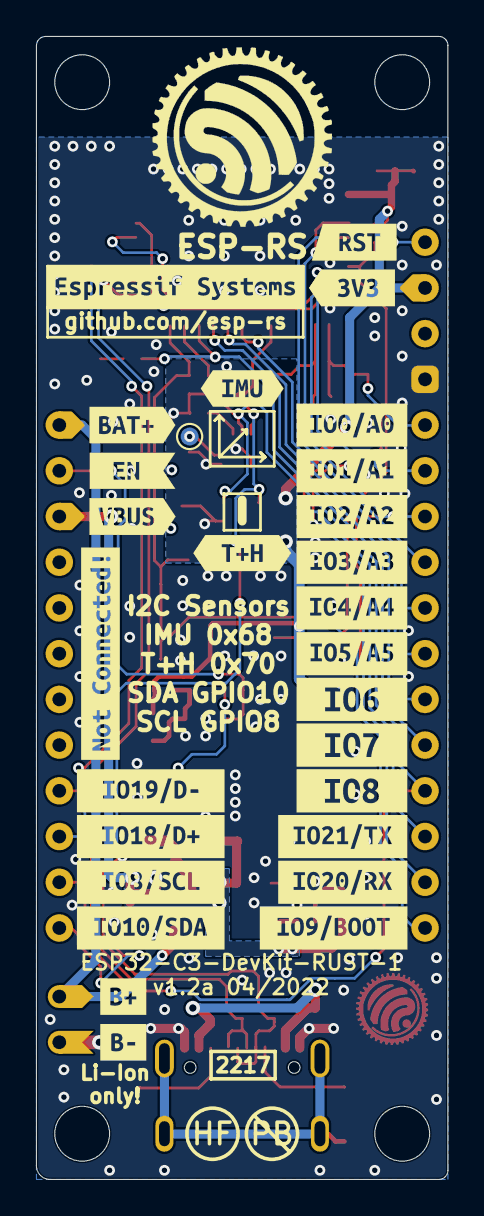
[picture p491: board esp-rust-board.kicad_pcb from below]

Board: 2 copper layers, 22.9 x 63.5 mm, 92 parts (28 on the bottom side), 35 nets.

Other parts of the board:
kibuzzard-61B9CCBB, kibuzzard-61B9CE3D, kibuzzard-61B9CE86, kibuzzard-61B9CEAB, kibuzzard-61B9EF98, kibuzzard-61C0F3FF, kibuzzard-61C0F315, kibuzzard-61C0F325, kibuzzard-61C0F363, kibuzzard-61C0F406, kibuzzard-61C0F511, kibuzzard-61C0F551, kibuzzard-61C05A1A, kibuzzard-61C05A22, kibuzzard-61C05B60, kibuzzard-61C05BAC, kibuzzard-61C05C0D, kibuzzard-61C05C87, kibuzzard-61C05C92, kibuzzard-61C05D58, kibuzzard-61C05D75, kibuzzard-61C05DB0, kibuzzard-61C057D5, kibuzzard-61C057FD, kibuzzard-61C0588C, kibuzzard-61C0597E, kibuzzard-61C05335, kibuzzard-61C05804, kibuzzard-61C05909, kibuzzard-61C05949, kibuzzard-61C05975: G***; label
kibuzzard-61E1AB2E: G***; kibuzzard-61E1AB2E
kibuzzard-61F2685B: G***; kibuzzard-61F2685B
kibuzzard-61F26841: G***; kibuzzard-61F26841
kibuzzard-61F26855: G***; kibuzzard-61F26855
kibuzzard-623DAB98: G***; kibuzzard-623DAB98
kibuzzard-6269032F: G***; kibuzzard-6269032F
