rompasaurus/regardedPal/hardware-design/examples/04-olimex-s3-devkit-lipo/HARDWARE/ESP32-S3-DevKit-LiPo_Rev_B/ESP32-S3-DevKit-LiPo_Rev_B.kicad_pcb

## KiCad design hardware-design/examples/04-olimex-s3-devkit-lipo/HARDWARE/ESP32-S3-DevKit-LiPo_Rev_B/ESP32-S3-DevKit-LiPo_Rev_B.kicad_pcb (2026-04-15)

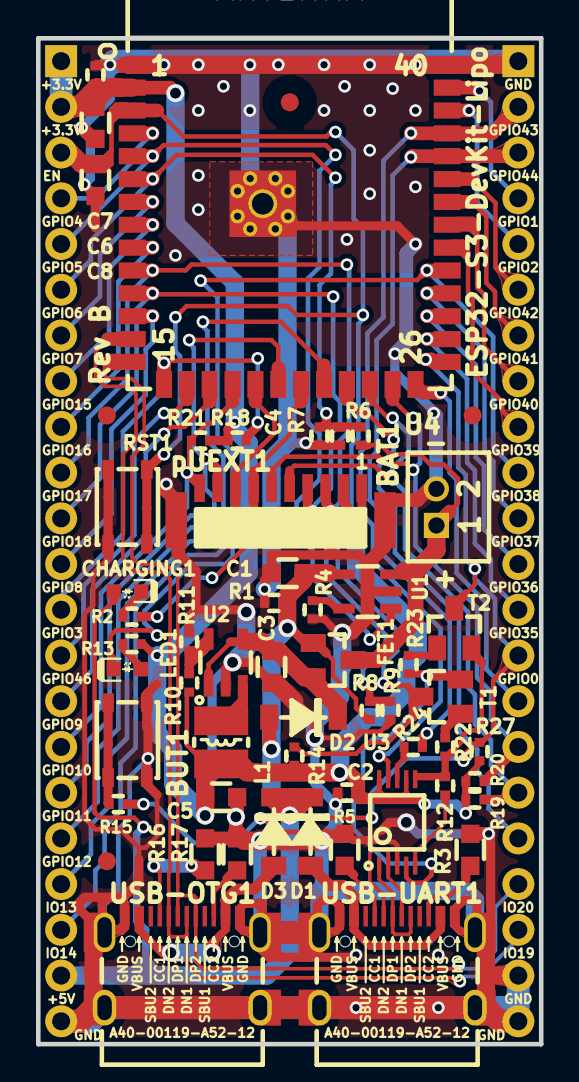
[picture p492: board ESP32-S3-DevKit-LiPo_Rev_B.kicad_pcb from above]

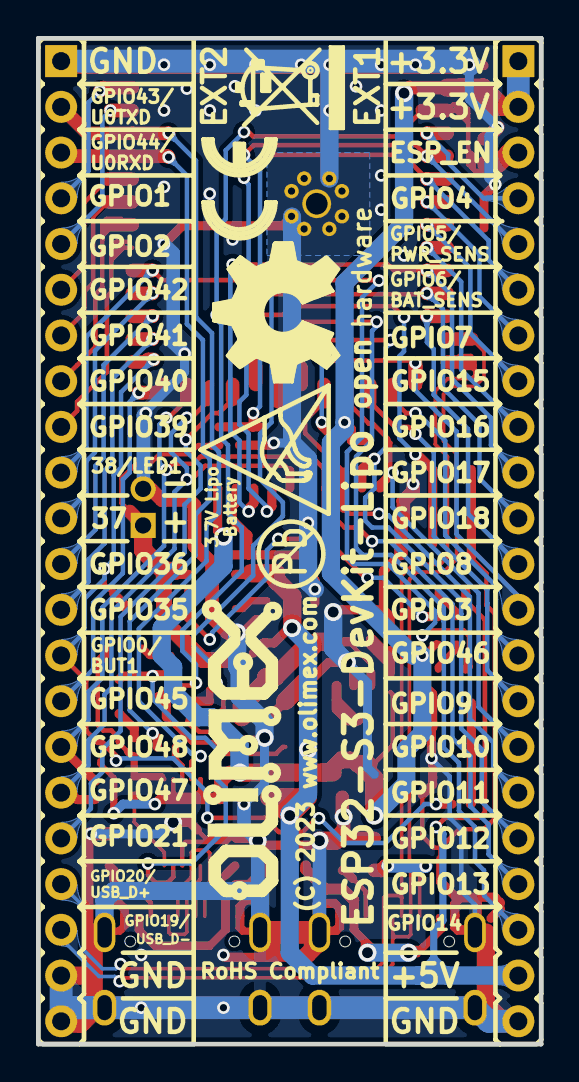
[picture p493: board ESP32-S3-DevKit-LiPo_Rev_B.kicad_pcb from below]

Board: 2 copper layers, 27.9 x 55.9 mm, 64 parts (8 on the bottom side), 63 nets.

Parts:
BAT1: DW02S; LIPO_BAT_VERTICAL_DW02S
BUT1: YTS-A016-X
C1, C3, C5, C6: 22uF/6.3V/20%/X5R/C0603; C_0603_5MIL_DWS
C2, C4, C7: 100nF/10V/10%/X7R/C0402; C_0402_5MIL_DWS
C8: 1uF/10V/10%/X5R/C0603; C_0603_5MIL_DWS
CHARGING1: LED/YELLOW/0603; LED_0603_KA
D1, D2, D3: 1N5819S4/SOD123; SOD-123_1C-2A_KA
EXT1, EXT2: HN1x22
FET1: WPM2015-3/TR; SOT23
FID1, FID2, FID3, FID4: Fiducial; Fiducial1x3
L1: 2.2uH/1.5A/DCR=72mR/20%/3.00x3.00x1.50mm/CD32(NR3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; CD32
LED1: LED/Green/0603; LED_0603_KA
Logo_OLIMEX_TB: Logo_OLIMEX_TB
R1, R4, R14, R18, R21: 10k/R0402; R_0402_5MIL_DWS
R2, R13, R19, R20: 2.2k/R0402; R_0402_5MIL_DWS
R3, R5, R16, R17: 5.1k/R0603; R_0603_5MIL_DWS
R6, R9: 470k/R0402; R_0402_5MIL_DWS
R7: 150k/R0402; R_0402_5MIL_DWS
R8, R10: 220k/R0402; R_0402_5MIL_DWS
R11: 49.9k/1%/R0402; R_0402_5MIL_DWS
R12: 4.7k/R0402; R_0402_5MIL_DWS
R15, R24: 100R/R0402; R_0402_5MIL_DWS
R22, R23: 1k/R0402; R_0402_5MIL_DWS
R27: NA/R0402; R_0402_5MIL_DWS
RST1: YTS-A016-X
Sign_Antistatic: Sign_Antistatic
Sign_CE: CE_Sign
Sign_OSHW_8x8: Sign_OSHW_8x8
Sign_PB-Free: Sign_PB-Free
Sign_RecycleBin_1: Sign_RecycleBin_1
T1, T2: BC817-40(SOT23); SOT23
U1: BL4054B-42TPRN(SOT23-5); SOT-23-5
U2: SY8089AAAC(SOT23-5); SOT-23-5
U3: CH340X(MSOP-10); MSOP-10_Pitch-0.5mm_3.00x3.00x1.00mm
U4: ESP32-S3-WROOM-1-N8R8; ESP32-­S3-­WROOM­-1
USB-OTG1: USB-C-16P-F(A40-00119-A52-12); USB2.0_TYPE-C(A40-00119-A52-12)
USB-UART1: USB-C-16P-F(A40-00119-A52-12); USB2.0_TYPE-C(A40-00119-A52-12)
pUEXT1: JST_BM10B-SRSS-TB; BM10B-SRSS-TB

Connections:
+3.3V: C2.1, C5.1, C6.1, C7.2, EXT1.1, EXT1.2, L1.2, R10.2, R13.1, R14.1, R18.1, R19.1, R20.1, R21.1, R27.1, U3.7, U3.10, U4.2, pUEXT1.1
+5V: C1.1, CHARGING1.2, D1.1, D2.2, D3.1, EXT1.21, FET1.1, R1.1, R8.1, U1.4
/ESP_EN: C8.1, EXT1.3, R14.2, RST1.2, T1.3, U4.3
/GPIO0\BUT1: EXT2.14, R15.1, R27.2, T2.3, U4.27
/GPIO1: EXT2.4, U4.39
/GPIO2: EXT2.5, U4.38
/GPIO3: EXT1.13, R18.2, U4.15
/GPIO4: EXT1.4, U4.4
/GPIO5\PWR_SENS: EXT1.5, R8.2, R9.1, U4.5
/GPIO6\BAT_SENS: C4.2, EXT1.6, R6.2, R7.1, U4.6
/GPIO7: EXT1.7, U4.7
/GPIO8: EXT1.12, U4.12
/GPIO9: EXT1.15, U4.17
/GPIO10\FSPICS0(SPI3_CS0): EXT1.16, R21.2, U4.18, pUEXT1.10
/GPIO11\FSPID(SPI3_MOSI): EXT1.17, U4.19, pUEXT1.8
/GPIO12\FSPICLK(SPI3_CLK): EXT1.18, U4.20, pUEXT1.9
/GPIO13\FSPIQ(SPI3_MISO): EXT1.19, U4.21, pUEXT1.7
/GPIO14: EXT1.20, U4.22
/GPIO15: EXT1.8, U4.8
/GPIO16: EXT1.9, U4.9
/GPIO17\U1TXD: EXT1.10, U4.10, pUEXT1.3
/GPIO18\U1RXD: EXT1.11, U4.11, pUEXT1.4
/GPIO19\USB_D-: EXT2.20, U4.13, USB-OTG1.A7, USB-OTG1.B7
/GPIO20\USB_D+: EXT2.19, U4.14, USB-OTG1.A6, USB-OTG1.B6
/GPIO21: EXT2.18, U4.23
/GPIO35: EXT2.13, U4.28
/GPIO36: EXT2.12, U4.29
/GPIO37: EXT2.11, U4.30
/GPIO38\LED1: EXT2.10, LED1.1, U4.31
/GPIO39: EXT2.9, U4.32
/GPIO40: EXT2.8, U4.33
/GPIO41: EXT2.7, U4.34
/GPIO42: EXT2.6, U4.35
/GPIO43\U0TXD: EXT2.2, U3.9, U4.37
/GPIO44\U0RXD: EXT2.3, R24.2, U4.36
/GPIO45: EXT2.15, U4.26
/GPIO46: EXT1.14, U4.16
/GPIO47\I2C_SCL: EXT2.17, R19.2, U4.24, pUEXT1.5
/GPIO48\I2C_SDA: EXT2.16, R20.2, U4.25, pUEXT1.6
/UD+: U3.1, USB-UART1.A6, USB-UART1.B6
/UD-: U3.2, USB-UART1.A7, USB-UART1.B7
GND: BAT1.2, BUT1.2, C1.2, C2.2, C3.2, C4.1, C5.2, C6.2, C7.1, C8.2, EXT1.22, EXT2.1, EXT2.21, EXT2.22, R1.2, R3.1, R4.2, R5.1, R7.2, R9.2, R11.2, R16.1, R17.1, RST1.1, U1.2, U2.2, U3.3, U4.1, U4.40, U4.41, USB-OTG1.0, USB-OTG1.A1, USB-OTG1.A12, USB-OTG1.B1, USB-OTG1.B12, USB-UART1.0, USB-UART1.A1, USB-UART1.A12, USB-UART1.B1, USB-UART1.B12, pUEXT1.0, pUEXT1.2
unnamed: BUT1.1, R15.2
unnamed: C3.1, D2.1, FET1.2, U2.1, U2.4
unnamed: CHARGING1.1, R2.1
unnamed: D1.2, USB-UART1.A4, USB-UART1.A9, USB-UART1.B4, USB-UART1.B9
unnamed: D3.2, USB-OTG1.A4, USB-OTG1.A9, USB-OTG1.B4, USB-OTG1.B9
unnamed: L1.1, U2.3
unnamed: LED1.2, R13.2
unnamed: R2.2, U1.1
unnamed: R3.2, USB-UART1.B5
unnamed: R4.1, U1.5
unnamed: R5.2, USB-UART1.A5
unnamed: R10.1, R11.1, U2.5
unnamed: R12.1, U3.5
unnamed: R12.2, R22.1, T2.2, U3.6
unnamed: R16.2, USB-OTG1.A5
unnamed: R17.2, USB-OTG1.B5
unnamed: R22.2, T1.1
unnamed: R23.1, T1.2, U3.4
unnamed: R23.2, T2.1
unnamed: R24.1, U3.8
VBAT: BAT1.1, FET1.3, R6.1, U1.3
