rompasaurus/regardedPal/hardware-design/examples/06-unexpected-maker-s3/kicad/NanoS3 Carrier/NanoS3_Carrier.kicad_pcb

## KiCad design hardware-design/examples/06-unexpected-maker-s3/kicad/NanoS3 Carrier/NanoS3_Carrier.kicad_pcb (2026-04-15)

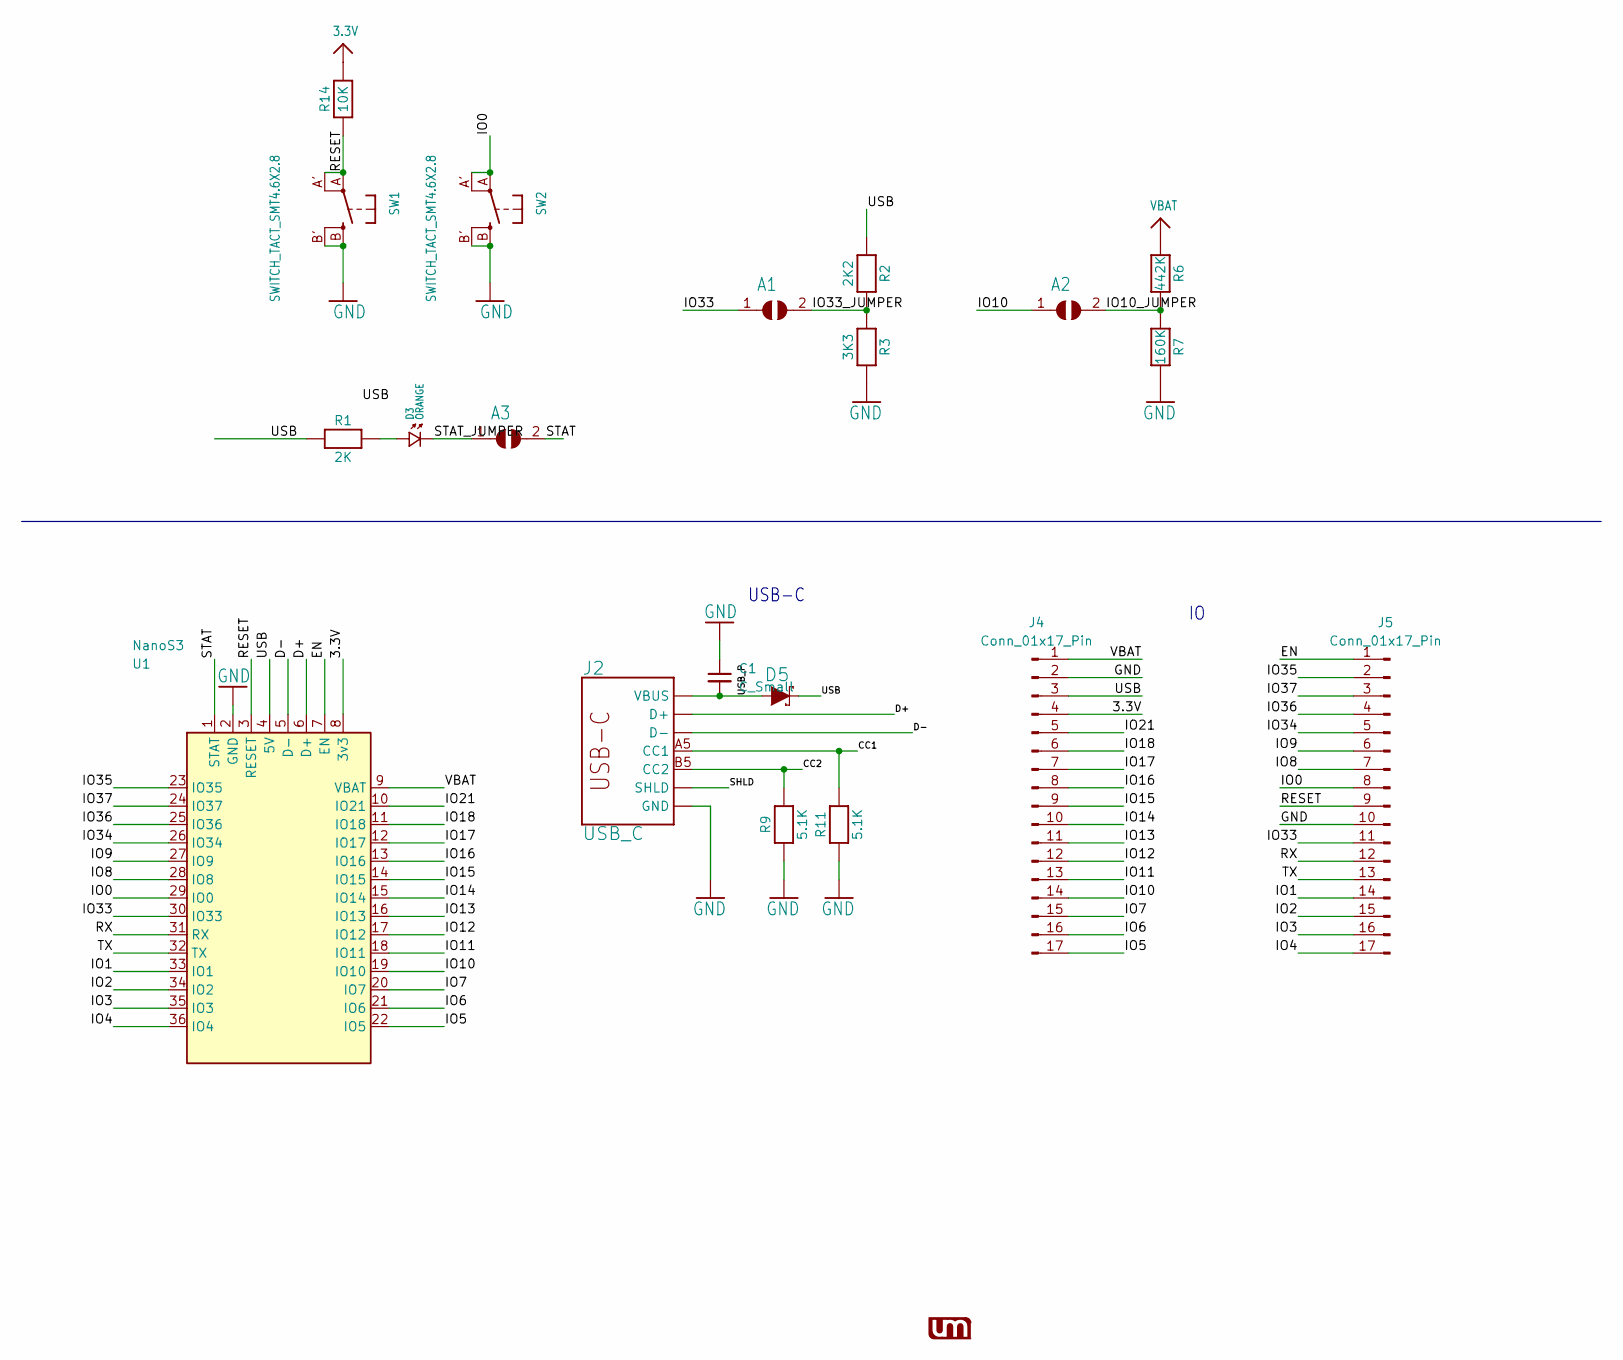
[picture p494: schematic NanoS3_Carrier.kicad_sch, NanoS3 Carrier]

Parts:
A1, A2, A3: SOLDERJUMPERCLOSED; SOLDERJUMPER_CLOSEDWIRE
C1: C_Small; C_0603_1608Metric
D3: ORANGE; 0402.LED.W
D5: DIODE-SCHOTTKYWIDE; SOD-523W
J2: USB_C; USB-C-16P-LESSPASTE-2-FIxed
J4, J5: Conn_01x17_Pin; 1X17_BLIZZARD_S3_BOTTOM
R1: 2K; _0402_SRWW
R2: 2K2; _0402_SRWW
R3: 3K3; _0402_SRWW
R6: 442K; _0402_SRWW
R7: 160K; _0402_SRWW
R9, R11: 5.1K; _0402_SRWW
R14: 10K; _0402_SRWW
SW1, SW2: SWITCH_TACT_SMT4.6X2.8; BTN_KMR2_4.6X2.8
U1: NanoS3
U$88: UM_LOGONEW_SMALLER; UM_LOGO_NEW_SMALLER

Connections:
3.3V: J4.4, R14.2, U1.8 (3v3)
/CC1: J2.A5 (CC1), R11.2
/CC2: J2.B5 (CC2), R9.2
/D+: J2.A6 (D+), J2.B6 (D+), U1.6 (D+)
/D-: J2.A7 (D-), J2.B7 (D-), U1.5 (D-)
/EN: J5.1, U1.7 (EN)
/IO0: J5.8, SW2.A, SW2.A' (P1), U1.29 (IO0)
/IO1: J5.14, U1.33 (IO1)
/IO2: J5.15, U1.34 (IO2)
/IO3: J5.16, U1.35 (IO3)
/IO4: J5.17, U1.36 (IO4)
/IO5: J4.17, U1.22 (IO5)
/IO6: J4.16, U1.21 (IO6)
/IO7: J4.15, U1.20 (IO7)
/IO8: J5.7, U1.28 (IO8)
/IO9: J5.6, U1.27 (IO9)
/IO10: A2.1, J4.14, U1.19 (IO10)
/IO10_JUMPER: A2.2, R6.2, R7.1
/IO11: J4.13, U1.18 (IO11)
/IO12: J4.12, U1.17 (IO12)
/IO13: J4.11, U1.16 (IO13)
/IO14: J4.10, U1.15 (IO14)
/IO15: J4.9, U1.14 (IO15)
/IO16: J4.8, U1.13 (IO16)
/IO17: J4.7, U1.12 (IO17)
/IO18: J4.6, U1.11 (IO18)
/IO21: J4.5, U1.10 (IO21)
/IO33: A1.1, J5.11, U1.30 (IO33)
/IO33_JUMPER: A1.2, R2.2, R3.1
/IO34: J5.5, U1.26 (IO34)
/IO35: J5.2, U1.23 (IO35)
/IO36: J5.4, U1.25 (IO36)
/IO37: J5.3, U1.24 (IO37)
/RESET: J5.9, R14.1, SW1.A, SW1.A' (P1), U1.3 (RESET)
/RX: J5.12, U1.31 (RX)
/STAT: A3.2, U1.1 (STAT)
/STAT_JUMPER: A3.1, D3.2
/TX: J5.13, U1.32 (TX)
/USB: D5.C, J4.3, R1.1, R2.1, U1.4 (5V)
/USB_P: C1.2, D5.A, J2.VBUS1 (VBUS), J2.VBUS2 (VBUS)
unnamed: D3.1, R1.2
VBAT: J4.1, R6.1, U1.9 (VBAT)

Notes on the sheet:
USB-C

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
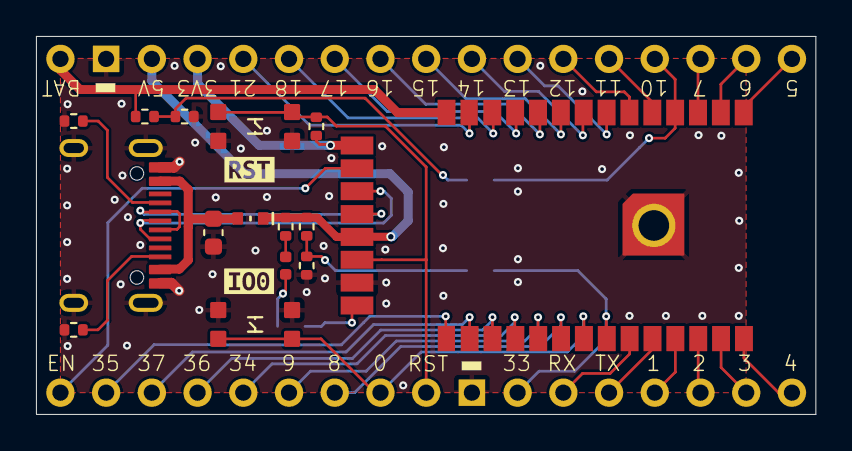
[picture p495: board NanoS3_Carrier.kicad_pcb from above]

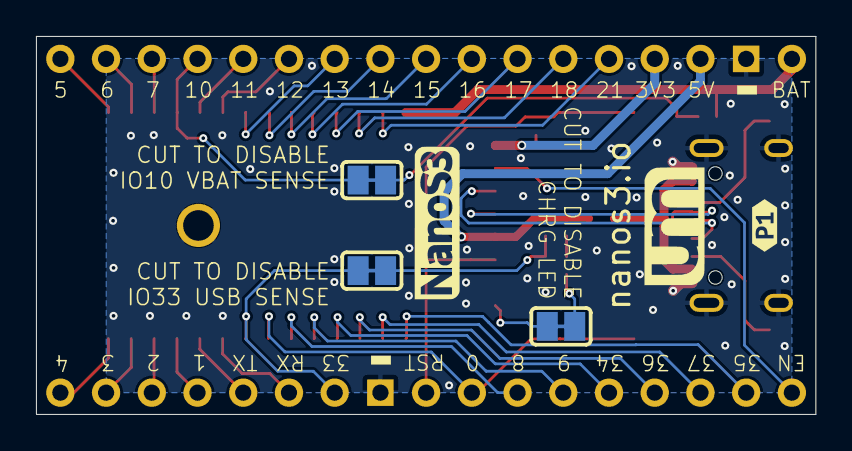
[picture p496: board NanoS3_Carrier.kicad_pcb from below]

Board: 2 copper layers, 43.3 x 21.0 mm, 24 parts (5 on the bottom side), 43 nets.

Other parts of the board:
kibuzzard-649F567F: G***; kibuzzard-649F567F
kibuzzard-649F677A: G***; kibuzzard-649F677A
kibuzzard-649F5696: G***; kibuzzard-649F5696
