rompasaurus/regardedPal/hardware-design/examples/06-unexpected-maker-s3/kicad/OMGS3 Carrier/OMGS3_Carrier_R1.kicad_pcb

## KiCad design hardware-design/examples/06-unexpected-maker-s3/kicad/OMGS3 Carrier/OMGS3_Carrier_R1.kicad_pcb (2026-04-15)

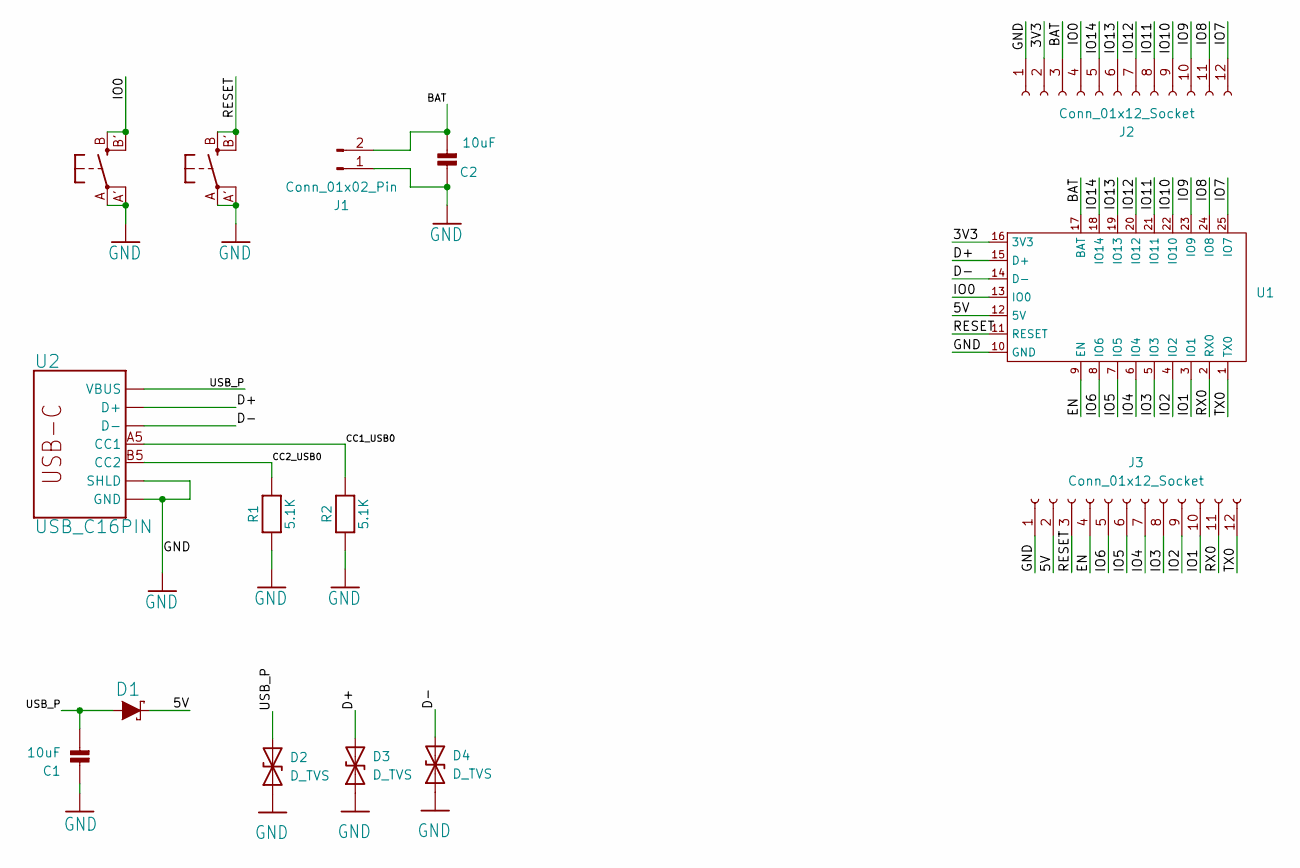
[picture p497: schematic OMGS3_Carrier_R1.kicad_sch, OMGS3 Reference Carrier Design]

Parts:
C1, C2: 10uF; C_0603_1608Metric
D1: DIODE-SCHOTTKYWIDE; SOD-523-MSK4010
D2, D3, D4: D_TVS; X1-DFN1006-2
J1: Conn_01x02_Pin; JST-PICOBLADE
J2, J3: Conn_01x12_Socket; PinHeader_1x12_P2.54mm_Vertical
R1, R2: 5.1K; R_0402_1005Metric
SW1, SW2: KMR2; BTN_KMR2_4.6X2.8
U1: OMGS3
U2: USB_C16PIN; USB-C-16P-LESSPASTE-2-Fixed-Sqr-Front

Connections:
/3V3: J2.2, U1.16 (3V3)
/5V: D1.C, J3.2, U1.12 (5V)
/BAT: C2.2, J1.2, J2.3, U1.17 (BAT)
/CC1_USB0: R2.2, U2.A5 (CC1)
/CC2_USB0: R1.2, U2.B5 (CC2)
/D+: D3.2 (A2), U1.15 (D+), U2.A6 (D+), U2.B6 (D+)
/D-: D4.2 (A2), U1.14 (D-), U2.A7 (D-), U2.B7 (D-)
/EN: J3.4, U1.9 (EN)
/IO0: J2.4, SW1.B (S), SW1.B' (S1), U1.13 (IO0)
/IO1: J3.10, U1.3 (IO1)
/IO2: J3.9, U1.4 (IO2)
/IO3: J3.8, U1.5 (IO3)
/IO4: J3.7, U1.6 (IO4)
/IO5: J3.6, U1.7 (IO5)
/IO6: J3.5, U1.8 (IO6)
/IO7: J2.12, U1.25 (IO7)
/IO8: J2.11, U1.24 (IO8)
/IO9: J2.10, U1.23 (IO9)
/IO10: J2.9, U1.22 (IO10)
/IO11: J2.8, U1.21 (IO11)
/IO12: J2.7, U1.20 (IO12)
/IO13: J2.6, U1.19 (IO13)
/IO14: J2.5, U1.18 (IO14)
/RESET: J3.3, SW2.B (S), SW2.B' (S1), U1.11 (RESET)
/RX0: J3.11, U1.2 (RX0)
/TX0: J3.12, U1.1 (TX0)
/USB_P: C1.2, D1.A, D2.2 (A2), U2.VBUS1 (VBUS), U2.VBUS2 (VBUS)
GND: C1.1, C2.1, D2.1 (A1), D3.1 (A1), D4.1 (A1), J1.1, J2.1, J3.1, R1.1, R2.1, SW1.A, SW1.A' (P1), SW2.A, SW2.A' (P1), U1.10 (GND), U1.EXP, U2.GND, U2.GND2 (GND), U2.SHLD, U2.SHLD1 (SHLD), U2.SHLD2 (SHLD), U2.SHLD3 (SHLD), U2.SHLD4 (SHLD), U2.SHLD5 (SHLD), U2.SHLD6 (SHLD), U2.SHLD7 (SHLD), U2.SHLD8 (SHLD)

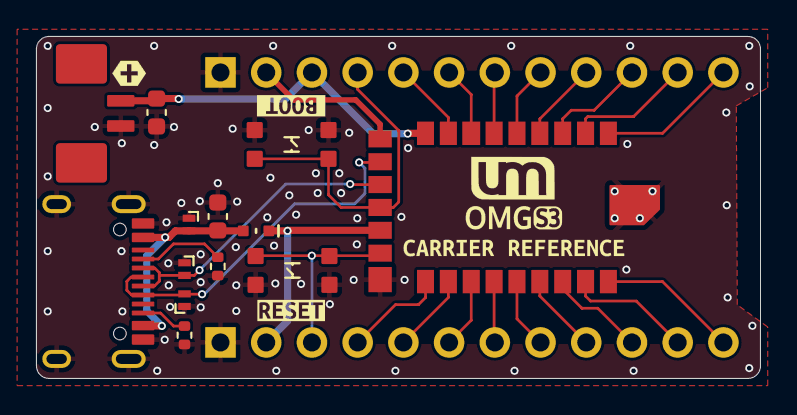
[picture p498: board OMGS3_Carrier_R1.kicad_pcb from above]

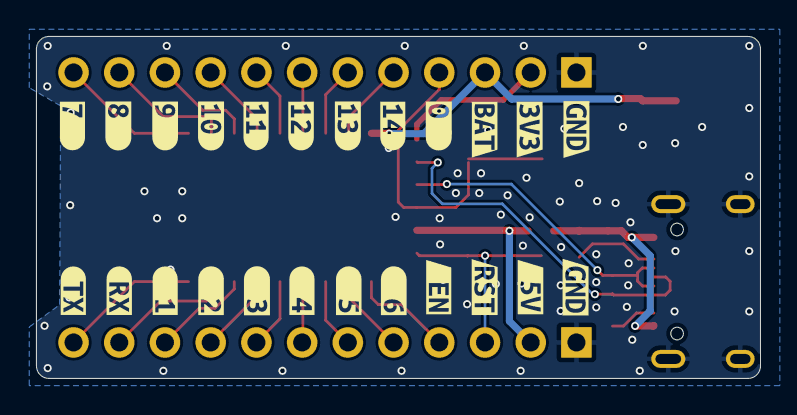
[picture p499: board OMGS3_Carrier_R1.kicad_pcb from below]

Board: 2 copper layers, 40.2 x 19.0 mm, 43 parts (24 on the bottom side), 28 nets.

Other parts of the board:
kibuzzard-66A337D7: G***; kibuzzard-66A337D7
kibuzzard-66A3379E: G***; kibuzzard-66A3379E
kibuzzard-66BFF9CC: G***; kibuzzard-66BFF9CC
kibuzzard-66BFF9DF: G***; kibuzzard-66BFF9DF
kibuzzard-66BFF9E6: G***; kibuzzard-66BFF9E6
kibuzzard-66BFF9F3: G***; kibuzzard-66BFF9F3
kibuzzard-66BFF9F9: G***; kibuzzard-66BFF9F9
kibuzzard-66BFF9FE: G***; kibuzzard-66BFF9FE
kibuzzard-66BFFA1D: G***; kibuzzard-66BFFA1D
kibuzzard-66BFFA03: G***; kibuzzard-66BFFA03
kibuzzard-66BFFA07: G***; kibuzzard-66BFFA07
kibuzzard-66BFFA15: G***; kibuzzard-66BFFA15
kibuzzard-66BFFA19: G***; kibuzzard-66BFFA19
kibuzzard-66BFFA21: G***; kibuzzard-66BFFA21
kibuzzard-66BFFAE0: G***; kibuzzard-66BFFAE0
kibuzzard-66BFFAF9: G***; kibuzzard-66BFFAF9
kibuzzard-66BFFB0C: G***; kibuzzard-66BFFB0C
kibuzzard-66BFFB4C: G***; kibuzzard-66BFFB4C
kibuzzard-66BFFB4F: G***; kibuzzard-66BFFB4F
kibuzzard-66BFFB5D: G***; kibuzzard-66BFFB5D
kibuzzard-66BFFB12: G***; kibuzzard-66BFFB12
kibuzzard-66BFFB21: G***; kibuzzard-66BFFB21
kibuzzard-66BFFB47: G***; kibuzzard-66BFFB47
kibuzzard-66BFFB52: G***; kibuzzard-66BFFB52
kibuzzard-66BFFB54: G***; kibuzzard-66BFFB54
kibuzzard-66BFFB58: G***; kibuzzard-66BFFB58
kibuzzard-66C531C2: G***; kibuzzard-66C531C2
kibuzzard-66C53217: G***; kibuzzard-66C53217
