rompasaurus/regardedPal/hardware-design/examples/10-klp5e-sensor-board/KiCad project/ESP32 sensor board.kicad_pcb

## KiCad design hardware-design/examples/10-klp5e-sensor-board/KiCad project/ESP32 sensor board.kicad_pcb (2026-04-15)

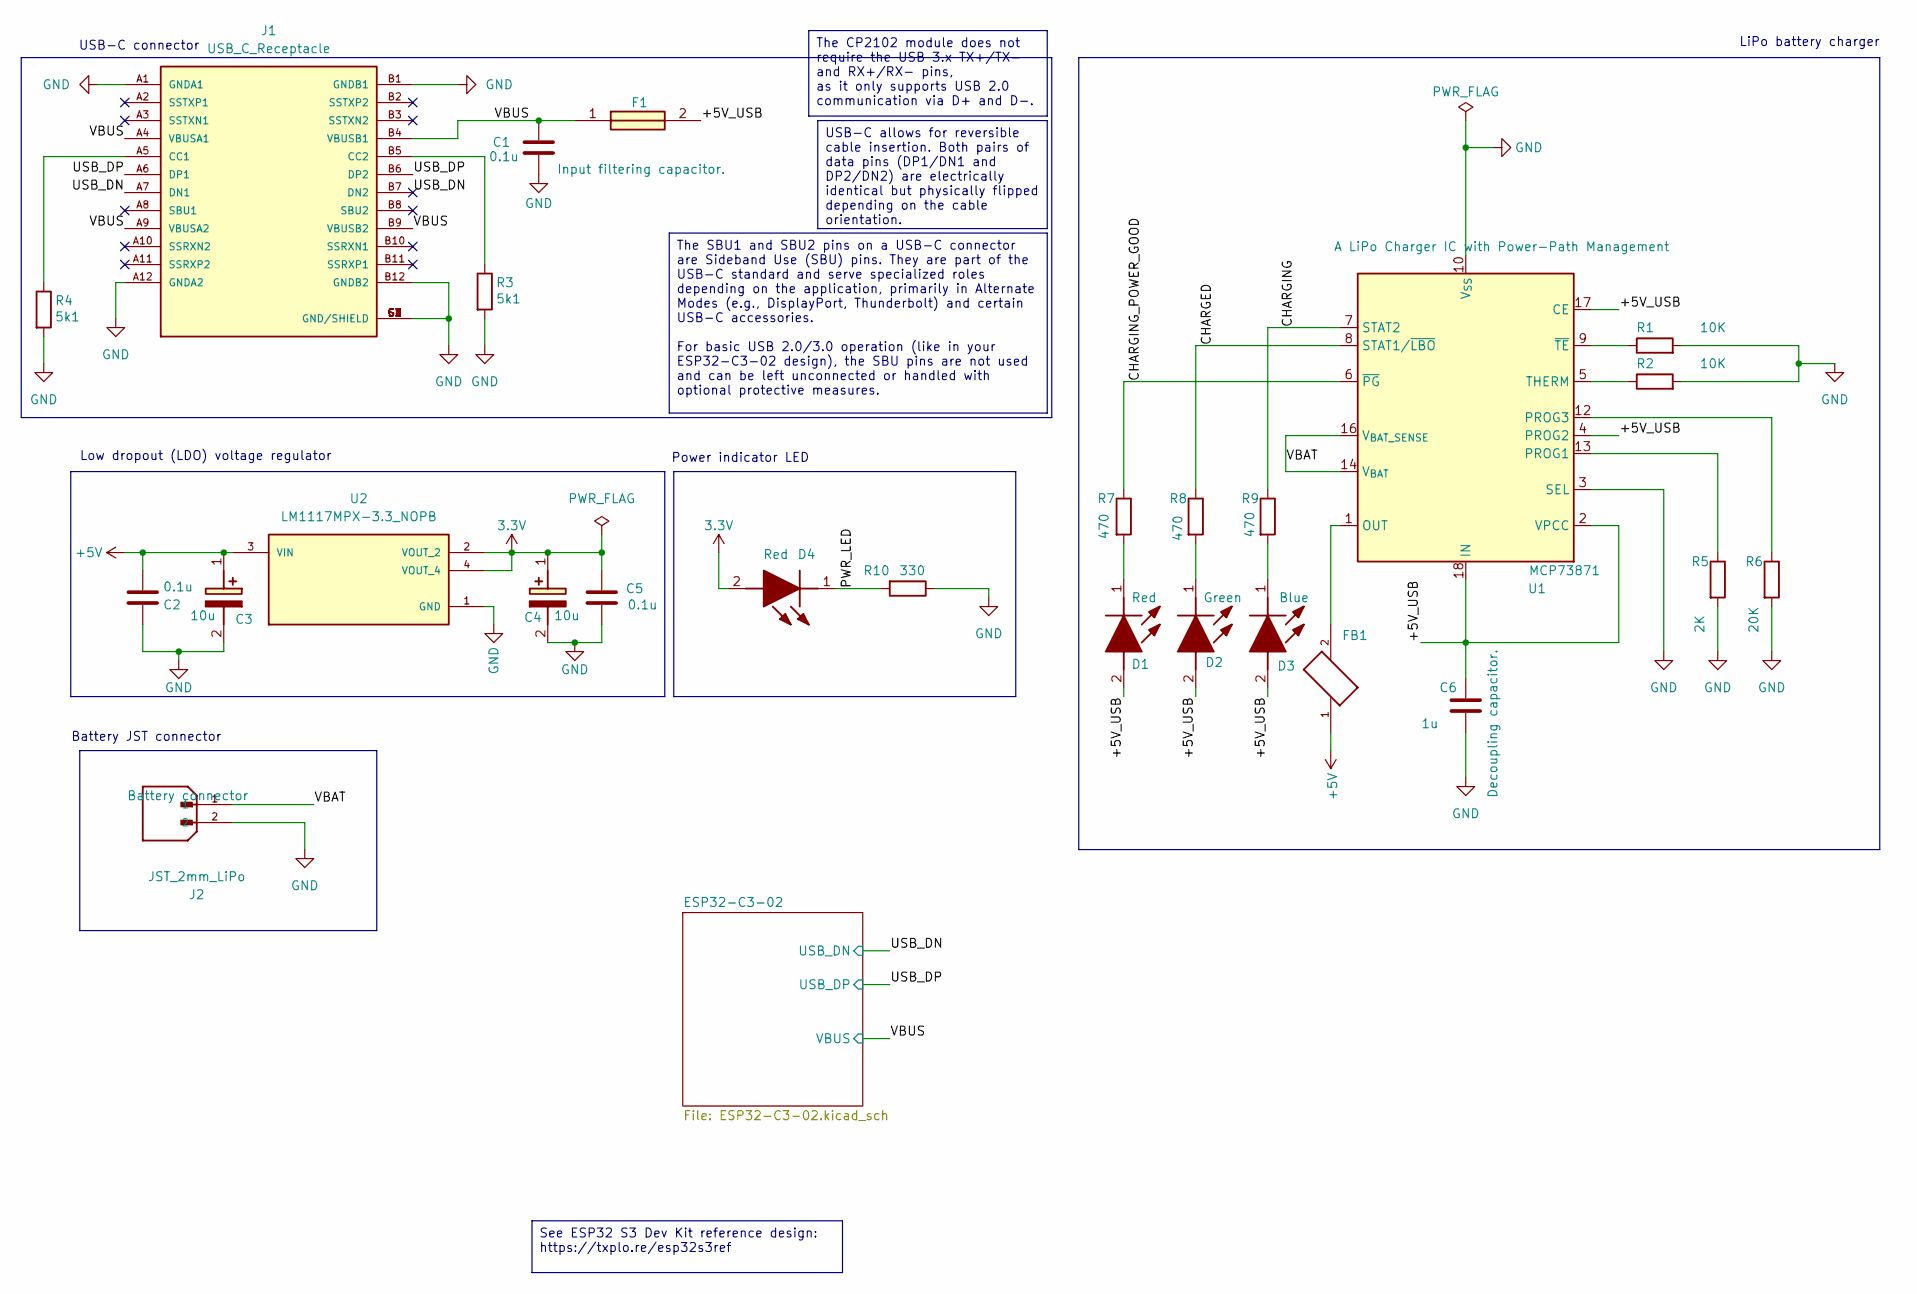
[picture p500: schematic ESP32 sensor board.kicad_sch]

Parts:
C1, C2, C5: 0.1u; C_0805_2012Metric; Voltage 1kV; Tolerance 100%
C3, C4: 10u; T491A; Voltage 1kV; Tolerance 100%; Manufacturer_Part_Number T491A106K010AT7280; Mouser Part Number 80-T491A106K107280
C6: 1u; C_0805_2012Metric; Voltage 1kV; Tolerance 100%
D1, D4: Red; LEDC2012X120N; Manufacturer_Part_Number LTST-C170KRKT; Mouser Part Number 859-LTST-C170KRKT
D2: Green; LEDC2012X120N; Manufacturer_Part_Number LTST-C170GKT; Mouser Part Number 859-LTST-C170GKT
D3: Blue; LEDC2012X120N; Manufacturer_Part_Number LTST-C170TBKT; Mouser Part Number 859-LTST-C170TBKT
F1: 0ZCH0110AF2E; FUSC3226X100N; Manufacturer_Part_Number 0ZCH0110AF2E
FB1: FBMJ2125HM330-T; BEADC2012X105N
J1: USB_C_Receptacle; BELFUSE_SS-52400-002; PARTREV A0
J2: JST_2mm_LiPo; JST_B2B-PH-SM4-TB; Manufacturer_Part_Number ?
R1, R2: 10K; R_0805_2012Metric
R3, R4: 5k1; R_0805_2012Metric
R5: 2K; R_0805_2012Metric
R6: 20K; R_0805_2012Metric
R7, R8, R9: 470; R_0805_2012Metric
R10: 330; R_0805_2012Metric
U1: MCP73871; QFN-20-1EP_4x4mm_P0.5mm_EP2.5x2.5mm; Manufacturer_Part_Number MCP73871-4CCI/ML
U2: LM1117MPX-3.3_NOPB; VREG_LM1117MPX-3.3; Mouser Part Number 926-LM1117MPX3.3NOPB

Connections:
3.3V: C4.1 (+), C5.1, D4.2 (A), U2.2 (VOUT_2), U2.4 (VOUT_4); also elsewhere on the board
+5V: C2.1, C3.1 (+), FB1.1, U2.3 (VIN)
/+5V_USB: C6.1, D1.2 (A), D2.2 (A), D3.2 (A), F1.2, U1.2 (VPCC), U1.4 (PROG2), U1.17 (CE), U1.18 (IN), U1.19 (IN)
/CHARGED: R8.1, U1.8 (STAT1/~LBO)
/CHARGING: R9.1, U1.7 (STAT2)
/CHARGING_POWER_GOOD: R7.1, U1.6 (~PG)
/PWR_LED: D4.1 (K), R10.2
/USB_DN: J1.A7 (DN1), J1.B7 (DN2); also elsewhere on the board
/USB_DP: J1.A6 (DP1), J1.B6 (DP2); also elsewhere on the board
/VBAT: J2.1, U1.14 (V_{BAT}), U1.15 (V_{BAT}), U1.16 (V_{BAT_SENSE})
/VBUS: C1.1, F1.1, J1.A4 (VBUSA1), J1.A9 (VBUSA2), J1.B4 (VBUSB1), J1.B9 (VBUSB2); also elsewhere on the board
unnamed: D1.1 (K), R7.2
unnamed: D2.1 (K), R8.2
unnamed: D3.1 (K), R9.2
unnamed: FB1.2, U1.1 (OUT), U1.20 (OUT)
unnamed: J1.A5 (CC1), R4.1
unnamed: J1.B5 (CC2), R3.1
unnamed: R5.1, U1.13 (PROG1)
unnamed: R6.1, U1.12 (PROG3)
unnamed: R2.1, U1.5 (THERM)
unnamed: R1.1, U1.9 (~TE)

Notes on the sheet:
USB-C connector
LiPo battery charger
Power indicator LED
Low dropout (LDO) voltage regulator
Battery JST connector
The CP2102 module does not require the USB 3.x TX+/TX- and RX+/RX- pins, as it only supports USB 2.0 communication via D+ and D-.
See ESP32 S3 Dev Kit reference design: https://txplo.re/esp32s3ref
The SBU1 and SBU2 pins on a USB-C connector are Sideband Use (SBU) pins. They are part of the USB-C standard and serve specialized roles depending on the application, primarily in Alternate Modes (e.g., DisplayPort, Thunderbolt) and certain USB-C accessories. For basic USB 2.0/3.0 operation (like i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
USB-C allows for reversible cable insertion. Both pairs of data pins (DP1/DN1 and DP2/DN2) are electrically identical but physically flipped depending on the cable orientation.

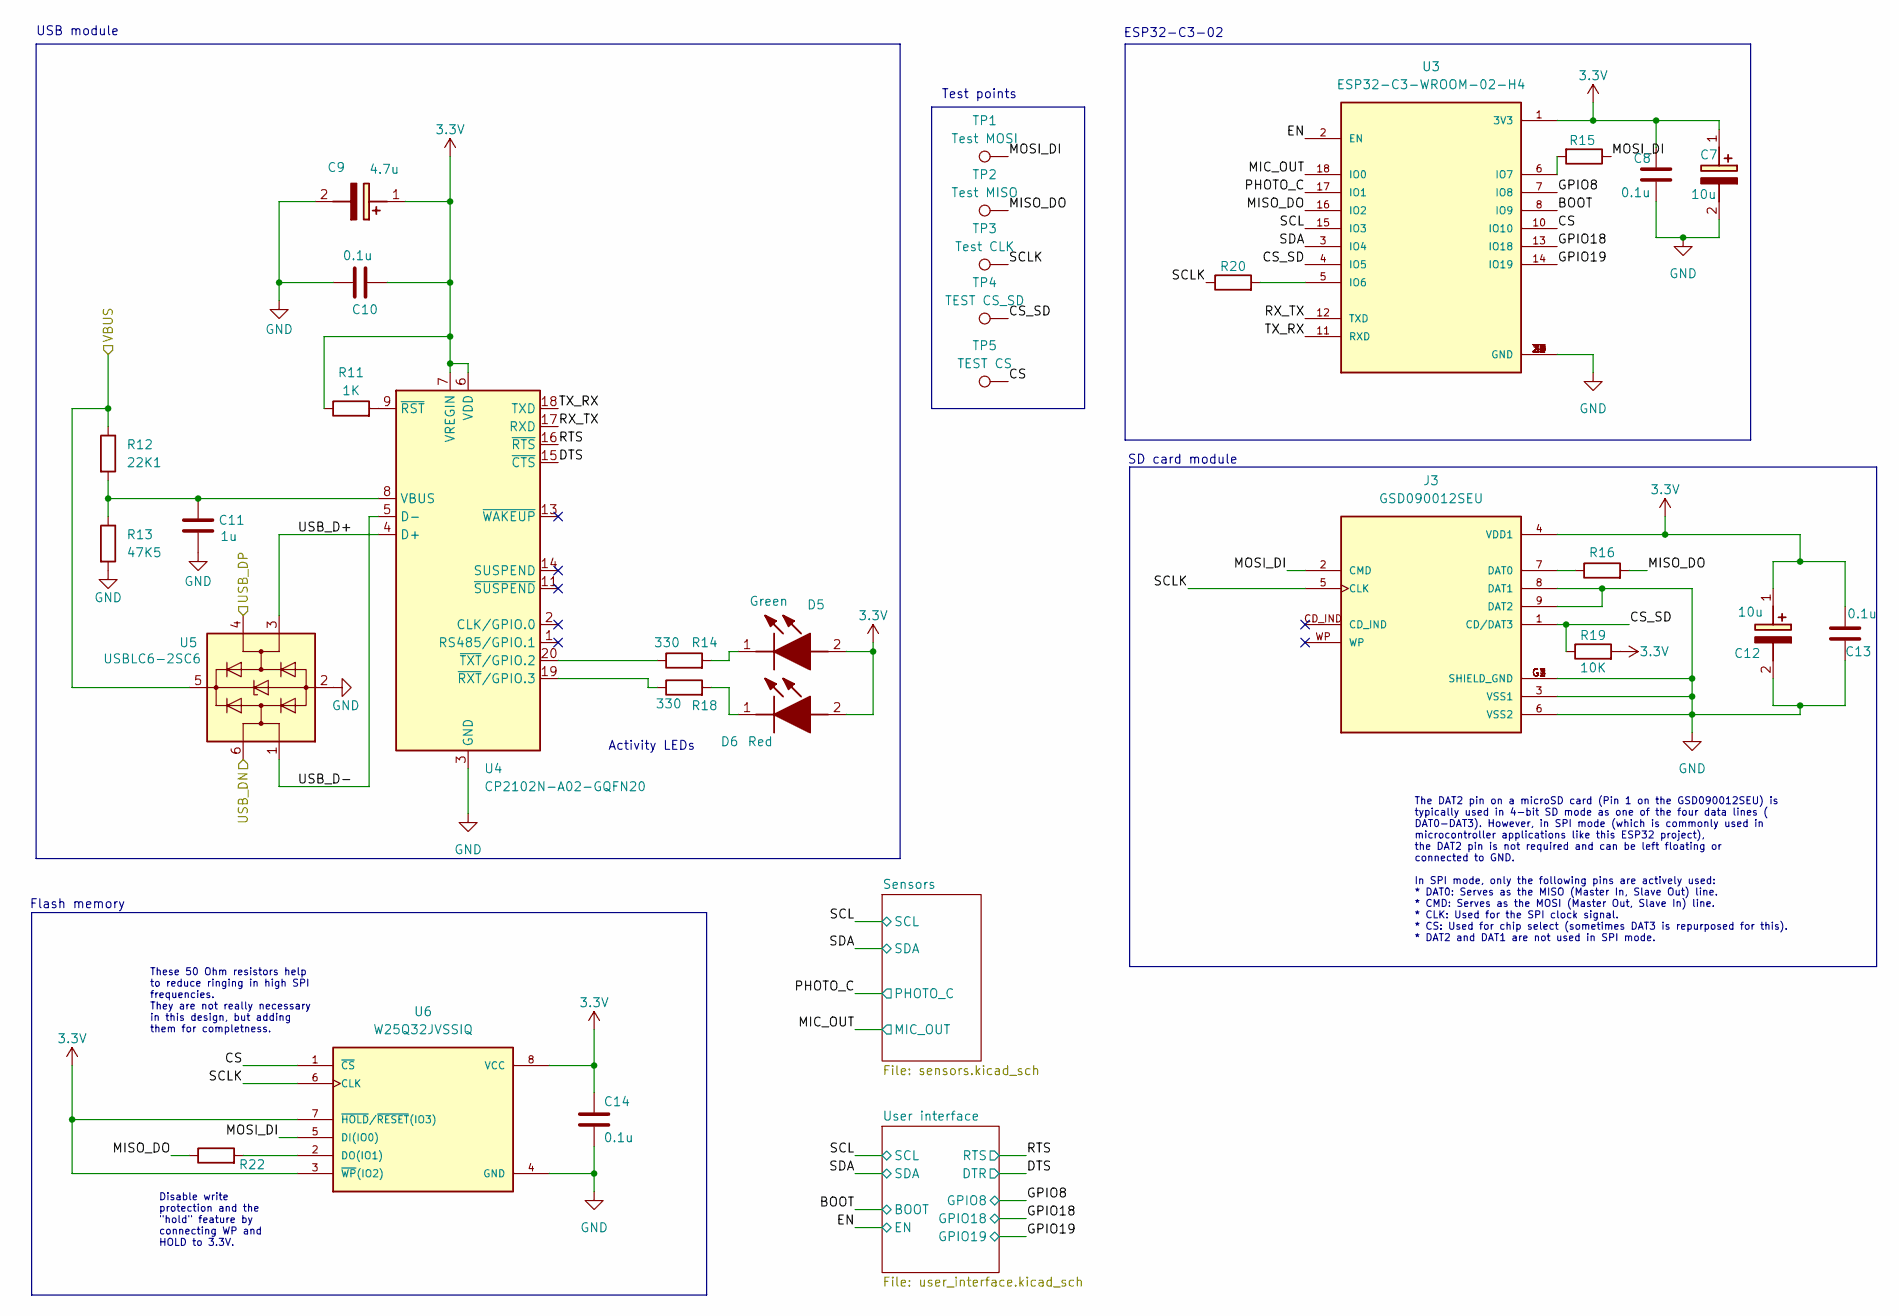
[picture p501: schematic ESP32-C3-02.kicad_sch, ESP32 C3 02 and USB to UART converter]

Parts:
C7, C12: 10u; T491A; Voltage 1kV; Tolerance 100%; Manufacturer_Part_Number T491A106K010AT7280; Mouser Part Number 80-T491A106K107280
C8, C10, C13, C14: 0.1u; C_0805_2012Metric; Voltage 1kV; Tolerance 100%
C9: 4.7u; T491A; Voltage 1kV; Tolerance 100%; Manufacturer_Part_Number T491A106K010AT7280; Mouser Part Number 80-T491A106K107280
C11: 1u; C_0805_2012Metric; Voltage 1kV; Tolerance 100%
D5: Green; LEDC2012X120N; Manufacturer_Part_Number LTST-C170GKT; Mouser Part Number 859-LTST-C170GKT
D6: Red; LEDC2012X120N; Manufacturer_Part_Number LTST-C170KRKT; Mouser Part Number 859-LTST-C170KRKT
J3: GSD090012SEU; AMPHENOL_GSD090012SEU; PARTREV E
R11: 1K; R_0805_2012Metric
R12: 22K1; R_0805_2012Metric
R13: 47K5; R_0805_2012Metric
R14, R18: 330; R_0805_2012Metric
R15, R16, R20, R22: 50; R_0805_2012Metric
R19: 10K; R_0805_2012Metric
TP1: Test MOSI; TestPoint_Pad_D1.0mm
TP2: Test MISO; TestPoint_Pad_D1.0mm
TP3: Test CLK; TestPoint_Pad_D1.0mm
TP4: TEST CS_SD; TestPoint_Pad_D1.0mm
TP5: TEST CS; TestPoint_Pad_D1.0mm
U3: ESP32-C3-WROOM-02-H4; MODULE_ESP32-C3-WROOM-02-H4; Manufacturer_Part_Number ESP32-C3-WROOM-02-H4
U4: CP2102N-A02-GQFN20; SiliconLabs_QFN-20-1EP_3x3mm_P0.5mm_EP1.8x1.8mm; Manufacturer_Part_Number CP2102N-A02-GQFN20
U5: USBLC6-2SC6; SOT-23-6; Manufacturer_Part_Number USBLC6-2SC6; Mouser Part Number 511-USBLC6-2SC6
U6: W25Q32JVSSIQ; SOIC127P790X216-8N; M_PART_NUMBER W25QXX

Connections:
3.3V: C7.1 (+), C8.1, C9.1 (+), C10.1, C12.1 (+), C13.2, C14.1, D5.2 (A), D6.2 (A), J3.4 (VDD1), R11.1, R19.2, U3.1 (3V3), U4.6 (VDD), U4.7 (VREGIN), U6.3 (~WP(IO2)), U6.7 (~HOLD/~RESET(IO3)), U6.8 (VCC); also elsewhere on the board
/ESP32-C3-02/CS: TP5.1, U3.10 (IO10), U6.1 (~CS)
/ESP32-C3-02/CS_SD: J3.1 (CD/DAT3), R19.1, TP4.1, U3.4 (IO5)
/ESP32-C3-02/DTS: U4.15 (~CTS); also elsewhere on the board
/ESP32-C3-02/GPIO8: U3.7 (IO8); also elsewhere on the board
/ESP32-C3-02/GPIO18: U3.13 (IO18); also elsewhere on the board
/ESP32-C3-02/GPIO19: U3.14 (IO19); also elsewhere on the board
/ESP32-C3-02/MIC_OUT: U3.18 (IO0); also elsewhere on the board
/ESP32-C3-02/MISO_DO: R16.2, R22.1, TP2.1, U3.16 (IO2)
/ESP32-C3-02/MOSI_DI: J3.2 (CMD), R15.1, TP1.1, U6.5 (DI(IO0))
/ESP32-C3-02/PHOTO_C: U3.17 (IO1); also elsewhere on the board
/ESP32-C3-02/RTS: U4.16 (~RTS); also elsewhere on the board
/ESP32-C3-02/RX_TX: U3.12 (TXD), U4.17 (RXD)
/ESP32-C3-02/SCL: U3.15 (IO3); also elsewhere on the board
/ESP32-C3-02/SCLK: J3.5 (CLK), R20.1, TP3.1, U6.6 (CLK)
/ESP32-C3-02/SDA: U3.3 (IO4); also elsewhere on the board
/ESP32-C3-02/TX_RX: U3.11 (RXD), U4.18 (TXD)
/ESP32-C3-02/USB_D+: U4.4 (D+), U5.3 (I/O2)
/ESP32-C3-02/USB_D-: U4.5 (D-), U5.1 (I/O1)
/USB_DN: U5.6 (I/O1); also elsewhere on the board
/USB_DP: U5.4 (I/O2); also elsewhere on the board
/VBUS: R12.1, U5.5 (VBUS); also elsewhere on the board
unnamed: D5.1 (K), R14.2
unnamed: D6.1 (K), R18.2
unnamed: J3.7 (DAT0), R16.1
unnamed: R20.2, U3.5 (IO6)
unnamed: R15.2, U3.6 (IO7)
unnamed: C11.1, R12.2, R13.1, U4.8 (VBUS)
unnamed: R11.2, U4.9 (~RST)
unnamed: R18.1, U4.19 (~RXT/GPIO.3)
unnamed: R14.1, U4.20 (~TXT/GPIO.2)
unnamed: R22.2, U6.2 (DO(IO1))

Notes on the sheet:
SD card module
Activity LEDs
Flash memory
USB module
Test points
ESP32-C3-02
Disable write protection and the "hold" feature by connecting WP and HOLD to 3.3V.
The DAT2 pin on a microSD card (Pin 1 on the GSD090012SEU) is typically used in 4-bit SD mode as one of the four data lines ( DAT0-DAT3). However, in SPI mode (which is commonly used in microcontroller applications like this ESP32 project), the DAT2 pin is not required and can be left floating or c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
These 50 Ohm resistors help to reduce ringing in high SPI frequencies. They are not really necessary in this design, but adding them for completness.

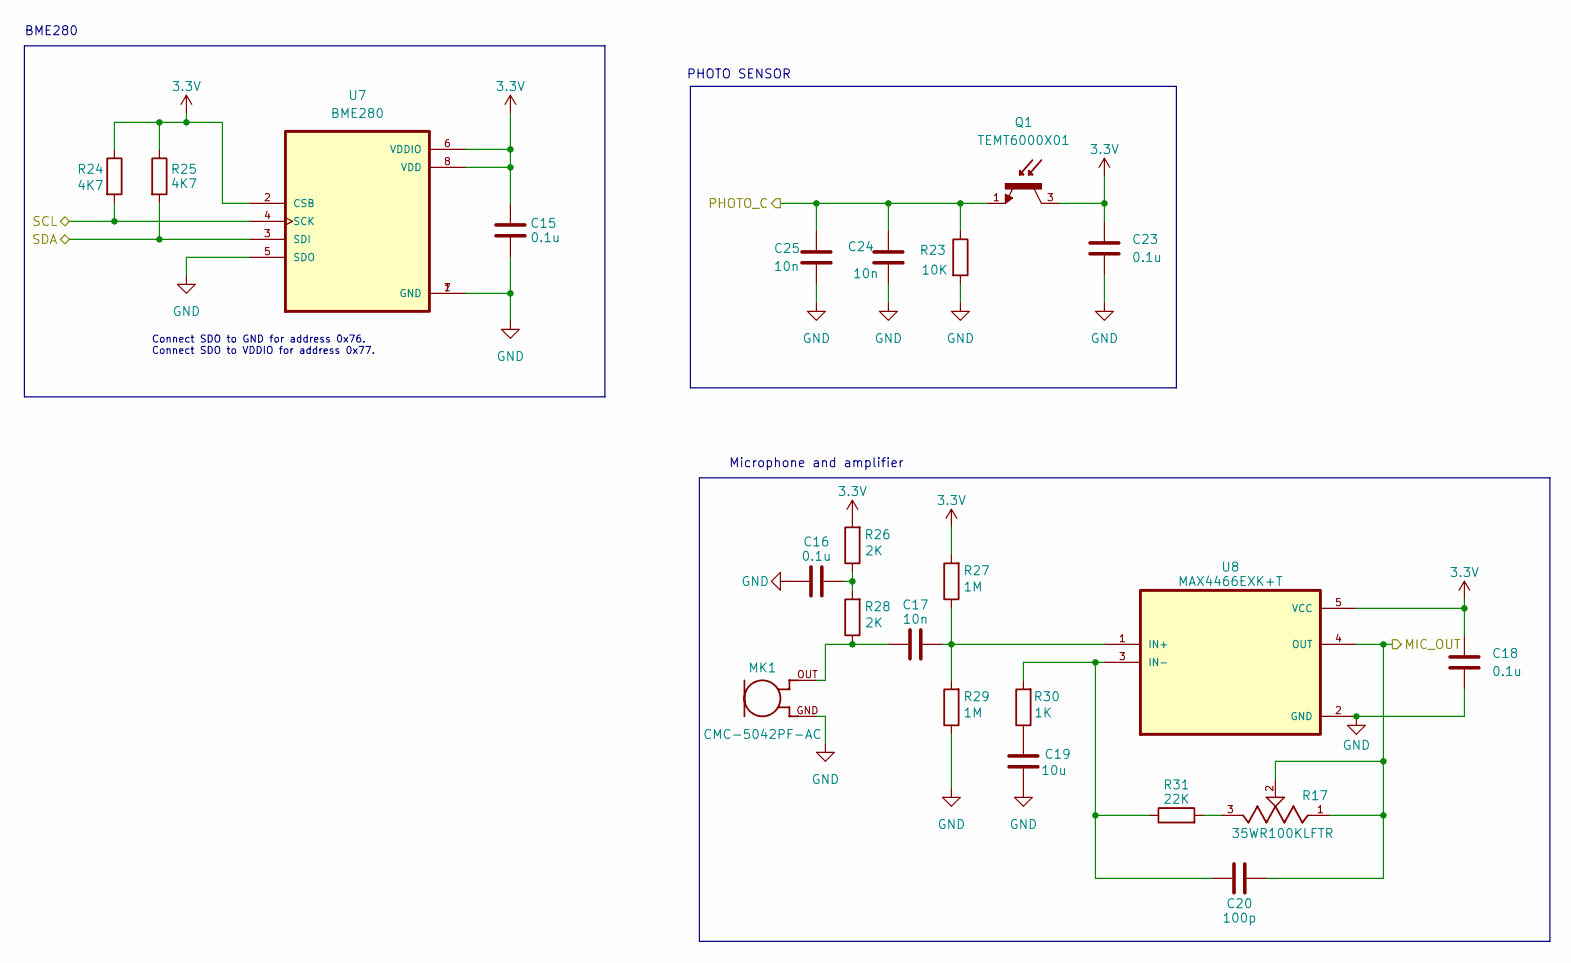
[picture p502: schematic sensors.kicad_sch]

Parts:
C15: 0.1u; C_0805_2012Metric; Voltage 1kV; Tolerance 100%
C16, C18, C23: 0.1u; C_0805_2012Metric
C17, C24, C25: 10n; C_0805_2012Metric
C19: 10u; C_0805_2012Metric
C20: 100p; C_0805_2012Metric
MK1: CMC-5042PF-AC; CUI_CMC-5042PF-AC; Manufacturer_Part_Number CMC-5042PF-AC
Q1: TEMT6000X01; TRANS_TEMT6000X01; PARTREV 1.9
R17: 35WR100KLFTR; TRIM_35WR100KLFTR; PARTREV D
R23: 10K; R_0805_2012Metric
R24, R25: 4K7; R_0805_2012Metric
R26, R28: 2K; R_0805_2012Metric
R27, R29: 1M; R_0805_2012Metric
R30: 1K; R_0805_2012Metric
R31: 22K; R_0805_2012Metric
U7: BME280; PSON65P250X250X100-8N; Manufacturer_Part_Number BME280
U8: MAX4466EXK+T; SOT65P210X110-5N; Manufacturer_Part_Number MAX4466EXK+T

Connections:
3.3V: C15.2, C18.1, C23.1, Q1.3, R24.1, R25.1, R26.2, R27.2, U7.2 (CSB), U7.6 (VDDIO), U7.8 (VDD), U8.5 (VCC); also elsewhere on the board
/ESP32-C3-02/MIC_OUT: C20.2, R17.1, R17.2, U8.4 (OUT); also elsewhere on the board
/ESP32-C3-02/PHOTO_C: C24.1, C25.1, Q1.1, R23.1; also elsewhere on the board
/ESP32-C3-02/SCL: R24.2, U7.4 (SCK); also elsewhere on the board
/ESP32-C3-02/SDA: R25.2, U7.3 (SDI); also elsewhere on the board
unnamed: C16.1, R26.1, R28.2
unnamed: C17.2, MK1.OUT, R28.1
unnamed: C19.2, R30.1
unnamed: R17.3, R31.2
unnamed: C17.1, R27.1, R29.2, U8.1 (IN+)
unnamed: C20.1, R30.2, R31.1, U8.3 (IN-)

Notes on the sheet:
PHOTO SENSOR
Microphone and amplifier
BME280
Connect SDO to GND for address 0x76. Connect SDO to VDDIO for address 0x77.

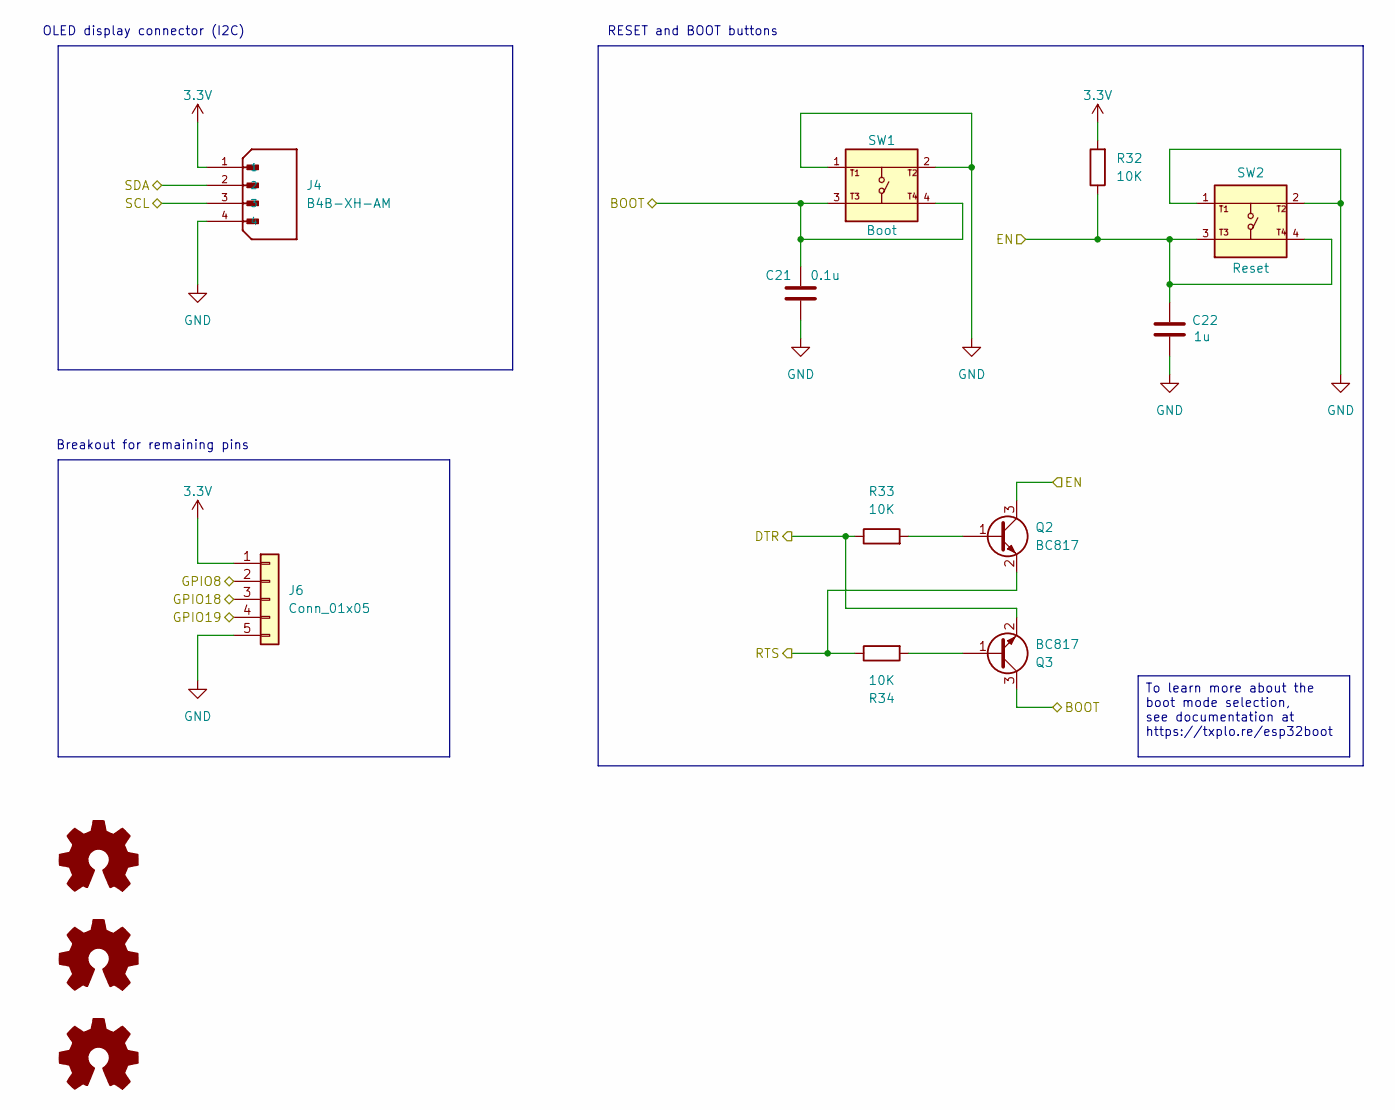
[picture p503: schematic user_interface.kicad_sch]

Parts:
C21: 0.1u; C_0805_2012Metric; Voltage 1kV; Tolerance 100%
C22: 1u; C_0805_2012Metric; Voltage 1kV; Tolerance 100%
J4: B4B-XH-AM; JST_B4B-XH-AM__LF__SN_; PARTREV N/A
J6: Conn_01x05; PinHeader_1x05_P2.54mm_Vertical
Q2, Q3: BC817; SOT-23; Manufacturer_Part_Number BC817
R32, R33, R34: 10K; R_0805_2012Metric
SW1, SW2: 1101NE; SW_USLPT2819DT2TR; Mfg Part# 8-004 SMD Button 8x3.6mm Height=2.5mm

Connections:
3.3V: J4.1, J6.1, R32.2; also elsewhere on the board
/ESP32-C3-02/DTS: Q3.2 (E), R33.1; also elsewhere on the board
/ESP32-C3-02/GPIO8: J6.2; also elsewhere on the board
/ESP32-C3-02/GPIO18: J6.3; also elsewhere on the board
/ESP32-C3-02/GPIO19: J6.4; also elsewhere on the board
/ESP32-C3-02/RTS: Q2.2 (E), R34.1; also elsewhere on the board
/ESP32-C3-02/SCL: J4.3; also elsewhere on the board
/ESP32-C3-02/SDA: J4.2; also elsewhere on the board
unnamed: Q2.1 (B), R33.2
unnamed: Q3.1 (B), R34.2

Notes on the sheet:
OLED display connector (I2C)
RESET and BOOT buttons
Breakout for remaining pins
To learn more about the boot mode selection, see documentation at https://txplo.re/esp32boot

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
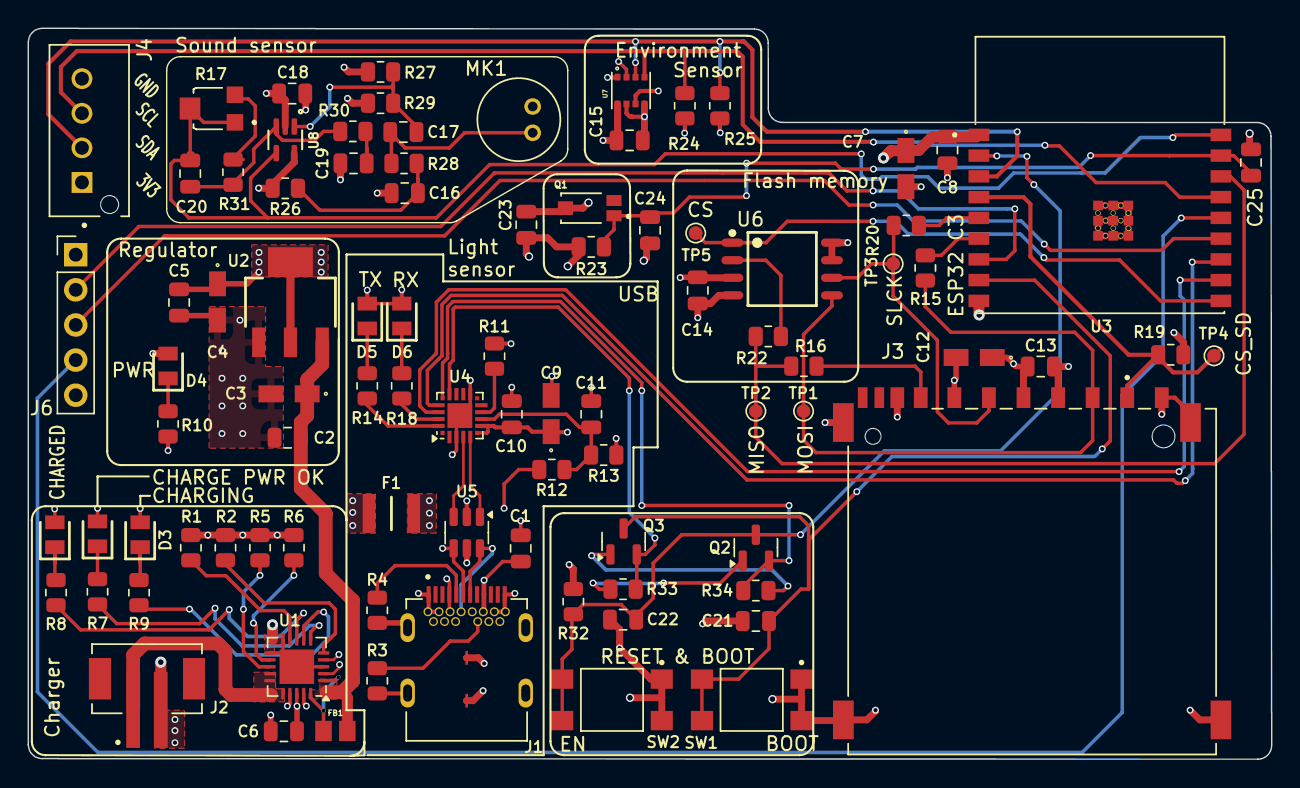
[picture p504: board ESP32 sensor board.kicad_pcb from above]

Board: 4 copper layers, 89.9 x 52.8 mm, 90 parts (0 on the bottom side), 60 nets.
