rompasaurus/regardedPal/hardware-design/examples/07-whirlingbits-s3-platform/ESP_S3-CP-24_Platform.kicad_pcb

## KiCad design hardware-design/examples/07-whirlingbits-s3-platform/ESP_S3-CP-24_Platform.kicad_pcb (2026-04-15)

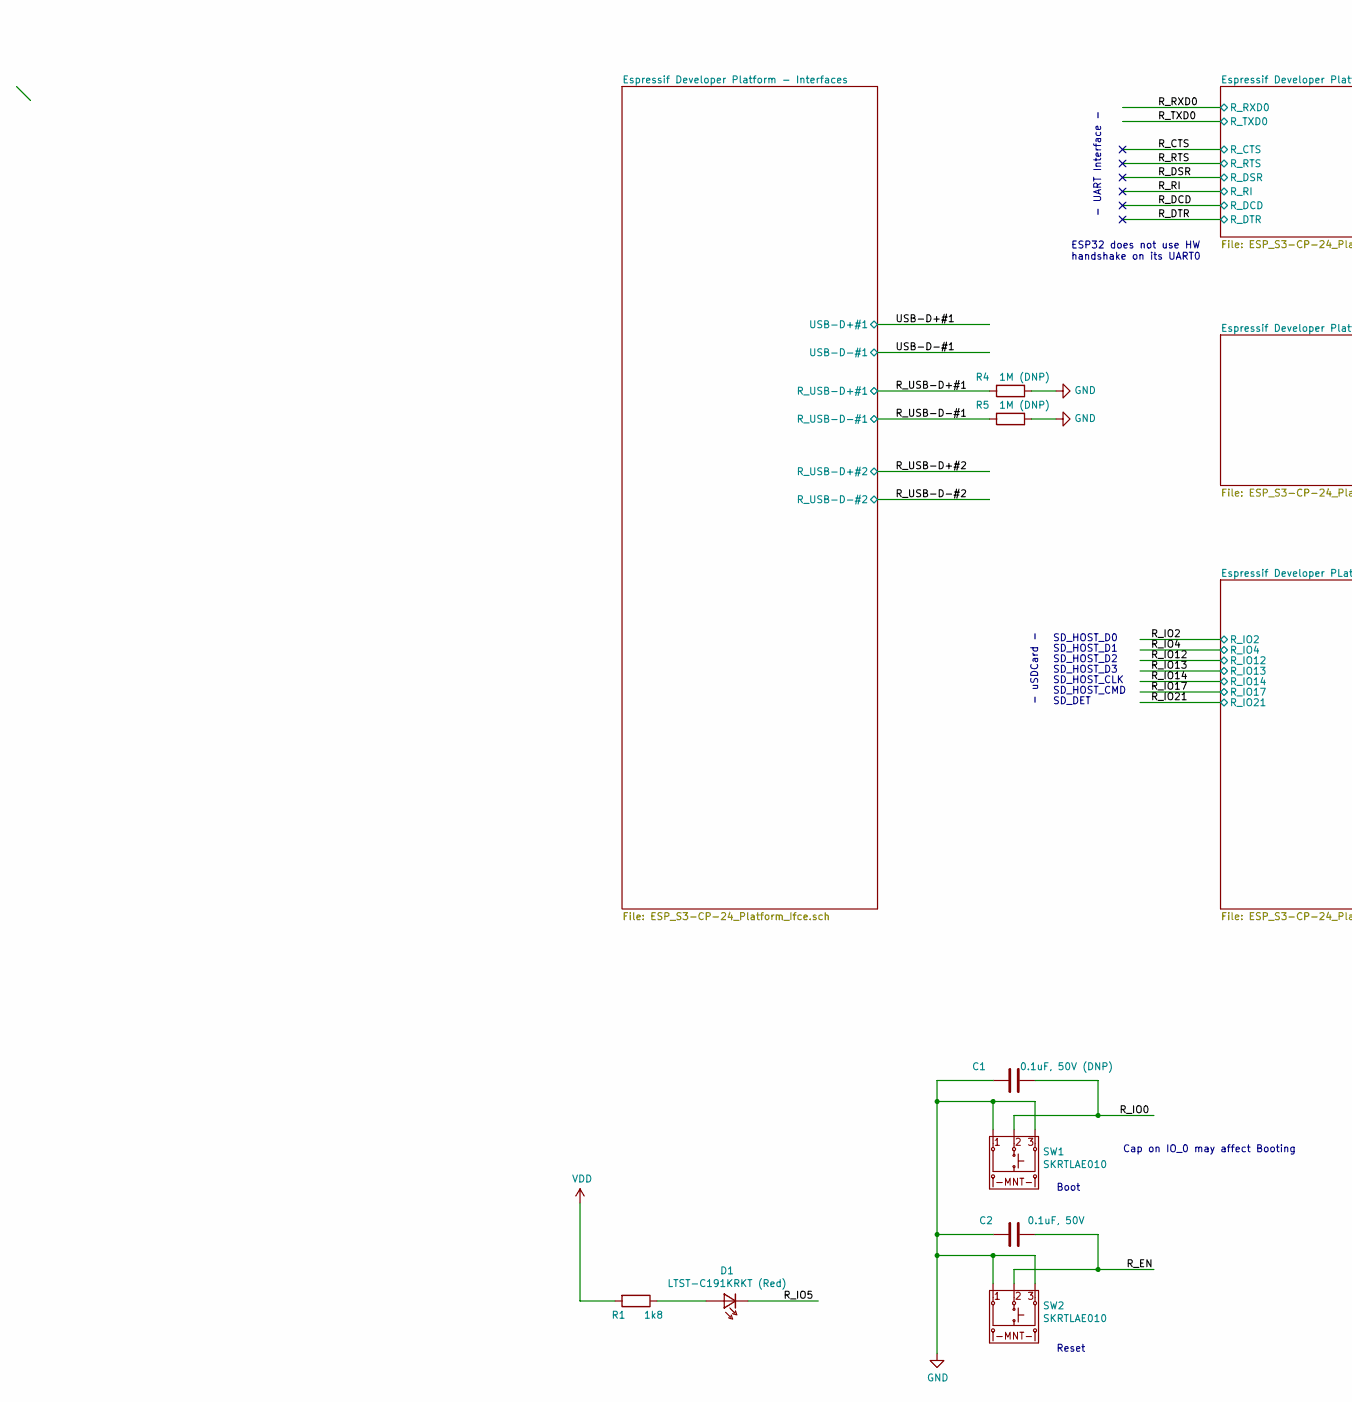
[picture p505: schematic ESP_S3-CP-24_Platform.sch, Espressif ESP32_S3-CP-24 Developer Platform - Overview, part in row 1, column 1]

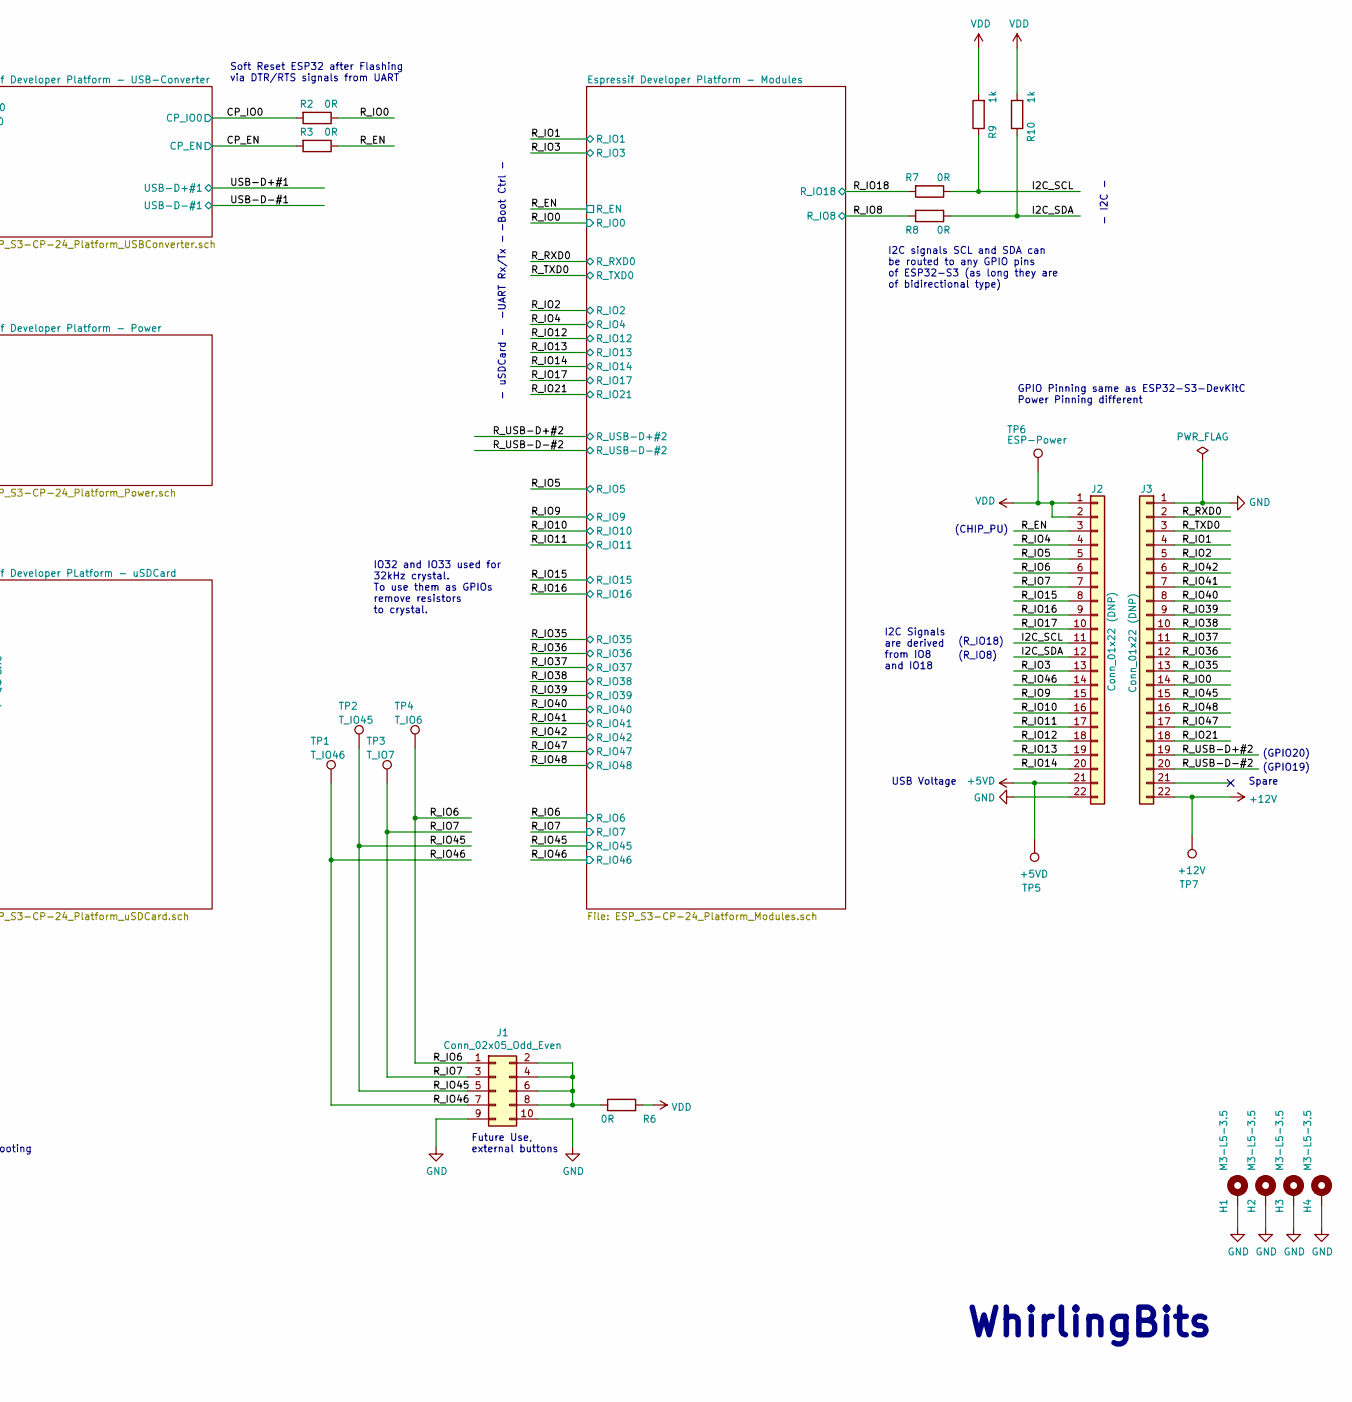
[picture p506: schematic ESP_S3-CP-24_Platform.sch, Espressif ESP32_S3-CP-24 Developer Platform - Overview, part in row 1, column 2]

Parts:
C1: 0.1uF, 50V (DNP); C_0805_2012Metric; LCSC C161260
C2: 0.1uF, 50V; C_0805_2012Metric; LCSC C161260
D1: LTST-C191KRKT (Red); LED_0603_1608Metric; LCSC C125099
H1, H2, H3, H4: M3-L5-3.5; MountingHole_3.2mm_M3_Pad_Via
J1: Conn_02x05_Odd_Even; PinHeader_2x05_P1.27mm_Vertical_SMD; LCSC C150517
J2, J3: Conn_01x22 (DNP); PinHeader_1x22_P2.54mm_Vertical; LCSC C725954
R1: 1k8; R_0805_2012Metric; LCSC C137465
R2, R3, R6: 0R; R_0805_2012Metric
R4, R5: 1M (DNP); R_0805_2012Metric
R7, R8: 0R; R_0805_2012Metric; LCSC C100045
R9, R10: 1k; R_0805_2012Metric; LCSC C95781
SW1, SW2: SKRTLAE010; SW_Push_1P1T-MP_NO_Horizontal_Alps_SKRTLAE010; LCSC C110293
TP1: T_IO46; TestPoint_Pad_2.0x2.0mm
TP2: T_IO45; TestPoint_Pad_2.0x2.0mm
TP3: T_IO7; TestPoint_Pad_2.0x2.0mm
TP4: T_IO6; TestPoint_Pad_2.0x2.0mm
TP5: +5VD; TestPoint_Pad_2.0x2.0mm
TP6: ESP-Power; TestPoint_Pad_2.0x2.0mm
TP7: +12V; TestPoint_Pad_2.0x2.0mm

Connections:
+5VD: J2.21, TP5.1; also elsewhere on the board
+12V: J3.22, TP7.1; also elsewhere on the board
/CP_EN: R3.2; also elsewhere on the board
/CP_IO0: R2.2; also elsewhere on the board
/I2C_SCL: J2.11, R7.1, R9.1
/I2C_SDA: J2.12, R8.1, R10.1
/R_EN: C2.1, J2.3, R3.1, SW2.2; also elsewhere on the board
/R_IO0: C1.1, J3.14, R2.1, SW1.2; also elsewhere on the board
/R_IO1: J3.4; also elsewhere on the board
/R_IO2: J3.5; also elsewhere on the board
/R_IO3: J2.13; also elsewhere on the board
/R_IO4: J2.4; also elsewhere on the board
/R_IO5: D1.1, J2.5; also elsewhere on the board
/R_IO6: J1.1, J2.6, TP4.1; also elsewhere on the board
/R_IO7: J1.3, J2.7, TP3.1; also elsewhere on the board
/R_IO8: R8.2; also elsewhere on the board
/R_IO9: J2.15; also elsewhere on the board
/R_IO10: J2.16; also elsewhere on the board
/R_IO11: J2.17; also elsewhere on the board
/R_IO12: J2.18; also elsewhere on the board
/R_IO13: J2.19; also elsewhere on the board
/R_IO14: J2.20; also elsewhere on the board
/R_IO15: J2.8; also elsewhere on the board
/R_IO16: J2.9; also elsewhere on the board
/R_IO17: J2.10; also elsewhere on the board
/R_IO18: R7.2; also elsewhere on the board
/R_IO21: J3.18; also elsewhere on the board
/R_IO35: J3.13; also elsewhere on the board
/R_IO36: J3.12; also elsewhere on the board
/R_IO37: J3.11; also elsewhere on the board
/R_IO38: J3.10; also elsewhere on the board
/R_IO39: J3.9; also elsewhere on the board
/R_IO40: J3.8; also elsewhere on the board
/R_IO41: J3.7; also elsewhere on the board
/R_IO42: J3.6; also elsewhere on the board
/R_IO45: J1.5, J3.15, TP2.1; also elsewhere on the board
/R_IO46: J1.7, J2.14, TP1.1; also elsewhere on the board
/R_IO47: J3.17; also elsewhere on the board
/R_IO48: J3.16; also elsewhere on the board
/R_RXD0: J3.2; also elsewhere on the board
/R_TXD0: J3.3; also elsewhere on the board
/R_USB-D+#1: R4.2; also elsewhere on the board
/R_USB-D+#2: J3.19; also elsewhere on the board
/R_USB-D-#1: R5.2; also elsewhere on the board
/R_USB-D-#2: J3.20; also elsewhere on the board
GND: C1.2, C2.2, H1.1, H2.1, H3.1, H4.1, J1.9, J1.10, J2.22, J3.1, R4.1, R5.1, SW1.1, SW1.3, SW2.1, SW2.3; also elsewhere on the board
unnamed: D1.2, R1.1
unnamed: J1.2, J1.4, J1.6, J1.8, R6.1
VDD: J2.1, J2.2, R1.2, R6.2, R9.2, R10.2, TP6.1; also elsewhere on the board

Notes on the sheet:
I2C signals SCL and SDA can be routed to any GPIO pins of ESP32-S3 (as long they are of bidirectional type)
- I2C -
-Boot Ctrl -
- UART Interface -
ESP32 does not use HW handshake on its UART0
-UART Rx/Tx -
Reset
Boot
Cap on IO_0 may affect Booting
Future Use, external buttons
- uSDCard -
Soft Reset ESP32 after Flashing via DTR/RTS signals from UART
USB Voltage
I2C Signals are derived from IO8 and IO18
IO32 and IO33 used for 32kHz crystal. To use them as GPIOs remove resistors to crystal.
SD_HOST_D0
SD_HOST_D1
SD_HOST_D2
SD_HOST_D3
SD_HOST_CLK
SD_HOST_CMD
SD_DET
(R_IO18)
(R_IO8)
(CHIP_PU)
GPIO Pinning same as ESP32-S3-DevKitC Power Pinning different
Spare
(GPIO20)
(GPIO19)
WhirlingBits

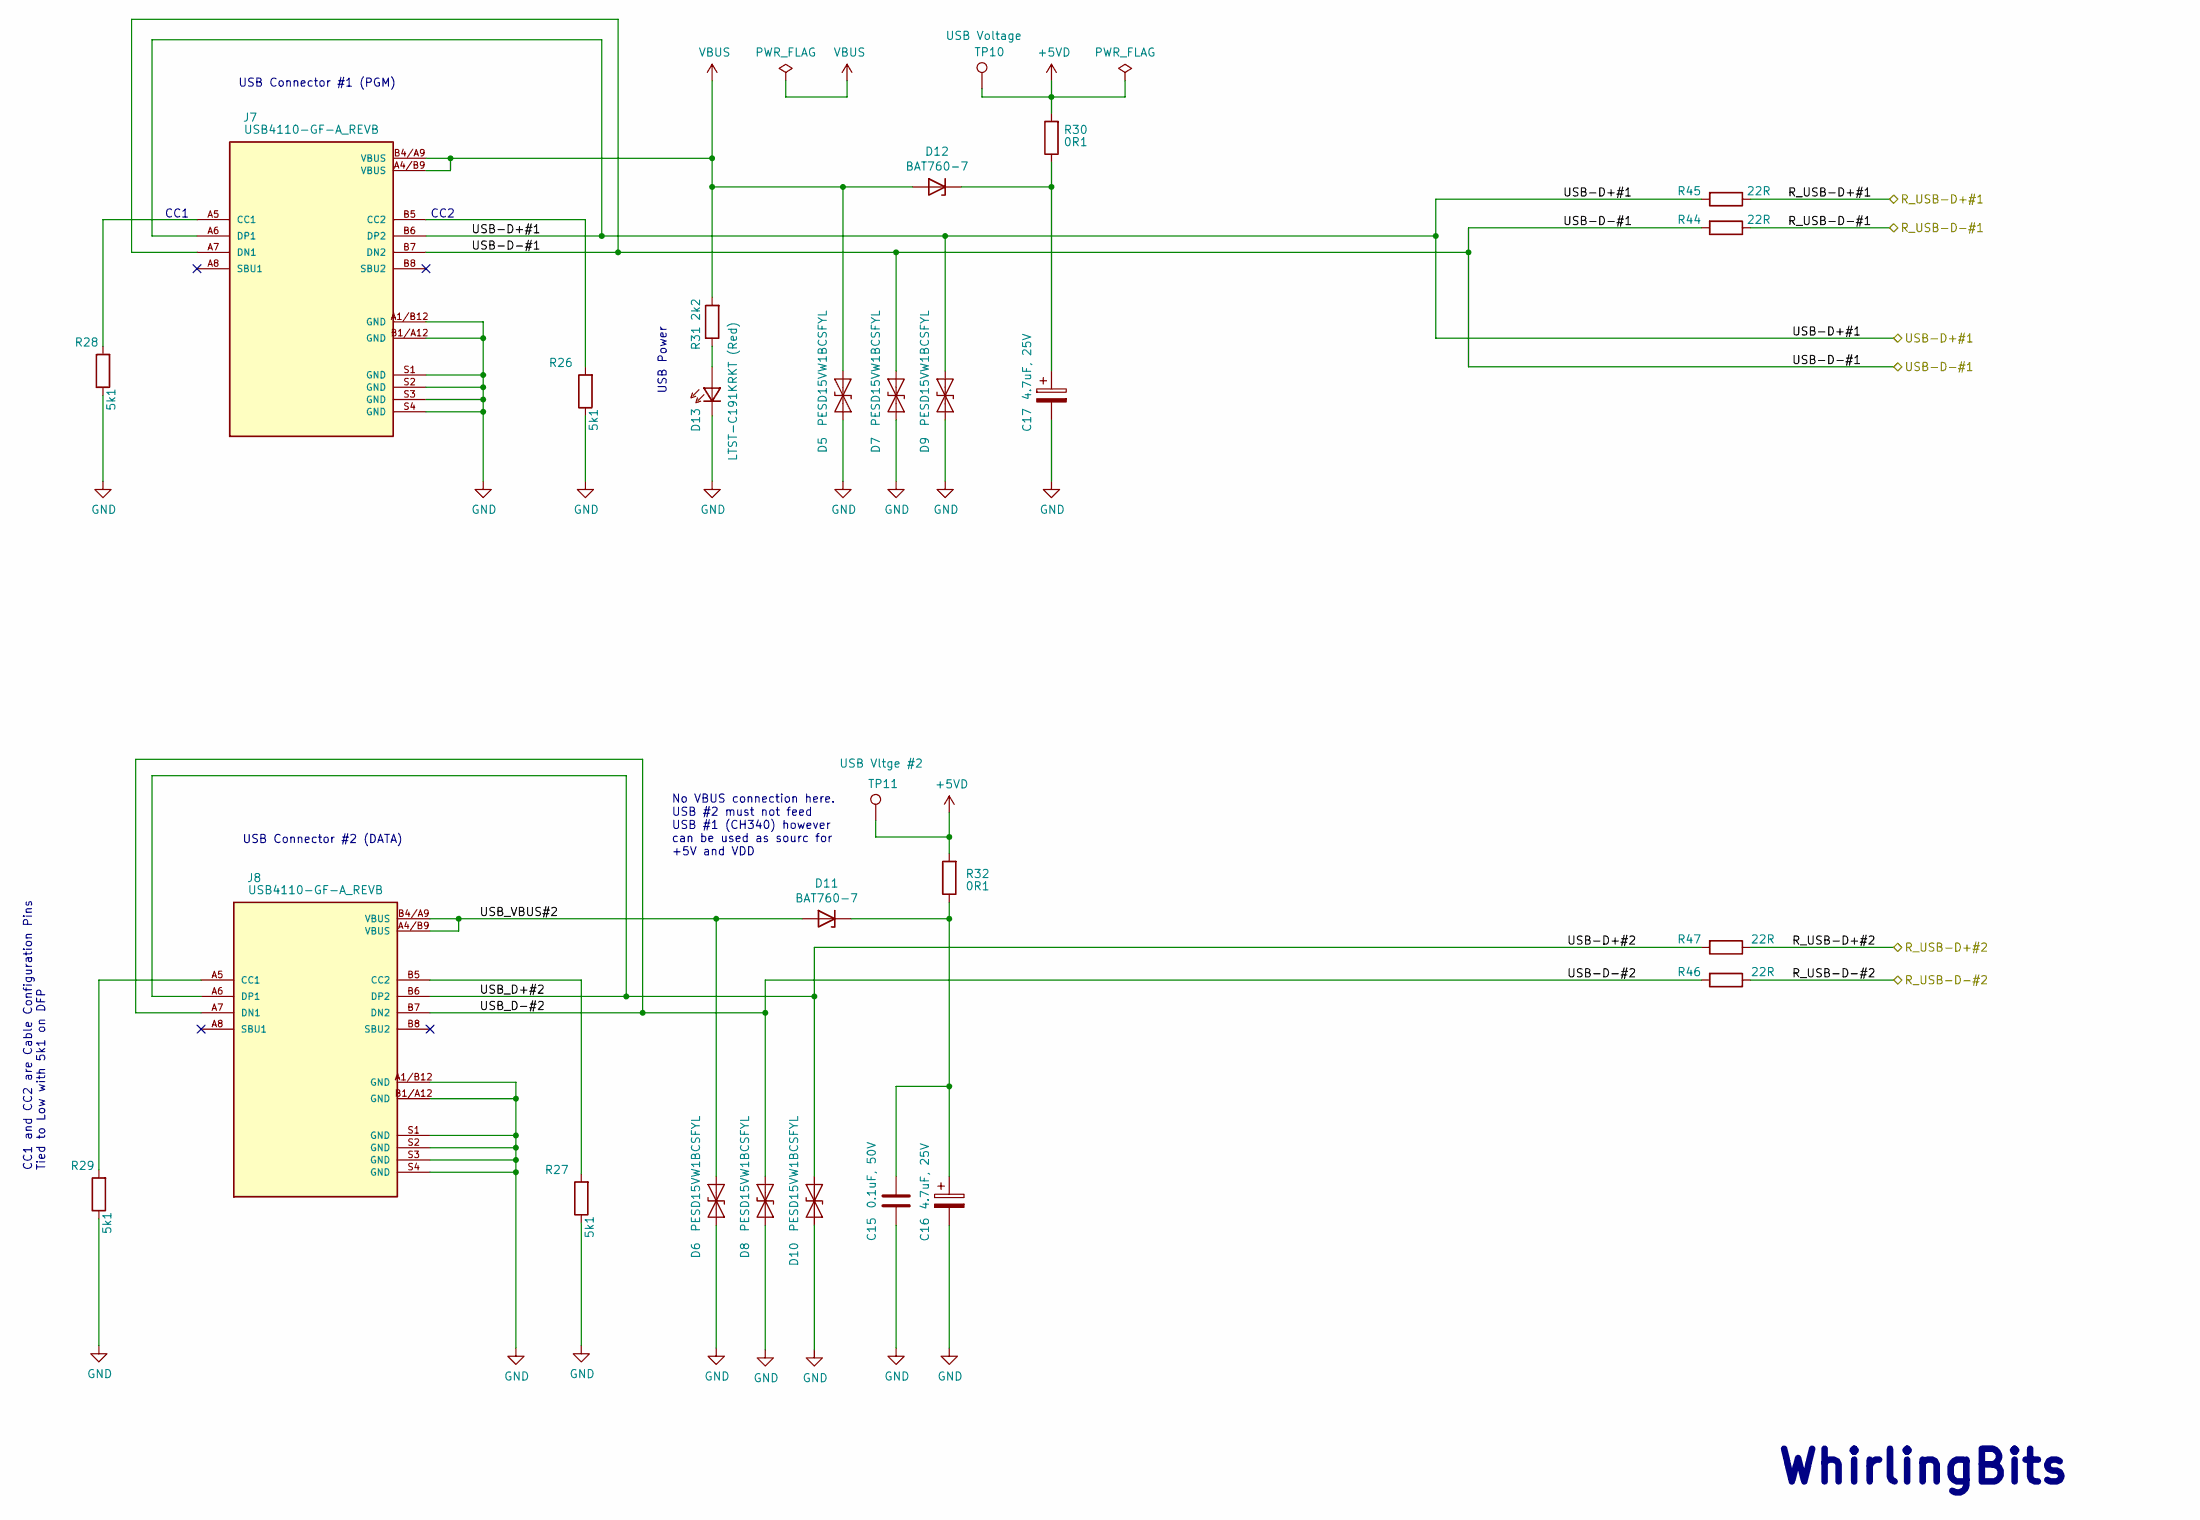
[picture p507: schematic ESP_S3-CP-24_Platform_Ifce.sch, Espressif ESP32_S3-CP-24 Developer Platform - Overview]

Parts:
C15: 0.1uF, 50V; C_0805_2012Metric; LCSC C161260
C16, C17: 4.7uF, 25V; C_0805_2012Metric; LCSC C98192
D5, D6, D7, D8, D9, D10: PESD15VW1BCSFYL; D_SOD-523; Mouser Part Number 771-PESD15VW1BCSFYL; Mouser 771-PESD15VW1BCSFYL
D11, D12: BAT760-7; D_SOD-323; LCSC C116158
D13: LTST-C191KRKT (Red); LED_0603_1608Metric; LCSC C125099
J7, J8: USB4110-GF-A_REVB; GCT_USB4110-GF-A_REVB; PARTREV B; Mouser 640-USB4110-GF-A
R26, R27, R28, R29: 5k1; R_0805_2012Metric; LCSC C204548
R30, R32: 0R1; R_1210_3225Metric; LCSC C473589
R31: 2k2; R_0805_2012Metric; LCSC C441982
R44, R45, R46, R47: 22R; R_0805_2012Metric; LCSC C144531
TP10: USB Voltage; TestPoint_Pad_2.0x2.0mm
TP11: USB Vltge #2; TestPoint_Pad_2.0x2.0mm

Connections:
+5VD: R30.2, R32.2, TP10.1, TP11.1; also elsewhere on the board
/Espressif Developer Platform - Interfaces/USB-D+#2: D10.1 (A1), J8.A6 (DP1), J8.B6 (DP2), R47.2
/Espressif Developer Platform - Interfaces/USB-D-#2: D8.1 (A1), J8.A7 (DN1), J8.B7 (DN2), R46.2
/Espressif Developer Platform - Interfaces/USB_VBUS#2: D6.1 (A1), D11.2 (A), J8.A4/B9 (VBUS), J8.B4/A9 (VBUS)
/R_USB-D+#1: R45.1; also elsewhere on the board
/R_USB-D+#2: R47.1; also elsewhere on the board
/R_USB-D-#1: R44.1; also elsewhere on the board
/R_USB-D-#2: R46.1; also elsewhere on the board
/USB-D+#1: D9.1 (A1), J7.A6 (DP1), J7.B6 (DP2), R45.2; also elsewhere on the board
/USB-D-#1: D7.1 (A1), J7.A7 (DN1), J7.B7 (DN2), R44.2; also elsewhere on the board
GND: C15.2, C16.2, C17.2, D5.2 (A2), D6.2 (A2), D7.2 (A2), D8.2 (A2), D9.2 (A2), D10.2 (A2), D13.1, J7.A1/B12 (GND), J7.B1/A12 (GND), J7.S1 (GND), J7.S2 (GND), J7.S3 (GND), J7.S4 (GND), J8.A1/B12 (GND), J8.B1/A12 (GND), J8.S1 (GND), J8.S2 (GND), J8.S3 (GND), J8.S4 (GND), R26.1, R27.1, R28.1, R29.1; also elsewhere on the board
unnamed: C15.1, C16.1, D11.1 (K), R32.1
unnamed: C17.1, D12.1 (K), R30.1
unnamed: D13.2, R31.1
unnamed: J7.A5 (CC1), R28.2
unnamed: J7.B5 (CC2), R26.2
unnamed: J8.A5 (CC1), R29.2
unnamed: J8.B5 (CC2), R27.2
VBUS: D5.1 (A1), D12.2 (A), J7.A4/B9 (VBUS), J7.B4/A9 (VBUS), R31.2; also elsewhere on the board

Notes on the sheet:
USB Connector #1 (PGM)
USB Power
USB Connector #2 (DATA)
No VBUS connection here. USB #2 must not feed USB #1 (CH340) however can be used as sourc for +5V and VDD
CC1 and CC2 are Cable Configuration Pins Tied to Low with 5k1 on DFP
CC1
CC2
WhirlingBits

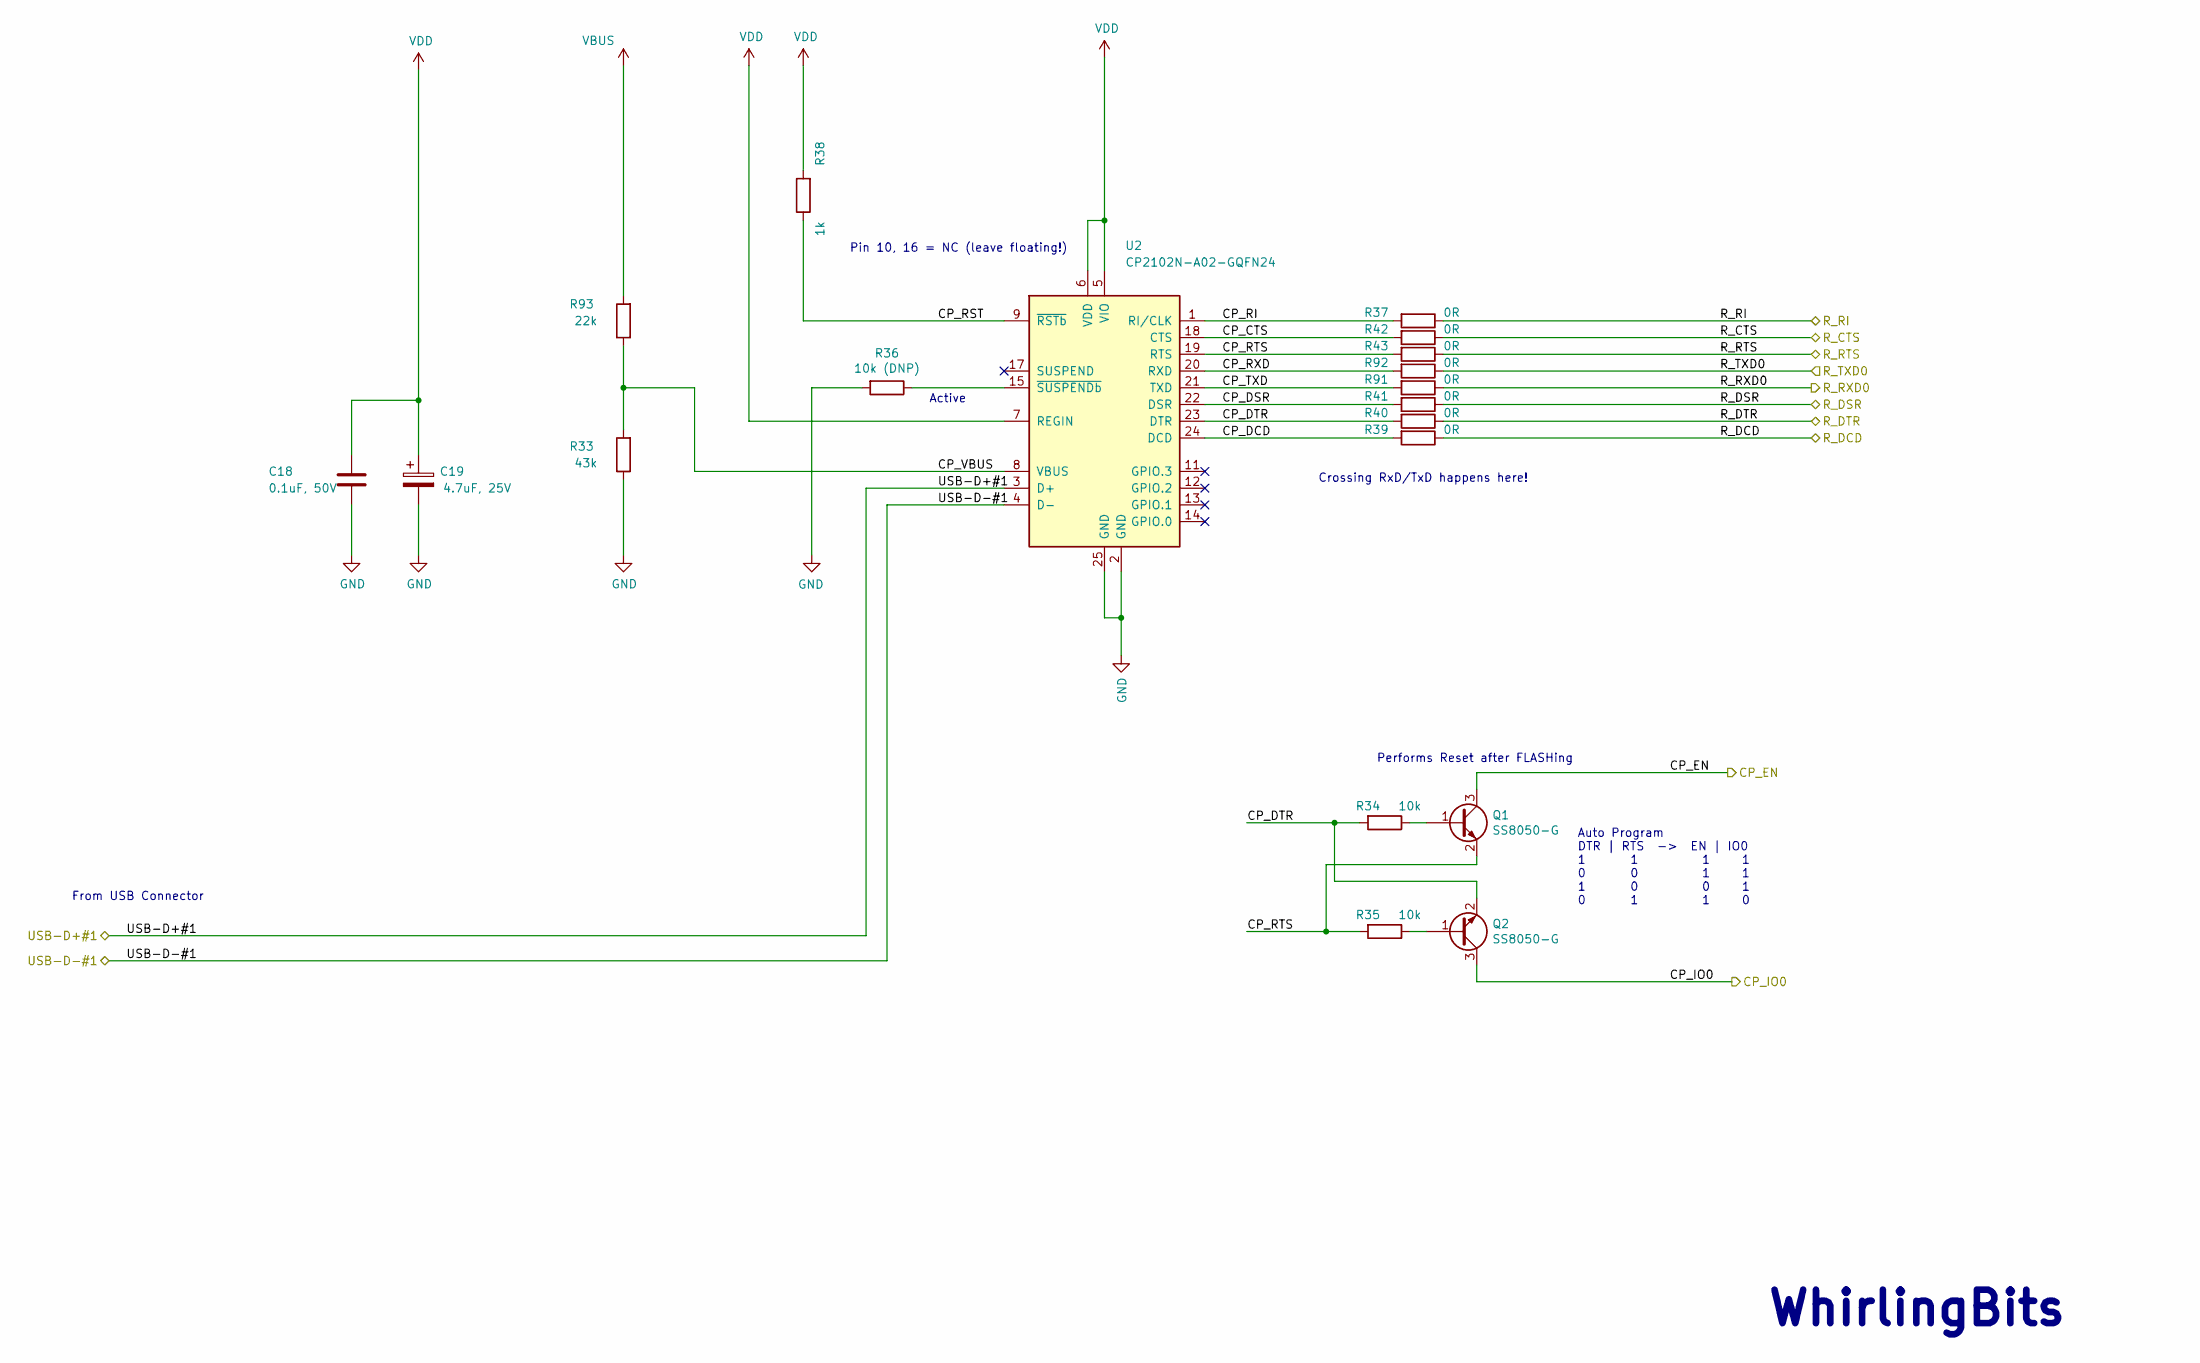
[picture p508: schematic ESP_S3-CP-24_Platform_USBConverter.sch, Espressif ESP32_S3-CP-24 Developer Platform - Overview]

Parts:
C18: 0.1uF, 50V; C_0805_2012Metric; LCSC C161260
C19: 4.7uF, 25V; C_0805_2012Metric; LCSC C98192
Q1, Q2: SS8050-G; SOT-23; LCSC C164885
R33: 43k; R_0805_2012Metric; LCSC C104355
R34, R35: 10k; R_0805_2012Metric; LCSC C169253
R36: 10k (DNP); R_0805_2012Metric
R37, R39, R40, R41, R42, R43, R91, R92: 0R; R_0805_2012Metric
R38: 1k; R_0805_2012Metric
R93: 22k; R_0805_2012Metric; LCSC C104113
U2: CP2102N-A02-GQFN24; QFN-24-1EP_4x4mm_P0.5mm_EP2.6x2.6mm; LCSC C80225

Connections:
/CP_EN: Q1.3 (C); also elsewhere on the board
/CP_IO0: Q2.3 (C); also elsewhere on the board
/Espressif Developer Platform - USB-Converter/CP_CTS: R42.2, U2.18 (CTS)
/Espressif Developer Platform - USB-Converter/CP_DCD: R39.2, U2.24 (DCD)
/Espressif Developer Platform - USB-Converter/CP_DSR: R41.2, U2.22 (DSR)
/Espressif Developer Platform - USB-Converter/CP_DTR: Q2.2 (E), R34.2, R40.2, U2.23 (DTR)
/Espressif Developer Platform - USB-Converter/CP_RI: R37.2, U2.1 (RI/CLK)
/Espressif Developer Platform - USB-Converter/CP_RST: R38.1, U2.9 (~RSTb)
/Espressif Developer Platform - USB-Converter/CP_RTS: Q1.2 (E), R35.2, R43.2, U2.19 (RTS)
/Espressif Developer Platform - USB-Converter/CP_RXD: R92.2, U2.20 (RXD)
/Espressif Developer Platform - USB-Converter/CP_TXD: R91.2, U2.21 (TXD)
/Espressif Developer Platform - USB-Converter/CP_VBUS: R33.2, R93.1, U2.8 (VBUS)
/R_CTS: R42.1
/R_DCD: R39.1
/R_DSR: R41.1
/R_DTR: R40.1
/R_RI: R37.1
/R_RTS: R43.1
/R_RXD0: R91.1; also elsewhere on the board
/R_TXD0: R92.1; also elsewhere on the board
/USB-D+#1: U2.3 (D+); also elsewhere on the board
/USB-D-#1: U2.4 (D-); also elsewhere on the board
GND: C18.2, C19.2, R33.1, R36.2, U2.2 (GND), U2.25 (GND); also elsewhere on the board
unnamed: Q1.1 (B), R34.1
unnamed: Q2.1 (B), R35.1
unnamed: R36.1, U2.15 (~SUSPENDb)
VBUS: R93.2; also elsewhere on the board
VDD: C18.1, C19.1, R38.2, U2.5 (VIO), U2.6 (VDD), U2.7 (REGIN); also elsewhere on the board

Notes on the sheet:
Active
From USB Connector
Crossing RxD/TxD happens here!
Auto Program DTR | RTS -> EN | IO0 1 1 1 1 0 0 1 1 1 0 0 1 0 1 1 0
Performs Reset after FLASHing
Pin 10, 16 = NC (leave floating!)
WhirlingBits

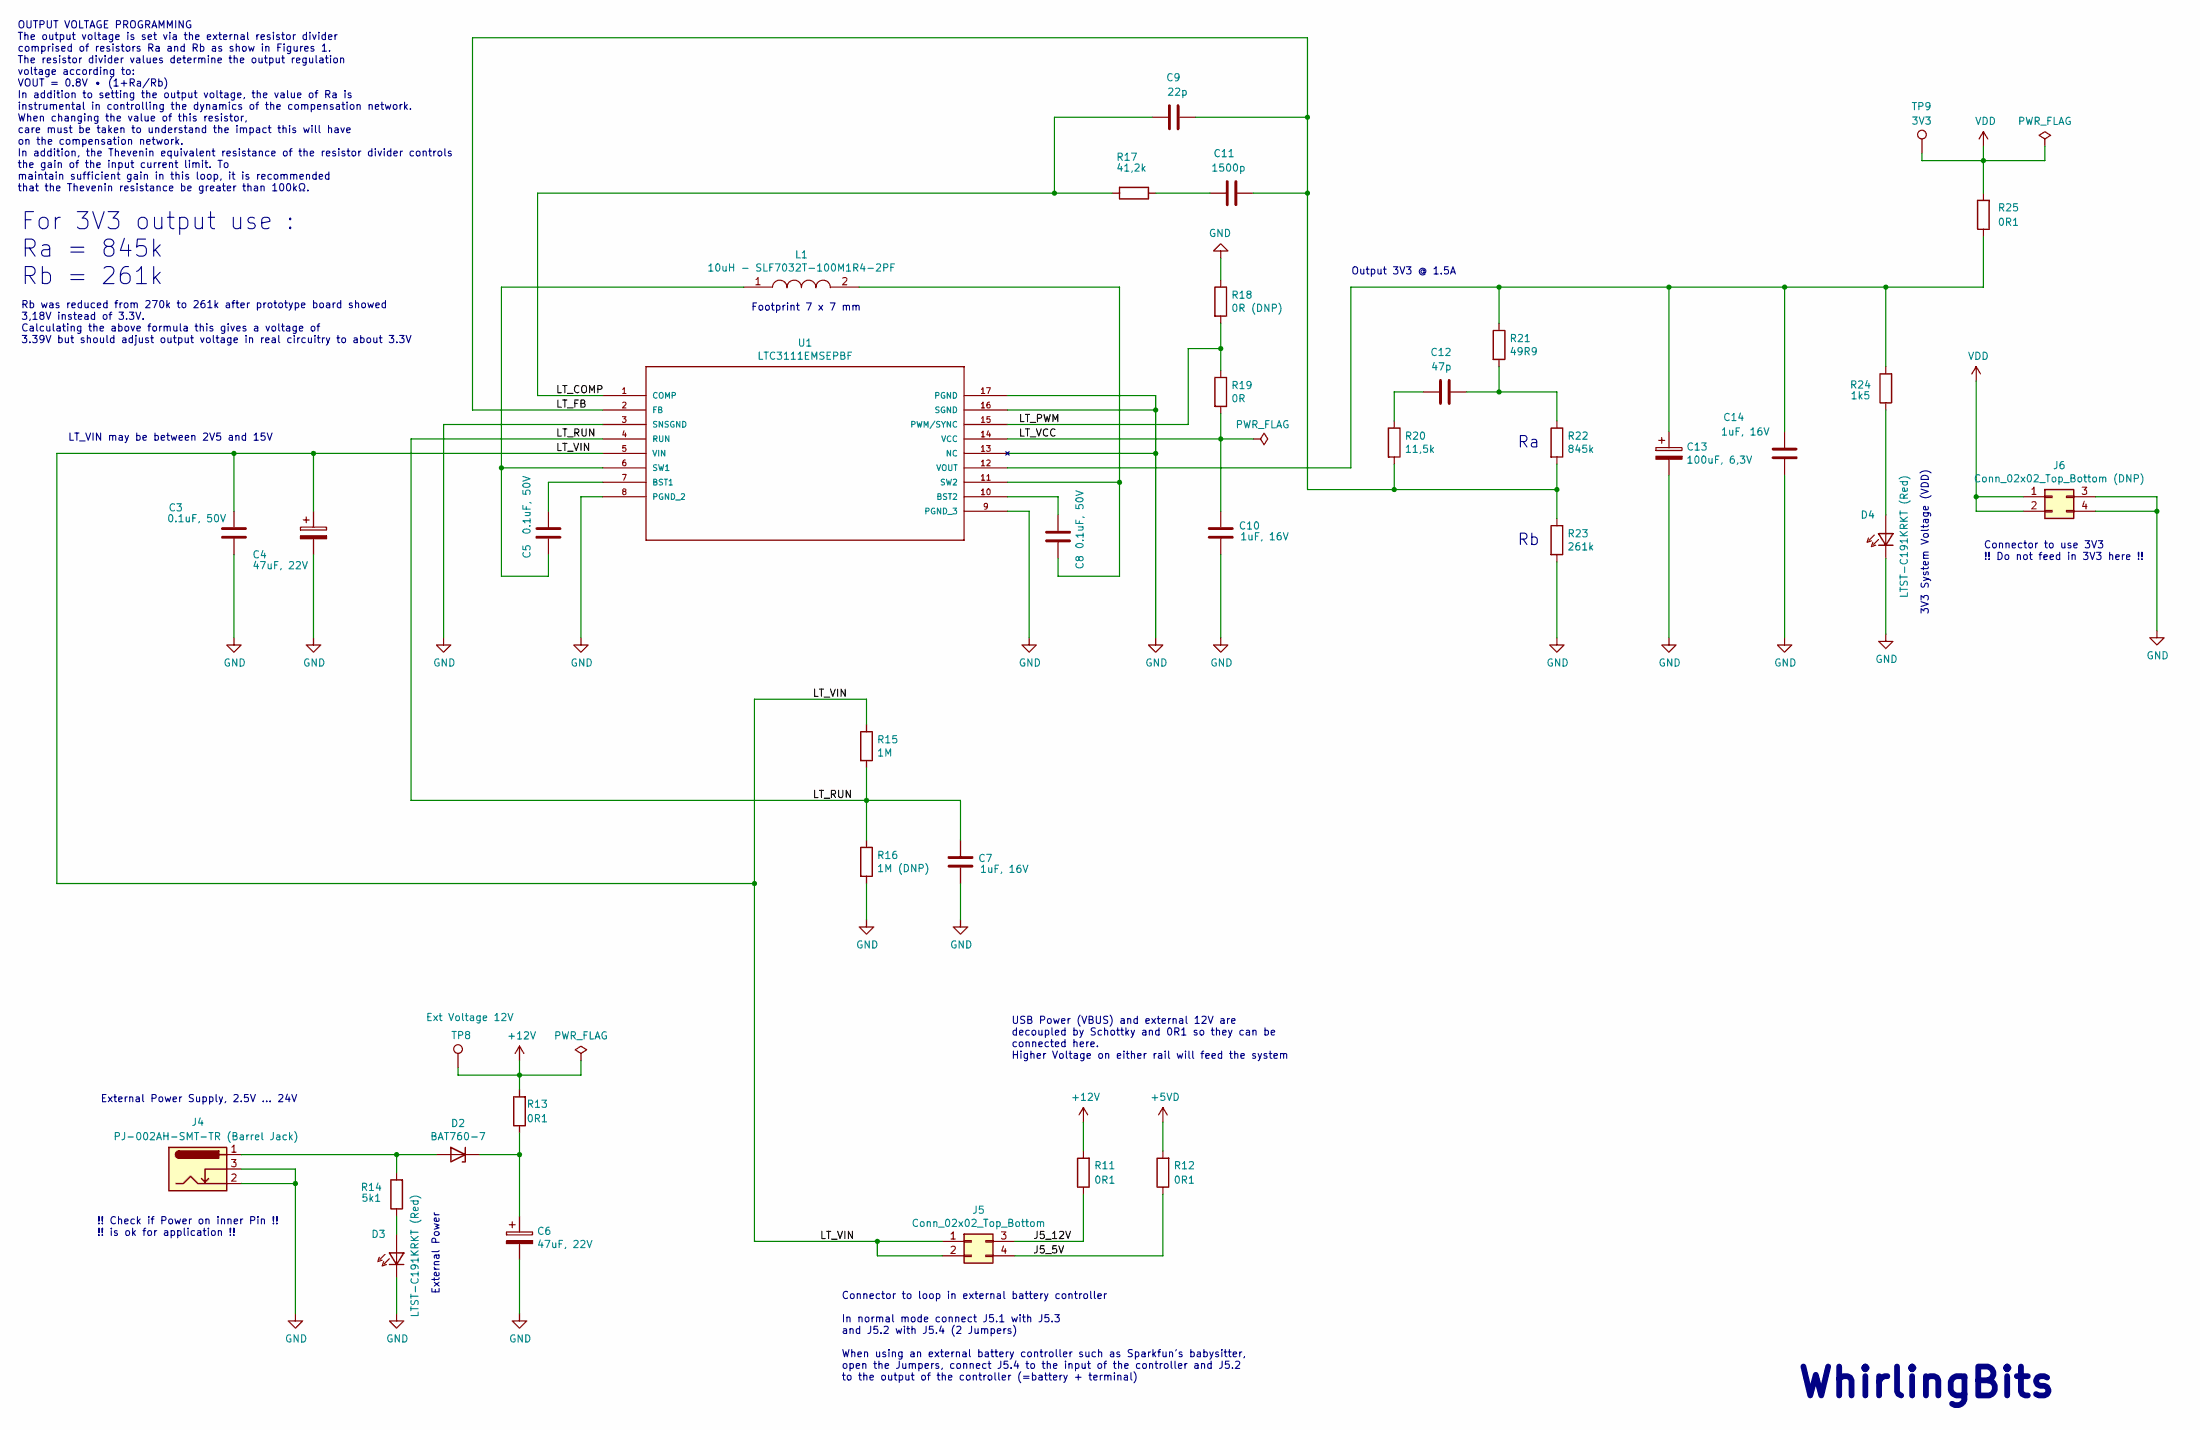
[picture p509: schematic ESP_S3-CP-24_Platform_Power.sch, Espressif ESP32_S3-CP-24 Developer Platform - Overview]

Parts:
C3, C5, C8: 0.1uF, 50V; C_0805_2012Metric; LCSC C161260
C4, C6: 47uF, 22V; C_0805_2012Metric; Mouser Part Number 810-C2012X5R1A476M; LCSC C90142
C7, C10, C14: 1uF, 16V; C_0805_2012Metric; LCSC C16834
C9: 22p; C_0805_2012Metric; LCSC C105623
C11: 1500p; C_0805_2012Metric; LCSC C114765
C12: 47p; C_0805_2012Metric; LCSC C113821
C13: 100uF, 6,3V; C_0805_2012Metric; LCSC C141660
D2: BAT760-7; D_SOD-323; LCSC C116158
D3, D4: LTST-C191KRKT (Red); LED_0603_1608Metric; LCSC C125099
J4: PJ-002AH-SMT-TR (Barrel Jack); BarrelJack_CLIFF_FC681465S_SMT_Horizontal; Mouser Part Number 490-PJ-002AH-SMT-TR
J5: Conn_02x02_Top_Bottom; PinHeader_2x02_P2.54mm_Vertical; LCSC C492419
J6: Conn_02x02_Top_Bottom (DNP); PinHeader_2x02_P2.54mm_Vertical; LCSC C492419
L1: 10uH - SLF7032T-100M1R4-2PF; L_TDK_SLF7032; Mouser Part Number 810-SLF732100M1R42PF
R11, R12, R13, R25: 0R1; R_1210_3225Metric; LCSC C473589
R14: 5k1; R_0805_2012Metric; LCSC C204548
R15: 1M; R_0805_2012Metric; LCSC C230655
R16: 1M (DNP); R_0805_2012Metric; LCSC C230655
R17: 41,2k; R_0805_2012Metric; LCSC C204486
R18: 0R (DNP); R_0805_2012Metric; LCSC C100045
R19: 0R; R_0805_2012Metric; LCSC C100045
R20: 11,5k; R_0805_2012Metric; LCSC C228269
R21: 49R9; R_0805_2012Metric; LCSC C479104
R22: 845k; R_0805_2012Metric; LCSC C416871
R23: 261k; R_0805_2012Metric; LCSC C352236
R24: 1k5; R_0805_2012Metric; LCSC C163951
TP8: Ext Voltage 12V; TestPoint_Pad_2.0x2.0mm
TP9: 3V3; TestPoint_Pad_2.0x2.0mm
U1: LTC3111EMSEPBF; MSOP-16-1EP_3x4.039mm_P0.5mm_EP1.651x2.845mm_ThermalVias; MANUFACTURER_PART_NUMBER ltc3111emse#pbf; LCSC C684080

Connections:
+5VD: R12.2; also elsewhere on the board
+12V: R11.2, R13.2, TP8.1; also elsewhere on the board
/Espressif Developer Platform - Power/J5_5V: J5.4, R12.1
/Espressif Developer Platform - Power/J5_12V: J5.3, R11.1
/Espressif Developer Platform - Power/LT_COMP: C9.1, R17.2, U1.1 (COMP)
/Espressif Developer Platform - Power/LT_FB: C9.2, C11.2, R20.2, R22.2, R23.1, U1.2 (FB)
/Espressif Developer Platform - Power/LT_PWM: R18.2, R19.1, U1.15 (PWM/SYNC)
/Espressif Developer Platform - Power/LT_RUN: C7.2, R15.2, R16.1, U1.4 (RUN)
/Espressif Developer Platform - Power/LT_VCC: C10.2, R19.2, U1.14 (VCC)
/Espressif Developer Platform - Power/LT_VIN: C3.2, C4.1, J5.1, J5.2, R15.1, U1.5 (VIN)
GND: C3.1, C4.2, C6.2, C7.1, C10.1, C13.2, C14.1, D3.1, D4.1, J4.2, J4.3, J6.3, J6.4, R16.2, R18.1, R23.2, U1.3 (SNSGND), U1.8 (PGND_2), U1.9 (PGND_3), U1.13 (NC), U1.16 (SGND), U1.17 (PGND); also elsewhere on the board
unnamed: C5.1, L1.1, U1.6 (SW1)
unnamed: C5.2, U1.7 (BST1)
unnamed: C6.1, D2.1 (K), R13.1
unnamed: C8.1, L1.2, U1.11 (SW2)
unnamed: C8.2, U1.10 (BST2)
unnamed: C11.1, R17.1
unnamed: C12.1, R20.1
unnamed: C12.2, R21.2, R22.1
unnamed: C13.1, C14.2, R21.1, R24.2, R25.1, U1.12 (VOUT)
unnamed: D2.2 (A), J4.1, R14.2
unnamed: D3.2, R14.1
unnamed: D4.2, R24.1
VDD: J6.1, J6.2, R25.2, TP9.1; also elsewhere on the board

Notes on the sheet:
OUTPUT VOLTAGE PROGRAMMING The output voltage is set via the external resistor divider comprised of resistors Ra and Rb as show in Figures 1. The resistor divider values determine the output regulation voltage according to: VOUT = 0.8V • (1+Ra/Rb) In addition to setting the output voltage, the valu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
For 3V3 output use : Ra = 845k Rb = 261k
External Power Supply, 2.5V ... 24V
USB Power (VBUS) and external 12V are decoupled by Schottky and 0R1 so they can be connected here. Higher Voltage on either rail will feed the system
External Power
LT_VIN may be between 2V5 and 15V
Output 3V3 @ 1.5A
Connector to loop in external battery controller In normal mode connect J5.1 with J5.3 and J5.2 with J5.4 (2 Jumpers) When using an external battery controller such as Sparkfun's babysitter, open the Jumpers, connect J5.4 to the input of the controller and J5.2 to the output of the controller (=bat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
Connector to use 3V3 !! Do not feed in 3V3 here !!
3V3 System Voltage (VDD)
Footprint 7 x 7 mm
!! Check if Power on inner Pin !! !! is ok for application !!
WhirlingBits
Rb was reduced from 270k to 261k after prototype board showed 3,18V instead of 3.3V. Calculating the above formula this gives a voltage of 3.39V but should adjust output voltage in real circuitry to about 3.3V
