rompasaurus/regardedPal/hardware-design/examples/07-whirlingbits-s3-platform/ESP_S3-CP-24_Platform.kicad_pcb

## KiCad design hardware-design/examples/07-whirlingbits-s3-platform/ESP_S3-CP-24_Platform.kicad_pcb (continued)

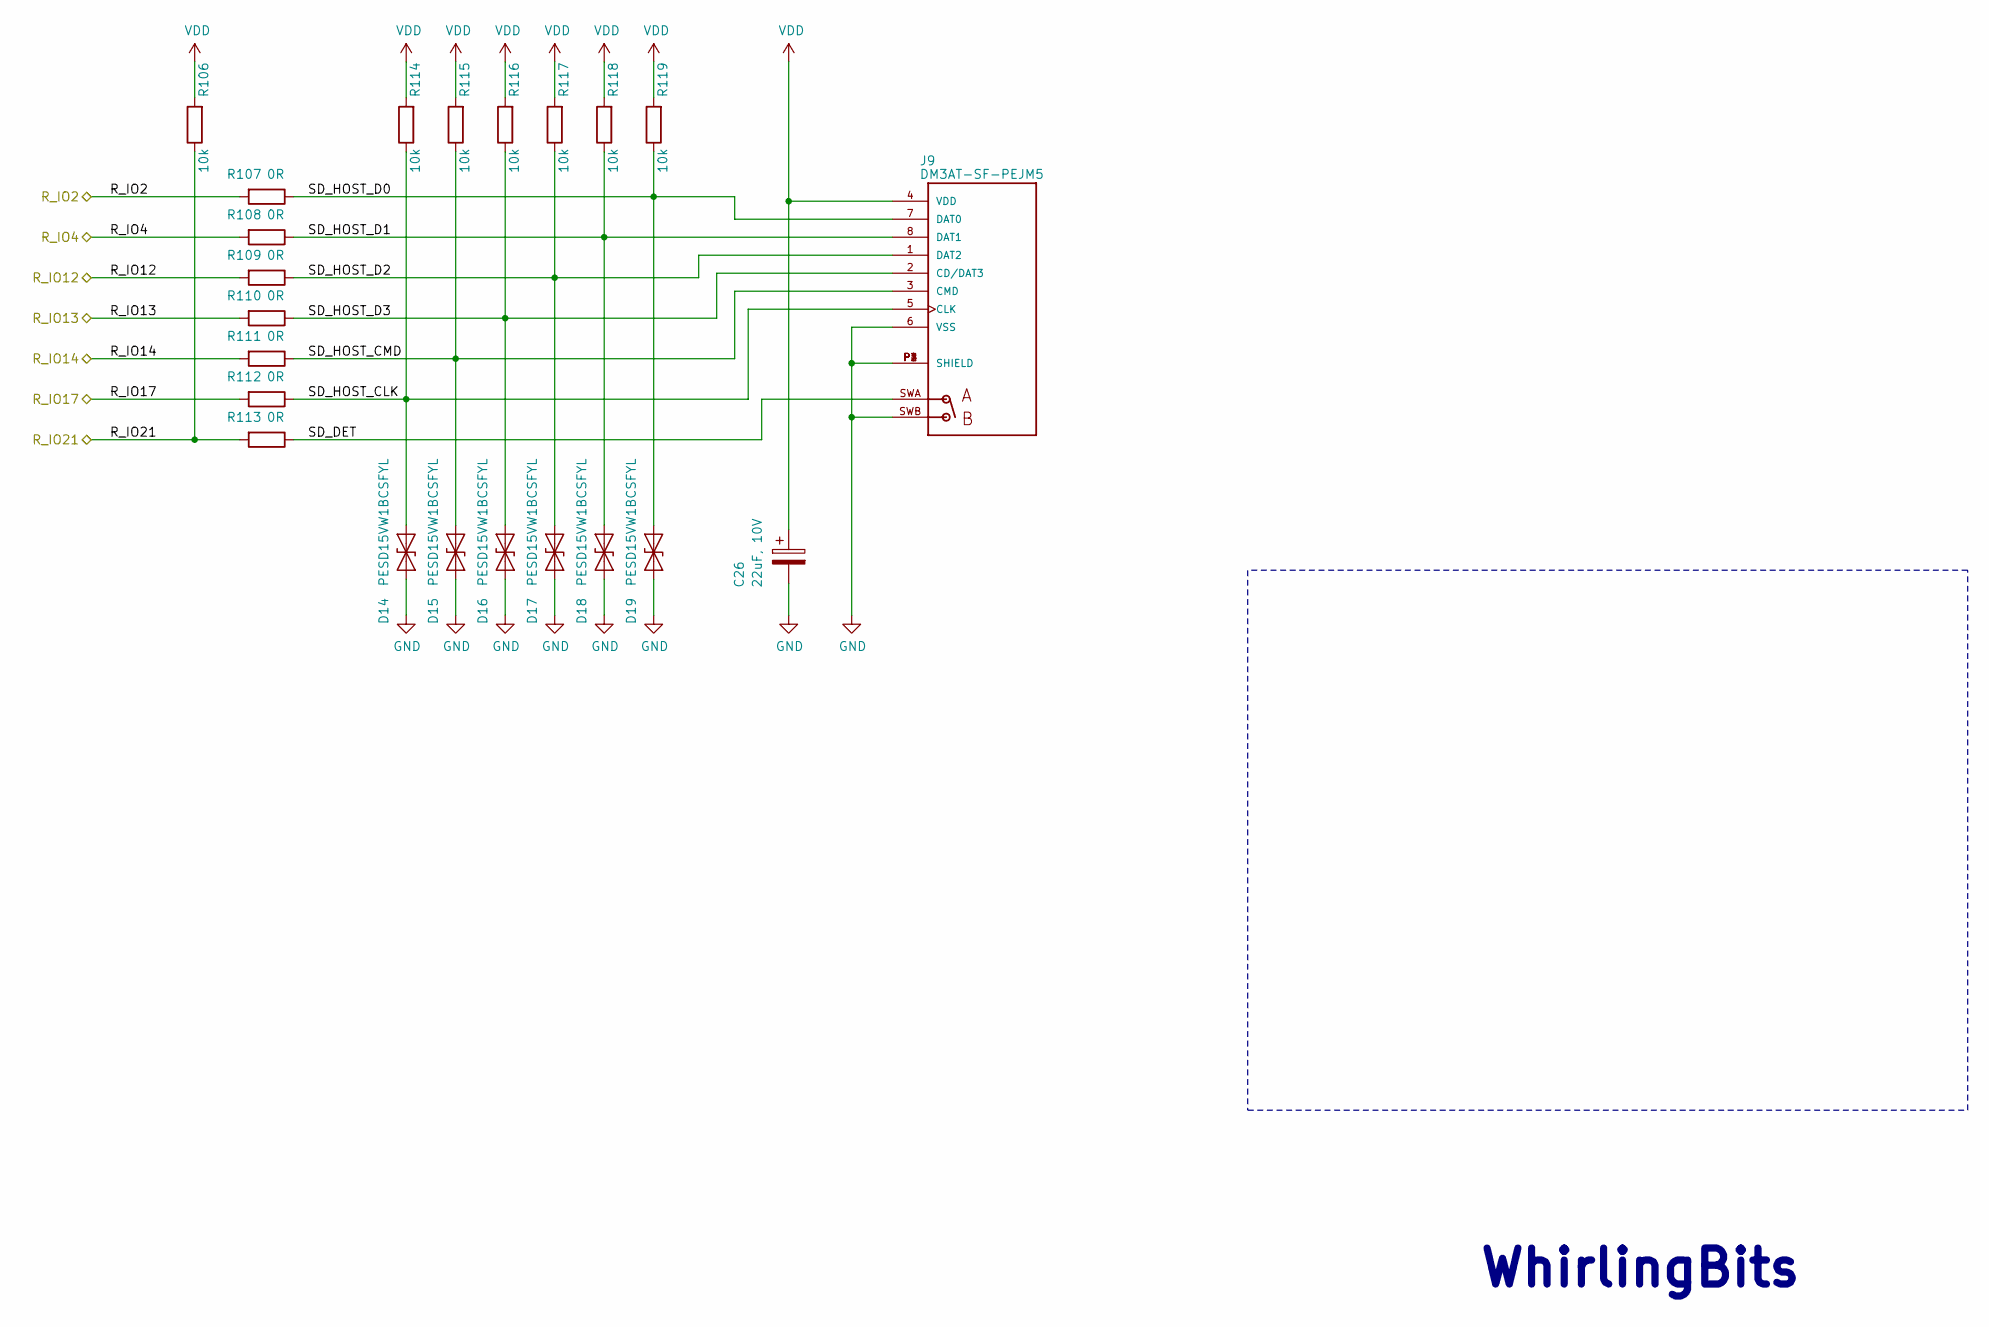
[picture p510: schematic ESP_S3-CP-24_Platform_uSDCard.sch, Espressif ESP32_S3-CP-24 Developer Platform - Overview]

Parts:
C26: 22uF, 10V; C_0805_2012Metric; Mouser 81-GRM21BD71A226ME4L
D14, D15, D16, D17, D18, D19: PESD15VW1BCSFYL; D_SOD-523; Mouser Part Number 771-PESD15VW1BCSFYL; Mouser 771-PESD15VW1BCSFYL
J9: DM3AT-SF-PEJM5; HRS_DM3AT-SF-PEJM5; LCSC C114218
R106, R114, R115, R116, R117, R118, R119: 10k; R_0805_2012Metric; LCSC C169253
R107, R108, R109, R110, R111, R112, R113: 0R; R_0805_2012Metric; LCSC C100045

Connections:
/Espressif Developer PLatform - uSDCard/SD_DET: J9.SWA, R113.1
/Espressif Developer PLatform - uSDCard/SD_HOST_CLK: D14.1 (A1), J9.5 (CLK), R112.1, R114.1
/Espressif Developer PLatform - uSDCard/SD_HOST_CMD: D15.1 (A1), J9.3 (CMD), R111.1, R115.1
/Espressif Developer PLatform - uSDCard/SD_HOST_D0: D19.1 (A1), J9.7 (DAT0), R107.1, R119.1
/Espressif Developer PLatform - uSDCard/SD_HOST_D1: D18.1 (A1), J9.8 (DAT1), R108.1, R118.1
/Espressif Developer PLatform - uSDCard/SD_HOST_D2: D17.1 (A1), J9.1 (DAT2), R109.1, R117.1
/Espressif Developer PLatform - uSDCard/SD_HOST_D3: D16.1 (A1), J9.2 (CD/DAT3), R110.1, R116.1
/R_IO2: R107.2; also elsewhere on the board
/R_IO4: R108.2; also elsewhere on the board
/R_IO12: R109.2; also elsewhere on the board
/R_IO13: R110.2; also elsewhere on the board
/R_IO14: R111.2; also elsewhere on the board
/R_IO17: R112.2; also elsewhere on the board
/R_IO21: R106.1, R113.2; also elsewhere on the board
GND: C26.2, D14.2 (A2), D15.2 (A2), D16.2 (A2), D17.2 (A2), D18.2 (A2), D19.2 (A2), J9.6 (VSS), J9.P1 (SHIELD), J9.P2 (SHIELD), J9.P3 (SHIELD), J9.P4 (SHIELD), J9.SWB; also elsewhere on the board
VDD: C26.1, J9.4 (VDD), R106.2, R114.2, R115.2, R116.2, R117.2, R118.2, R119.2; also elsewhere on the board

Notes on the sheet:
WhirlingBits

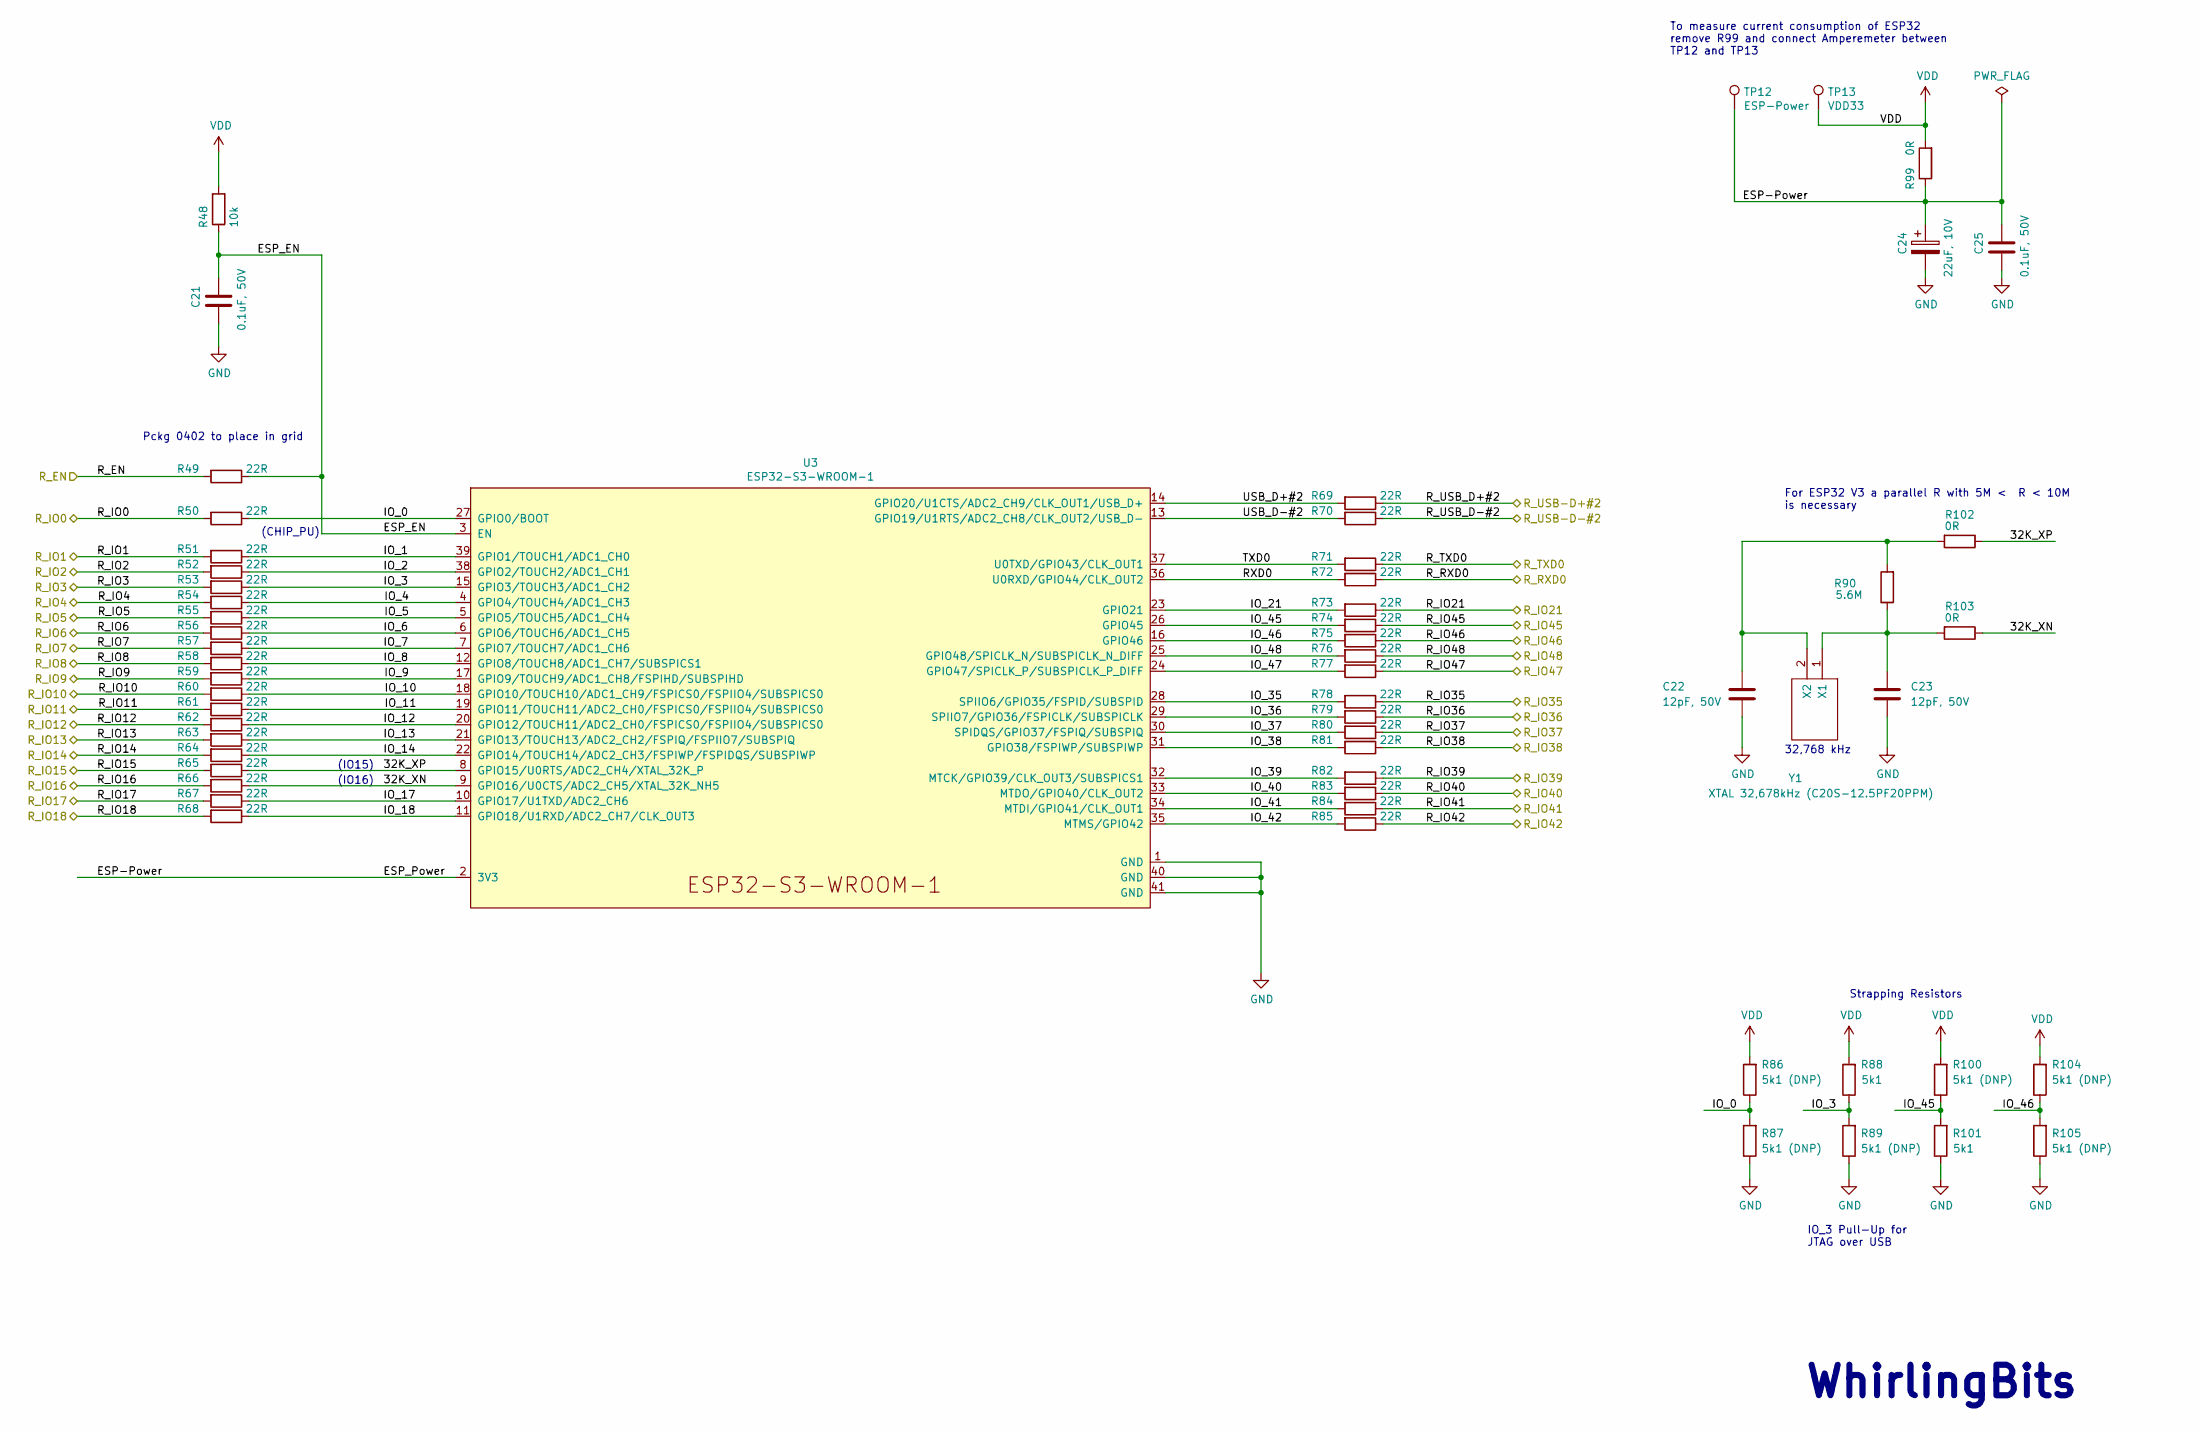
[picture p511: schematic ESP_S3-CP-24_Platform_Modules.sch, Espressif ESP32_S3-CP-24 Developer Platform - Overview]

Parts:
C21, C25: 0.1uF, 50V; C_0805_2012Metric; LCSC C161260
C22, C23: 12pF, 50V; C_0805_2012Metric; LCSC C182488
C24: 22uF, 10V; C_0805_2012Metric; Mouser 81-GRM21BD71A226ME4L
R48: 10k; R_0805_2012Metric; LCSC C169253
R49, R50, R51, R52, R53, R54, R55, R56, R57, R58, R59, R60, R61, R62, R63, R64, R65, R66, R67, R68, R69, R70, R71, R72, R73, R74, R75, R76, R77, R78, R79, R80, R81, R82, R83, R84, R85: 22R; R_0402_1005Metric; LCSC C114765
R86, R87, R89, R100, R104, R105: 5k1 (DNP); R_0805_2012Metric; LCSC C204548
R88, R101: 5k1; R_0805_2012Metric; LCSC C204548
R90: 5.6M; R_0805_2012Metric; LCSC C185285
R99, R102, R103: 0R; R_0805_2012Metric; LCSC C100045
TP12: ESP-Power; TestPoint_Pad_2.0x2.0mm
TP13: VDD33; TestPoint_Pad_2.0x2.0mm
U3: ESP32-S3-WROOM-1; LCSC C2913201
Y1: XTAL 32,678kHz (C20S-12.5PF20PPM); SC20S125PF20PPM; Manufacturer_Part_Number SC20S-12.5PF20PPM; LCSC C97603

Connections:
/Espressif Developer Platform - Modules/32K_XN: R66.1, R103.1, U3.9 (GPIO16/U0CTS/ADC2_CH5/XTAL_32K_NH5)
/Espressif Developer Platform - Modules/32K_XP: R65.1, R102.1, U3.8 (GPIO15/U0RTS/ADC2_CH4/XTAL_32K_P)
/Espressif Developer Platform - Modules/ESP-Power: C24.1, C25.1, R99.1, TP12.1, U3.2 (3V3)
/Espressif Developer Platform - Modules/ESP_EN: C21.1, R48.1, R49.1, U3.3 (EN)
/Espressif Developer Platform - Modules/IO_0: R50.1, R86.1, R87.2, U3.27 (GPIO0/BOOT)
/Espressif Developer Platform - Modules/IO_1: R51.1, U3.39 (GPIO1/TOUCH1/ADC1_CH0)
/Espressif Developer Platform - Modules/IO_2: R52.1, U3.38 (GPIO2/TOUCH2/ADC1_CH1)
/Espressif Developer Platform - Modules/IO_3: R53.1, R88.1, R89.2, U3.15 (GPIO3/TOUCH3/ADC1_CH2)
/Espressif Developer Platform - Modules/IO_4: R54.1, U3.4 (GPIO4/TOUCH4/ADC1_CH3)
/Espressif Developer Platform - Modules/IO_5: R55.1, U3.5 (GPIO5/TOUCH5/ADC1_CH4)
/Espressif Developer Platform - Modules/IO_6: R56.1, U3.6 (GPIO6/TOUCH6/ADC1_CH5)
/Espressif Developer Platform - Modules/IO_7: R57.1, U3.7 (GPIO7/TOUCH7/ADC1_CH6)
/Espressif Developer Platform - Modules/IO_8: R58.1, U3.12 (GPIO8/TOUCH8/ADC1_CH7/SUBSPICS1)
/Espressif Developer Platform - Modules/IO_9: R59.1, U3.17 (GPIO9/TOUCH9/ADC1_CH8/FSPIHD/SUBSPIHD)
/Espressif Developer Platform - Modules/IO_10: R60.1, U3.18 (GPIO10/TOUCH10/ADC1_CH9/FSPICS0/FSPIIO4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)
/Espressif Developer Platform - Modules/IO_11: R61.1, U3.19 (GPIO11/TOUCH11/ADC2_CH0/FSPICS0/FSPIIO4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)
/Espressif Developer Platform - Modules/IO_12: R62.1, U3.20 (GPIO12/TOUCH11/ADC2_CH0/FSPICS0/FSPIIO4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)
/Espressif Developer Platform - Modules/IO_13: R63.1, U3.21 (GPIO13/TOUCH13/ADC2_CH2/FSPIQ/FSPIIO7/S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)
/Espressif Developer Platform - Modules/IO_14: R64.1, U3.22 (GPIO14/TOUCH14/ADC2_CH3/FSPIWP/FSPIDQS/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)
/Espressif Developer Platform - Modules/IO_17: R67.1, U3.10 (GPIO17/U1TXD/ADC2_CH6)
/Espressif Developer Platform - Modules/IO_18: R68.1, U3.11 (GPIO18/U1RXD/ADC2_CH7/CLK_OUT3)
/Espressif Developer Platform - Modules/IO_21: R73.2, U3.23 (GPIO21)
/Espressif Developer Platform - Modules/IO_35: R78.2, U3.28 (SPIIO6/GPIO35/FSPID/SUBSPID)
/Espressif Developer Platform - Modules/IO_36: R79.2, U3.29 (SPIIO7/GPIO36/FSPICLK/SUBSPICLK)
/Espressif Developer Platform - Modules/IO_37: R80.2, U3.30 (SPIDQS/GPIO37/FSPIQ/SUBSPIQ)
/Espressif Developer Platform - Modules/IO_38: R81.2, U3.31 (GPIO38/FSPIWP/SUBSPIWP)
/Espressif Developer Platform - Modules/IO_39: R82.2, U3.32 (MTCK/GPIO39/CLK_OUT3/SUBSPICS1)
/Espressif Developer Platform - Modules/IO_40: R83.2, U3.33 (MTDO/GPIO40/CLK_OUT2)
/Espressif Developer Platform - Modules/IO_41: R84.2, U3.34 (MTDI/GPIO41/CLK_OUT1)
/Espressif Developer Platform - Modules/IO_42: R85.2, U3.35 (MTMS/GPIO42)
/Espressif Developer Platform - Modules/IO_45: R74.2, R100.1, R101.2, U3.26 (GPIO45)
/Espressif Developer Platform - Modules/IO_46: R75.2, R104.1, R105.2, U3.16 (GPIO46)
/Espressif Developer Platform - Modules/IO_47: R77.2, U3.24 (GPIO47/SPICLK_P/SUBSPICLK_P_DIFF)
/Espressif Developer Platform - Modules/IO_48: R76.2, U3.25 (GPIO48/SPICLK_N/SUBSPICLK_N_DIFF)
/Espressif Developer Platform - Modules/RXD0: R72.2, U3.36 (U0RXD/GPIO44/CLK_OUT2)
/Espressif Developer Platform - Modules/TXD0: R71.2, U3.37 (U0TXD/GPIO43/CLK_OUT1)
/Espressif Developer Platform - Modules/USB_D+#2: R69.2, U3.14 (GPIO20/U1CTS/ADC2_CH9/CLK_OUT1/USB_D+)
/Espressif Developer Platform - Modules/USB_D-#2: R70.2, U3.13 (GPIO19/U1RTS/ADC2_CH8/CLK_OUT2/USB_D-)
/R_EN: R49.2; also elsewhere on the board
/R_IO0: R50.2; also elsewhere on the board
/R_IO1: R51.2; also elsewhere on the board
/R_IO2: R52.2; also elsewhere on the board
/R_IO3: R53.2; also elsewhere on the board
/R_IO4: R54.2; also elsewhere on the board
/R_IO5: R55.2; also elsewhere on the board
/R_IO6: R56.2; also elsewhere on the board
/R_IO7: R57.2; also elsewhere on the board
/R_IO8: R58.2; also elsewhere on the board
/R_IO9: R59.2; also elsewhere on the board
/R_IO10: R60.2; also elsewhere on the board
/R_IO11: R61.2; also elsewhere on the board
/R_IO12: R62.2; also elsewhere on the board
/R_IO13: R63.2; also elsewhere on the board
/R_IO14: R64.2; also elsewhere on the board
/R_IO15: R65.2; also elsewhere on the board
/R_IO16: R66.2; also elsewhere on the board
/R_IO17: R67.2; also elsewhere on the board
/R_IO18: R68.2; also elsewhere on the board
/R_IO21: R73.1; also elsewhere on the board
/R_IO35: R78.1; also elsewhere on the board
/R_IO36: R79.1; also elsewhere on the board
/R_IO37: R80.1; also elsewhere on the board
/R_IO38: R81.1; also elsewhere on the board
/R_IO39: R82.1; also elsewhere on the board
/R_IO40: R83.1; also elsewhere on the board
/R_IO41: R84.1; also elsewhere on the board
/R_IO42: R85.1; also elsewhere on the board
/R_IO45: R74.1; also elsewhere on the board
/R_IO46: R75.1; also elsewhere on the board
/R_IO47: R77.1; also elsewhere on the board
/R_IO48: R76.1; also elsewhere on the board
/R_RXD0: R72.1; also elsewhere on the board
/R_TXD0: R71.1; also elsewhere on the board
/R_USB-D+#2: R69.1; also elsewhere on the board
/R_USB-D-#2: R70.1; also elsewhere on the board
GND: C21.2, C22.2, C23.2, C24.2, C25.2, R87.1, R89.1, R101.1, R105.1, U3.1 (GND), U3.40 (GND), U3.41 (GND); also elsewhere on the board
unnamed: C22.1, R90.2, R102.2, Y1.2 (X2)
unnamed: C23.1, R90.1, R103.2, Y1.1 (X1)
VDD: R48.2, R86.2, R88.2, R99.2, R100.2, R104.2, TP13.1; also elsewhere on the board

Notes on the sheet:
To measure current consumption of ESP32 remove R99 and connect Amperemeter between TP12 and TP13
Strapping Resistors
For ESP32 V3 a parallel R with 5M < R < 10M is necessary
Pckg 0402 to place in grid
32,768 kHz
(IO15)
(IO16)
(CHIP_PU)
IO_3 Pull-Up for JTAG over USB
WhirlingBits

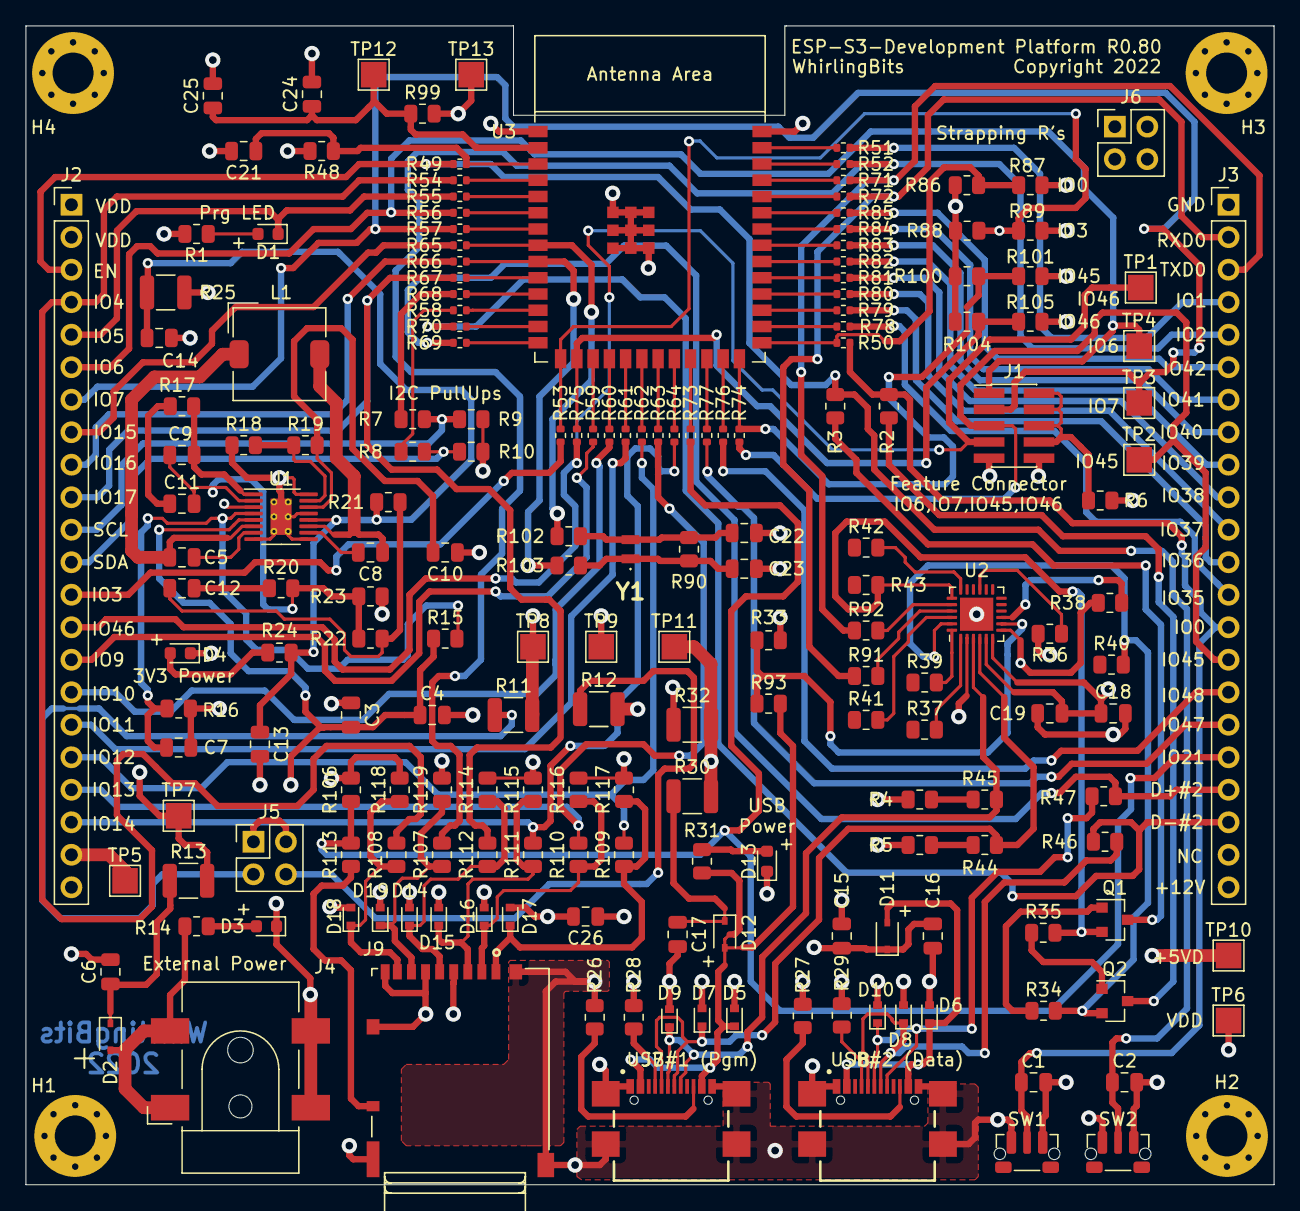
[picture p512: board ESP_S3-CP-24_Platform.kicad_pcb from above]

Board: 4 copper layers, 97.5 x 90.6 mm, 193 parts (0 on the bottom side), 142 nets.
