rompasaurus/regardedPal/hardware-design/examples/02-lilka-console/hardware/v2/main.kicad_pcb

## KiCad design hardware-design/examples/02-lilka-console/hardware/v2/main.kicad_pcb (2026-04-15)

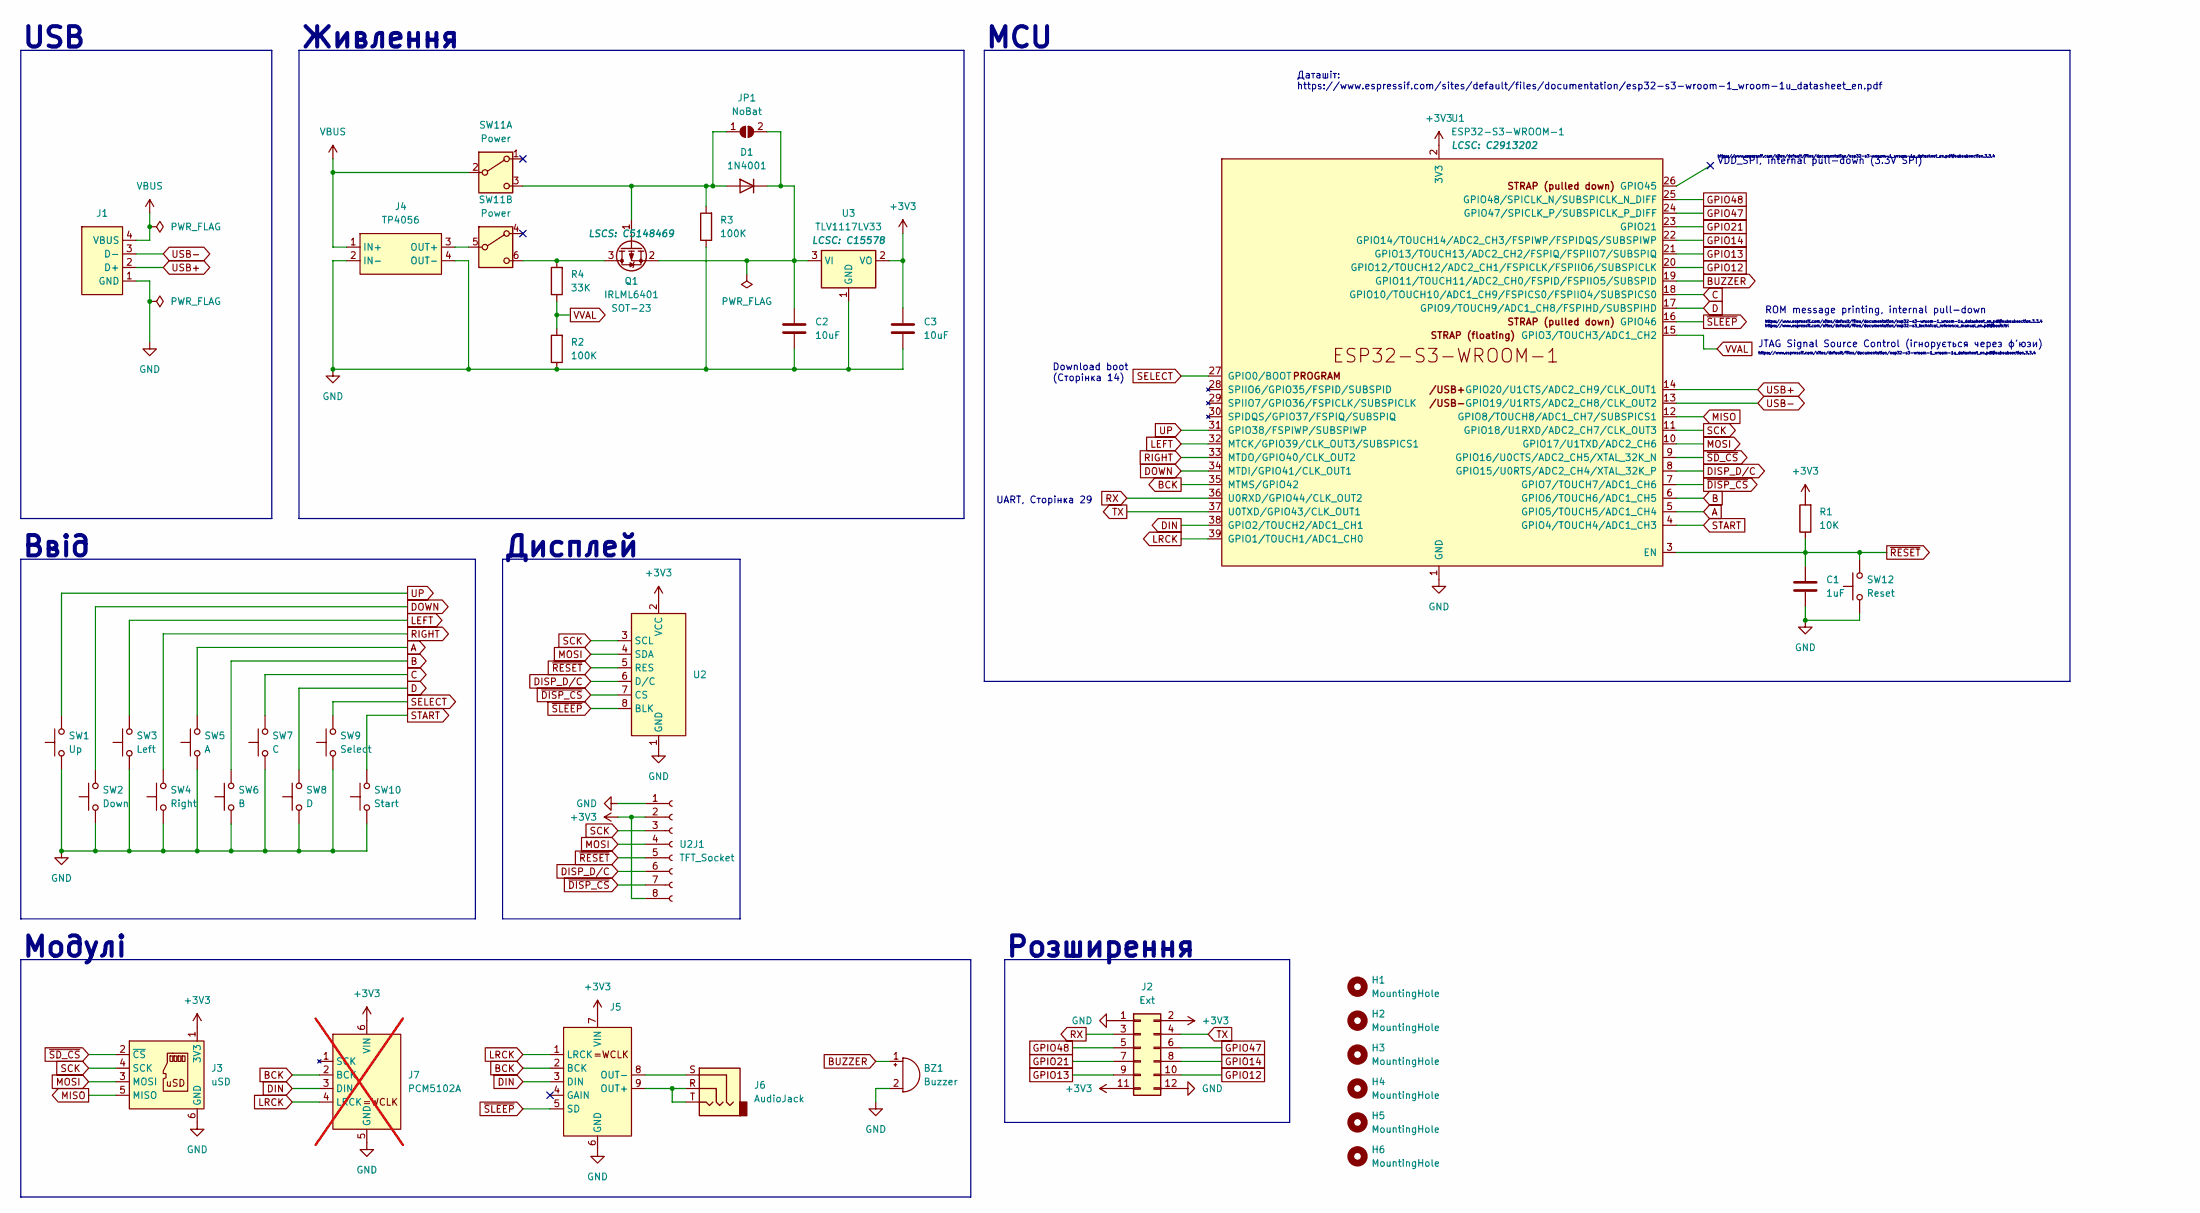
[picture p513: schematic main.kicad_sch, Lilka]

Parts:
BZ1: Buzzer; Buzzer_Wide
C1: 1uF; C_Disc_D4.3mm_W1.9mm_P5.00mm
C2, C3: 10uF; C_Disc_D4.3mm_W1.9mm_P5.00mm
D1: 1N4001; D_DO-41_SOD81_P10.16mm_Horizontal
H1, H2, H3, H4, H5, H6: MountingHole; MountingHole_2.7mm_M2.5_DIN965_Pad
J1: USB_2.0_PCB
J2: Ext; PinHeader_1x12_P2.54mm_Vertical
J3: uSD; MicroSD-Adapter-3v3
J4: TP4056; Charge_Controller_TP4056_4pin
J5: MAX98357-I2S-Module
J6: AudioJack; JackSocketTRS_PJ3013D
J7: PCM5102A; PCM5102A-I2S-Module; not fitted
JP1: NoBat; SolderJumper-2_P1.3mm_Open_Pad1.0x1.5mm
Q1: IRLML6401; SOT-23
R1: 10K; R_Axial_DIN0204_L3.6mm_D1.6mm_P7.62mm_Horizontal
R2, R3: 100K; R_Axial_DIN0204_L3.6mm_D1.6mm_P7.62mm_Horizontal
R4: 33K; R_Axial_DIN0204_L3.6mm_D1.6mm_P7.62mm_Horizontal
SW1: Up; SW_PUSH-12mm-fixed-min
SW2: Down; SW_PUSH-12mm-fixed-min
SW3: Left; SW_PUSH-12mm-fixed-min
SW4: Right; SW_PUSH-12mm-fixed-min
SW5: A; SW_PUSH-12mm-fixed-min
SW6: B; SW_PUSH-12mm-fixed-min
SW7: C; SW_PUSH-12mm-fixed-min
SW8: D; SW_PUSH-12mm-fixed-min
SW9: Select; SW_PUSH_6mm
SW10: Start; SW_PUSH_6mm
SW11: Power; SW_E-Switch_EG1271_SPDT
SW12: Reset; SW_PUSH_6mm
U1: ESP32-S3-WROOM-1; LCSC C2913202
U2: TFT_240x280_2pads
U2J1: TFT_Socket; PinSocket_1x08_P2.54mm_Vertical
U3: TLV1117LV33; SOT-223; LCSC C15578

Connections:
+3V3: C3.1, J2.2, J2.11, J3.1 (3V3), J5.7 (VIN), J7.6 (VIN), R1.2, U1.2 (3V3), U2.2 (VCC), U2J1.2, U2J1.8, U3.2 (VO), U3.4 (VO)
A: SW5.2, U1.5 (GPIO5/TOUCH5/ADC1_CH4)
B: SW6.2, U1.6 (GPIO6/TOUCH6/ADC1_CH5)
BCK: J5.2 (BCK), J7.2 (BCK), U1.35 (MTMS/GPIO42)
BUZZER: BZ1.1 (+), U1.19 (GPIO11/TOUCH11/ADC2_CH0/FSPID/FSPIIO5/S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)
C: SW7.2, U1.18 (GPIO10/TOUCH10/ADC1_CH9/FSPICS0/FSPIIO4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)
D: SW8.2, U1.17 (GPIO9/TOUCH9/ADC1_CH8/FSPIHD/SUBSPIHD)
DIN: J5.3 (DIN), J7.3 (DIN), U1.38 (GPIO2/TOUCH2/ADC1_CH1)
DISP_D/C: U1.8 (GPIO15/U0RTS/ADC2_CH4/XTAL_32K_P), U2.6 (D/C), U2J1.6
DOWN: SW2.2, U1.34 (MTDI/GPIO41/CLK_OUT1)
GND: BZ1.2 (-), C1.2, C2.2, C3.2, J1.1 (GND), J2.1, J2.12, J3.6 (GND), J4.2 (IN-), J4.4 (OUT-), J5.6 (GND), J7.5 (GND), R2.1, R3.1, SW1.1, SW2.1, SW3.1, SW4.1, SW5.1, SW6.1, SW7.1, SW8.1, SW9.1, SW10.1, SW12.1, U1.1 (GND), U1.40 (GND), U1.41 (GND), U2.1 (GND), U2J1.1, U3.1 (GND)
GPIO12: J2.10, U1.20 (GPIO12/TOUCH12/ADC2_CH1/FSPICLK/FSPIIO6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)
GPIO13: J2.9, U1.21 (GPIO13/TOUCH13/ADC2_CH2/FSPIQ/FSPIIO7/S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)
GPIO14: J2.8, U1.22 (GPIO14/TOUCH14/ADC2_CH3/FSPIWP/FSPIDQS/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)
GPIO21: J2.7, U1.23 (GPIO21)
GPIO47: J2.6, U1.24 (GPIO47/SPICLK_P/SUBSPICLK_P_DIFF)
GPIO48: J2.5, U1.25 (GPIO48/SPICLK_N/SUBSPICLK_N_DIFF)
LEFT: SW3.2, U1.32 (MTCK/GPIO39/CLK_OUT3/SUBSPICS1)
LRCK: J5.1 (LRCK), J7.4 (LRCK), U1.39 (GPIO1/TOUCH1/ADC1_CH0)
MISO: J3.5 (MISO), U1.12 (GPIO8/TOUCH8/ADC1_CH7/SUBSPICS1)
MOSI: J3.3 (MOSI), U1.10 (GPIO17/U1TXD/ADC2_CH6), U2.4 (SDA), U2J1.4
unnamed: D1.2 (A), JP1.1 (A), Q1.1 (G), R3.2, SW11.3 (C)
unnamed: C2.1, D1.1 (K), JP1.2 (B), Q1.2 (S), U3.3 (VI)
unnamed: J4.3 (OUT+), SW11.5 (B)
unnamed: J5.9 (OUT+), J6.R, J6.T
unnamed: J5.8 (OUT-), J6.S
unnamed: Q1.3 (D), R4.2, SW11.6 (C)
RIGHT: SW4.2, U1.33 (MTDO/GPIO40/CLK_OUT2)
RX: J2.3, U1.36 (U0RXD/GPIO44/CLK_OUT2)
SCK: J3.4 (SCK), U1.11 (GPIO18/U1RXD/ADC2_CH7/CLK_OUT3), U2.3 (SCL), U2J1.3
SELECT: SW9.2, U1.27 (GPIO0/BOOT)
START: SW10.2, U1.4 (GPIO4/TOUCH4/ADC1_CH3)
TX: J2.4, U1.37 (U0TXD/GPIO43/CLK_OUT1)
UP: SW1.2, U1.31 (GPIO38/FSPIWP/SUBSPIWP)
USB+: J1.2 (D+), U1.14 (GPIO20/U1CTS/ADC2_CH9/CLK_OUT1)
USB-: J1.3 (D-), U1.13 (GPIO19/U1RTS/ADC2_CH8/CLK_OUT2)
VBUS: J1.4 (VBUS), J4.1 (IN+), SW11.2 (B)
VVAL: R2.2, R4.1, U1.15 (GPIO3/TOUCH3/ADC1_CH2)
~DISP_CS: U1.7 (GPIO7/TOUCH7/ADC1_CH6), U2.7 (CS), U2J1.7
~RESET: C1.1, R1.1, SW12.2, U1.3 (EN), U2.5 (RES), U2J1.5
~SD_CS: J3.2 (~CS), U1.9 (GPIO16/U0CTS/ADC2_CH5/XTAL_32K_N)
~SLEEP: J5.5 (SD), U1.16 (GPIO46), U2.8 (BLK)

Notes on the sheet:
Модулі
Дисплей
Живлення
Ввід
JTAG Signal Source Control (ігнорується через ф'юзи)
Download boot (Сторінка 14)
https://www.espressif.com/sites/default/files/documentation/esp32-s3-wroom-1_wroom-1u_datasheet_en.pdf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 https://www.espressif.com/sites/default/files/documentation/esp32-s3_technical_reference_manual_en.pdf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
VDD_SPI, internal pull-down (3.3V SPI)
Розширення
https://www.espressif.com/sites/default/files/documentation/esp32-s3-wroom-1_wroom-1u_datasheet_en.pdf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
Даташіт: https://www.espressif.com/sites/default/files/documentation/esp32-s3-wroom-1_wroom-1u_datasheet_en.pdf
USB
MCU
ROM message printing, internal pull-down
UART, Сторінка 29

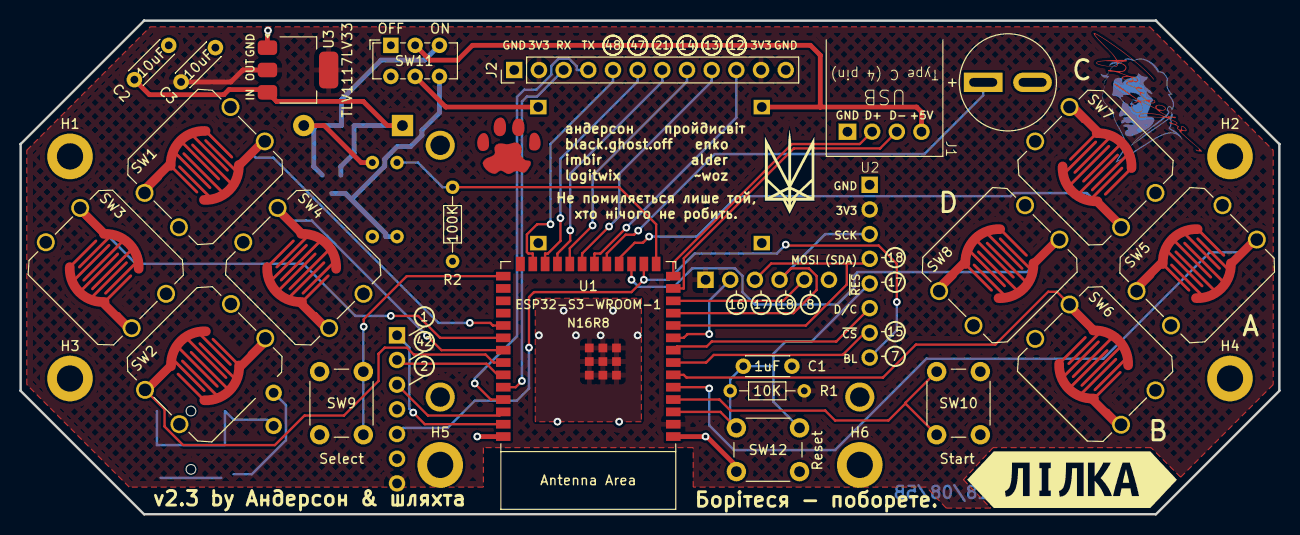
[picture p514: board hardware-design/examples/02-lilka-console/hardware/v2/main.kicad_pcb from above]

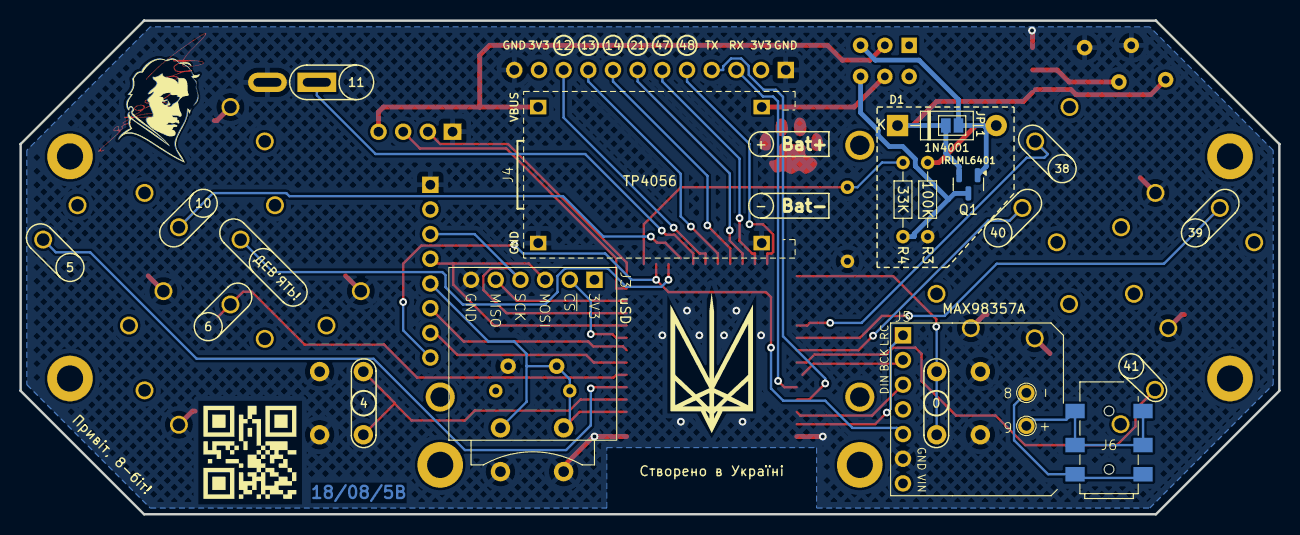
[picture p515: board hardware-design/examples/02-lilka-console/hardware/v2/main.kicad_pcb from below]

Board: 2 copper layers, 129.5 x 50.8 mm, 39 parts (9 on the bottom side), 42 nets.

Other parts of the board:
kibuzzard-65B2D7AF: G***; kibuzzard-65B2D7AF
