rompasaurus/regardedPal/hardware-design/examples/02-lilka-console/hardware/v1/main.kicad_pcb

## KiCad design hardware-design/examples/02-lilka-console/hardware/v1/main.kicad_pcb (2026-04-15, an earlier design)

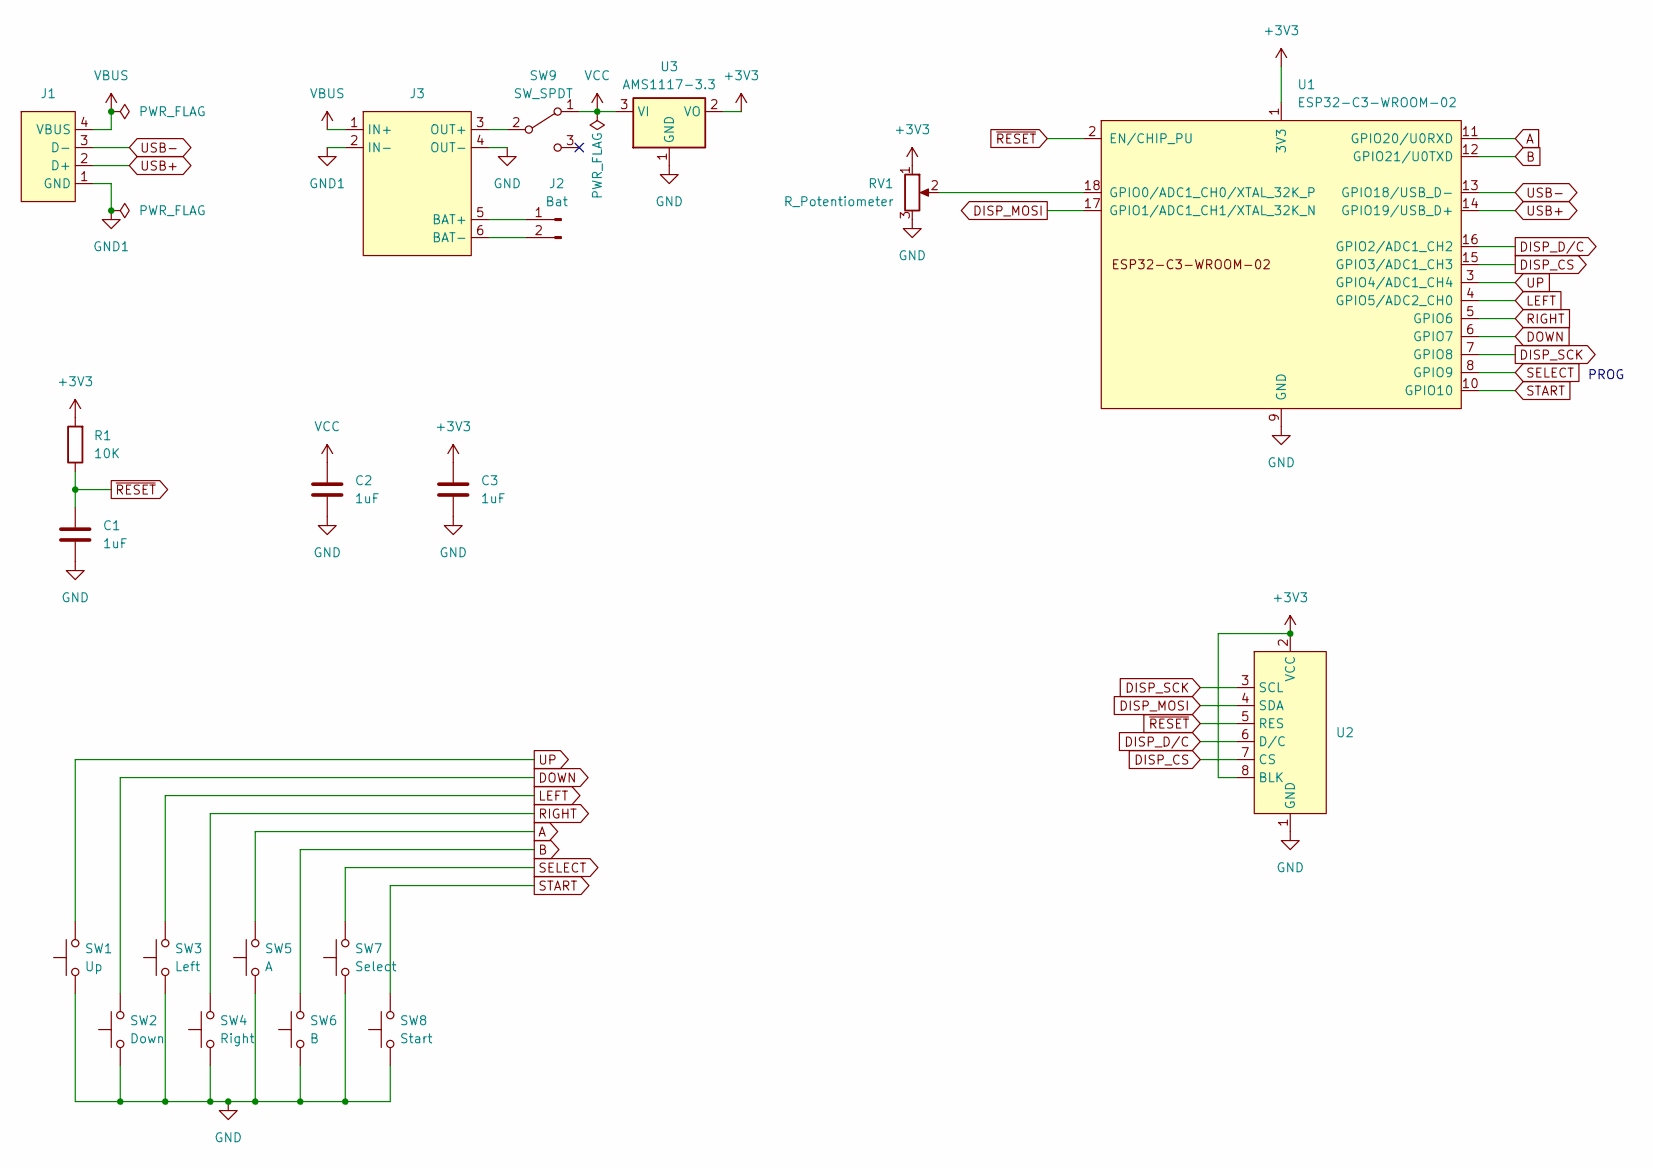
[picture p516: schematic main.kicad_sch]

Parts:
C1, C2, C3: 1uF; C_Disc_D3.0mm_W2.0mm_P2.50mm
J1: USB_2.0_PCB
J2: Bat; PinHeader_1x02_P2.54mm_Vertical
J3: Charge_Controller_TP4056
R1: 10K; R_Axial_DIN0204_L3.6mm_D1.6mm_P7.62mm_Horizontal
RV1: R_Potentiometer; Potentiometer_Alpha_RD901F-40-00D_Single_Vertical
SW1: Up; SW_PUSH-12mm-fixed
SW2: Down; SW_PUSH-12mm-fixed
SW3: Left; SW_PUSH-12mm-fixed
SW4: Right; SW_PUSH-12mm-fixed
SW5: A; SW_PUSH-12mm-fixed
SW6: B; SW_PUSH-12mm-fixed
SW7: Select; SW_PUSH_6mm
SW8: Start; SW_PUSH_6mm
SW9: SW_SPDT; SW_CuK_OS102011MA1QN1_SPDT_Angled
U1: ESP32-C3-WROOM-02; ESP32-C3-WROOM-02_no_gnd
U2: TFT_240x280
U3: AMS1117-3.3; SOT-223-3_TabPin2

Connections:
+3V3: C3.1, R1.2, RV1.1, U1.1 (3V3), U2.2 (VCC), U2.8 (BLK), U3.2 (VO)
A: SW5.2, U1.11 (GPIO20/U0RXD)
B: SW6.2, U1.12 (GPIO21/U0TXD)
DISP_CS: U1.15 (GPIO3/ADC1_CH3), U2.7 (CS)
DISP_D/C: U1.16 (GPIO2/ADC1_CH2), U2.6 (D/C)
DISP_MOSI: U1.17 (GPIO1/ADC1_CH1/XTAL_32K_N), U2.4 (SDA)
DISP_SCK: U1.7 (GPIO8), U2.3 (SCL)
DOWN: SW2.2, U1.6 (GPIO7)
GND: C1.2, C2.2, C3.2, J3.4 (OUT-), RV1.3, SW1.1, SW2.1, SW3.1, SW4.1, SW5.1, SW6.1, SW7.1, SW8.1, U1.9 (GND), U2.1 (GND), U3.1 (GND)
GND1: J1.1 (GND), J3.2 (IN-)
LEFT: SW3.2, U1.4 (GPIO5/ADC2_CH0)
unnamed: J2.1, J3.5 (BAT+)
unnamed: J2.2, J3.6 (BAT-)
unnamed: J3.3 (OUT+), SW9.2 (B)
unnamed: RV1.2, U1.18 (GPIO0/ADC1_CH0/XTAL_32K_P)
RIGHT: SW4.2, U1.5 (GPIO6)
SELECT: SW7.2, U1.8 (GPIO9)
START: SW8.2, U1.10 (GPIO10)
UP: SW1.2, U1.3 (GPIO4/ADC1_CH4)
USB+: J1.2 (D+), U1.14 (GPIO19/USB_D+)
USB-: J1.3 (D-), U1.13 (GPIO18/USB_D-)
VBUS: J1.4 (VBUS), J3.1 (IN+)
VCC: C2.1, SW9.1 (A), U3.3 (VI)
~RESET: C1.1, R1.1, U1.2 (EN/CHIP_PU), U2.5 (RES)

Notes on the sheet:
PROG
