rompasaurus/regardedPal/hardware-design/examples/02-lilka-console/hardware/v1/main.kicad_pcb

## KiCad design hardware-design/examples/02-lilka-console/hardware/v1/main.kicad_pcb (continued)

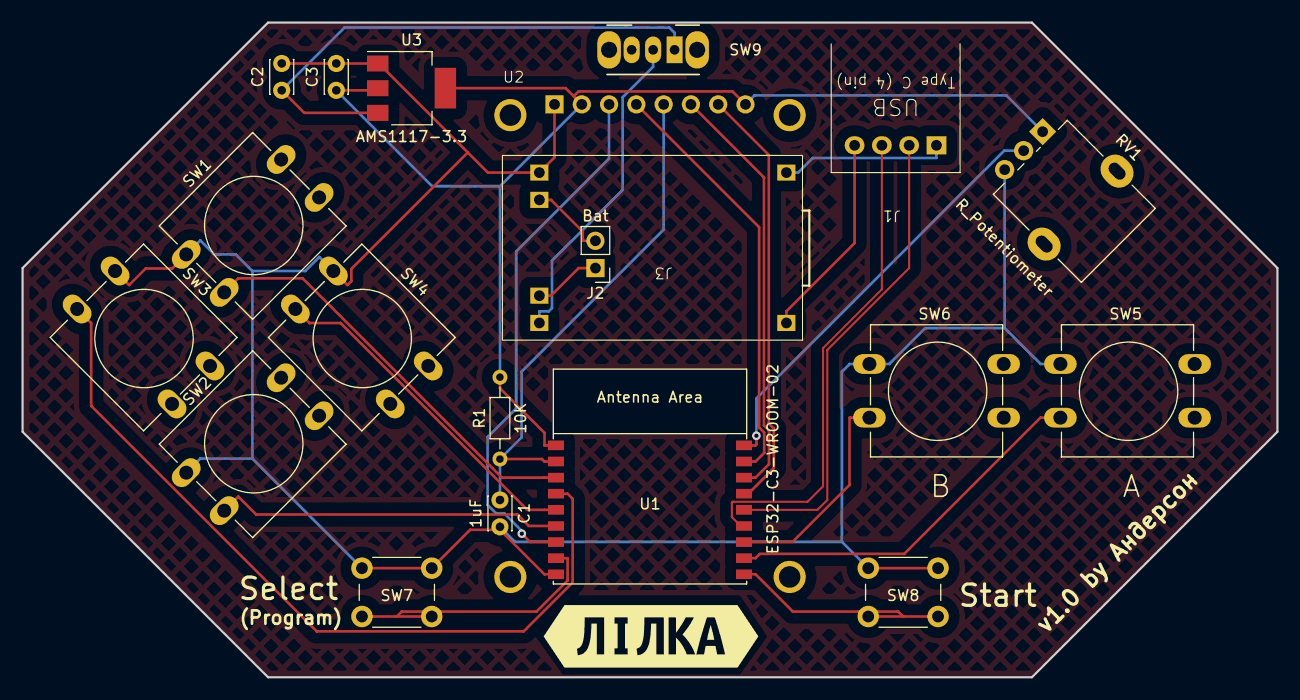
[picture p517: board hardware-design/examples/02-lilka-console/hardware/v1/main.kicad_pcb from above]

Board: 2 copper layers, 116.8 x 61.0 mm, 21 parts (0 on the bottom side), 24 nets.

Other parts of the board:
kibuzzard-65B2D7AF: G***; kibuzzard-65B2D7AF
