rompasaurus/regardedPal/hardware-design/reference-boards/opentama-virtual-pet/OpenTama.kicad_pcb

## KiCad design hardware-design/reference-boards/opentama-virtual-pet/OpenTama.kicad_pcb (2026-04-15)

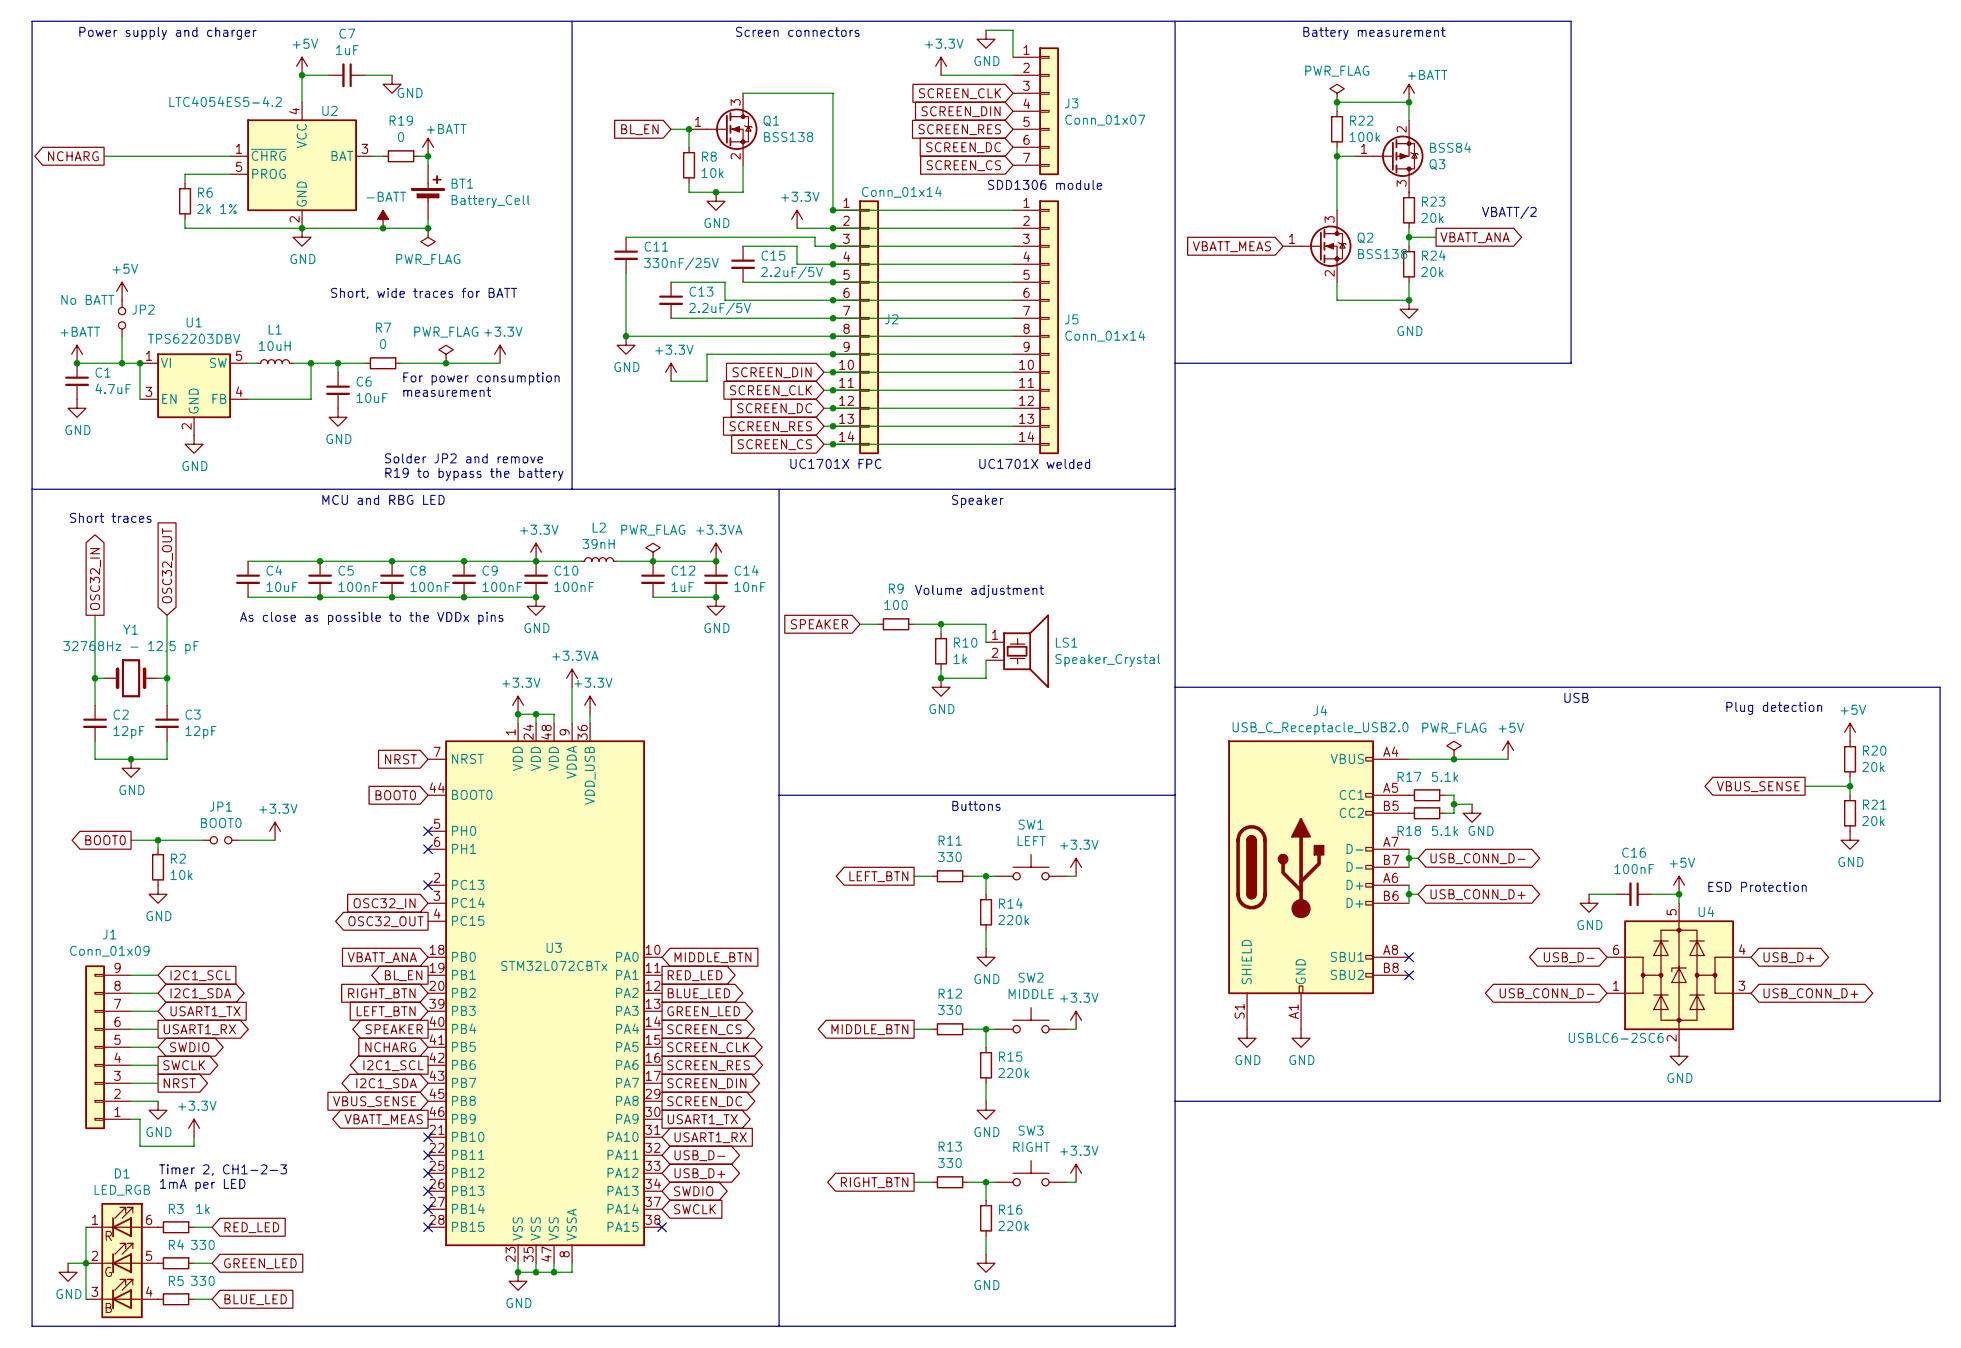
[picture p518: schematic OpenTama.kicad_sch]

Parts:
BT1: Battery_Cell; Battery_Pads_4x4
C1: 4.7uF; C_1206_3216Metric; LCSC C29823
C2, C3: 12pF; C_0402_1005Metric; LCSC C1547
C4: 10uF; C_0603_1608Metric; LCSC C19702
C5, C8, C9, C10: 100nF; C_0402_1005Metric; LCSC C1525
C6: 10uF; C_1206_3216Metric; LCSC C13585
C7: 1uF; C_1206_3216Metric; LCSC C1848
C11: 330nF/25V; C_0603_1608Metric; LCSC C1615
C12: 1uF; C_0603_1608Metric; LCSC C15849
C13, C15: 2.2uF/5V; C_0402_1005Metric; LCSC C12530
C14: 10nF; C_0402_1005Metric; LCSC C15195
C16: 100nF; C_0603_1608Metric; LCSC C14663
D1: LED_RGB; LED_RGB_TC5050; LCSC C784540
J1: Conn_01x09; PinHeader_1x09_P2.54mm_Vertical
J2: Conn_01x14; Hirose_FH34SRJ-14S-0.5SH_1x14-1MP_P0.50mm_Horizontal; LCSC C324724
J3: Conn_01x07; PinHeader_1x07_P2.54mm_Vertical
J4: USB_C_Receptacle_USB2.0; USB_C_Receptacle_HRO_TYPE-C-31-M-12; LCSC C165948
J5: Conn_01x14; LCD_14p_0.6mm
JP1: BOOT0; PinHeader_1x02_P2.54mm_Vertical
JP2: No BATT; SolderJumper-2_P1.3mm_Open_RoundedPad1.0x1.5mm
L1: 10uH; L_Sunlord_MWSA0518_5.4x5.2mm; LCSC C408412
L2: 39nH; L_0402_1005Metric; LCSC C26443
LS1: Speaker_Crystal; Buzzer_CUI_CPT-9019S-SMT; LCSC C391035
Q1, Q2: BSS138; SOT-23; LCSC C347484
Q3: BSS84; SOT-23; LCSC C8492
R2, R8: 10k; R_0402_1005Metric; LCSC C25744
R3: 1k; R_0603_1608Metric; LCSC C21190
R4, R5: 330; R_0603_1608Metric; LCSC C23138
R6: 2k 1%; R_0603_1608Metric; LCSC C22975
R7, R19: 0; R_0603_1608Metric; LCSC C21189
R9: 100; R_0402_1005Metric; LCSC C25076
R10: 1k; R_0402_1005Metric; LCSC C11702
R11, R12, R13: 330; R_0402_1005Metric; LCSC C25104
R14, R15, R16: 220k; R_0402_1005Metric; LCSC C25767
R17, R18: 5.1k; R_0402_1005Metric; LCSC C25905
R20, R21, R23, R24: 20k; R_0402_1005Metric; LCSC C25765
R22: 100k; R_0402_1005Metric; LCSC C25741
SW1: LEFT; SW_Push_1P1T_NO_6x6mm_H9.5mm; LCSC C221880
SW2: MIDDLE; SW_Push_1P1T_NO_6x6mm_H9.5mm; LCSC C221880
SW3: RIGHT; SW_Push_1P1T_NO_6x6mm_H9.5mm; LCSC C221880
U1: TPS62203DBV; SOT-23-5; LCSC C9051
U2: LTC4054ES5-4.2; TSOT-23-5; LCSC C462648
U3: STM32L072CBTx; LQFP-48_7x7mm_P0.5mm; LCSC C465977
U4: USBLC6-2SC6; SOT-23-6; LCSC C2827654
Y1: 32768Hz - 12,5 pF; Crystal_SMD_3215-2Pin_3.2x1.5mm; LCSC C32346

Connections:
+3.3VA: C12.1, C14.1, L2.2, U3.9 (VDDA)
+3V3: C4.1, C5.1, C8.1, C9.1, C10.1, J1.1, J2.2, J2.9, J3.2, J5.2, J5.9, JP1.2, L2.1, R7.1, SW1.2, SW2.2, SW3.2, U3.1 (VDD), U3.24 (VDD), U3.36 (VDD_USB), U3.48 (VDD)
+5V: C7.2, C16.1, J4.A4 (VBUS), J4.A9 (VBUS), J4.B4 (VBUS), J4.B9 (VBUS), JP2.1, R20.1, U2.4 (VCC), U4.5 (VBUS)
+BATT: BT1.1 (+), C1.1, JP2.2, Q3.2 (S), R19.1, R22.1, U1.1 (VI), U1.3 (EN)
-BATT: BT1.2 (-), C1.2, C2.2, C3.2, C4.2, C5.2, C6.2, C7.1, C8.2, C9.2, C10.2, C11.2, C12.2, C14.2, C16.2, D1.1 (RK), D1.2 (GK), D1.3 (BK), J1.2, J2.8, J3.1, J4.A1 (GND), J4.A12 (GND), J4.B1 (GND), J4.B12 (GND), J4.S1 (SHIELD), J5.8, LS1.2, Q1.2 (S), Q2.2 (S), R2.2, R6.2, R8.2, R10.2, R14.2, R15.2, R16.2, R17.1, R18.1, R21.2, R24.2, U1.2 (GND), U2.2 (GND), U3.8 (VSSA), U3.23 (VSS), U3.35 (VSS), U3.47 (VSS), U4.2 (GND)
BLUE_LED: R5.1, U3.12 (PA2)
BL_EN: Q1.1 (G), R8.1, U3.19 (PB1)
BOOT0: JP1.1, R2.1, U3.44 (BOOT0)
GREEN_LED: R4.1, U3.13 (PA3)
I2C1_SCL: J1.9, U3.42 (PB6)
I2C1_SDA: J1.8, U3.43 (PB7)
LEFT_BTN: R11.2, U3.39 (PB3)
MIDDLE_BTN: R12.2, U3.10 (PA0)
NCHARG: U2.1 (~CHRG), U3.41 (PB5)
NRST: J1.3, U3.7 (NRST)
unnamed: D1.4 (BA), R5.2
unnamed: D1.5 (GA), R4.2
unnamed: D1.6 (RA), R3.2
unnamed: J2.1, J5.1, Q1.3 (D)
unnamed: C11.1, J2.3, J5.3
unnamed: C15.1, J2.4, J5.4
unnamed: C15.2, J2.5, J5.5
unnamed: C13.1, J2.6, J5.6
unnamed: C13.2, J2.7, J5.7
unnamed: J4.A5 (CC1), R17.2
unnamed: J4.B5 (CC2), R18.2
unnamed: LS1.1, R9.1, R10.1
unnamed: Q2.3 (D), Q3.1 (G), R22.2
unnamed: Q3.3 (D), R23.1
unnamed: R11.1, R14.1, SW1.1
unnamed: R12.1, R15.1, SW2.1
unnamed: R13.1, R16.1, SW3.1
unnamed: C6.1, L1.2, R7.2, U1.4 (FB)
unnamed: L1.1, U1.5 (SW)
unnamed: R19.2, U2.3 (BAT)
unnamed: R6.1, U2.5 (PROG)
OSC32_IN: C2.1, U3.3 (PC14), Y1.1
OSC32_OUT: C3.1, U3.4 (PC15), Y1.2
RED_LED: R3.1, U3.11 (PA1)
RIGHT_BTN: R13.2, U3.20 (PB2)
SCREEN_CLK: J2.11, J3.3, J5.11, U3.15 (PA5)
SCREEN_CS: J2.14, J3.7, J5.14, U3.14 (PA4)
SCREEN_DC: J2.12, J3.6, J5.12, U3.29 (PA8)
SCREEN_DIN: J2.10, J3.4, J5.10, U3.17 (PA7)
SCREEN_RES: J2.13, J3.5, J5.13, U3.16 (PA6)
SPEAKER: R9.2, U3.40 (PB4)
SWCLK: J1.4, U3.37 (PA14)
SWDIO: J1.5, U3.34 (PA13)
USART1_RX: J1.6, U3.31 (PA10)
USART1_TX: J1.7, U3.30 (PA9)
USB_CONN_D+: J4.A6 (D+), J4.B6 (D+), U4.3 (I/O2)
USB_CONN_D-: J4.A7 (D-), J4.B7 (D-), U4.1 (I/O1)
USB_D+: U3.33 (PA12), U4.4 (I/O2)
USB_D-: U3.32 (PA11), U4.6 (I/O1)
VBATT_ANA: R23.2, R24.1, U3.18 (PB0)
VBATT_MEAS: Q2.1 (G), U3.46 (PB9)
VBUS_SENSE: R20.2, R21.1, U3.45 (PB8)

Notes on the sheet:
Power supply and charger
Solder JP2 and remove R19 to bypass the battery
Short traces
ESD Protection
Short, wide traces for BATT
Battery measurement
VBATT/2
Speaker
USB
Timer 2, CH1-2-3 1mA per LED
As close as possible to the VDDx pins
Plug detection
SDD1306 module
MCU and RBG LED
For power consumption measurement
UC1701X FPC
UC1701X welded
Volume adjustment
Screen connectors
Buttons

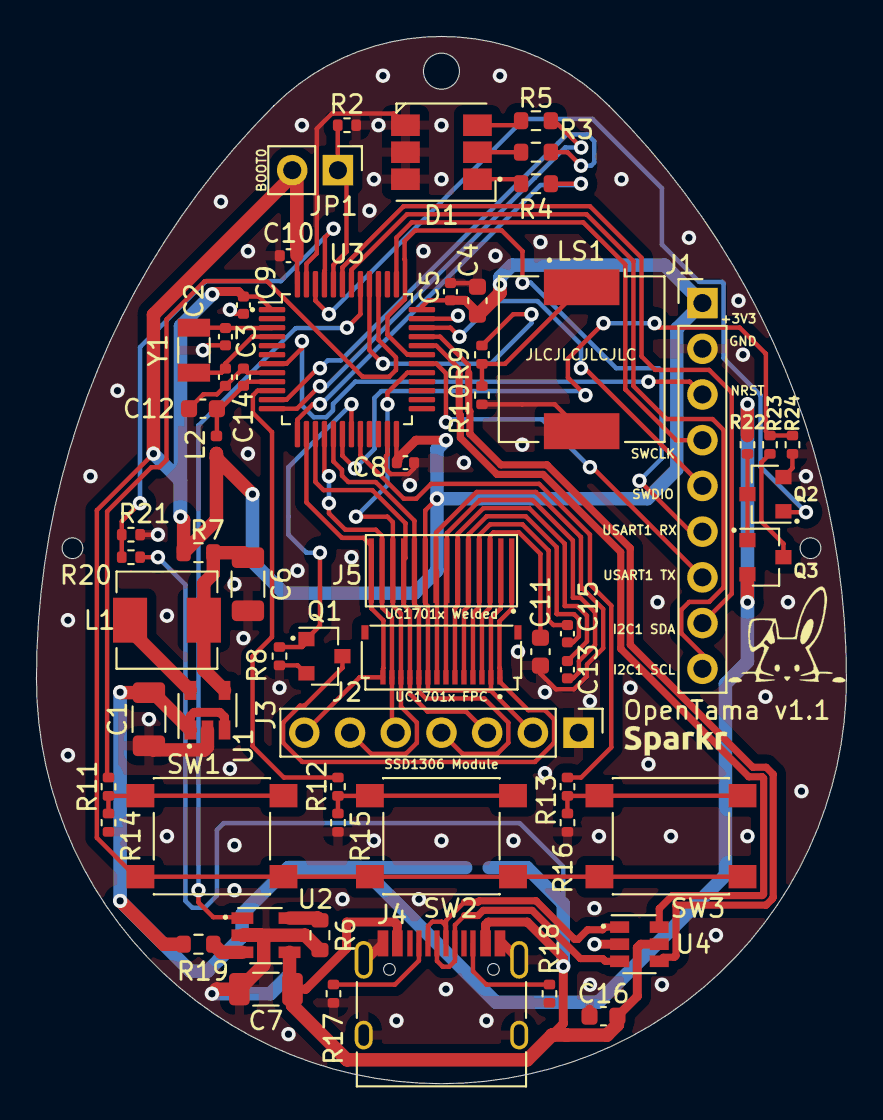
[picture p519: board OpenTama.kicad_pcb from above]

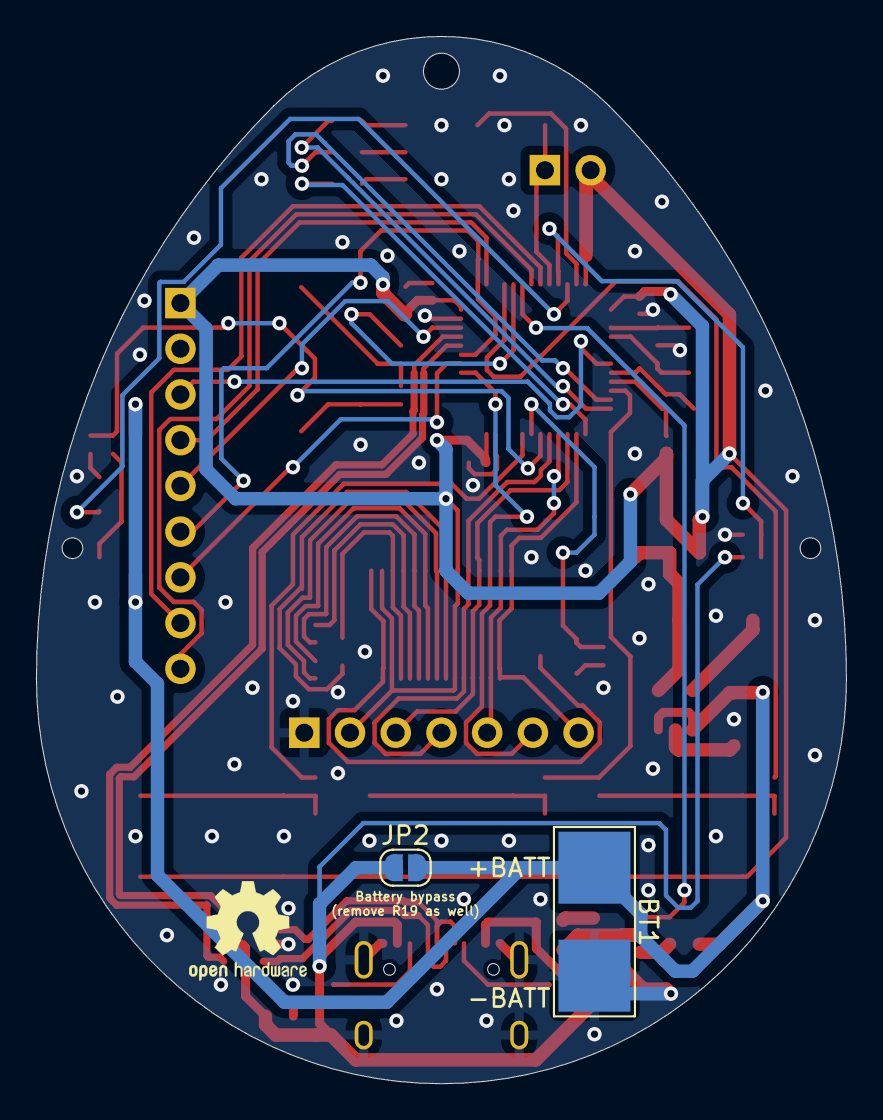
[picture p520: board OpenTama.kicad_pcb from below]

Board: 2 copper layers, 45.0 x 58.2 mm, 62 parts (2 on the bottom side), 57 nets.
