rompasaurus/regardedPal/hardware-design/reference-boards/rp2040-pico-usbc/KiCad Projects/Pico C/RPI-PICO-R3a-PUBLIC.kicad_pcb

## KiCad design hardware-design/reference-boards/rp2040-pico-usbc/KiCad Projects/Pico C/RPI-PICO-R3a-PUBLIC.kicad_pcb (2026-04-15)

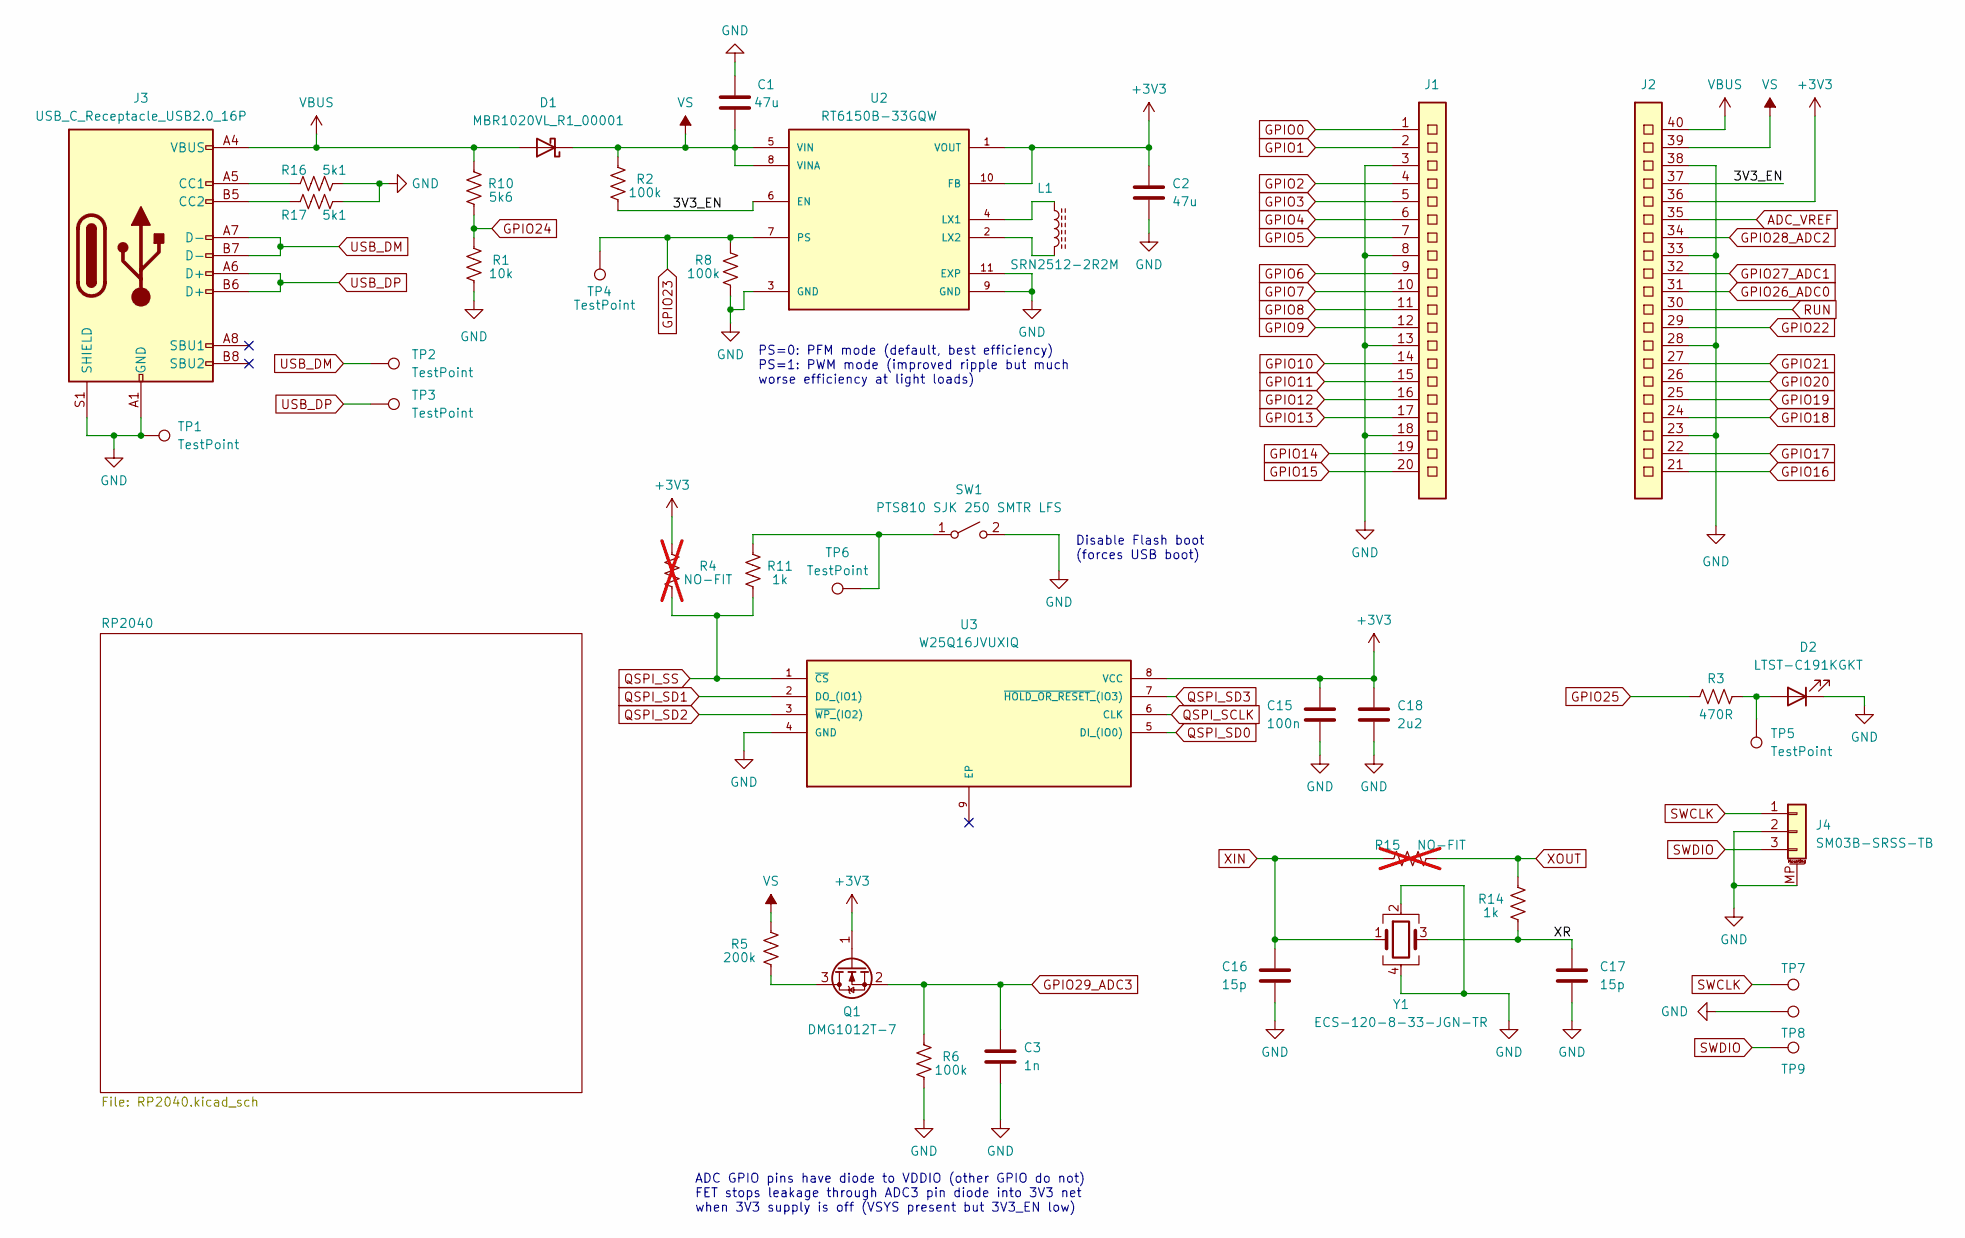
[picture p521: schematic RPI-PICO-R3a-PUBLIC.kicad_sch, project piCo]

Parts:
C1, C2: 47u; C_0805_2012Metric
C3: 1n; C_0201_0603Metric
C15: 100n; C_0201_0603Metric
C16, C17: 15p; C_0201_0603Metric
C18: 2u2; C_0402_1005Metric
D1: MBR1020VL_R1_00001; D_SOD-123F
D2: LTST-C191KGKT; LED_0603_1608Metric
J1: CON_PICO_1-20
J2: CON_PICO_21-40
J3: USB_C_Receptacle_USB2.0_16P; USB_C_Receptacle_GCT_USB4105-xx-A_16P_TopMnt_Horizontal
J4: SM03B-SRSS-TB; JST_SH_SM03B-SRSS-TB_1x03-1MP_P1.00mm_Horizontal
L1: SRN2512-2R2M; L_1008_2520Metric
Q1: DMG1012T-7; SOT-523
R1: 10k; R_0402_1005Metric
R2, R6, R8: 100k; R_0402_1005Metric
R3: 470R; R_0402_1005Metric
R4, R15: NO-FIT; R_0402_1005Metric; not fitted
R5: 200k; R_0402_1005Metric
R10: 5k6; R_0402_1005Metric
R11, R14: 1k; R_0402_1005Metric
R16, R17: 5k1; R_0402_1005Metric
SW1: PTS810 SJK 250 SMTR LFS; SW_SPST_PTS810
TP1, TP2, TP3, TP4, TP5, TP6, TP7, TP8, TP9: TestPoint; TestPoint_Pad_1.5x1.5mm
U2: RT6150B-33GQW; DFN-10-1EP_2.6x2.6mm_P0.5mm_EP1.3x2.2mm
U3: W25Q16JVUXIQ; SON50P300X200X60-9N
Y1: ECS-120-8-33-JGN-TR; Crystal_SMD_SeikoEpson_FA238-4Pin_3.2x2.5mm

Connections:
+3V3: C2.1, C15.1, C18.1, J2.36, Q1.1 (G), R4.2, U2.1 (VOUT), U2.10 (FB), U3.8 (VCC); also elsewhere on the board
/3V3_EN: J2.37, R2.1, U2.6 (EN)
/XR: C17.1, R14.1, Y1.3
ADC_VREF: J2.35; also elsewhere on the board
GND: C1.2, C2.2, C3.2, C15.2, C16.2, C17.2, C18.2, D2.1 (K), J1.3, J1.8, J1.13, J1.18, J2.23, J2.28, J2.33, J2.38, J3.A1 (GND), J3.A12 (GND), J3.B1 (GND), J3.B12 (GND), J3.S1 (SHIELD), J4.2, J4.MP (MountPin), R1.1, R6.1, R8.2, R16.2, R17.2, SW1.2 (B), TP1.1, TP8.1, U2.3 (GND), U2.9 (GND), U2.11 (EXP), U3.4 (GND), Y1.2, Y1.4; also elsewhere on the board
GPIO0: J1.1; also elsewhere on the board
GPIO1: J1.2; also elsewhere on the board
GPIO2: J1.4; also elsewhere on the board
GPIO3: J1.5; also elsewhere on the board
GPIO4: J1.6; also elsewhere on the board
GPIO5: J1.7; also elsewhere on the board
GPIO6: J1.9; also elsewhere on the board
GPIO7: J1.10; also elsewhere on the board
GPIO8: J1.11; also elsewhere on the board
GPIO9: J1.12; also elsewhere on the board
GPIO10: J1.14; also elsewhere on the board
GPIO11: J1.15; also elsewhere on the board
GPIO12: J1.16; also elsewhere on the board
GPIO13: J1.17; also elsewhere on the board
GPIO14: J1.19; also elsewhere on the board
GPIO15: J1.20; also elsewhere on the board
GPIO16: J2.21; also elsewhere on the board
GPIO17: J2.22; also elsewhere on the board
GPIO18: J2.24; also elsewhere on the board
GPIO19: J2.25; also elsewhere on the board
GPIO20: J2.26; also elsewhere on the board
GPIO21: J2.27; also elsewhere on the board
GPIO22: J2.29; also elsewhere on the board
GPIO23: R8.1, TP4.1, U2.7 (PS); also elsewhere on the board
GPIO24: R1.2, R10.1; also elsewhere on the board
GPIO25: R3.1; also elsewhere on the board
GPIO26_ADC0: J2.31; also elsewhere on the board
GPIO27_ADC1: J2.32; also elsewhere on the board
GPIO28_ADC2: J2.34; also elsewhere on the board
GPIO29_ADC3: C3.1, Q1.2 (S), R6.2; also elsewhere on the board
unnamed: D2.2 (A), R3.2, TP5.1
unnamed: J3.A5 (CC1), R16.1
unnamed: J3.B5 (CC2), R17.1
unnamed: Q1.3 (D), R5.1
unnamed: R11.2, SW1.1 (A), TP6.1
unnamed: L1.1, U2.4 (LX1)
unnamed: L1.2, U2.2 (LX2)
QSPI_SCLK: U3.6 (CLK); also elsewhere on the board
QSPI_SD0: U3.5 (DI_(IO0)); also elsewhere on the board
QSPI_SD1: U3.2 (DO_(IO1)); also elsewhere on the board
QSPI_SD2: U3.3 (~WP_(IO2)); also elsewhere on the board
QSPI_SD3: U3.7 (~HOLD_OR_RESET_(IO3)); also elsewhere on the board
QSPI_SS: R4.1, R11.1, U3.1 (~CS); also elsewhere on the board
RUN: J2.30; also elsewhere on the board
SWCLK: J4.1, TP7.1; also elsewhere on the board
SWDIO: J4.3, TP9.1; also elsewhere on the board
USB_DM: J3.A7 (D-), J3.B7 (D-), TP2.1; also elsewhere on the board
USB_DP: J3.A6 (D+), J3.B6 (D+), TP3.1; also elsewhere on the board
VBUS: D1.2 (A), J2.40, J3.A4 (VBUS), J3.A9 (VBUS), J3.B4 (VBUS), J3.B9 (VBUS), R10.2
VS: C1.1, D1.1 (K), J2.39, R2.2, R5.2, U2.5 (VIN), U2.8 (VINA)
XIN: C16.1, R15.1, Y1.1; also elsewhere on the board
XOUT: R14.2, R15.2; also elsewhere on the board

Notes on the sheet:
PS=0: PFM mode (default, best efficiency) PS=1: PWM mode (improved ripple but much worse efficiency at light loads)
ADC GPIO pins have diode to VDDIO (other GPIO do not) FET stops leakage through ADC3 pin diode into 3V3 net when 3V3 supply is off (VSYS present but 3V3_EN low)
Disable Flash boot (forces USB boot)

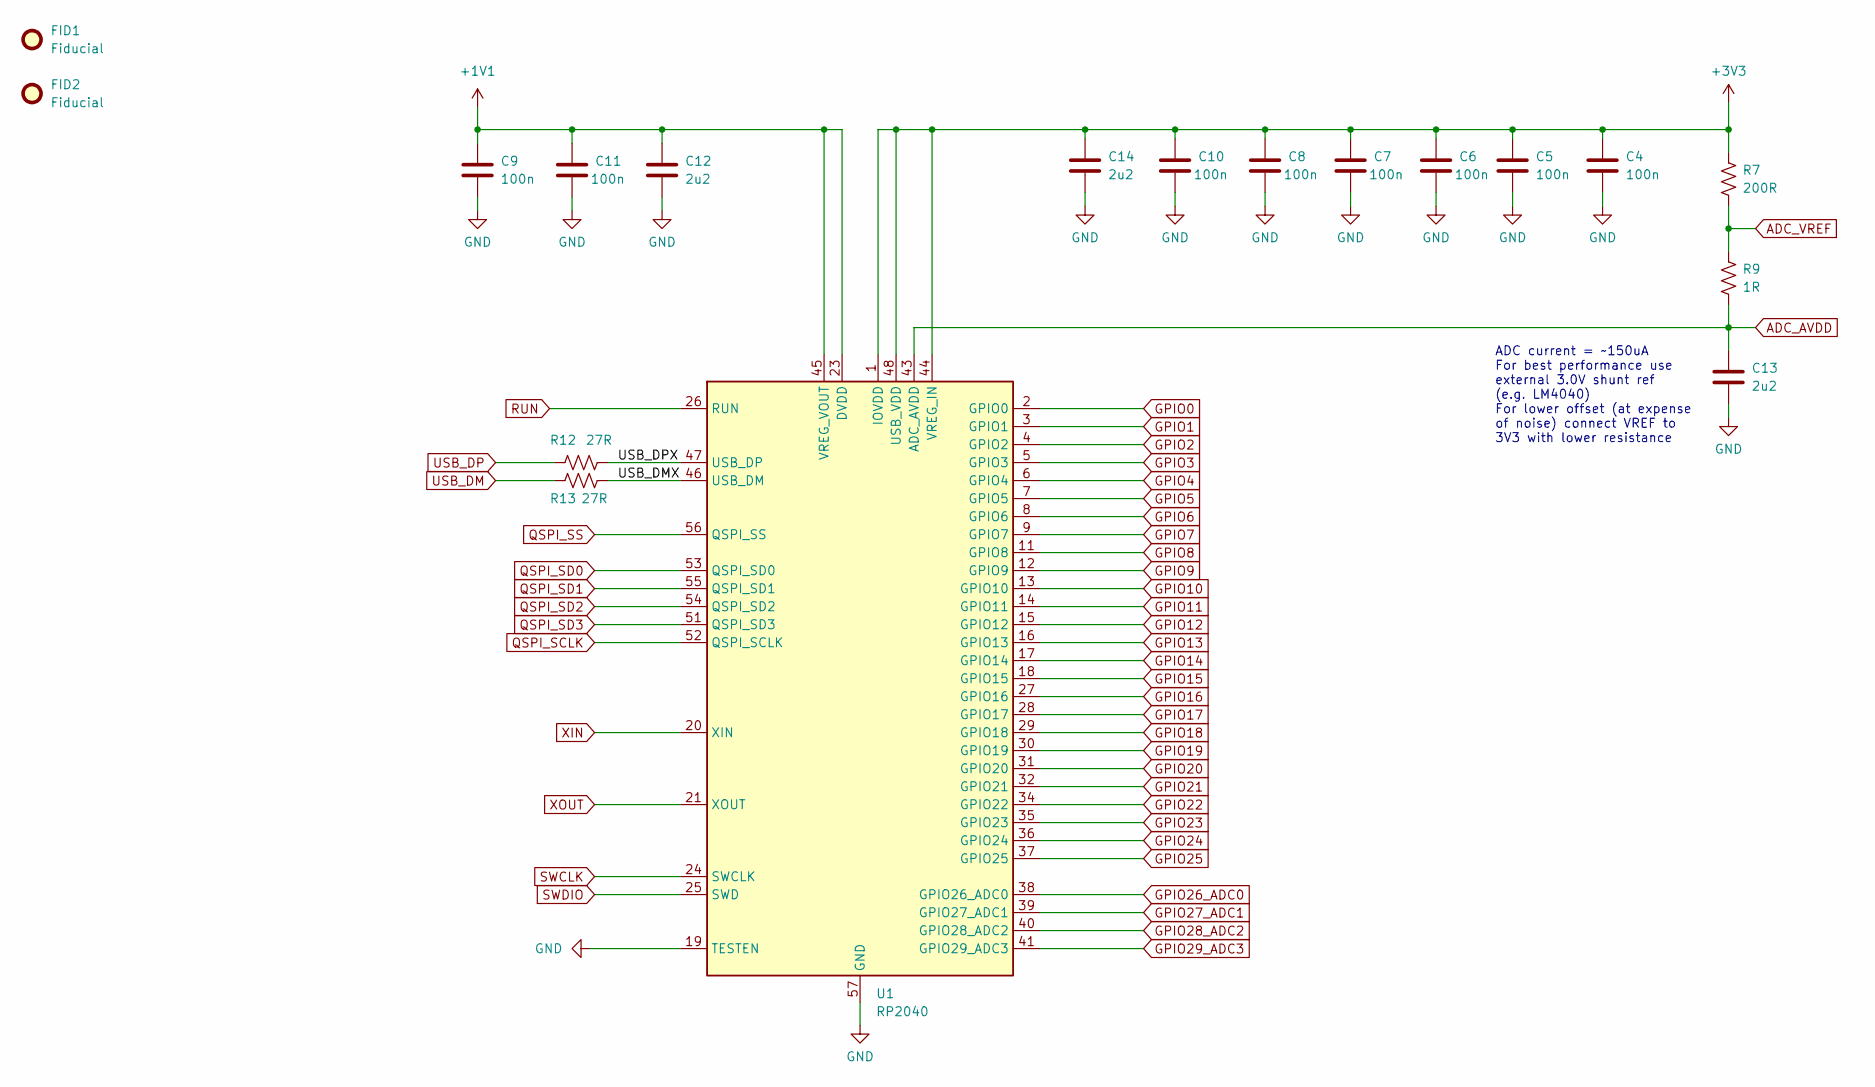
[picture p522: schematic RP2040.kicad_sch, project piCo - RP2040]

Parts:
C4, C5, C6, C7, C8, C9, C10, C11: 100n; C_0201_0603Metric
C12, C13, C14: 2u2; C_0402_1005Metric
FID1, FID2: Fiducial; Fiducial_1mm_Mask2mm
R7: 200R; R_0603_1608Metric
R9: 1R; R_0402_1005Metric
R12, R13: 27R; R_0201_0603Metric
U1: RP2040; QFN-56-1EP_7x7mm_P0.4mm_EP3.2x3.2mm

Connections:
+1V1: C9.1, C11.1, C12.1, U1.23 (DVDD), U1.45 (VREG_VOUT), U1.50 (DVDD)
+3V3: C4.1, C5.1, C6.1, C7.1, C8.1, C10.1, C14.1, R7.1, U1.1 (IOVDD), U1.10 (IOVDD), U1.22 (IOVDD), U1.33 (IOVDD), U1.42 (IOVDD), U1.44 (VREG_IN), U1.48 (USB_VDD), U1.49 (IOVDD); also elsewhere on the board
/RP2040/USB_DMX: R13.2, U1.46 (USB_DM)
/RP2040/USB_DPX: R12.2, U1.47 (USB_DP)
ADC_AVDD: C13.1, R9.2, U1.43 (ADC_AVDD)
ADC_VREF: R7.2, R9.1; also elsewhere on the board
GND: C4.2, C5.2, C6.2, C7.2, C8.2, C9.2, C10.2, C11.2, C12.2, C13.2, C14.2, U1.19 (TESTEN), U1.57 (GND); also elsewhere on the board
GPIO0: U1.2 (GPIO0); also elsewhere on the board
GPIO1: U1.3 (GPIO1); also elsewhere on the board
GPIO2: U1.4 (GPIO2); also elsewhere on the board
GPIO3: U1.5 (GPIO3); also elsewhere on the board
GPIO4: U1.6 (GPIO4); also elsewhere on the board
GPIO5: U1.7 (GPIO5); also elsewhere on the board
GPIO6: U1.8 (GPIO6); also elsewhere on the board
GPIO7: U1.9 (GPIO7); also elsewhere on the board
GPIO8: U1.11 (GPIO8); also elsewhere on the board
GPIO9: U1.12 (GPIO9); also elsewhere on the board
GPIO10: U1.13 (GPIO10); also elsewhere on the board
GPIO11: U1.14 (GPIO11); also elsewhere on the board
GPIO12: U1.15 (GPIO12); also elsewhere on the board
GPIO13: U1.16 (GPIO13); also elsewhere on the board
GPIO14: U1.17 (GPIO14); also elsewhere on the board
GPIO15: U1.18 (GPIO15); also elsewhere on the board
GPIO16: U1.27 (GPIO16); also elsewhere on the board
GPIO17: U1.28 (GPIO17); also elsewhere on the board
GPIO18: U1.29 (GPIO18); also elsewhere on the board
GPIO19: U1.30 (GPIO19); also elsewhere on the board
GPIO20: U1.31 (GPIO20); also elsewhere on the board
GPIO21: U1.32 (GPIO21); also elsewhere on the board
GPIO22: U1.34 (GPIO22); also elsewhere on the board
GPIO23: U1.35 (GPIO23); also elsewhere on the board
GPIO24: U1.36 (GPIO24); also elsewhere on the board
GPIO25: U1.37 (GPIO25); also elsewhere on the board
GPIO26_ADC0: U1.38 (GPIO26_ADC0); also elsewhere on the board
GPIO27_ADC1: U1.39 (GPIO27_ADC1); also elsewhere on the board
GPIO28_ADC2: U1.40 (GPIO28_ADC2); also elsewhere on the board
GPIO29_ADC3: U1.41 (GPIO29_ADC3); also elsewhere on the board
QSPI_SCLK: U1.52 (QSPI_SCLK); also elsewhere on the board
QSPI_SD0: U1.53 (QSPI_SD0); also elsewhere on the board
QSPI_SD1: U1.55 (QSPI_SD1); also elsewhere on the board
QSPI_SD2: U1.54 (QSPI_SD2); also elsewhere on the board
QSPI_SD3: U1.51 (QSPI_SD3); also elsewhere on the board
QSPI_SS: U1.56 (QSPI_SS); also elsewhere on the board
RUN: U1.26 (RUN); also elsewhere on the board
SWCLK: U1.24 (SWCLK); also elsewhere on the board
SWDIO: U1.25 (SWD); also elsewhere on the board
USB_DM: R13.1; also elsewhere on the board
USB_DP: R12.1; also elsewhere on the board
XIN: U1.20 (XIN); also elsewhere on the board
XOUT: U1.21 (XOUT); also elsewhere on the board

Notes on the sheet:
ADC current = ~150uA For best performance use external 3.0V shunt ref (e.g. LM4040) For lower offset (at expense of noise) connect VREF to 3V3 with lower resistance

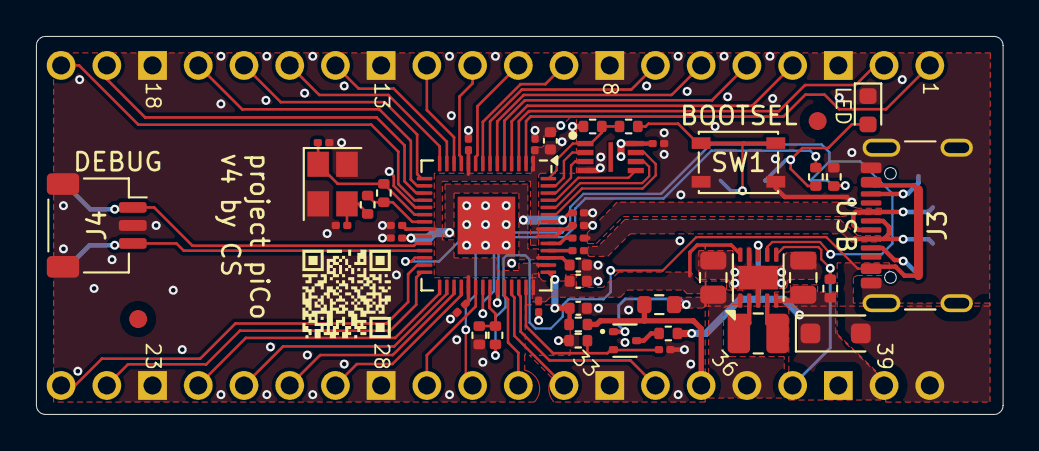
[picture p523: board RPI-PICO-R3a-PUBLIC.kicad_pcb from above]

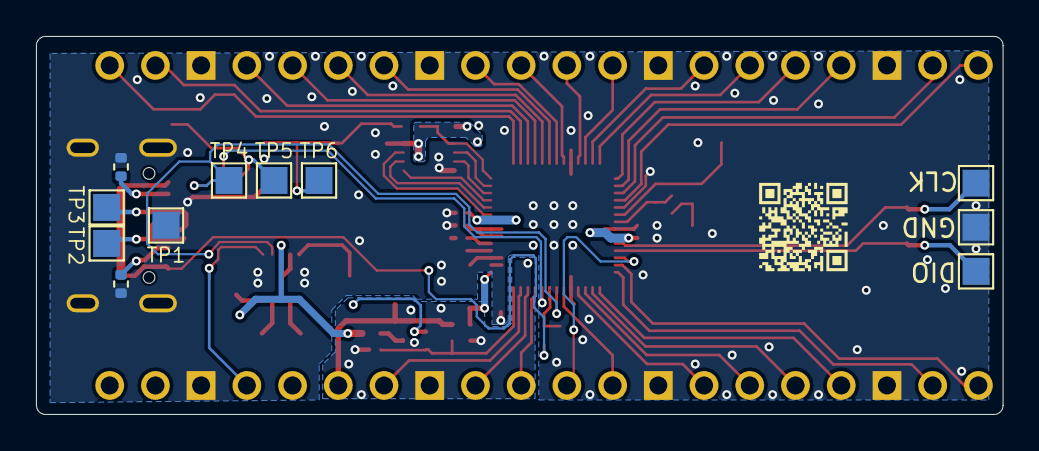
[picture p524: board RPI-PICO-R3a-PUBLIC.kicad_pcb from below]

Board: 2 copper layers, 53.7 x 21.0 mm, 59 parts (11 on the bottom side), 61 nets.
