rompasaurus/regardedPal/hardware-design/reference-boards/rp2040-pico-usbc/KiCad Projects/Pico WH - No License/Pico WH.kicad_pcb

## KiCad design hardware-design/reference-boards/rp2040-pico-usbc/KiCad Projects/Pico WH - No License/Pico WH.kicad_pcb (2026-04-15)

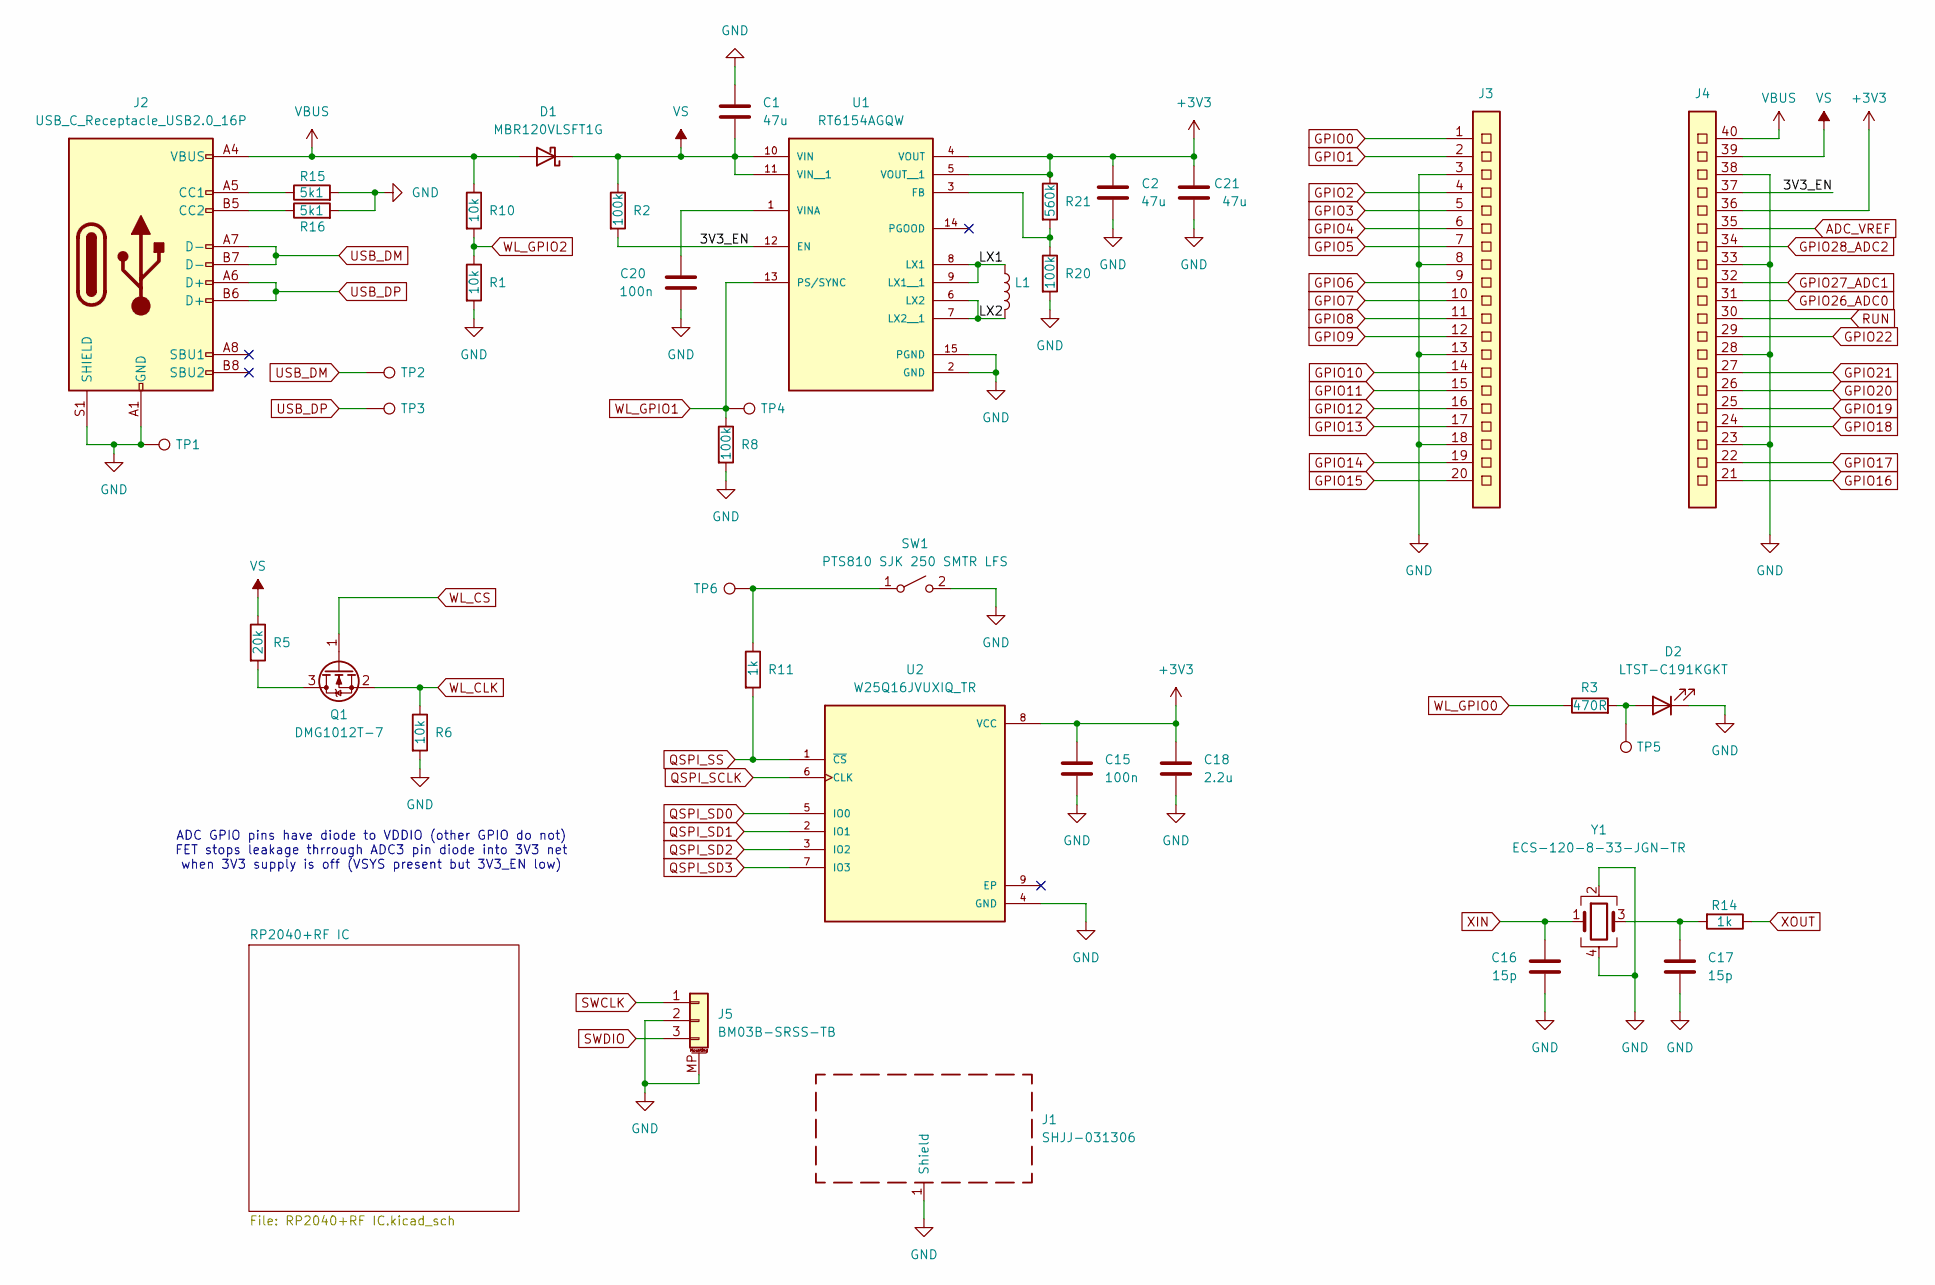
[picture p525: schematic Pico WH.kicad_sch, project piCo W]

Parts:
C1, C2, C21: 47u; C_0805_2012Metric
C15, C20: 100n; C_0201_0603Metric
C16, C17: 15p; C_0201_0603Metric
C18: 2.2u; C_0402_1005Metric
D1: MBR120VLSFT1G; D_SOD-123F
D2: LTST-C191KGKT; LED_0603_1608Metric
J1: SHJJ-031306; RF_SHIELD_PICOW
J2: USB_C_Receptacle_USB2.0_16P; USB_C_Receptacle_GCT_USB4105-xx-A_16P_TopMnt_Horizontal
J3: CON_PICO_1-20
J4: CON_PICO_21-40
J5: BM03B-SRSS-TB; JST_SH_BM03B-SRSS-TB_1x03-1MP_P1.00mm_Vertical
L1: SRN2512-1R0M; L_1008_2520Metric
Q1: DMG1012T-7; SOT-523
R1, R6, R10: 10k; R_0201_0603Metric
R2, R8, R20: 100k; R_0201_0603Metric
R3: 470R; R_0201_0603Metric
R5: 20k; R_0201_0603Metric
R11, R14: 1k; R_0201_0603Metric
R15, R16: 5k1; R_0402_1005Metric
R21: 560k; R_0201_0603Metric
SW1: PTS810 SJK 250 SMTR LFS; SW_SPST_PTS810
TP1, TP2, TP3, TP4, TP5, TP6: TestPoint; TestPoint_Pad_1.5x1.5mm
U1: RT6154AGQW; DFN-14-1EP_3x4mm_P0.5mm_EP1.7x3.3mm
U2: W25Q16JVUXIQ_TR; TDFN-8-1EP_3x2mm_P0.5mm_EP1.3x1.4mm
Y1: ECS-120-8-33-JGN-TR; Crystal_SMD_SeikoEpson_FA238-4Pin_3.2x2.5mm

Connections:
+3V3: C2.1, C15.1, C18.1, C21.1, J4.36, R21.1, U1.4 (VOUT), U1.5 (VOUT__1), U2.8 (VCC); also elsewhere on the board
/3V3_EN: J4.37, R2.2, U1.12 (EN)
/LX1: L1.1, U1.8 (LX1), U1.9 (LX1__1)
/LX2: L1.2, U1.6 (LX2), U1.7 (LX2__1)
ADC_VREF: J4.35; also elsewhere on the board
GND: C1.2, C2.2, C15.2, C16.2, C17.2, C18.2, C20.2, C21.2, D2.1 (K), J1.1 (Shield), J2.A1 (GND), J2.A12 (GND), J2.B1 (GND), J2.B12 (GND), J2.S1 (SHIELD), J3.3, J3.8, J3.13, J3.18, J4.23, J4.28, J4.33, J4.38, J5.2, J5.MP (MountPin), R1.2, R6.2, R8.2, R15.2, R16.2, R20.2, SW1.2 (B), TP1.1, U1.2 (GND), U1.15 (PGND), U2.4 (GND), Y1.2, Y1.4; also elsewhere on the board
GPIO0: J3.1; also elsewhere on the board
GPIO1: J3.2; also elsewhere on the board
GPIO2: J3.4; also elsewhere on the board
GPIO3: J3.5; also elsewhere on the board
GPIO4: J3.6; also elsewhere on the board
GPIO5: J3.7; also elsewhere on the board
GPIO6: J3.9; also elsewhere on the board
GPIO7: J3.10; also elsewhere on the board
GPIO8: J3.11; also elsewhere on the board
GPIO9: J3.12; also elsewhere on the board
GPIO10: J3.14; also elsewhere on the board
GPIO11: J3.15; also elsewhere on the board
GPIO12: J3.16; also elsewhere on the board
GPIO13: J3.17; also elsewhere on the board
GPIO14: J3.19; also elsewhere on the board
GPIO15: J3.20; also elsewhere on the board
GPIO16: J4.21; also elsewhere on the board
GPIO17: J4.22; also elsewhere on the board
GPIO18: J4.24; also elsewhere on the board
GPIO19: J4.25; also elsewhere on the board
GPIO20: J4.26; also elsewhere on the board
GPIO21: J4.27; also elsewhere on the board
GPIO22: J4.29; also elsewhere on the board
GPIO26_ADC0: J4.31; also elsewhere on the board
GPIO27_ADC1: J4.32; also elsewhere on the board
GPIO28_ADC2: J4.34; also elsewhere on the board
unnamed: C17.1, R14.2, Y1.3
unnamed: D2.2 (A), R3.2, TP5.1
unnamed: J2.A5 (CC1), R15.1
unnamed: J2.B5 (CC2), R16.1
unnamed: Q1.3 (D), R5.2
unnamed: R11.1, SW1.1 (A), TP6.1
unnamed: R20.1, R21.2, U1.3 (FB)
unnamed: C20.1, U1.1 (VINA)
QSPI_SCLK: U2.6 (CLK); also elsewhere on the board
QSPI_SD0: U2.5 (IO0); also elsewhere on the board
QSPI_SD1: U2.2 (IO1); also elsewhere on the board
QSPI_SD2: U2.3 (IO2); also elsewhere on the board
QSPI_SD3: U2.7 (IO3); also elsewhere on the board
QSPI_SS: R11.2, U2.1 (~CS); also elsewhere on the board
RUN: J4.30; also elsewhere on the board
SWCLK: J5.1; also elsewhere on the board
SWDIO: J5.3; also elsewhere on the board
USB_DM: J2.A7 (D-), J2.B7 (D-), TP2.1; also elsewhere on the board
USB_DP: J2.A6 (D+), J2.B6 (D+), TP3.1; also elsewhere on the board
VBUS: D1.2 (A), J2.A4 (VBUS), J2.A9 (VBUS), J2.B4 (VBUS), J2.B9 (VBUS), J4.40, R10.1
VS: C1.1, D1.1 (K), J4.39, R2.1, R5.1, U1.10 (VIN), U1.11 (VIN__1)
WL_CLK: Q1.2 (S), R6.1; also elsewhere on the board
WL_CS: Q1.1 (G); also elsewhere on the board
WL_GPIO0: R3.1; also elsewhere on the board
WL_GPIO1: R8.1, TP4.1, U1.13 (PS/SYNC); also elsewhere on the board
WL_GPIO2: R1.1, R10.2; also elsewhere on the board
XIN: C16.1, Y1.1; also elsewhere on the board
XOUT: R14.1; also elsewhere on the board

Notes on the sheet:
ADC GPIO pins have diode to VDDIO (other GPIO do not) FET stops leakage thrrough ADC3 pin diode into 3V3 net when 3V3 supply is off (VSYS present but 3V3_EN low)

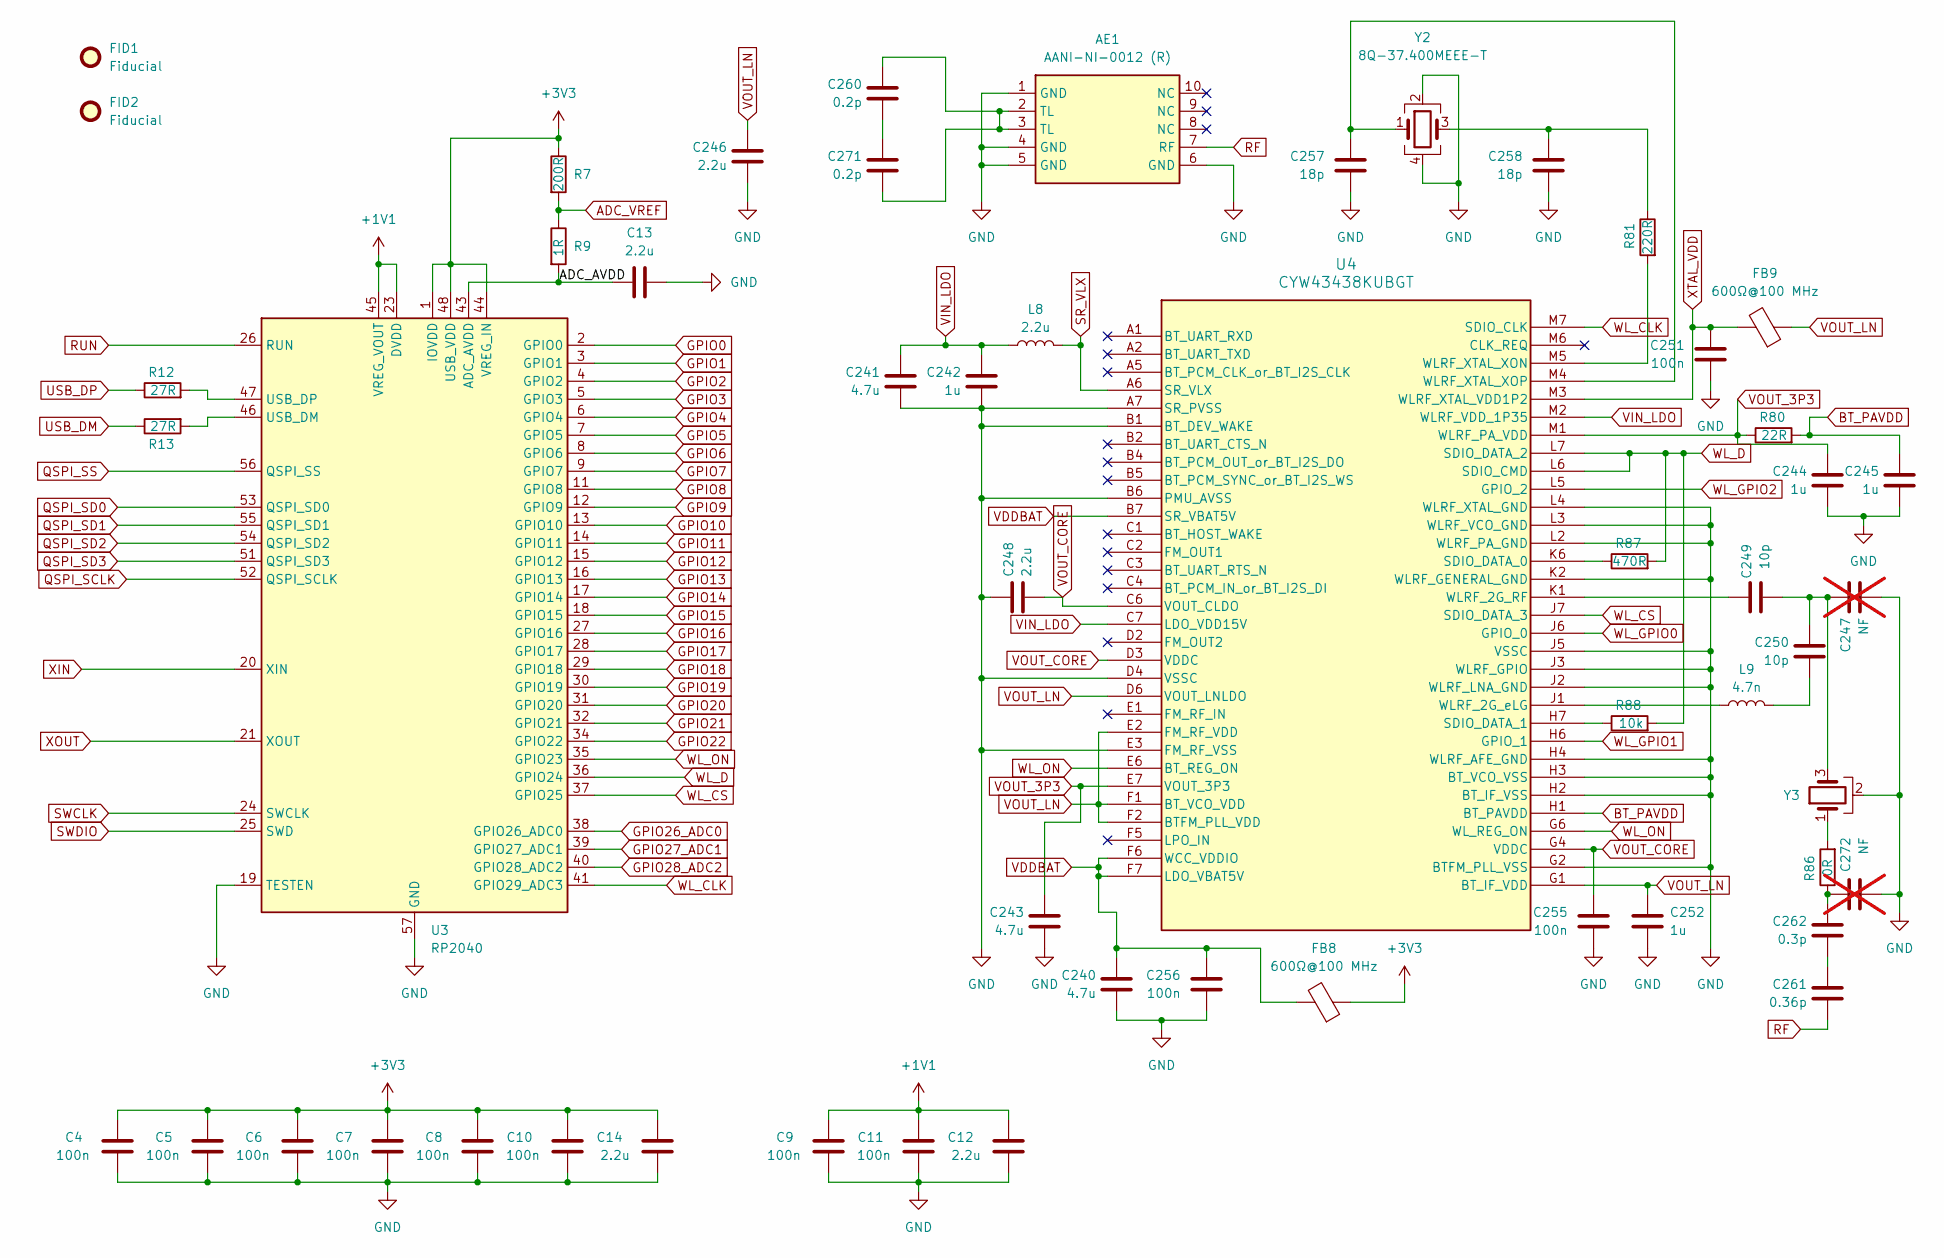
[picture p526: schematic RP2040+RF IC.kicad_sch, project piCo W - RP2040+RF IC]

Parts:
AE1: AANI-NI-0012 (R); AANI-NI-0012
C4, C5, C6, C7, C8, C9, C10, C11, C251, C255, C256: 100n; C_0201_0603Metric
C12, C13, C14, C246, C248: 2.2u; C_0402_1005Metric
C240, C241, C243: 4.7u; C_0402_1005Metric
C242, C244, C245, C252: 1u; C_0201_0603Metric
C247, C272: NF; C_0201_0603Metric; not fitted
C249, C250: 10p; C_0201_0603Metric
C257, C258: 18p; C_0201_0603Metric
C260, C271: 0.2p; C_0402_1005Metric
C261: 0.36p; C_0402_1005Metric
C262: 0.3p; C_0402_1005Metric
FB8: 600Ω@100 MHz; L_0603_1608Metric
FB9: 600Ω@100 MHz; L_0201_0603Metric
FID1, FID2: Fiducial; Fiducial_1mm_Mask2mm
L8: 2.2u; L_0603_1608Metric
L9: 4.7n; L_0201_0603Metric
R7: 200R; R_0603_1608Metric
R9: 1R; R_0402_1005Metric
R12, R13: 27R; R_0201_0603Metric
R80: 22R; R_0201_0603Metric
R81: 220R; R_0201_0603Metric
R86: 0R; R_0201_0603Metric
R87: 470R; R_0201_0603Metric
R88: 10k; R_0201_0603Metric
U3: RP2040; QFN-56-1EP_7x7mm_P0.4mm_EP3.2x3.2mm
U4: CYW43438KUBGT; BGA-63
Y2: 8Q-37.400MEEE-T; Oscillator_SMD_Abracon_ASCO-4Pin_1.6x1.2mm
Y3: LFB212G45CG7D227; FILS3_MUR_LFB21XXCG2Q

Connections:
+1V1: C9.1, C11.1, C12.1, U3.23 (DVDD), U3.45 (VREG_VOUT), U3.50 (DVDD)
+3V3: C4.1, C5.1, C6.1, C7.1, C8.1, C10.1, C14.1, FB8.1, R7.1, U3.1 (IOVDD), U3.10 (IOVDD), U3.22 (IOVDD), U3.33 (IOVDD), U3.42 (IOVDD), U3.44 (VREG_IN), U3.48 (USB_VDD), U3.49 (IOVDD); also elsewhere on the board
/RP2040+RF IC/ADC_AVDD: C13.1, R9.2, U3.43 (ADC_AVDD)
ADC_VREF: R7.2, R9.1; also elsewhere on the board
BT_PAVDD: C245.1, R80.2, U4.H1 (BT_PAVDD)
GND: AE1.1 (GND), AE1.4 (GND), AE1.5 (GND), AE1.6 (GND), C4.2, C5.2, C6.2, C7.2, C8.2, C9.2, C10.2, C11.2, C12.2, C13.2, C14.2, C240.2, C241.2, C242.2, C243.2, C244.2, C245.2, C246.2, C247.1, C248.2, C251.2, C252.2, C255.2, C256.2, C257.2, C258.2, C272.2, U3.19 (TESTEN), U3.57 (GND), U4.A7 (SR_PVSS), U4.B1 (BT_DEV_WAKE), U4.B6 (PMU_AVSS), U4.D4 (VSSC), U4.E3 (FM_RF_VSS), U4.G2 (BTFM_PLL_VSS), U4.H2 (BT_IF_VSS), U4.H3 (BT_VCO_VSS), U4.H4 (WLRF_AFE_GND), U4.J2 (WLRF_LNA_GND), U4.J3 (WLRF_GPIO), U4.J5 (VSSC), U4.K2 (WLRF_GENERAL_GND), U4.L2 (WLRF_PA_GND), U4.L3 (WLRF_VCO_GND), U4.L4 (WLRF_XTAL_GND), Y2.2, Y2.4, Y3.2; also elsewhere on the board
GPIO0: U3.2 (GPIO0); also elsewhere on the board
GPIO1: U3.3 (GPIO1); also elsewhere on the board
GPIO2: U3.4 (GPIO2); also elsewhere on the board
GPIO3: U3.5 (GPIO3); also elsewhere on the board
GPIO4: U3.6 (GPIO4); also elsewhere on the board
GPIO5: U3.7 (GPIO5); also elsewhere on the board
GPIO6: U3.8 (GPIO6); also elsewhere on the board
GPIO7: U3.9 (GPIO7); also elsewhere on the board
GPIO8: U3.11 (GPIO8); also elsewhere on the board
GPIO9: U3.12 (GPIO9); also elsewhere on the board
GPIO10: U3.13 (GPIO10); also elsewhere on the board
GPIO11: U3.14 (GPIO11); also elsewhere on the board
GPIO12: U3.15 (GPIO12); also elsewhere on the board
GPIO13: U3.16 (GPIO13); also elsewhere on the board
GPIO14: U3.17 (GPIO14); also elsewhere on the board
GPIO15: U3.18 (GPIO15); also elsewhere on the board
GPIO16: U3.27 (GPIO16); also elsewhere on the board
GPIO17: U3.28 (GPIO17); also elsewhere on the board
GPIO18: U3.29 (GPIO18); also elsewhere on the board
GPIO19: U3.30 (GPIO19); also elsewhere on the board
GPIO20: U3.31 (GPIO20); also elsewhere on the board
GPIO21: U3.32 (GPIO21); also elsewhere on the board
GPIO22: U3.34 (GPIO22); also elsewhere on the board
GPIO26_ADC0: U3.38 (GPIO26_ADC0); also elsewhere on the board
GPIO27_ADC1: U3.39 (GPIO27_ADC1); also elsewhere on the board
GPIO28_ADC2: U3.40 (GPIO28_ADC2); also elsewhere on the board
unnamed: AE1.2 (TL), AE1.3 (TL), C260.1, C271.2
unnamed: C247.2, C249.1, C250.1, Y3.3
unnamed: C250.2, L9.1
unnamed: C258.1, R81.1, Y2.3
unnamed: C260.2, C271.1
unnamed: C261.1, C262.1
unnamed: C262.2, C272.1, R86.1
unnamed: R86.2, Y3.1
unnamed: R13.2, U3.46 (USB_DM)
unnamed: R12.2, U3.47 (USB_DP)
unnamed: R87.1, U4.K6 (SDIO_DATA_0)
unnamed: R88.1, U4.H7 (SDIO_DATA_1)
unnamed: C249.2, U4.K1 (WLRF_2G_RF)
unnamed: L9.2, U4.J1 (WLRF_2G_eLG)
unnamed: R81.2, U4.M5 (WLRF_XTAL_XON)
unnamed: C257.1, U4.M4 (WLRF_XTAL_XOP), Y2.1
QSPI_SCLK: U3.52 (QSPI_SCLK); also elsewhere on the board
QSPI_SD0: U3.53 (QSPI_SD0); also elsewhere on the board
QSPI_SD1: U3.55 (QSPI_SD1); also elsewhere on the board
QSPI_SD2: U3.54 (QSPI_SD2); also elsewhere on the board
QSPI_SD3: U3.51 (QSPI_SD3); also elsewhere on the board
QSPI_SS: U3.56 (QSPI_SS); also elsewhere on the board
RF: AE1.7 (RF), C261.2
RUN: U3.26 (RUN); also elsewhere on the board
SR_VLX: L8.1, U4.A6 (SR_VLX)
SWCLK: U3.24 (SWCLK); also elsewhere on the board
SWDIO: U3.25 (SWD); also elsewhere on the board
USB_DM: R13.1; also elsewhere on the board
USB_DP: R12.1; also elsewhere on the board
VDDBAT: C240.1, C256.1, FB8.2, U4.B7 (SR_VBAT5V), U4.F6 (WCC_VDDIO), U4.F7 (LDO_VBAT5V)
VIN_LDO: C241.1, C242.1, L8.2, U4.C7 (LDO_VDD15V), U4.M2 (WLRF_VDD_1P35)
VOUT_3P3: C243.1, C244.1, R80.1, U4.E7 (VOUT_3P3), U4.M1 (WLRF_PA_VDD)
VOUT_CORE: C248.1, C255.1, U4.C6 (VOUT_CLDO), U4.D3 (VDDC), U4.G4 (VDDC)
VOUT_LN: C246.1, C252.1, FB9.1, U4.D6 (VOUT_LNLDO), U4.E2 (FM_RF_VDD), U4.F1 (BT_VCO_VDD), U4.F2 (BTFM_PLL_VDD), U4.G1 (BT_IF_VDD)
WL_CLK: U3.41 (GPIO29_ADC3), U4.M7 (SDIO_CLK); also elsewhere on the board
WL_CS: U3.37 (GPIO25), U4.J7 (SDIO_DATA_3); also elsewhere on the board
WL_D: R87.2, R88.2, U3.36 (GPIO24), U4.L6 (SDIO_CMD), U4.L7 (SDIO_DATA_2)
WL_GPIO0: U4.J6 (GPIO_0); also elsewhere on the board
WL_GPIO1: U4.H6 (GPIO_1); also elsewhere on the board
WL_GPIO2: U4.L5 (GPIO_2); also elsewhere on the board
WL_ON: U3.35 (GPIO23), U4.E6 (BT_REG_ON), U4.G6 (WL_REG_ON)
XIN: U3.20 (XIN); also elsewhere on the board
XOUT: U3.21 (XOUT); also elsewhere on the board
XTAL_VDD: C251.1, FB9.2, U4.M3 (WLRF_XTAL_VDD1P2)

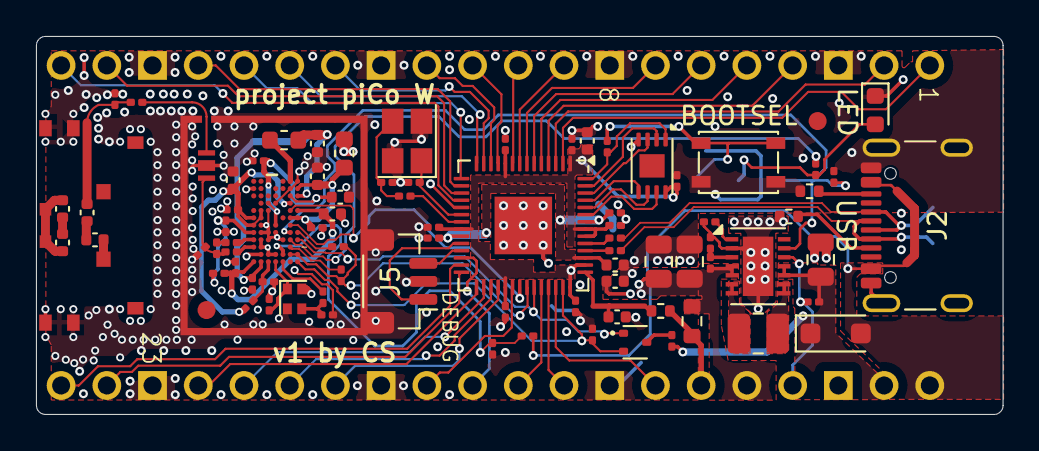
[picture p527: board Pico WH.kicad_pcb from above]

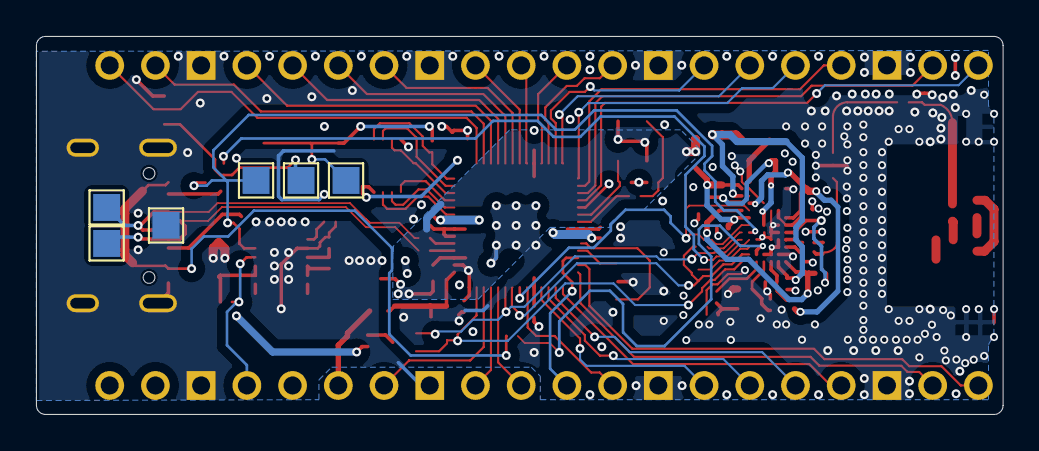
[picture p528: board Pico WH.kicad_pcb from below]

Board: 4 copper layers, 53.7 x 21.0 mm, 93 parts (6 on the bottom side), 89 nets.
