rompasaurus/regardedPal/hardware-design/reference-boards/rp2040-designguide/PCB/RP2040-Guide.kicad_pcb

## KiCad design hardware-design/reference-boards/rp2040-designguide/PCB/RP2040-Guide.kicad_pcb (2026-04-15)

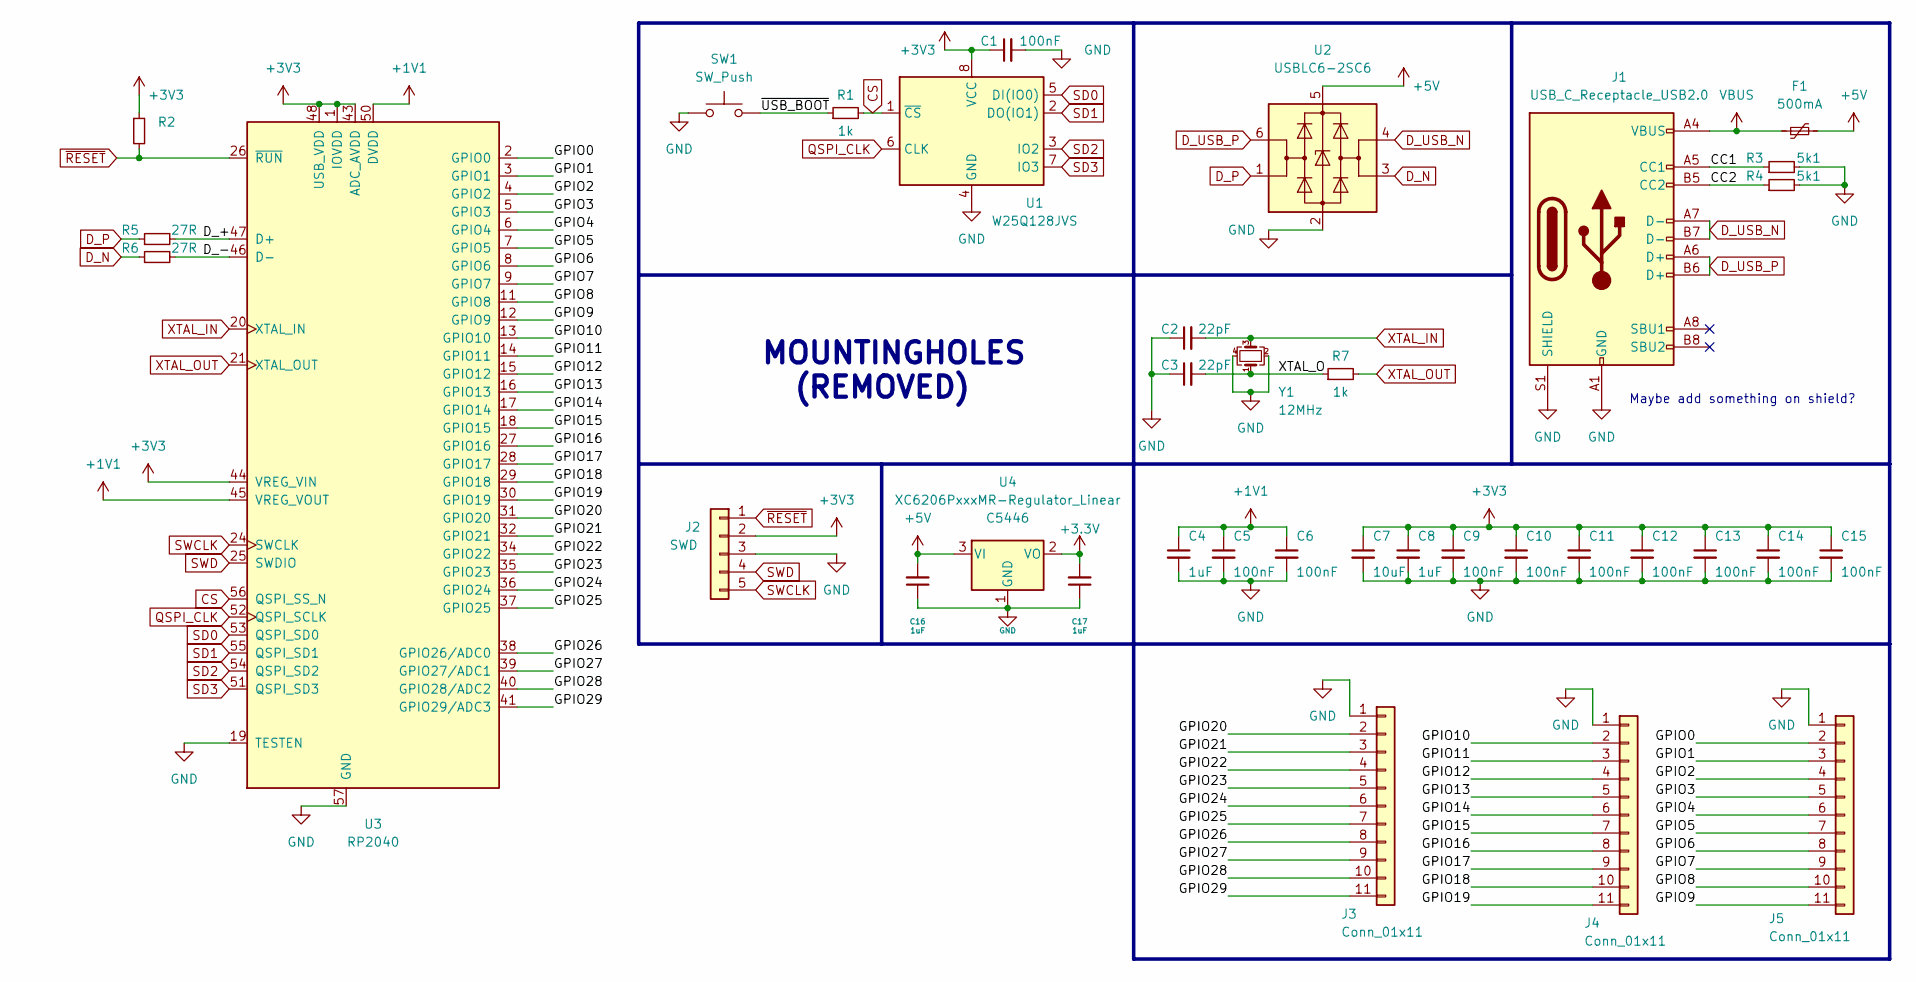
[picture p529: schematic RP2040-Guide.kicad_sch, RP2040 - Design Guide]

Parts:
C1, C5, C6, C9, C10, C11, C12, C13, C14, C15: 100nF; C_0402_1005Metric; LCSC C1525
C2, C3: 22pF; C_0402_1005Metric; LCSC C1555
C4, C8, C16, C17: 1uF; C_0402_1005Metric; LCSC C52923
C7: 10uF; C_0402_1005Metric; LCSC C15525
F1: 500mA; Fuse_1206_3216Metric; LCSC C70076
J1: USB_C_Receptacle_USB2.0; USB_C_Receptacle_HRO_TYPE-C-31-M-12; LCSC C165948
J2: SWD; PinSocket_1x05_P2.54mm_Vertical
J3, J4, J5: Conn_01x11; PinSocket_1x11_P2.54mm_Vertical
R1, R7: 1k; R_0402_1005Metric; LCSC C11702
R2: LCSC C11702
R3, R4: 5k1; R_0402_1005Metric; LCSC C25905
R5, R6: 27R; R_0603_1608Metric; LCSC C25190
SW1: SW_Push; PinSocket_1x02_P2.54mm_Vertical
U1: W25Q128JVS; SOIC-8_5.23x5.23mm_P1.27mm; LCSC C131025
U2: USBLC6-2SC6; SOT-23-6; LCSC C2827654
U3: RP2040; RP2040-QFN-56; LCSC C2040
U4: XC6206PxxxMR-Regulator_Linear; SOT-23; LCSC C5446
Y1: 12MHz; Crystal_SMD_3225-4Pin_3.2x2.5mm; LCSC C9002

Connections:
+1V1: C4.1, C5.1, C6.1, U3.23 (DVDD), U3.45 (VREG_VOUT), U3.50 (DVDD)
+5V: C16.2, F1.2, U2.5 (VBUS), U4.3 (VI)
/CC1: J1.A5 (CC1), R3.1
/CC2: J1.B5 (CC2), R4.1
/D_+: R5.2, U3.47 (D+)
/D_-: R6.2, U3.46 (D-)
/GPIO0: J5.2, U3.2 (GPIO0)
/GPIO1: J5.3, U3.3 (GPIO1)
/GPIO2: J5.4, U3.4 (GPIO2)
/GPIO3: J5.5, U3.5 (GPIO3)
/GPIO4: J5.6, U3.6 (GPIO4)
/GPIO5: J5.7, U3.7 (GPIO5)
/GPIO6: J5.8, U3.8 (GPIO6)
/GPIO7: J5.9, U3.9 (GPIO7)
/GPIO8: J5.10, U3.11 (GPIO8)
/GPIO9: J5.11, U3.12 (GPIO9)
/GPIO10: J4.2, U3.13 (GPIO10)
/GPIO11: J4.3, U3.14 (GPIO11)
/GPIO12: J4.4, U3.15 (GPIO12)
/GPIO13: J4.5, U3.16 (GPIO13)
/GPIO14: J4.6, U3.17 (GPIO14)
/GPIO15: J4.7, U3.18 (GPIO15)
/GPIO16: J4.8, U3.27 (GPIO16)
/GPIO17: J4.9, U3.28 (GPIO17)
/GPIO18: J4.10, U3.29 (GPIO18)
/GPIO19: J4.11, U3.30 (GPIO19)
/GPIO20: J3.2, U3.31 (GPIO20)
/GPIO21: J3.3, U3.32 (GPIO21)
/GPIO22: J3.4, U3.34 (GPIO22)
/GPIO23: J3.5, U3.35 (GPIO23)
/GPIO24: J3.6, U3.36 (GPIO24)
/GPIO25: J3.7, U3.37 (GPIO25)
/GPIO26: J3.8, U3.38 (GPIO26/ADC0)
/GPIO27: J3.9, U3.39 (GPIO27/ADC1)
/GPIO28: J3.10, U3.40 (GPIO28/ADC2)
/GPIO29: J3.11, U3.41 (GPIO29/ADC3)
/XTAL_O: C3.2, R7.1, Y1.1
/~USB_BOOT: R1.1, SW1.2
CS: R1.2, U1.1 (~CS), U3.56 (QSPI_SS_N)
D_N: R6.1, U2.3 (I/O2)
D_P: R5.1, U2.1 (I/O1)
D_USB_N: J1.A7 (D-), J1.B7 (D-), U2.4 (I/O2)
D_USB_P: J1.A6 (D+), J1.B6 (D+), U2.6 (I/O1)
GND: C1.2, C2.1, C3.1, C4.2, C5.2, C6.2, C7.2, C8.2, C9.2, C10.2, C11.2, C12.2, C13.2, C14.2, C15.2, C16.1, C17.1, J1.A1 (GND), J1.A12 (GND), J1.B1 (GND), J1.B12 (GND), J1.S1 (SHIELD), J2.3, J3.1, J4.1, J5.1, R3.2, R4.2, SW1.1, U1.4 (GND), U2.2 (GND), U3.19 (TESTEN), U3.57 (GND), U4.1 (GND), Y1.2, Y1.4
QSPI_CLK: U1.6 (CLK), U3.52 (QSPI_SCLK)
SD0: U1.5 (DI(IO0)), U3.53 (QSPI_SD0)
SD1: U1.2 (DO(IO1)), U3.55 (QSPI_SD1)
SD2: U1.3 (IO2), U3.54 (QSPI_SD2)
SD3: U1.7 (IO3), U3.51 (QSPI_SD3)
SWCLK: J2.5, U3.24 (SWCLK)
SWD: J2.4, U3.25 (SWDIO)
VBUS: F1.1, J1.A4 (VBUS), J1.A9 (VBUS), J1.B4 (VBUS), J1.B9 (VBUS)
XTAL_IN: C2.2, U3.20 (XTAL_IN), Y1.3
XTAL_OUT: R7.2, U3.21 (XTAL_OUT)
~RESET: J2.1, R2.2, U3.26 (~RUN)

Notes on the sheet:
MOUNTINGHOLES (REMOVED)
Maybe add something on shield?

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
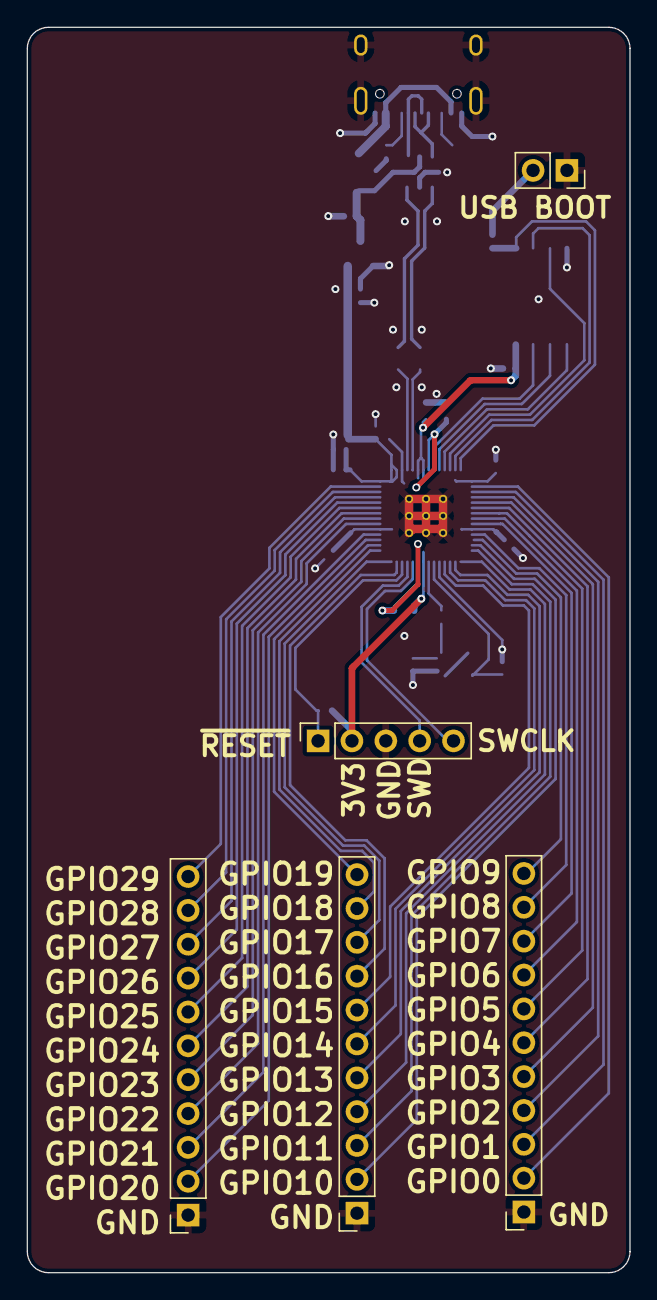
[picture p530: board RP2040-Guide.kicad_pcb from above]

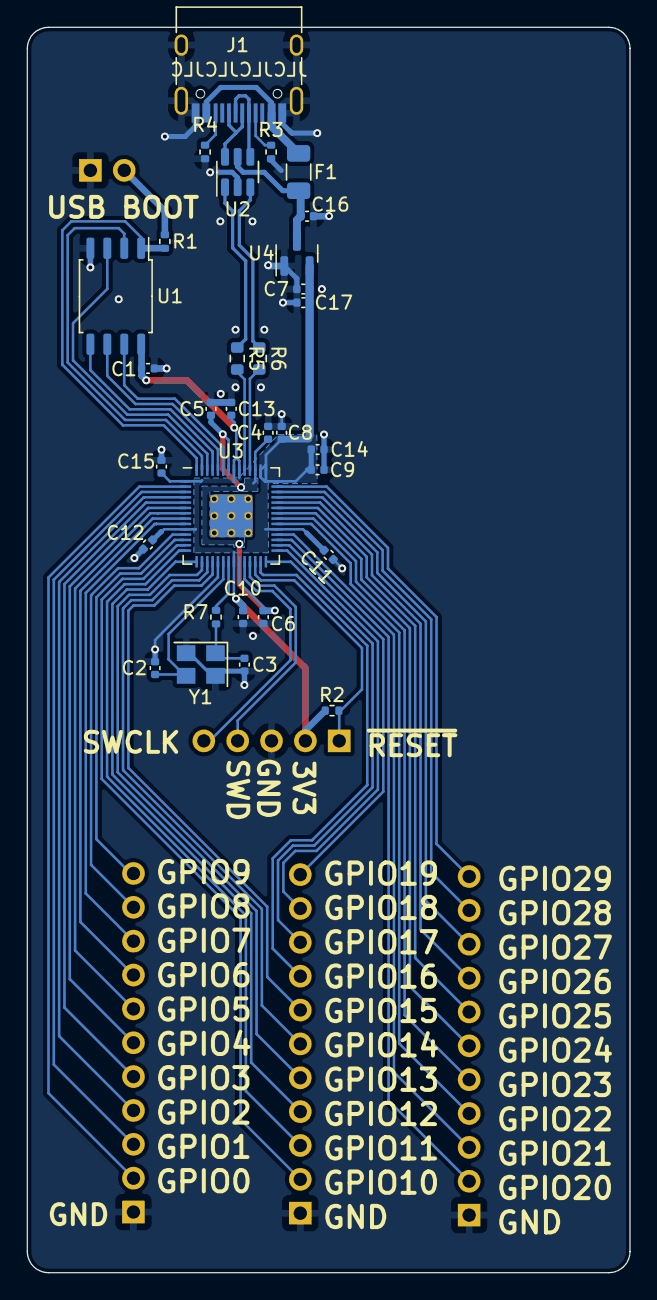
[picture p531: board RP2040-Guide.kicad_pcb from below]

Board: 2 copper layers, 45.2 x 93.4 mm, 36 parts (31 on the bottom side), 56 nets.
