rompasaurus/regardedPal/hardware-design/reference-boards/rp2040-pico-usbc/KiCad Projects/Pico 2 C/Pico 2 C.kicad_pcb

## KiCad design hardware-design/reference-boards/rp2040-pico-usbc/KiCad Projects/Pico 2 C/Pico 2 C.kicad_pcb (2026-04-15)

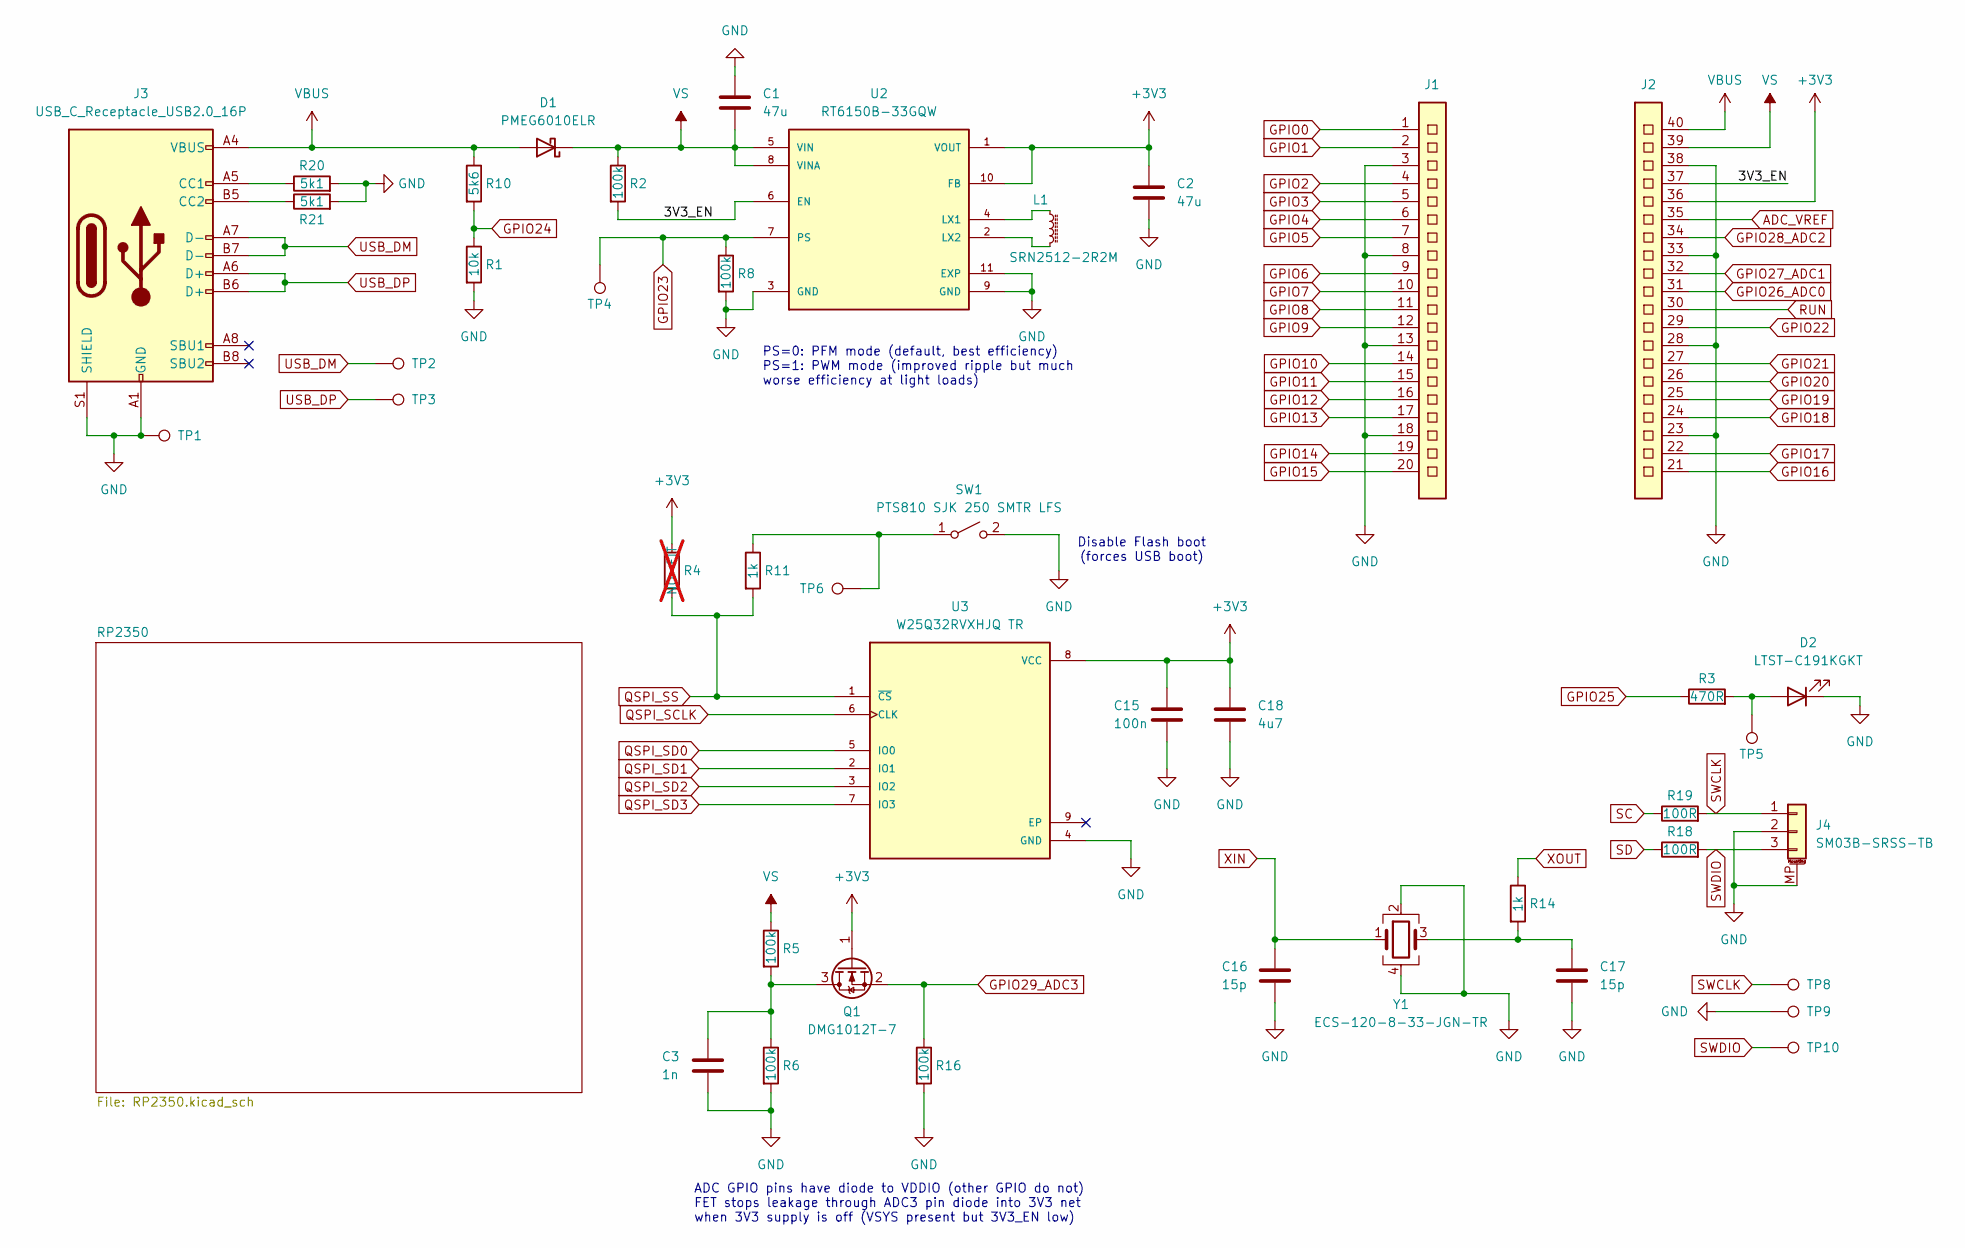
[picture p532: schematic Pico 2 C.kicad_sch, project piCo 2]

Parts:
C1, C2: 47u; C_0805_2012Metric
C3: 1n; C_0201_0603Metric
C15: 100n; C_0201_0603Metric
C16, C17: 15p; C_0201_0603Metric
C18: 4u7; C_0402_1005Metric
D1: PMEG6010ELR; D_SOD-123F
D2: LTST-C191KGKT; LED_0603_1608Metric
J1: CON_PICO_1-20
J2: CON_PICO_21-40
J3: USB_C_Receptacle_USB2.0_16P; USB_C_Receptacle_GCT_USB4105-xx-A_16P_TopMnt_Horizontal
J4: SM03B-SRSS-TB; JST_SH_SM03B-SRSS-TB_1x03-1MP_P1.00mm_Horizontal
L1: SRN2512-2R2M; L_1008_2520Metric
Q1: DMG1012T-7; SOT-523
R1: 10k; R_0201_0603Metric
R2, R5, R6, R8, R16: 100k; R_0201_0603Metric
R3: 470R; R_0201_0603Metric
R4: NO-FIT; R_0201_0603Metric; not fitted
R10: 5k6; R_0201_0603Metric
R11, R14: 1k; R_0201_0603Metric
R18, R19: 100R; R_0201_0603Metric
R20, R21: 5k1; R_0402_1005Metric
SW1: PTS810 SJK 250 SMTR LFS; SW_SPST_PTS810
TP1, TP2, TP3, TP4, TP5, TP6, TP8, TP9, TP10: TestPoint; TestPoint_Pad_1.5x1.5mm
U2: RT6150B-33GQW; DFN-10-1EP_2.6x2.6mm_P0.5mm_EP1.3x2.2mm
U3: W25Q32RVXHJQ TR; TDFN-8-1EP_3x2mm_P0.5mm_EP1.3x1.4mm
Y1: ECS-120-8-33-JGN-TR; Crystal_SMD_SeikoEpson_FA238-4Pin_3.2x2.5mm

Connections:
+3V3: C2.1, C15.1, C18.1, J2.36, Q1.1 (G), R4.1, U2.1 (VOUT), U2.10 (FB), U3.8 (VCC); also elsewhere on the board
/3V3_EN: J2.37, R2.2, U2.6 (EN)
ADC_VREF: J2.35; also elsewhere on the board
GND: C1.2, C2.2, C3.2, C15.2, C16.2, C17.2, C18.2, D2.1 (K), J1.3, J1.8, J1.13, J1.18, J2.23, J2.28, J2.33, J2.38, J3.A1 (GND), J3.A12 (GND), J3.B1 (GND), J3.B12 (GND), J3.S1 (SHIELD), J4.2, J4.MP (MountPin), R1.2, R6.2, R8.2, R16.2, R20.2, R21.2, SW1.2 (B), TP1.1, TP9.1, U2.3 (GND), U2.9 (GND), U2.11 (EXP), U3.4 (GND), Y1.2, Y1.4; also elsewhere on the board
GPIO0: J1.1; also elsewhere on the board
GPIO1: J1.2; also elsewhere on the board
GPIO2: J1.4; also elsewhere on the board
GPIO3: J1.5; also elsewhere on the board
GPIO4: J1.6; also elsewhere on the board
GPIO5: J1.7; also elsewhere on the board
GPIO6: J1.9; also elsewhere on the board
GPIO7: J1.10; also elsewhere on the board
GPIO8: J1.11; also elsewhere on the board
GPIO9: J1.12; also elsewhere on the board
GPIO10: J1.14; also elsewhere on the board
GPIO11: J1.15; also elsewhere on the board
GPIO12: J1.16; also elsewhere on the board
GPIO13: J1.17; also elsewhere on the board
GPIO14: J1.19; also elsewhere on the board
GPIO15: J1.20; also elsewhere on the board
GPIO16: J2.21; also elsewhere on the board
GPIO17: J2.22; also elsewhere on the board
GPIO18: J2.24; also elsewhere on the board
GPIO19: J2.25; also elsewhere on the board
GPIO20: J2.26; also elsewhere on the board
GPIO21: J2.27; also elsewhere on the board
GPIO22: J2.29; also elsewhere on the board
GPIO23: R8.1, TP4.1, U2.7 (PS); also elsewhere on the board
GPIO24: R1.1, R10.2; also elsewhere on the board
GPIO25: R3.1; also elsewhere on the board
GPIO26_ADC0: J2.31; also elsewhere on the board
GPIO27_ADC1: J2.32; also elsewhere on the board
GPIO28_ADC2: J2.34; also elsewhere on the board
GPIO29_ADC3: Q1.2 (S), R16.1; also elsewhere on the board
unnamed: C17.1, R14.2, Y1.3
unnamed: D2.2 (A), R3.2, TP5.1
unnamed: J3.A5 (CC1), R20.1
unnamed: J3.B5 (CC2), R21.1
unnamed: C3.1, Q1.3 (D), R5.2, R6.1
unnamed: R11.1, SW1.1 (A), TP6.1
unnamed: L1.1, U2.4 (LX1)
unnamed: L1.2, U2.2 (LX2)
QSPI_SCLK: U3.6 (CLK); also elsewhere on the board
QSPI_SD0: U3.5 (IO0); also elsewhere on the board
QSPI_SD1: U3.2 (IO1); also elsewhere on the board
QSPI_SD2: U3.3 (IO2); also elsewhere on the board
QSPI_SD3: U3.7 (IO3); also elsewhere on the board
QSPI_SS: R4.2, R11.2, U3.1 (~CS); also elsewhere on the board
RUN: J2.30; also elsewhere on the board
SC: R19.1; also elsewhere on the board
SD: R18.1; also elsewhere on the board
SWCLK: J4.1, R19.2, TP8.1
SWDIO: J4.3, R18.2, TP10.1
USB_DM: J3.A7 (D-), J3.B7 (D-), TP2.1; also elsewhere on the board
USB_DP: J3.A6 (D+), J3.B6 (D+), TP3.1; also elsewhere on the board
VBUS: D1.2 (A), J2.40, J3.A4 (VBUS), J3.A9 (VBUS), J3.B4 (VBUS), J3.B9 (VBUS), R10.1
VS: C1.1, D1.1 (K), J2.39, R2.1, R5.1, U2.5 (VIN), U2.8 (VINA)
XIN: C16.1, Y1.1; also elsewhere on the board
XOUT: R14.1; also elsewhere on the board

Notes on the sheet:
ADC GPIO pins have diode to VDDIO (other GPIO do not) FET stops leakage through ADC3 pin diode into 3V3 net when 3V3 supply is off (VSYS present but 3V3_EN low)
Disable Flash boot (forces USB boot)
PS=0: PFM mode (default, best efficiency) PS=1: PWM mode (improved ripple but much worse efficiency at light loads)
