rompasaurus/regardedPal/hardware-design/reference-boards/rp2040-pico-usbc/KiCad Projects/Pico 2 C/Pico 2 C.kicad_pcb

## KiCad design hardware-design/reference-boards/rp2040-pico-usbc/KiCad Projects/Pico 2 C/Pico 2 C.kicad_pcb (continued)

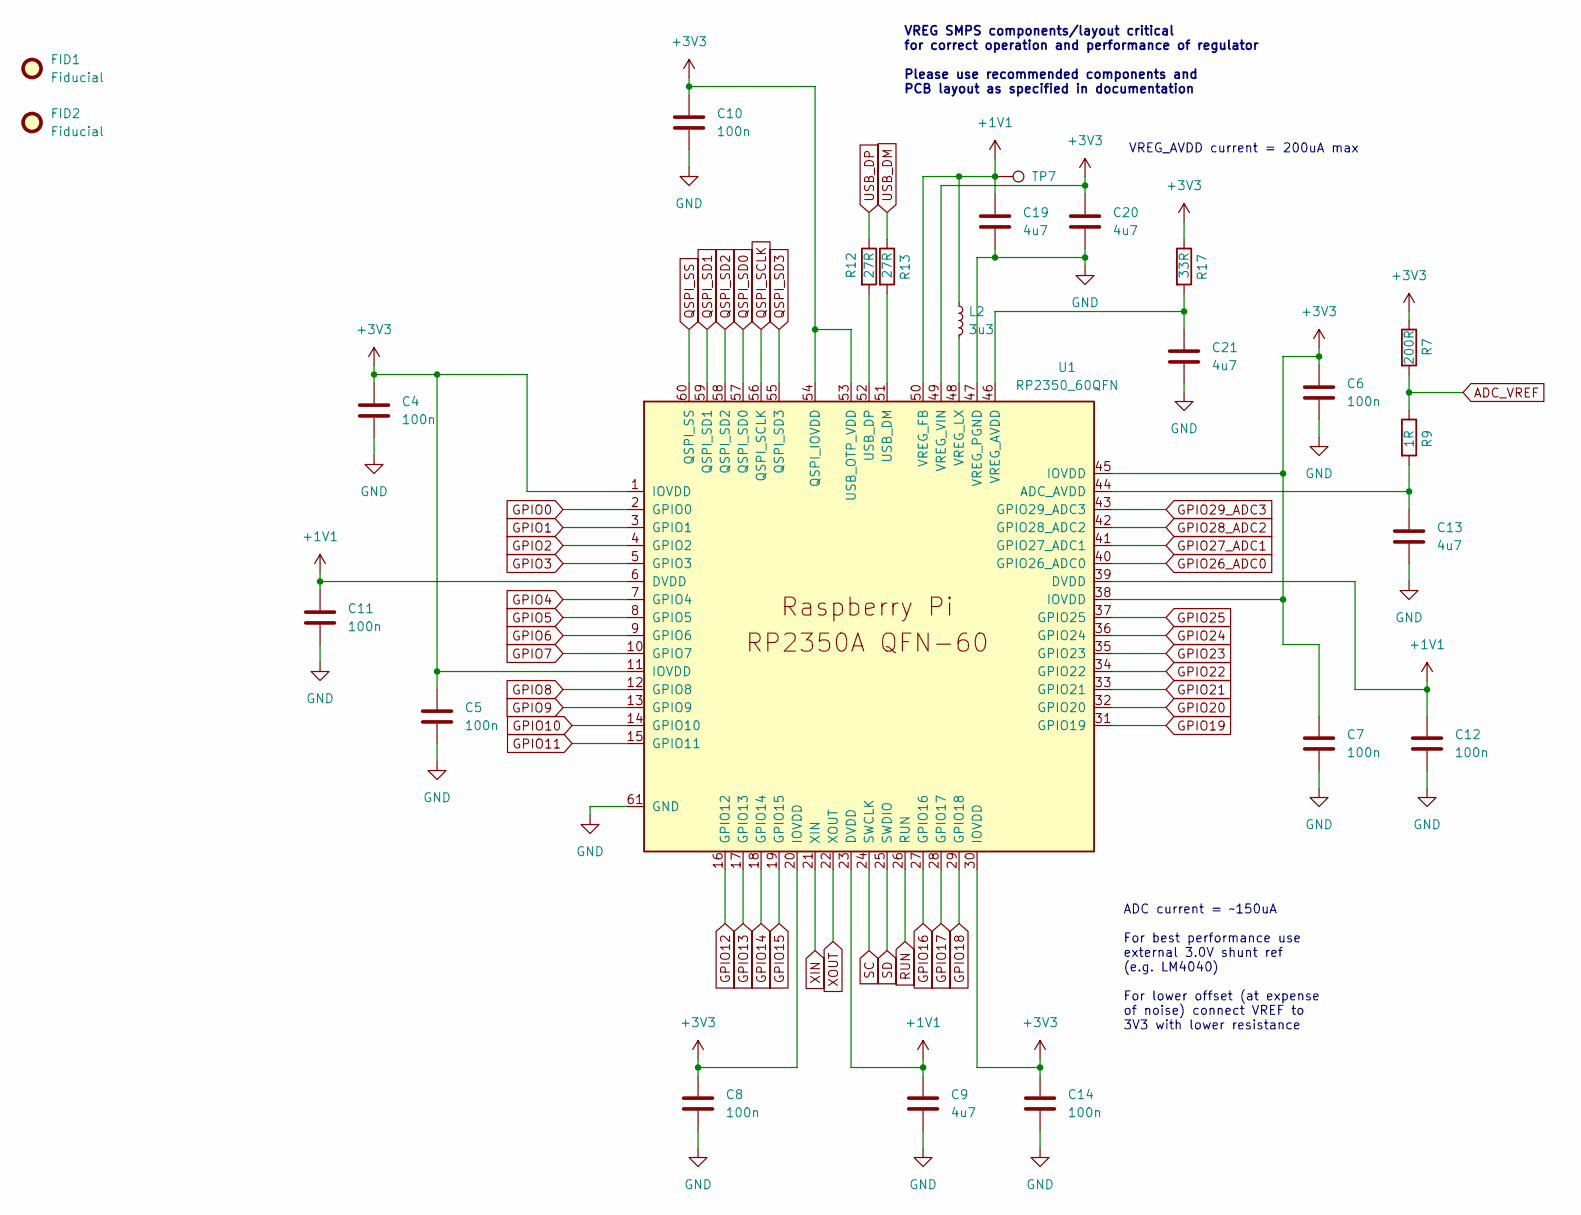
[picture p533: schematic RP2350.kicad_sch, project piCo 2 - RP2350]

Parts:
C4, C5, C6, C7, C8, C10, C11, C12, C14: 100n; C_0201_0603Metric
C9: 4u7; C_0201_0603Metric
C13, C19, C20, C21: 4u7; C_0402_1005Metric
FID1, FID2: Fiducial; Fiducial_1mm_Mask2mm
L2: 3u3; L_0603_1608Metric
R7: 200R; R_0402_1005Metric
R9: 1R; R_0201_0603Metric
R12, R13: 27R; R_0201_0603Metric
R17: 33R; R_0402_1005Metric
TP7: TestPoint; TestPoint_Pad_1.5x1.5mm
U1: RP2350_60QFN; RP2350-QFN-60-1EP_7x7_P0.4mm_EP3.4x3.4mm_ThermalVias

Connections:
+1V1: C9.1, C11.1, C12.1, C19.1, L2.1, TP7.1, U1.6 (DVDD), U1.23 (DVDD), U1.39 (DVDD), U1.50 (VREG_FB)
+3V3: C4.1, C5.1, C6.1, C7.1, C8.1, C10.1, C14.1, C20.1, R7.1, R17.1, U1.1 (IOVDD), U1.11 (IOVDD), U1.20 (IOVDD), U1.30 (IOVDD), U1.38 (IOVDD), U1.45 (IOVDD), U1.49 (VREG_VIN), U1.53 (USB_OTP_VDD), U1.54 (QSPI_IOVDD); also elsewhere on the board
ADC_VREF: R7.2, R9.1; also elsewhere on the board
GND: C4.2, C5.2, C6.2, C7.2, C8.2, C9.2, C10.2, C11.2, C12.2, C13.2, C14.2, C19.2, C20.2, C21.2, U1.47 (VREG_PGND), U1.61 (GND); also elsewhere on the board
GPIO0: U1.2 (GPIO0); also elsewhere on the board
GPIO1: U1.3 (GPIO1); also elsewhere on the board
GPIO2: U1.4 (GPIO2); also elsewhere on the board
GPIO3: U1.5 (GPIO3); also elsewhere on the board
GPIO4: U1.7 (GPIO4); also elsewhere on the board
GPIO5: U1.8 (GPIO5); also elsewhere on the board
GPIO6: U1.9 (GPIO6); also elsewhere on the board
GPIO7: U1.10 (GPIO7); also elsewhere on the board
GPIO8: U1.12 (GPIO8); also elsewhere on the board
GPIO9: U1.13 (GPIO9); also elsewhere on the board
GPIO10: U1.14 (GPIO10); also elsewhere on the board
GPIO11: U1.15 (GPIO11); also elsewhere on the board
GPIO12: U1.16 (GPIO12); also elsewhere on the board
GPIO13: U1.17 (GPIO13); also elsewhere on the board
GPIO14: U1.18 (GPIO14); also elsewhere on the board
GPIO15: U1.19 (GPIO15); also elsewhere on the board
GPIO16: U1.27 (GPIO16); also elsewhere on the board
GPIO17: U1.28 (GPIO17); also elsewhere on the board
GPIO18: U1.29 (GPIO18); also elsewhere on the board
GPIO19: U1.31 (GPIO19); also elsewhere on the board
GPIO20: U1.32 (GPIO20); also elsewhere on the board
GPIO21: U1.33 (GPIO21); also elsewhere on the board
GPIO22: U1.34 (GPIO22); also elsewhere on the board
GPIO23: U1.35 (GPIO23); also elsewhere on the board
GPIO24: U1.36 (GPIO24); also elsewhere on the board
GPIO25: U1.37 (GPIO25); also elsewhere on the board
GPIO26_ADC0: U1.40 (GPIO26_ADC0); also elsewhere on the board
GPIO27_ADC1: U1.41 (GPIO27_ADC1); also elsewhere on the board
GPIO28_ADC2: U1.42 (GPIO28_ADC2); also elsewhere on the board
GPIO29_ADC3: U1.43 (GPIO29_ADC3); also elsewhere on the board
unnamed: C13.1, R9.2, U1.44 (ADC_AVDD)
unnamed: R13.2, U1.51 (USB_DM)
unnamed: R12.2, U1.52 (USB_DP)
unnamed: C21.1, R17.2, U1.46 (VREG_AVDD)
unnamed: L2.2, U1.48 (VREG_LX)
QSPI_SCLK: U1.56 (QSPI_SCLK); also elsewhere on the board
QSPI_SD0: U1.57 (QSPI_SD0); also elsewhere on the board
QSPI_SD1: U1.59 (QSPI_SD1); also elsewhere on the board
QSPI_SD2: U1.58 (QSPI_SD2); also elsewhere on the board
QSPI_SD3: U1.55 (QSPI_SD3); also elsewhere on the board
QSPI_SS: U1.60 (QSPI_SS); also elsewhere on the board
RUN: U1.26 (RUN); also elsewhere on the board
SC: U1.24 (SWCLK); also elsewhere on the board
SD: U1.25 (SWDIO); also elsewhere on the board
USB_DM: R13.1; also elsewhere on the board
USB_DP: R12.1; also elsewhere on the board
XIN: U1.21 (XIN); also elsewhere on the board
XOUT: U1.22 (XOUT); also elsewhere on the board

Notes on the sheet:
VREG SMPS components/layout critical for correct operation and performance of regulator Please use recommended components and PCB layout as specified in documentation
ADC current = ~150uA For best performance use external 3.0V shunt ref (e.g. LM4040) For lower offset (at expense of noise) connect VREF to 3V3 with lower resistance
VREG_AVDD current = 200uA max

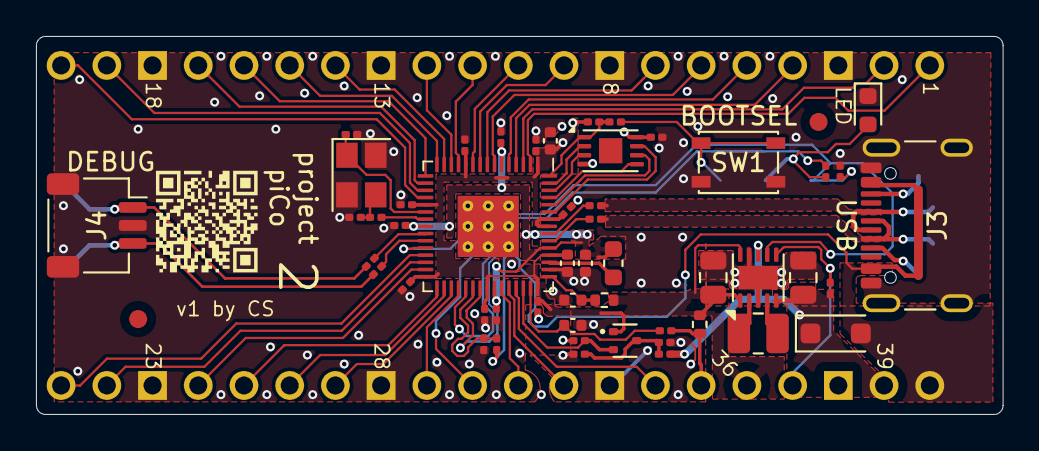
[picture p534: board Pico 2 C.kicad_pcb from above]

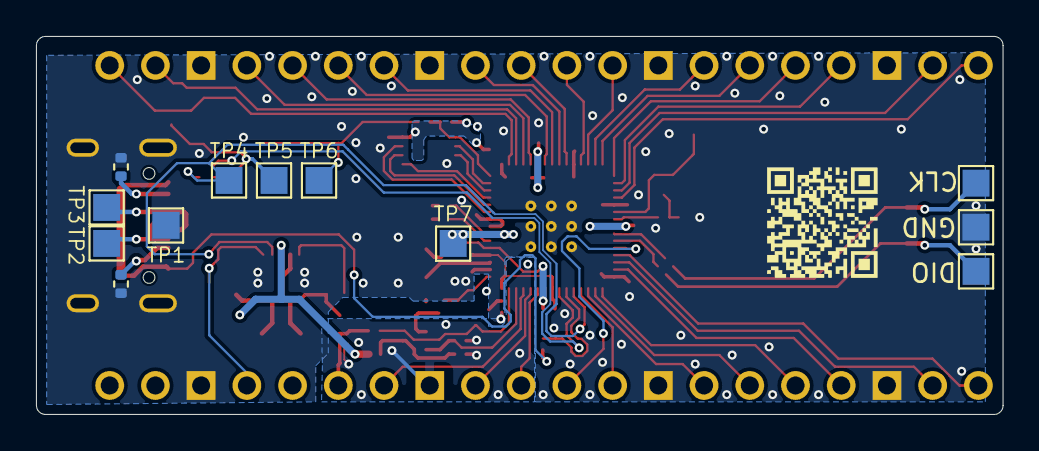
[picture p535: board Pico 2 C.kicad_pcb from below]

Board: 2 copper layers, 53.7 x 21.0 mm, 67 parts (12 on the bottom side), 65 nets.
