rompasaurus/regardedPal/hardware-design/reference-boards/esp32s3-basic-devboard/dev-board.kicad_pcb

## KiCad design hardware-design/reference-boards/esp32s3-basic-devboard/dev-board.kicad_pcb (2026-04-15)

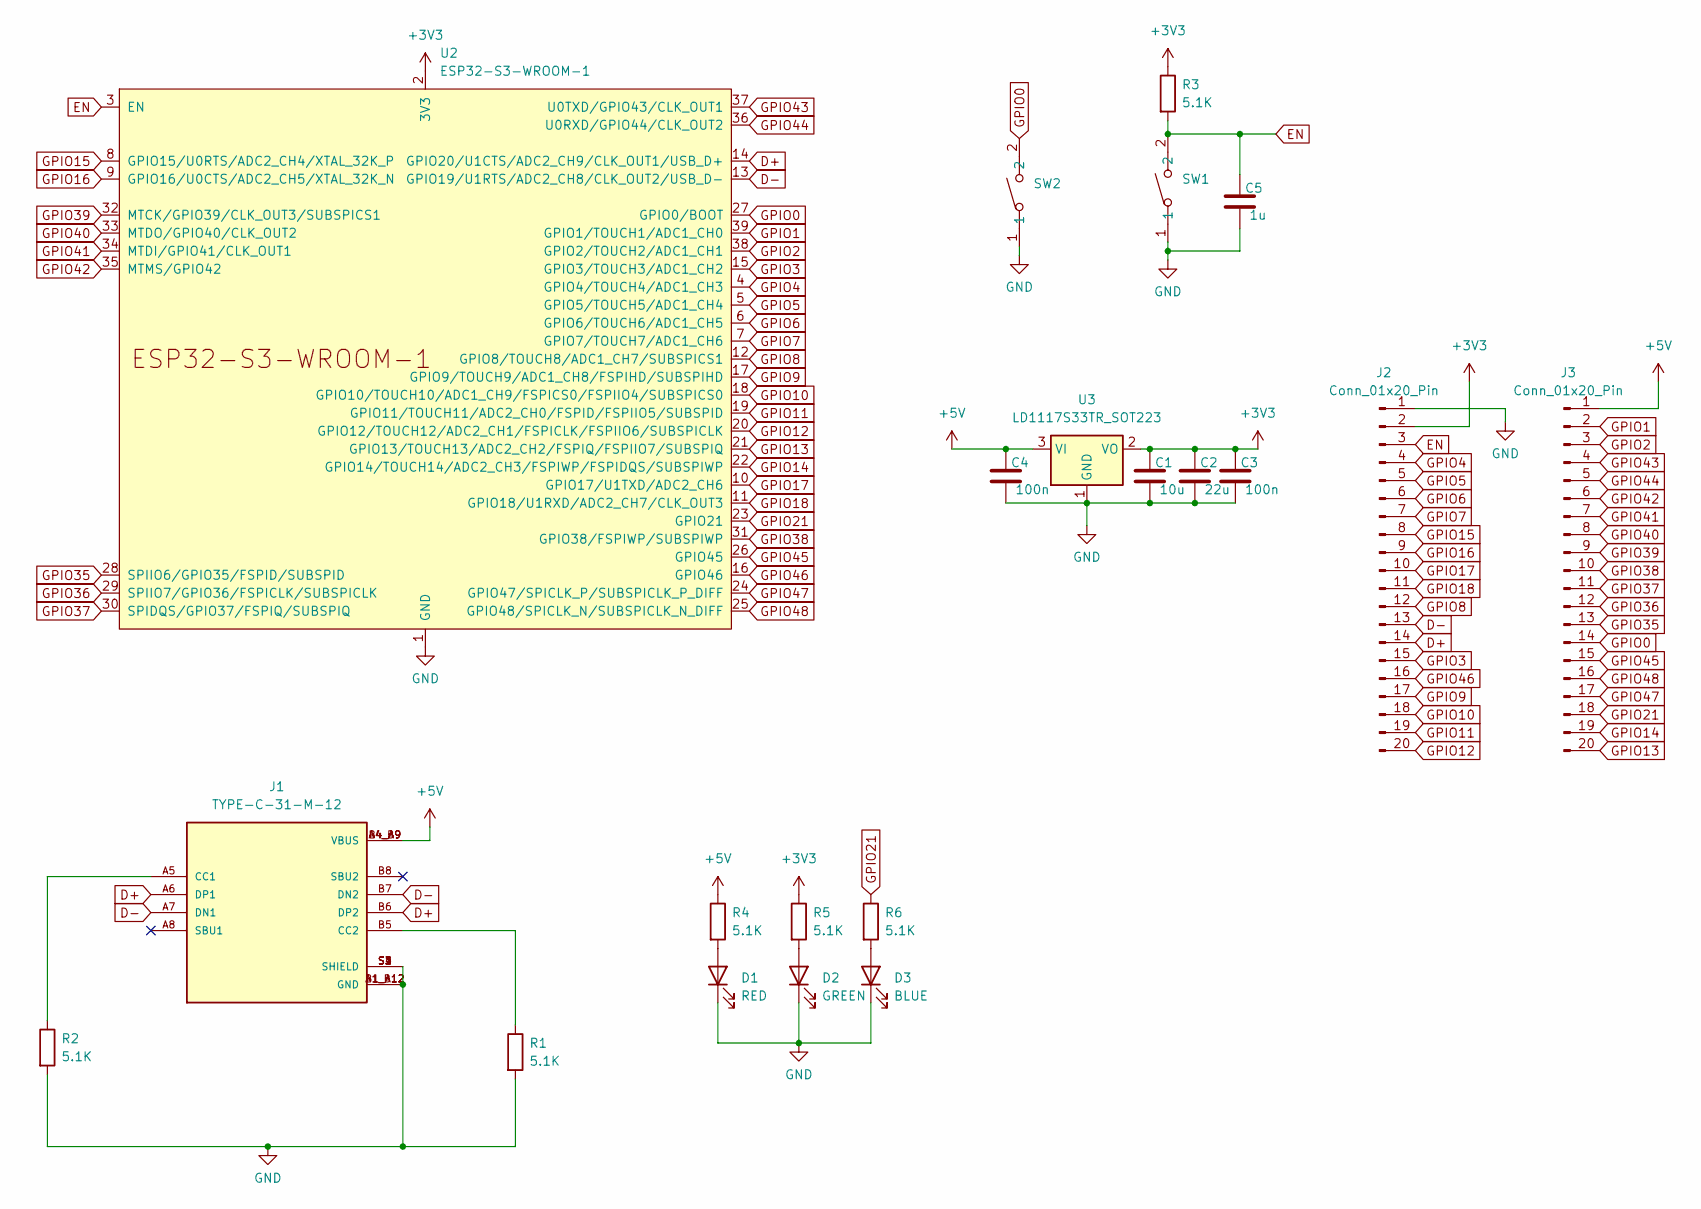
[picture p536: schematic dev-board.kicad_sch]

Parts:
C1: 10u; C_0603_1608Metric
C2: 22u; C_0603_1608Metric
C3, C4: 100n; C_0603_1608Metric
C5: 1u; C_0603_1608Metric
D1: RED; LED_0603_1608Metric
D2: GREEN; LED_0603_1608Metric
D3: BLUE; LED_0603_1608Metric
J1: TYPE-C-31-M-12; HRO_TYPE-C-31-M-12; PARTREV 2020.12.08
J2, J3: Conn_01x20_Pin; PinHeader_1x20_P2.54mm_Vertical
R1, R2, R3, R4, R5, R6: 5.1K; R_0603_1608Metric
SW1, SW2: TS-1088-AR02016; SW-SMD_L3.9-W3.0-P4.45; LCSC Part C720477
U2: ESP32-S3-WROOM-1
U3: LD1117S33TR_SOT223; SOT-223-3_TabPin2

Connections:
+3V3: C1.1, C2.1, C3.1, J2.2, R3.1, R5.1, U2.2 (3V3), U3.2 (VO)
+5V: C4.1, J1.A4_B9 (VBUS), J1.B4_A9 (VBUS), J3.1, R4.1, U3.3 (VI)
D+: J1.A6 (DP1), J1.B6 (DP2), J2.14, U2.14 (GPIO20/U1CTS/ADC2_CH9/CLK_OUT1/USB_D+)
D-: J1.A7 (DN1), J1.B7 (DN2), J2.13, U2.13 (GPIO19/U1RTS/ADC2_CH8/CLK_OUT2/USB_D-)
EN: C5.1, J2.3, R3.2, SW1.2, U2.3 (EN)
GND: C1.2, C2.2, C3.2, C4.2, C5.2, D1.1 (K), D2.1 (K), D3.1 (K), J1.A1_B12 (GND), J1.B1_A12 (GND), J1.S1 (SHIELD), J1.S2 (SHIELD), J1.S3 (SHIELD), J1.S4 (SHIELD), J2.1, R1.2, R2.2, SW1.1, SW2.1, U2.1 (GND), U2.40 (GND), U2.41 (GND), U3.1 (GND)
GPIO0: J3.14, SW2.2, U2.27 (GPIO0/BOOT)
GPIO1: J3.2, U2.39 (GPIO1/TOUCH1/ADC1_CH0)
GPIO2: J3.3, U2.38 (GPIO2/TOUCH2/ADC1_CH1)
GPIO3: J2.15, U2.15 (GPIO3/TOUCH3/ADC1_CH2)
GPIO4: J2.4, U2.4 (GPIO4/TOUCH4/ADC1_CH3)
GPIO5: J2.5, U2.5 (GPIO5/TOUCH5/ADC1_CH4)
GPIO6: J2.6, U2.6 (GPIO6/TOUCH6/ADC1_CH5)
GPIO7: J2.7, U2.7 (GPIO7/TOUCH7/ADC1_CH6)
GPIO8: J2.12, U2.12 (GPIO8/TOUCH8/ADC1_CH7/SUBSPICS1)
GPIO9: J2.17, U2.17 (GPIO9/TOUCH9/ADC1_CH8/FSPIHD/SUBSPIHD)
GPIO10: J2.18, U2.18 (GPIO10/TOUCH10/ADC1_CH9/FSPICS0/FSPIIO4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)
GPIO11: J2.19, U2.19 (GPIO11/TOUCH11/ADC2_CH0/FSPID/FSPIIO5/S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)
GPIO12: J2.20, U2.20 (GPIO12/TOUCH12/ADC2_CH1/FSPICLK/FSPIIO6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)
GPIO13: J3.20, U2.21 (GPIO13/TOUCH13/ADC2_CH2/FSPIQ/FSPIIO7/S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)
GPIO14: J3.19, U2.22 (GPIO14/TOUCH14/ADC2_CH3/FSPIWP/FSPIDQS/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)
GPIO15: J2.8, U2.8 (GPIO15/U0RTS/ADC2_CH4/XTAL_32K_P)
GPIO16: J2.9, U2.9 (GPIO16/U0CTS/ADC2_CH5/XTAL_32K_N)
GPIO17: J2.10, U2.10 (GPIO17/U1TXD/ADC2_CH6)
GPIO18: J2.11, U2.11 (GPIO18/U1RXD/ADC2_CH7/CLK_OUT3)
GPIO21: J3.18, R6.1, U2.23 (GPIO21)
GPIO35: J3.13, U2.28 (SPIIO6/GPIO35/FSPID/SUBSPID)
GPIO36: J3.12, U2.29 (SPIIO7/GPIO36/FSPICLK/SUBSPICLK)
GPIO37: J3.11, U2.30 (SPIDQS/GPIO37/FSPIQ/SUBSPIQ)
GPIO38: J3.10, U2.31 (GPIO38/FSPIWP/SUBSPIWP)
GPIO39: J3.9, U2.32 (MTCK/GPIO39/CLK_OUT3/SUBSPICS1)
GPIO40: J3.8, U2.33 (MTDO/GPIO40/CLK_OUT2)
GPIO41: J3.7, U2.34 (MTDI/GPIO41/CLK_OUT1)
GPIO42: J3.6, U2.35 (MTMS/GPIO42)
GPIO43: J3.4, U2.37 (U0TXD/GPIO43/CLK_OUT1)
GPIO44: J3.5, U2.36 (U0RXD/GPIO44/CLK_OUT2)
GPIO45: J3.15, U2.26 (GPIO45)
GPIO46: J2.16, U2.16 (GPIO46)
GPIO47: J3.17, U2.24 (GPIO47/SPICLK_P/SUBSPICLK_P_DIFF)
GPIO48: J3.16, U2.25 (GPIO48/SPICLK_N/SUBSPICLK_N_DIFF)
unnamed: D1.2 (A), R4.2
unnamed: D2.2 (A), R5.2
unnamed: D3.2 (A), R6.2
unnamed: J1.A5 (CC1), R2.1
unnamed: J1.B5 (CC2), R1.1

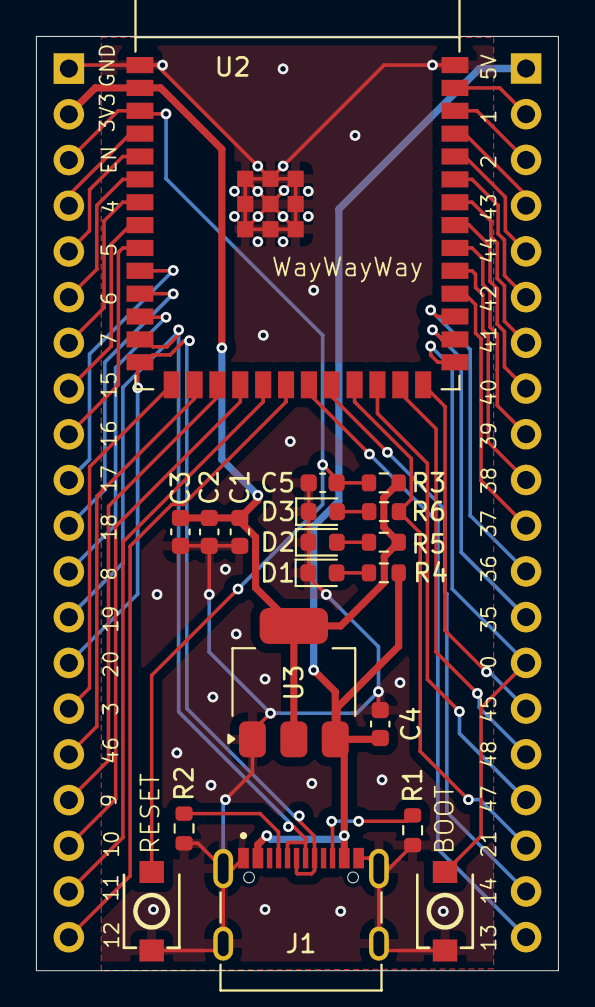
[picture p537: board dev-board.kicad_pcb from above]

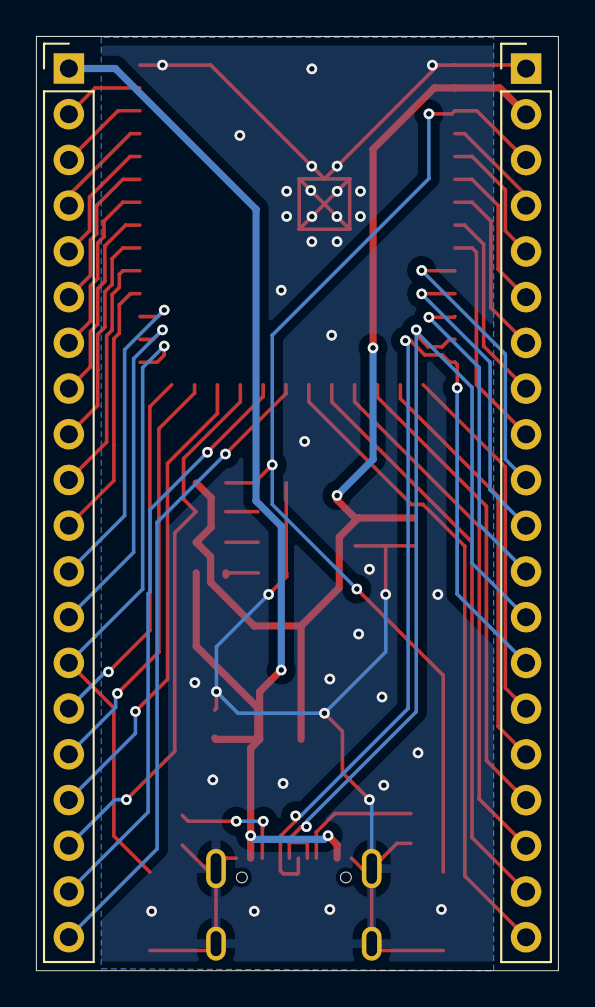
[picture p538: board dev-board.kicad_pcb from below]

Board: 2 copper layers, 29.0 x 51.9 mm, 21 parts (2 on the bottom side), 45 nets.
