rompasaurus/regardedPal/hardware-design/reference-boards/rp2040-minimal-jlcpcb/RP2040_minimal.kicad_pcb

## KiCad design hardware-design/reference-boards/rp2040-minimal-jlcpcb/RP2040_minimal.kicad_pcb (2026-04-15)

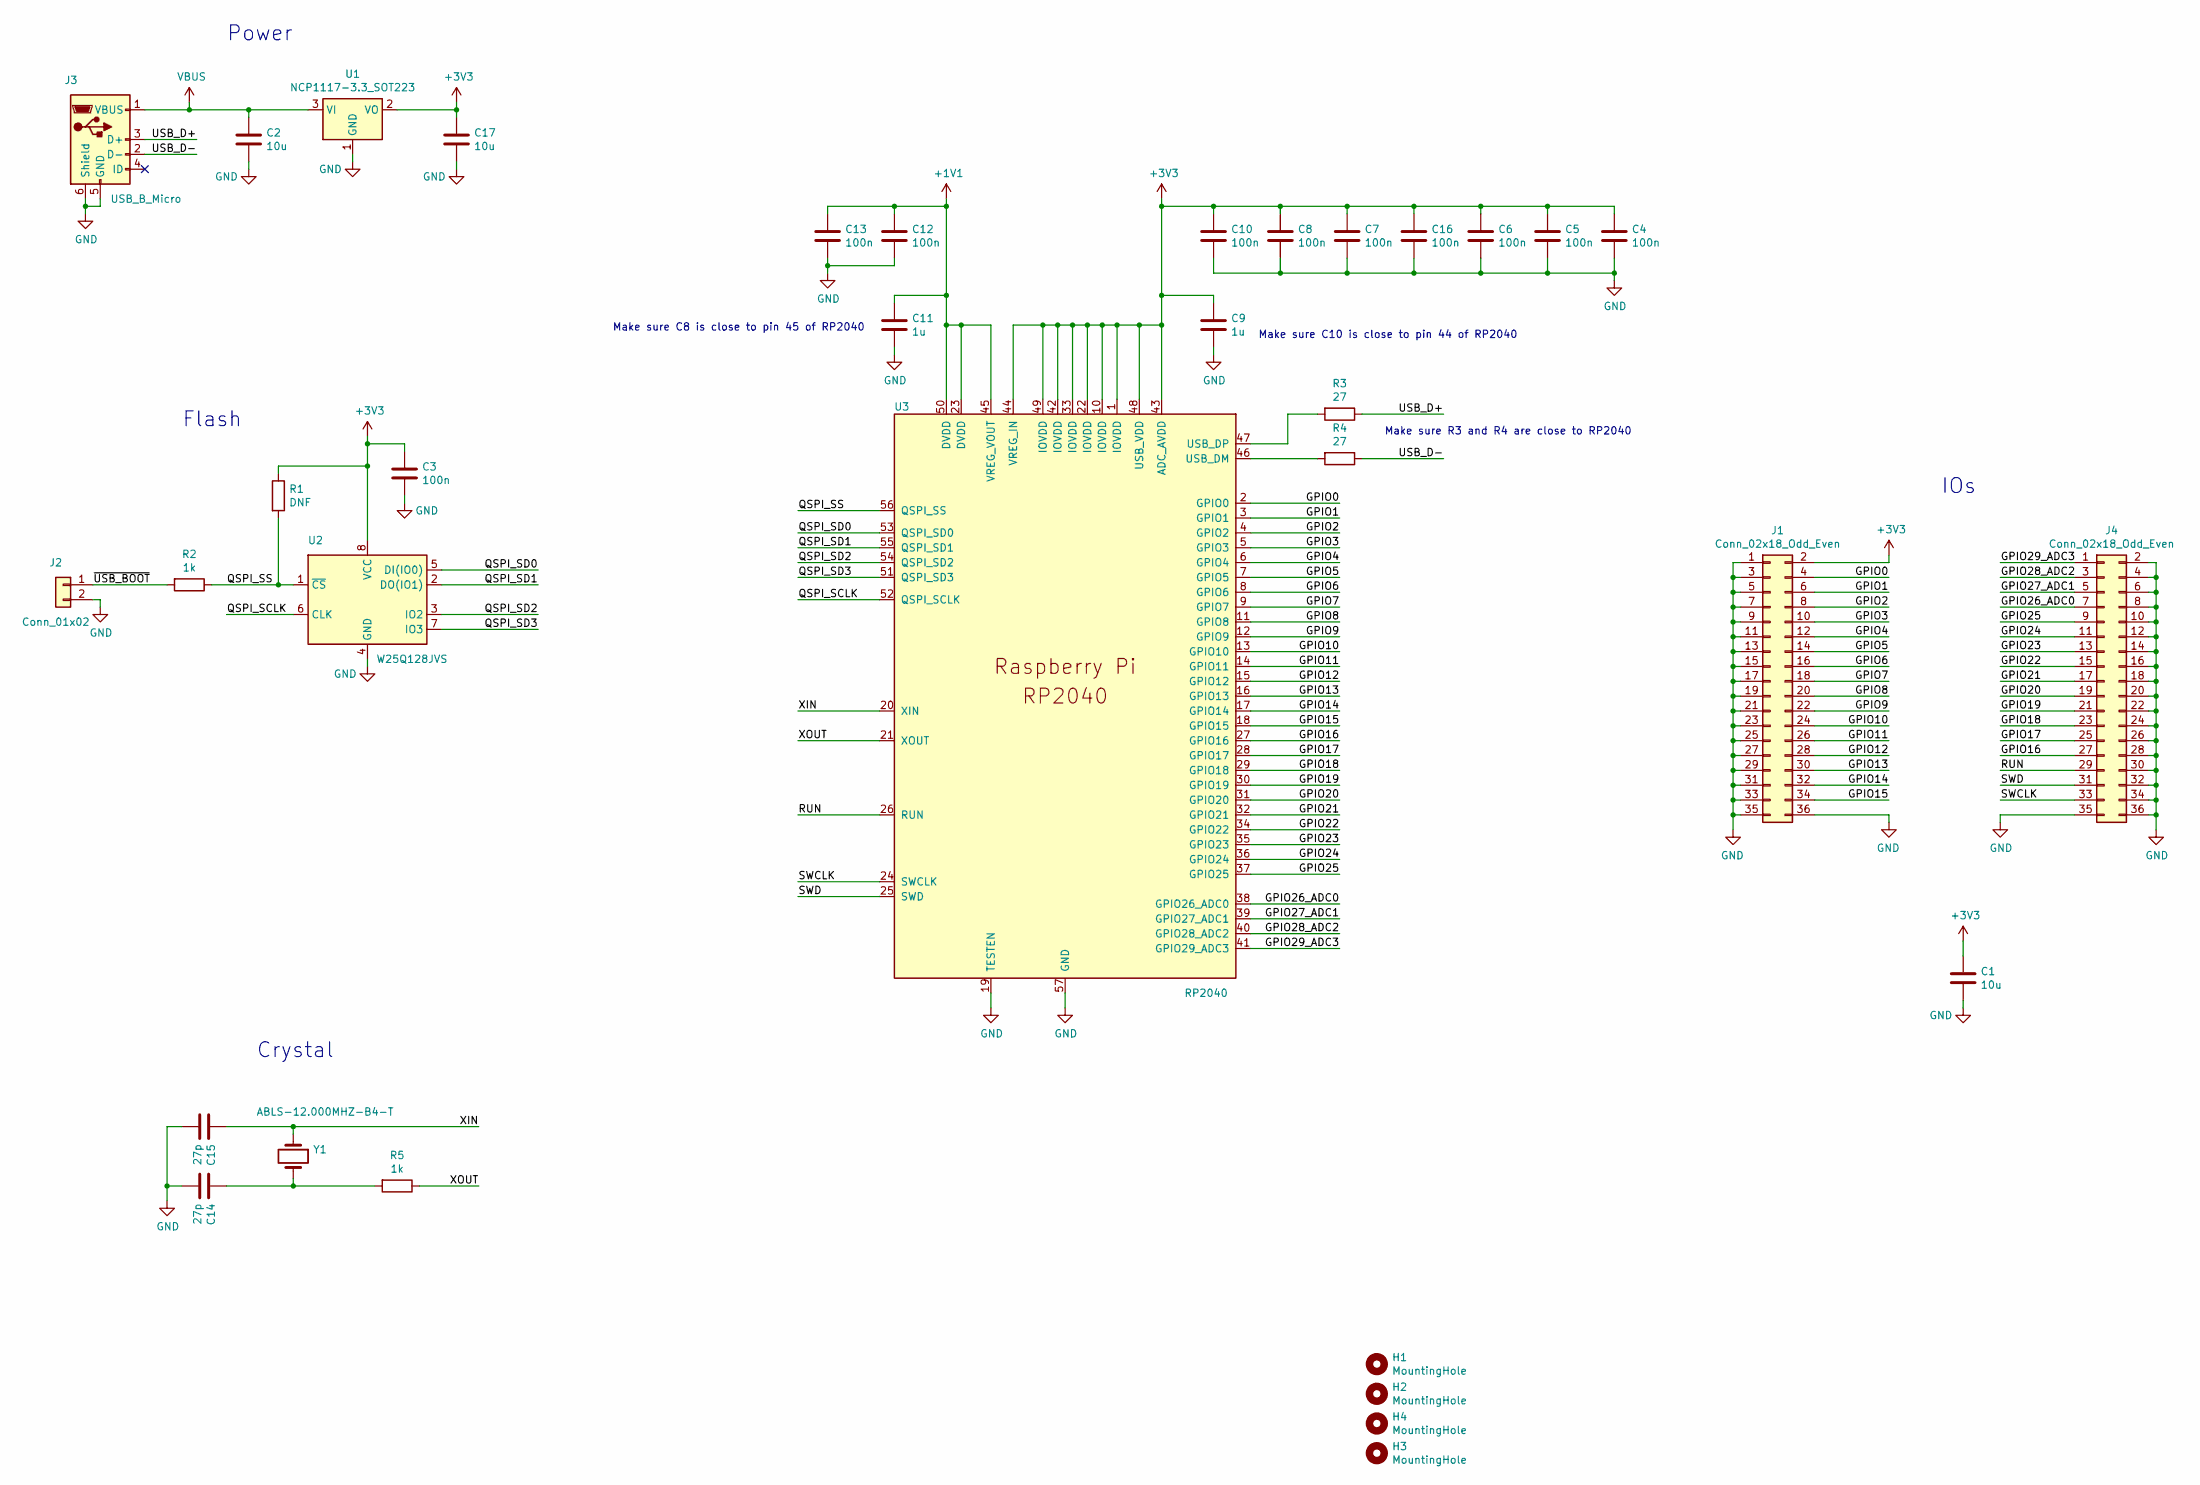
[picture p539: schematic RP2040_minimal.kicad_sch, RP2040 Minimal Design Example]

Parts:
C1, C2, C17: 10u; C_0805_2012Metric; LCSC C15850
C3, C4, C5, C6, C7, C8, C10, C12, C13, C16: 100n; C_0402_1005Metric; LCSC C126504
C9, C11: 1u; C_0402_1005Metric; LCSC C307331
C14, C15: 27p; C_0402_1005Metric; LCSC C52923
H1, H2, H3, H4: MountingHole; MountingHole_2.7mm_M2.5
J1, J4: Conn_02x18_Odd_Even; PinHeader_2x18_P2.54mm_Vertical; LCSC C168945
J2: Conn_01x02; PinHeader_1x02_P2.54mm_Vertical; LCSC C124375
J3: USB_B_Micro; USB_Micro-B_Amphenol_10103594-0001LF_Horizontal_modified; LCSC C428495
R1: DNF; C_0402_1005Metric
R2, R5: 1k; C_0402_1005Metric; LCSC C11702
R3, R4: 27; C_0402_1005Metric; LCSC C274349
U1: NCP1117-3.3_SOT223; SOT-223-3_TabPin2; LCSC C26537
U2: W25Q128JVS; SOIC-8_5.23x5.23mm_P1.27mm; LCSC C97521
U3: RP2040; RP2040-QFN-56; LCSC C2040
Y1: ABLS-12.000MHZ-B4-T; Crystal_SMD_HC49-US; LCSC C110563

Connections:
+1V1: C11.1, C12.1, C13.1, U3.23 (DVDD), U3.45 (VREG_VOUT), U3.50 (DVDD)
+3V3: C1.1, C3.1, C4.1, C5.1, C6.1, C7.1, C8.1, C9.1, C10.1, C16.1, C17.1, J1.2, R1.1, U1.2 (VO), U2.8 (VCC), U3.1 (IOVDD), U3.10 (IOVDD), U3.22 (IOVDD), U3.33 (IOVDD), U3.42 (IOVDD), U3.43 (ADC_AVDD), U3.44 (VREG_IN), U3.48 (USB_VDD), U3.49 (IOVDD)
/GPIO0: J1.4, U3.2 (GPIO0)
/GPIO1: J1.6, U3.3 (GPIO1)
/GPIO2: J1.8, U3.4 (GPIO2)
/GPIO3: J1.10, U3.5 (GPIO3)
/GPIO4: J1.12, U3.6 (GPIO4)
/GPIO5: J1.14, U3.7 (GPIO5)
/GPIO6: J1.16, U3.8 (GPIO6)
/GPIO7: J1.18, U3.9 (GPIO7)
/GPIO8: J1.20, U3.11 (GPIO8)
/GPIO9: J1.22, U3.12 (GPIO9)
/GPIO10: J1.24, U3.13 (GPIO10)
/GPIO11: J1.26, U3.14 (GPIO11)
/GPIO12: J1.28, U3.15 (GPIO12)
/GPIO13: J1.30, U3.16 (GPIO13)
/GPIO14: J1.32, U3.17 (GPIO14)
/GPIO15: J1.34, U3.18 (GPIO15)
/GPIO16: J4.27, U3.27 (GPIO16)
/GPIO17: J4.25, U3.28 (GPIO17)
/GPIO18: J4.23, U3.29 (GPIO18)
/GPIO19: J4.21, U3.30 (GPIO19)
/GPIO20: J4.19, U3.31 (GPIO20)
/GPIO21: J4.17, U3.32 (GPIO21)
/GPIO22: J4.15, U3.34 (GPIO22)
/GPIO23: J4.13, U3.35 (GPIO23)
/GPIO24: J4.11, U3.36 (GPIO24)
/GPIO25: J4.9, U3.37 (GPIO25)
/GPIO26_ADC0: J4.7, U3.38 (GPIO26_ADC0)
/GPIO27_ADC1: J4.5, U3.39 (GPIO27_ADC1)
/GPIO28_ADC2: J4.3, U3.40 (GPIO28_ADC2)
/GPIO29_ADC3: J4.1, U3.41 (GPIO29_ADC3)
/QSPI_SCLK: U2.6 (CLK), U3.52 (QSPI_SCLK)
/QSPI_SD0: U2.5 (DI(IO0)), U3.53 (QSPI_SD0)
/QSPI_SD1: U2.2 (DO(IO1)), U3.55 (QSPI_SD1)
/QSPI_SD2: U2.3 (IO2), U3.54 (QSPI_SD2)
/QSPI_SD3: U2.7 (IO3), U3.51 (QSPI_SD3)
/QSPI_SS: R1.2, R2.1, U2.1 (~CS), U3.56 (QSPI_SS)
/RUN: J4.29, U3.26 (RUN)
/SWCLK: J4.33, U3.24 (SWCLK)
/SWD: J4.31, U3.25 (SWD)
/USB_D+: J3.3 (D+), R3.1
/USB_D-: J3.2 (D-), R4.1
/XIN: C15.1, U3.20 (XIN), Y1.1
/XOUT: R5.1, U3.21 (XOUT)
/~USB_BOOT: J2.1, R2.2
GND: C1.2, C2.2, C3.2, C4.2, C5.2, C6.2, C7.2, C8.2, C9.2, C10.2, C11.2, C12.2, C13.2, C14.2, C15.2, C16.2, C17.2, J1.1, J1.3, J1.5, J1.7, J1.9, J1.11, J1.13, J1.15, J1.17, J1.19, J1.21, J1.23, J1.25, J1.27, J1.29, J1.31, J1.33, J1.35, J1.36, J2.2, J3.5 (GND), J3.6 (Shield), J4.2, J4.4, J4.6, J4.8, J4.10, J4.12, J4.14, J4.16, J4.18, J4.20, J4.22, J4.24, J4.26, J4.28, J4.30, J4.32, J4.34, J4.35, J4.36, U1.1 (GND), U2.4 (GND), U3.19 (TESTEN), U3.57 (GND)
unnamed: C14.1, R5.2, Y1.2
unnamed: R4.2, U3.46 (USB_DM)
unnamed: R3.2, U3.47 (USB_DP)
VBUS: C2.1, J3.1 (VBUS), U1.3 (VI)

Notes on the sheet:
IOs
Make sure C8 is close to pin 45 of RP2040
Make sure C10 is close to pin 44 of RP2040
Crystal
Power
Flash
Make sure R3 and R4 are close to RP2040

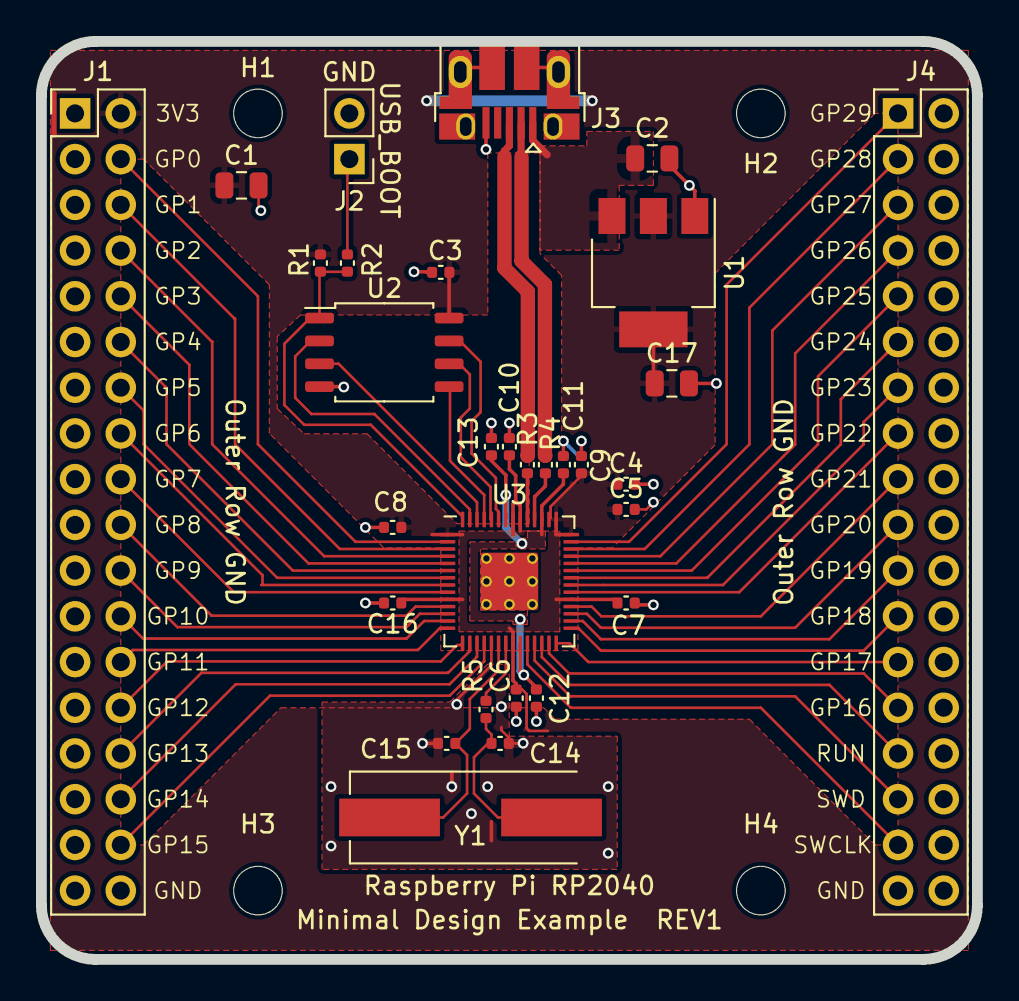
[picture p540: board RP2040_minimal.kicad_pcb from above]

Board: 2 copper layers, 52.0 x 51.0 mm, 34 parts (0 on the bottom side), 51 nets.
