rompasaurus/regardedPal/hardware-design/reference-boards/rp2040-pico-usbc/KiCad Projects/Pico C/RPI-PICO-R3a-PUBLIC - Official.kicad_pcb

## KiCad design hardware-design/reference-boards/rp2040-pico-usbc/KiCad Projects/Pico C/RPI-PICO-R3a-PUBLIC - Official.kicad_pcb (2026-04-15)

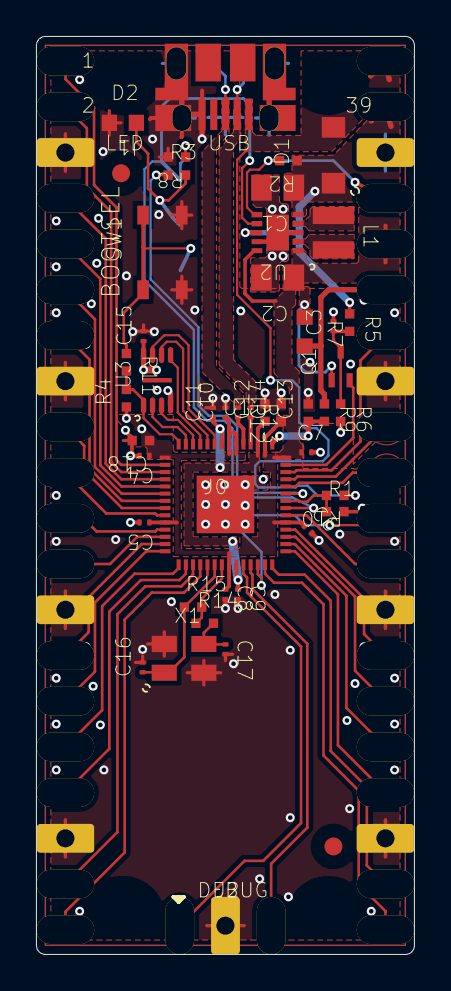
[picture p541: board RPI-PICO-R3a-PUBLIC - Official.kicad_pcb from above]

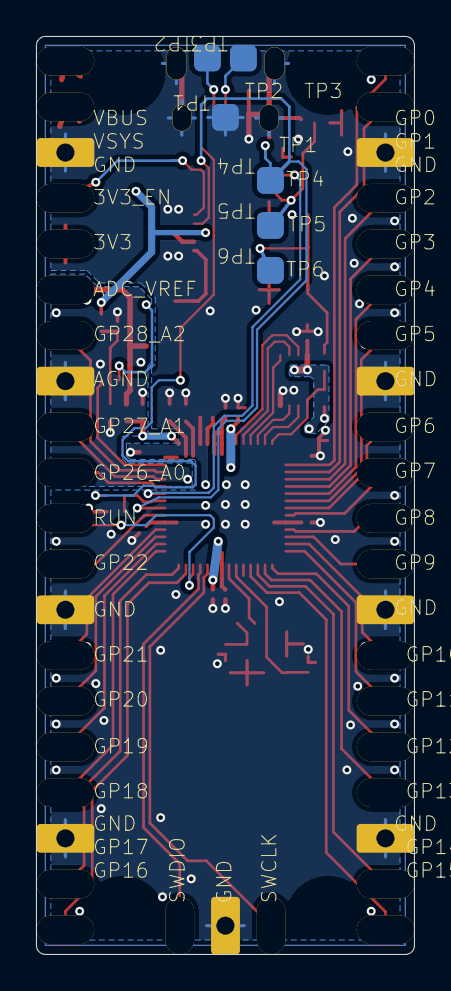
[picture p542: board RPI-PICO-R3a-PUBLIC - Official.kicad_pcb from below]

Board: 2 copper layers, 21.0 x 51.0 mm, 51 parts (6 on the bottom side), 59 nets.

Parts:
C1, C2: CAP_MLCC_CAPC2012_47U_RP-019A1P; CAPC2012
C3: CAP_MLCC_M0603_PICO_1N_RP-019A1; M0603_PICO
C4, C5, C6, C7, C8, C9, C10, C11, C15: CAP_MLCC_M0603_PICO_100N_RP-019; M0603_PICO
C12, C13, C14, C18: CAP_MLCC_CAPC1005_2U2_RP-019A1P; CAPC1005
C16, C17: CAP_MLCC_M0603_PICO_15P_RP-019A; M0603_PICO
D1: DIODE_SCHOTTKY_SOD123FL_MBR120V; SOD123FL
D2: LED_2PIN_AVAGO_QSM_GREEN_RP-019; AVAGO_QSM
J0: CON_PICO_40W_CON_PICO_40W_CON_P; CON_PICO_40W
J1: CON_UUSB_B_FCI_10103594-0001LF_; FCI_10103594-0001LF
J2: CON_PICO_3W_CON_PICO_3W_CON_PIC; CON_PICO_3W
L1: INDUCTOR_BOURNS_SRN2512_2U2_RP-; BOURNS_SRN2512
Q1: MOSFET_N_SOT50P160X90-3N_DMG101; SOT50P160X90-3N
R1: RES_CHIP_RESC1005_10K_RP-019A1P; RESC1005
R2, R6, R8: RES_CHIP_RESC1005_100K_RP-019A1; RESC1005
R3: RES_CHIP_RESC1005_470R_RP-019A1; RESC1005
R4, R15: RES_CHIP_RESC1005_NO-FIT_; RESC1005
R5: RES_CHIP_RESC1005_200K_RP-019A1; RESC1005
R7: RES_CHIP_RESC1608_200R_RP-01A5Y; RESC1608
R9: RES_CHIP_RESC1005_1R_RP-019A1P-; RESC1005
R10: RES_CHIP_RESC1005_5K6_RP-019A1P; RESC1005
R11, R14: RES_CHIP_RESC1005_1K_RP-019A1P-; RESC1005
R12, R13: RES_CHIP_M0603_PICO_27R_RP-019A; M0603_PICO
SW1: SW_PB_4PIN_TONEPARTS_TP-1221U-K; TONEPARTS_TP-1221U-K9K5325
TP1, TP2, TP3, TP4, TP5, TP6: TP_SMT_SQUARERC_1P5MM_TP_SMT_1P; TP_SMT_1P5X1P5MM
U1: RPI_RP2040_RPI_RP2040_RP2040; RPI_RP2040
U2: RICHTEK_RT6150_RICHTEK_RT6150B_; RICHTEK_RT6150B
U3: WINBOND_W25X_QSPI_FLASH_USON_US; USON_2X3MM
X1: CRYSTAL_4P_XTAL320X250X100_12MH; XTAL320X250X100

Connections:
1V1: C9.1, C11.1, C12.1, U1.23, U1.45, U1.50
3V3: C2.1, C4.1, C5.1, C6.1, C7.1, C8.1, C10.1, C14.1, C15.1, C18.1, J0.36, Q1.1, R4.1, R7.1, U1.1, U1.10, U1.22, U1.33, U1.42, U1.44, U1.48, U1.49, U2.1, U2.10, U3.8
3V3_EN: J0.37, R2.2, U2.6
ADC_AVDD: C13.1, R9.2, U1.43
ADC_VREF: J0.35, R7.2, R9.1
GND: C1.2, C2.2, C3.2, C4.2, C5.2, C6.2, C7.2, C8.2, C9.2, C10.2, C11.2, C12.2, C13.2, C14.2, C15.2, C16.2, C17.2, C18.2, D2.1, J0.3, J0.8, J0.13, J0.18, J0.23, J0.28, J0.33, J0.38, J1.5, J1.6, J1.7, J1.8, J1.9, J2.2, R1.2, R6.2, R8.2, SW1.3, SW1.4, TP1.1, U1.19, U1.57, U2.3, U2.9, U2.11, U3.4, X1.2, X1.4
GPIO0: J0.1, U1.2
GPIO1: J0.2, U1.3
GPIO2: J0.4, U1.4
GPIO3: J0.5, U1.5
GPIO4: J0.6, U1.6
GPIO5: J0.7, U1.7
GPIO6: J0.9, U1.8
GPIO7: J0.10, U1.9
GPIO8: J0.11, U1.11
GPIO9: J0.12, U1.12
GPIO10: J0.14, U1.13
GPIO11: J0.15, U1.14
GPIO12: J0.16, U1.15
GPIO13: J0.17, U1.16
GPIO14: J0.19, U1.17
GPIO15: J0.20, U1.18
GPIO16: J0.21, U1.27
GPIO17: J0.22, U1.28
GPIO18: J0.24, U1.29
GPIO19: J0.25, U1.30
GPIO20: J0.26, U1.31
GPIO21: J0.27, U1.32
GPIO22: J0.29, U1.34
GPIO23: R8.1, TP4.1, U1.35, U2.7
GPIO24: R1.1, R10.2, U1.36
GPIO25: R3.1, U1.37
GPIO26_ADC0: J0.31, U1.38
GPIO27_ADC1: J0.32, U1.39
GPIO28_ADC2: J0.34, U1.40
GPIO29_ADC3: Q1.2, U1.41
N1248345: L1.1, U2.4
N1248352: L1.2, U2.2
N1283798: D2.2, R3.2, TP5.1
N1286133: C3.1, Q1.3, R5.2, R6.1
N1327876: R11.1, SW1.1, SW1.2, TP6.1
QSPI_SCLK: U1.52, U3.6
QSPI_SD0: U1.53, U3.5
QSPI_SD1: U1.55, U3.2
QSPI_SD2: U1.54, U3.3
QSPI_SD3: U1.51, U3.7
QSPI_SS: R4.2, R11.2, U1.56, U3.1
RUN: J0.30, U1.26
SWCLK: J2.1, U1.24
SWDIO: J2.3, U1.25
USB_DM: J1.2, R13.1, TP2.1
USB_DMX: R13.2, U1.46
USB_DP: J1.3, R12.1, TP3.1
USB_DPX: R12.2, U1.47
VBUS: D1.2, J0.40, J1.1, R10.1
VSYS: C1.1, D1.1, J0.39, R2.1, R5.1, U2.5, U2.8
XIN: C16.1, R15.1, U1.20, X1.1
XOUT: R14.1, R15.2, U1.21
XR: C17.1, R14.2, X1.3
