rompasaurus/regardedPal/hardware-design/Board Design kicad/dilder.kicad_pcb

## KiCad design hardware-design/Board Design kicad/dilder.kicad_pcb (2026-04-14)

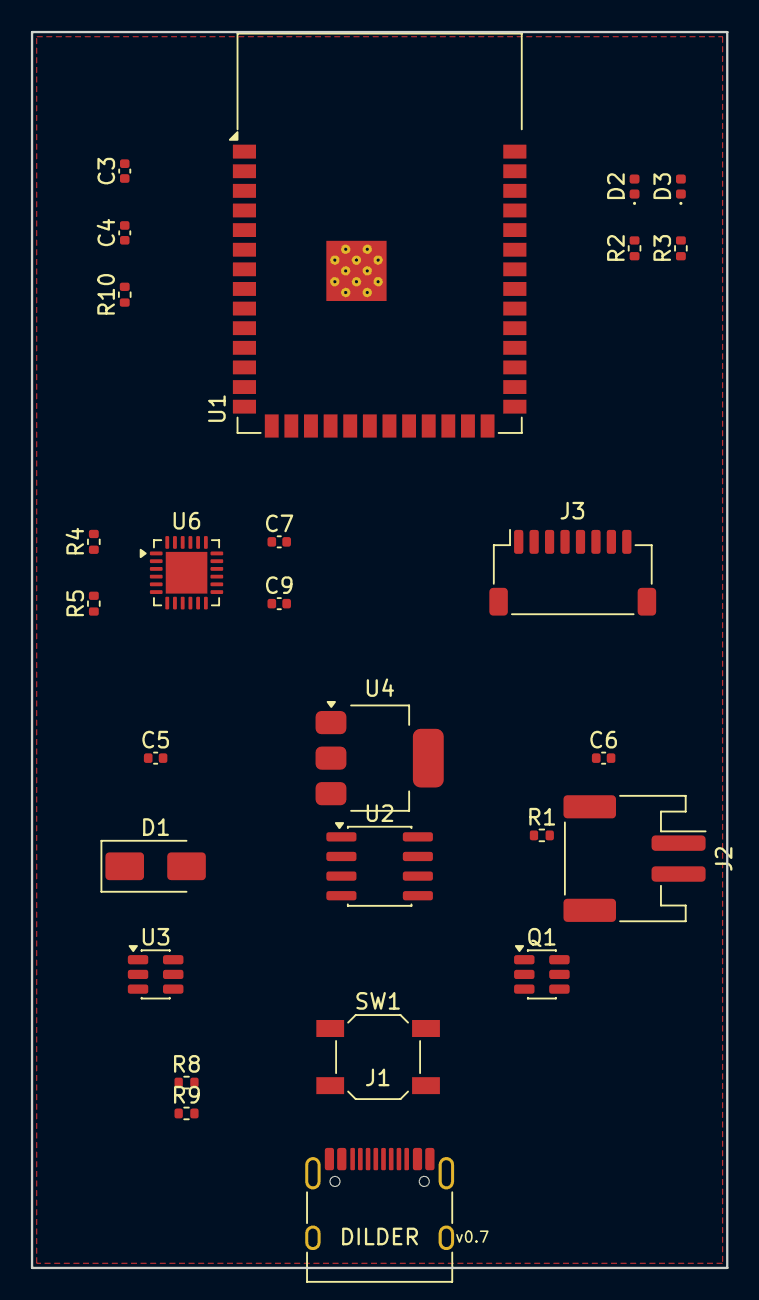
[picture p543: board dilder.kicad_pcb from above]

Board: 4 copper layers, 45.0 x 80.0 mm, 27 parts (0 on the bottom side), 29 nets, no tracks yet.

Parts:
C3, C7, C9: 100nF; C_0402_1005Metric
C4, C5, C6: 10uF; C_0402_1005Metric
D1: SS34; D_SMA
D2: RED; LED_0402_1005Metric
D3: GREEN; LED_0402_1005Metric
J1: USB-C; USB_C_Receptacle_HRO_TYPE-C-31-M-12
J2: BAT; JST_PH_S2B-PH-SM4-TB_1x02-1MP_P2.00mm_Horizontal
J3: ePaper; JST_SH_SM08B-SRSS-TB_1x08-1MP_P1.00mm_Horizontal
Q1: FS8205A; SOT-23-6
R1: 1.2k; R_0402_1005Metric
R2, R3: 1k; R_0402_1005Metric
R4, R5, R10: 10k; R_0402_1005Metric
R8, R9: 5.1k; R_0402_1005Metric
SW1: 5-Way; SW_SPST_SKQG_WithStem
U1: ESP32-S3-N16R8; ESP32-S3-WROOM-1
U2: TP4056; SOIC-8_3.9x4.9mm_P1.27mm
U3: DW01A; SOT-23-6
U4: AMS1117-3.3; SOT-223-3_TabPin2
U6: MPU-6050; QFN-24-1EP_4x4mm_P0.5mm_EP2.7x2.7mm

Connections:
3V3: C3.1, C4.1, C6.1, C7.1, J3.1, R2.1, R3.1, R4.1, R5.1, R10.1, U1.2, U2.4, U4.2, U6.1, U6.13
BAT_PLUS: J2.1, Q1.6
CC1: J1.A5, R8.1
CC2: J1.B5, R9.1
CHRG_LED: D2.1, R2.2
CHRG_OUT: D2.2, U2.7
CS_DRAIN: Q1.3, Q1.4, U3.2
EN: R10.2, U1.3
EPD_BUSY: J3.8, U1.20
EPD_CLK: J3.4, U1.15
EPD_CS: J3.5, U1.19
EPD_DC: J3.6, U1.17
EPD_MOSI: J3.3, U1.16
EPD_RST: J3.7, U1.18
GND: C3.2, C4.2, C5.2, C6.2, C7.2, C9.2, J1.A1, J1.A12, J1.B1, J1.B12, J2.2, J3.2, Q1.1, R1.2, R8.2, R9.2, SW1.1, U1.1, U1.31, U1.32, U1.40, U1.41, U2.1, U2.5, U3.6, U4.1, U6.8, U6.9, U6.11, U6.18
I2C_SCL: R5.2, U1.10, U6.23
I2C_SDA: R4.2, U1.9, U6.24
JOY_CENTER: SW1.2, U1.8
OC: Q1.5, U3.3
OD: Q1.2, U3.1
PROG: R1.1, U2.2
REGOUT: C9.1, U6.10
STDBY_LED: D3.1, R3.2
STDBY_OUT: D3.2, U2.6
USB_DM: J1.A7, J1.B7, U1.13
USB_DP: J1.A6, J1.B6, U1.14
VBAT: C5.1, U2.3, U3.4, U3.5, U4.3
VBUS: D1.1, J1.A4, J1.B4
VBUS_CHG: D1.2, U2.8
