rompasaurus/regardedPal/tools/devtool/devtool.py

#!/usr/bin/env python3
"""
Dilder DevTool — Multi-Board Development Companion

Tkinter GUI for developing on the Pico W and ESP32-S3 (Olimex DevKit-Lipo)
with the Waveshare 2.13" e-ink display.

Features:
  - Board selector (Pico W / ESP32-S3) with auto-detection
  - E-ink display emulator (250x122, 1-bit) with drawing and text tools
  - Serial monitor for live printf output
  - Firmware flash utility (Pico BOOTSEL + ESP32 esptool)
  - Asset manager (save/load/preview 1-bit bitmaps)
  - GPIO pin reference for both boards

Usage:
  python3 tools/devtool/devtool.py
"""

import io
import json
import os
import platform
import random
import re
import shutil
import struct
import subprocess
import sys
import threading
import time
from pathlib import Path
from datetime import datetime

# ── Dependency gate ─────────────────────────────────────────────────────────
# When run directly (python3 devtool.py), check for system packages before
# importing them. If missing, offer to install and re-exec.
# When imported as a module (e.g. by tests), skip the gate — the caller
# is responsible for ensuring deps are present.

def _check_and_install_deps():
    """Check for required system packages and offer to install them."""
    missing = []

    try:
        import tkinter as _tk  # noqa: F401
    except ImportError:
        missing.append(("tkinter", {"arch": "tk", "debian": "python3-tk", "fedora": "python3-tkinter"}))

    try:
        import serial as _ser  # noqa: F401
    except ImportError:
        missing.append(("pyserial", {"arch": "python-pyserial", "debian": "python3-serial", "fedora": "python3-pyserial"}))

    if not missing:
        return True

    # Detect distro
    distro = "unknown"
    try:
        with open("/etc/os-release") as f:
            content = f.read().lower()
        if "cachyos" in content or "arch" in content or "manjaro" in content:
            distro = "arch"
        elif "ubuntu" in content or "debian" in content or "mint" in content:
            distro = "debian"
        elif "fedora" in content or "rhel" in content or "centos" in content:
            distro = "fedora"
    except FileNotFoundError:
        pass

    names = [n for n, _ in missing]
    pkgs = [pkg_map.get(distro) for _, pkg_map in missing if pkg_map.get(distro)]

    print(f"\n  Missing dependencies: {', '.join(names)}")

    if not pkgs:
        print("  Unknown distro — install manually and re-run.")
        return False

    if distro == "arch":
        cmd = ["sudo", "pacman", "-S", "--needed"] + pkgs
    elif distro == "debian":
        cmd = ["sudo", "apt", "install", "-y"] + pkgs
    elif distro == "fedora":
        cmd = ["sudo", "dnf", "install", "-y"] + pkgs
    else:
        return False

    print(f"  Installing: {' '.join(pkgs)}")
    print(f"  $ {' '.join(cmd)}\n")
    result = subprocess.run(cmd)
    if result.returncode == 0:
        print("\n  Dependencies installed. Starting DevTool...\n")
        return True
    else:
        print(f"\n  Install failed. Run manually:")
        print(f"    {' '.join(cmd)}")
        return False


if __name__ == "__main__":
    # Check deps BEFORE the module-level class definitions execute.
    # If deps are missing and install succeeds, re-exec so the module
    # loads fresh with the new packages.
    _needs_install = False
    try:
        import tkinter as _tk_test  # noqa: F401
        import serial as _ser_test  # noqa: F401
    except ImportError:
        _needs_install = True

    if _needs_install:
        if _check_and_install_deps():
            os.execv(sys.executable, [sys.executable] + sys.argv)
        else:
            sys.exit(1)

# ── Now safe to import ──────────────────────────────────────────────────────

import serial
import serial.tools.list_ports
import tkinter as tk
from tkinter import ttk, filedialog, messagebox, colorchooser, simpledialog, font as tkfont

# ─────────────────────────────────────────────────────────────────────────────
# Constants
# ─────────────────────────────────────────────────────────────────────────────

APP_NAME = "Dilder DevTool"
APP_VERSION = "1.1.0"

# ── Target boards ──────────────────────────────────────────────────────────
BOARD_PICO_W = "pico_w"
BOARD_PICO2_W = "pico2_w"
BOARD_ESP32S3 = "esp32s3"

BOARD_LABELS = {
    BOARD_PICO_W:  "Pico W (RP2040)",
    BOARD_PICO2_W: "Pico 2 W (RP2350)",
    BOARD_ESP32S3: "ESP32-S3 (Olimex)",
}

# Boards that use the Pico SDK (UF2/BOOTSEL workflow)
PICO_BOARDS = {BOARD_PICO_W, BOARD_PICO2_W}

# ESP32-S3 flash size (Olimex DevKit-Lipo N8R8)
ESP32_FLASH_KB = 8192  # 8 MB

# Display dimensions (Waveshare 2.13" V3)
DISPLAY_W = 250
DISPLAY_H = 122

# Scale factor for the emulator canvas
CANVAS_SCALE = 3

# Project paths
PROJECT_ROOT = Path(__file__).parent.parent.parent.resolve()
ASSETS_DIR = PROJECT_ROOT / "assets"
DEV_SETUP = PROJECT_ROOT / "dev-setup"

# Serial defaults
DEFAULT_BAUD = 115200
SERIAL_TIMEOUT = 0.1

# Ensure ~/.local/bin is in PATH (pipx installs PlatformIO/esptool there,
# but Python may not inherit it from the shell profile).
_local_bin = str(Path.home() / ".local" / "bin")
if _local_bin not in os.environ.get("PATH", ""):
    os.environ["PATH"] = _local_bin + os.pathsep + os.environ.get("PATH", "")

# Colours for the UI
BG_DARK = "#1e1e2e"
BG_PANEL = "#282840"
BG_CANVAS = "#2a2a3a"
FG_TEXT = "#cdd6f4"
FG_DIM = "#6c7086"
FG_ACCENT = "#89b4fa"
FG_GREEN = "#a6e3a1"
FG_RED = "#f38ba8"
FG_YELLOW = "#f9e2af"
FG_MAGENTA = "#cba6f7"

# E-ink colours (on screen)
EINK_WHITE = "#e8e8e8"
EINK_BLACK = "#1a1a1a"


# ─────────────────────────────────────────────────────────────────────────────
# Utility helpers
# ─────────────────────────────────────────────────────────────────────────────

def find_pico_serial():
    """Find the Pico W serial port.

    Checks all comports for ttyACM / usbmodem devices, or the Raspberry Pi
    USB vendor ID (2E8A).  Handles port number changes when switching USB
    ports (ttyACM0 → ttyACM1, etc.).
    """
    # First pass: match by Raspberry Pi Pico VID (0x2E8A)
    for port in serial.tools.list_ports.comports():
        if port.vid == 0x2E8A:
            return port.device
    # Second pass: match by device name pattern (broader)
    for port in serial.tools.list_ports.comports():
        if "ttyACM" in port.device or "usbmodem" in port.device:
            return port.device
    return None


def find_esp32_serial():
    """Find the ESP32-S3 serial port (Olimex DevKit-Lipo via CH340X).

    The Olimex board's USB-UART port uses a CH340X chip which shows up as
    /dev/ttyUSB* on Linux. The CH340 VID is 0x1A86, PID 0x55D4 (CH340X)
    or 0x7523 (CH340G/CH340C).
    """
    CH340_VID = 0x1A86
    CH340X_PIDS = {0x55D4, 0x7523}  # CH340X, CH340G/C
    # First pass: match by CH340 VID + PID
    for port in serial.tools.list_ports.comports():
        if port.vid == CH340_VID and port.pid in CH340X_PIDS:
            return port.device
    # Second pass: match by ttyUSB pattern (broader)
    for port in serial.tools.list_ports.comports():
        if "ttyUSB" in port.device:
            return port.device
    return None


def find_serial_for_board(board):
    """Find the serial port for the given target board."""
    if board == BOARD_ESP32S3:
        return find_esp32_serial()
    return find_pico_serial()


def find_rpi_rp2_mount():
    """Find the Pico BOOTSEL USB drive for flashing.

    Pico W (RP2040) mounts as 'RPI-RP2'.
    Pico 2 W (RP2350) mounts as 'RP2350'.
    """
    user = os.environ.get("USER", "")
    # Labels for both Pico W and Pico 2 W BOOTSEL modes
    labels = ["RPI-RP2", "RP2350"]
    for label in labels:
        paths = [
            Path(f"/run/media/{user}/{label}"),
            Path(f"/media/{user}/{label}"),
            Path(f"/mnt/{label}"),
        ]
        for p in paths:
            if p.exists() and p.is_dir():
                return p
    # Fallback: findmnt
    for label in labels:
        try:
            result = subprocess.run(
                ["findmnt", "-rno", "TARGET", "-S", f"LABEL={label}"],
                capture_output=True, text=True, timeout=3
            )
            if result.returncode == 0 and result.stdout.strip():
                p = Path(result.stdout.strip().splitlines()[0])
                if p.exists():
                    return p
        except (FileNotFoundError, subprocess.TimeoutExpired):
            pass
    return None


# ─────────────────────────────────────────────────────────────────────────────
# E-Ink Display Emulator
# ─────────────────────────────────────────────────────────────────────────────

class DisplayEmulator(ttk.Frame):
    """
    250x122 pixel 1-bit e-ink display emulator with drawing tools.

    Tools: pencil, eraser, line, rectangle, filled rectangle, text
    Colours: black (draw) and white (erase) only — matches real e-ink.
    """

    TOOLS = ["pencil", "eraser", "line", "rectangle", "filled_rect", "text"]
    TOOL_LABELS = {
        "pencil": "Pencil",
        "eraser": "Eraser",
        "line": "Line",
        "rectangle": "Rect",
        "filled_rect": "Fill Rect",
        "text": "Text",
    }

    def __init__(self, parent, app):
        super().__init__(parent)
        self.app = app
        self.scale = CANVAS_SCALE
        self.canvas_w = DISPLAY_W * self.scale
        self.canvas_h = DISPLAY_H * self.scale

        # Pixel buffer: 0 = white, 1 = black
        self.pixels = [[0] * DISPLAY_W for _ in range(DISPLAY_H)]

        self.current_tool = "pencil"
        self.brush_size = 1
        self.current_font_size = 16
        self.drag_start = None

        self._build_ui()
        self._clear_canvas()

    def _build_ui(self):
        # ── Toolbar ──
        toolbar = ttk.Frame(self)
        toolbar.pack(fill=tk.X, padx=5, pady=(5, 2))

        ttk.Label(toolbar, text="Tool:").pack(side=tk.LEFT, padx=(0, 5))

        self.tool_var = tk.StringVar(value="pencil")
        for tool_key in self.TOOLS:
            rb = ttk.Radiobutton(
                toolbar, text=self.TOOL_LABELS[tool_key],
                variable=self.tool_var, value=tool_key,
                command=self._on_tool_change
            )
            rb.pack(side=tk.LEFT, padx=2)

        ttk.Separator(toolbar, orient=tk.VERTICAL).pack(side=tk.LEFT, fill=tk.Y, padx=8)

        ttk.Label(toolbar, text="Size:").pack(side=tk.LEFT, padx=(0, 3))
        self.size_var = tk.IntVar(value=1)
        size_spin = ttk.Spinbox(toolbar, from_=1, to=10, width=3,
                                textvariable=self.size_var)
        size_spin.pack(side=tk.LEFT, padx=(0, 8))

        ttk.Label(toolbar, text="Font:").pack(side=tk.LEFT, padx=(0, 3))
        self.font_size_var = tk.IntVar(value=16)
        font_spin = ttk.Spinbox(toolbar, from_=8, to=48, width=3,
                                textvariable=self.font_size_var)
        font_spin.pack(side=tk.LEFT, padx=(0, 8))

        ttk.Separator(toolbar, orient=tk.VERTICAL).pack(side=tk.LEFT, fill=tk.Y, padx=8)

        ttk.Button(toolbar, text="Clear", command=self._clear_canvas).pack(side=tk.LEFT, padx=2)
        ttk.Button(toolbar, text="Invert", command=self._invert_canvas).pack(side=tk.LEFT, padx=2)
        ttk.Button(toolbar, text="Save", command=self._save_image).pack(side=tk.LEFT, padx=2)
        ttk.Button(toolbar, text="Load", command=self._load_image).pack(side=tk.LEFT, padx=2)
        ttk.Button(toolbar, text="Send to Pico", command=self._send_to_pico).pack(side=tk.LEFT, padx=2)

        # ── Canvas ──
        canvas_frame = ttk.Frame(self)
        canvas_frame.pack(fill=tk.BOTH, expand=True, padx=5, pady=5)

        self.canvas = tk.Canvas(
            canvas_frame,
            width=self.canvas_w,
            height=self.canvas_h,
            bg=EINK_WHITE,
            cursor="crosshair",
            highlightthickness=1,
            highlightbackground=FG_DIM,
        )
        self.canvas.pack()

        # ── Status bar ──
        status = ttk.Frame(self)
        status.pack(fill=tk.X, padx=5, pady=(0, 5))

        self.pos_label = ttk.Label(status, text="x: -  y: -")
        self.pos_label.pack(side=tk.LEFT)

        self.info_label = ttk.Label(status, text=f"{DISPLAY_W}x{DISPLAY_H}  1-bit monochrome")
        self.info_label.pack(side=tk.RIGHT)

        # ── Bindings ──
        self.canvas.bind("<Button-1>", self._on_click)
        self.canvas.bind("<B1-Motion>", self._on_drag)
        self.canvas.bind("<ButtonRelease-1>", self._on_release)
        self.canvas.bind("<Motion>", self._on_motion)

    def _on_tool_change(self):
        self.current_tool = self.tool_var.get()

    def _canvas_to_pixel(self, cx, cy):
        """Convert canvas coords to pixel coords."""
        px = int(cx / self.scale)
        py = int(cy / self.scale)
        return max(0, min(px, DISPLAY_W - 1)), max(0, min(py, DISPLAY_H - 1))

    def _set_pixel(self, px, py, value):
        """Set a pixel in the buffer and draw it on the canvas."""
        if 0 <= px < DISPLAY_W and 0 <= py < DISPLAY_H:
            self.pixels[py][px] = value
            colour = EINK_BLACK if value else EINK_WHITE
            x1 = px * self.scale
            y1 = py * self.scale
            self.canvas.create_rectangle(
                x1, y1, x1 + self.scale, y1 + self.scale,
                fill=colour, outline=colour, tags="pixel"
            )

    def _draw_brush(self, px, py, value):
        """Draw a square brush at the given pixel position."""
        size = self.size_var.get()
        half = size // 2
        for dy in range(-half, -half + size):
            for dx in range(-half, -half + size):
                self._set_pixel(px + dx, py + dy, value)

    def _on_click(self, event):
        px, py = self._canvas_to_pixel(event.x, event.y)
        tool = self.tool_var.get()

        if tool == "pencil":
            self._draw_brush(px, py, 1)
        elif tool == "eraser":
            self._draw_brush(px, py, 0)
        elif tool in ("line", "rectangle", "filled_rect"):
            self.drag_start = (px, py)
        elif tool == "text":
            self._place_text(px, py)

    def _on_drag(self, event):
        px, py = self._canvas_to_pixel(event.x, event.y)
        tool = self.tool_var.get()

        if tool == "pencil":
            self._draw_brush(px, py, 1)
        elif tool == "eraser":
            self._draw_brush(px, py, 0)
        elif tool in ("line", "rectangle", "filled_rect"):
            # Preview with rubber band
            self.canvas.delete("preview")
            if self.drag_start:
                sx, sy = self.drag_start
                x1, y1 = sx * self.scale, sy * self.scale
                x2, y2 = px * self.scale, py * self.scale
                if tool == "line":
                    self.canvas.create_line(x1, y1, x2, y2, fill=EINK_BLACK,
                                            width=self.size_var.get(), tags="preview")
                elif tool == "rectangle":
                    self.canvas.create_rectangle(x1, y1, x2, y2, outline=EINK_BLACK,
                                                 width=self.size_var.get(), tags="preview")
                elif tool == "filled_rect":
                    self.canvas.create_rectangle(x1, y1, x2, y2, fill=EINK_BLACK,
                                                 outline=EINK_BLACK, tags="preview")

    def _on_release(self, event):
        px, py = self._canvas_to_pixel(event.x, event.y)
        tool = self.tool_var.get()
        self.canvas.delete("preview")

        if self.drag_start and tool in ("line", "rectangle", "filled_rect"):
            sx, sy = self.drag_start
            if tool == "line":
                self._draw_line(sx, sy, px, py)
            elif tool == "rectangle":
                self._draw_rect(sx, sy, px, py, fill=False)
            elif tool == "filled_rect":
                self._draw_rect(sx, sy, px, py, fill=True)
            self.drag_start = None

    def _on_motion(self, event):
        px, py = self._canvas_to_pixel(event.x, event.y)
        self.pos_label.config(text=f"x: {px}  y: {py}")

    def _draw_line(self, x0, y0, x1, y1):
        """Bresenham's line algorithm."""
        dx = abs(x1 - x0)
        dy = abs(y1 - y0)
        sx = 1 if x0 < x1 else -1
        sy = 1 if y0 < y1 else -1
        err = dx - dy
        while True:
            self._draw_brush(x0, y0, 1)
            if x0 == x1 and y0 == y1:
                break
            e2 = 2 * err
            if e2 > -dy:
                err -= dy
                x0 += sx
            if e2 < dx:
                err += dx
                y0 += sy

    def _draw_rect(self, x0, y0, x1, y1, fill=False):
        """Draw a rectangle (outline or filled)."""
        left, right = min(x0, x1), max(x0, x1)
        top, bottom = min(y0, y1), max(y0, y1)
        if fill:
            for y in range(top, bottom + 1):
                for x in range(left, right + 1):
                    self._set_pixel(x, y, 1)
        else:
            for x in range(left, right + 1):
                self._set_pixel(x, top, 1)
                self._set_pixel(x, bottom, 1)
            for y in range(top, bottom + 1):
                self._set_pixel(left, y, 1)
                self._set_pixel(right, y, 1)

    def _place_text(self, px, py):
        """Place text at the clicked position."""
        text = simpledialog.askstring("Draw Text", "Enter text:",
                                      parent=self.winfo_toplevel())
        if not text:
            return

        font_size = self.font_size_var.get()
        # Render text to pixel buffer using a temporary canvas trick
        tmp = tk.Canvas(self, width=DISPLAY_W, height=DISPLAY_H)
        fnt = tkfont.Font(family="Courier", size=font_size, weight="bold")
        tmp.create_text(0, 0, text=text, anchor=tk.NW, font=fnt, fill="black")
        tmp.update_idletasks()

        # Get text bounding box and rasterize character by character
        # Simple approach: use font metrics to estimate pixel placement
        char_w = fnt.measure("M")
        char_h = fnt.metrics("linespace")
        tmp.destroy()

        # Draw each character as a block of pixels
        for i, ch in enumerate(text):
            cx = px + i * (char_w // self.scale + 1)
            # Simple bitmap font rendering — draw character outline
            for row in range(min(char_h, DISPLAY_H - py)):
                for col in range(min(char_w, DISPLAY_W - cx)):
                    # Approximate: fill a rectangle for each character
                    pass

        # Fallback: draw text directly on the scaled canvas and extract
        self.canvas.create_text(
            px * self.scale, py * self.scale,
            text=text, anchor=tk.NW,
            font=tkfont.Font(family="Courier", size=font_size * self.scale // 3, weight="bold"),
            fill=EINK_BLACK, tags="text_render"
        )

        # Rasterize canvas text to pixel buffer
        self._rasterize_text_to_buffer(px, py, text, font_size)

    def _rasterize_text_to_buffer(self, px, py, text, font_size):
        """Render text into the pixel buffer using a simple bitmap approach."""
        # Use Pillow if available for proper rasterization, else approximate
        try:
            from PIL import Image, ImageDraw, ImageFont
            img = Image.new("1", (DISPLAY_W, DISPLAY_H), 1)  # white
            draw = ImageDraw.Draw(img)
            try:
                pil_font = ImageFont.truetype("/usr/share/fonts/TTF/DejaVuSansMono.ttf", font_size)
            except (OSError, IOError):
                try:
                    pil_font = ImageFont.truetype("/usr/share/fonts/truetype/dejavu/DejaVuSansMono.ttf", font_size)
                except (OSError, IOError):
                    pil_font = ImageFont.load_default()
            draw.text((px, py), text, font=pil_font, fill=0)  # black text

            # Copy rendered pixels into buffer
            for y in range(DISPLAY_H):
                for x in range(DISPLAY_W):
                    if img.getpixel((x, y)) == 0:
                        self._set_pixel(x, y, 1)
        except ImportError:
            # No Pillow — just mark approximate character positions
            char_w = max(font_size // 2, 6)
            char_h = font_size
            for i, ch in enumerate(text):
                if ch == " ":
                    continue
                cx = px + i * char_w
                for dy in range(min(char_h, DISPLAY_H - py)):
                    for dx in range(min(char_w, DISPLAY_W - cx)):
                        if 0 <= cx + dx < DISPLAY_W and 0 <= py + dy < DISPLAY_H:
                            self._set_pixel(cx + dx, py + dy, 1)

    def _clear_canvas(self):
        """Clear to white."""
        self.canvas.delete("all")
        self.pixels = [[0] * DISPLAY_W for _ in range(DISPLAY_H)]
        self.canvas.configure(bg=EINK_WHITE)

    def _invert_canvas(self):
        """Invert all pixels."""
        for y in range(DISPLAY_H):
            for x in range(DISPLAY_W):
                self.pixels[y][x] = 1 - self.pixels[y][x]
        self._redraw_from_buffer()

    def _redraw_from_buffer(self):
        """Redraw the entire canvas from the pixel buffer."""
        self.canvas.delete("all")
        for y in range(DISPLAY_H):
            for x in range(DISPLAY_W):
                if self.pixels[y][x]:
                    x1 = x * self.scale
                    y1 = y * self.scale
                    self.canvas.create_rectangle(
                        x1, y1, x1 + self.scale, y1 + self.scale,
                        fill=EINK_BLACK, outline=EINK_BLACK, tags="pixel"
                    )

    def _pixels_to_bytes(self):
        """Convert pixel buffer to packed bytes (MSB first, 1=black)."""
        byte_width = (DISPLAY_W + 7) // 8
        data = bytearray(byte_width * DISPLAY_H)
        for y in range(DISPLAY_H):
            for x in range(DISPLAY_W):
                if self.pixels[y][x]:
                    byte_idx = y * byte_width + x // 8
                    bit_idx = 7 - (x % 8)
                    data[byte_idx] |= (1 << bit_idx)
        return bytes(data)

    def _bytes_to_pixels(self, data):
        """Load packed bytes into the pixel buffer."""
        byte_width = (DISPLAY_W + 7) // 8
        self.pixels = [[0] * DISPLAY_W for _ in range(DISPLAY_H)]
        for y in range(DISPLAY_H):
            for x in range(DISPLAY_W):
                byte_idx = y * byte_width + x // 8
                bit_idx = 7 - (x % 8)
                if byte_idx < len(data) and data[byte_idx] & (1 << bit_idx):
                    self.pixels[y][x] = 1

    def _save_image(self):
        """Save the current canvas as a .pbm (P4 binary) and raw .bin file."""
        ASSETS_DIR.mkdir(exist_ok=True)

        name = simpledialog.askstring("Save Image", "Asset name (no extension):",
                                       parent=self.winfo_toplevel())
        if not name:
            return

        name = re.sub(r'[^\w\-]', '_', name)

        # Save as PBM (P4 binary — 1-bit, no dependencies)
        pbm_path = ASSETS_DIR / f"{name}.pbm"
        byte_width = (DISPLAY_W + 7) // 8
        with open(pbm_path, "wb") as f:
            f.write(f"P4\n{DISPLAY_W} {DISPLAY_H}\n".encode())
            for y in range(DISPLAY_H):
                row = 0
                for x in range(DISPLAY_W):
                    if x > 0 and x % 8 == 0:
                        f.write(struct.pack("B", row))
                        row = 0
                    if self.pixels[y][x]:
                        row |= (1 << (7 - x % 8))
                # Write last byte of row (with padding)
                f.write(struct.pack("B", row))
                # Pad remaining bytes if needed
                remaining = byte_width - ((DISPLAY_W + 7) // 8)
                f.write(b'\x00' * remaining)

        # Save as raw binary (for direct upload to Pico)
        bin_path = ASSETS_DIR / f"{name}.bin"
        with open(bin_path, "wb") as f:
            f.write(self._pixels_to_bytes())

        # Save as PNG if Pillow is available
        try:
            from PIL import Image
            img = Image.new("1", (DISPLAY_W, DISPLAY_H), 1)
            for y in range(DISPLAY_H):
                for x in range(DISPLAY_W):
                    if self.pixels[y][x]:
                        img.putpixel((x, y), 0)
            png_path = ASSETS_DIR / f"{name}.png"
            img.save(str(png_path))
            self.app.log(f"Saved: {pbm_path.name}, {bin_path.name}, {png_path.name}")
        except ImportError:
            self.app.log(f"Saved: {pbm_path.name}, {bin_path.name} (install Pillow for PNG)")

    def _load_image(self):
        """Load a .pbm, .bin, or .png image."""
        path = filedialog.askopenfilename(
            title="Load Image",
            initialdir=str(ASSETS_DIR),
            filetypes=[
                ("All supported", "*.pbm *.bin *.png"),
                ("PBM", "*.pbm"),
                ("Raw binary", "*.bin"),
                ("PNG", "*.png"),
            ]
        )
        if not path:
            return

        p = Path(path)
        if p.suffix == ".bin":
            data = p.read_bytes()
            self._bytes_to_pixels(data)
            self._redraw_from_buffer()
        elif p.suffix == ".pbm":
            self._load_pbm(p)
            self._redraw_from_buffer()
        elif p.suffix == ".png":
            self._load_png(p)
            self._redraw_from_buffer()

        self.app.log(f"Loaded: {p.name}")

    def _load_pbm(self, path):
        """Load a P4 (binary) or P1 (ASCII) PBM file."""
        with open(path, "rb") as f:
            magic = f.readline().strip()
            # Skip comments
            line = f.readline()
            while line.startswith(b"#"):
                line = f.readline()
            w, h = map(int, line.split())
            if magic == b"P4":
                data = f.read()
                self._bytes_to_pixels(data)
            elif magic == b"P1":
                text = f.read().decode()
                vals = [int(c) for c in text.split()]
                self.pixels = [[0] * DISPLAY_W for _ in range(DISPLAY_H)]
                idx = 0
                for y in range(min(h, DISPLAY_H)):
                    for x in range(min(w, DISPLAY_W)):
                        if idx < len(vals):
                            self.pixels[y][x] = vals[idx]
                            idx += 1

    def _load_png(self, path):
        """Load a PNG via Pillow."""
        try:
            from PIL import Image
            img = Image.open(str(path)).convert("1").resize((DISPLAY_W, DISPLAY_H))
            self.pixels = [[0] * DISPLAY_W for _ in range(DISPLAY_H)]
            for y in range(DISPLAY_H):
                for x in range(DISPLAY_W):
                    if img.getpixel((x, y)) == 0:
                        self.pixels[y][x] = 1
        except ImportError:
            messagebox.showerror("Error", "Pillow is required for PNG support.\n\npip install Pillow")

    def _send_to_pico(self):
        """Send the current image to the board via serial (non-blocking)."""
        bn = BOARD_LABELS.get(self.app.target_board, "Pico")
        port = find_pico_serial()
        if not port:
            messagebox.showwarning("No Board", f"No {bn} detected on USB serial.")
            return

        data = self._pixels_to_bytes()
        self.app.log(f"Sending {len(data)} bytes to {port}...")

        def _do_send():
            try:
                with serial.Serial(port, DEFAULT_BAUD, timeout=2,
                                    write_timeout=5) as ser:
                    ser.write(b"IMG:")
                    ser.write(struct.pack("<HH", DISPLAY_W, DISPLAY_H))
                    ser.write(data)
                    ser.flush()
                self.app.log(f"Image sent to {bn} ({len(data)} bytes)")
            except serial.SerialTimeoutException:
                self.after(0, lambda: messagebox.showwarning(
                    "Send Timed Out",
                    f"{bn} needs IMG-receiver firmware to display images.\n\n"
                    "Steps:\n"
                    "1) Go to the Programs tab\n"
                    "2) Put board in BOOTSEL mode (hold BOOTSEL + plug in)\n"
                    "3) Click 'Build & Flash'\n"
                    "4) Wait for reboot, then retry Send to Pico"))
            except serial.SerialException as e:
                self.after(0, lambda: messagebox.showerror("Serial Error", str(e)))

        threading.Thread(target=_do_send, daemon=True).start()


# ─────────────────────────────────────────────────────────────────────────────
# Serial Monitor
# ─────────────────────────────────────────────────────────────────────────────

class SerialMonitor(ttk.Frame):
    """
    Live serial monitor for Pico W USB output.

    Connects to /dev/ttyACM0 at 115200 baud, displays incoming text,
    supports sending commands, and can log to file.
    """

    def __init__(self, parent, app):
        super().__init__(parent)
        self.app = app
        self.serial_conn = None
        self.read_thread = None
        self.running = False
        self.log_file = None
        self.auto_scroll = True

        self._build_ui()

    def _build_ui(self):
        # ── Connection bar ──
        conn = ttk.Frame(self)
        conn.pack(fill=tk.X, padx=5, pady=(5, 2))

        ttk.Label(conn, text="Port:").pack(side=tk.LEFT, padx=(0, 3))
        self.port_var = tk.StringVar()
        self.port_combo = ttk.Combobox(conn, textvariable=self.port_var, width=18)
        self.port_combo.pack(side=tk.LEFT, padx=(0, 5))

        ttk.Button(conn, text="Refresh", command=self._refresh_ports).pack(side=tk.LEFT, padx=2)

        ttk.Label(conn, text="Baud:").pack(side=tk.LEFT, padx=(8, 3))
        self.baud_var = tk.StringVar(value=str(DEFAULT_BAUD))
        baud_combo = ttk.Combobox(conn, textvariable=self.baud_var, width=8,
                                   values=["9600", "19200", "38400", "57600", "115200", "230400"])
        baud_combo.pack(side=tk.LEFT, padx=(0, 8))

        self.connect_btn = ttk.Button(conn, text="Connect", command=self._toggle_connection)
        self.connect_btn.pack(side=tk.LEFT, padx=2)

        self.status_label = ttk.Label(conn, text="Disconnected", foreground=FG_RED)
        self.status_label.pack(side=tk.LEFT, padx=8)

        ttk.Separator(conn, orient=tk.VERTICAL).pack(side=tk.LEFT, fill=tk.Y, padx=8)

        self.autoscroll_var = tk.BooleanVar(value=True)
        ttk.Checkbutton(conn, text="Auto-scroll", variable=self.autoscroll_var).pack(side=tk.LEFT)

        ttk.Button(conn, text="Clear", command=self._clear_output).pack(side=tk.LEFT, padx=5)
        ttk.Button(conn, text="Save Log", command=self._save_log).pack(side=tk.LEFT, padx=2)

        # ── Output area ──
        output_frame = ttk.Frame(self)
        output_frame.pack(fill=tk.BOTH, expand=True, padx=5, pady=5)

        self.output_text = tk.Text(
            output_frame, wrap=tk.WORD, state=tk.DISABLED,
            bg=BG_DARK, fg=FG_TEXT, insertbackground=FG_TEXT,
            font=("JetBrains Mono", 10),
            selectbackground=FG_ACCENT, selectforeground=BG_DARK,
        )
        scrollbar = ttk.Scrollbar(output_frame, command=self.output_text.yview)
        self.output_text.configure(yscrollcommand=scrollbar.set)

        scrollbar.pack(side=tk.RIGHT, fill=tk.Y)
        self.output_text.pack(fill=tk.BOTH, expand=True)

        # ── Input bar ──
        input_frame = ttk.Frame(self)
        input_frame.pack(fill=tk.X, padx=5, pady=(0, 5))

        self.input_entry = ttk.Entry(input_frame)
        self.input_entry.pack(side=tk.LEFT, fill=tk.X, expand=True, padx=(0, 5))
        self.input_entry.bind("<Return>", self._send_command)

        ttk.Button(input_frame, text="Send", command=self._send_command).pack(side=tk.LEFT)
        ttk.Button(input_frame, text="Ctrl+C", command=self._send_interrupt).pack(side=tk.LEFT, padx=5)
        ttk.Button(input_frame, text="Reset", command=self._send_reset).pack(side=tk.LEFT)

        self._refresh_ports()

    def _refresh_ports(self):
        ports = [p.device for p in serial.tools.list_ports.comports()]
        self.port_combo["values"] = ports
        # Auto-select Pico
        pico = find_pico_serial()
        if pico:
            self.port_var.set(pico)
        elif ports:
            self.port_var.set(ports[0])

    def _toggle_connection(self):
        if self.running:
            self._disconnect()
        else:
            self._connect()

    def _connect(self):
        port = self.port_var.get()
        baud = int(self.baud_var.get())

        if not port:
            messagebox.showwarning("No Port", "Select a serial port first.")
            return

        try:
            self.serial_conn = serial.Serial(port, baud, timeout=SERIAL_TIMEOUT)
            self.running = True
            self.connect_btn.config(text="Disconnect")
            self.status_label.config(text=f"Connected: {port}", foreground=FG_GREEN)
            self.app.log(f"Serial connected: {port} @ {baud}")

            self.read_thread = threading.Thread(target=self._read_loop, daemon=True)
            self.read_thread.start()
        except serial.SerialException as e:
            messagebox.showerror("Connection Failed", str(e))

    def _disconnect(self):
        self.running = False
        if self.serial_conn and self.serial_conn.is_open:
            self.serial_conn.close()
        self.serial_conn = None
        self.connect_btn.config(text="Connect")
        self.status_label.config(text="Disconnected", foreground=FG_RED)
        self.app.log("Serial disconnected")

    def _read_loop(self):
        """Background thread reading serial data."""
        while self.running and self.serial_conn and self.serial_conn.is_open:
            try:
                data = self.serial_conn.readline()
                if data:
                    text = data.decode("utf-8", errors="replace")
                    self._append_output(text)
            except serial.SerialException:
                self.running = False
                self.winfo_toplevel().after(0, self._disconnect)
                break
            except Exception:
                pass

    def _append_output(self, text):
        """Append text to the output (thread-safe via after())."""
        def _do():
            self.output_text.configure(state=tk.NORMAL)
            self.output_text.insert(tk.END, text)
            if self.autoscroll_var.get():
                self.output_text.see(tk.END)
            self.output_text.configure(state=tk.DISABLED)
        self.winfo_toplevel().after(0, _do)

    def _send_command(self, event=None):
        cmd = self.input_entry.get()
        if not cmd or not self.serial_conn or not self.serial_conn.is_open:
            return
        try:
            self.serial_conn.write((cmd + "\r\n").encode())
            self._append_output(f"> {cmd}\n")
            self.input_entry.delete(0, tk.END)
        except serial.SerialException as e:
            self.app.log(f"Send failed: {e}")

    def _send_interrupt(self):
        if self.serial_conn and self.serial_conn.is_open:
            self.serial_conn.write(b"\x03")  # Ctrl+C

    def _send_reset(self):
        if self.serial_conn and self.serial_conn.is_open:
            self.serial_conn.write(b"\x04")  # Ctrl+D soft reset

    def _clear_output(self):
        self.output_text.configure(state=tk.NORMAL)
        self.output_text.delete("1.0", tk.END)
        self.output_text.configure(state=tk.DISABLED)

    def _save_log(self):
        path = filedialog.asksaveasfilename(
            title="Save Serial Log",
            defaultextension=".txt",
            filetypes=[("Text files", "*.txt"), ("All files", "*.*")],
            initialfile=f"serial_log_{datetime.now():%Y%m%d_%H%M%S}.txt"
        )
        if path:
            content = self.output_text.get("1.0", tk.END)
            Path(path).write_text(content)
            self.app.log(f"Log saved: {path}")

    def destroy(self):
        self._disconnect()
        super().destroy()


# ─────────────────────────────────────────────────────────────────────────────
# Firmware Flash Utility
# ─────────────────────────────────────────────────��───────────────────────────

class FlashUtility(ttk.Frame):
    """Flash firmware to the target board (Pico W via BOOTSEL, ESP32-S3 via esptool)."""

    @staticmethod
    def _pico_instructions(board=None):
        board_name = BOARD_LABELS.get(board, "Pico W (RP2040)")
        drive = "RP2350" if board == BOARD_PICO2_W else "RPI-RP2"
        return (
            f"To flash the {board_name}:\n\n"
            f"1. Unplug the board from USB\n"
            f"2. Hold down the BOOTSEL button (small white button)\n"
            f"3. While holding BOOTSEL, plug in the USB cable\n"
            f"4. Release BOOTSEL after 1 second\n"
            f'5. Click "Detect {drive}" above\n'
            f"6. Click \"Flash\" to copy the firmware\n\n"
            f"The board will reboot automatically after flashing.\n"
            f"The {drive} drive will disappear — this is normal."
        )

    _ESP32_INSTRUCTIONS = """\
To flash the ESP32-S3 (Olimex DevKit-Lipo):

1. Connect the USB-UART port (near the buttons, CH340X)
2. Click "Detect ESP32" to find the serial port
3. Select a .bin firmware or use PlatformIO to build
4. Click "Flash" to upload via esptool

Auto-reset: The CH340X handles bootloader entry automatically.
No need to hold BOOT — just click Flash.

If auto-reset fails:
  1. Hold the BOOT button
  2. Press and release RST
  3. Release BOOT
  4. Click Flash again"""

    def __init__(self, parent, app):
        super().__init__(parent)
        self.app = app
        self._current_board = BOARD_PICO_W
        self._build_ui()

    def _build_ui(self):
        # ── Firmware file selection ──
        file_frame = ttk.LabelFrame(self, text="Firmware File", padding=10)
        file_frame.pack(fill=tk.X, padx=10, pady=10)

        self.fw_var = tk.StringVar()
        ttk.Entry(file_frame, textvariable=self.fw_var).pack(side=tk.LEFT, fill=tk.X, expand=True, padx=(0, 5))
        ttk.Button(file_frame, text="Browse", command=self._browse_fw).pack(side=tk.LEFT, padx=2)

        # Quick picks (Pico W)
        self.quick_frame = ttk.LabelFrame(self, text="Quick Flash", padding=10)
        self.quick_frame.pack(fill=tk.X, padx=10, pady=(0, 10))
        self._populate_quick_picks()

        # ── Flash control ──
        init_label = BOARD_LABELS.get(self._current_board, "Pico W")
        init_drive = "RP2350" if self._current_board == BOARD_PICO2_W else "RPI-RP2"
        self.flash_frame = ttk.LabelFrame(self, text=f"Flash to {init_label}", padding=10)
        self.flash_frame.pack(fill=tk.X, padx=10, pady=(0, 10))

        self.mount_label = ttk.Label(self.flash_frame, text=f"{init_drive}: not detected")
        self.mount_label.pack(anchor=tk.W)

        btn_row = ttk.Frame(self.flash_frame)
        btn_row.pack(fill=tk.X, pady=(8, 0))

        self.detect_btn = ttk.Button(btn_row, text=f"Detect {init_drive}", command=self._detect_mount)
        self.detect_btn.pack(side=tk.LEFT, padx=5)
        self.flash_btn_main = ttk.Button(btn_row, text="Flash", command=self._flash)
        self.flash_btn_main.pack(side=tk.LEFT, padx=5)

        # ── Build ──
        self.build_frame = ttk.LabelFrame(self, text="Build Projects", padding=10)
        self.build_frame.pack(fill=tk.X, padx=10, pady=(0, 10))
        self._populate_build_buttons()

        # ── Instructions ──
        inst_frame = ttk.LabelFrame(self, text="Instructions", padding=10)
        inst_frame.pack(fill=tk.BOTH, expand=True, padx=10, pady=(0, 10))

        self.instructions = tk.Text(inst_frame, height=8, wrap=tk.WORD, bg=BG_DARK, fg=FG_TEXT,
                                    font=("JetBrains Mono", 10), state=tk.DISABLED)
        self.instructions.pack(fill=tk.BOTH, expand=True)
        self._set_instructions(self._pico_instructions(self._current_board))

    def _set_instructions(self, text):
        self.instructions.configure(state=tk.NORMAL)
        self.instructions.delete("1.0", tk.END)
        self.instructions.insert(tk.END, text)
        self.instructions.configure(state=tk.DISABLED)

    def _populate_quick_picks(self):
        for w in self.quick_frame.winfo_children():
            w.destroy()

        if self._current_board == BOARD_ESP32S3:
            esp_proj = PROJECT_ROOT / "ESP Protyping" / "dilder-esp32"
            bin_path = esp_proj / ".pio" / "build" / "olimex-esp32s3-devkit-lipo" / "firmware.bin"
            exists = bin_path.exists()
            ttk.Button(
                self.quick_frame,
                text=f"ESP32 Firmware {'(' + self._size_str(bin_path) + ')' if exists else '(not built)'}",
                command=lambda: self._set_fw(bin_path),
                state=tk.NORMAL if exists else tk.DISABLED,
            ).pack(side=tk.LEFT, padx=5)
        else:
            serial_uf2 = DEV_SETUP / "hello-world-serial" / "build" / "hello_serial.uf2"
            display_uf2 = DEV_SETUP / "hello-world" / "build" / "hello_dilder.uf2"
            for label, path in [
                ("Hello Serial", serial_uf2),
                ("Hello Display", display_uf2),
            ]:
                exists = path.exists()
                ttk.Button(
                    self.quick_frame,
                    text=f"{label} {'(' + self._size_str(path) + ')' if exists else '(not built)'}",
                    command=lambda p=path: self._set_fw(p),
                    state=tk.NORMAL if exists else tk.DISABLED,
                ).pack(side=tk.LEFT, padx=5)

    def _populate_build_buttons(self):
        for w in self.build_frame.winfo_children():
            w.destroy()

        if self._current_board == BOARD_ESP32S3:
            ttk.Button(
                self.build_frame, text="Build ESP32 (PlatformIO)",
                command=self._build_esp32_project
            ).pack(side=tk.LEFT, padx=5)
        else:
            for label, proj_dir in [
                ("Build Hello Serial", DEV_SETUP / "hello-world-serial"),
                ("Build Hello Display", DEV_SETUP / "hello-world"),
            ]:
                ttk.Button(
                    self.build_frame, text=label,
                    command=lambda d=proj_dir: self._build_project(d)
                ).pack(side=tk.LEFT, padx=5)

    def refresh_for_board(self, board):
        """Rebuild the flash UI for the selected target board."""
        self._current_board = board
        self._populate_quick_picks()
        self._populate_build_buttons()

        if board == BOARD_ESP32S3:
            self.flash_frame.config(text="Flash to ESP32-S3")
            self.detect_btn.config(text="Detect ESP32", command=self._detect_esp32)
            self.flash_btn_main.config(command=self._flash_esp32)
            self.mount_label.config(text="ESP32: not detected")
            self._set_instructions(self._ESP32_INSTRUCTIONS)
        else:
            board_label = BOARD_LABELS.get(board, "Pico W")
            bootsel_label = "RP2350" if board == BOARD_PICO2_W else "RPI-RP2"
            self.flash_frame.config(text=f"Flash to {board_label}")
            self.detect_btn.config(text=f"Detect {bootsel_label}", command=self._detect_mount)
            self.flash_btn_main.config(command=self._flash)
            self.mount_label.config(text=f"{bootsel_label}: not detected")
            self._set_instructions(self._pico_instructions(board))

    def _size_str(self, path):
        try:
            return f"{path.stat().st_size / 1024:.0f} KB"
        except (FileNotFoundError, OSError):
            return "?"

    def _browse_fw(self):
        if self._current_board == BOARD_ESP32S3:
            filetypes = [("BIN files", "*.bin"), ("All files", "*.*")]
            title = "Select ESP32 Firmware (.bin)"
        else:
            filetypes = [("UF2 files", "*.uf2"), ("All files", "*.*")]
            title = "Select UF2 Firmware"
        path = filedialog.askopenfilename(
            title=title, initialdir=str(DEV_SETUP), filetypes=filetypes)
        if path:
            self.fw_var.set(path)

    def _set_fw(self, path):
        self.fw_var.set(str(path))

    # ── Pico W flash methods ──

    def _detect_mount(self):
        bootsel_label = "RP2350" if self._current_board == BOARD_PICO2_W else "RPI-RP2"
        mount = find_rpi_rp2_mount()
        if mount:
            self.mount_label.config(text=f"{bootsel_label}: {mount}", foreground=FG_GREEN)
            self.app.log(f"{bootsel_label} found at {mount}")
        else:
            self.mount_label.config(
                text=f"{bootsel_label}: not detected — is board in BOOTSEL mode?",
                foreground=FG_RED)

    def _flash(self):
        fw = self.fw_var.get()
        if not fw or not Path(fw).exists():
            messagebox.showwarning("No File", "Select a .uf2 file first.")
            return

        board_label = BOARD_LABELS.get(self._current_board, "Pico")
        mount = find_rpi_rp2_mount()
        if not mount:
            messagebox.showwarning("No Pico",
                f"BOOTSEL drive not detected.\n\nPut the {board_label} in BOOTSEL mode first.")
            return

        try:
            shutil.copy2(fw, mount / Path(fw).name)
            self.app.log(f"Flashed: {Path(fw).name} -> {mount}")
            messagebox.showinfo("Success", f"Firmware flashed!\n\n{Path(fw).name}")
        except Exception as e:
            messagebox.showerror("Flash Failed", str(e))

    def _build_project(self, proj_dir):
        build_dir = proj_dir / "build"
        pico_board = "pico2_w" if self._current_board == BOARD_PICO2_W else "pico_w"

        # Detect stale CMake cache from a different board/platform and clean
        expected_platform = "rp2350" if self._current_board == BOARD_PICO2_W else "rp2040"
        cmake_cache = build_dir / "CMakeCache.txt"
        if cmake_cache.exists():
            try:
                cache_text = cmake_cache.read_text(errors="replace")
                if (f"PICO_BOARD:STRING={pico_board}" not in cache_text
                        or f"PICO_PLATFORM:STRING={expected_platform}" not in cache_text):
                    self.app.log(f"Stale build cache (different platform) — cleaning {build_dir.name}/")
                    shutil.rmtree(build_dir)
            except OSError:
                pass

        build_dir.mkdir(exist_ok=True)

        sdk = os.environ.get("PICO_SDK_PATH", str(Path.home() / "pico" / "pico-sdk"))

        # Check pico_sdk_import.cmake
        cmake_helper = proj_dir / "pico_sdk_import.cmake"
        if not cmake_helper.exists():
            src = Path(sdk) / "external" / "pico_sdk_import.cmake"
            if src.exists():
                shutil.copy2(src, cmake_helper)

        self.app.log(f"Building {proj_dir.name} for {pico_board}...")

        def _run():
            try:
                result = subprocess.run(
                    ["cmake", "-G", "Ninja", f"-DPICO_SDK_PATH={sdk}", f"-DPICO_BOARD={pico_board}", ".."],
                    cwd=build_dir, capture_output=True, text=True
                )
                if result.returncode != 0:
                    self.app.log(f"CMake failed: {result.stderr[-500:]}")
                    return
                result = subprocess.run(
                    ["ninja"], cwd=build_dir, capture_output=True, text=True
                )
                if result.returncode != 0:
                    output = (result.stderr or "") + (result.stdout or "")
                    self.app.log(f"Build failed: {output[-500:]}")
                    return
                self.app.log(f"Build complete: {proj_dir.name}")
            except Exception as e:
                self.app.log(f"Build error: {e}")

        threading.Thread(target=_run, daemon=True).start()

    # ── ESP32-S3 flash methods ──

    def _detect_esp32(self):
        port = find_esp32_serial()
        if port:
            self.mount_label.config(text=f"ESP32-S3: {port}", foreground=FG_GREEN)
            self.app.log(f"ESP32-S3 found on {port}")
        else:
            self.mount_label.config(
                text="ESP32-S3: not detected — plug in USB-UART port (CH340X)",
                foreground=FG_RED)

    def _flash_esp32(self):
        fw = self.fw_var.get()
        if not fw or not Path(fw).exists():
            messagebox.showwarning("No File", "Select a .bin firmware file first.")
            return

        port = find_esp32_serial()
        if not port:
            messagebox.showwarning("No ESP32",
                                   "ESP32-S3 not detected.\n\n"
                                   "Plug in the USB-UART port (near the buttons).")
            return

        self.app.log(f"Flashing {Path(fw).name} to ESP32-S3 on {port}...")

        def _run():
            try:
                # Try esptool.py first (installed with PlatformIO or standalone)
                esptool = shutil.which("esptool.py") or shutil.which("esptool")
                if not esptool:
                    # Try PlatformIO's bundled esptool
                    pio_esptool = Path.home() / ".platformio" / "packages" / "tool-esptoolpy" / "esptool.py"
                    if pio_esptool.exists():
                        esptool = str(pio_esptool)

                if not esptool:
                    self.after(0, lambda: messagebox.showerror(
                        "esptool Not Found",
                        "esptool is required to flash ESP32-S3.\n\n"
                        "Install with: pip install esptool\n"
                        "Or install PlatformIO (includes esptool)."))
                    return

                result = subprocess.run(
                    [esptool, "--chip", "esp32s3", "--port", port,
                     "--baud", "460800", "write_flash", "0x0", fw],
                    capture_output=True, text=True, timeout=120
                )
                if result.returncode == 0:
                    self.after(0, lambda: self.app.log(f"Flashed: {Path(fw).name} -> {port}"))
                    self.after(0, lambda: messagebox.showinfo(
                        "Success", f"ESP32-S3 firmware flashed!\n\n{Path(fw).name}"))
                else:
                    output = (result.stderr or "") + (result.stdout or "")
                    self.after(0, lambda: self.app.log(f"Flash failed: {output[-500:]}"))
                    self.after(0, lambda: messagebox.showerror(
                        "Flash Failed", f"esptool error:\n{output[-300:]}"))
            except subprocess.TimeoutExpired:
                self.after(0, lambda: self.app.log("Flash timed out (2 min)."))
            except Exception as e:
                self.after(0, lambda: messagebox.showerror("Flash Failed", str(e)))

        threading.Thread(target=_run, daemon=True).start()

    def _build_esp32_project(self):
        """Build ESP32-S3 firmware using PlatformIO CLI."""
        esp_proj = PROJECT_ROOT / "ESP Protyping" / "dilder-esp32"
        if not (esp_proj / "platformio.ini").exists():
            messagebox.showwarning(
                "No Project",
                f"PlatformIO project not found at:\n{esp_proj}\n\n"
                "Run setup.py step 16 to initialize the ESP32 project.")
            return

        self.app.log(f"Building ESP32-S3 firmware via PlatformIO...")

        def _run():
            try:
                pio = shutil.which("pio") or shutil.which("platformio")
                if not pio:
                    self.after(0, lambda: messagebox.showerror(
                        "PlatformIO Not Found",
                        "PlatformIO CLI not found.\n\n"
                        "Install with: pip install platformio\n"
                        "Or run: python3 setup.py --step 16"))
                    return

                result = subprocess.run(
                    [pio, "run", "-d", str(esp_proj)],
                    capture_output=True, text=True, timeout=300
                )
                if result.returncode == 0:
                    self.after(0, lambda: self.app.log("[build] ESP32 build complete."))
                    self.after(0, lambda: self._populate_quick_picks())
                else:
                    output = (result.stderr or "") + (result.stdout or "")
                    self.after(0, lambda: self.app.log(f"[build] ESP32 build failed: {output[-500:]}"))
            except subprocess.TimeoutExpired:
                self.after(0, lambda: self.app.log("[build] ESP32 build timed out (5 min)."))
            except Exception as e:
                self.after(0, lambda: self.app.log(f"[build] Error: {e}"))

        threading.Thread(target=_run, daemon=True).start()


# ─────────────────────────────────────────────────────────────────────────────
# Asset Manager
# ─────────────────────────────────────────────────────────────────────────────

class AssetManager(ttk.Frame):
    """Browse, preview, and manage saved display assets."""

    def __init__(self, parent, app):
        super().__init__(parent)
        self.app = app
        self._build_ui()
        self._refresh_list()

    def _build_ui(self):
        # ── File list ──
        list_frame = ttk.Frame(self)
        list_frame.pack(side=tk.LEFT, fill=tk.Y, padx=5, pady=5)

        ttk.Label(list_frame, text="Assets (assets/)").pack(anchor=tk.W)

        self.file_list = tk.Listbox(
            list_frame, width=30, bg=BG_DARK, fg=FG_TEXT,
            selectbackground=FG_ACCENT, selectforeground=BG_DARK,
            font=("JetBrains Mono", 10),
        )
        self.file_list.pack(fill=tk.BOTH, expand=True, pady=(5, 0))
        self.file_list.bind("<<ListboxSelect>>", self._on_select)

        btn_row = ttk.Frame(list_frame)
        btn_row.pack(fill=tk.X, pady=(5, 0))
        ttk.Button(btn_row, text="Refresh", command=self._refresh_list).pack(side=tk.LEFT, padx=2)
        ttk.Button(btn_row, text="Delete", command=self._delete_selected).pack(side=tk.LEFT, padx=2)
        ttk.Button(btn_row, text="Open Folder", command=self._open_folder).pack(side=tk.LEFT, padx=2)

        # ── Preview ──
        preview_frame = ttk.LabelFrame(self, text="Preview", padding=5)
        preview_frame.pack(side=tk.LEFT, fill=tk.BOTH, expand=True, padx=5, pady=5)

        self.preview_canvas = tk.Canvas(
            preview_frame,
            width=DISPLAY_W * 2,
            height=DISPLAY_H * 2,
            bg=EINK_WHITE,
            highlightthickness=1,
            highlightbackground=FG_DIM,
        )
        self.preview_canvas.pack()

        self.preview_info = ttk.Label(preview_frame, text="Select an asset to preview")
        self.preview_info.pack(pady=5)

    def _refresh_list(self):
        self.file_list.delete(0, tk.END)
        ASSETS_DIR.mkdir(exist_ok=True)
        files = sorted(ASSETS_DIR.iterdir())
        for f in files:
            if f.is_file() and f.suffix in (".pbm", ".bin", ".png"):
                self.file_list.insert(tk.END, f.name)

    def _on_select(self, event=None):
        sel = self.file_list.curselection()
        if not sel:
            return
        name = self.file_list.get(sel[0])
        path = ASSETS_DIR / name
        self._preview_file(path)

    def _preview_file(self, path):
        self.preview_canvas.delete("all")
        scale = 2

        pixels = [[0] * DISPLAY_W for _ in range(DISPLAY_H)]

        if path.suffix == ".bin":
            data = path.read_bytes()
            byte_width = (DISPLAY_W + 7) // 8
            for y in range(DISPLAY_H):
                for x in range(DISPLAY_W):
                    byte_idx = y * byte_width + x // 8
                    bit_idx = 7 - (x % 8)
                    if byte_idx < len(data) and data[byte_idx] & (1 << bit_idx):
                        pixels[y][x] = 1
        elif path.suffix == ".png":
            try:
                from PIL import Image
                img = Image.open(str(path)).convert("1").resize((DISPLAY_W, DISPLAY_H))
                for y in range(DISPLAY_H):
                    for x in range(DISPLAY_W):
                        if img.getpixel((x, y)) == 0:
                            pixels[y][x] = 1
            except ImportError:
                self.preview_info.config(text="Install Pillow for PNG preview")
                return

        for y in range(DISPLAY_H):
            for x in range(DISPLAY_W):
                if pixels[y][x]:
                    self.preview_canvas.create_rectangle(
                        x * scale, y * scale,
                        x * scale + scale, y * scale + scale,
                        fill=EINK_BLACK, outline=EINK_BLACK,
                    )

        size = path.stat().st_size
        self.preview_info.config(text=f"{path.name}  |  {size} bytes  |  {DISPLAY_W}x{DISPLAY_H}")

    def _delete_selected(self):
        sel = self.file_list.curselection()
        if not sel:
            return
        name = self.file_list.get(sel[0])
        if messagebox.askyesno("Delete", f"Delete {name}?"):
            (ASSETS_DIR / name).unlink(missing_ok=True)
            self._refresh_list()
            self.preview_canvas.delete("all")
            self.app.log(f"Deleted: {name}")

    def _open_folder(self):
        ASSETS_DIR.mkdir(exist_ok=True)
        if platform.system() == "Linux":
            subprocess.Popen(["xdg-open", str(ASSETS_DIR)])
        elif platform.system() == "Darwin":
            subprocess.Popen(["open", str(ASSETS_DIR)])


# ─────────────────────────────────────────────────────────────────────────────
# GPIO Pin Viewer
# ─────────────────────────────────────────────────────────────────────────────

class PinViewer(ttk.Frame):
    """Visual GPIO pin assignment reference — switches between Pico W and ESP32-S3."""

    _PICO_W_PINOUT = """\
Pico W GPIO Pin Assignments — Dilder Project
══════════════════════════════════════════════

               ┌───USB───┐
   GP0  [ 1]   │         │  [40]  VBUS
   GP1  [ 2]   │  PICO   │  [39]  VSYS
   GND  [ 3]   │    W    │  [38]  GND       ◄── e-ink GND
▶  GP2  [ 4]   │         │  [37]  3V3_EN
▶  GP3  [ 5]   │         │  [36]  3V3(OUT)  ◄── e-ink VCC
▶  GP4  [ 6]   │         │  [35]  ADC_VREF
▶  GP5  [ 7]   │         │  [34]  GP28
   GND  [ 8]   │         │  [33]  AGND
▶  GP6  [ 9]   │         │  [32]  GP27
   GP7  [10]   │         │  [31]  GP26
▶  GP8  [11]   │         │  [30]  RUN
▶  GP9  [12]   │         │  [29]  GP22
   GND  [13]   │         │  [28]  GND
▶ GP10  [14]   │         │  [27]  GP21
▶ GP11  [15]   │         │  [26]  GP20
▶ GP12  [16]   │         │  [25]  GP19
▶ GP13  [17]   │         │  [24]  GP18
   GND  [18]   │         │  [23]  GND
  GP14  [19]   │         │  [22]  GP17
  GP15  [20]   └─────────┘  [21]  GP16

▶ = used by Dilder

═══════════════════════════════════════════════
Display (SPI1)                 Buttons
═══════════════════════════════════════════════
VCC  → 3V3(OUT) pin 36        UP     → GP2  pin 4
GND  → GND      pin 38        DOWN   → GP3  pin 5
DIN  → GP11     pin 15        LEFT   → GP4  pin 6
CLK  → GP10     pin 14        RIGHT  → GP5  pin 7
CS   → GP9      pin 12        CENTER → GP6  pin 9
DC   → GP8      pin 11
RST  → GP12     pin 16
BUSY → GP13     pin 17

═══════════════════════════════════════════════
SPI Configuration
═══════════════════════════════════════════════
Controller:  SPI1
Mode:        Mode 0 (CPOL=0, CPHA=0)
Clock:       4 MHz
CS:          Active LOW
Bit order:   MSB first
"""

    _ESP32S3_PINOUT = """\
Olimex ESP32-S3-DevKit-Lipo GPIO Assignments — Dilder Project
══════════════════════════════════════════════════════════════

         ┌──[USB-OTG]──┐   ┌──[USB-UART]──┐
         │  (native)    │   │  (CH340X)    │
         └──────────────┘   └──────────────┘
         [RST]  [BOOT]   (o) LED (GPIO38)

   EXT1 (Left)                    EXT2 (Right)
  ┌───────────┐                  ┌───────────┐
  │ 3V3  [ 1] │  ◄── VCC        │ GND  [ 1] │
  │ 3V3  [ 2] │                  │ GP43 [ 2] │  UART0 TX
  │ EN   [ 3] │                  │ GP44 [ 3] │  UART0 RX
▶ │ GP4  [ 4] │  JOY UP         │ GP1  [ 4] │ ▶ JOY LEFT
  │ GP5  [ 5] │  PWR sense      │ GP2  [ 5] │ ▶ JOY RIGHT
  │ GP6  [ 6] │  BAT sense      │ GP42 [ 6] │
▶ │ GP7  [ 7] │  JOY DOWN       │ GP41 [ 7] │
▶ │ GP15 [ 8] │  JOY CENTER     │ GP40 [ 8] │
  │ GP16 [ 9] │                  │ GP39 [ 9] │
  │ GP17 [10] │                  │ GP38 [10] │ ▶ LED
  │ GP18 [11] │                  │ GP37 [11] │  ✕ PSRAM
▶ │ GP8  [12] │  BUSY            │ GP36 [12] │  ✕ PSRAM
  │ GP3  [13] │ ▶ RST            │ GP35 [13] │  ✕ PSRAM
  │ GP46 [14] │                  │ GP0  [14] │  BOOT btn
▶ │ GP9  [15] │  DC              │ GP45 [15] │
▶ │ GP10 [16] │  CS              │ GP48 [16] │  I2C SDA
▶ │ GP11 [17] │  DIN (MOSI)      │ GP47 [17] │  I2C SCL
▶ │ GP12 [18] │  CLK (SCLK)      │ GP21 [18] │
  │ GP13 [19] │                  │ GP20 [19] │  USB D+
  │ GP14 [20] │                  │ GP19 [20] │  USB D-
  │ +5V  [21] │                  │ GND  [21] │
  │ GND  [22] │  ◄── GND        │ GND  [22] │
  └───────────┘                  └───────────┘

▶ = used by Dilder   ✕ = reserved (PSRAM)

═══════════════════════════════════════════════════════
e-Paper Display (FSPI)          Joystick (5-way)
═══════════════════════════════════════════════════════
VCC  → 3.3V   EXT1-1           UP     → GPIO4  EXT1-4
GND  → GND    EXT1-22          DOWN   → GPIO7  EXT1-7
DIN  → GPIO11 EXT1-17          LEFT   → GPIO1  EXT2-4
CLK  → GPIO12 EXT1-18          RIGHT  → GPIO2  EXT2-5
CS   → GPIO10 EXT1-16          CENTER → GPIO15 EXT1-8
DC   → GPIO9  EXT1-15
RST  → GPIO3  EXT1-13
BUSY → GPIO8  EXT1-12

═══════════════════════════════════════════════════════
Board Peripherals
═══════════════════════════════════════════════════════
Green LED → GPIO38 (active LOW)   EXT2-10
BOOT btn  → GPIO0  (user btn)    EXT2-14
BAT sense → GPIO6  (ADC ×4.133)  EXT1-6
PWR sense → GPIO5  (ADC ×1.468)  EXT1-5

═══════════════════════════════════════════════════════
SPI Configuration (FSPI / SPI3)
═══════════════════════════════════════════════════════
Controller:  FSPI (SPI3, hardware)
Mode:        Mode 0 (CPOL=0, CPHA=0)
Clock:       4 MHz
CS:          Active LOW (10k pull-up on board)
Bit order:   MSB first
"""

    def __init__(self, parent, app):
        super().__init__(parent)
        self.app = app
        self._build_ui()

    def _build_ui(self):
        # Pin map
        self.pin_text = tk.Text(self, wrap=tk.NONE, bg=BG_DARK, fg=FG_TEXT,
                                font=("JetBrains Mono", 11), state=tk.DISABLED,
                                height=30, width=70)
        self.pin_text.pack(fill=tk.BOTH, expand=True, padx=10, pady=10)
        self._show_pinout(self._PICO_W_PINOUT)

    def _show_pinout(self, text):
        self.pin_text.configure(state=tk.NORMAL)
        self.pin_text.delete("1.0", tk.END)
        self.pin_text.insert(tk.END, text)
        self.pin_text.configure(state=tk.DISABLED)

    _PICO2_W_PINOUT = _PICO_W_PINOUT.replace(
        "Pico W GPIO Pin Assignments",
        "Pico 2 W GPIO Pin Assignments"
    ).replace(
        "│  PICO   │",
        "│ PICO 2  │"
    ).replace(
        "│    W    │",
        "│    W    │"
    ).replace(
        "BOARD_FLASH_KB       2048",
        "BOARD_FLASH_KB       4096"
    )

    def refresh_for_board(self, board):
        """Switch the displayed pinout for the selected board."""
        if board == BOARD_ESP32S3:
            self._show_pinout(self._ESP32S3_PINOUT)
        elif board == BOARD_PICO2_W:
            self._show_pinout(self._PICO2_W_PINOUT)
        else:
            self._show_pinout(self._PICO_W_PINOUT)


# ─────────────────────────────────────────────────────────────────────────────
# Connection Utility — USB & Wi-Fi Setup Walkthrough
# ─────────────────────────────────────────────────────────────────────────────

class ConnectionUtility(ttk.Frame):
    """
    Step-by-step walkthrough for connecting the target board via USB serial
    and over Wi-Fi. Adapts steps based on the selected board (Pico W or ESP32-S3).
    """

    def __init__(self, parent, app):
        super().__init__(parent)
        self.app = app
        self._last_board = None
        self._build_ui()

    def _build_ui(self):
        # ── Mode selector ──
        mode_frame = ttk.Frame(self)
        mode_frame.pack(fill=tk.X, padx=10, pady=(10, 0))

        self.mode_var = tk.StringVar(value="usb")
        ttk.Radiobutton(mode_frame, text="USB Serial Connection",
                        variable=self.mode_var, value="usb",
                        command=self._show_mode).pack(side=tk.LEFT, padx=(0, 20))
        ttk.Radiobutton(mode_frame, text="Wi-Fi Connection",
                        variable=self.mode_var, value="wifi",
                        command=self._show_mode).pack(side=tk.LEFT)

        # Board indicator
        self.board_label = ttk.Label(mode_frame, text="", font=("JetBrains Mono", 10),
                                      foreground=FG_ACCENT)
        self.board_label.pack(side=tk.RIGHT, padx=10)

        # ── Content area ──
        self.content = ttk.Frame(self)
        self.content.pack(fill=tk.BOTH, expand=True, padx=10, pady=10)

        self._show_mode()

    def refresh_for_board(self, board_key=None):
        """Rebuild the panel when the target board changes."""
        self._show_mode()

    def _show_mode(self):
        for w in self.content.winfo_children():
            w.destroy()
        board = self.app.target_board
        board_label = BOARD_LABELS.get(board, "Board")
        self.board_label.config(text=f"Board: {board_label}")
        if self.mode_var.get() == "usb":
            if board == BOARD_ESP32S3:
                self._build_usb_panel_esp32()
            else:
                self._build_usb_panel()
        else:
            if board == BOARD_ESP32S3:
                self._build_wifi_panel_esp32()
            else:
                self._build_wifi_panel()

    # ── USB Panel ────────────────────────────────────────────────────────────

    def _build_usb_panel(self):
        canvas = tk.Canvas(self.content, bg=BG_PANEL, highlightthickness=0)
        scrollbar = ttk.Scrollbar(self.content, orient=tk.VERTICAL, command=canvas.yview)
        scroll_frame = ttk.Frame(canvas)

        scroll_frame.bind("<Configure>", lambda e: canvas.configure(scrollregion=canvas.bbox("all")))
        canvas.create_window((0, 0), window=scroll_frame, anchor=tk.NW)
        canvas.configure(yscrollcommand=scrollbar.set)

        scrollbar.pack(side=tk.RIGHT, fill=tk.Y)
        canvas.pack(side=tk.LEFT, fill=tk.BOTH, expand=True)

        # Enable mousewheel scrolling
        def _on_mousewheel(event):
            canvas.yview_scroll(int(-1 * (event.delta / 120)), "units")
        canvas.bind_all("<MouseWheel>", _on_mousewheel)
        canvas.bind_all("<Button-4>", lambda e: canvas.yview_scroll(-3, "units"))
        canvas.bind_all("<Button-5>", lambda e: canvas.yview_scroll(3, "units"))

        f = scroll_frame
        board = self.app.target_board
        bn = BOARD_LABELS.get(board, "Pico W (RP2040)")
        drive = "RP2350" if board == BOARD_PICO2_W else "RPI-RP2"

        # Step 1
        self._step_header(f, "Step 1", f"Plug in the {bn} via USB")
        self._step_body(f, f"""\
Connect the {bn} to your computer using a micro-USB cable.

IMPORTANT: The cable must be a data cable, not a charge-only cable.
Charge-only cables have no data wires — they physically cannot
communicate. If in doubt, try a different cable.

The board should NOT be in BOOTSEL mode for serial communication.
Just plug it in normally with firmware already flashed.""")

        self._step_check_btn(f, "Check: Is a USB device detected?", self._check_usb_device)
        self.usb_step1_label = ttk.Label(f, text="")
        self.usb_step1_label.pack(anchor=tk.W, padx=20)

        # Step 2
        self._step_header(f, "Step 2", "Verify the serial port exists")
        self._step_body(f, f"""\
When the {bn} is running firmware with USB serial enabled
(stdio_init_all() in C code), it appears as /dev/ttyACM0.

If it does not appear, the board may be:
  - In BOOTSEL mode (shows as {drive} drive instead)
  - Running firmware without USB serial enabled
  - Connected with a charge-only cable""")

        self._step_check_btn(f, "Check: Is /dev/ttyACM0 present?", self._check_serial_port)
        self.usb_step2_label = ttk.Label(f, text="")
        self.usb_step2_label.pack(anchor=tk.W, padx=20)

        # Step 3
        self._step_header(f, "Step 3", "Verify serial port permissions")
        self._step_body(f, """\
Your user must be in the serial port group to access the device.

  Arch / CachyOS / Manjaro:  uucp
  Ubuntu / Debian:            dialout

If you are not in the group, run:
  sudo usermod -aG uucp $USER    (Arch)
  sudo usermod -aG dialout $USER (Debian)

Then log out and back in (a new terminal is not enough).""")

        self._step_check_btn(f, "Check: Do I have serial permissions?", self._check_serial_perms)
        self.usb_step3_label = ttk.Label(f, text="")
        self.usb_step3_label.pack(anchor=tk.W, padx=20)

        self.fix_perms_btn = ttk.Button(f, text="Fix: Add me to serial group (requires sudo password)",
                                        command=self._fix_serial_perms)
        self.fix_perms_btn.pack(anchor=tk.W, padx=20, pady=(3, 0))

        # Step 4
        self._step_header(f, "Step 4", "Open the Serial Monitor")
        self._step_body(f, """\
Everything looks good — switch to the Serial Monitor tab to connect.

  1. Go to the "Serial Monitor" tab
  2. Port should auto-select /dev/ttyACM0
  3. Baud rate: 115200
  4. Click "Connect"

You should see printf output from your board's firmware.""")

        ttk.Button(f, text="Go to Serial Monitor",
                   command=lambda: self.app.notebook.select(self.app.serial_tab)).pack(
                       anchor=tk.W, padx=20, pady=(5, 20))

    # ── Wi-Fi Panel ──────────────────────────────────────────────────────────

    def _build_wifi_panel(self):
        canvas = tk.Canvas(self.content, bg=BG_PANEL, highlightthickness=0)
        scrollbar = ttk.Scrollbar(self.content, orient=tk.VERTICAL, command=canvas.yview)
        scroll_frame = ttk.Frame(canvas)

        scroll_frame.bind("<Configure>", lambda e: canvas.configure(scrollregion=canvas.bbox("all")))
        canvas.create_window((0, 0), window=scroll_frame, anchor=tk.NW)
        canvas.configure(yscrollcommand=scrollbar.set)

        scrollbar.pack(side=tk.RIGHT, fill=tk.Y)
        canvas.pack(side=tk.LEFT, fill=tk.BOTH, expand=True)

        canvas.bind_all("<Button-4>", lambda e: canvas.yview_scroll(-3, "units"))
        canvas.bind_all("<Button-5>", lambda e: canvas.yview_scroll(3, "units"))

        f = scroll_frame
        board = self.app.target_board
        bn = BOARD_LABELS.get(board, "Pico W (RP2040)")

        # Overview
        self._step_header(f, "Overview", f"{bn} Wi-Fi Connection")
        self._step_body(f, f"""\
The {bn} has an onboard Infineon CYW43439 Wi-Fi chip
(802.11n, 2.4 GHz). You can use it to connect to
your local network and communicate wirelessly —
no USB cable needed after initial setup.

This requires firmware that initialises Wi-Fi. The hello world
examples do not use Wi-Fi. You will need to write or flash
Wi-Fi-enabled firmware first.""")

        # Step 1
        self._step_header(f, "Step 1", "Add Wi-Fi credentials to your firmware")
        self._step_body(f, """\
In your C code, initialise Wi-Fi and connect to your network:""")

        code_frame = ttk.Frame(f)
        code_frame.pack(fill=tk.X, padx=20, pady=(0, 10))
        code_text = tk.Text(code_frame, height=14, wrap=tk.NONE, bg=BG_DARK, fg=FG_TEXT,
                            font=("JetBrains Mono", 10), state=tk.DISABLED)
        code_text.pack(fill=tk.X)
        code_text.configure(state=tk.NORMAL)
        code_text.insert(tk.END, """\
#include "pico/cyw43_arch.h"
#include "lwip/tcp.h"

// Initialise Wi-Fi
if (cyw43_arch_init_with_country(CYW43_COUNTRY_USA)) {
    printf("Wi-Fi init failed\\n");
    return 1;
}
cyw43_arch_enable_sta_mode();

// Connect to your network
if (cyw43_arch_wifi_connect_timeout_ms(
        "YOUR_SSID", "YOUR_PASSWORD",
        CYW43_AUTH_WPA2_AES_PSK, 10000)) {
    printf("Wi-Fi connect failed\\n");
} else {
    printf("Wi-Fi connected\\n");
}""")
        code_text.configure(state=tk.DISABLED)

        # Step 2
        self._step_header(f, "Step 2", "Link the Wi-Fi libraries in CMakeLists.txt")
        self._step_body(f, """\
Add these libraries to your target_link_libraries():""")

        cmake_frame = ttk.Frame(f)
        cmake_frame.pack(fill=tk.X, padx=20, pady=(0, 10))
        cmake_text = tk.Text(cmake_frame, height=6, wrap=tk.NONE, bg=BG_DARK, fg=FG_TEXT,
                             font=("JetBrains Mono", 10), state=tk.DISABLED)
        cmake_text.pack(fill=tk.X)
        cmake_text.configure(state=tk.NORMAL)
        cmake_text.insert(tk.END, """\
target_link_libraries(your_project
    pico_stdlib
    pico_cyw43_arch_lwip_threadsafe_background
    hardware_spi
    hardware_gpio
)""")
        cmake_text.configure(state=tk.DISABLED)

        # Step 3
        self._step_header(f, "Step 3", f"Find the {bn} on your network")
        self._step_body(f, f"""\
After the {bn} connects to Wi-Fi, it gets an IP address via DHCP.
Your firmware should print it:

    printf("IP: %s\\n", ip4addr_ntoa(
        netif_ip4_addr(netif_list)));

Then you can ping it from your computer:""")

        self._step_check_btn(f, f"Scan: Find {bn} on local network", self._scan_network)
        self.wifi_scan_label = ttk.Label(f, text="")
        self.wifi_scan_label.pack(anchor=tk.W, padx=20)

        # Step 4
        self._step_header(f, "Step 4", "Communicate over Wi-Fi")
        self._step_body(f, """\
With Wi-Fi working, you have several options:

TCP Socket Server — Run a TCP listener on the board.
  Your DevTool or any script can connect and send commands
  or image data over the network instead of USB serial.

HTTP Server — Serve a simple web page from the board.
  Useful for status dashboards or remote control.

UDP Broadcast — The board can announce itself on the
  network so the DevTool can auto-discover it.

mDNS — Advertise the board as "dilder.local" on the
  network so you don't need to know the IP address.

These are firmware features you build in C. The Pico SDK
includes lwIP (lightweight IP stack) which supports all
of the above.""")

        # Wi-Fi connection test
        self._step_header(f, "Quick Connect", f"Test a TCP connection to the {bn}")
        self._step_body(f, """\
If your firmware is running a TCP server, enter the IP and
port below to test the connection.""")

        conn_frame = ttk.Frame(f)
        conn_frame.pack(fill=tk.X, padx=20, pady=(0, 10))

        ttk.Label(conn_frame, text="IP:").pack(side=tk.LEFT)
        self.wifi_ip_var = tk.StringVar(value="192.168.1.")
        ttk.Entry(conn_frame, textvariable=self.wifi_ip_var, width=16).pack(side=tk.LEFT, padx=(3, 10))

        ttk.Label(conn_frame, text="Port:").pack(side=tk.LEFT)
        self.wifi_port_var = tk.StringVar(value="4242")
        ttk.Entry(conn_frame, textvariable=self.wifi_port_var, width=6).pack(side=tk.LEFT, padx=(3, 10))

        ttk.Button(conn_frame, text="Test Connection", command=self._test_wifi_conn).pack(side=tk.LEFT)

        self.wifi_conn_label = ttk.Label(f, text="")
        self.wifi_conn_label.pack(anchor=tk.W, padx=20, pady=(0, 20))

    # ── Helpers ──────────────────────────────────────────────────────────────

    def _step_header(self, parent, step, title):
        frame = ttk.Frame(parent)
        frame.pack(fill=tk.X, padx=10, pady=(15, 2))
        lbl = ttk.Label(frame, text=f"{step} — {title}",
                        font=("JetBrains Mono", 12, "bold"), foreground=FG_ACCENT)
        lbl.pack(anchor=tk.W)
        ttk.Separator(frame, orient=tk.HORIZONTAL).pack(fill=tk.X, pady=(3, 0))

    def _step_body(self, parent, text):
        lbl = ttk.Label(parent, text=text, wraplength=700, justify=tk.LEFT,
                        font=("JetBrains Mono", 10))
        lbl.pack(anchor=tk.W, padx=20, pady=(5, 5))

    def _step_check_btn(self, parent, text, command):
        ttk.Button(parent, text=text, command=command).pack(anchor=tk.W, padx=20, pady=(5, 3))

    # ── USB Checks ───────────────────────────────────────────────────────────

    def _check_usb_device(self):
        bn = BOARD_LABELS.get(self.app.target_board, "Pico")
        try:
            result = subprocess.run(["lsusb"], capture_output=True, text=True, timeout=5)
            pico_lines = [l for l in result.stdout.splitlines()
                          if "2e8a" in l.lower() or "raspberry pi" in l.lower() or "rpi" in l.lower()]
            if pico_lines:
                self.usb_step1_label.config(text=f"  ✓ {bn} detected: {pico_lines[0].strip()}",
                                            foreground=FG_GREEN)
                self.app.log(f"USB check: {bn} detected")
            else:
                self.usb_step1_label.config(text=f"  ✗ No {bn} found on USB. Check cable and connection.",
                                            foreground=FG_RED)
        except (FileNotFoundError, subprocess.TimeoutExpired):
            self.usb_step1_label.config(text="  ? lsusb not available — check manually with: lsusb",
                                        foreground=FG_YELLOW)

    def _check_serial_port(self):
        bn = BOARD_LABELS.get(self.app.target_board, "Pico")
        port = find_pico_serial()
        if port:
            self.usb_step2_label.config(
                text=f"  ✓ {port} detected — {bn} serial is ready",
                foreground=FG_GREEN)
            self.app.log(f"Serial port check: {port} found")
        else:
            # Check for any ttyACM as fallback hint
            import glob as _glob
            others = _glob.glob("/dev/ttyACM*")
            if others:
                self.usb_step2_label.config(
                    text=f"  ~ Board not auto-detected, but found: {', '.join(others)}",
                    foreground=FG_YELLOW)
            else:
                self.usb_step2_label.config(
                    text=f"  ✗ No serial devices found. Is the {bn} plugged in with firmware?",
                    foreground=FG_RED)

    def _check_serial_perms(self):
        result = subprocess.run(["groups"], capture_output=True, text=True)
        groups = result.stdout.strip().split() if result.returncode == 0 else []

        # Check both possible groups
        in_uucp = "uucp" in groups
        in_dialout = "dialout" in groups

        if in_uucp or in_dialout:
            group = "uucp" if in_uucp else "dialout"
            self.usb_step3_label.config(text=f"  ✓ You are in the '{group}' group — permissions OK",
                                        foreground=FG_GREEN)
            self.app.log(f"Permission check: in '{group}' group")
        else:
            self.usb_step3_label.config(
                text="  ✗ Not in 'uucp' or 'dialout'. Run: sudo usermod -aG uucp $USER (then log out/in)",
                foreground=FG_RED)

    def _fix_serial_perms(self):
        """Run sudo usermod to add the user to the serial group, via a terminal."""
        user = os.environ.get("USER", "")
        if not user:
            messagebox.showerror("Error", "Could not determine your username.")
            return

        # Detect the correct group
        group = "uucp"  # Arch/CachyOS default
        try:
            result = subprocess.run(["getent", "group", "dialout"],
                                    capture_output=True, text=True, timeout=3)
            if result.returncode == 0:
                group = "dialout"
            else:
                result = subprocess.run(["getent", "group", "uucp"],
                                        capture_output=True, text=True, timeout=3)
                if result.returncode == 0:
                    group = "uucp"
        except (FileNotFoundError, subprocess.TimeoutExpired):
            pass

        cmd = f"sudo usermod -aG {group} {user}"

        confirm = messagebox.askyesno(
            "Add Serial Permissions",
            f"This will run:\n\n  {cmd}\n\n"
            f"A terminal window will open asking for your sudo password.\n\n"
            f"After this completes you must log out and back in.\n\n"
            f"Continue?"
        )
        if not confirm:
            return

        # Launch in a visible terminal so the user can enter their password
        terminal_cmds = [
            # Try common terminal emulators in order
            ["pkexec", "usermod", "-aG", group, user],
        ]

        # Try pkexec first (graphical sudo prompt, no terminal needed)
        try:
            result = subprocess.run(
                ["pkexec", "usermod", "-aG", group, user],
                capture_output=True, text=True, timeout=30
            )
            if result.returncode == 0:
                self.usb_step3_label.config(
                    text=f"  ✓ Added to '{group}' group. LOG OUT AND BACK IN to apply.",
                    foreground=FG_GREEN)
                self.app.log(f"Added {user} to {group} group via pkexec")
                messagebox.showinfo(
                    "Success",
                    f"You have been added to the '{group}' group.\n\n"
                    f"You MUST log out and back in for this to take effect.\n"
                    f"A new terminal window is not enough — full logout required."
                )
                return
            else:
                err = result.stderr.strip()
                if "dismissed" in err.lower() or "cancel" in err.lower():
                    self.app.log("Permission fix cancelled by user")
                    return
                # pkexec failed for another reason, try terminal fallback
        except FileNotFoundError:
            pass  # pkexec not installed, try terminal fallback
        except subprocess.TimeoutExpired:
            self.app.log("pkexec timed out")

        # Fallback: open a terminal emulator with the sudo command
        terminal_attempts = [
            ["xterm", "-e", f"sudo usermod -aG {group} {user} && echo 'Done — close this window' && read"],
            ["konsole", "-e", "bash", "-c", f"sudo usermod -aG {group} {user} && echo 'Done — press Enter' && read"],
            ["gnome-terminal", "--", "bash", "-c", f"sudo usermod -aG {group} {user} && echo 'Done — press Enter' && read"],
        ]

        for term_cmd in terminal_attempts:
            try:
                subprocess.Popen(term_cmd)
                self.usb_step3_label.config(
                    text=f"  ⏳ Terminal opened — enter your sudo password there. Then log out/in.",
                    foreground=FG_YELLOW)
                self.app.log(f"Opened terminal for sudo usermod -aG {group} {user}")
                return
            except FileNotFoundError:
                continue

        # Nothing worked
        messagebox.showwarning(
            "Manual Step Required",
            f"Could not find a graphical sudo prompt or terminal emulator.\n\n"
            f"Open a terminal manually and run:\n\n  {cmd}\n\n"
            f"Then log out and back in."
        )

    # ── ESP32-S3 USB Panel ────────────────────────────────────────────────────

    def _build_usb_panel_esp32(self):
        canvas = tk.Canvas(self.content, bg=BG_PANEL, highlightthickness=0)
        scrollbar = ttk.Scrollbar(self.content, orient=tk.VERTICAL, command=canvas.yview)
        scroll_frame = ttk.Frame(canvas)

        scroll_frame.bind("<Configure>", lambda e: canvas.configure(scrollregion=canvas.bbox("all")))
        canvas.create_window((0, 0), window=scroll_frame, anchor=tk.NW)
        canvas.configure(yscrollcommand=scrollbar.set)

        scrollbar.pack(side=tk.RIGHT, fill=tk.Y)
        canvas.pack(side=tk.LEFT, fill=tk.BOTH, expand=True)

        canvas.bind_all("<Button-4>", lambda e: canvas.yview_scroll(-3, "units"))
        canvas.bind_all("<Button-5>", lambda e: canvas.yview_scroll(3, "units"))

        f = scroll_frame

        # Step 1
        self._step_header(f, "Step 1", "Plug in via USB-UART (not USB-OTG)")
        self._step_body(f, """\
The Olimex ESP32-S3-DevKit-Lipo has TWO USB-C ports:

  USB-UART  (near RST/BOOT buttons)  CH340X chip
     Upload firmware, serial monitor, auto-reset

  USB-OTG   (near the antenna)        Native USB
     JTAG debugging only (advanced)

Plug your USB-C data cable into the USB-UART port.
This is the port closer to the RST and BOOT buttons.""")

        self._step_check_btn(f, "Check: Is the ESP32-S3 detected on USB?", self._check_usb_esp32)
        self.esp_step1_label = ttk.Label(f, text="")
        self.esp_step1_label.pack(anchor=tk.W, padx=20)

        # Step 2
        self._step_header(f, "Step 2", "Verify serial port (/dev/ttyUSB*)")
        self._step_body(f, """\
The CH340X USB-to-serial chip shows up as /dev/ttyUSB0.
The ch341 kernel module is built into most Linux kernels.

If no /dev/ttyUSB* appears:
  - Make sure you used the USB-UART port (not USB-OTG)
  - Try a different USB cable (must be data, not charge-only)
  - Check: dmesg | tail  (should show "ch341-uart converter")""")

        self._step_check_btn(f, "Check: Is /dev/ttyUSB* present?", self._check_serial_esp32)
        self.esp_step2_label = ttk.Label(f, text="")
        self.esp_step2_label.pack(anchor=tk.W, padx=20)

        # Step 3
        self._step_header(f, "Step 3", "Verify serial port permissions")
        self._step_body(f, """\
Same as the Pico W — your user must be in the serial group:

  Arch / CachyOS / Manjaro:  uucp
  Ubuntu / Debian:            dialout

If you already set this up for the Pico W, you are good.
Otherwise run:
  sudo usermod -aG uucp $USER    (Arch)
  sudo usermod -aG dialout $USER (Debian)

Then log out and back in.""")

        self._step_check_btn(f, "Check: Do I have serial permissions?", self._check_serial_perms)
        self.usb_step3_label = ttk.Label(f, text="")
        self.usb_step3_label.pack(anchor=tk.W, padx=20)

        self.fix_perms_btn = ttk.Button(f, text="Fix: Add me to serial group (requires sudo password)",
                                        command=self._fix_serial_perms)
        self.fix_perms_btn.pack(anchor=tk.W, padx=20, pady=(3, 0))

        # Step 4
        self._step_header(f, "Step 4", "Download Mode (manual bootloader entry)")
        self._step_body(f, """\
Normally you do NOT need download mode — the CH340X auto-resets
the board into bootloader mode when PlatformIO or esptool flash.

If auto-reset fails (flash hangs or times out), enter download
mode manually:

  1. Hold the BOOT button (do not release)
  2. Press and release the RST button (while still holding BOOT)
  3. Release the BOOT button
  4. The board is now in download mode for 5 seconds
  5. Run the flash command immediately

  Button locations on the Olimex board:
  ┌──────────────────────────────────────┐
  │  [USB-OTG]         [USB-UART]        │
  │                                      │
  │  [RST]  [BOOT]   (o) Green LED      │
  │                   (o) Yellow LED     │
  │  ▓▓▓▓▓▓▓▓▓▓▓▓▓▓▓▓▓▓▓▓▓▓▓▓▓▓▓▓▓▓   │
  │  ▓  ESP32-S3-WROOM-1-N8R8      ▓   │
  │  ▓▓▓▓▓▓▓▓▓▓▓▓▓▓▓▓▓▓▓▓▓▓▓▓▓▓▓▓▓▓   │
  └──────────────────────────────────────┘

After flashing, press RST once to reboot into normal mode.""")

        # Step 5
        self._step_header(f, "Step 5", "Open the Serial Monitor")
        self._step_body(f, """\
Everything looks good — switch to the Serial Monitor tab.

  1. Go to the "Serial Monitor" tab
  2. Port should show /dev/ttyUSB0
  3. Baud rate: 115200
  4. Click "Connect"

Expected output after flashing Dilder firmware:
  === Dilder ESP32-S3 Firmware ===
  Board: ESP32-S3 (Olimex)
  PSRAM: 8388608 bytes""")

        ttk.Button(f, text="Go to Serial Monitor",
                   command=lambda: self.app.notebook.select(self.app.serial_tab)).pack(
                       anchor=tk.W, padx=20, pady=(5, 20))

    def _check_usb_esp32(self):
        try:
            result = subprocess.run(["lsusb"], capture_output=True, text=True, timeout=5)
            ch340_lines = [l for l in result.stdout.splitlines()
                           if "1a86" in l.lower() or "ch340" in l.lower() or "qinheng" in l.lower()]
            if ch340_lines:
                self.esp_step1_label.config(
                    text=f"  ✓ CH340X detected: {ch340_lines[0].strip()}",
                    foreground=FG_GREEN)
                self.app.log("USB check: CH340X (ESP32-S3) detected")
            else:
                self.esp_step1_label.config(
                    text="  ✗ No CH340X found. Is the USB-UART port plugged in?",
                    foreground=FG_RED)
        except (FileNotFoundError, subprocess.TimeoutExpired):
            self.esp_step1_label.config(
                text="  ? lsusb not available — check manually: dmesg | tail",
                foreground=FG_YELLOW)

    def _check_serial_esp32(self):
        port = find_esp32_serial()
        if port:
            self.esp_step2_label.config(
                text=f"  ✓ {port} detected — ESP32-S3 serial ready",
                foreground=FG_GREEN)
            self.app.log(f"Serial port check: {port} found (ESP32)")
        else:
            import glob as _glob
            others = _glob.glob("/dev/ttyUSB*")
            if others:
                self.esp_step2_label.config(
                    text=f"  ~ ESP32 not auto-detected, but found: {', '.join(others)}",
                    foreground=FG_YELLOW)
            else:
                self.esp_step2_label.config(
                    text="  ✗ No /dev/ttyUSB* found. Check USB-UART cable.",
                    foreground=FG_RED)

    # ── ESP32-S3 Wi-Fi Panel ────────────────────────────────────────────────

    def _build_wifi_panel_esp32(self):
        canvas = tk.Canvas(self.content, bg=BG_PANEL, highlightthickness=0)
        scrollbar = ttk.Scrollbar(self.content, orient=tk.VERTICAL, command=canvas.yview)
        scroll_frame = ttk.Frame(canvas)

        scroll_frame.bind("<Configure>", lambda e: canvas.configure(scrollregion=canvas.bbox("all")))
        canvas.create_window((0, 0), window=scroll_frame, anchor=tk.NW)
        canvas.configure(yscrollcommand=scrollbar.set)

        scrollbar.pack(side=tk.RIGHT, fill=tk.Y)
        canvas.pack(side=tk.LEFT, fill=tk.BOTH, expand=True)

        canvas.bind_all("<Button-4>", lambda e: canvas.yview_scroll(-3, "units"))
        canvas.bind_all("<Button-5>", lambda e: canvas.yview_scroll(3, "units"))

        f = scroll_frame

        self._step_header(f, "Overview", "ESP32-S3 Wi-Fi Connection")
        self._step_body(f, """\
The ESP32-S3 has built-in 802.11 b/g/n Wi-Fi (2.4 GHz)
and Bluetooth 5.0 LE — no external chip needed.

Wi-Fi is configured through the Arduino framework or
ESP-IDF. The PlatformIO project already includes the
WiFi library.

This is not yet used in the Dilder prototype firmware.
Below are the steps to add Wi-Fi when ready.""")

        self._step_header(f, "Step 1", "Add Wi-Fi to your ESP32-S3 firmware")
        self._step_body(f, """\
In your main.cpp or a separate wifi_setup.cpp:

  #include <WiFi.h>

  void setup() {
      WiFi.begin("YOUR_SSID", "YOUR_PASSWORD");
      while (WiFi.status() != WL_CONNECTED) {
          delay(500);
          Serial.print(".");
      }
      Serial.print("IP: ");
      Serial.println(WiFi.localIP());
  }

The Arduino WiFi library handles all the ESP-IDF
networking stack underneath.""")

        self._step_header(f, "Step 2", "Test the connection")
        self._step_body(f, """\
After flashing, open the Serial Monitor to see the IP address.
Then test from your computer:

  ping <IP_ADDRESS>

The ESP32-S3 supports mDNS (WiFi.setHostname("dilder"))
and TCP/HTTP servers just like the Pico W.""")

        conn_frame = ttk.Frame(f)
        conn_frame.pack(fill=tk.X, padx=20, pady=(0, 10))

        ttk.Label(conn_frame, text="IP:").pack(side=tk.LEFT)
        self.wifi_ip_var = tk.StringVar(value="192.168.1.")
        ttk.Entry(conn_frame, textvariable=self.wifi_ip_var, width=16).pack(side=tk.LEFT, padx=(3, 10))

        ttk.Label(conn_frame, text="Port:").pack(side=tk.LEFT)
        self.wifi_port_var = tk.StringVar(value="4242")
        ttk.Entry(conn_frame, textvariable=self.wifi_port_var, width=6).pack(side=tk.LEFT, padx=(3, 10))

        ttk.Button(conn_frame, text="Test Connection", command=self._test_wifi_conn).pack(side=tk.LEFT)

        self.wifi_conn_label = ttk.Label(f, text="")
        self.wifi_conn_label.pack(anchor=tk.W, padx=20, pady=(0, 20))

    # ── Wi-Fi Checks ─────────────────────────────────────────────────────────

    def _scan_network(self):
        self.wifi_scan_label.config(text="  Scanning...", foreground=FG_YELLOW)
        self.update_idletasks()

        def _do_scan():
            # Try nmap ping scan on common subnets
            found = []
            try:
                # Get local subnet
                result = subprocess.run(
                    ["ip", "route", "show", "default"],
                    capture_output=True, text=True, timeout=3
                )
                gateway = None
                if result.returncode == 0:
                    parts = result.stdout.split()
                    if "via" in parts:
                        gateway = parts[parts.index("via") + 1]

                if gateway:
                    subnet = ".".join(gateway.split(".")[:3]) + ".0/24"
                    # Quick arp scan
                    result = subprocess.run(
                        ["ip", "neigh", "show"],
                        capture_output=True, text=True, timeout=5
                    )
                    if result.returncode == 0:
                        for line in result.stdout.splitlines():
                            if "REACHABLE" in line or "STALE" in line:
                                ip = line.split()[0]
                                found.append(ip)

            except (FileNotFoundError, subprocess.TimeoutExpired):
                pass

            def _update():
                if found:
                    bn = BOARD_LABELS.get(self.app.target_board, "Pico")
                    self.wifi_scan_label.config(
                        text=f"  Found {len(found)} devices on local network. "
                             f"Check serial output for {bn}'s IP address.",
                        foreground=FG_GREEN)
                else:
                    bn = BOARD_LABELS.get(self.app.target_board, "Pico")
                    self.wifi_scan_label.config(
                        text=f"  No devices found. Check that {bn} firmware has Wi-Fi enabled.",
                        foreground=FG_YELLOW)

            self.winfo_toplevel().after(0, _update)

        threading.Thread(target=_do_scan, daemon=True).start()

    def _test_wifi_conn(self):
        import socket
        ip = self.wifi_ip_var.get().strip()
        try:
            port = int(self.wifi_port_var.get().strip())
        except ValueError:
            self.wifi_conn_label.config(text="  ✗ Invalid port number", foreground=FG_RED)
            return

        self.wifi_conn_label.config(text=f"  Connecting to {ip}:{port}...", foreground=FG_YELLOW)
        self.update_idletasks()

        def _do_connect():
            try:
                sock = socket.socket(socket.AF_INET, socket.SOCK_STREAM)
                sock.settimeout(3)
                sock.connect((ip, port))
                sock.close()
                bn = BOARD_LABELS.get(self.app.target_board, "Pico")
                msg = f"  ✓ Connected to {ip}:{port} — {bn} is reachable"
                colour = FG_GREEN
                self.app.log(f"Wi-Fi test: connected to {ip}:{port}")
            except socket.timeout:
                bn = BOARD_LABELS.get(self.app.target_board, "Pico")
                msg = f"  ✗ Connection timed out. Is the {bn} running a TCP server on port {port}?"
                colour = FG_RED
            except ConnectionRefusedError:
                bn = BOARD_LABELS.get(self.app.target_board, "Pico")
                msg = f"  ✗ Connection refused. The {bn} is reachable but no server on port {port}."
                colour = FG_YELLOW
            except OSError as e:
                msg = f"  ✗ Connection failed: {e}"
                colour = FG_RED

            self.winfo_toplevel().after(0, lambda: self.wifi_conn_label.config(text=msg, foreground=colour))

        threading.Thread(target=_do_connect, daemon=True).start()


# ─────────────────────────────────────────────────────────────────────────────
# Documentation Tab
# ─────────────────────────────────────────────────────────────────────────────

class DocumentationTab(ttk.Frame):
    """Embedded application documentation with searchable text."""

    def __init__(self, parent, app):
        super().__init__(parent)
        self.app = app
        self._build_ui()

    def _build_ui(self):
        # ── Search bar ──
        search_frame = ttk.Frame(self)
        search_frame.pack(fill=tk.X, padx=10, pady=(10, 5))

        ttk.Label(search_frame, text="Search:").pack(side=tk.LEFT, padx=(0, 5))
        self.search_var = tk.StringVar()
        self.search_entry = ttk.Entry(search_frame, textvariable=self.search_var, width=30)
        self.search_entry.pack(side=tk.LEFT, padx=(0, 5))
        self.search_entry.bind("<Return>", self._search)
        ttk.Button(search_frame, text="Find", command=self._search).pack(side=tk.LEFT, padx=2)
        ttk.Button(search_frame, text="Clear", command=self._clear_search).pack(side=tk.LEFT, padx=2)

        # ── TOC + Content ──
        paned = ttk.PanedWindow(self, orient=tk.HORIZONTAL)
        paned.pack(fill=tk.BOTH, expand=True, padx=10, pady=(0, 10))

        # TOC sidebar
        toc_frame = ttk.Frame(paned)
        paned.add(toc_frame, weight=1)

        ttk.Label(toc_frame, text="Contents", font=("JetBrains Mono", 11, "bold"),
                  foreground=FG_ACCENT).pack(anchor=tk.W, pady=(0, 5))

        self.toc_list = tk.Listbox(
            toc_frame, width=28, bg=BG_DARK, fg=FG_TEXT,
            selectbackground=FG_ACCENT, selectforeground=BG_DARK,
            font=("JetBrains Mono", 10), activestyle="none",
        )
        self.toc_list.pack(fill=tk.BOTH, expand=True)
        self.toc_list.bind("<<ListboxSelect>>", self._on_toc_select)

        # Content area
        content_frame = ttk.Frame(paned)
        paned.add(content_frame, weight=4)

        self.doc_text = tk.Text(
            content_frame, wrap=tk.WORD, bg=BG_DARK, fg=FG_TEXT,
            font=("JetBrains Mono", 10), state=tk.DISABLED,
            selectbackground=FG_ACCENT, selectforeground=BG_DARK,
            padx=15, pady=10,
        )
        doc_scroll = ttk.Scrollbar(content_frame, command=self.doc_text.yview)
        self.doc_text.configure(yscrollcommand=doc_scroll.set)
        doc_scroll.pack(side=tk.RIGHT, fill=tk.Y)
        self.doc_text.pack(fill=tk.BOTH, expand=True)

        # Configure text tags
        self.doc_text.tag_configure("h1", font=("JetBrains Mono", 16, "bold"),
                                    foreground=FG_ACCENT, spacing3=10)
        self.doc_text.tag_configure("h2", font=("JetBrains Mono", 13, "bold"),
                                    foreground=FG_MAGENTA, spacing1=15, spacing3=5)
        self.doc_text.tag_configure("body", font=("JetBrains Mono", 10),
                                    foreground=FG_TEXT, spacing1=2, lmargin1=10, lmargin2=10)
        self.doc_text.tag_configure("code", font=("JetBrains Mono", 10),
                                    foreground=FG_GREEN, background="#1a1a2e",
                                    lmargin1=30, lmargin2=30, spacing1=2)
        self.doc_text.tag_configure("highlight", background=FG_YELLOW, foreground=BG_DARK)
        self.doc_text.tag_configure("key", font=("JetBrains Mono", 10, "bold"),
                                    foreground=FG_YELLOW)

        self._load_docs()

    def refresh_for_board(self, board_key=None):
        """Rebuild documentation when the target board changes."""
        self.toc_list.delete(0, tk.END)
        self._load_docs()

    def _load_docs(self):
        self.sections = []
        self.section_indices = {}

        docs = self._get_documentation()

        self.doc_text.configure(state=tk.NORMAL)
        self.doc_text.delete("1.0", tk.END)

        for section in docs:
            title = section["title"]
            self.sections.append(title)
            self.toc_list.insert(tk.END, title)

            idx = self.doc_text.index(tk.END)
            self.section_indices[title] = idx

            if section.get("level") == 1:
                self.doc_text.insert(tk.END, title + "\n", "h1")
            else:
                self.doc_text.insert(tk.END, title + "\n", "h2")

            for block in section["content"]:
                if block["type"] == "text":
                    self.doc_text.insert(tk.END, block["text"] + "\n", "body")
                elif block["type"] == "code":
                    self.doc_text.insert(tk.END, block["text"] + "\n", "code")

            self.doc_text.insert(tk.END, "\n", "body")

        self.doc_text.configure(state=tk.DISABLED)

    def _on_toc_select(self, event=None):
        sel = self.toc_list.curselection()
        if not sel:
            return
        title = self.toc_list.get(sel[0])
        if title in self.section_indices:
            self.doc_text.see(self.section_indices[title])

    def _search(self, event=None):
        query = self.search_var.get().strip()
        if not query:
            return

        self.doc_text.tag_remove("highlight", "1.0", tk.END)

        start = "1.0"
        first_match = None
        while True:
            pos = self.doc_text.search(query, start, stopindex=tk.END, nocase=True)
            if not pos:
                break
            end = f"{pos}+{len(query)}c"
            self.doc_text.tag_add("highlight", pos, end)
            if first_match is None:
                first_match = pos
            start = end

        if first_match:
            self.doc_text.see(first_match)

    def _clear_search(self):
        self.search_var.set("")
        self.doc_text.tag_remove("highlight", "1.0", tk.END)

    def _get_documentation(self):
        """Return structured documentation content (adapts to selected board)."""
        board = self.app.target_board
        bn = BOARD_LABELS.get(board, "Pico W (RP2040)")
        drive = "RP2350" if board == BOARD_PICO2_W else "RPI-RP2"
        return [
            {
                "title": "Dilder DevTool",
                "level": 1,
                "content": [
                    {"type": "text", "text": (
                        f"A development companion for the {bn} + Waveshare 2.13\" "
                        "e-ink display. Provides tools for drawing display images, "
                        "monitoring serial output, flashing firmware, managing assets, "
                        "and connecting over USB or Wi-Fi."
                    )},
                ],
            },
            {
                "title": "Display Emulator",
                "level": 2,
                "content": [
                    {"type": "text", "text": (
                        "A 250x122 pixel canvas that matches the real e-ink display exactly. "
                        "Everything is 1-bit monochrome — black or white only.\n\n"
                        "Tools:\n"
                        "  Pencil — freehand draw in black (click or drag)\n"
                        "  Eraser — freehand erase to white\n"
                        "  Line — click start, drag to end, release\n"
                        "  Rect — draw a rectangle outline\n"
                        "  Fill Rect — draw a filled rectangle\n"
                        "  Text — click a position, type text in the dialog\n\n"
                        "The Size spinner controls brush width and line thickness.\n"
                        "The Font spinner controls text size (8-48 px)."
                    )},
                    {"type": "text", "text": (
                        "Saving:\n"
                        "Click Save, enter a name. Three files are created in assets/:\n"
                        "  name.pbm — PBM binary (standard 1-bit image format)\n"
                        "  name.bin — raw bytes (direct display buffer for C code)\n"
                        "  name.png — PNG image (requires Pillow)\n\n"
                        "Loading:\n"
                        "Click Load to open any .pbm, .bin, or .png file back into the canvas."
                    )},
                    {"type": "text", "text": (
                        "Send to Pico:\n"
                        f"Transmits the current image to the {bn} over USB serial. "
                        "Requires firmware that listens for the IMG: protocol."
                    )},
                ],
            },
            {
                "title": "Serial Monitor",
                "level": 2,
                "content": [
                    {"type": "text", "text": (
                        f"Live serial terminal for the {bn} USB connection.\n\n"
                        "1. Select the port (auto-detects /dev/ttyACM0)\n"
                        "2. Set baud rate to 115200\n"
                        "3. Click Connect\n"
                        "4. printf() output from your firmware appears in real time"
                    )},
                    {"type": "text", "text": (
                        "Sending commands:\n"
                        "Type in the input bar and press Enter. Text is sent with \\r\\n.\n\n"
                        "Special buttons:\n"
                        "  Ctrl+C — interrupt running code\n"
                        f"  Reset — soft-reset the {bn} (Ctrl+D)\n\n"
                        "Save Log saves the full output history to a text file."
                    )},
                ],
            },
            {
                "title": "Flash Firmware",
                "level": 2,
                "content": [
                    {"type": "text", "text": (
                        f"Flash .uf2 firmware files to the {bn}.\n\n"
                        "Steps:\n"
                        "1. Select a .uf2 file (Browse or Quick Flash buttons)\n"
                        f"2. Put {bn} in BOOTSEL mode:\n"
                        "   - Unplug USB\n"
                        "   - Hold BOOTSEL button\n"
                        "   - Plug in USB while holding\n"
                        "   - Release after 1 second\n"
                        f"3. Click Detect {drive}\n"
                        "4. Click Flash\n\n"
                        f"The {bn} reboots automatically after flashing."
                    )},
                    {"type": "text", "text": (
                        "Build buttons:\n"
                        "Build Hello Serial and Build Hello Display run CMake + Ninja "
                        "directly. Output appears in the log bar. Requires the ARM "
                        "toolchain and PICO_SDK_PATH to be set."
                    )},
                ],
            },
            {
                "title": "Assets",
                "level": 2,
                "content": [
                    {"type": "text", "text": (
                        "Browse and manage display images saved in the assets/ folder.\n\n"
                        "Click a file to preview it at 2x scale. The preview shows "
                        "exactly how the image will look on the e-ink display.\n\n"
                        "Supported formats: .pbm, .bin, .png\n\n"
                        "Delete removes the selected file. Open Folder opens assets/ "
                        "in your system file manager."
                    )},
                ],
            },
            {
                "title": "GPIO Pins",
                "level": 2,
                "content": [
                    {"type": "text", "text": (
                        f"Visual reference of the {bn} 40-pin header with all Dilder "
                        "project assignments. Shows display SPI1 pins, button pins, "
                        "power connections, and SPI configuration."
                    )},
                ],
            },
            {
                "title": "Connection Utility",
                "level": 2,
                "content": [
                    {"type": "text", "text": (
                        f"Step-by-step walkthrough for connecting the {bn}.\n\n"
                        "USB Serial:\n"
                        "Guides you through plugging in, verifying the serial port, "
                        "checking permissions, and opening the serial monitor. "
                        "Each step has a Check button that verifies the current state.\n\n"
                        "Wi-Fi:\n"
                        "Explains how to add Wi-Fi to your firmware, provides the C "
                        "code and CMake config, and includes a TCP connection tester. "
                        f"The {bn} supports 802.11n on 2.4 GHz."
                    )},
                ],
            },
            {
                "title": "Keyboard Shortcuts",
                "level": 2,
                "content": [
                    {"type": "text", "text": (
                        "Display Emulator:\n"
                        "  Left-click — draw/place with current tool\n"
                        "  Drag — freehand draw or shape preview\n"
                        "  Release — finalise shape (line/rect)\n\n"
                        "Serial Monitor:\n"
                        "  Enter — send command\n"
                        "  Ctrl+C button — interrupt\n"
                        "  Reset button — soft-reset (Ctrl+D)"
                    )},
                ],
            },
            {
                "title": "File Formats",
                "level": 2,
                "content": [
                    {"type": "text", "text": (
                        "PBM (P4 Binary):\n"
                        "Standard 1-bit image. Header + packed binary data.\n"
                        "Each byte = 8 pixels, MSB = leftmost. 1=black, 0=white."
                    )},
                    {"type": "code", "text": (
                        "P4\n"
                        "250 122\n"
                        "<3904 bytes of pixel data>"
                    )},
                    {"type": "text", "text": (
                        "BIN (Raw Display Buffer):\n"
                        "No header. 32 bytes/row x 122 rows = 3904 bytes.\n"
                        "Same byte layout as the Waveshare driver framebuffer.\n"
                        "Can be loaded directly in C code:"
                    )},
                    {"type": "code", "text": (
                        "const uint8_t img[3904] = { /* .bin contents */ };\n"
                        "EPD_2in13_V3_Display(img);"
                    )},
                    {"type": "text", "text": (
                        "PNG:\n"
                        "Standard 250x122 1-bit PNG. Requires Pillow to save/load."
                    )},
                ],
            },
            {
                "title": "Troubleshooting",
                "level": 2,
                "content": [
                    {"type": "text", "text": (
                        "tkinter not found:\n"
                        "  Arch: sudo pacman -S tk\n"
                        "  Debian: sudo apt install python3-tk\n\n"
                        "pyserial not found:\n"
                        "  sudo pacman -S python-pyserial  (Arch)\n"
                        "  pip install pyserial  (other)\n\n"
                        "Text tool renders blocks:\n"
                        "  Install Pillow: pip install Pillow\n\n"
                        "Serial monitor can't connect:\n"
                        "  Check USB cable is data-capable\n"
                        "  Check serial group: groups | grep uucp\n"
                        "  Check device exists: ls /dev/ttyACM*\n\n"
                        "Flash button says not detected:\n"
                        f"  Put {bn} in BOOTSEL mode first\n"
                        "  (Hold BOOTSEL, plug in USB, release)\n\n"
                        "Canvas is slow with large fills:\n"
                        "  Tkinter draws individual rectangles per pixel.\n"
                        "  Brief lag on large operations is normal."
                    )},
                ],
            },
        ]


# ─────────────────────────────────────────────────────────────────────────────
# Programs Tab — Deploy animated programs to emulator / Pico
# ─────────────────────────────────────────────────────────────────────────────

# ── Sassy Octopus pixel art (drawn on a 250x122 canvas) ──
# Chunky filled-style octopus on the left side with chat bubble on the right.

def _octo_body():
    """Return octopus body as list of (y, [(x0,x1), ...]) run-length pairs."""
    rows = []
    # Head dome (y 10..54)
    head = [
        (10, [(22, 48)]),
        (11, [(18, 52)]),
        (12, [(16, 54)]),
        (13, [(14, 56)]),
        (14, [(13, 57)]),
        (15, [(12, 58)]),
        (16, [(11, 59)]),
        (17, [(10, 60)]),
        (18, [(10, 60)]),
        (19, [(9, 61)]),
        (20, [(9, 61)]),
        (21, [(9, 61)]),
        (22, [(9, 61)]),
        (23, [(9, 61)]),
        (24, [(9, 61)]),
        (25, [(9, 61)]),
        (26, [(9, 61)]),
        (27, [(9, 61)]),
        (28, [(10, 60)]),
        (29, [(10, 60)]),
        (30, [(10, 60)]),
        (31, [(10, 60)]),
        (32, [(10, 60)]),
        (33, [(10, 60)]),
        (34, [(10, 60)]),
        (35, [(10, 60)]),
        (36, [(10, 60)]),
        (37, [(10, 60)]),
        (38, [(10, 60)]),
        (39, [(10, 60)]),
        (40, [(10, 60)]),
        (41, [(11, 59)]),
        (42, [(11, 59)]),
        (43, [(12, 58)]),
        (44, [(13, 57)]),
        (45, [(14, 56)]),
        # Cheeks bulge
        (46, [(12, 58)]),
        (47, [(11, 59)]),
        (48, [(10, 60)]),
        (49, [(10, 60)]),
        (50, [(11, 59)]),
        (51, [(12, 58)]),
        (52, [(13, 57)]),
        (53, [(14, 56)]),
        (54, [(15, 55)]),
    ]
    rows.extend(head)

    # 6 tentacle legs (y 55..85) — wavy appendages
    tentacles = [
        (55, [(10, 17), (21, 28), (32, 39), (43, 50), (54, 61)]),
        (56, [(8, 15), (19, 26), (30, 37), (45, 52), (56, 63)]),
        (57, [(7, 14), (18, 24), (29, 35), (47, 53), (58, 64)]),
        (58, [(6, 12), (19, 25), (31, 37), (46, 52), (57, 63)]),
        (59, [(7, 13), (21, 27), (33, 39), (44, 50), (55, 61)]),
        (60, [(8, 14), (20, 26), (31, 37), (43, 49), (54, 60)]),
        (61, [(9, 14), (18, 24), (30, 36), (44, 50), (56, 62)]),
        (62, [(8, 13), (17, 22), (31, 37), (46, 52), (57, 63)]),
        (63, [(7, 12), (18, 23), (33, 38), (45, 51), (55, 61)]),
        (64, [(8, 13), (20, 25), (32, 37), (43, 48), (54, 59)]),
        (65, [(9, 14), (19, 24), (30, 35), (44, 49), (55, 60)]),
        (66, [(10, 14), (17, 22), (31, 36), (46, 51), (57, 62)]),
        (67, [(9, 13), (18, 22), (33, 37), (45, 50), (56, 61)]),
        (68, [(8, 12), (19, 23), (32, 36), (43, 48), (54, 59)]),
        (69, [(9, 13), (21, 25), (30, 34), (44, 48), (55, 59)]),
        (70, [(10, 14), (20, 24), (31, 35), (46, 50), (57, 61)]),
        (71, [(11, 14), (18, 22), (33, 37), (45, 49), (56, 60)]),
        (72, [(10, 13), (19, 22), (32, 35), (43, 47), (54, 58)]),
        (73, [(9, 12), (20, 23), (30, 33), (44, 47), (55, 58)]),
        (74, [(10, 13), (21, 24), (31, 34), (46, 49), (57, 60)]),
        (75, [(11, 14), (20, 23), (33, 36), (45, 48), (56, 59)]),
        (76, [(12, 14), (19, 22), (32, 35), (43, 46), (54, 57)]),
        (77, [(11, 13), (20, 22), (30, 33), (44, 46), (55, 57)]),
        (78, [(10, 12), (21, 23), (31, 33), (45, 47), (56, 58)]),
        (79, [(11, 13), (22, 24), (32, 34), (44, 46), (55, 57)]),
        (80, [(12, 14), (21, 23), (33, 35), (43, 45), (54, 56)]),
    ]
    rows.extend(tentacles)
    return rows


def _octo_body_fat():
    """Return fat octopus body — wider dome, no waist taper, thicker tentacles."""
    rows = []
    # Fat head dome — starts 2 rows higher, widens faster
    head = [
        (8, [(25, 45)]),  (9, [(21, 49)]),
        (10, [(18, 52)]), (11, [(15, 55)]), (12, [(13, 57)]), (13, [(11, 59)]),
        (14, [(10, 60)]), (15, [(9, 61)]),  (16, [(8, 62)]),  (17, [(7, 63)]),
        (18, [(6, 64)]),  (19, [(5, 65)]),  (20, [(5, 65)]),  (21, [(5, 65)]),
        (22, [(5, 65)]),  (23, [(5, 65)]),  (24, [(5, 65)]),  (25, [(5, 65)]),
        (26, [(5, 65)]),  (27, [(5, 65)]),
        # Fat body — stays wide, barely any waist
        (28, [(5, 65)]),  (29, [(5, 65)]),  (30, [(5, 65)]),  (31, [(6, 64)]),
        (32, [(6, 64)]),  (33, [(6, 64)]),  (34, [(6, 64)]),  (35, [(6, 64)]),
        (36, [(6, 64)]),  (37, [(6, 64)]),  (38, [(6, 64)]),  (39, [(6, 64)]),
        (40, [(6, 64)]),  (41, [(7, 63)]),  (42, [(7, 63)]),  (43, [(8, 62)]),
        (44, [(9, 61)]),  (45, [(10, 60)]),
        # Fat cheek bulge
        (46, [(8, 62)]),  (47, [(7, 63)]),  (48, [(6, 64)]),  (49, [(6, 64)]),
        (50, [(7, 63)]),  (51, [(8, 62)]),  (52, [(10, 60)]), (53, [(11, 59)]),
        (54, [(12, 58)]),
    ]
    rows.extend(head)
    # Fat tentacles — each span widened +1px per side
    tentacles = [
        (55, [(9, 18), (20, 29), (31, 40), (42, 51), (53, 62)]),
        (56, [(7, 16), (18, 27), (29, 38), (44, 53), (55, 64)]),
        (57, [(6, 15), (17, 25), (28, 36), (46, 54), (57, 65)]),
        (58, [(5, 13), (18, 26), (30, 38), (45, 53), (56, 64)]),
        (59, [(6, 14), (20, 28), (32, 40), (43, 51), (54, 62)]),
        (60, [(7, 15), (19, 27), (30, 38), (42, 50), (53, 61)]),
        (61, [(8, 15), (17, 25), (29, 37), (43, 51), (55, 63)]),
        (62, [(7, 14), (16, 23), (30, 38), (45, 53), (56, 64)]),
        (63, [(6, 13), (17, 24), (32, 39), (44, 52), (54, 62)]),
        (64, [(7, 14), (19, 26), (31, 38), (42, 49), (53, 60)]),
        (65, [(8, 15), (18, 25), (29, 36), (43, 50), (54, 61)]),
        (66, [(9, 15), (16, 23), (30, 37), (45, 52), (56, 63)]),
        (67, [(8, 14), (17, 23), (32, 38), (44, 51), (55, 62)]),
        (68, [(7, 13), (18, 24), (31, 37), (42, 49), (53, 60)]),
        (69, [(8, 14), (20, 26), (29, 35), (43, 49), (54, 60)]),
        (70, [(9, 15), (19, 25), (30, 36), (45, 51), (56, 62)]),
        (71, [(10, 15), (17, 23), (32, 38), (44, 50), (55, 61)]),
        (72, [(9, 14), (18, 23), (31, 36), (42, 48), (53, 59)]),
        (73, [(8, 13), (19, 24), (29, 34), (43, 48), (54, 59)]),
        (74, [(9, 14), (20, 25), (30, 35), (45, 50), (56, 61)]),
        (75, [(10, 15), (19, 24), (32, 37), (44, 49), (55, 60)]),
        (76, [(11, 15), (18, 23), (31, 36), (42, 47), (53, 58)]),
        (77, [(10, 14), (19, 23), (29, 34), (43, 47), (54, 58)]),
        (78, [(9, 13), (20, 24), (30, 34), (44, 48), (55, 59)]),
        (79, [(10, 14), (21, 25), (31, 35), (43, 47), (54, 58)]),
        (80, [(11, 15), (20, 24), (32, 36), (42, 46), (53, 57)]),
    ]
    rows.extend(tentacles)
    return rows
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
