rompasaurus/regardedPal/hardware-design/examples/01-pocketmage-pda/Docs/Documents & Advanced/Subsystem Tests/EInkTest/EInkTest.ino

#include  <GxEPD2_BW.h>

#include  <Fonts/FreeMonoBold9pt7b.h>

GxEPD2_BW<GxEPD2_310_GDEQ031T10, GxEPD2_310_GDEQ031T10::HEIGHT> display(GxEPD2_310_GDEQ031T10(/*CS=*/ 2, /*DC=*/ 21, /*RST=*/ 9, /*BUSY=*/ 37)); 

volatile bool GxEPD2_310_GDEQ031T10::useFastFullUpdate = true;

const unsigned char backgroundaero [] PROGMEM = {
	0xff, 0xff, 0xff, 0xff, 0xff, 0xff, 0xff, 0xff, 0xff, 0xff, 0xff, 0xff, 0xff, 0xff, 0xff, 0xff, 
	0xff, 0xff, 0xff, 0xff, 0xff, 0xff, 0xff, 0xff, 0xff, 0xff, 0xff, 0xff, 0xff, 0x7e, 0xee, 0xdb, 
	0x6a, 0x91, 0x29, 0x00, 0x00, 0x05, 0x55, 0x6d, 0xee, 0xee, 0xee, 0xee, 0xdb, 0x6d, 0xb6, 0xdb, 
	0x6d, 0xb6, 0xdb, 0x6d, 0xb6, 0xdb, 0x6d, 0xb5, 0xad, 0x6b, 0x5a, 0xd6, 0xb5, 0xad, 0x6b, 0x55, 
	0x55, 0x55, 0x55, 0x55, 0x55, 0xd7, 0xbb, 0xef, 0xbd, 0x4a, 0xa4, 0xaa, 0x90, 0x12, 0xbf, 0xb7, 
	0xbf, 0xbf, 0xbb, 0xbb, 0xff, 0xff, 0xff, 0xff, 0xff, 0xff, 0xff, 0xff, 0xff, 0xff, 0xfb, 0xef, 
	0xff, 0xff, 0xff, 0xff, 0xff, 0xff, 0xff, 0xff, 0xff, 0xff, 0xff, 0xff, 0xff, 0x7a, 0xee, 0xba, 
	0xd5, 0x50, 0x12, 0x00, 0x00, 0x05, 0x49, 0x7a, 0xfb, 0xfb, 0xff, 0xff, 0x6d, 0xb6, 0xdb, 0x6d, 
	0xb6, 0xd5, 0x6d, 0x55, 0x55, 0x55, 0x5e, 0xbd, 0x6b, 0x5a, 0xd6, 0xb5, 0xad, 0x6b, 0x5a, 0xdb, 
	0x55, 0x55, 0x55, 0x55, 0x55, 0xdf, 0x7b, 0xdd, 0xba, 0x89, 0x48, 0xa0, 0x00, 0x12, 0xb6, 0xd7, 
	0xee, 0xee, 0xee, 0xef, 0xff, 0xff, 0xff, 0xff, 0xff, 0xff, 0xff, 0xff, 0xff, 0xff, 0xf7, 0xf7, 
	0xfe, 0xff, 0xbf, 0xef, 0xfb, 0xfe, 0xff, 0xbf, 0xff, 0xff, 0xff, 0xff, 0xff, 0x75, 0xad, 0x6b, 
	0x6e, 0xa0, 0x02, 0x04, 0x40, 0x04, 0x4b, 0x6d, 0xff, 0xbf, 0xbb, 0xbb, 0x6d, 0xb6, 0xda, 0xb5, 
	0x55, 0x6e, 0xd5, 0xdd, 0xdd, 0xb6, 0xdd, 0xbe, 0xdb, 0xaa, 0xf5, 0x7d, 0x5f, 0x57, 0xd5, 0xea, 
	0xaa, 0xaa, 0xaa, 0xaa, 0xab, 0xde, 0xf7, 0xbd, 0xb5, 0x52, 0x10, 0x00, 0x00, 0x11, 0x55, 0xb6, 
	0xb7, 0xfb, 0xff, 0xff, 0xff, 0xff, 0xff, 0xff, 0xff, 0xfb, 0xff, 0x77, 0x77, 0xff, 0xff, 0xef, 
	0xf6, 0xd7, 0xdf, 0xd7, 0xf5, 0xfd, 0xbf, 0x7f, 0xff, 0xff, 0xff, 0xff, 0xfe, 0xf7, 0x5a, 0xd7, 
	0x6d, 0xa0, 0x01, 0x00, 0x00, 0x04, 0xaa, 0xbb, 0xfd, 0xbe, 0xdd, 0xdb, 0x6d, 0xb6, 0xad, 0xdb, 
	0xdd, 0xaf, 0x6d, 0xff, 0xfe, 0xd6, 0xb5, 0x7a, 0xbf, 0xf6, 0xf6, 0xfe, 0xdf, 0xb7, 0xf7, 0xda, 
	0xad, 0x5a, 0xad, 0x5a, 0xab, 0x5b, 0xee, 0xfb, 0xb6, 0x94, 0x00, 0x00, 0x00, 0x01, 0x15, 0xad, 
	0xdf, 0xef, 0xf7, 0x7f, 0xff, 0xff, 0xff, 0x7e, 0xf7, 0xfd, 0xff, 0xb5, 0xab, 0xff, 0xff, 0xdf, 
	0xea, 0xab, 0xbf, 0xb7, 0xbb, 0x7d, 0x5d, 0x77, 0xfb, 0xf7, 0xfb, 0xf7, 0xff, 0xed, 0x5b, 0x55, 
	0x5a, 0xd0, 0x00, 0x00, 0x00, 0x10, 0xaa, 0xd6, 0xf6, 0xfb, 0x7f, 0xed, 0xb6, 0xdb, 0x6d, 0xef, 
	0xbe, 0xdf, 0xab, 0xef, 0xff, 0x5a, 0xd6, 0xf5, 0xbf, 0xd5, 0xea, 0xfa, 0xef, 0xd7, 0xf7, 0xde, 
	0xae, 0xdd, 0x5e, 0xdd, 0xaa, 0xbf, 0xf6, 0xdf, 0xeb, 0x24, 0x00, 0x00, 0x00, 0x02, 0x2a, 0xbb, 
	0xbf, 0xbf, 0xdb, 0x7f, 0xff, 0xff, 0xff, 0xba, 0xef, 0xf5, 0xfe, 0xbd, 0x6d, 0xff, 0xff, 0xbf, 
	0xd5, 0x4a, 0xbf, 0xaf, 0xfa, 0xfd, 0xbd, 0xf7, 0xfb, 0xb7, 0xf7, 0x77, 0x7f, 0xea, 0xad, 0xaa, 
	0xba, 0xa8, 0x00, 0x00, 0x00, 0x00, 0x8a, 0xd5, 0xf6, 0xed, 0xff, 0xed, 0xad, 0x55, 0x6b, 0xff, 
	0xfa, 0xbf, 0x6f, 0xf7, 0xff, 0x6a, 0xaa, 0xea, 0xbf, 0xa5, 0xf6, 0xfb, 0x5f, 0xaf, 0xef, 0x5d, 
	0x5e, 0xfd, 0x5b, 0xdd, 0xd5, 0x5f, 0x7b, 0xfb, 0x55, 0x50, 0x00, 0x00, 0x00, 0x02, 0x25, 0x5e, 
	0xdf, 0xff, 0x6d, 0xbf, 0xff, 0xff, 0xfe, 0xab, 0x5f, 0xed, 0xfa, 0xde, 0xab, 0xdf, 0xff, 0xbf, 
	0xed, 0x82, 0xdd, 0xdf, 0xf5, 0xfa, 0xbb, 0xf7, 0xeb, 0xab, 0xed, 0x77, 0x7f, 0xf5, 0xd6, 0xad, 
	0xbb, 0x44, 0x00, 0x00, 0x00, 0x00, 0x15, 0x6a, 0xfb, 0x6d, 0xff, 0xf6, 0xdb, 0x77, 0x5f, 0xff, 
	0xf6, 0xff, 0xaf, 0xfb, 0xfe, 0xfb, 0x6d, 0xed, 0xbf, 0x66, 0xf7, 0x75, 0x5f, 0x5f, 0xee, 0xbd, 
	0x7d, 0x7d, 0x77, 0xbb, 0xd5, 0x5e, 0xbb, 0x76, 0xd5, 0x51, 0x00, 0x00, 0x00, 0x00, 0x92, 0xab, 
	0xbf, 0xff, 0xb6, 0xdf, 0xff, 0xdd, 0xe0, 0x2d, 0xbf, 0xaa, 0xfd, 0xaf, 0x6d, 0xaf, 0xdf, 0x7e, 
	0xd5, 0xaa, 0xbf, 0xdf, 0xf6, 0xf5, 0xbb, 0xef, 0xab, 0xd7, 0xad, 0x6d, 0x7f, 0xeb, 0xdd, 0xab, 
	0x56, 0xa4, 0x00, 0x00, 0x00, 0x02, 0x0a, 0xaa, 0xed, 0xb6, 0xff, 0xfb, 0x6b, 0x7f, 0x95, 0x47, 
	0xed, 0xff, 0xdf, 0x7d, 0xff, 0xfa, 0xf5, 0xd7, 0xbf, 0xe5, 0xea, 0xf6, 0xbd, 0xdf, 0x7e, 0xb5, 
	0x76, 0xba, 0xf7, 0xb7, 0xaa, 0xbd, 0x6b, 0xfd, 0xea, 0x90, 0x00, 0x00, 0x00, 0x00, 0x49, 0x55, 
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
};

void setup() {
  // put your setup code here, to run once:
  display.init(115200);
  display.setRotation(3);
  display.setTextColor(GxEPD_BLACK);

  delay(5000);
}

void loop() {
  // put your main code here, to run repeatedly:
  // FULL REFRESH TXT
  display.setFullWindow();  // Use the entire screen area
  display.fillScreen(GxEPD_WHITE);  // Clear the display
  display.setCursor(10, 30);
  display.setTextColor(GxEPD_BLACK);
  display.setFont(&FreeMonoBold9pt7b);
  display.print("Full Refresh Example");
  display.display(false);  // Perform a full refresh
  delay(3000);  // Ensure the 3-second delay before the next update

  // FULL REFRESH TXT (2)
  display.setFullWindow();  // Use the entire screen area
  display.fillScreen(GxEPD_WHITE);  // Clear the display
  display.setCursor(10, 30);
  display.setTextColor(GxEPD_BLACK);
  display.setFont(&FreeMonoBold9pt7b);
  display.print("Full Refresh Example 2");
  
  GxEPD2_310_GDEQ031T10::useFastFullUpdate = false;
  display.refresh(false);

  delay(3000);  // Ensure the 3-second delay before the next update

  // FULL REFRESH IMG
  display.setFullWindow();  // Use the entire screen area
  display.fillScreen(GxEPD_WHITE);  // Clear the display
  display.drawBitmap(0, 0, backgroundaero, 320, 240, GxEPD_BLACK);
  display.display(false);  // Perform a full refresh
  delay(3000);  // Ensure the 3-second delay before the next update

  // FULL FAST REFRESH TEXT
  display.setFullWindow();  // Use the entire screen area
  display.fillScreen(GxEPD_WHITE);
  display.setCursor(10, 30);
  display.setTextColor(GxEPD_BLACK);
  display.setFont(&FreeMonoBold9pt7b);
  display.print("Fast Full Refresh");
  display.display(true);  // Perform a fast refresh
  delay(3000);  // Ensure the 1-second delay before the next update


  // Define the partial update area (e.g., 50x50 box starting at x=10, y=10)
  /*display.setRotation(3);
  //display.setPartialWindow(0, 0, 240, 15);
  //display.fillScreen(GxEPD_WHITE);
  display.setFullWindow();
  display.fillRect(0,0,240,15,GxEPD_WHITE);
  display.setCursor(0, 10);
  display.setTextColor(GxEPD_BLACK);
  display.setFont(&FreeMonoBold9pt7b);
  display.print("Partial Update");
  display.displayWindow(0,0,240,15);
  //display.display(true);  // Perform a partial refresh
  delay(3000);  // Ensure the 0.5-second delay before the next update*/
}
