rompasaurus/regardedPal/hardware-design/examples/01-pocketmage-pda/Code/PocketMage_V3/src/UTILS.cpp

#include <globals.h>
static constexpr const char* TAG = "UTILS";

static uint8_t prevSec = 0;

// DRY helper for battery math to prevent duplicated magic numbers
inline float getBatteryVoltage() {
  return (analogRead(BAT_SENS) * (3.3 / 4095.0) * 2) + 0.2;
}

void printDebug() {
  DateTime now = CLOCK().nowDT();
  if (now.second() != prevSec) {
    prevSec = now.second();
    float batteryVoltage = getBatteryVoltage();

    // Display GPIO states and system info
    ESP_LOGD(
        TAG, "PWR_BTN: %d, KB_INT: %d, CHRG: %d, RTC_INT: %d, BAT: %.2f, CPU_FRQ: %.1f, FFU: %d",
        digitalRead(PWR_BTN), digitalRead(KB_IRQ), digitalRead(CHRG_SENS), digitalRead(RTC_INT),
        batteryVoltage, (float)getCpuFrequencyMhz(), (int)GxEPD2_310_GDEQ031T10::useFastFullUpdate);

    // Display system time
    ESP_LOGD(TAG, "SYSTEM_CLOCK: %d/%d/%d (%s) %d:%d:%d", now.month(), now.day(), now.year(),
             daysOfTheWeek[now.dayOfTheWeek()], now.hour(), now.minute(), now.second());
  }
}

void checkTimeout() {
  int randomScreenSaver = 0;
  CLOCK().setTimeoutMillis(millis());
  ESP_LOGV(TAG, "checking timeout");
  
  // Trigger timeout deep sleep
  if (!disableTimeout) {
    if (CLOCK().getTimeDiff() >= TIMEOUT * 1000) {
      ESP_LOGD(TAG, "Device idle... Deep sleeping");

      // Give a chance to keep device awake
      OLED().oledWord("  Going to sleep!  ");
      unsigned long i = millis();
      unsigned long j = millis();
      while ((j - i) <= 4000) {  // 4 sec
        j = millis();
        if (KB().updateKeypress() != 0) {
          OLED().oledWord("Good Save!");
          delay(500);
          CLOCK().setPrevTimeMillis(millis()); // Reset system idle timer
          keypad.flush();
          return;
        }
        vTaskDelay(pdMS_TO_TICKS(10)); // Prevent watchdog starvation during this while loop
      }

#if !OTA_APP
      saveEditingFile();
#else
      // user skipped reboot flag if true, return to OS normally
      if (!pocketmage::setRebootFlagOTA()) {
        return;
      }
      display.setFullWindow();
#endif

      switch (CurrentAppState) {
#if !OTA_APP
        case TXT:
          if (SLEEPMODE == "TEXT" && PM_SDAUTO().getEditingFile() != "" && !OTA_APP) {
            pocketmage::deepSleep(true);
          } else
            pocketmage::deepSleep();
          break;
#endif
        default:
          pocketmage::deepSleep();
          break;
      }
    }
  } else {
    CLOCK().setPrevTimeMillis(millis());
  }

  // Power Button Event sleep
  if (PWR_BTN_event && CurrentHOMEState != NOWLATER) {
    PWR_BTN_event = false;
    ESP_LOGE(TAG, "Power Button Event: Sleeping now");

#if !OTA_APP
    saveEditingFile();
#endif

    if (digitalRead(CHRG_SENS) == HIGH && !OTA_APP) {
      // Save last state
      prefs.begin("PocketMage", false);
      prefs.putInt("CurrentAppState", static_cast<int>(CurrentAppState));
      prefs.putString("editingFile", PM_SDAUTO().getEditingFile());
      prefs.end();

      CurrentAppState = HOME;
      CurrentHOMEState = NOWLATER;

#if !OTA_APP
      updateTaskArray();
      sortTasksByDueDate(tasks);
#endif
      u8g2.clearBuffer();
      OLED().oledWord(" ");
      OLED().setPowerSave(true);
      disableTimeout = true;
      newState = true;

      // Shutdown Jingle
      BZ().playJingle(Jingles::Shutdown);

      // Clear screen
      display.setFullWindow();
      display.fillScreen(GxEPD_WHITE);

    } else {
      ESP_LOGD(TAG, "Not charging");
      switch (CurrentAppState) {
        case TXT:
          if (SLEEPMODE == "TEXT" && PM_SDAUTO().getEditingFile() != "" && !OTA_APP) {
            ESP_LOGE(TAG, "text sleep mode");
            EINK().setFullRefreshAfter(FULL_REFRESH_AFTER + 1);
            display.setFullWindow();
            display.setFont(&FreeMonoBold9pt7b);

            display.fillRect(0, display.height() - 26, display.width(), 26, GxEPD_WHITE);
            display.drawRect(0, display.height() - 20, display.width(), 20, GxEPD_BLACK);
            display.setCursor(4, display.height() - 6);
            
            EINK().statusBar(PM_SDAUTO().getEditingFile(), true);

            display.fillRect(320 - 86, 240 - 52, 87, 52, GxEPD_WHITE);
            display.drawBitmap(320 - 86, 240 - 52, sleep1, 87, 52, GxEPD_BLACK);

            pocketmage::deepSleep(true);
          }
          // Sleep device normally
          else
            pocketmage::deepSleep();
          break;
        default:
          pocketmage::deepSleep();
          break;
      }
    }

  } else if (PWR_BTN_event && CurrentHOMEState == NOWLATER) {
    ESP_LOGE(TAG, "In NOWLATER state, returning home");
    loadState();
    keypad.flush();

    CurrentHOMEState = HOME_HOME;
    PWR_BTN_event = false;
    OLED().setPowerSave(false);
    display.fillScreen(GxEPD_WHITE);
    EINK().forceSlowFullUpdate(true);

    // Play startup jingle
    BZ().playJingle(Jingles::Startup);

    EINK().refresh();
    delay(200);
    newState = true;
  }
}

void loadState(bool changeState) {
  // LOAD PREFERENCES
  prefs.begin("PocketMage", true);  // Read-Only
  // Misc
  TIMEOUT = prefs.getInt("TIMEOUT", 120);
  DEBUG_VERBOSE = prefs.getBool("DEBUG_VERBOSE", true);
  SYSTEM_CLOCK = prefs.getBool("SYSTEM_CLOCK", true);
  SHOW_YEAR = prefs.getBool("SHOW_YEAR", true);
  SAVE_POWER = prefs.getBool("SAVE_POWER", true);
  ALLOW_NO_MICROSD = prefs.getBool("ALLOW_NO_SD", true);
  PM_SDAUTO().setEditingFile(prefs.getString("editingFile", ""));
  HOME_ON_BOOT = prefs.getBool("HOME_ON_BOOT", false);
  OLED_BRIGHTNESS = prefs.getInt("OLED_BRIGHTNESS", 255);
  OLED_MAX_FPS = prefs.getInt("OLED_MAX_FPS", 60);

  OTA1_APP = prefs.getString("OTA1", "-");
  OTA2_APP = prefs.getString("OTA2", "-");
  OTA3_APP = prefs.getString("OTA3", "-");
  OTA4_APP = prefs.getString("OTA4", "-");

  if (!changeState) {
    prefs.end();
    return;
  }

  u8g2.setContrast(OLED_BRIGHTNESS);

#if !OTA_APP  // POCKETMAGE_OS
  if (HOME_ON_BOOT) {
    CurrentAppState = HOME;
  } else {
    CurrentAppState = static_cast<AppState>(prefs.getInt("CurrentAppState", HOME));

    // Check boot keypress
    KB().setKeyboardState(NORMAL);
    char inchar = KB().updateKeypress();
    switch (inchar) {
      case 'h': CurrentAppState = HOME; break;
      case 'u': CurrentAppState = USB_APP; break;
      case 'f': CurrentAppState = FILEWIZ; break;
      case 't': CurrentAppState = TASKS; break;
      case 'n': CurrentAppState = TXT; break;
      case 's': CurrentAppState = SETTINGS; break;
      case 'c': CurrentAppState = CALENDAR; break;
      case 'j': CurrentAppState = JOURNAL; break;
      case 'd': CurrentAppState = LEXICON; break;
      case 'x': CurrentAppState = TERMINAL; break;
      case 'l': CurrentAppState = APPLOADER; break;
      default: break;
    }

    keypad.flush();

    // Initialize boot app if needed
    switch (CurrentAppState) {
      case HOME:      HOME_INIT(); break;
      case TXT:       TXT_INIT(); break; 
      case SETTINGS:  SETTINGS_INIT(); break;
      case TASKS:     TASKS_INIT(); break;
      case USB_APP:   HOME_INIT(); break;
      case CALENDAR:  CALENDAR_INIT(); break;
      case LEXICON:   LEXICON_INIT(); break;
      case JOURNAL:   JOURNAL_INIT(); break;
      case TERMINAL:  TERMINAL_INIT(); break;
      default:        HOME_INIT(); break;
    }
  }
#endif  // POCKETMAGE_OS
  prefs.end();
}

void updateBattState() {
  float rawVoltage = getBatteryVoltage();

  // Moving average smoothing
  static float filteredVoltage = rawVoltage;
  const float alpha = 0.1;  
  filteredVoltage = alpha * rawVoltage + (1.0 - alpha) * filteredVoltage;

  static float prevVoltage = 0.0;
  static int prevBattState = -1;  
  const float threshold = 0.05;   

  int newState = battState;

  // Charging state overrides everything
  MP2722::MP2722_ChargeStatus chg;
  if (PowerSystem.getChargeStatus(chg) &&
      (chg.code == 0b001 || chg.code == 0b010 || chg.code == 0b011 || chg.code == 0b100 ||
       chg.code == 0b101)) {
    newState = 5;
  } else {
    // Check for low battery
    bool low;
    if (!PowerSystem.isBatteryLow(low)) {
      if (low) {
        OLED().sysMessage("Battery Critical!",1000);

#if !OTA_APP
        saveEditingFile();
#endif
        pocketmage::deepSleep(false);
      }
    }

    // Normal battery voltage thresholds with hysteresis
    if (filteredVoltage > 4.1 || (prevBattState == 4 && filteredVoltage > 4.1 - threshold)) {
      newState = 4;
    } else if (filteredVoltage > 3.9 || (prevBattState == 3 && filteredVoltage > 3.9 - threshold)) {
      newState = 3;
    } else if (filteredVoltage > 3.8 || (prevBattState == 2 && filteredVoltage > 3.8 - threshold)) {
      newState = 2;
    } else if (filteredVoltage > 3.7 || (prevBattState == 1 && filteredVoltage > 3.7 - threshold)) {
      newState = 1;
    } else if (filteredVoltage <= 3.7) {
      newState = 0;
    }
  }

  if (newState != battState) {
    battState = newState;
    prevBattState = newState;
  }

  prevVoltage = filteredVoltage;
}

#pragma region Basic Inputs
// Prompt the user for text input, return the text
String textPrompt(String promptText, String prefix) {
  String currentLine = "";
  int cursor_pos = 0;
  long lastInput = CLOCK().getPrevTimeMillis(); // Sync to system idle
  bool redraw = true; 

  for (;;) {
    #if !OTA_APP 
      if (!noTimeout)  checkTimeout();
      if (DEBUG_VERBOSE) printDebug();
      if (CurrentHOMEState == NOWLATER) return "_RETURN_";
    #endif
    
    updateBattState();
    KB().checkUSBKB();

    int currentMillis = millis();
    String left = "";
    String right = "";

    unsigned long currentSystemTime = CLOCK().getPrevTimeMillis();
    if (currentSystemTime > lastInput) {
        lastInput = currentSystemTime;
        redraw = true;
    }

    char inchar = KB().updateKeypress();

    if (currentMillis - KBBounceMillis >= KB_COOLDOWN) {
      if (inchar != 0) {
        lastInput = millis();
        KBBounceMillis = currentMillis; 
        redraw = true;

        // HANDLE INPUTS
        if (inchar == 23) {
          currentLine = "_RETURN_";
          break;
        }
        else if (inchar == 13) {
          cursor_pos = 0;
          break;
        }
        else if (inchar == 17) {
          if (KB().getKeyboardState() == SHIFT || KB().getKeyboardState() == FN_SHIFT) {
            KB().setKeyboardState(NORMAL);
          } else if (KB().getKeyboardState() == FUNC) {
            KB().setKeyboardState(FN_SHIFT);
          } else {
            KB().setKeyboardState(SHIFT);
          }
        }
        else if (inchar == 18) {
          if (KB().getKeyboardState() == FUNC || KB().getKeyboardState() == FN_SHIFT) {
            KB().setKeyboardState(NORMAL);
          } else if (KB().getKeyboardState() == SHIFT) {
            KB().setKeyboardState(FN_SHIFT);
          } else {
            KB().setKeyboardState(FUNC);
          }
        }
        else if (inchar == 8) {
          if (currentLine.length() > 0 && cursor_pos != 0) {
            int old_cursor = cursor_pos;
            do { cursor_pos--; } while (cursor_pos > 0 && (currentLine[cursor_pos] & 0xC0) == 0x80);
            int bytesToDelete = old_cursor - cursor_pos;
            currentLine.remove(cursor_pos, bytesToDelete);
          }
        }
        else if (inchar == 19) {
          if (cursor_pos > 0) {
            do { cursor_pos--; } while (cursor_pos > 0 && (currentLine[cursor_pos] & 0xC0) == 0x80);
          }
        }
        else if (inchar == 21) {
          if (cursor_pos < currentLine.length()) {
            do { cursor_pos++; } while (cursor_pos < currentLine.length() && (currentLine[cursor_pos] & 0xC0) == 0x80);
          }
        }
        else if (inchar == 20) {
        }
        else if (inchar == 28) {
          cursor_pos = 0;
          KB().setKeyboardState(NORMAL);
        }
        else if (inchar == 30) {
          cursor_pos = currentLine.length();
          KB().setKeyboardState(NORMAL);
        }
        else if (inchar == 29) {
          KB().setKeyboardState(NORMAL);
        }
        else if (inchar == 12) {
          currentLine = "_EXIT_";
          break;
        }
        else if (inchar == 6) {
          KB().setKeyboardState(NORMAL);
        }
        else if (inchar == 7) {
          currentLine = "";
          cursor_pos = 0;
          KB().setKeyboardState(NORMAL);
        }
        else if (inchar == 24) {
          KB().setKeyboardState(NORMAL);
        }
        else if (inchar == 26) {
          KB().setKeyboardState(NORMAL);
        }
        else if (inchar == 25) {
          KB().setKeyboardState(NORMAL);
        }
        else if (inchar == 9 || inchar == 14) {
          KB().setKeyboardState(NORMAL);
        } else {
          if (cursor_pos == 0) {
            currentLine = inchar + currentLine;
          } else if (cursor_pos == currentLine.length()) {
            currentLine += inchar;
          } else {
            left = currentLine.substring(0, cursor_pos);
            right = currentLine.substring(cursor_pos);
            currentLine = left + inchar + right;
          }
          cursor_pos++;
          if (inchar >= 48 && inchar <= 57) {
          } 
          else if (KB().getKeyboardState() != NORMAL) {
            KB().setKeyboardState(NORMAL);
          }
        }
      }
    }

    // Handle idle state transitions
    bool isIdle = (millis() - lastInput > IDLE_TIME);
    static bool wasIdle = false;
    
    // If we just woke up from being idle, reset the mage and force a text redraw
    if (isIdle != wasIdle) {
       wasIdle = isIdle;
       if (!isIdle) {
           resetIdle();
           redraw = true; 
       }
    }

    // Display Update Loop (Runs at OLED_MAX_FPS)
    if (currentMillis - OLEDFPSMillis >= (1000 / OLED_MAX_FPS)) {
      if (isIdle) {
        // Continuously update the idle animation frames while idle
        OLEDFPSMillis = currentMillis;
        mageIdle(true); 
      } 
      else if (redraw) {
        // Only redraw the text prompt if the user typed or moved the cursor
        OLEDFPSMillis = currentMillis;
        redraw = false;
        
        if (prefix != "") OLED().oledLine(prefix + currentLine, cursor_pos+prefix.length(), false, promptText);
        else OLED().oledLine(currentLine, cursor_pos, false, promptText);
      }
    }

    vTaskDelay(pdMS_TO_TICKS(10));
    yield();
  }

  return currentLine;
}

int boolPrompt(String promptText) {
  KB().setKeyboardState(NORMAL);
  pocketmage::setCpuSpeed(240); // Boost clock for smooth animation

  String msg = promptText + " (y/n)";
  u8g2.clearBuffer();
  const uint16_t dw = u8g2.getDisplayWidth();
  const uint16_t dh = u8g2.getDisplayHeight();
  
  int y_offset = 0;
  int x_offset = 0;
  const uint8_t* activeFont;

  // --- 1. Find the largest font that fits and calculate offsets ---
  u8g2.setFont(u8g2_font_ncenB14_tf);
  if (u8g2.getUTF8Width(msg.c_str()) < dw-8) {
    y_offset = 16 + 3 + 5;
    x_offset = (dw - u8g2.getUTF8Width(msg.c_str())) / 2;
    activeFont = u8g2_font_ncenB14_tf;
  } 
  else {
    u8g2.setFont(u8g2_font_ncenB12_tf);
    if (u8g2.getUTF8Width(msg.c_str()) < dw-8) {
      y_offset = 16 + 2 + 5;
      x_offset = (dw - u8g2.getUTF8Width(msg.c_str())) / 2;
      activeFont = u8g2_font_ncenB12_tf;
    } 
    else {
      u8g2.setFont(u8g2_font_ncenB10_tf);
      if (u8g2.getUTF8Width(msg.c_str()) < dw-8) {
        y_offset = 16 + 1 + 5;
        x_offset = (dw - u8g2.getUTF8Width(msg.c_str())) / 2;
        activeFont = u8g2_font_ncenB10_tf;
      } 
      else {
        u8g2.setFont(u8g2_font_ncenB08_tf);
        if (u8g2.getUTF8Width(msg.c_str()) < dw-8) {
          y_offset = 16 + 5;
          x_offset = (dw - u8g2.getUTF8Width(msg.c_str())) / 2;
        } 
        else {
          y_offset = 16 + 5;
          x_offset = dw - u8g2.getUTF8Width(msg.c_str());
        }
        activeFont = u8g2_font_ncenB08_tf;
      }
    }
  }

  // --- 2. Slide Up Animation ---
  for (int y = dh; y > 0; y-=2) {
    u8g2.clearBuffer();
    u8g2.setFont(activeFont);
    u8g2.drawUTF8(x_offset, y + y_offset, msg.c_str());
    u8g2.drawRFrame(0, y, dw, dh + 16, 10);
    u8g2.sendBuffer();
    delay(5);
  }

  if (SAVE_POWER) pocketmage::setCpuSpeed(POWER_SAVE_FREQ);

  unsigned long lastSystemTime = CLOCK().getPrevTimeMillis();
  int retVal = -1;

  // --- 3. Input Loop ---
  for (;;) {
    #if !OTA_APP 
      if (!noTimeout)  checkTimeout();
      if (DEBUG_VERBOSE) printDebug();
    #endif

    // Set timeout
    CLOCK().setPrevTimeMillis(millis());
    updateBattState();

    // Redraw if background tasks overwrite the screen
    unsigned long currentSystemTime = CLOCK().getPrevTimeMillis();
    if (currentSystemTime > lastSystemTime) {
        lastSystemTime = currentSystemTime;
        u8g2.clearBuffer();
        u8g2.setFont(activeFont);
        u8g2.drawUTF8(x_offset, y_offset, msg.c_str());
        u8g2.drawRFrame(0, 0, dw, dh + 16, 10);
        u8g2.sendBuffer();
    }

    int currentMillis = millis();
    char inchar = KB().updateKeypress();

    if (currentMillis - KBBounceMillis >= KB_COOLDOWN) {
      if (inchar != 0) {
        KBBounceMillis = currentMillis; 
        
        if (inchar == 'y' || inchar == 'Y') {
          retVal = 1;
          break;
        }
        else if (inchar == 'n' || inchar == 'N') {
          retVal = 0;
          break;
        }
        else if (inchar == 23) { // App Switcher Kill Signal
          retVal = 0; // Default to 'no' on cancel
          break;
        }
      }
    }

    vTaskDelay(pdMS_TO_TICKS(10));
    yield();
  }

  pocketmage::setCpuSpeed(240); // Boost clock for exit animation

  // --- 4. Slide Down Animation ---
  for (int y = 0; y <= dh; y+=2) {
    u8g2.clearBuffer();
    u8g2.setFont(activeFont);
    u8g2.drawUTF8(x_offset, y + y_offset, msg.c_str());
    u8g2.drawRFrame(0, y, dw, dh + 16, 10);
    u8g2.sendBuffer();
    delay(5);
  }

  if (SAVE_POWER) pocketmage::setCpuSpeed(POWER_SAVE_FREQ);
  return retVal;
}

int timePrompt(int defaultTime) {
  uint8_t digits[4] = {0,0,0,0};
  ulong currentIndex = 0;

  // If a valid time is passed (e.g., 1430), extract it into the digits array
  if (defaultTime >= 0 && defaultTime <= 2359) {
    digits[0] = (defaultTime / 1000) % 10;
    digits[1] = (defaultTime / 100) % 10;
    digits[2] = (defaultTime / 10) % 10;
    digits[3] = defaultTime % 10;
  }

  // X coordinates for the 4 digits (HHMM)
  const int tX[4] = {93, 110, 131, 148};

  for (;;) {
    #if !OTA_APP 
      if (!noTimeout)  checkTimeout();
      if (DEBUG_VERBOSE) printDebug();
    #endif

    // Update scroll
    int scrollVec = TOUCH().getScrollVector();
    if (scrollVec != 0) {
      
      if (currentIndex == 0) {
        // Isolate the Tens of Hours digit to prevent base-24 modulo bleeding
        int d0 = digits[0] + scrollVec;
        if (d0 > 2) d0 = 0;
        if (d0 < 0) d0 = 2;
        digits[0] = d0;
        
        // Reverse Clamp: If we wrapped to 2, ensure the hours digit isn't sitting at 4-9
        if (digits[0] == 2 && digits[1] > 3) {
           digits[1] = 3; 
        }
      } else {
        // Convert current digits to total minutes for smooth carry-over
        int total_mins = (digits[0] * 10 + digits[1]) * 60 + (digits[2] * 10 + digits[3]);

        // Apply the scroll vector based on cursor position
        switch (currentIndex) {
          case 1: total_mins += scrollVec * 60;  break; // +/- 1 hour
          case 2: total_mins += scrollVec * 10;  break; // +/- 10 minutes
          case 3: total_mins += scrollVec * 1;   break; // +/- 1 minute
        }

        // Wrap-around logic for 24-hour format (1440 minutes in a day)
        total_mins = total_mins % 1440;
        if (total_mins < 0) {
            total_mins += 1440; // Wrap backwards (e.g. 00:00 - 1 min = 23:59)
        }

        // Convert total minutes back to individual digits
        int h = total_mins / 60;
        int m = total_mins % 60;
        
        digits[0] = h / 10;
        digits[1] = h % 10;
        digits[2] = m / 10;
        digits[3] = m % 10;
      }
    }
    
    // Update system state
    updateBattState();
    KB().checkUSBKB();

    // Handle keyboard inputs
    KB().setKeyboardState(FUNC);
    
    int currentMillis = millis();
    char inchar = KB().updateKeypress();

    if (currentMillis - KBBounceMillis >= KB_COOLDOWN) {
      if (inchar != 0) {
        KBBounceMillis = currentMillis;

        // Left arrow or bksp
        if (inchar == 12 || inchar == 8) {
          if (currentIndex > 0) {
            currentIndex--;
          } 
        }
        // Right arrow
        else if (inchar == 6) {
          if (currentIndex < 3) {
            currentIndex++;
          }
        }
        // Direct Numeric Entry (0-9)
        else if (inchar >= '0' && inchar <= '9') {
          int val = inchar - '0'; // Convert ASCII char to integer
          
          switch (currentIndex) {
            case 0: // Tens of Hours (Max 2)
              digits[0] = (val > 2) ? 2 : val;
              // Reverse Clamp: If we just set it to 2, ensure the hours digit isn't sitting at 4-9
              if (digits[0] == 2 && digits[1] > 3) {
                 digits[1] = 3; 
              }
              break;
              
            case 1: // Hours (Max 3 if Tens is 2, otherwise Max 9)
              if (digits[0] == 2) {
                digits[1] = (val > 3) ? 3 : val;
              } else {
                digits[1] = val;
              }
              break;
              
            case 2: // Tens of Minutes (Max 5)
              digits[2] = (val > 5) ? 5 : val;
              break;
              
            case 3: // Minutes (Max 9)
              digits[3] = val;
              break;
          }
          
          // Auto-advance cursor for natural typing flow
          if (currentIndex < 3) {
            currentIndex++;
          }
        }
        // Enter 
        else if (inchar == 13) {
          int returnInt = 0;
          returnInt += digits[3]*1;
          returnInt += digits[2]*10;
          returnInt += digits[1]*100;
          returnInt += digits[0]*1000;

          // Because of our modulo math and strict clamping, the digits can 
          // physically never exceed 23:59. But we clamp just in case.
          if (returnInt >= 2400) {
              returnInt = 0;
          }

          return returnInt;
        }
      }
    }

    // Draw interface
    u8g2.clearBuffer(); // Required so text doesn't smear endlessly

    // Draw background
    u8g2.drawXBMP(0,0,256,32,timeInput);

    // Draw indicator
    switch (currentIndex) {
      case 0:
        u8g2.drawXBMP(89,21,24,11,leftRightIndicator0);
        break;
      case 1:
        u8g2.drawXBMP(106,21,24,11,leftRightIndicator1);
        break;
      case 2:
        u8g2.drawXBMP(127,21,24,11,leftRightIndicator1);
        break;
      case 3:
        u8g2.drawXBMP(144,21,24,11,leftRightIndicator2);
        break;
    }

    // Draw digits dynamically with inverted active block
    u8g2.setFont(u8g2_font_luBIS14_tn);
    for (int i = 0; i < 4; i++) {
      if (i == currentIndex) {
        u8g2.setDrawColor(1);
        u8g2.drawBox(tX[i], 0, 15, 20); // Draw white background block
        u8g2.setDrawColor(0);               // Set text color to black
      } else {
        u8g2.setDrawColor(1);               // Standard white text
      }
      u8g2.drawStr(tX[i], 16, String(digits[i]).c_str());
    }
    u8g2.setDrawColor(1); // Reset for next draw cycle

    u8g2.sendBuffer(); // Required to push the frame to the OLED

    vTaskDelay(pdMS_TO_TICKS(10));
    yield();
  }
}

// Helper function to calculate max days in a month (handles Leap Years)
static int getDaysInMonth(int month, int year) {
  if (month == 2) {
    return ((year % 4 == 0 && year % 100 != 0) || year % 400 == 0) ? 29 : 28;
  }
  if (month == 4 || month == 6 || month == 9 || month == 11) return 30;
  return 31;
}
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
